ObeliskInc/obelisk-hardware/Generation 2 Mining Hardware/Electrical/Hashing Board/SC1B_MEMO-13.pdf

ORCHID TECHNOLOGIES ENGINEERING & CONSULTING, INC.

147 Main Street, Maynard, MA 01754
Tel: 978‐461‐2000 Fax: 978‐461‐2003 Web Site: www.orchid‐tech.com | Page 1

To: Zach Herbert

Fr: Paul Nickelsberg

Re: SC1B Rev D Release Package

Dt: September 25, 2018

Enclosed, please find the SC1B Revision D Hashing Board Release Package. This release package is suitable for construction of SC1B low volume, prototype circuit board assemblies. While Orchid has made every effort to provide an accurate, re-producible package, design anomalies and changes are inevitable between the construction of prototype assemblies, testing of those prototype assemblies and subsequent volume production. Please plan accordingly.

This package includes:

- SC1B Revision D Build Instructions
- SC1B Revision D Schematic Data Base
- SC1B Revision D Layout Data Base
- SC1B Revision D Bill of Materials

Sincerely,
Paul Nickelsberg
President
Orchid Technologies Engineering and Consulting, Inc.
