ObeliskInc/obelisk-hardware/Generation 2 Mining Hardware/Electrical/Control Board/docs/CC1B_REVA_BLD1_0.pdf

ORCHID TECHNOLOGIES CONFIDENTIAL – All Rights Reserved

FILE=CC1B_REVA_BLD1_0.DOC

# Orchid Technologies CC1B Control board PCB Assembly Build Instructions

Prepared By: Orchid Technologies Engineering and Consulting, Inc. 147 Main Street Maynard, Ma. 01754 978-461-2000

PROPRIETARY DATA NOTICE

This document shall not be duplicated or used for any purpose other than that for which provided. The information disclosed herein was originated by and is the property of Orchid Technologies Engineering & Consulting Inc. and/or its wholly-owned subsidiaries, and except for rights expressly granted by written consent, such information shall not be disclosed or disseminated in whole or in part. Orchid Technologies Engineering & Consulting Inc. and/or its wholly-owned subsidiaries reserve all Patent, Proprietary, Design, Use, Sale, Manufacturing, and Reproduction Rights thereto. Permission is hereby granted to you to copy this document as required for internal use only.

This document is presented to assist you in appraising the potential value of the CC1B CONTROL BOARD Build Instructions based upon the information which you have provided to us concerning your needs. Naturally, your requirements may change as business conditions and your operations change. Only you can determine the feasibility of the proposed CC1B CONTROL BOARD Build Instructions to answer your specific business needs. Consequently, while we believe that our CC1B CONTROL BOARD Build Instructions are sound, it cannot constitute express or implied warranties of merchantability and fitness for a particular purpose.

Revision History:
Revision | Date | Reason
1.0 | August 6, 2018 | Original

CC1B CONTROL Board, Rev A PCB Build Instructions, V1.0

This document contains the assembly-time instructions for the proper build of CC1B CONTROL BOARD Revision A Printed Circuit Boards. These Instructions together with the following documents comprise the CC1B CONTROL BOARD Revision A Circuit Board Fabrication and Assembly data base.

Related Documentation:

1. SC071018 Revision A July 29, 2018 Schematic Data Base
2. CC1B_072918.xls Bill of Materials – Base Bill
3. CC1B CONTROL BOARD PCB, Revision A Data Base Assembly and Fabrication Artwork as released by Orchid Technologies using SC071018 Revision A schematic and the CC1B_072918.xls BOM data base.

The documents listed above are considered finished documents and will not be modified by Orchid Technologies Engineering and Consulting, Inc. until Phase 2 of the project. All modifications to the documents listed above will take the form of notes and appear in this document as revised.

Documentation Errata, Changes, Acceptable Procedures:
All component stuffing and board options reference CC1B_072918.xls. Please use CC1B_072918.xls, as the basic guideline for board stuffing options.

### 0. DO NOT POWER BOARDS

1. Do Not Populate components with values “DNP”.
2. Do Not Populate components with values prefixed “DNP-“.
3. Completed assemblies shall be free of any and all flux residues.

Known BOM Discrepancies and AVL issues:

BOM Updates:
Item No | Description
| None

AVL Issues:
Item No | Description
| None

Programmable Logic Instructions:
This describes the programmable device data files and their uses.

NONE

CC1B CONTROL BOARD Revision A Rework Instructions:
Perform the instructions listed below on all CC1B CONTROL BOARD Revision A Circuit Boards.
Item | Action | Disposition
| None
