ObeliskInc/obelisk-hardware/Generation 2 Mining Hardware/Electrical/Hashing Board/pcb/SC1B_REVD_ASY/SC1B_REVD_AS2.pdf

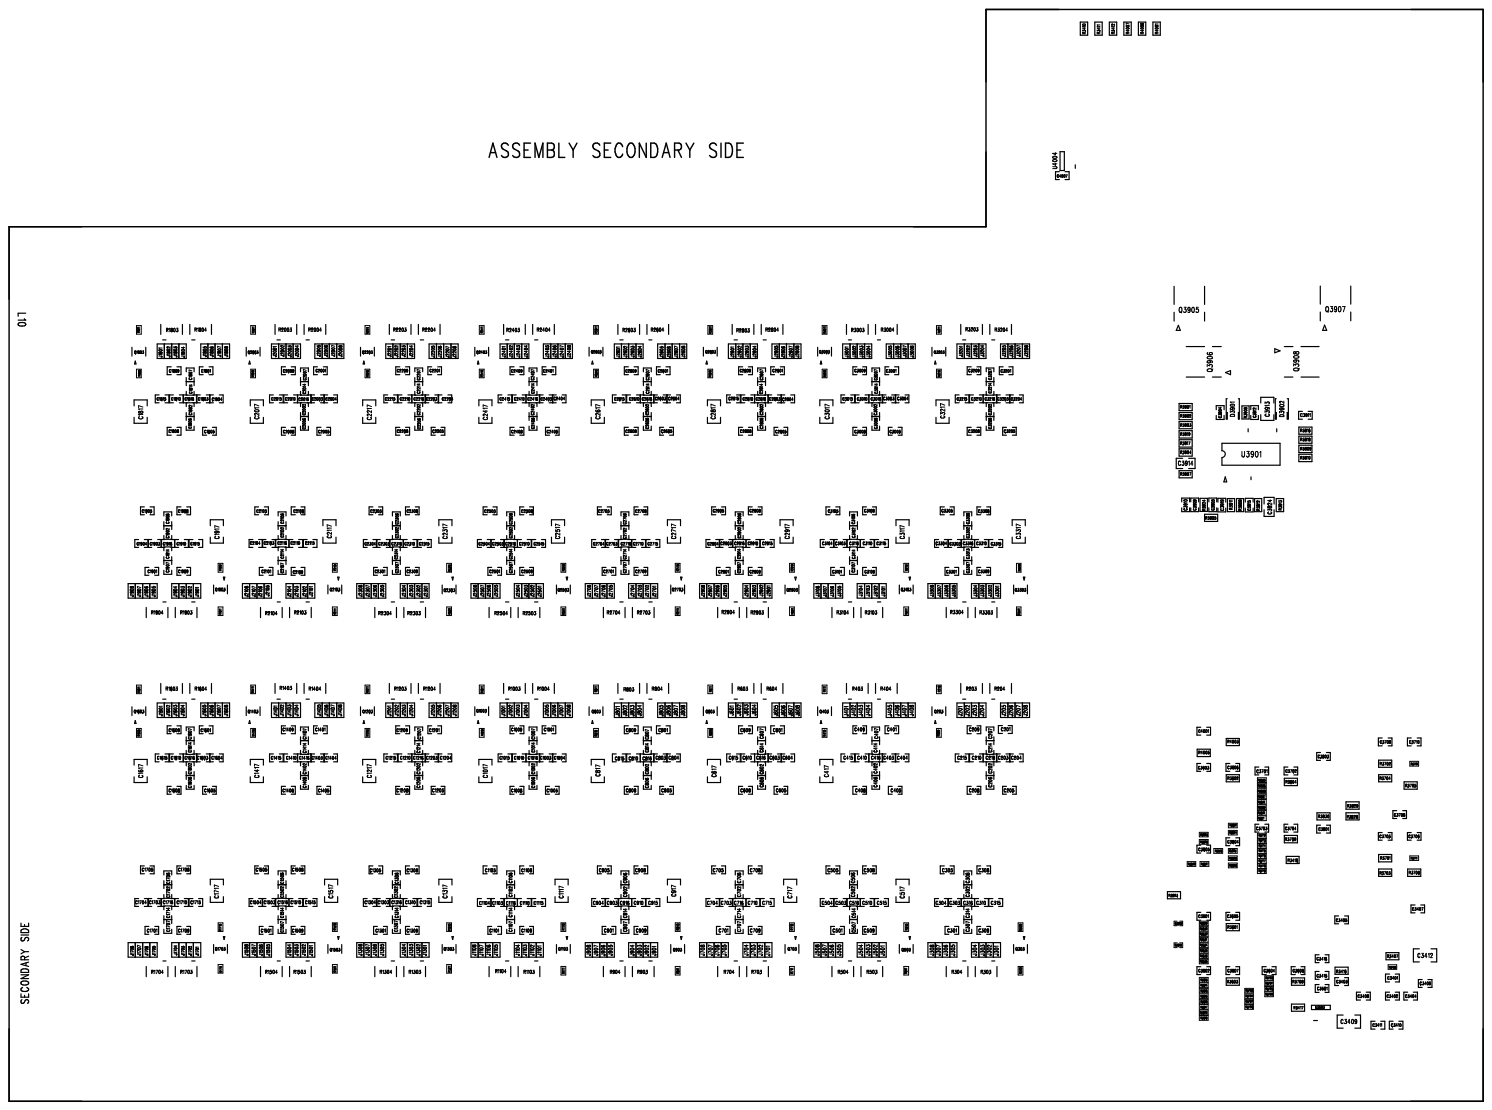
[picture p1: page 1]
