ObeliskInc/obelisk-hardware/Generation 2 Mining Hardware/Electrical/Control Board/docs/CC1B_072918.xls

Item | Quan | Reference | Value | Vendor | Vendor PN | Shape | Notes | Alt Vendor | Alt Vendor PN
1 | 4 | C902,C903,C904,C905 | 15pF/50V | MURATA | GRM0335C1H150J | C0201
2 | 2 | C301,C302 | 18pF/50V | MURATA | GRM0335C1H180J | C0201
3 | 1 | C1616 | 33pF/25V | MURATA | GRM0335C1E330J | C0201
4 | 1 | C1506 | 6800pF/25V | MURATA | GRM155R71E682K | C0402
5 | 1 | C1617 | 0.01uF/6.3V | MURATA | GRM033R70J103K | C0201
6 | 1 | C1601 | 0.01uF/10V | MURATA | GRM033R71A103K | C0201
7 | 1 | C1501 | 0.01uF/16V | MURATA | GRM155R71C103K | C0402
8 | 108 | C601,C602,C603,C604,C605, | 0.1uF/6.3V | MURATA | GRM155R70J104K | CC0402
 |  | C606,C607,C608,C609,C610,
 |  | C611,C612,C613,C614,C615,
 |  | C616,C617,C618,C619,C620,
 |  | C621,C622,C623,C624,C625,
 |  | C626,C627,C628,C629,C630,
 |  | C631,C632,C633,C634,C635,
 |  | C636,C637,C638,C639,C640,
 |  | C641,C642,C643,C644,C645,
 |  | C646,C647,C648,C649,C650,
 |  | C651,C652,C653,C654,C655,
 |  | C656,C657,C658,C659,C701,
 |  | C702,C703,C704,C705,C706,
 |  | C707,C708,C709,C710,C711,
 |  | C712,C713,C714,C715,C716,
 |  | C717,C718,C719,C720,C721,
 |  | C722,C723,C724,C725,C726,
 |  | C727,C728,C729,C730,C802,
 |  | C1001,C1002,C1003,C1201,
 |  | C1202,C1203,C1204,C1205,
 |  | C1206,C1207,C1208,C1209,
 |  | C1210,C1211,C1212,C1301,
 |  | C1302,C1619
9 | 30 | C201,C801,C901,C906,C908, | 0.1uF/16V | MURATA | GRM155R71C104K | CC0402
 |  | C909,C913,C914,C916,
 |  | C1101,C1102,C1103,C1104,
 |  | C1401,C1402,C1403,C1404,
 |  | C1405,C1406,C1407,C1502,
 |  | C1507,C1508,C1509,C1510,
 |  | C1511,C1512,C1602,C1603,
 |  | C1604
10 | 4 | C666,C667,C668,C669 | 1.0uF/6.3V | MURATA | GRM188R70J105K | C0603
11 | 4 | C1621,C1622,C1623,C1624 | 1.0uF/16V | MURATA | GRM21BR71C105K | C0805 | X7R
12 | 3 | C910,C911,C912 | 4.7uF/6.3V | MURATA | GRM188R60J475K | C0603
13 | 13 | C660,C661,C662,C663,C664, | 10uF/6.3V | TDK | CGA4J1X7R0J106K125AC | C0805
 |  | C665,C1004,C1610,C1611,
 |  | C1612,C1613,C1614,C1620
14 | 2 | C1503,C1513 | 10uF/16V | MURATA | GRM31CR71C106K | C1206
15 | 5 | C1504,C1505,C1605,C1606, | 22uF/6.3V | TDK | C2012X6S0J226K | C0805
 |  | C1607
16 | 24 | R301,R306,R307,R308,R309, | 0 OHM | VISHAY | CRCW02010000Z0 | R0201
 |  | R311,R312,R325,R326,R402,
 |  | R403,R1007,R1201,R1202,
 |  | R1203,R1204,R1205,R1206,
 |  | R1207,R1208,R1209,R1210,
 |  | R1211,R1212
17 | 20 | R304,R305,R320,R321,R322, | 33 OHM | VISHAY | CRCW020133R0JN | R0201
 |  | R323,R324,R401,R916,R917,
 |  | R918,R919,R920,R926,R927,
 |  | R928,R929,R930,R1004,
 |  | R1309
18 | 7 | R803,R804,R805,R806,R921, | 330 OHM | VISHAY | CRCW0201330RJN | R0201
 |  | R922,R1406
19 | 12 | R404,R405,R801,R802, | 1K | VISHAY | CRCW02011K00JN | R0201
 |  | R1305,R1308,R1405,R1606,
 |  | R1607,R1609,R1610,R1611
20 | 5 | R318,R319,R702,R1310, | 2.2K | VISHAY | CRCW02012K20JN | R0201
 |  | R1311
21 | 19 | R901,R902,R903,R904,R905, | 4.7K | VISHAY | CRCW02014K70JN | R0201
 |  | R906,R907,R913,R914,R915,
 |  | R923,R924,R933,R1005,
 |  | R1006,R1109,R1110,R1111,
 |  | R1112
22 | 1 | R1504 | 6.8K | VISHAY | CRCW02016K80JN | R0201
23 | 44 | R313,R406,R407,R408,R409, | 10K | VISHAY | CRCW020110K0JN | R0201
 |  | R410,R411,R412,R413,R414,
 |  | R415,R416,R420,R421,R424,
 |  | R425,R426,R925,R1001,
 |  | R1002,R1003,R1008,R1009,
 |  | R1010,R1011,R1012,R1101,
 |  | R1102,R1103,R1104,R1105,
 |  | R1106,R1107,R1108,R1301,
 |  | R1302,R1303,R1304,R1306,
 |  | R1307,R1401,R1402,R1403,
 |  | R1404
24 | 1 | R1502 | 100K | VISHAY | CRCW0201100KJN | R0201
25 | 29 | R201,R704,R705,R706,R707, | 49.9 OHM 1% | VISHAY | CRCW020149R9FK | R0201
 |  | R708,R709,R710,R711,R712,
 |  | R713,R714,R715,R716,R717,
 |  | R718,R719,R720,R721,R722,
 |  | R723,R724,R725,R727,R728,
 |  | R908,R909,R910,R911
26 | 1 | R701 | 100 OHM 1% | VISHAY | CRCW0201100RFK | R0201
27 | 1 | R703 | 240 OHM 1% | VISHAY | CRCW0201240RFK | R0201
28 | 1 | R1501 | 10.0K 1% | VISHAY | CRCW020110K0FK | R0201
29 | 1 | R912 | 12.1K 1% | VISHAY | CRCW020112K1FK | R0201
30 | 1 | R1503 | 26.1K 1% | VISHAY | CRCW020126K1FK | R0201
31 | 1 | R1601 | 150K 1% | VISHAY | CRCW0201150KFK | R0201
32 | 2 | R1602,R1603 | 180K 1% | VISHAY | CRCW0201180KFK | R0201
33 | 1 | R1608 | 270K 1% | VISHAY | CRCW0201270KFK | R0201
34 | 3 | L601,L602,L901 | BLM18 | MURATA | BLM18PG121SN1D | 0603
35 | 1 | L1501 | 10uH | BOURNS | SRU8043-100Y | IND_SRU8043-100Y | NEW
36 | 1 | Y901 | ASFL1-25.000MHz | ABRACON | ASFL1-25.000MHZ-LR-T | CRY\ASFL1
37 | 1 | Y301 | ABM8G-24.000 | ABRACON | ABM8G-24.000MHZ-18-D2Y-T | CRY\ABM8
38 | 1 | U1402 | ASDK-32.768KHZ | ABRACON | ASDK-32.768KHZ | CRY_ASDK
39 | 1 | U1401 | CSEQ | ALTERA | 5M40ZE64C5 | QFP64_7X7MM_TP
40 | 2 | L1601,L1602 | LPS4018-222MRC | COILCRAFT | LPS4018-222MRC | IND_LPS4018
41 | 1 | D801 | LED-553-GG | DIALIGHT | 553-0122F | LED_553-0132F
42 | 1 | U1501 | AP6502SP-13 | DIODES INC | AP6502SP-13 | DIP8_SO-8EP
43 | 1 | D1501 | S1A-13-F | DIODES INC | S1A-13-F | SMA
44 | 1 | J1002 | CONN-DM3CS | HIROSE | DM3CS-SF | HRS-DM3CS-SF
45 | 1 | U1002 | IDT74CBTLV3257QG | IDT | IDT74CBTLV3257QG | DIP16\QSOP
46 | 1 | F1501 | FUSE-5A | LITTELFUSE | 0451005.MRL | FUSE\LF-0451
47 | 1 | U701 | MT41J64M16 | MICRON | MT41J64M16JT-15E:g | BGA96_8X14MM |  | NANYA | NT5CB64M16GP-DH
48 | 1 | U1001 | MT25QL128 | MICRON | MT25QL128ABA3ESF-OSIT | DIP16/SOL |  | MICRON | MT25QL128ABA8ESF-OSIT
49 | 1 | U1601 | LP2998MR | NATIONAL SEMI | LP2998MR/NOPB | DIP8\PSOP
50 | 1 | U1301 | CAT24C256YI-G | ON SEMI | CAT24C256YI-G | DIP8\TSSOP
51 | 2 | Q902,Q901 | MMBT3904LT1 | ON SEMI | MMBT3904LT1G | SOT-23
52 | 2 | Q801,Q802 | MUN5235DW1 | ON SEMI | MUN5235DW1T1G | SOT-363
53 | 2 | U1604,U1605 | NCP114ASN180T1G | ON SEMI | NCP114ASN180T1G | TSOP-5
54 | 1 | U1403 | CAT809TTBI-GT3 | ON SEMI | CAT809TTBI-GT3 | SOT-23
55 | 1 | F1502 | PTC_1A | RAYCHEM | SMD100F | SMD100
56 | 4 | F1503,F1504,F1505,F1506 | PTC_1A5 | RAYCHEM | SMD150F | SMD100
57 | 1 | U901 | LAN8710A-EZC | SMSC | LAN8710A-EZC | QFN32_5X5MM_TP
58 | 5 | J501,J1301,J1302,J1304, | CON2 | SAMTEC | TSW-102-23-T-S | SIP\2P
 |  | J1305
59 | 2 | J1201,J1202 | CON3 | SAMTEC | TSW-103-23-T-S | SIP\3P
60 | 1 | J1001 | HEADER 4X2 | SAMTEC | TSW-104-23-T-D | J\8P
61 | 1 | J1401 | HEADER 5X2 | SAMTEC | TSW-105-23-T-D | J\10P
62 | 1 | J1306 | HEADER 10X2 | SAMTEC | TSW-110-23-T-D | J\20P
63 | 2 | J1207,J1208 | HEADER 10X2S | 3M | D2520-6002 | 3M_D2520-6002
64 | 4 | J1101,J1102,J1103,J1104 | CONN-FAN | TE CONN | 640454-4 | AMP\640454-4
65 | 1 | S801 | SW-RA | TE CONN | 1825027-5 | SW_TE_1825027-X
66 | 1 | J901 | CONN_LAN | UDE | RB1-125BAG1A | UDE_RB1-125BAG1A | RJ45 WITH MAG, NEW
67 | 1 | U201 | AM3352-ZCZ3 | TEXAS INSTRUMENTS | AM3352BZCZ30 | BGA324_.8MM_15X15MM
68 | 9 | U801,U1101,U1102,U1103, | SN74LVC2G14DB | TEXAS INSTRUMENTS | SN74LVC2G14DBVRE4 | SOT-23-6
 |  | U1104,U1201,U1202,U1203,
 |  | U1204
69 | 1 | U1603 | TPS22967DSGT | TEXAS INSTRUMENTS | TPS22967DSGI | DSG8_2X2MM_TP
70 | 1 | U1602 | TPS62410DRCT | TEXAS INSTRUMENTS | TPS62410DRCT | DRC10_3X3MM_TP
71 | 1 | D1401 | TLMG1100 | VISHAY | TLMG1100-GS08 | LED\0603
72 | 1 | D805 | VBUS054B-HSF | VISHAY | VBUS054B-HSF | ARRAY_VBUS054B-HSF
73 | 27 | R303,R310,R417,R418,R419, | DNP | DO NOT POPULATE | DO NOT POPULATE | 0402
 |  | R422,R423,R1013,R1113,
 |  | R1114,R1115,R1116,R1213,
 |  | R1214,R1215,R1216,R1217,
 |  | R1218,R1219,R1220,R1221,
 |  | R1222,R1223,R1224,R1407,
 |  | R1408,R1409
74 | 2 | H1302,H1303 | HOLE_M3X6 | DO NOT POPULATE | DO NOT POPULATE | HOLE_M3X6
75 | 2 | H1301,H1304 | SLOT_M3X3MM | DO NOT POPULATE | DO NOT POPULATE | SLOT_M3X3MM
76 | 17 | T201,T301,T501,T502,T503, | TP | OTEC TEST POINT | DO NOT POPULATE | TPTOP
 |  | T504,T505,T506,T507,T508,
 |  | T509,T601,T602,T1401,
 |  | T1402,T1403,T1404
77 | 1 | D802 | DNP_LED-553-GG | DO NOT POPULATE | DO NOT POPULATE | LED_553-0132F
78 | 3 | D1402,D1403,D1404 | DNP_TLMG1100 | DO NOT POPULATE | DO NOT POPULATE | LED\0603
79 | 4 | J1203,J1204,J1205,J1206 | DNP_CON3 | DO NOT POPULATE | DO NOT POPULATE | SIP\3P
80 | 4 | J1209,J1210,J1211,J1212 | DNP_HEADER 10X2S | DO NOT POPULATE | DO NOT POPULATE | 3M_D2520-6002
81 | 8 | U1205,U1206,U1207,U1208, | DNP_SN74LVC2G14DB | DO NOT POPULATE | DO NOT POPULATE | SOT-23-6
 |  | U1209,U1210,U1211,U1212
