ObeliskInc/obelisk-hardware/Generation 2 Mining Hardware/Electrical/Hashing Board/docs/SC1B_091918.xls

Item | Quan | Reference | Value | Vendor | Vendor PN | Shape | Notes
1 | 3 | C3410,C3411,C3915 | 22pF/50V | MURATA | GRM1555C1H220J | C0402
2 | 1 | C3909 | 220pF/50V | TDK | C1005C0G1H221J050BA | C0402
3 | 1 | C3905 | 820pF/50V | TDK | C1005C0G1H821J050BA | C0402
4 | 4 | C3609,C3610,C3617,C3618 | 2200pF/16V | MURATA | GRM033R71C222K | C0201
5 | 5 | C3401,C3413,C3414,C3415, | 0.01uF/16V | MURATA | GRM155R71C103K | C0402
 |  | C3416
6 | 409 | C201,C202,C203,C204,C205, | 0.1uF/6.3V | MURATA | GRM155R710J104K | C0402
 |  | C206,C207,C208,C209,C210,
 |  | C214,C215,C301,C302,C303,
 |  | C304,C305,C306,C307,C308,
 |  | C309,C310,C314,C315,C401,
 |  | C402,C403,C404,C405,C406,
 |  | C407,C408,C409,C410,C414,
 |  | C415,C501,C502,C503,C504,
 |  | C505,C506,C507,C508,C509,
 |  | C510,C514,C515,C601,C602,
 |  | C603,C604,C605,C606,C607,
 |  | C608,C609,C610,C614,C615,
 |  | C701,C702,C703,C704,C705,
 |  | C706,C707,C708,C709,C710,
 |  | C714,C715,C801,C802,C803,
 |  | C804,C805,C806,C807,C808,
 |  | C809,C810,C814,C815,C901,
 |  | C902,C903,C904,C905,C906,
 |  | C907,C908,C909,C910,C914,
 |  | C915,C1001,C1002,C1003,
 |  | C1004,C1005,C1006,C1007,
 |  | C1008,C1009,C1010,C1014,
 |  | C1015,C1101,C1102,C1103,
 |  | C1104,C1105,C1106,C1107,
 |  | C1108,C1109,C1110,C1114,
 |  | C1115,C1201,C1202,C1203,
 |  | C1204,C1205,C1206,C1207,
 |  | C1208,C1209,C1210,C1214,
 |  | C1215,C1301,C1302,C1303,
 |  | C1304,C1305,C1306,C1307,
 |  | C1308,C1309,C1310,C1314,
 |  | C1315,C1401,C1402,C1403,
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
 |  | R1509,R1609,R1709,R1809,
 |  | R1909,R2009,R2109,R2209,
 |  | R2309,R2409,R2509,R2609,
 |  | R2709,R2809,R2909,R3009,
 |  | R3109,R3209,R3309
32 | 1 | R3911 | 3.90K 1% | VISHAY | CRCW04023K90FK | R0402
33 | 2 | R3904,R3912 | 11.0K 1% | VISHAY | CRCW040211K0FK | R0402
34 | 4 | R3907,R3913,R3916,R3917 | 20.0K 1% | VISHAY | CRCW040220K0FK | R0402
35 | 1 | R3922 | 30.0K 1% | VISHAY | CRCW040230K0FK | R0402
36 | 1 | R3905 | 43.2K 1% | VISHAY | CRCW040243K2FK | R0402
37 | 2 | R3919,R3918 | 49.9K 1% | VISHAY | CRCW040249K9FK | R0402
38 | 1 | R3908 | 60.4K 1% | VISHAY | CRCW040260K4FK | R0402
39 | 1 | R3903 | 100K 1% | VISHAY | CRCW0402100KFK | R0402
40 | 2 | RT3901,RT3902 | 100KT | MURATA | NCU18WF104F60RB | R0603 | THERMISTOR
41 | 2 | R3414,R3415 | R4A-33 OHM | VISHAY | CRA06S083033RJ | ARRAY_CRA06S0831
42 | 64 | R203,R204,R303,R304,R403, | R4A-100 OHM | VISHAY | CRA06S083101RJ | ARRAY_CRA06S0831
 |  | R404,R503,R504,R603,R604,
 |  | R703,R704,R803,R804,R903,
 |  | R904,R1003,R1004,R1103,
 |  | R1104,R1203,R1204,R1303,
 |  | R1304,R1403,R1404,R1503,
 |  | R1504,R1603,R1604,R1703,
 |  | R1704,R1803,R1804,R1903,
 |  | R1904,R2003,R2004,R2103,
 |  | R2104,R2203,R2204,R2303,
 |  | R2304,R2403,R2404,R2503,
 |  | R2504,R2603,R2604,R2703,
 |  | R2704,R2803,R2804,R2903,
 |  | R2904,R3003,R3004,R3103,
 |  | R3104,R3203,R3204,R3303,
 |  | R3304
43 | 32 | R205,R308,R405,R505,R605, | R4A-1M | VISHAY | CRA06S0831M00J | ARRAY_CRA06S0831
 |  | R705,R805,R905,R1005,
 |  | R1105,R1205,R1305,R1405,
 |  | R1505,R1605,R1705,R1805,
 |  | R1905,R2005,R2105,R2205,
 |  | R2305,R2405,R2505,R2605,
 |  | R2705,R2805,R2905,R3005,
 |  | R3105,R3205,R3305
44 | 1 | Y3401 | 8.00MHZ | CARDINAL COMP | CX532Z-A2B3C5-70-8.0D18 | CRY_CX532
45 | 2 | L3901,L3902 | 1.2uH | COILCRAFT | XAL1060-122MEB | IND_XAL1060-401/1350
46 | 2 | U3501,U3502 | TMP37GRTZ | ANALOG DEVICES | TMP37GRTZ-REEL7 | SOT-23-5
47 | 1 | U3902 | AD5111BCPZ80 | ANALOG DEVICES | AD5111BCPZ80 | LFCSP8_UD_2X2MM
48 | 32 | U201,U301,U401,U501,U601, | BLAKE2B | CSS | BLAKE2B | BGA144_.8MM_10X10MM
 |  | U701,U801,U901,U1001,
 |  | U1101,U1201,U1301,U1401,
 |  | U1501,U1601,U1701,U1801,
 |  | U1901,U2001,U2101,U2201,
 |  | U2301,U2401,U2501,U2601,
 |  | U2701,U2801,U2901,U3001,
 |  | U3101,U3201,U3301
49 | 2 | D3901,D3902 | DFLS1100-7 | DIODES INC | DFLS1100-7 | POWERDI_123
50 | 6 | Q3901,Q3902,Q3903,Q3904, | BSC018NE2LS | INFINEON | BSC018NE2LSIATMA1 | POWERPAK-SO8
 |  | Q3905,Q3907
51 | 1 | U3901 | LTC3855IFE#PBF | LINEAR TECH | LTC3855IFE#PBF | DIP38_SSOP_TP
52 | 1 | F4001 | FUSE-5A | LITTELFUSE | 0451005.MRL | FUSE\LF-0451
53 | 3 | J3901,J3902,J3903 | MINIFIT_JR_6P | MOLEX | 0039301061 | MOLEX\39-30-0060
54 | 1 | L3401 | BEAD1 | MURATA | BLM21PG300SN1D | 0805
55 | 34 | D201,D302,D401,D501,D601, | IP4220CZ6 | NEXPERIA | IP4220CZ6 | TSOP-6
 |  | D701,D801,D901,D1001,
 |  | D1101,D1201,D1301,D1401,
 |  | D1501,D1601,D1701,D1801,
 |  | D1901,D2001,D2101,D2201,
 |  | D2301,D2401,D2501,D2601,
 |  | D2701,D2801,D2901,D3001,
 |  | D3101,D3201,D3301,D3404,
 |  | D4006
56 | 42 | Q203,Q303,Q403,Q503,Q603, | MUN5235DW1 | ON SEMI | MUN5235DW1T1G | SOT-363
 |  | Q703,Q803,Q903,Q1003,
 |  | Q1103,Q1203,Q1303,Q1403,
 |  | Q1503,Q1603,Q1703,Q1803,
 |  | Q1903,Q2003,Q2103,Q2203,
 |  | Q2303,Q2403,Q2503,Q2603,
 |  | Q2703,Q2803,Q2903,Q3003,
 |  | Q3103,Q3203,Q3303,Q3501,
 |  | Q3502,Q3503,Q3504,Q3505,
 |  | Q3506,Q3507,Q3508,Q3801,
 |  | Q3802
57 | 64 | Q201,Q202,Q301,Q302,Q401, | MUN5335DW1 | ON SEMI | MUN5335DW1T1G | SOT-363
 |  | Q402,Q501,Q502,Q601,Q602,
 |  | Q701,Q702,Q801,Q802,Q901,
 |  | Q902,Q1001,Q1002,Q1101,
 |  | Q1102,Q1201,Q1202,Q1301,
 |  | Q1302,Q1401,Q1402,Q1501,
 |  | Q1502,Q1601,Q1602,Q1701,
 |  | Q1702,Q1801,Q1802,Q1901,
 |  | Q1902,Q2001,Q2002,Q2101,
 |  | Q2102,Q2201,Q2202,Q2301,
 |  | Q2302,Q2401,Q2402,Q2501,
 |  | Q2502,Q2601,Q2602,Q2701,
 |  | Q2702,Q2801,Q2802,Q2901,
 |  | Q2902,Q3001,Q3002,Q3101,
 |  | Q3102,Q3201,Q3202,Q3301,
 |  | Q3302
58 | 1 | D4007 | MMBD4148 | ON SEMI | MMBD4148SE | SOT-23
59 | 4 | J4001,J4002,J4003,J4004 | CON2 | SAMTEC | TSW-102-23-T-S | SIP\2P
60 | 2 | J3401,J3501 | HEADER 5X2 | SAMTEC | TSW-105-23-T-D | J\10P
61 | 1 | J4005 | HEADER 10X2 | SAMTEC | TSW-110-23-T-D | J\20P
62 | 1 | U3401 | STM32F101V8 | ST MICRO | STM32F101V8T6TR | LQFP100_14X14MM
63 | 32 | D202,D301,D402,D502,D602, | BAT30F4 | ST MICRO | BAT30F4 | DIODE_BAT30F4
 |  | D702,D802,D902,D1002,
 |  | D1102,D1202,D1302,D1402,
 |  | D1502,D1602,D1702,D1802,
 |  | D1902,D2002,D2102,D2202,
 |  | D2302,D2402,D2502,D2602,
 |  | D2702,D2802,D2902,D3002,
 |  | D3102,D3202,D3302
64 | 2 | U3702,U3701 | SN74AVC4T245DR | TI | SN74AVC4T245DR | DIP16_SO
65 | 2 | U3703,U4004 | SN74LVC2G14DB | TI | SN74LVC2G14DBVRE4 | SOT-23-6
66 | 2 | U3801,U3802 | CD4097BPWR | TI | CD4097BPWR | DIP24\TSSOP
67 | 2 | U3803,U4001 | TLV272CDR | TI | TLV272CDR | DIP8\SO
68 | 6 | U3601,U3602,U3603,U3604, | SN74AVC8T245PW | TI | SN74AVC8T245PW | DIP24\TSSOP
 |  | U3704,U3705
69 | 1 | U4002 | TPS70912DRVR | TI | TPS70912DRVR | DIP6_WSON_TP
70 | 1 | U4003 | TPS70933DRVR | TI | TPS70933DRVR | DIP6_WSON_TP
71 | 1 | U3503 | SN74LVC1G3157DBV | TI | SN74LVC13157DBVR | SOT-23-6
72 | 6 | D3401,D3402,D3403,D4003, | TLMG1100 | VISHAY | TLMG1100-GS08 | LED\0603
 |  | D4004,D4005
73 | 176 | J201,J202,J203,J204,J205, | BJC | OTEC JUMPER | DO NOT POPULATE | OTEC_BJC | BOARD SHAPE - CLOSED
 |  | J206,J207,J208,J301,J302,
 |  | J303,J304,J305,J307,J308,
 |  | J402,J403,J404,J405,J406,
 |  | J407,J408,J502,J503,J504,
 |  | J505,J507,J508,J601,J603,
 |  | J604,J605,J606,J607,J608,
 |  | J701,J703,J704,J705,J707,
 |  | J708,J803,J804,J805,J806,
 |  | J807,J808,J903,J904,J905,
 |  | J907,J908,J1001,J1002,
 |  | J1004,J1005,J1006,J1007,
 |  | J1008,J1101,J1102,J1104,
 |  | J1105,J1107,J1108,J1202,
 |  | J1204,J1205,J1206,J1207,
 |  | J1208,J1302,J1304,J1305,
 |  | J1307,J1308,J1401,J1404,
 |  | J1405,J1406,J1407,J1408,
 |  | J1501,J1504,J1505,J1507,
 |  | J1508,J1604,J1605,J1606,
 |  | J1607,J1608,J1704,J1705,
 |  | J1707,J1708,J1801,J1802,
 |  | J1803,J1805,J1806,J1807,
 |  | J1808,J1901,J1902,J1903,
 |  | J1905,J1907,J1908,J2002,
 |  | J2003,J2005,J2006,J2007,
 |  | J2008,J2102,J2103,J2105,
 |  | J2107,J2108,J2201,J2203,
 |  | J2205,J2206,J2207,J2208,
 |  | J2301,J2303,J2305,J2307,
 |  | J2308,J2403,J2405,J2406,
 |  | J2407,J2408,J2503,J2505,
 |  | J2507,J2508,J2601,J2602,
 |  | J2605,J2606,J2607,J2608,
 |  | J2701,J2702,J2705,J2707,
 |  | J2708,J2802,J2805,J2806,
 |  | J2807,J2808,J2902,J2905,
 |  | J2907,J2908,J3001,J3005,
 |  | J3006,J3007,J3008,J3101,
 |  | J3105,J3107,J3108,J3205,
 |  | J3206,J3207,J3208,J3305,
 |  | J3307,J3308
74 | 80 | J306,J401,J501,J506,J602, | BJO | OTEC JUMPER | DO NOT POPULATE | OTEC_BJO | BOARD SHAPE - OPEN
 |  | J702,J706,J801,J802,J901,
 |  | J902,J906,J1003,J1103,
 |  | J1106,J1201,J1203,J1301,
 |  | J1303,J1306,J1402,J1403,
 |  | J1502,J1503,J1506,J1601,
 |  | J1602,J1603,J1701,J1702,
 |  | J1703,J1706,J1804,J1904,
 |  | J1906,J2001,J2004,J2101,
 |  | J2104,J2106,J2202,J2204,
 |  | J2302,J2304,J2306,J2401,
 |  | J2402,J2404,J2501,J2502,
 |  | J2504,J2506,J2603,J2604,
 |  | J2703,J2704,J2706,J2801,
 |  | J2803,J2804,J2901,J2903,
 |  | J2904,J2906,J3002,J3003,
 |  | J3004,J3102,J3103,J3104,
 |  | J3106,J3201,J3202,J3203,
 |  | J3204,J3301,J3302,J3303,
 |  | J3304,J3306
75 | 67 | T201,T202,T301,T302,T401, | TP | OTEC TEST POINT | DO NOT POPULATE | TPTOP
 |  | T402,T501,T502,T601,T602,
 |  | T701,T702,T801,T802,T901,
 |  | T902,T1001,T1002,T1101,
 |  | T1102,T1201,T1202,T1301,
 |  | T1302,T1401,T1402,T1501,
 |  | T1502,T1601,T1602,T1701,
 |  | T1702,T1801,T1802,T1901,
 |  | T1902,T2001,T2002,T2101,
 |  | T2102,T2201,T2202,T2301,
 |  | T2302,T2401,T2402,T2501,
 |  | T2502,T2601,T2602,T2701,
 |  | T2702,T2801,T2802,T2901,
 |  | T2902,T3001,T3002,T3101,
 |  | T3102,T3201,T3202,T3301,
 |  | T3302,T3403,T3404,T3405
76 | 8 | H4001,H4002,H4003,H4004, | HOLE125-250 | OTEC MOUNTING HOLE | DO NOT POPULATE | HOLE125-250
 |  | H4005,H4006,H4007,H4008
77 | 24 | R3606,R3607,R3608,R3609, | DNP-0201 | -- | DO NOT POPULATE | R0201
 |  | R3611,R3612,R3614,R3615,
 |  | R3616,R3617,R3619,R3620,
 |  | R3713,R3714,R3715,R3717,
 |  | R3718,R3719,R3721,R3722,
 |  | R3723,R3724,R3726,R3727
78 | 5 | R3413,R3901,R3902,R3909, | DNP | -- | DO NOT POPULATE | R0402
 |  | R3910
79 | 1 | C3919 | DNP-C0402 | -- | DO NOT POPULATE | C0402
80 | 1 | R4009 | DNP-2010 | -- | DO NOT POPULATE | 2010
81 | 2 | Q3908,Q3906 | DNP-MOSFETN | -- | DO NOT POPULATE | POWERPAK-SO8
