ObeliskInc/obelisk-hardware/Generation 1 Mining Hardware/Mechanical/TE-1719_742929-01_SC1-Upper-Guide.DXF

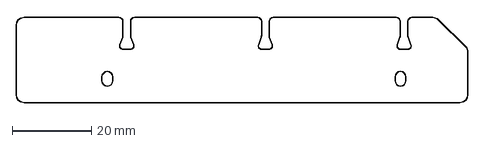
[picture p16: CAD file, 2019-08-30]
Generation 1 Mining Hardware/Mechanical/TE-1719_742929-01_SC1-Upper-Guide.DXF
114.0 x 21.5 mm
