ObeliskInc/obelisk-hardware/Generation 2 Mining Hardware/Heatsink/Heatsink.SLDPRT

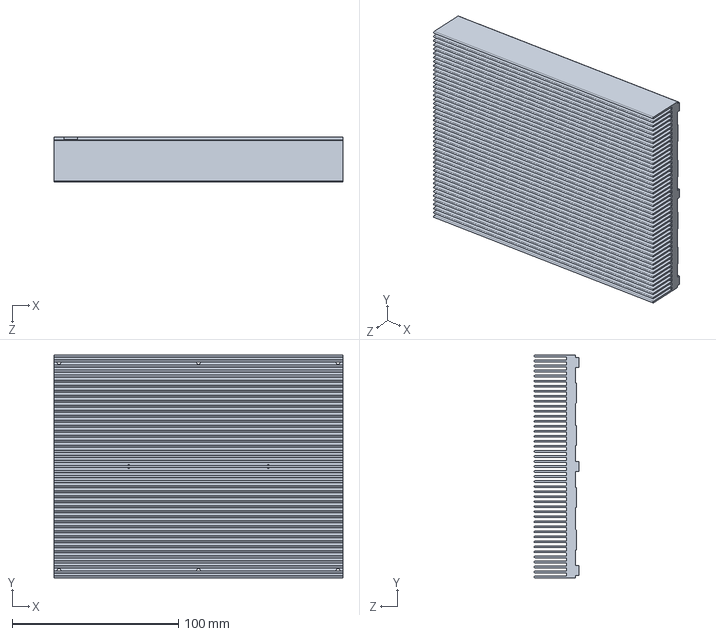
[picture p17: CAD file, 2019-09-12]
Generation 2 Mining Hardware/Heatsink/Heatsink.SLDPRT
174.0 x 134.1 x 27.0 mm
