ObeliskInc/obelisk-hardware/Generation 2 Mining Hardware/Mechanical – Immersion/OB_1735102-D_1U-Rack-Sled-Assem_2018-01-07/FOAM_062_NEOPRENE-ADHESIVE.SLDPRT

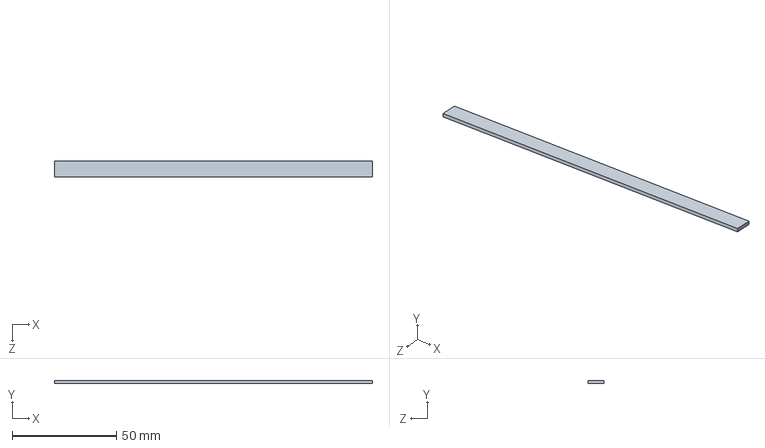
[picture p18: CAD file, 2019-08-30]
Generation 2 Mining Hardware/Mechanical – Immersion/OB_1735102-D_1U-Rack-Sled-Assem_2018-01-07/FOAM_062_NEOPRENE-ADHESIVE.SLDPRT
152.4 x 1.57 x 7.62 mm
