ObeliskInc/obelisk-hardware/Generation 2 Mining Hardware/Mechanical – Immersion/OB_1735102-D_1U-Rack-Sled-Assem_2018-01-07/ATS-2476-C1-R0.SLDPRT

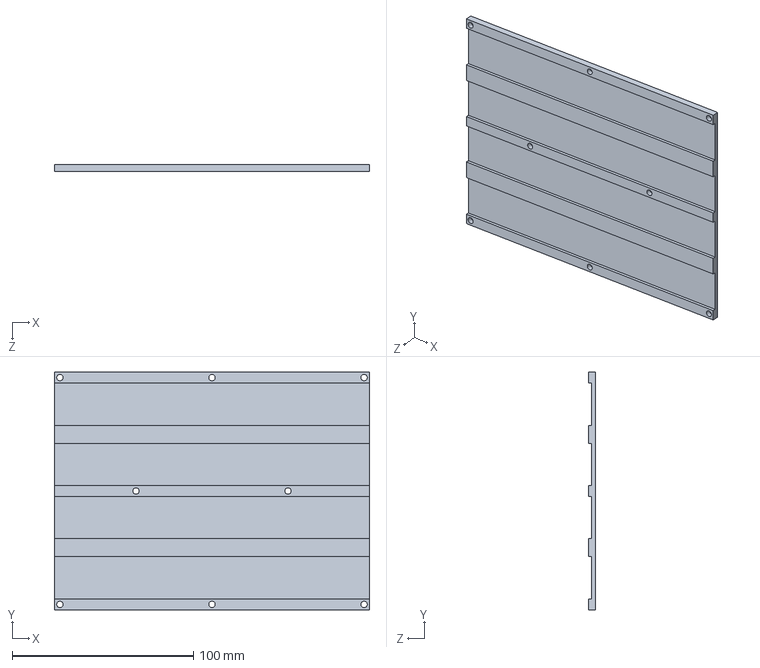
[picture p19: CAD file, 2019-08-30]
Generation 2 Mining Hardware/Mechanical – Immersion/OB_1735102-D_1U-Rack-Sled-Assem_2018-01-07/ATS-2476-C1-R0.SLDPRT
174.0 x 131.3 x 4.00 mm
