ObeliskInc/obelisk-hardware/Generation 2 Mining Hardware/Mechanical – Slim/OB_1735100-F_W2-Assem_2018-10-01/Standoff_4-40x312_JHP-BSO644010D.SLDPRT

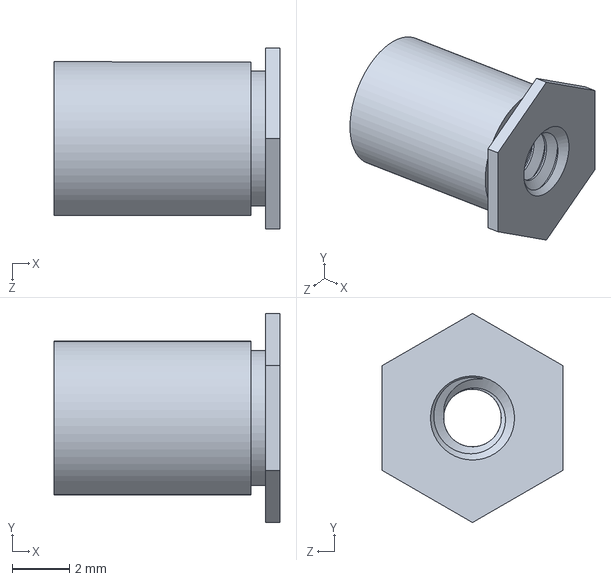
[picture p20: CAD file, 2019-08-30]
Generation 2 Mining Hardware/Mechanical – Slim/OB_1735100-F_W2-Assem_2018-10-01/Standoff_4-40x312_JHP-BSO644010D.SLDPRT
7.92 x 7.33 x 6.35 mm
