ObeliskInc/obelisk-hardware/Generation 1 Mining Hardware/Mechanical/TE-1719_742921-02_SC1-Assem_PRELIM_051818/TE-1719_742924-02_SC1-Cover.SLDPRT

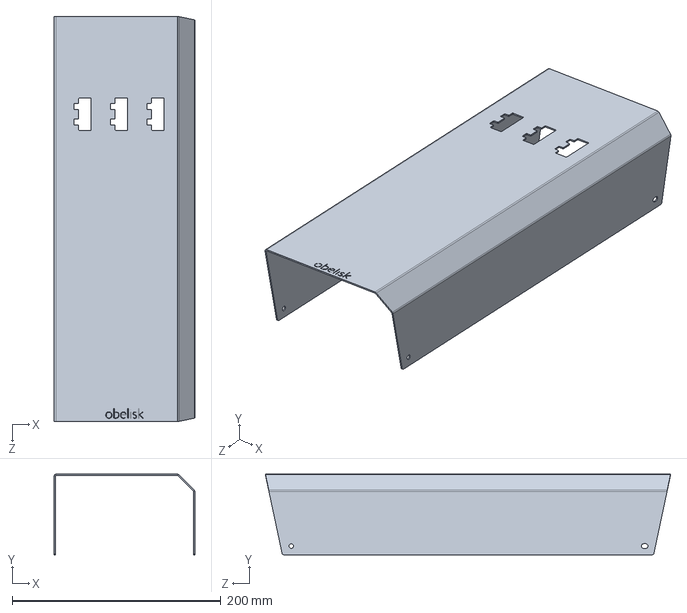
[picture p21: CAD file, 2019-08-30]
Generation 1 Mining Hardware/Mechanical/TE-1719_742921-02_SC1-Assem_PRELIM_051818/TE-1719_742924-02_SC1-Cover.SLDPRT
135.0 x 77.5 x 388.5 mm
