ObeliskInc/obelisk-hardware/Generation 2 Mining Hardware/Mechanical – Immersion/OB_1735102-D_1U-Rack-Sled-Assem_2018-01-07/BACK.SLDPRT

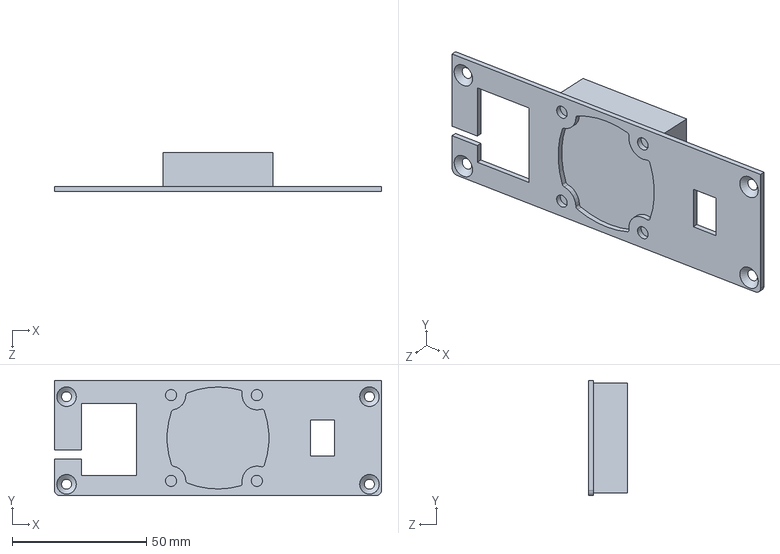
[picture p22: CAD file, 2019-08-30]
Generation 2 Mining Hardware/Mechanical – Immersion/OB_1735102-D_1U-Rack-Sled-Assem_2018-01-07/BACK.SLDPRT
122.0 x 43.0 x 14.5 mm
