ObeliskInc/obelisk-hardware/Generation 2 Mining Hardware/Mechanical – Slim/OB_1735100-F_W2-Assem_2018-10-01/CARD-GUIDE_Bivar-DC-800-102.SLDPRT

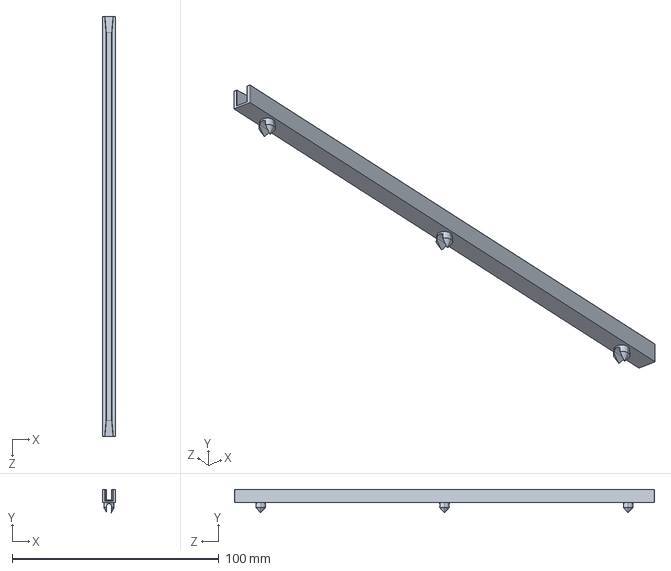
[picture p23: CAD file, 2019-08-30]
Generation 2 Mining Hardware/Mechanical – Slim/OB_1735100-F_W2-Assem_2018-10-01/CARD-GUIDE_Bivar-DC-800-102.SLDPRT
6.35 x 11.2 x 203.2 mm
