ObeliskInc/obelisk-hardware/Generation 1 Mining Hardware/Mechanical/TE-1719_742921-02_SC1-Assem_PRELIM_051818/M-RJE73-188-00XX0-REVG1.SLDPRT

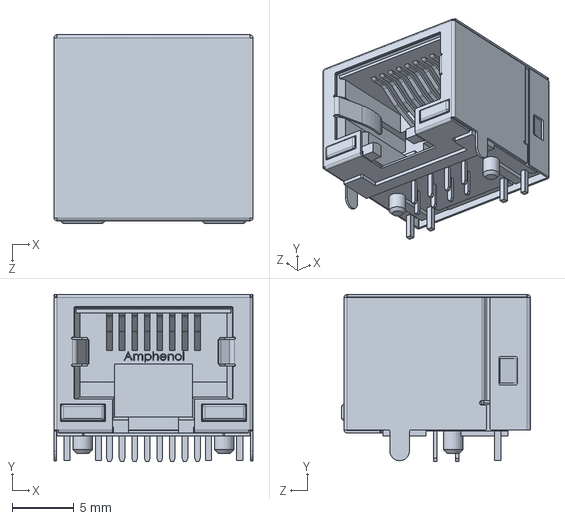
[picture p24: CAD file, 2019-08-30]
Generation 1 Mining Hardware/Mechanical/TE-1719_742921-02_SC1-Assem_PRELIM_051818/M-RJE73-188-00XX0-REVG1.SLDPRT
16.1 x 13.6 x 15.3 mm
