ObeliskInc/obelisk-hardware/Generation 1 Mining Hardware/Mechanical/TE-1719_742921-02_SC1-Assem_PRELIM_051818/LED_Dual-3mm_Dialight.SLDPRT

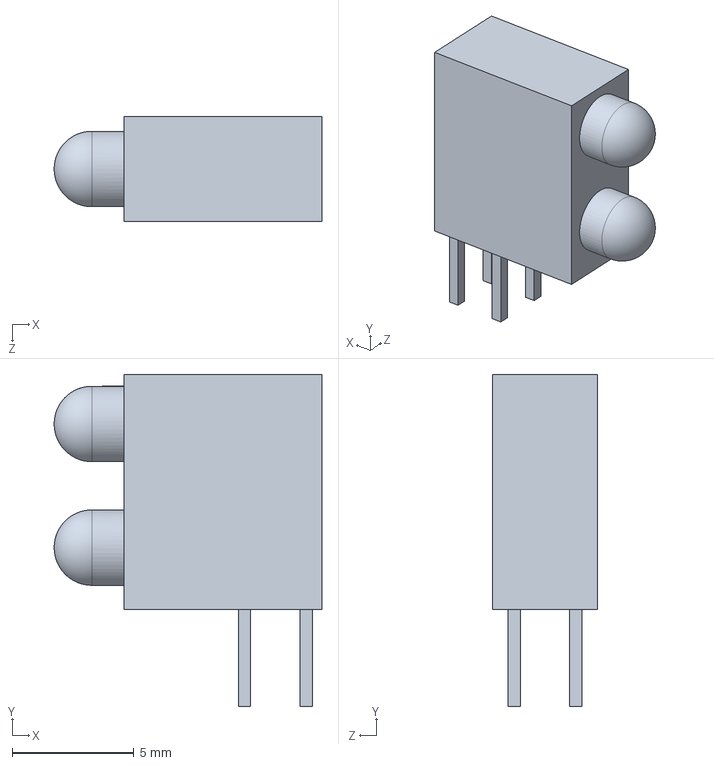
[picture p25: CAD file, 2019-08-30]
Generation 1 Mining Hardware/Mechanical/TE-1719_742921-02_SC1-Assem_PRELIM_051818/LED_Dual-3mm_Dialight.SLDPRT
11.0 x 13.6 x 4.32 mm
