ObeliskInc/obelisk-hardware/Generation 2 Mining Hardware/Mechanical – Immersion/OB_1735102-D_1U-Rack-Sled-Assem_2018-01-07/MP1000-1121 ON OFF KEY.SLDPRT

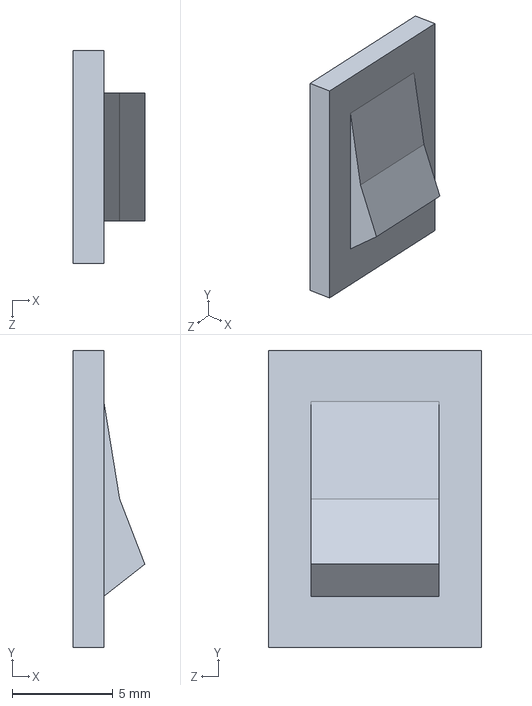
[picture p26: CAD file, 2019-08-30]
Generation 2 Mining Hardware/Mechanical – Immersion/OB_1735102-D_1U-Rack-Sled-Assem_2018-01-07/MP1000-1121 ON OFF KEY.SLDPRT
3.56 x 14.7 x 10.5 mm
