ObeliskInc/obelisk-hardware/Generation 1 Mining Hardware/Mechanical/TE-1719_742921-02_SC1-Assem_PRELIM_051818/TE-1719_742933-00_SC1-AIRFLOW-GUIDE.SLDPRT

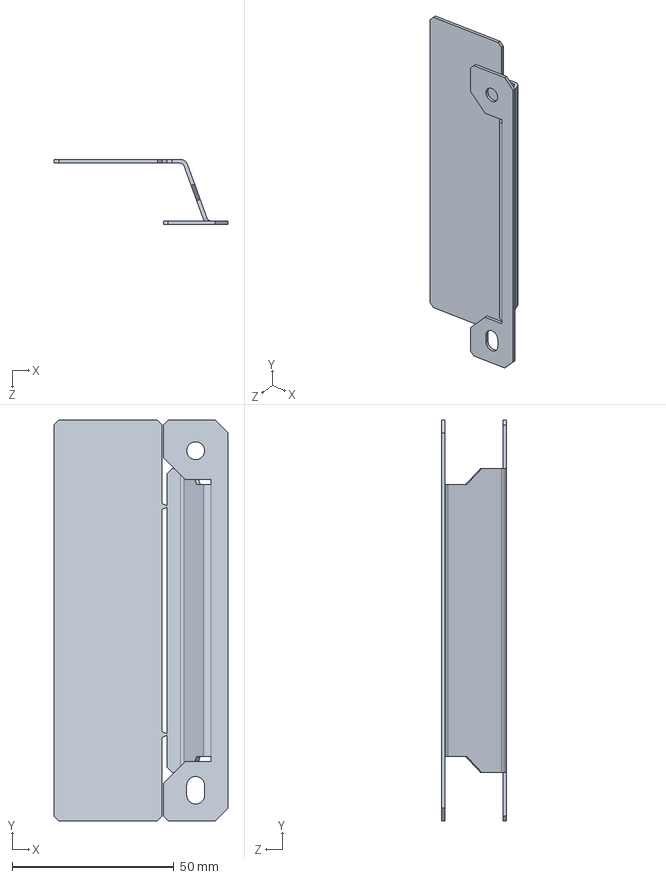
[picture p27: CAD file, 2019-08-30]
Generation 1 Mining Hardware/Mechanical/TE-1719_742921-02_SC1-Assem_PRELIM_051818/TE-1719_742933-00_SC1-AIRFLOW-GUIDE.SLDPRT
53.8 x 124.0 x 20.2 mm
