ObeliskInc/obelisk-hardware/Generation 2 Mining Hardware/Mechanical – Slim/OB_1735100-F_W2-Assem_2018-10-01/CARD-GUIDE_Bivar-DC-450-102.SLDPRT

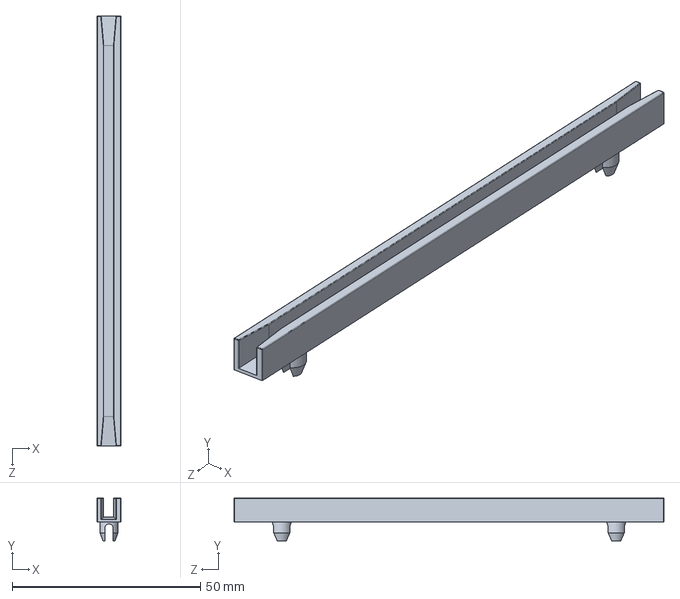
[picture p28: CAD file, 2019-08-30]
Generation 2 Mining Hardware/Mechanical – Slim/OB_1735100-F_W2-Assem_2018-10-01/CARD-GUIDE_Bivar-DC-450-102.SLDPRT
6.35 x 11.4 x 114.3 mm
