ObeliskInc/obelisk-hardware/Generation 2 Mining Hardware/Mechanical – Immersion/OB_1735102-D_1U-Rack-Sled-Assem_2018-01-07/OB_1735315-B_1U-Outer-Bracket.SLDPRT

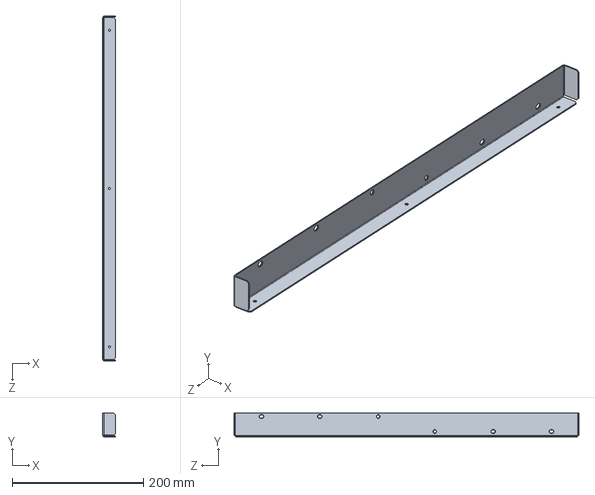
[picture p29: CAD file, 2019-08-30]
Generation 2 Mining Hardware/Mechanical – Immersion/OB_1735102-D_1U-Rack-Sled-Assem_2018-01-07/OB_1735315-B_1U-Outer-Bracket.SLDPRT
19.1 x 36.1 x 525.8 mm
