ObeliskInc/obelisk-hardware/Generation 1 Mining Hardware/Mechanical/TE-1719_742921-02_SC1-Assem_PRELIM_051818/EVQPF008K.SLDPRT

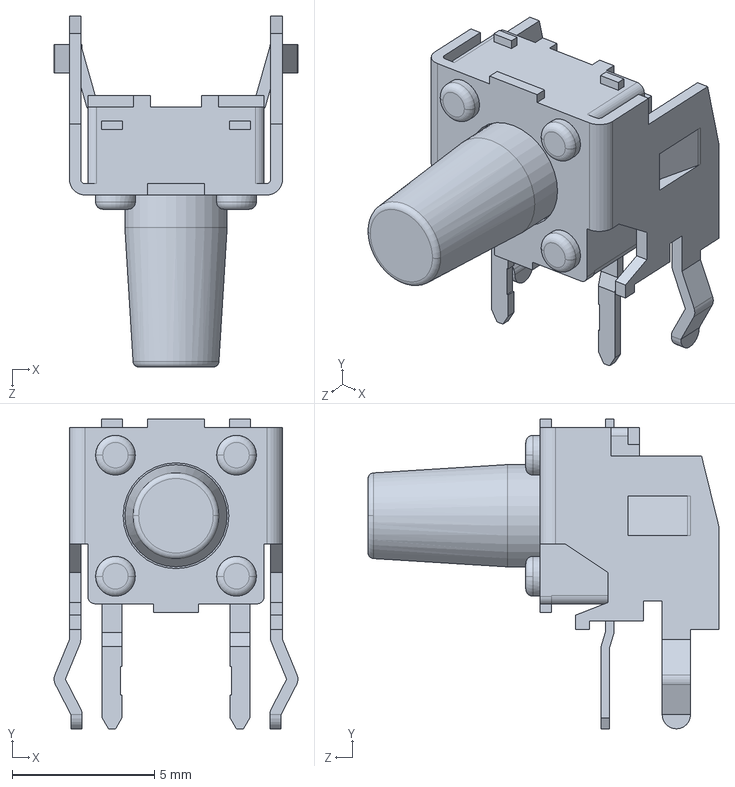
[picture p30: CAD file, 2019-08-30]
Generation 1 Mining Hardware/Mechanical/TE-1719_742921-02_SC1-Assem_PRELIM_051818/EVQPF008K.SLDPRT
8.58 x 10.9 x 12.4 mm
