ObeliskInc/obelisk-hardware/Generation 2 Mining Hardware/Mechanical – Slim/OB_1735100-F_W2-Assem_2018-10-01/OB_1735307-A_Grill-Foam-Strip-Upper.SLDPRT

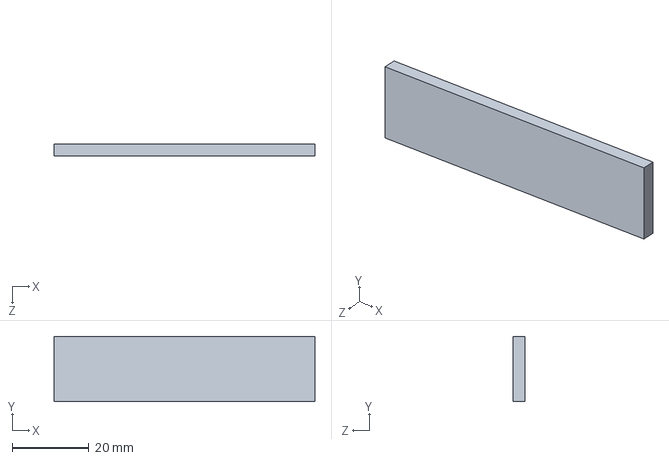
[picture p32: CAD file, 2019-08-30]
Generation 2 Mining Hardware/Mechanical – Slim/OB_1735100-F_W2-Assem_2018-10-01/OB_1735307-A_Grill-Foam-Strip-Upper.SLDPRT
68.0 x 17.0 x 3.05 mm
