ObeliskInc/obelisk-hardware/Generation 1 Mining Hardware/Mechanical/TE-1719_742921-02_SC1-Assem_PRELIM_051818/FAN_Jaro_JCD1203812LBBA0D(4600).SLDPRT

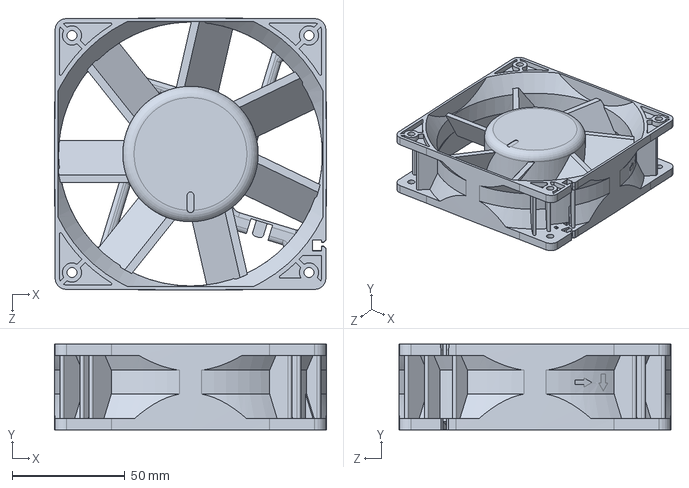
[picture p33: CAD file, 2019-08-30]
Generation 1 Mining Hardware/Mechanical/TE-1719_742921-02_SC1-Assem_PRELIM_051818/FAN_Jaro_JCD1203812LBBA0D(4600).SLDPRT
120.5 x 38.0 x 120.5 mm
