ObeliskInc/obelisk-hardware/Generation 2 Mining Hardware/Mechanical – Slim/OB_1735100-F_W2-Assem_2018-10-01/OB_1735305-A_PCB-Foam-Strip.SLDPRT

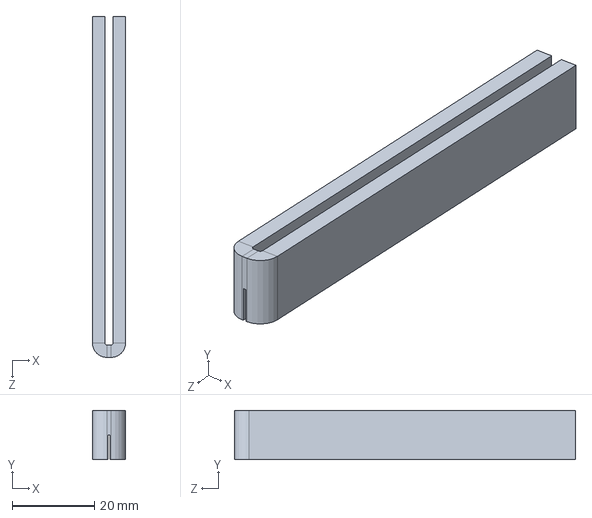
[picture p35: CAD file, 2019-08-30]
Generation 2 Mining Hardware/Mechanical – Slim/OB_1735100-F_W2-Assem_2018-10-01/OB_1735305-A_PCB-Foam-Strip.SLDPRT
8.10 x 12.0 x 83.0 mm
