ObeliskInc/obelisk-hardware/Generation 2 Mining Hardware/Mechanical – Slim/OB_1735100-F_W2-Assem_2018-10-01/Fan_60x60x38_Generic.SLDPRT

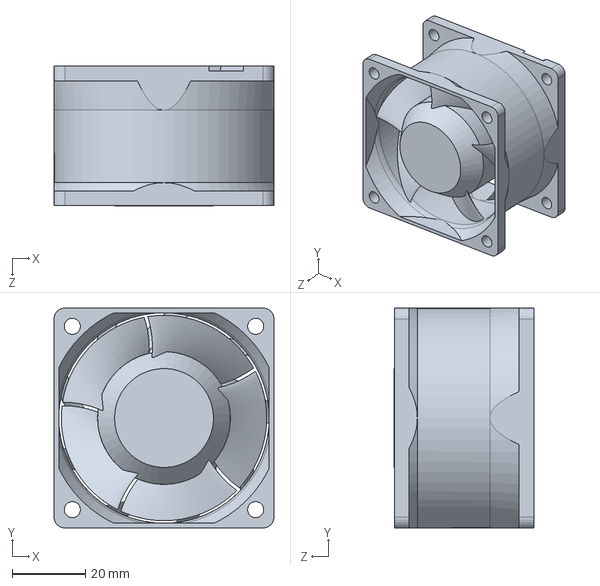
[picture p38: CAD file, 2019-08-30]
Generation 2 Mining Hardware/Mechanical – Slim/OB_1735100-F_W2-Assem_2018-10-01/Fan_60x60x38_Generic.SLDPRT
60.0 x 60.0 x 38.1 mm
