ObeliskInc/obelisk-hardware/Generation 1 Mining Hardware/Mechanical/TE-1719_742921-02_SC1-Assem_PRELIM_051818/RIVET_3-32_97447A110.SLDPRT

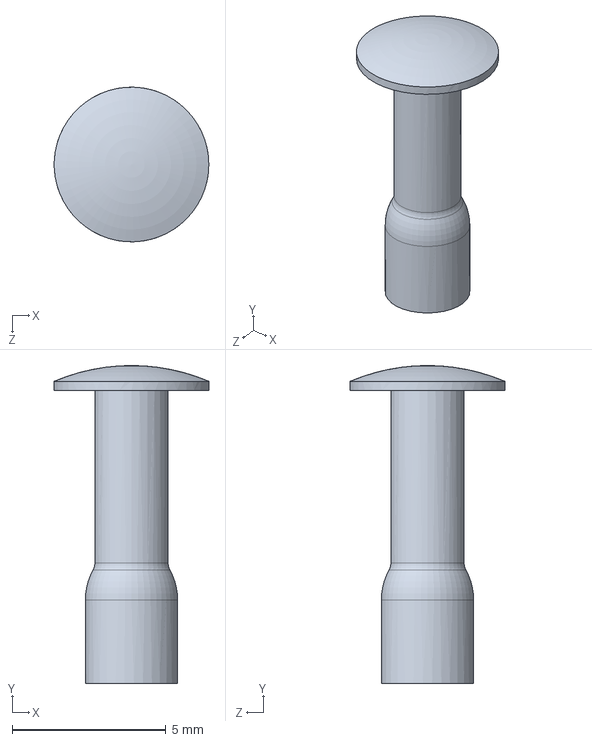
[picture p39: CAD file, 2019-08-30]
Generation 1 Mining Hardware/Mechanical/TE-1719_742921-02_SC1-Assem_PRELIM_051818/RIVET_3-32_97447A110.SLDPRT
5.03 x 10.3 x 5.03 mm
