ObeliskInc/obelisk-hardware/Generation 2 Mining Hardware/Mechanical – Immersion/OB_1735102-D_1U-Rack-Sled-Assem_2018-01-07/OB_1735317-A_1U-Foam-Support.SLDPRT

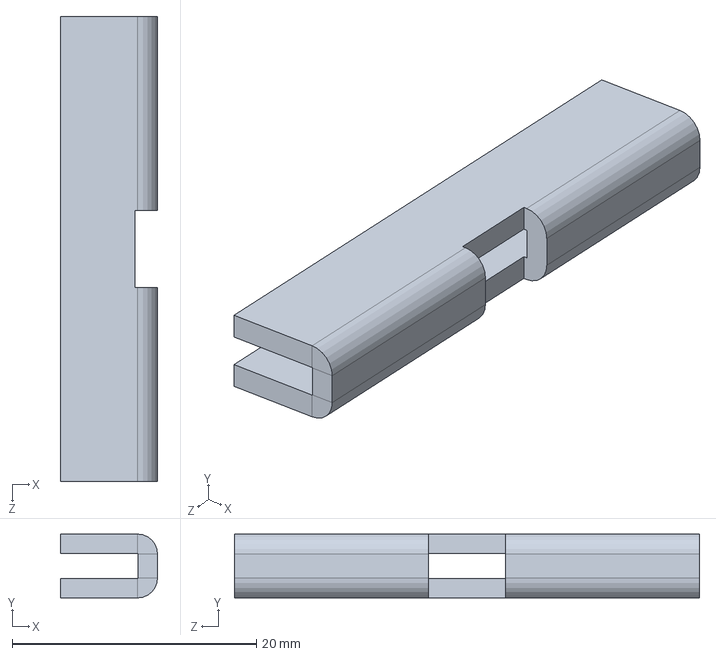
[picture p40: CAD file, 2019-08-30]
Generation 2 Mining Hardware/Mechanical – Immersion/OB_1735102-D_1U-Rack-Sled-Assem_2018-01-07/OB_1735317-A_1U-Foam-Support.SLDPRT
7.95 x 5.23 x 38.1 mm
