ObeliskInc/obelisk-hardware/Generation 2 Mining Hardware/Mechanical – Slim/OB_1735100-F_W2-Assem_2018-10-01/RIVET_1-8_JAY-CEE_PR42FFP.SLDPRT

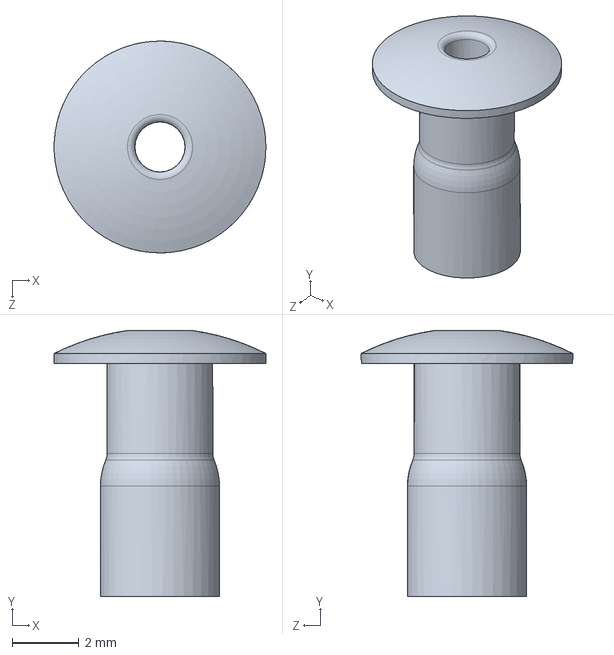
[picture p41: CAD file, 2019-08-30]
Generation 2 Mining Hardware/Mechanical – Slim/OB_1735100-F_W2-Assem_2018-10-01/RIVET_1-8_JAY-CEE_PR42FFP.SLDPRT
6.35 x 7.97 x 6.35 mm
