ObeliskInc/obelisk-hardware/Generation 2 Mining Hardware/Mechanical – Immersion/OB_1735102-D_1U-Rack-Sled-Assem_2018-01-07/MP1000-1121 BACK PLATE.SLDPRT

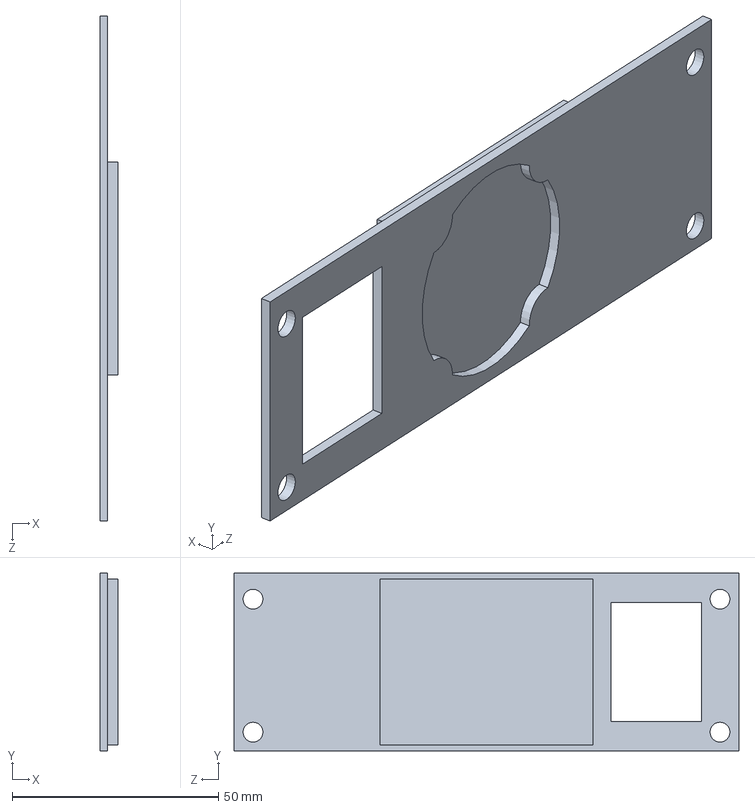
[picture p42: CAD file, 2019-08-30]
Generation 2 Mining Hardware/Mechanical – Immersion/OB_1735102-D_1U-Rack-Sled-Assem_2018-01-07/MP1000-1121 BACK PLATE.SLDPRT
4.45 x 43.2 x 122.4 mm
