ObeliskInc/obelisk-hardware/Generation 2 Mining Hardware/Mechanical – Slim/OB_1735100-F_W2-Assem_2018-10-01/OB_1735306-A_Foam-Block-Air-Guide.SLDPRT

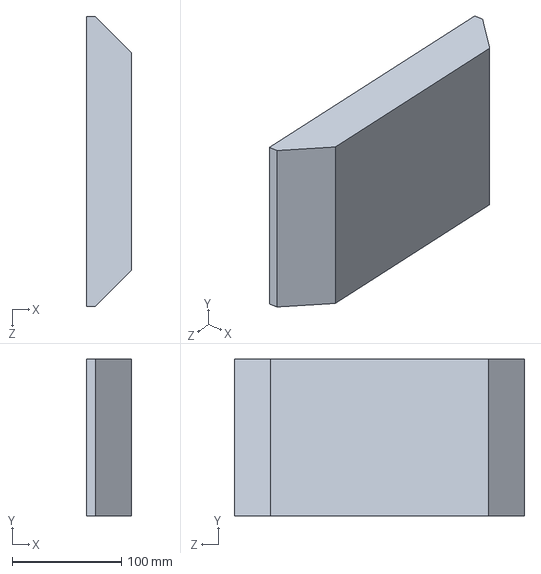
[picture p43: CAD file, 2019-08-30]
Generation 2 Mining Hardware/Mechanical – Slim/OB_1735100-F_W2-Assem_2018-10-01/OB_1735306-A_Foam-Block-Air-Guide.SLDPRT
41.0 x 144.0 x 266.0 mm
