ObeliskInc/obelisk-hardware/Generation 1 Mining Hardware/Mechanical/TE-1719_742921-02_SC1-Assem_PRELIM_051818/TE-1719_742929-01_SC1-Upper-Guide.SLDPRT

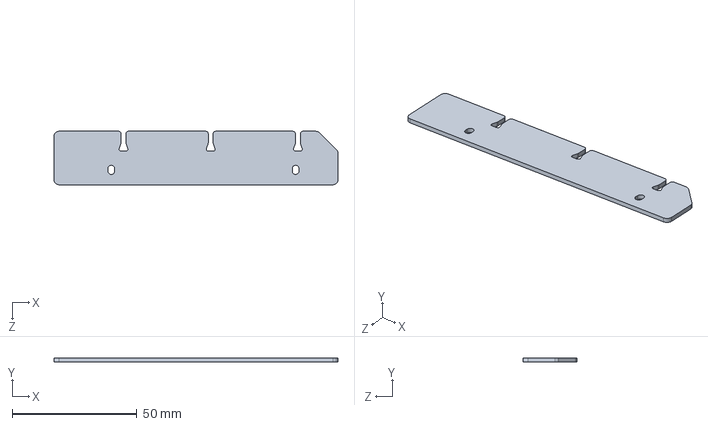
[picture p44: CAD file, 2019-08-30]
Generation 1 Mining Hardware/Mechanical/TE-1719_742921-02_SC1-Assem_PRELIM_051818/TE-1719_742929-01_SC1-Upper-Guide.SLDPRT
114.0 x 1.59 x 21.5 mm
