ObeliskInc/obelisk-hardware/Generation 1 Mining Hardware/Mechanical/TE-1719_742921-02_SC1-Assem_PRELIM_051818/STICKER_FRONT.SLDPRT

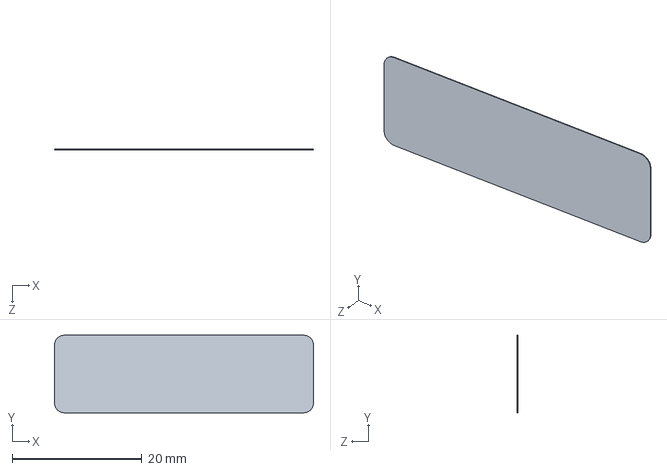
[picture p45: CAD file, 2019-08-30]
Generation 1 Mining Hardware/Mechanical/TE-1719_742921-02_SC1-Assem_PRELIM_051818/STICKER_FRONT.SLDPRT
40.0 x 12.0 x 0.1 mm
