ObeliskInc/obelisk-hardware/Generation 2 Mining Hardware/Mechanical – Slim/OB_1735100-F_W2-Assem_2018-10-01/OB_1735308-A_Grill-Foam-Strip-Lower.SLDPRT

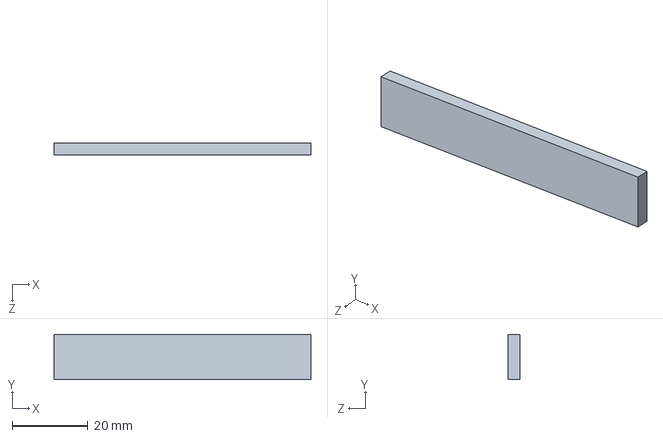
[picture p46: CAD file, 2019-08-30]
Generation 2 Mining Hardware/Mechanical – Slim/OB_1735100-F_W2-Assem_2018-10-01/OB_1735308-A_Grill-Foam-Strip-Lower.SLDPRT
68.0 x 12.0 x 3.05 mm
