ObeliskInc/obelisk-hardware/Generation 1 Mining Hardware/Mechanical/TE-1719_742921-02_SC1-Assem_PRELIM_051818/PEM-Standoff_BSO-440-18ZI.SLDPRT

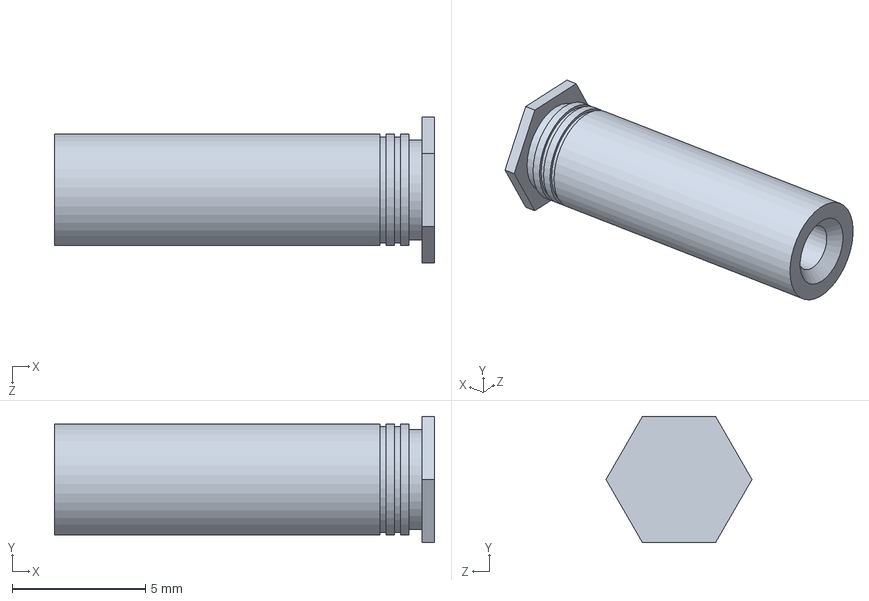
[picture p47: CAD file, 2019-08-30]
Generation 1 Mining Hardware/Mechanical/TE-1719_742921-02_SC1-Assem_PRELIM_051818/PEM-Standoff_BSO-440-18ZI.SLDPRT
14.3 x 4.75 x 5.48 mm
