ObeliskInc/obelisk-hardware/Generation 2 Mining Hardware/Mechanical – Immersion/OB_1735102-D_1U-Rack-Sled-Assem_2018-01-07/OB_1735316-C_1U-Corner-Panel.SLDPRT

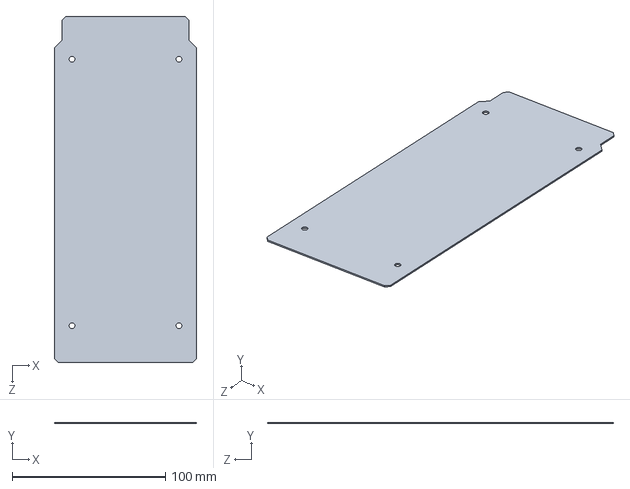
[picture p48: CAD file, 2019-08-30]
Generation 2 Mining Hardware/Mechanical – Immersion/OB_1735102-D_1U-Rack-Sled-Assem_2018-01-07/OB_1735316-C_1U-Corner-Panel.SLDPRT
92.7 x 0.914 x 226.1 mm
