ObeliskInc/obelisk-hardware/Generation 2 Mining Hardware/Mechanical – Immersion/OB_1735102-D_1U-Rack-Sled-Assem_2018-01-07/Copy of 3M_89120_0101^SC1B_RevB- HashBoard_withHS_Heal-Import.SLDPRT

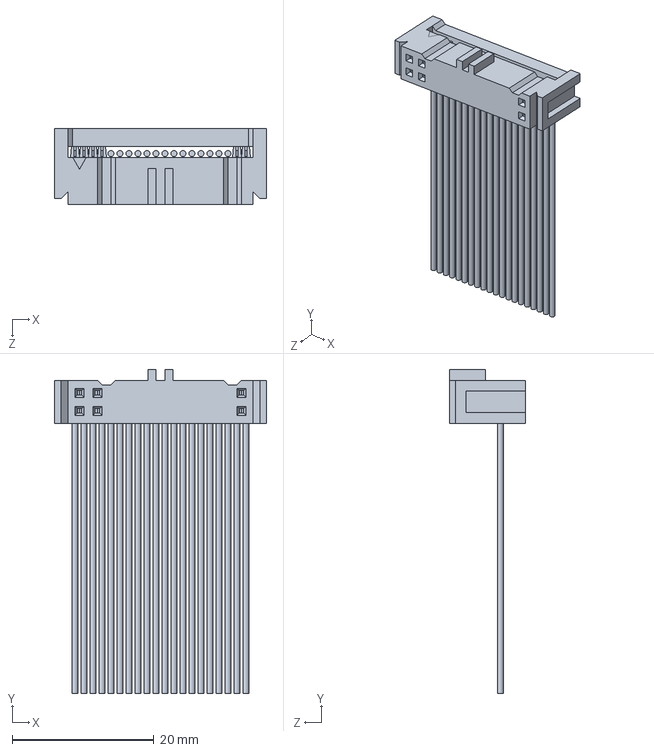
[picture p49: CAD file, 2019-08-30]
Generation 2 Mining Hardware/Mechanical – Immersion/OB_1735102-D_1U-Rack-Sled-Assem_2018-01-07/Copy of 3M_89120_0101^SC1B_RevB- HashBoard_withHS_Heal-Import.SLDPRT
30.0 x 45.7 x 10.7 mm
