ObeliskInc/obelisk-hardware/Generation 2 Mining Hardware/Mechanical – Immersion/OB_1735102-D_1U-Rack-Sled-Assem_2018-01-07/HANDLE_Hammond-1427B2BK-1.SLDPRT

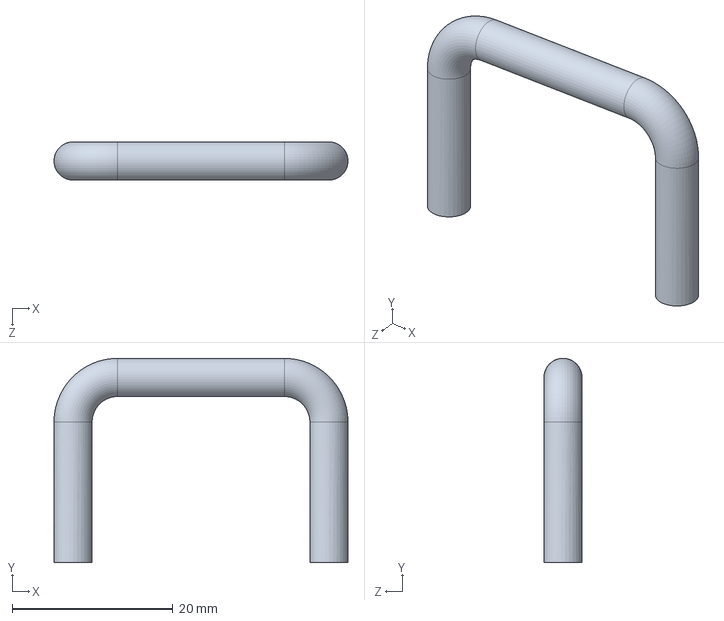
[picture p51: CAD file, 2019-08-30]
Generation 2 Mining Hardware/Mechanical – Immersion/OB_1735102-D_1U-Rack-Sled-Assem_2018-01-07/HANDLE_Hammond-1427B2BK-1.SLDPRT
36.5 x 25.4 x 4.75 mm
