ObeliskInc/obelisk-hardware/Generation 2 Mining Hardware/Mechanical – Immersion/OB_1735102-D_1U-Rack-Sled-Assem_2018-01-07/MP1000-1121 PCB SPACER.SLDPRT

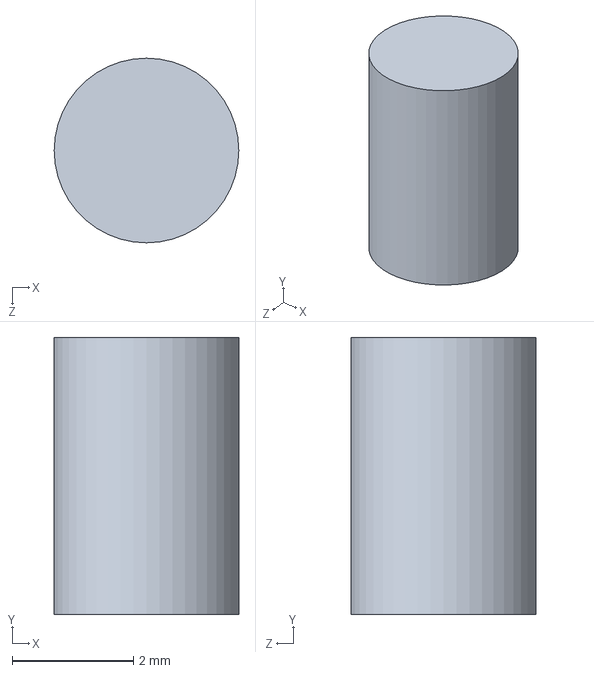
[picture p52: CAD file, 2019-08-30]
Generation 2 Mining Hardware/Mechanical – Immersion/OB_1735102-D_1U-Rack-Sled-Assem_2018-01-07/MP1000-1121 PCB SPACER.SLDPRT
3.05 x 4.57 x 3.05 mm
