ObeliskInc/obelisk-hardware/Generation 2 Mining Hardware/Mechanical – Immersion/OB_1735102-D_1U-Rack-Sled-Assem_2018-01-07/MP1000-1121 FAN CAP.SLDPRT

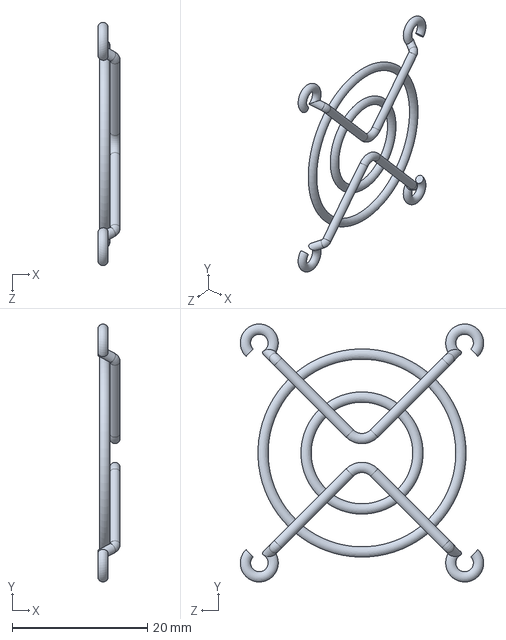
[picture p53: CAD file, 2019-08-30]
Generation 2 Mining Hardware/Mechanical – Immersion/OB_1735102-D_1U-Rack-Sled-Assem_2018-01-07/MP1000-1121 FAN CAP.SLDPRT
3.30 x 38.1 x 35.9 mm
