ObeliskInc/obelisk-hardware/Generation 2 Mining Hardware/Mechanical – Immersion/OB_1735102-D_1U-Rack-Sled-Assem_2018-01-07/APS-Power-Supply_01.SLDPRT

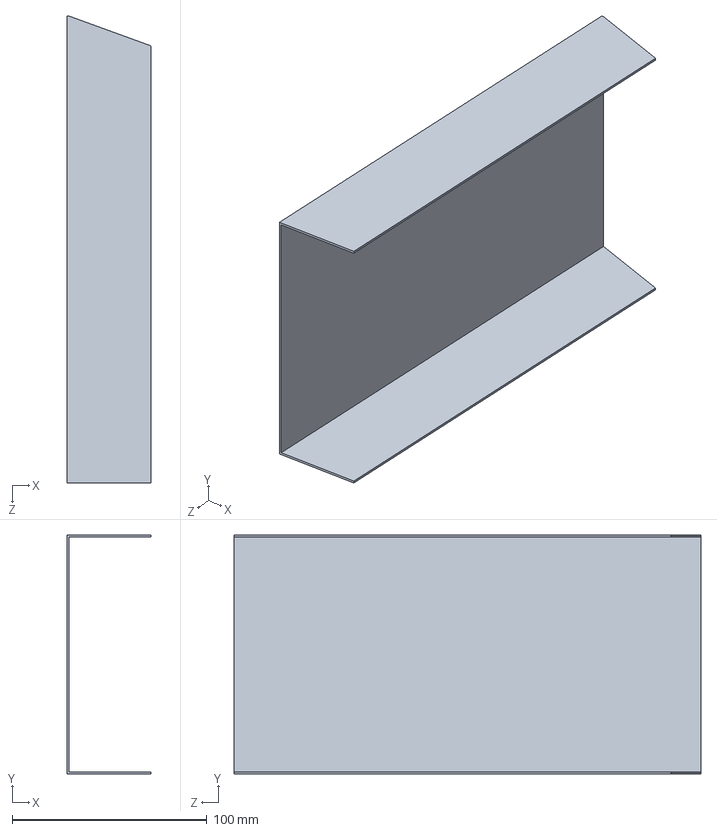
[picture p55: CAD file, 2019-08-30]
Generation 2 Mining Hardware/Mechanical – Immersion/OB_1735102-D_1U-Rack-Sled-Assem_2018-01-07/APS-Power-Supply_01.SLDPRT
43.2 x 122.4 x 239.6 mm
