ObeliskInc/obelisk-hardware/Generation 2 Mining Hardware/Mechanical – Immersion/OB_1735102-D_1U-Rack-Sled-Assem_2018-01-07/OB_1735312-E_1U-Front-Panel.SLDPRT

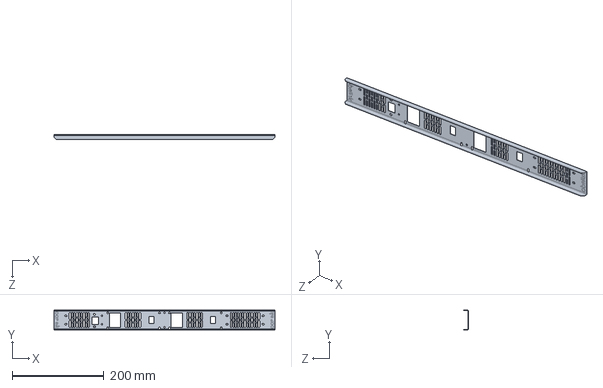
[picture p57: CAD file, 2019-08-30]
Generation 2 Mining Hardware/Mechanical – Immersion/OB_1735102-D_1U-Rack-Sled-Assem_2018-01-07/OB_1735312-E_1U-Front-Panel.SLDPRT
482.6 x 43.0 x 10.2 mm
