ObeliskInc/obelisk-hardware/Generation 2 Mining Hardware/Mechanical – Immersion/OB_1735102-D_1U-Rack-Sled-Assem_2018-01-07/OB_1735313-B_1U-Top-Cover.SLDPRT

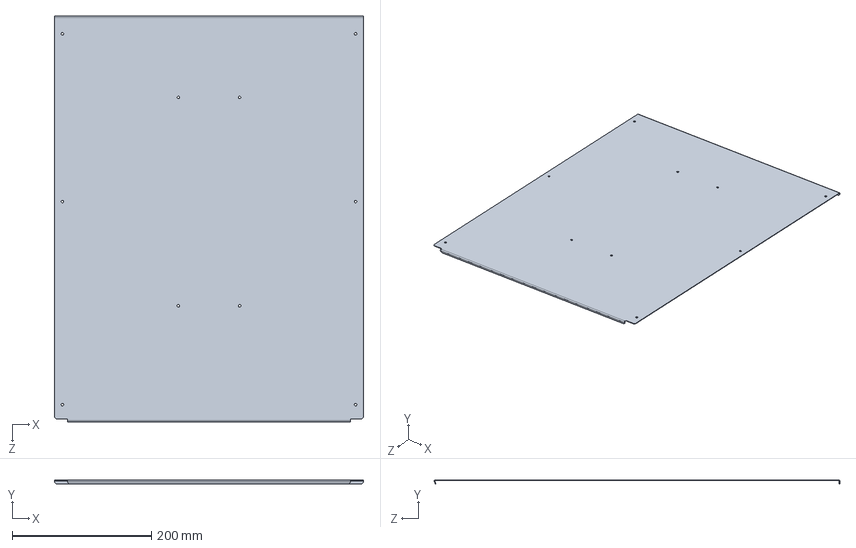
[picture p58: CAD file, 2019-08-30]
Generation 2 Mining Hardware/Mechanical – Immersion/OB_1735102-D_1U-Rack-Sled-Assem_2018-01-07/OB_1735313-B_1U-Top-Cover.SLDPRT
444.5 x 6.35 x 583.5 mm
