ObeliskInc/obelisk-hardware/Generation 2 Mining Hardware/Mechanical – Immersion/OB_1735102-D_1U-Rack-Sled-Assem_2018-01-07/MP1000-1121 PCB.SLDPRT

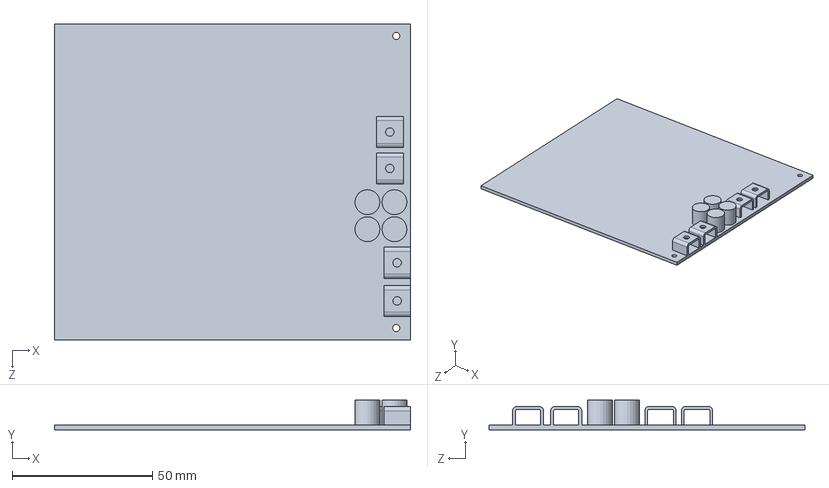
[picture p59: CAD file, 2019-08-30]
Generation 2 Mining Hardware/Mechanical – Immersion/OB_1735102-D_1U-Rack-Sled-Assem_2018-01-07/MP1000-1121 PCB.SLDPRT
127.0 x 10.7 x 112.9 mm
