ObeliskInc/obelisk-hardware/Generation 2 Mining Hardware/Mechanical – Immersion/OB_1735102-D_1U-Rack-Sled-Assem_2018-01-07/OB_1735313-C_1U-Top-Cover.SLDPRT

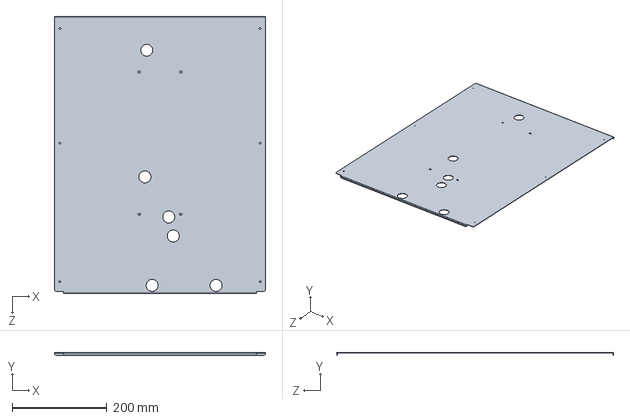
[picture p60: CAD file, 2019-08-30]
Generation 2 Mining Hardware/Mechanical – Immersion/OB_1735102-D_1U-Rack-Sled-Assem_2018-01-07/OB_1735313-C_1U-Top-Cover.SLDPRT
444.5 x 6.35 x 583.5 mm
