ObeliskInc/obelisk-hardware/Generation 2 Mining Hardware/Mechanical – Immersion/OB_1735102-D_1U-Rack-Sled-Assem_2018-01-07/ETHERNET_RJ45-Panel-Mount-Extension-Cable.SLDPRT

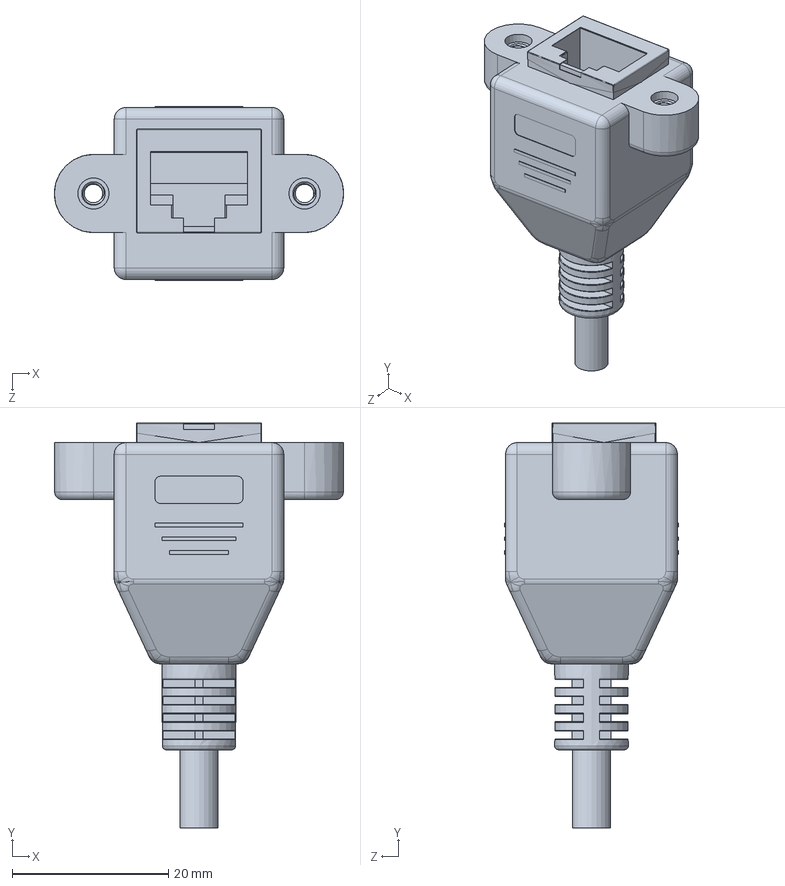
[picture p61: CAD file, 2019-08-30]
Generation 2 Mining Hardware/Mechanical – Immersion/OB_1735102-D_1U-Rack-Sled-Assem_2018-01-07/ETHERNET_RJ45-Panel-Mount-Extension-Cable.SLDPRT
37.0 x 51.8 x 22.2 mm
