ObeliskInc/obelisk-hardware/Generation 2 Mining Hardware/Mechanical – Immersion/OB_1735102-D_1U-Rack-Sled-Assem_2018-01-07/PEM-STANDOFF_BSO-440-10ZI.SLDPRT

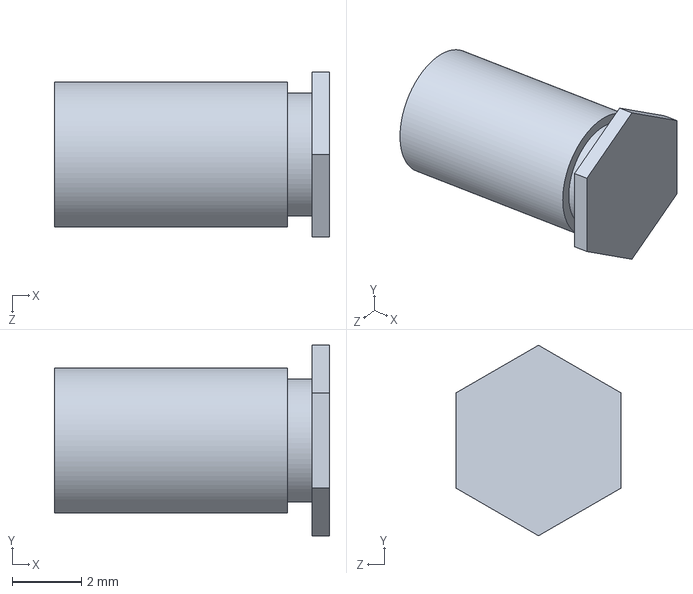
[picture p63: CAD file, 2019-08-30]
Generation 2 Mining Hardware/Mechanical – Immersion/OB_1735102-D_1U-Rack-Sled-Assem_2018-01-07/PEM-STANDOFF_BSO-440-10ZI.SLDPRT
7.94 x 5.50 x 4.76 mm
