ObeliskInc/obelisk-hardware/Generation 2 Mining Hardware/Mechanical – Immersion/OB_1735313-C_1U-Top-Cover.PDF

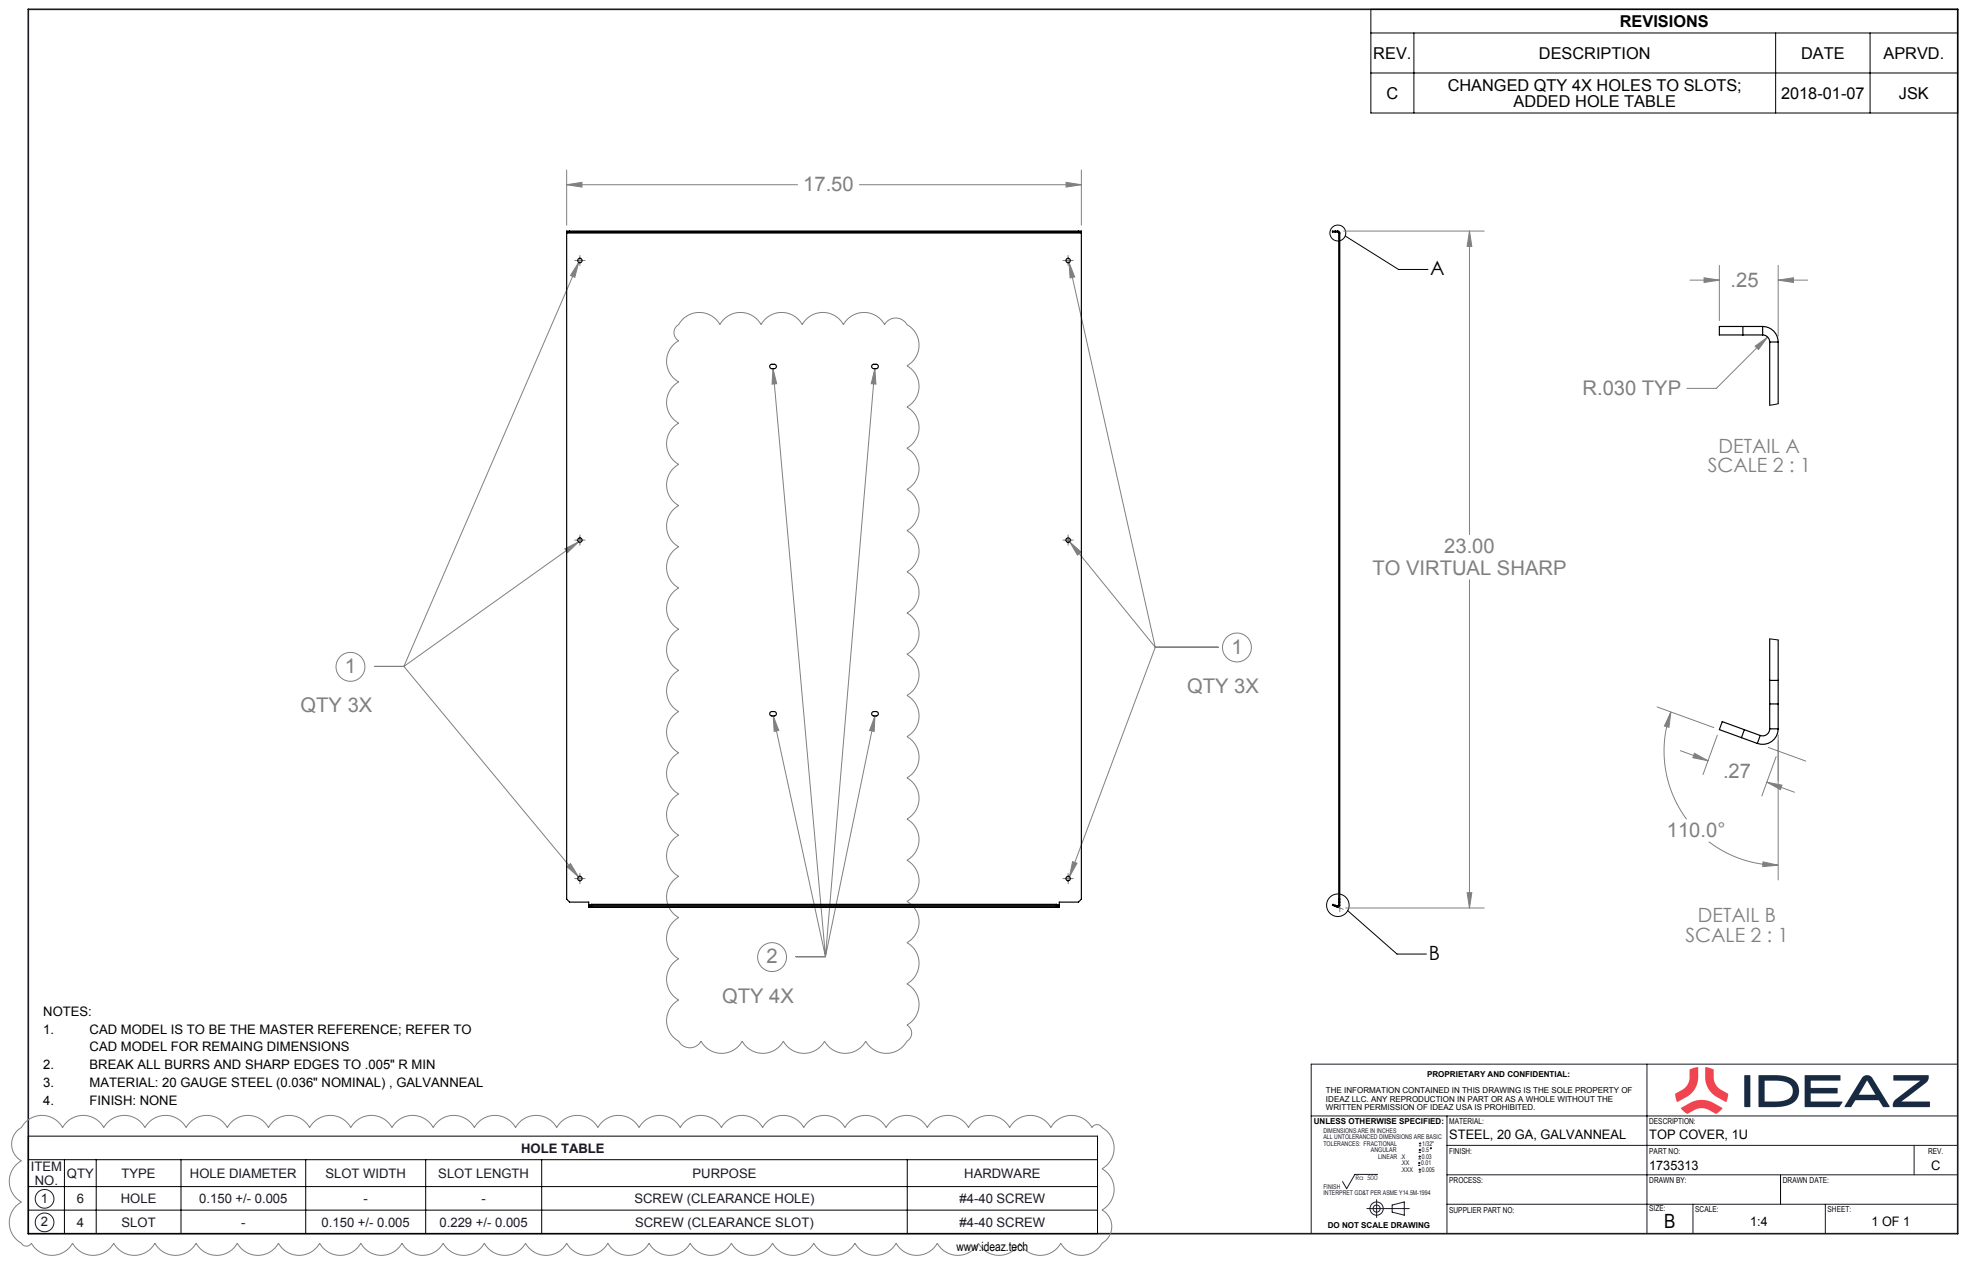
[picture p73: page 1]
QTY 3X; QTY 4X; DETAIL B SCALE 2 : 1; R.030 TYP; DETAIL A SCALE 2 : 1; HOLE TABLE

REVISIONS

REV. | DESCRIPTION | DATE | APRVD.
C | CHANGED QTY 4X HOLES TO SLOTS; ADDED HOLE TABLE | 2018-01-07 | JSK

TO VIRTUAL SHARP

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

FINISH: | PART NO: REV. 1735313 C

ITEM NO. | QTY | TYPE | HOLE DIAMETER | SLOT WIDTH | SLOT LENGTH | PURPOSE | HARDWARE
1 | 6 | HOLE | 0.150 +/- 0.005 | - | - | SCREW (CLEARANCE HOLE) | #4-40 SCREW
SUPPLIER PART NO: | SIZE: B | SCALE: 1:4 | SHEET: 1 OF 1
2 | 4 | SLOT | - | 0.150 +/- 0.005 | 0.229 +/- 0.005 | SCREW (CLEARANCE SLOT) | #4-40 SCREW

PROCESS: | DRAWN BY: | DRAWN DATE:

www.ideaz.tech
