ObeliskInc/obelisk-hardware/Generation 2 Mining Hardware/Mechanical – Immersion/OB_1735314-C_1U-Inner-Bracket.PDF

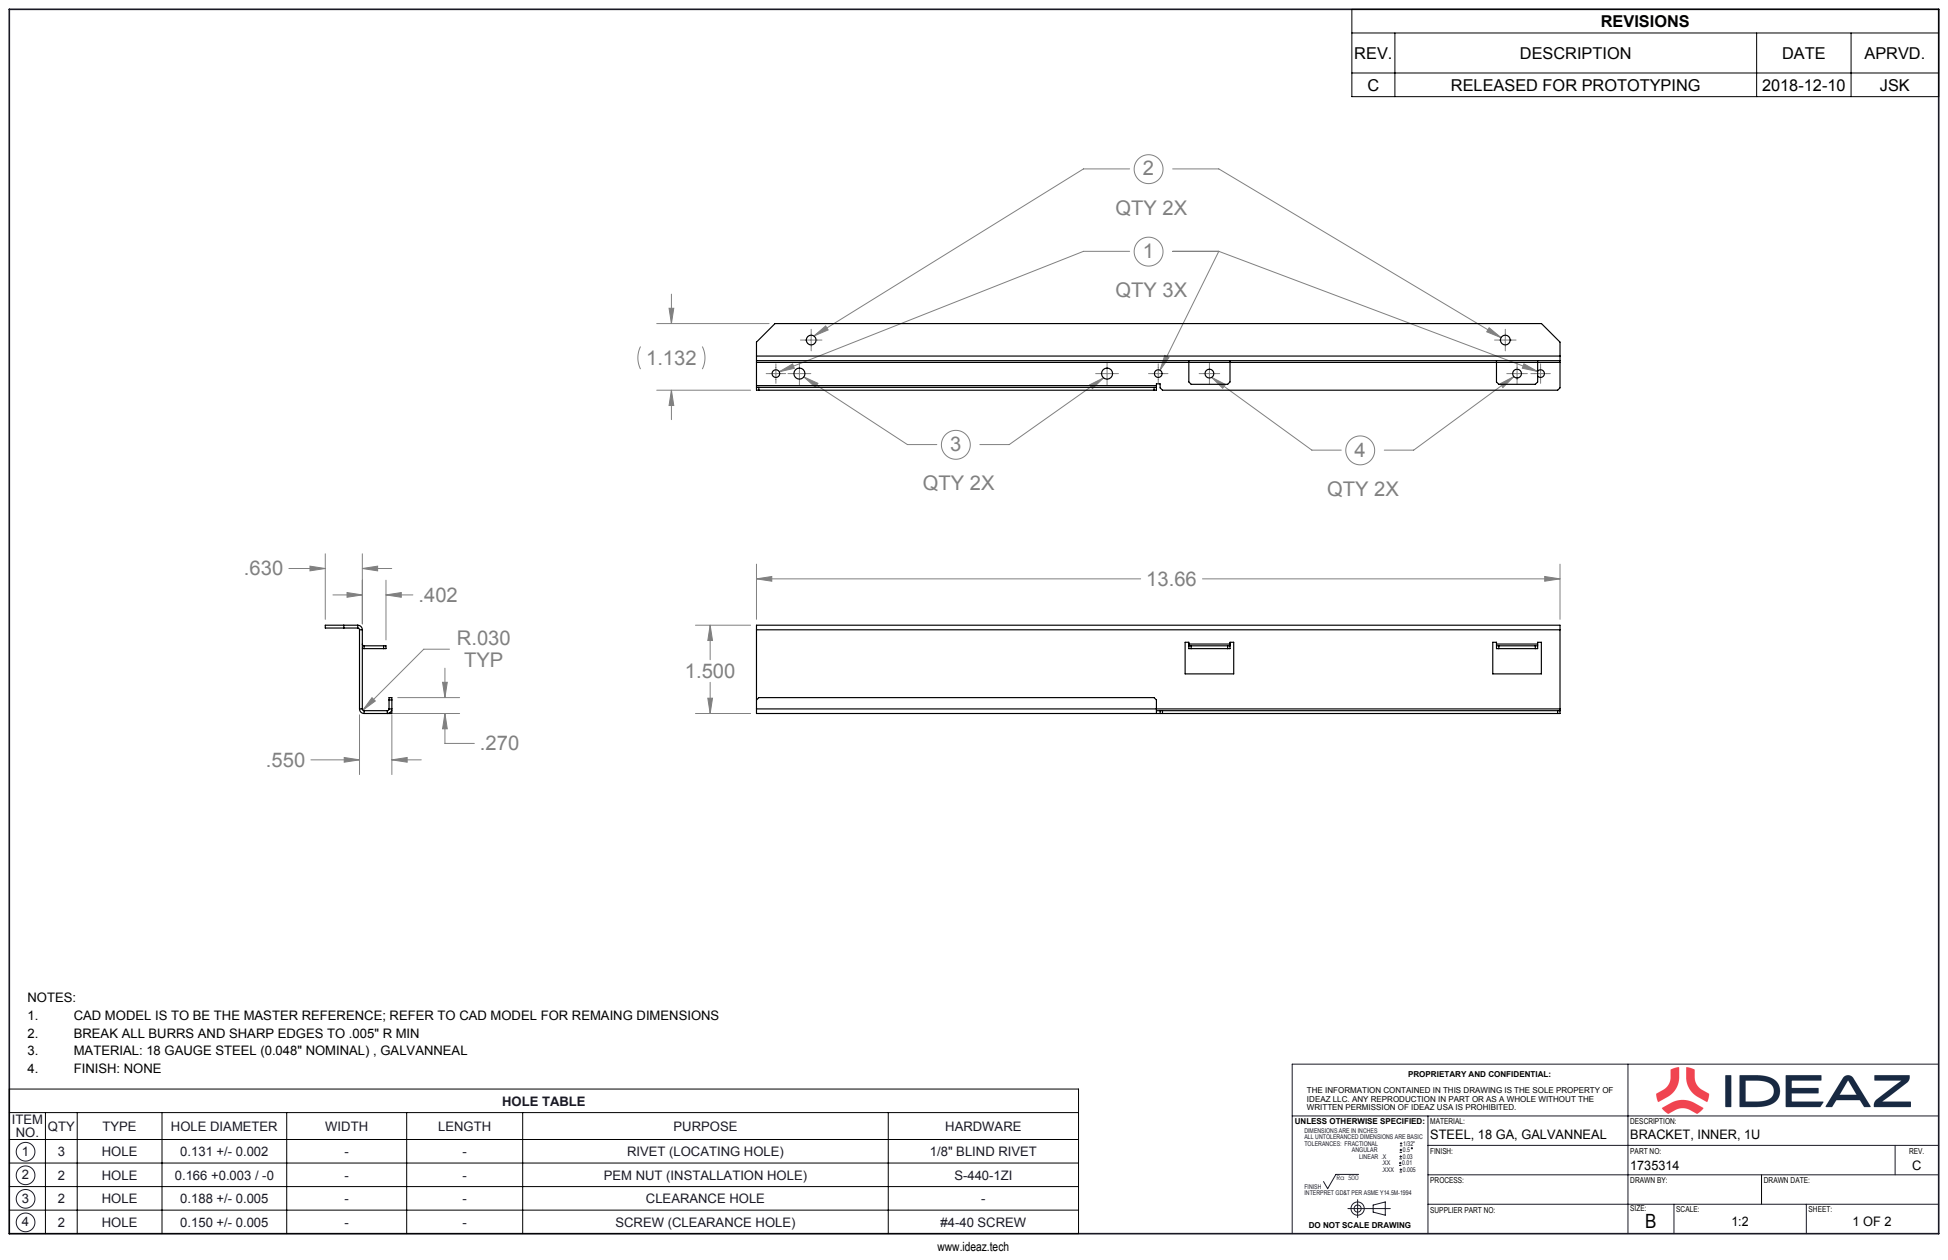
[picture p74: page 1]
TOLERANCES: FRACTIONAL; LINEAR .X; .XXX 0.005; QTY 3X; QTY 2X; HOLE TABLE; QTY; TYPE; HOLE DIAMETER; WIDTH; LENGTH; PURPOSE; HARDWARE; BRACKET, INNER, 1U

REVISIONS

REV. | DESCRIPTION | DATE | APRVD.
C | RELEASED FOR PROTOTYPING | 2018-12-10 | JSK

NOTES:
1. CAD MODEL IS TO BE THE MASTER REFERENCE; REFER TO CAD MODEL FOR REMAING DIMENSIONS
2. BREAK ALL BURRS AND SHARP EDGES TO .005" R MIN
3. MATERIAL: 18 GAUGE STEEL (0.048" NOMINAL) , GALVANNEAL
4. FINISH: NONE

PROPRIETARY AND CONFIDENTIAL:

THE INFORMATION CONTAINED IN THIS DRAWING IS THE SOLE PROPERTY OF
IDEAZ LLC. ANY REPRODUCTION IN PART OR AS A WHOLE WITHOUT THE
WRITTEN PERMISSION OF IDEAZ USA IS PROHIBITED.
UNLESS OTHERWISE SPECIFIED:
DIMENSIONS ARE IN INCHES
ALL UNTOLERANCED DIMENSIONS ARE BASIC

MATERIAL:
STEEL, 18 GA, GALVANNEAL

1 | 3 | HOLE | 0.131 +/- 0.002 | - | - | RIVET (LOCATING HOLE) | 1/8" BLIND RIVET
2 | 2 | HOLE | 0.166 +0.003 / -0 | - | - | PEM NUT (INSTALLATION HOLE) | S-440-1ZI
3 | 2 | HOLE | 0.188 +/- 0.005 | - | - | CLEARANCE HOLE | -
4 | 2 | HOLE | 0.150 +/- 0.005 | - | - | SCREW (CLEARANCE HOLE) | #4-40 SCREW

FINISH: | PART NO: REV. 1735314 C

FINISH
INTERPRET GD&T PER ASME Y14.5M-1994

PROCESS: | DRAWN BY: | DRAWN DATE:
SUPPLIER PART NO: | SIZE: B | SCALE: 1:2 | SHEET: 1 OF 2

DO NOT SCALE DRAWING

www.ideaz.tech

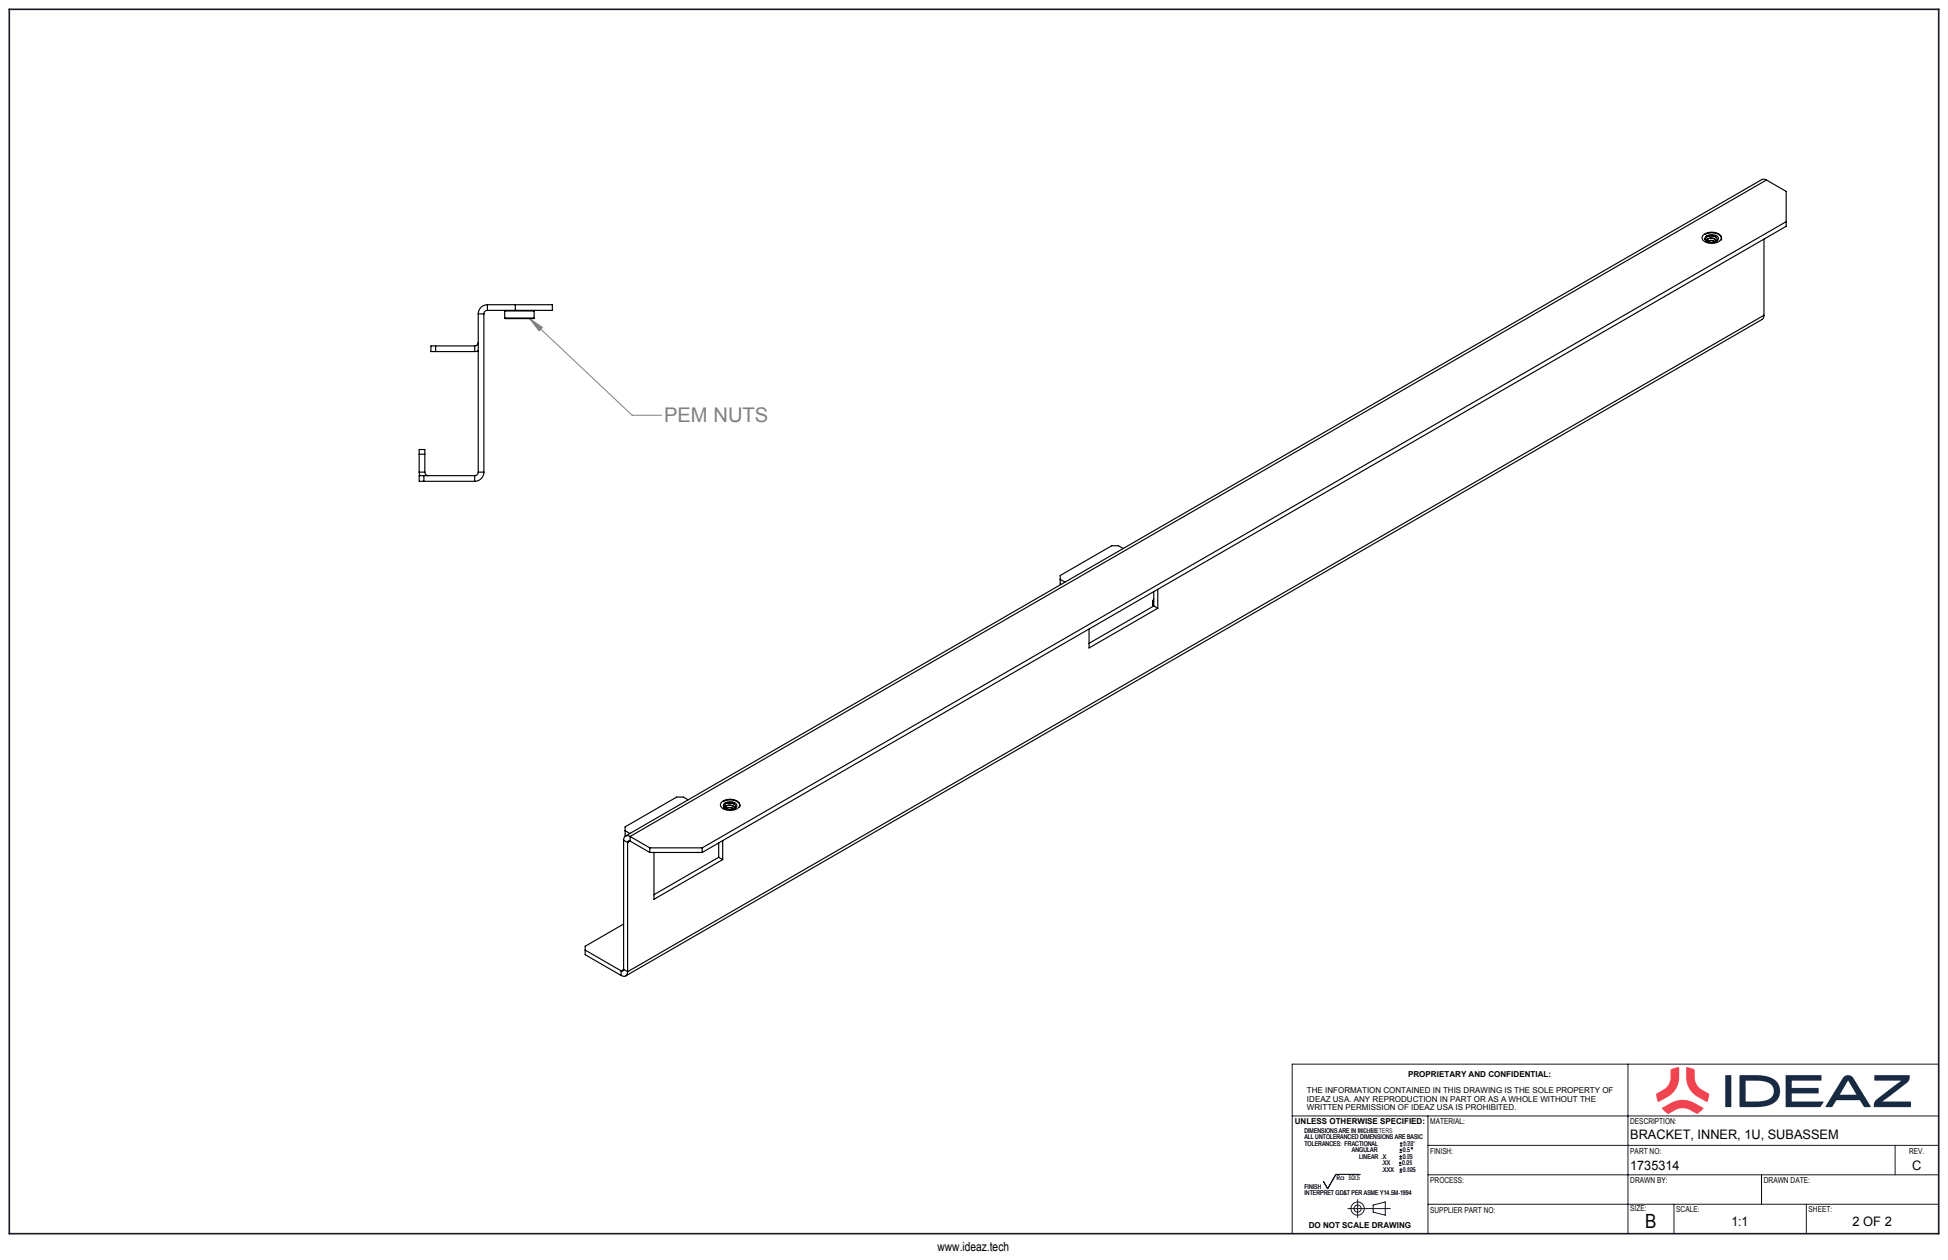
[picture p75: page 2]
PEM NUTS

PROPRIETARY AND CONFIDENTIAL: THE INFORMATION CONTAINED IN THIS DRAWING IS THE SOLE PROPERTY OF IDEAZ USA. ANY REPRODUCTION IN PART OR AS A WHOLE WITHOUT THE WRITTEN PERMISSION OF IDEAZ USA IS PROHIBITED.

UNLESS OTHERWISE SPECIFIED: DIMENSIONS ARE IN INCHES DIMENSIONS ARE IN MILLIMETERS ALL UNTOLERANCED DIMENSIONS ARE BASIC ALL UNTOLERANCED DIMENSIONS ARE BASIC TOLERANCES: FRACTIONAL TOLERANCES: FRACTIONAL 1/32" 0.75 ANGULAR ANGULAR 0.5 0.5 LINEAR .X LINEAR .X 0.03 0.75 .XX .XX 0.01 0.25 .XXX 0.005 .XXX 0.125 Ra 500 Ra 12.5 FINISH FINISH INTERPRET GD&T PER ASME Y14.5M-1994 INTERPRET GD&T PER ASME Y14.5M-1994 DO NOT SCALE DRAWING | MATERIAL: | DESCRIPTION: BRACKET, INNER, 1U, SUBASSEM

FINISH: | PART NO: REV. 1735314 C

PROCESS: | DRAWN BY: | DRAWN DATE:
SUPPLIER PART NO: | SIZE: B | SCALE: 1:1 | SHEET: 2 OF 2

www.ideaz.tech
