ObeliskInc/obelisk-hardware/Generation 2 Mining Hardware/Mechanical – Slim/OB_1735300-D_W2-Front-Grill.PDF

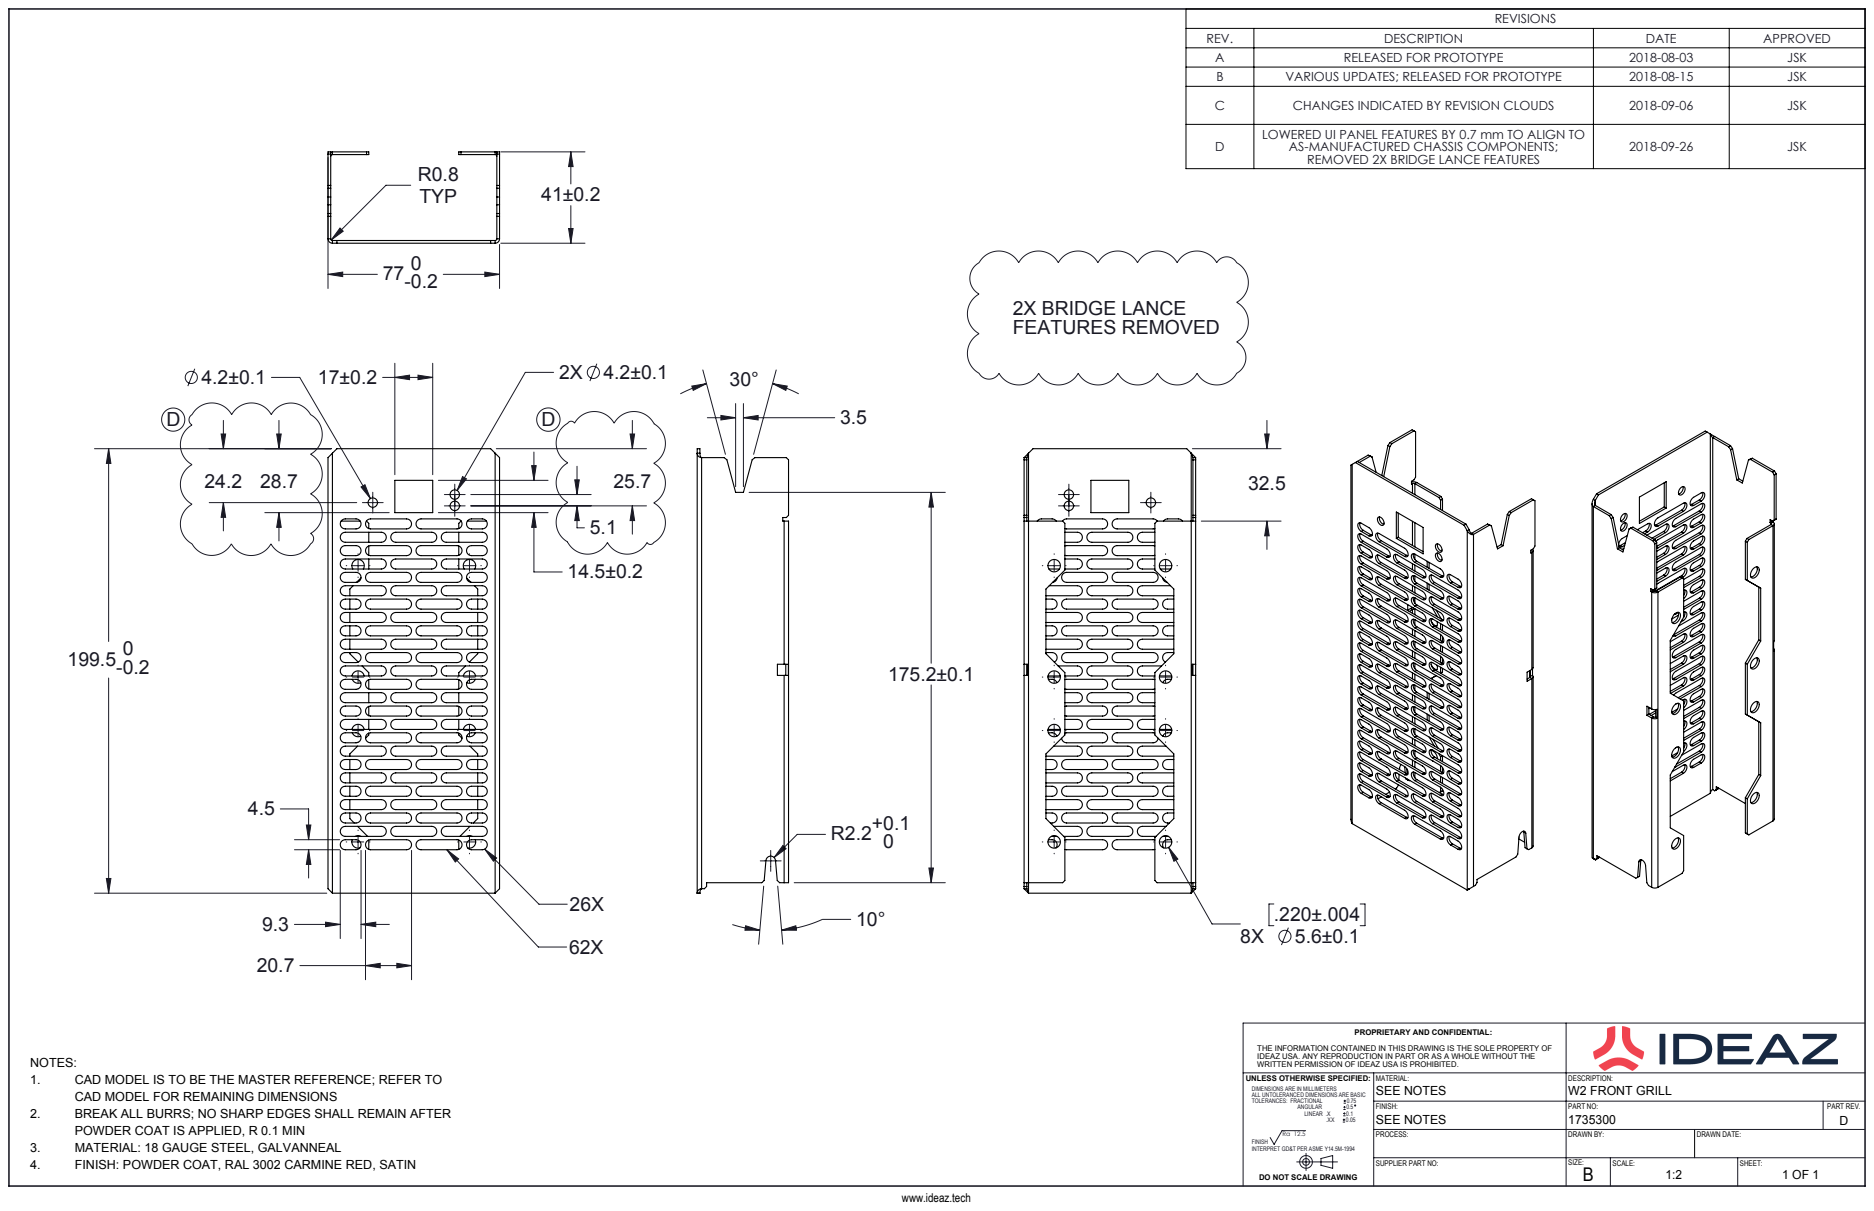
[picture p76: page 1]
2X BRIDGE LANCE FEATURES REMOVED

REVISIONS

REV. | DESCRIPTION | DATE | APPROVED
A | RELEASED FOR PROTOTYPE | 2018-08-03 | JSK
B | VARIOUS UPDATES; RELEASED FOR PROTOTYPE | 2018-08-15 | JSK
C | CHANGES INDICATED BY REVISION CLOUDS | 2018-09-06 | JSK
D | LOWERED UI PANEL FEATURES BY 0.7 mm TO ALIGN TO AS-MANUFACTURED CHASSIS COMPONENTS; REMOVED 2X BRIDGE LANCE FEATURES | 2018-09-26 | JSK

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

NOTES:
1. CAD MODEL IS TO BE THE MASTER REFERENCE; REFER TO
CAD MODEL FOR REMAINING DIMENSIONS
2. BREAK ALL BURRS; NO SHARP EDGES SHALL REMAIN AFTER
POWDER COAT IS APPLIED, R 0.1 MIN
3. MATERIAL: 18 GAUGE STEEL, GALVANNEAL
4. FINISH: POWDER COAT, RAL 3002 CARMINE RED, SATIN

UNLESS OTHERWISE SPECIFIED: DIMENSIONS ARE IN MILLIMETERS ALL UNTOLERANCED DIMENSIONS ARE BASIC TOLERANCES: FRACTIONAL 0.75 ANGULAR 0.5 LINEAR .X 0.1 .XX 0.05 Ra 12.5 FINISH INTERPRET GD&T PER ASME Y14.5M-1994 DO NOT SCALE DRAWING | MATERIAL: SEE NOTES | DESCRIPTION: W2 FRONT GRILL

FINISH: SEE NOTES | PART NO: PART REV. 1735300 D

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

www.ideaz.tech
