ObeliskInc/obelisk-hardware/Generation 2 Mining Hardware/Mechanical – Slim/OB_1735302-D_W2-Cover.PDF

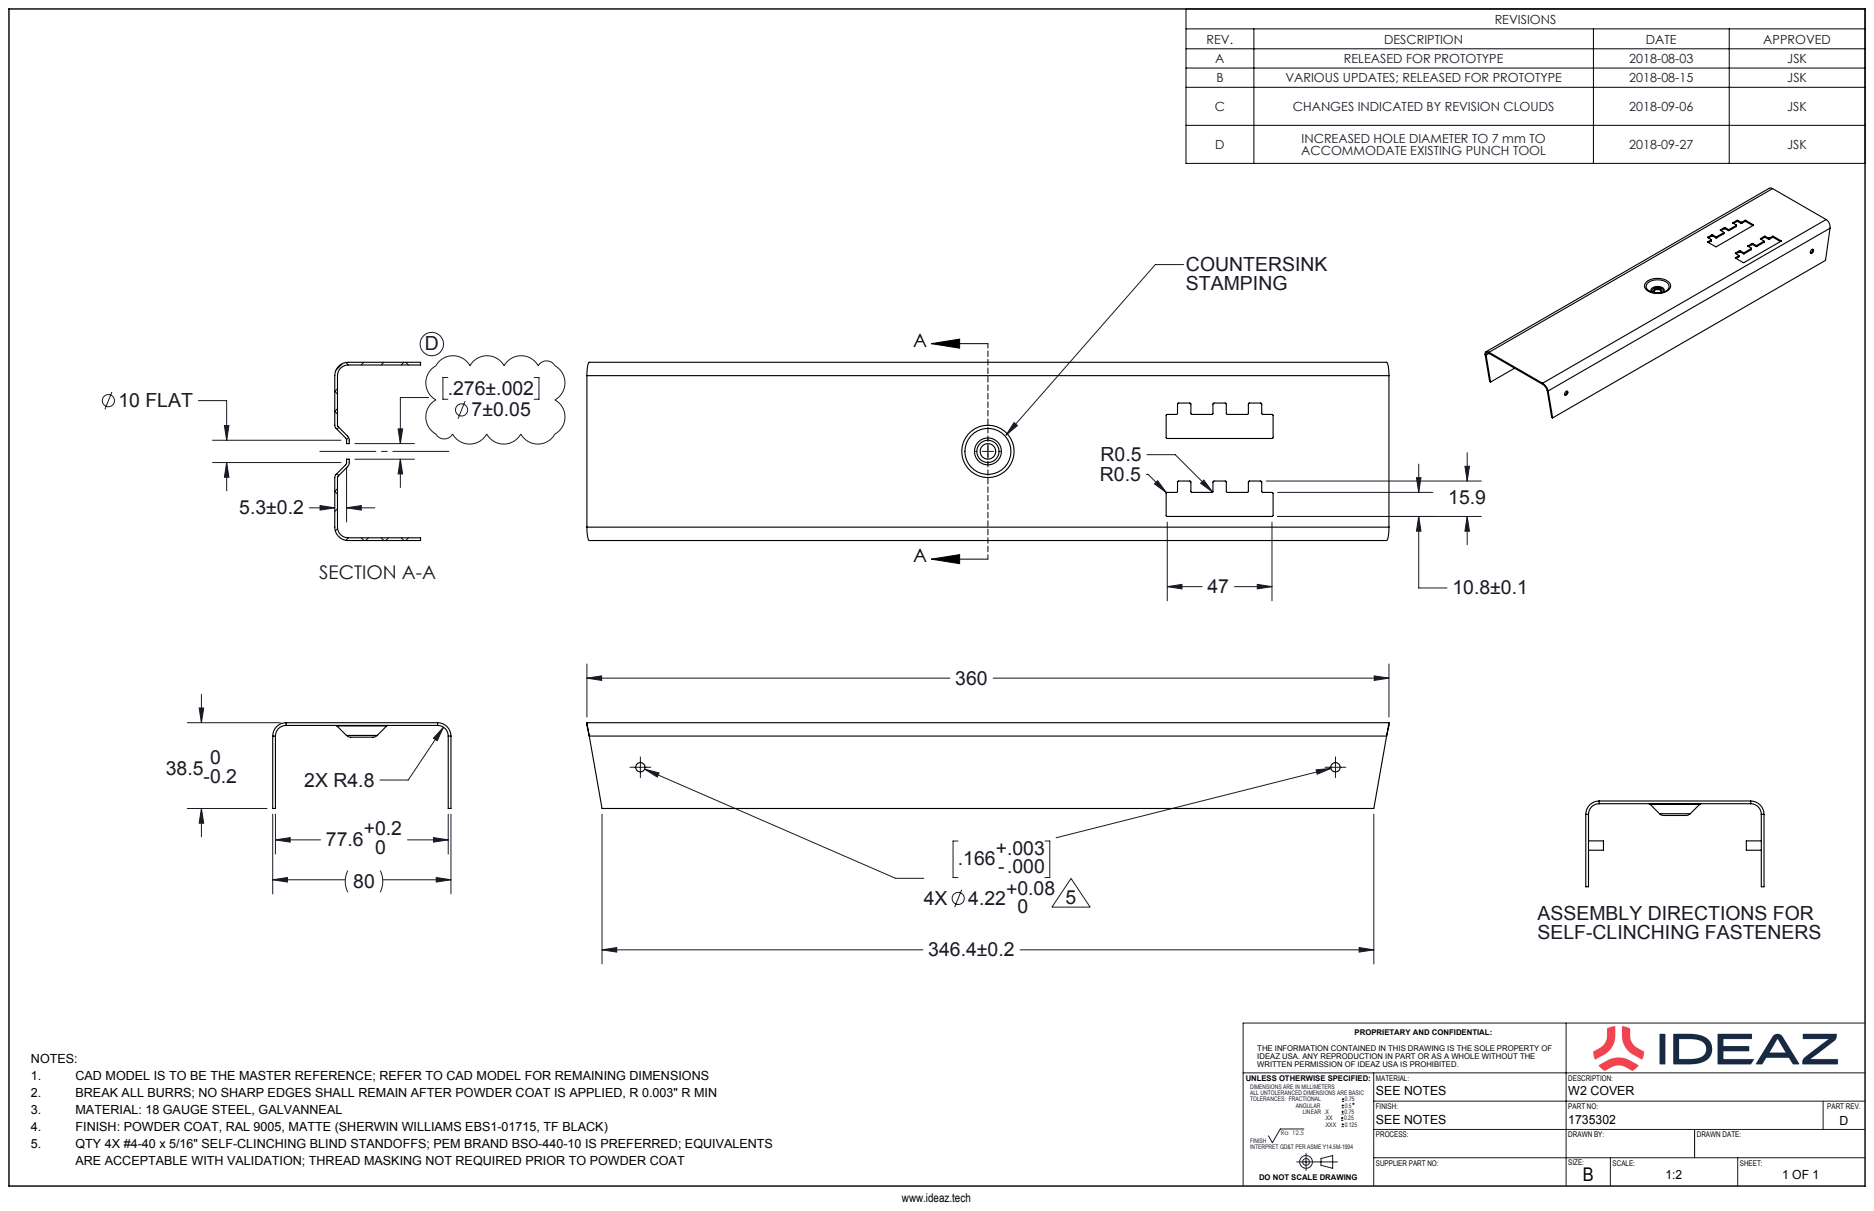
[picture p77: page 1]
10 FLAT; SECTION A-A

REVISIONS

REV. | DESCRIPTION | DATE | APPROVED
A | RELEASED FOR PROTOTYPE | 2018-08-03 | JSK
B | VARIOUS UPDATES; RELEASED FOR PROTOTYPE | 2018-08-15 | JSK
C | CHANGES INDICATED BY REVISION CLOUDS | 2018-09-06 | JSK
D | INCREASED HOLE DIAMETER TO 7 mm TO ACCOMMODATE EXISTING PUNCH TOOL | 2018-09-27 | JSK

ASSEMBLY DIRECTIONS FOR
SELF-CLINCHING FASTENERS

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

NOTES:
1. CAD MODEL IS TO BE THE MASTER REFERENCE; REFER TO CAD MODEL FOR REMAINING DIMENSIONS
2. BREAK ALL BURRS; NO SHARP EDGES SHALL REMAIN AFTER POWDER COAT IS APPLIED, R 0.003" R MIN
3. MATERIAL: 18 GAUGE STEEL, GALVANNEAL
4. FINISH: POWDER COAT, RAL 9005, MATTE (SHERWIN WILLIAMS EBS1-01715, TF BLACK)
5. QTY 4X #4-40 x 5/16" SELF-CLINCHING BLIND STANDOFFS; PEM BRAND BSO-440-10 IS PREFERRED; EQUIVALENTS
ARE ACCEPTABLE WITH VALIDATION; THREAD MASKING NOT REQUIRED PRIOR TO POWDER COAT

UNLESS OTHERWISE SPECIFIED: DIMENSIONS ARE IN MILLIMETERS ALL UNTOLERANCED DIMENSIONS ARE BASIC TOLERANCES: FRACTIONAL 0.75 ANGULAR 0.5 LINEAR .X 0.75 .XX 0.25 .XXX 0.125 Ra 12.5 FINISH INTERPRET GD&T PER ASME Y14.5M-1994 DO NOT SCALE DRAWING | MATERIAL: SEE NOTES | DESCRIPTION: W2 COVER

FINISH: SEE NOTES | PART NO: PART REV. 1735302 D

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

www.ideaz.tech
