ObeliskInc/obelisk-hardware/Generation 2 Mining Hardware/Mechanical – Slim/OB_1735303-E_W2-Chassis-Right.PDF

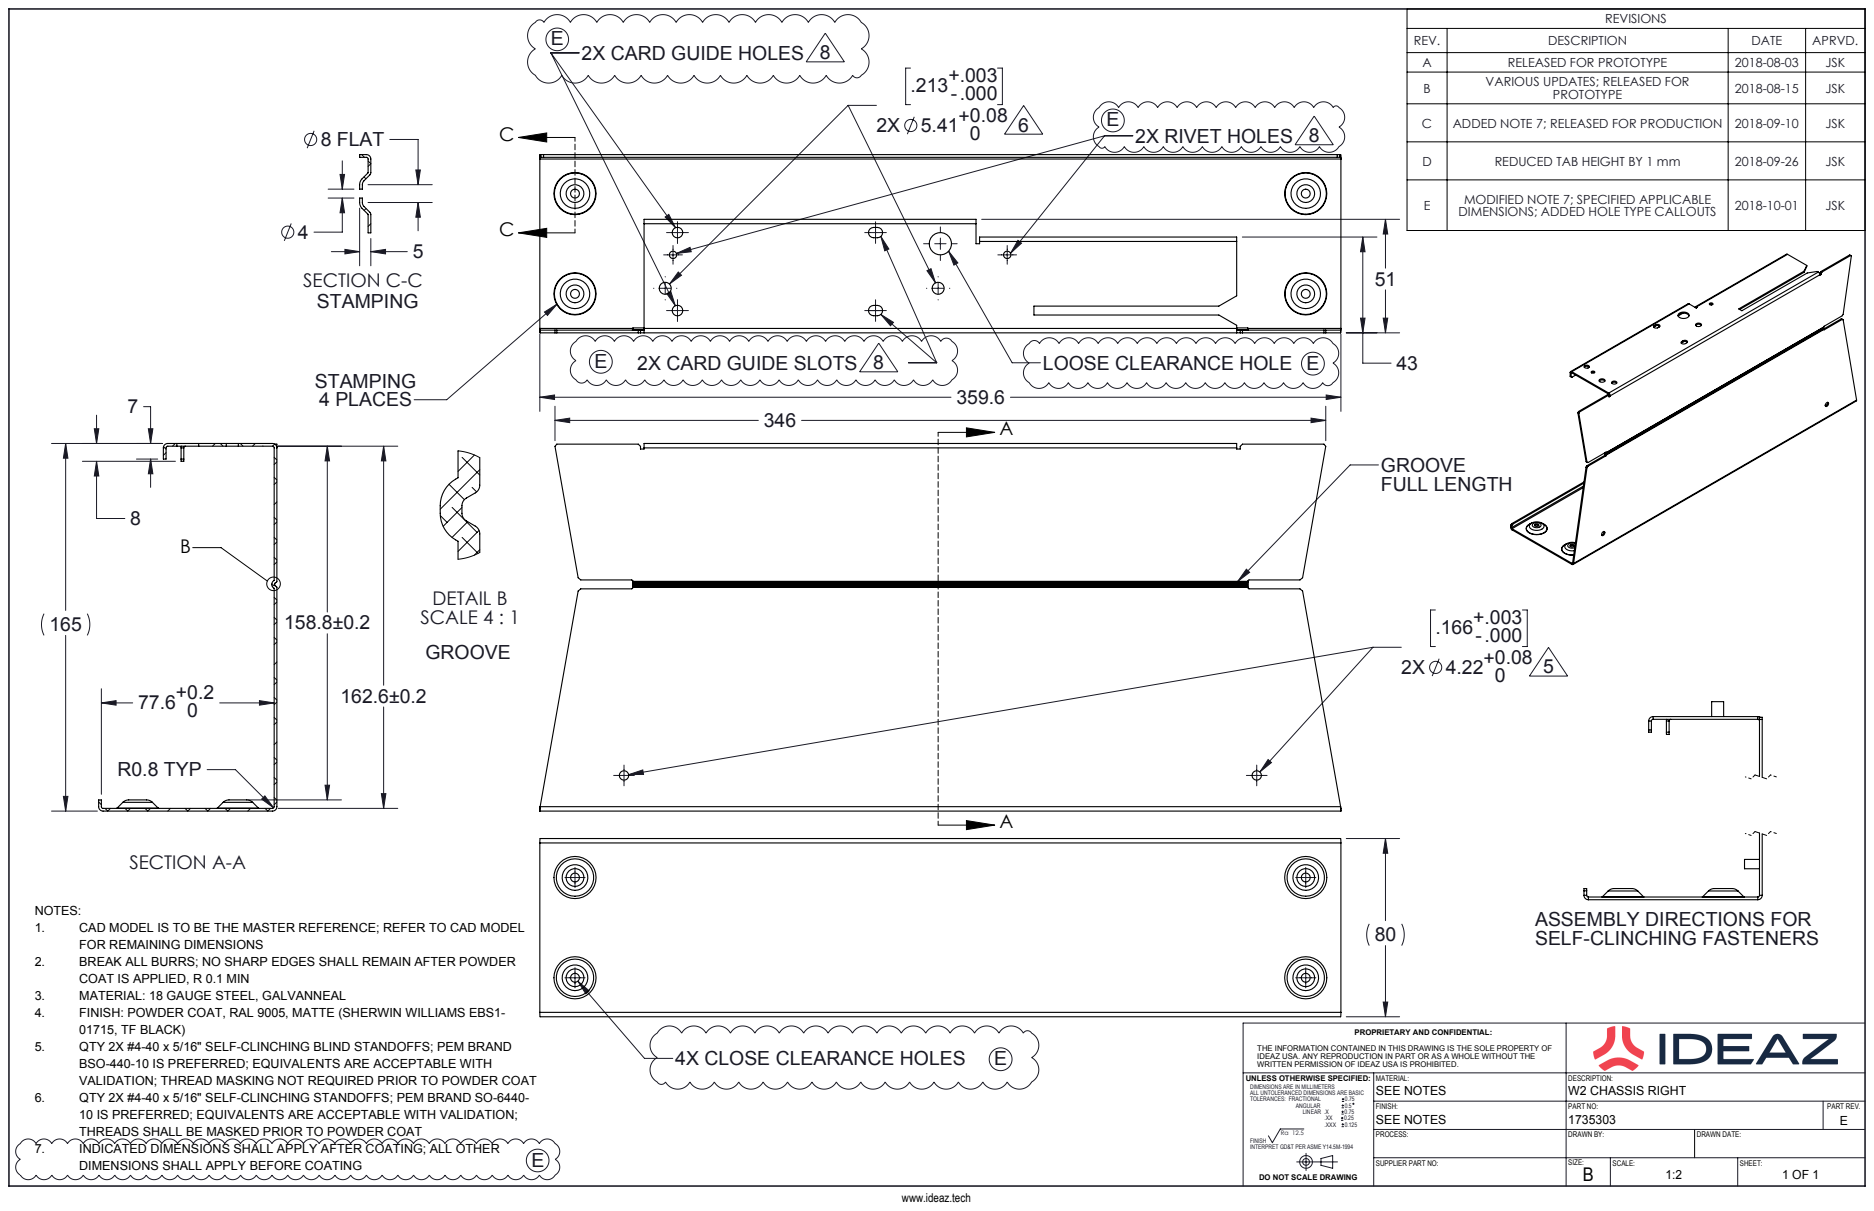
[picture p78: page 1]
FULL LENGTH; 4 PLACES; 2X RIVET HOLES 8; LOOSE CLEARANCE HOLE E; R0.8 TYP; SECTION A-A; DETAIL B SCALE 4 : 1; 8 FLAT; SECTION C-C; DIMENSIONS SHALL APPLY BEFORE COATING

REVISIONS

2X CARD GUIDE HOLES 8

REV. | DESCRIPTION | DATE | APRVD.
A | RELEASED FOR PROTOTYPE | 2018-08-03 | JSK
B | VARIOUS UPDATES; RELEASED FOR PROTOTYPE | 2018-08-15 | JSK

C | ADDED NOTE 7; RELEASED FOR PRODUCTION | 2018-09-10 | JSK

D | REDUCED TAB HEIGHT BY 1 mm | 2018-09-26 | JSK

E | MODIFIED NOTE 7; SPECIFIED APPLICABLE DIMENSIONS; ADDED HOLE TYPE CALLOUTS | 2018-10-01 | JSK

2X CARD GUIDE SLOTS 8

NOTES:
1. CAD MODEL IS TO BE THE MASTER REFERENCE; REFER TO CAD MODEL
FOR REMAINING DIMENSIONS
2. BREAK ALL BURRS; NO SHARP EDGES SHALL REMAIN AFTER POWDER
COAT IS APPLIED, R 0.1 MIN
3. MATERIAL: 18 GAUGE STEEL, GALVANNEAL
4. FINISH: POWDER COAT, RAL 9005, MATTE (SHERWIN WILLIAMS EBS1-
01715, TF BLACK)
5. QTY 2X #4-40 x 5/16" SELF-CLINCHING BLIND STANDOFFS; PEM BRAND
BSO-440-10 IS PREFERRED; EQUIVALENTS ARE ACCEPTABLE WITH
VALIDATION; THREAD MASKING NOT REQUIRED PRIOR TO POWDER COAT
6. QTY 2X #4-40 x 5/16" SELF-CLINCHING STANDOFFS; PEM BRAND SO-6440-
10 IS PREFERRED; EQUIVALENTS ARE ACCEPTABLE WITH VALIDATION;
THREADS SHALL BE MASKED PRIOR TO POWDER COAT
7. INDICATED DIMENSIONS SHALL APPLY AFTER COATING; ALL OTHER

ASSEMBLY DIRECTIONS FOR
SELF-CLINCHING FASTENERS

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

4X CLOSE CLEARANCE HOLES E

UNLESS OTHERWISE SPECIFIED: DIMENSIONS ARE IN MILLIMETERS ALL UNTOLERANCED DIMENSIONS ARE BASIC TOLERANCES: FRACTIONAL 0.75 ANGULAR 0.5 LINEAR .X 0.75 .XX 0.25 .XXX 0.125 Ra 12.5 FINISH INTERPRET GD&T PER ASME Y14.5M-1994 DO NOT SCALE DRAWING | MATERIAL: SEE NOTES | DESCRIPTION: W2 CHASSIS RIGHT

FINISH: SEE NOTES | PART NO: PART REV. 1735303 E

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

www.ideaz.tech
