ObeliskInc/obelisk-hardware/Generation 2 Mining Hardware/Mechanical – Slim/OB_1735304-E_W2-Chassis-Left.PDF

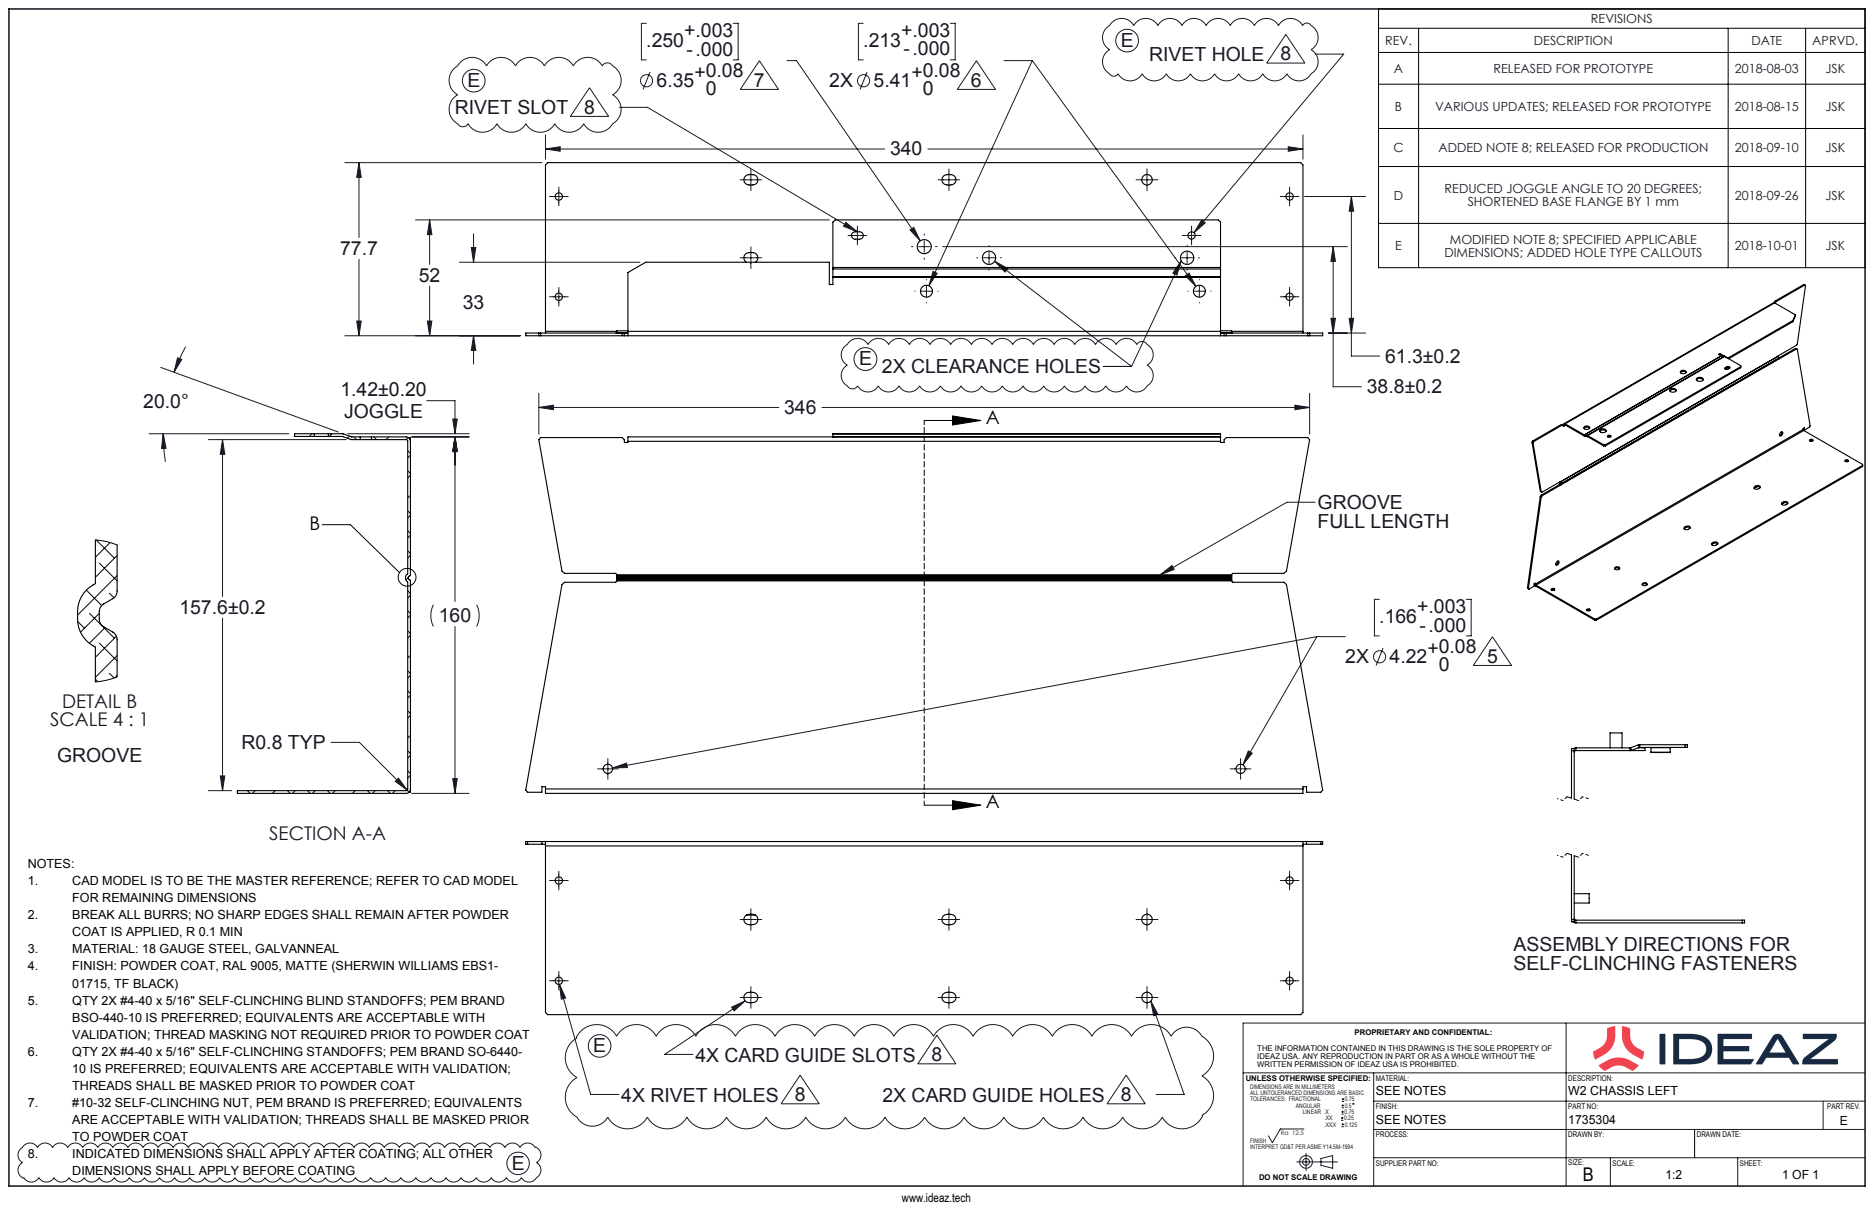
[picture p79: page 1]
FULL LENGTH; R0.8 TYP; SECTION A-A; DETAIL B SCALE 4 : 1; RIVET SLOT 8; RIVET HOLE 8; 2X CLEARANCE HOLES; 4X RIVET HOLES 8; DIMENSIONS SHALL APPLY BEFORE COATING

REVISIONS

REV. | DESCRIPTION | DATE | APRVD.
A | RELEASED FOR PROTOTYPE | 2018-08-03 | JSK

B | VARIOUS UPDATES; RELEASED FOR PROTOTYPE | 2018-08-15 | JSK

C | ADDED NOTE 8; RELEASED FOR PRODUCTION | 2018-09-10 | JSK

D | REDUCED JOGGLE ANGLE TO 20 DEGREES; SHORTENED BASE FLANGE BY 1 mm | 2018-09-26 | JSK

E | MODIFIED NOTE 8; SPECIFIED APPLICABLE DIMENSIONS; ADDED HOLE TYPE CALLOUTS | 2018-10-01 | JSK

NOTES:
1. CAD MODEL IS TO BE THE MASTER REFERENCE; REFER TO CAD MODEL
FOR REMAINING DIMENSIONS
2. BREAK ALL BURRS; NO SHARP EDGES SHALL REMAIN AFTER POWDER
COAT IS APPLIED, R 0.1 MIN
3. MATERIAL: 18 GAUGE STEEL, GALVANNEAL
4. FINISH: POWDER COAT, RAL 9005, MATTE (SHERWIN WILLIAMS EBS1-
01715, TF BLACK)
5. QTY 2X #4-40 x 5/16" SELF-CLINCHING BLIND STANDOFFS; PEM BRAND
BSO-440-10 IS PREFERRED; EQUIVALENTS ARE ACCEPTABLE WITH
VALIDATION; THREAD MASKING NOT REQUIRED PRIOR TO POWDER COAT
6. QTY 2X #4-40 x 5/16" SELF-CLINCHING STANDOFFS; PEM BRAND SO-6440-
10 IS PREFERRED; EQUIVALENTS ARE ACCEPTABLE WITH VALIDATION;
THREADS SHALL BE MASKED PRIOR TO POWDER COAT
7. #10-32 SELF-CLINCHING NUT, PEM BRAND IS PREFERRED; EQUIVALENTS
ARE ACCEPTABLE WITH VALIDATION; THREADS SHALL BE MASKED PRIOR
TO POWDER COAT
8. INDICATED DIMENSIONS SHALL APPLY AFTER COATING; ALL OTHER

ASSEMBLY DIRECTIONS FOR
SELF-CLINCHING FASTENERS

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

4X CARD GUIDE SLOTS 8

UNLESS OTHERWISE SPECIFIED: DIMENSIONS ARE IN MILLIMETERS ALL UNTOLERANCED DIMENSIONS ARE BASIC TOLERANCES: FRACTIONAL 0.75 ANGULAR 0.5 LINEAR .X 0.75 .XX 0.25 .XXX 0.125 Ra 12.5 FINISH INTERPRET GD&T PER ASME Y14.5M-1994 DO NOT SCALE DRAWING | MATERIAL: SEE NOTES | DESCRIPTION: W2 CHASSIS LEFT

2X CARD GUIDE HOLES 8

FINISH: SEE NOTES | PART NO: PART REV. 1735304 E

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

www.ideaz.tech
