ObeliskInc/obelisk-hardware/Generation 2 Mining Hardware/Mechanical – Slim/OB_1735305-A_PCB-Foam-Strip.PDF

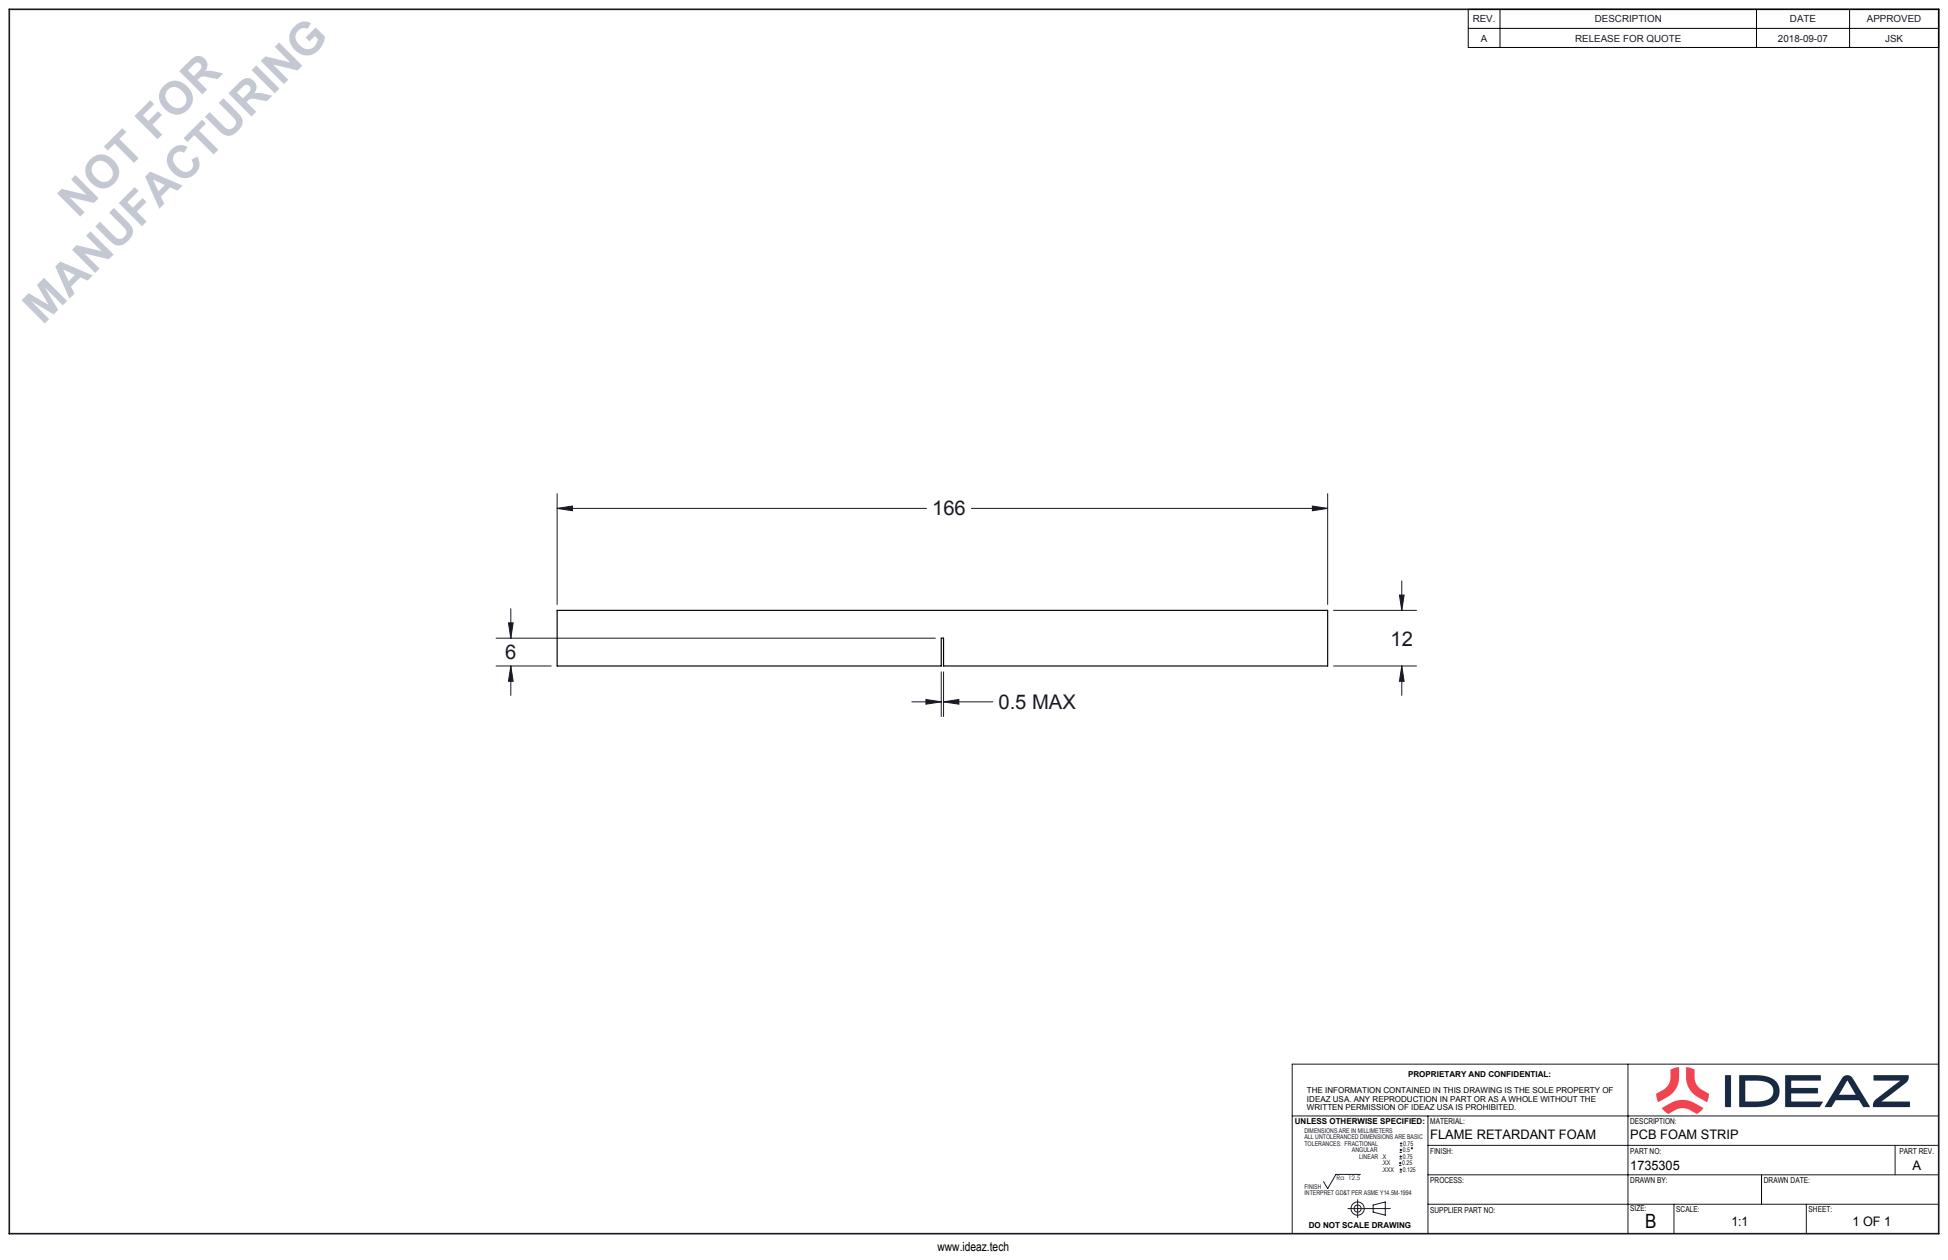
[picture p80: page 1]
0.5 MAX; NOT FOR

REV. | DESCRIPTION | DATE | APPROVED
A | RELEASE FOR QUOTE | 2018-09-07 | JSK

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

UNLESS OTHERWISE SPECIFIED: DIMENSIONS ARE IN MILLIMETERS ALL UNTOLERANCED DIMENSIONS ARE BASIC TOLERANCES: FRACTIONAL 0.75 ANGULAR 0.5 LINEAR .X 0.75 .XX 0.25 .XXX 0.125 Ra 12.5 FINISH INTERPRET GD&T PER ASME Y14.5M-1994 DO NOT SCALE DRAWING | MATERIAL: FLAME RETARDANT FOAM | DESCRIPTION: PCB FOAM STRIP

FINISH: | PART NO: PART REV. 1735305 A

PROCESS: | DRAWN BY: | DRAWN DATE:
SUPPLIER PART NO: | SIZE: B | SCALE: 1:1 | SHEET: 1 OF 1

www.ideaz.tech
