ObeliskInc/obelisk-hardware/Generation 1 Mining Hardware/Electrical/Control Board/SOMController742904RAsch.pdf

07 JUN 2018 | 0 | INITIAL- OBELISK HASHING CONTROLLER 742904 (FROM PROTOTYPE 742902)
14 JUN 2018 | A | PRODUCTION RELEASE- OBELISK SOM HASHING CONTROLLER 742904 REV A

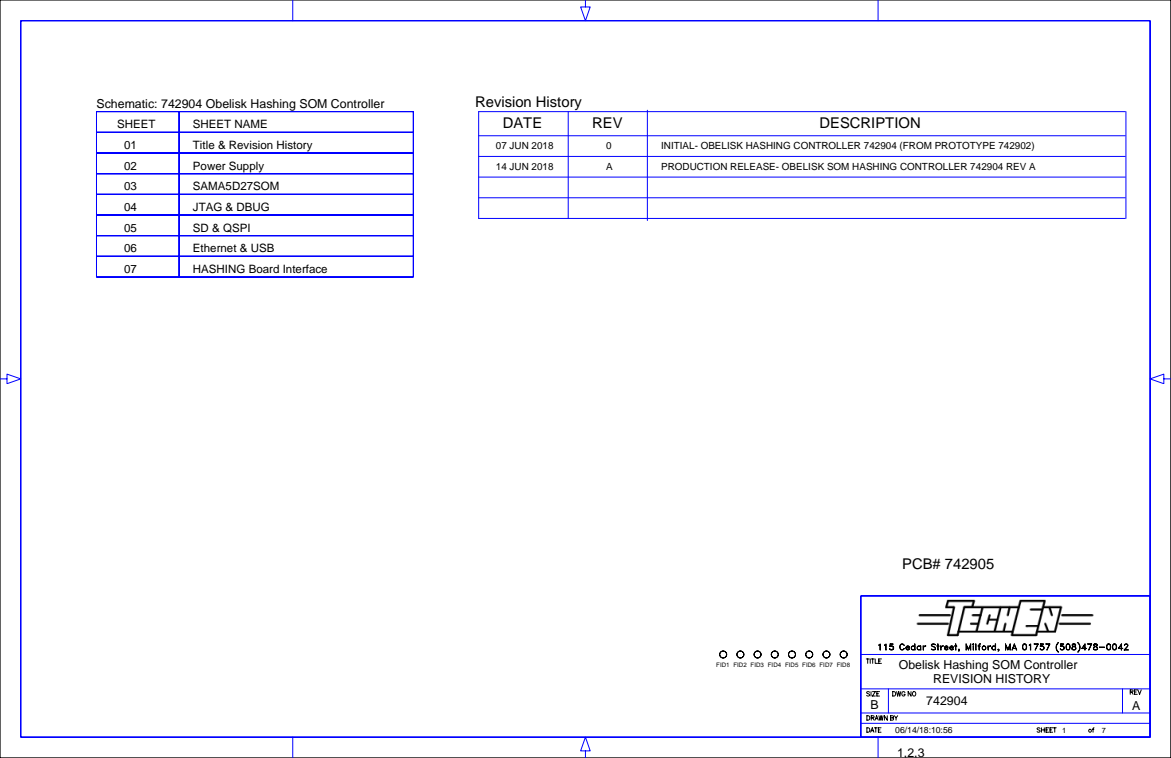
[picture p81: page 1]
Revision History; REV; DESCRIPTION; DATE; SHEET; SHEET NAME; FID1 FID2 FID3 FID4 FID5 FID6 FID7 FID8; PCB# 742905

Schematic: 742904 Obelisk Hashing SOM Controller

01 | Title & Revision History
02 | Power Supply
03 | SAMA5D27SOM
04 | JTAG & DBUG
05 | SD & QSPI
06 | Ethernet & USB
07 | HASHING Board Interface

Obelisk Hashing SOM Controller
REVISION HISTORY

# POWER SUPPLY

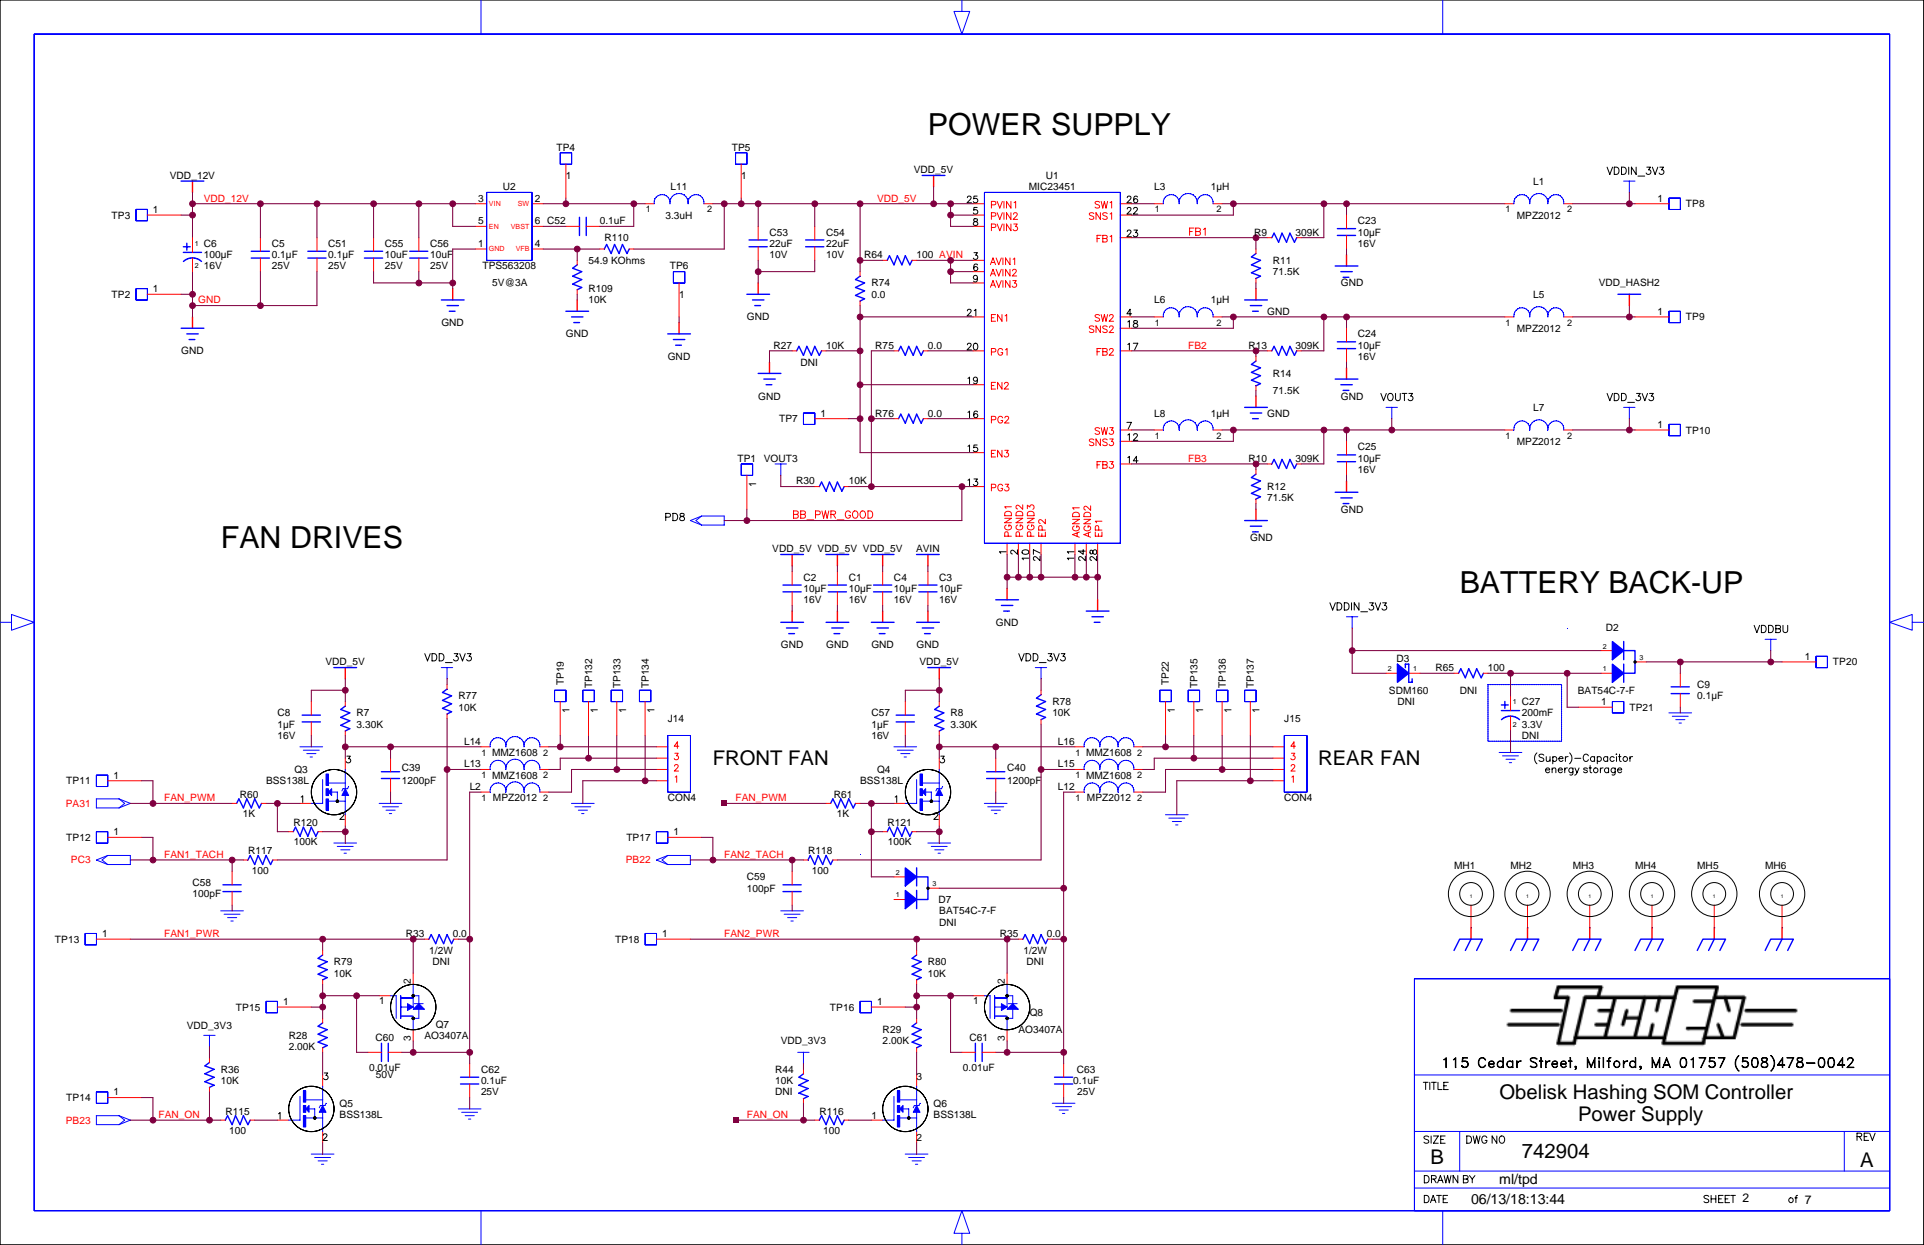
[picture p82: page 2]

Obelisk Hashing SOM Controller

# SOM CONTROLLER

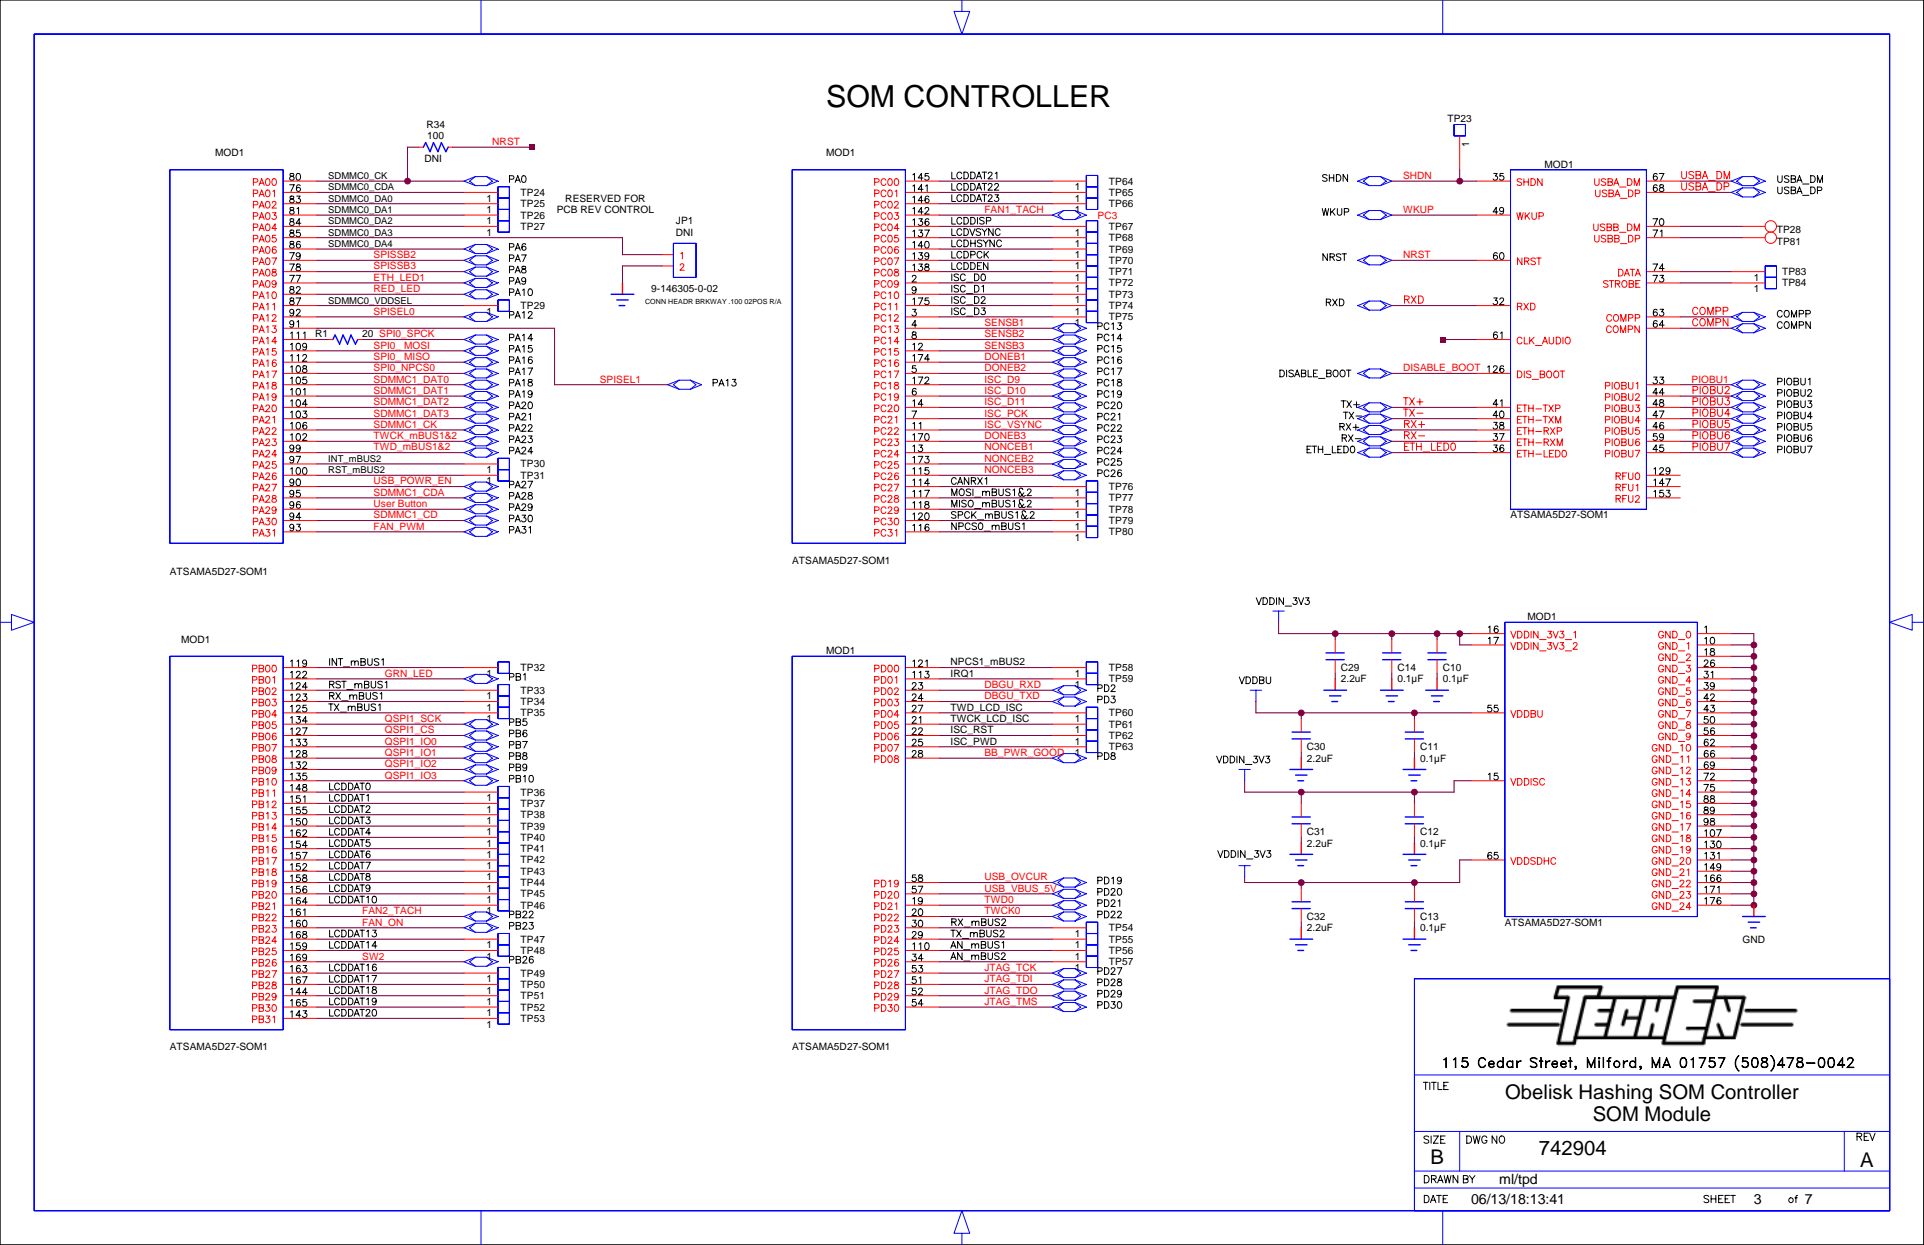
[picture p83: page 3]

Obelisk Hashing SOM Controller

JTAG | DEBUG PORT

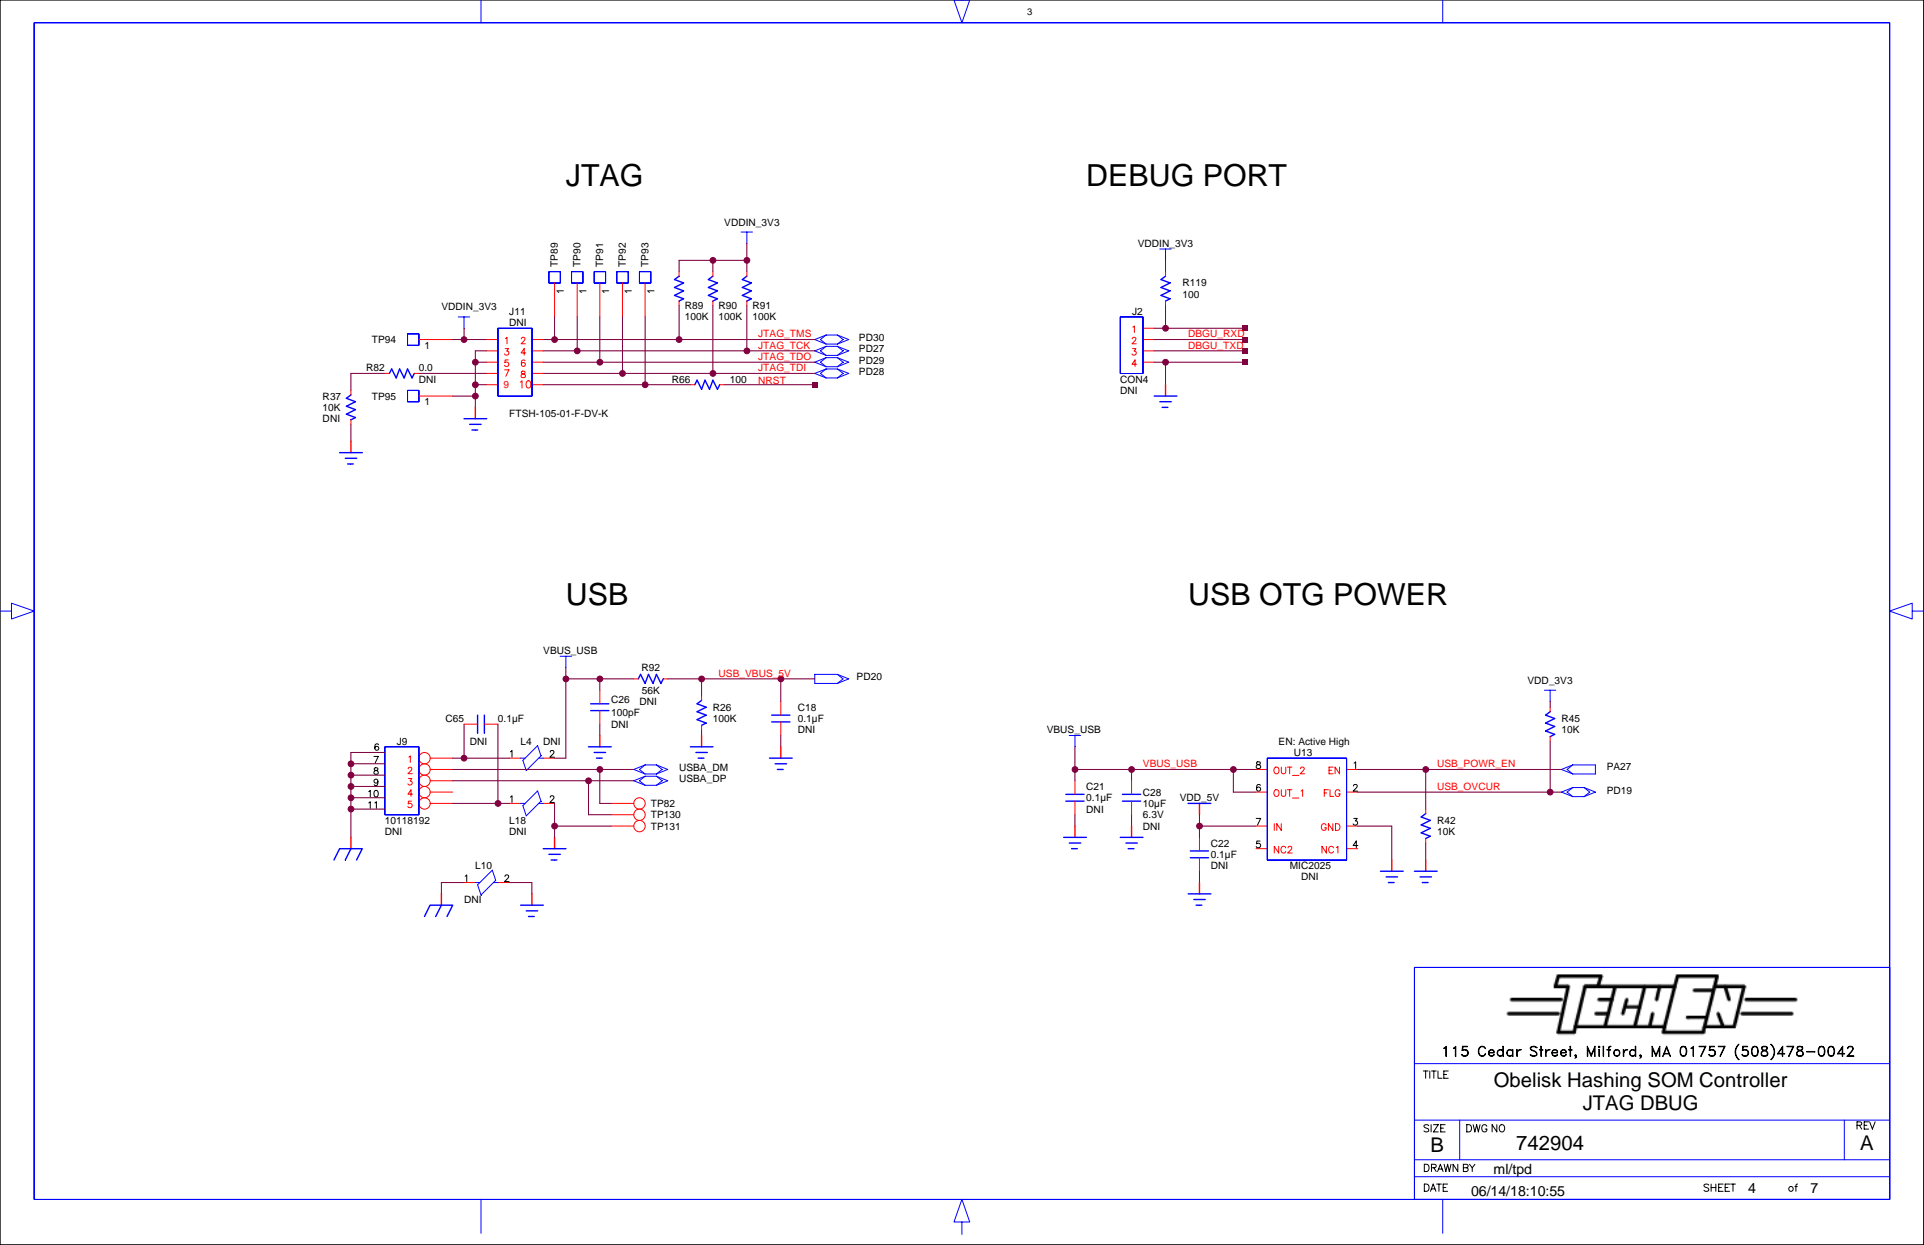
[picture p84: page 4]

Obelisk Hashing SOM Controller

# QSPI Flash

# SDMMC1 µSD Card interface

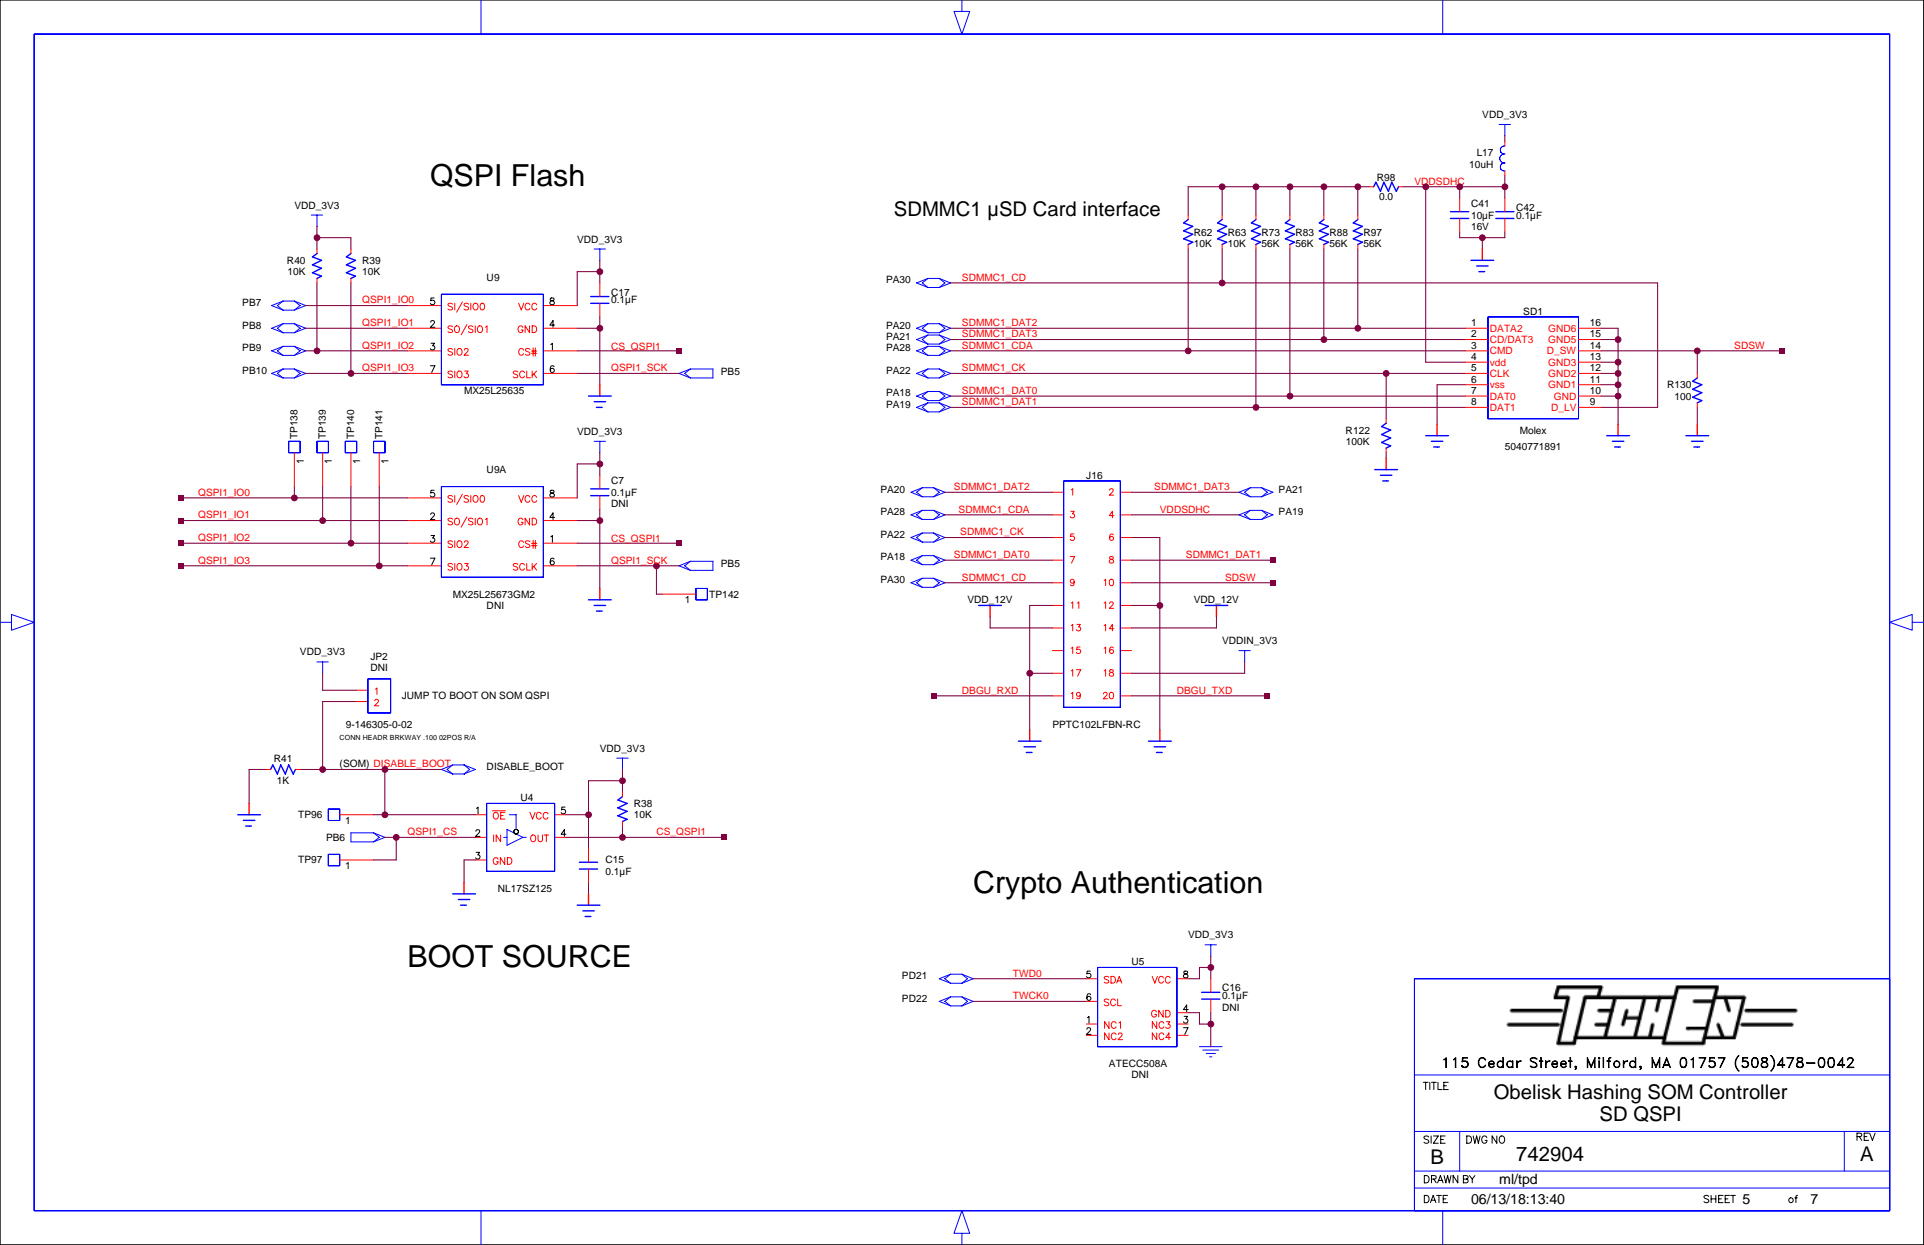
[picture p85: page 5]

JUMP TO BOOT ON SOM QSPI

Obelisk Hashing SOM Controller

## User Button

## NRST

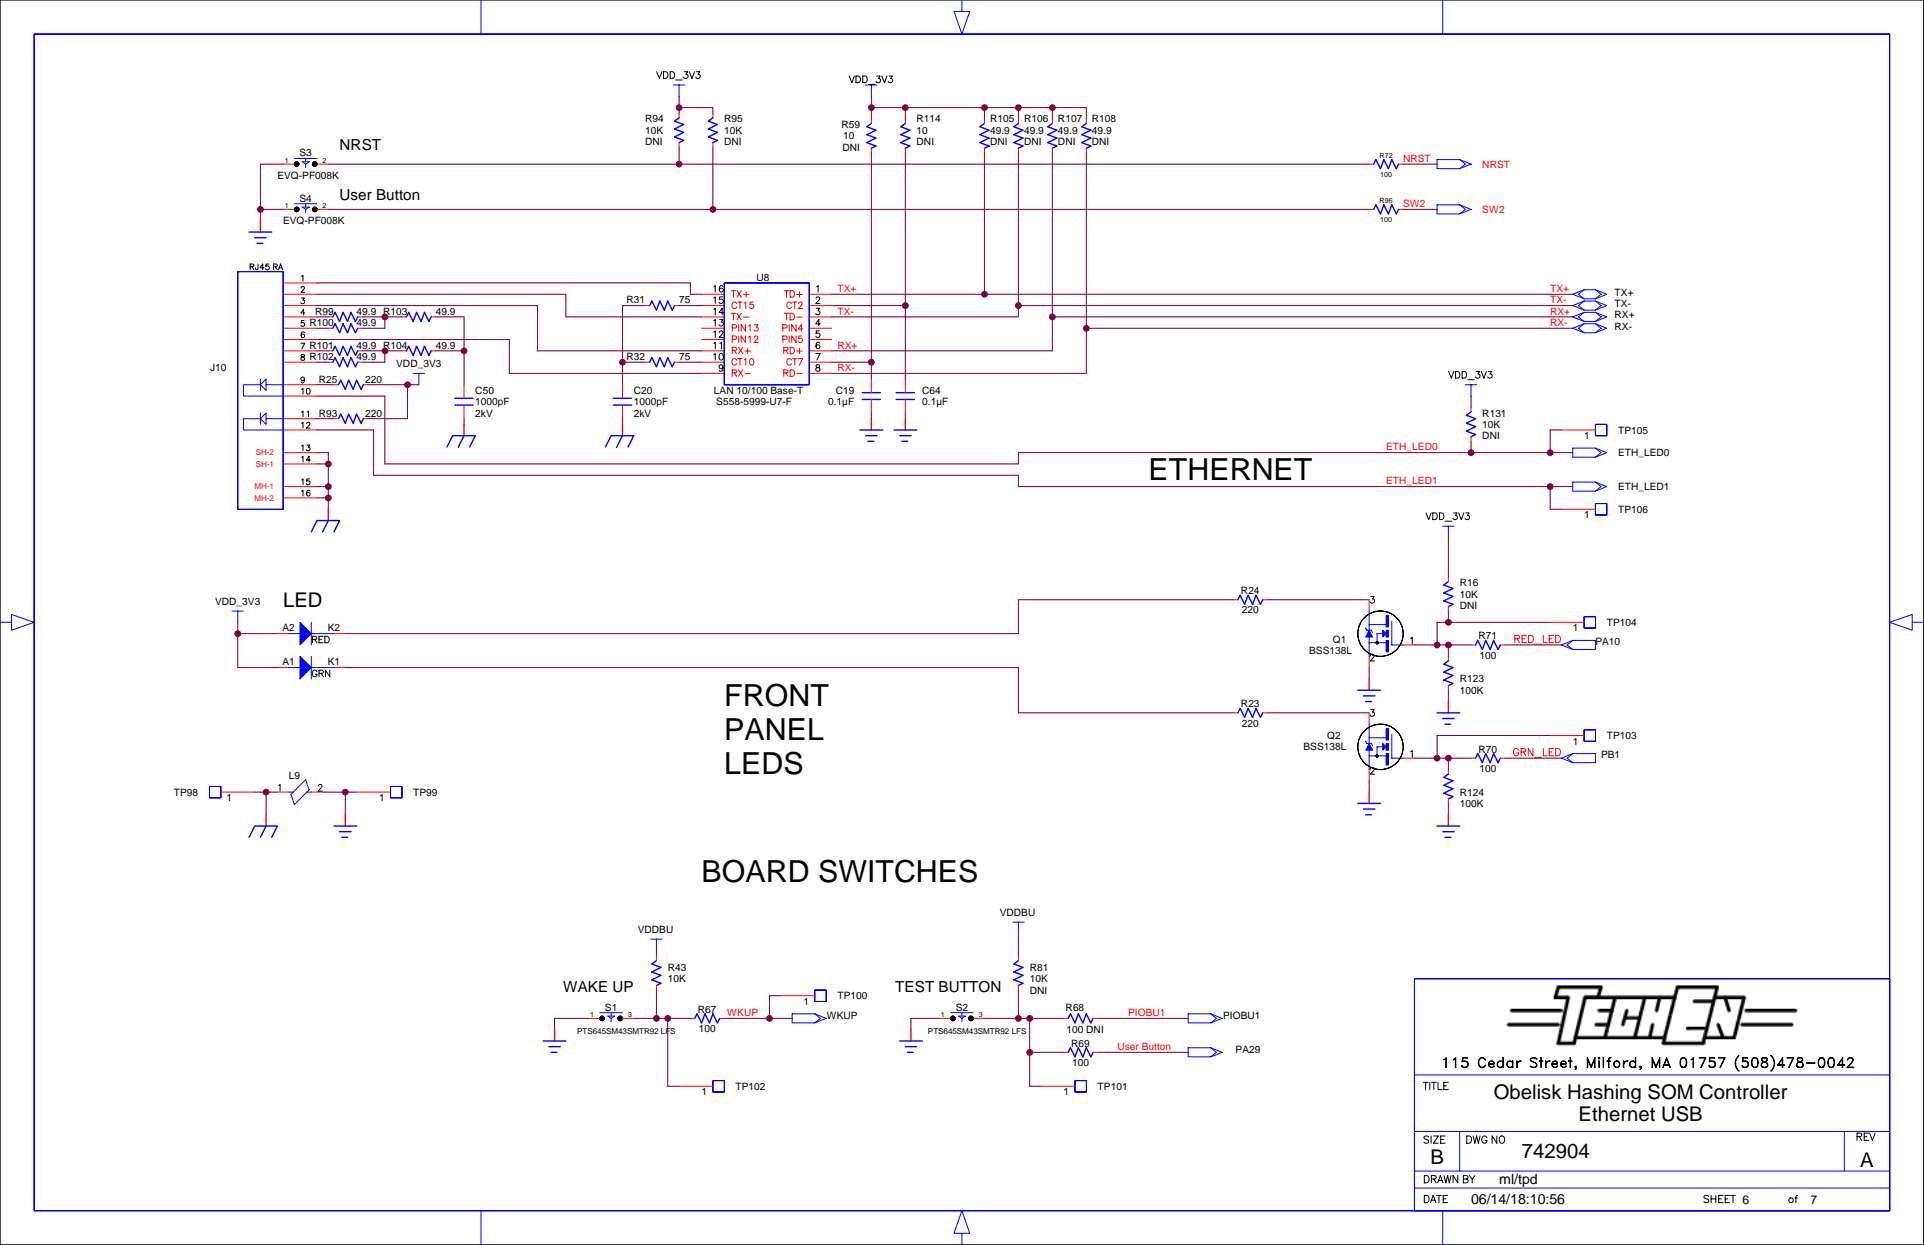
[picture p86: page 6]

10 DNI | 49.9 DNI | 49.9 DNI | 49.9 DNI | DNI

Obelisk Hashing SOM Controller

# SLOT 1

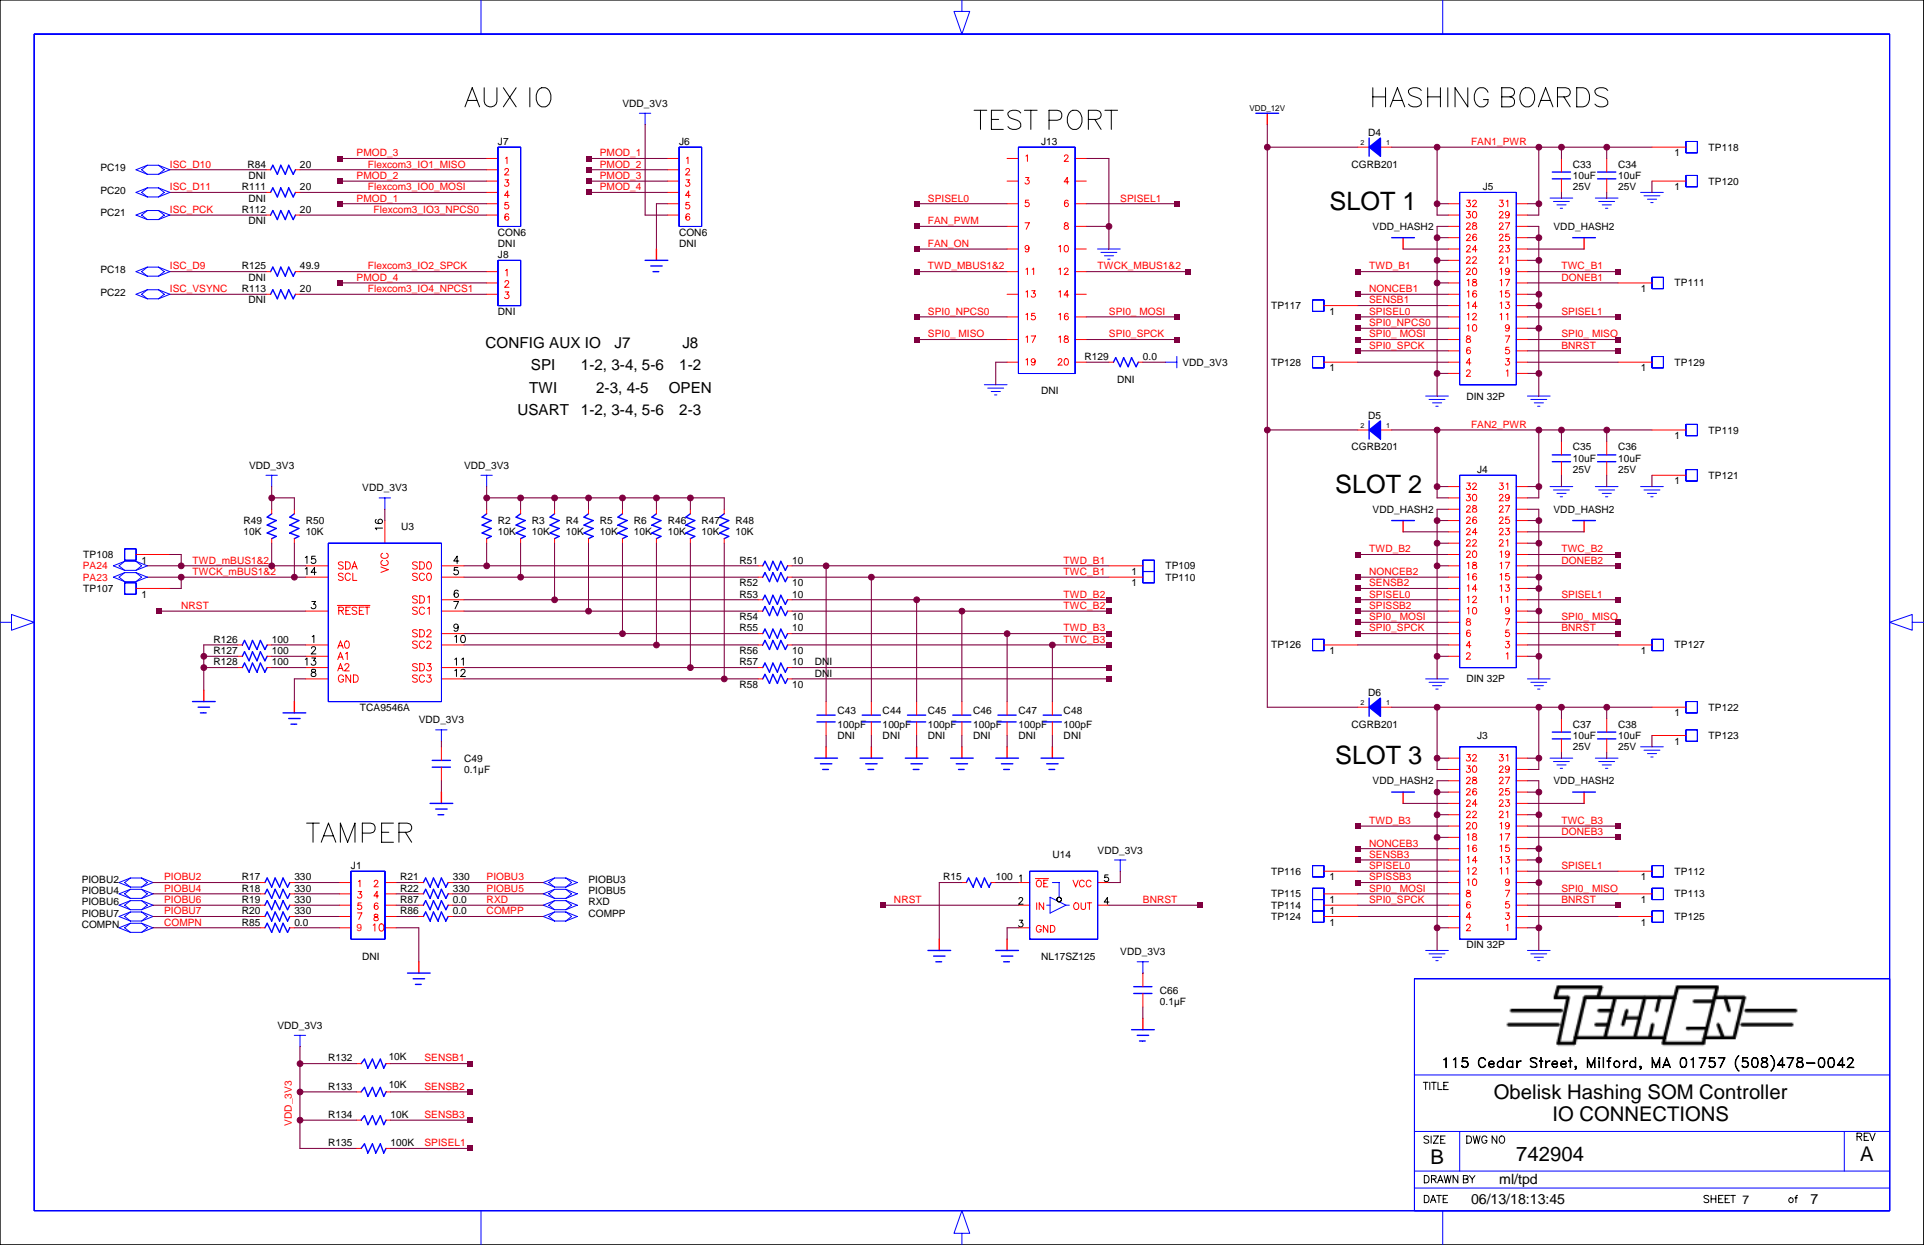
[picture p87: page 7]

VDD_12V

1 SPI0_SPCK

Obelisk Hashing SOM Controller
IO CONNECTIONS
