ObeliskInc/obelisk-hardware/Generation 1 Mining Hardware/Electrical/Hashing Board/SIAHashBd742901R2sch_06-19-18b.pdf

# 25 AMP ASIC POWER SUPPLY

# INPUT

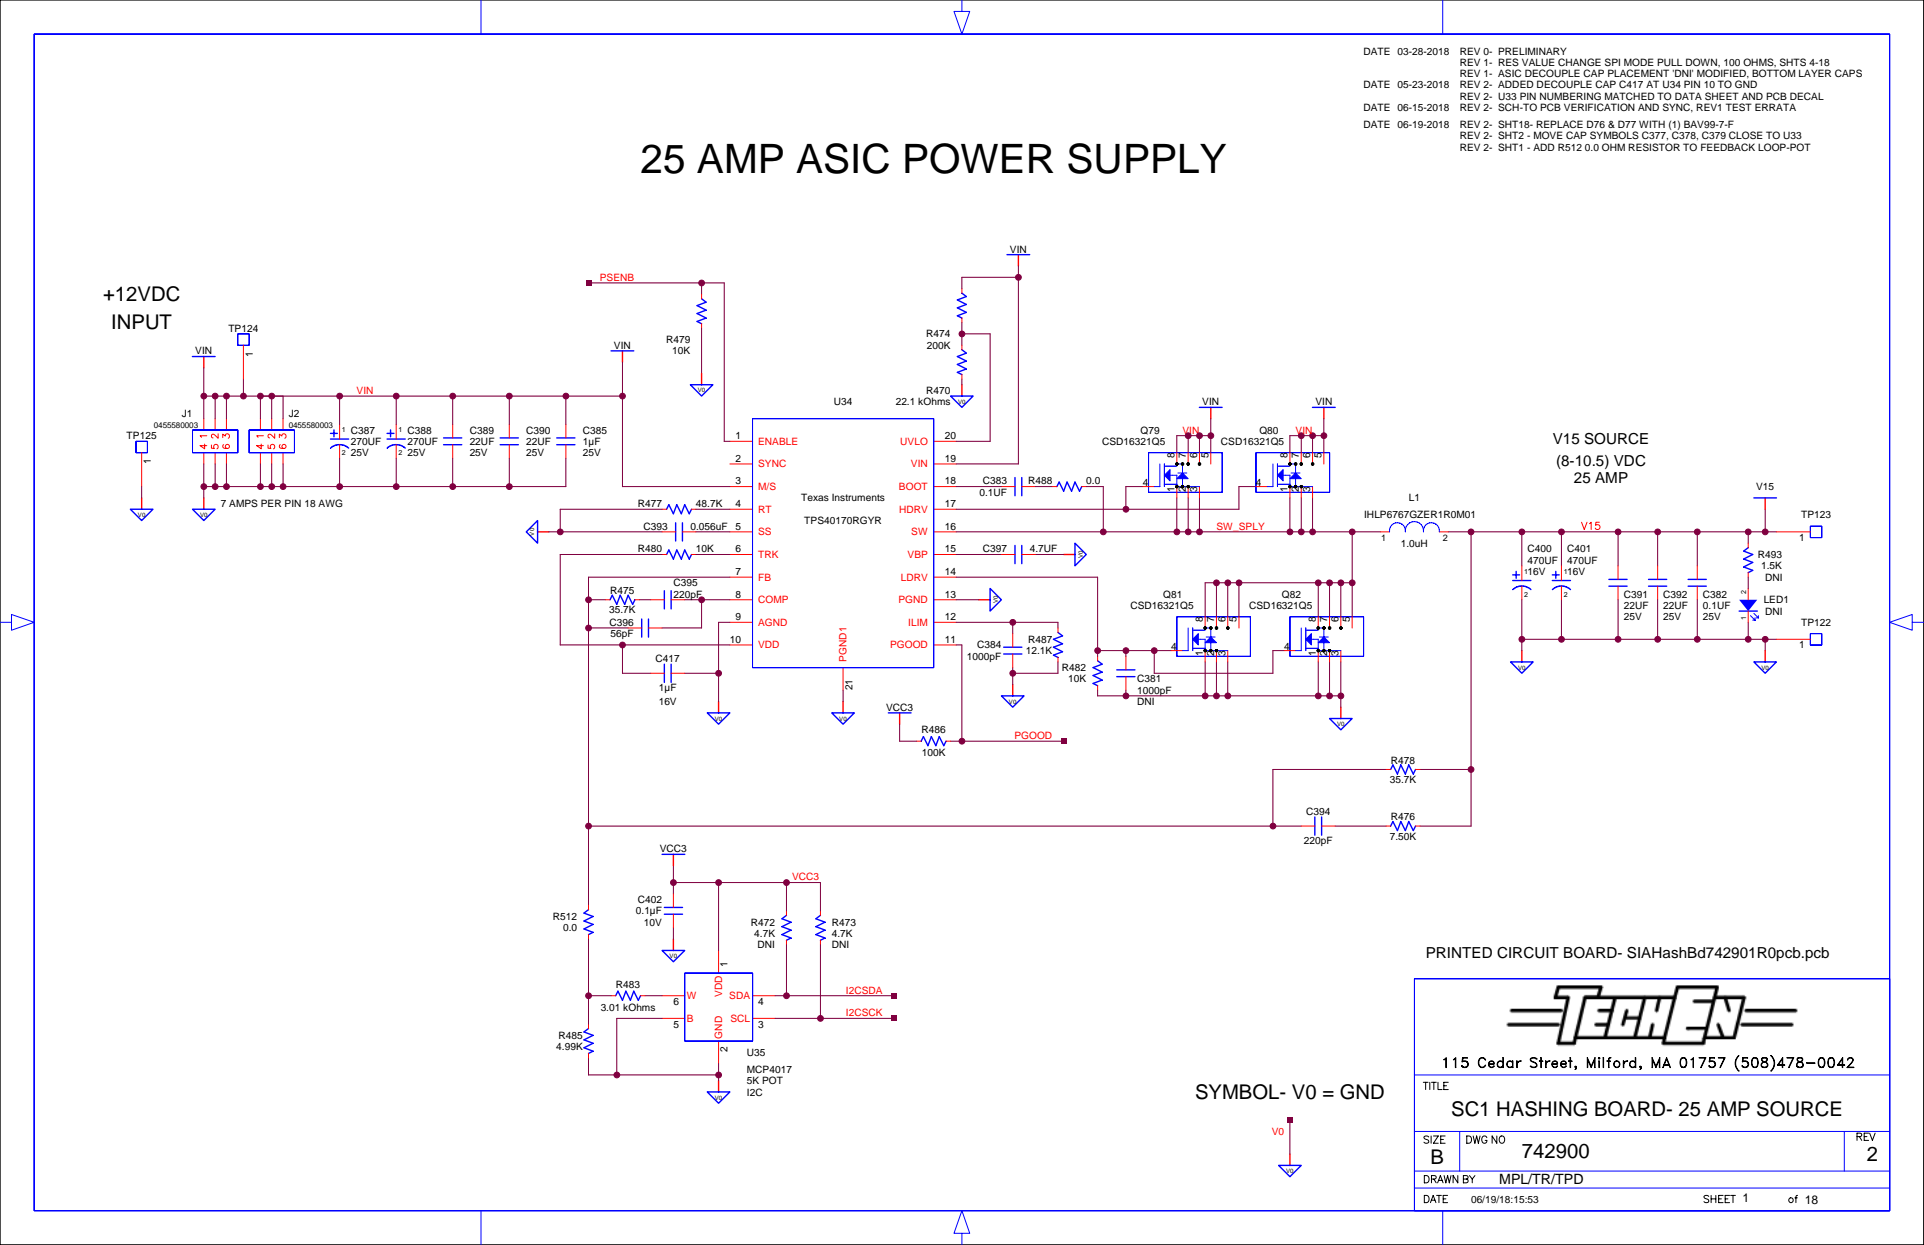
[picture p88: page 1]

REV 0- PRELIMINARY
REV 1- RES VALUE CHANGE SPI MODE PULL DOWN, 100 OHMS, SHTS 4-18
REV 1- ASIC DECOUPLE CAP PLACEMENT 'DNI' MODIFIED, BOTTOM LAYER CAPS
REV 2- ADDED DECOUPLE CAP C417 AT U34 PIN 10 TO GND
REV 2- U33 PIN NUMBERING MATCHED TO DATA SHEET AND PCB DECAL
REV 2- SCH-TO PCB VERIFICATION AND SYNC, REV1 TEST ERRATA

DATE 06-15-2018
DATE 06-19-2018 REV 2- SHT18- REPLACE D76 & D77 WITH (1) BAV99-7-F

REV 2- SHT2 - MOVE CAP SYMBOLS C377, C378, C379 CLOSE TO U33
REV 2- SHT1 - ADD R512 0.0 OHM RESISTOR TO FEEDBACK LOOP-POT

7 AMPS PER PIN 18 AWG

PRINTED CIRCUIT BOARD- SIAHashBd742901R0pcb.pcb

SC1 HASHING BOARD- 25 AMP SOURCE

# BUFFERING AND LEVEL TRANSLATION

### VCC3 FROM CONTROLLER

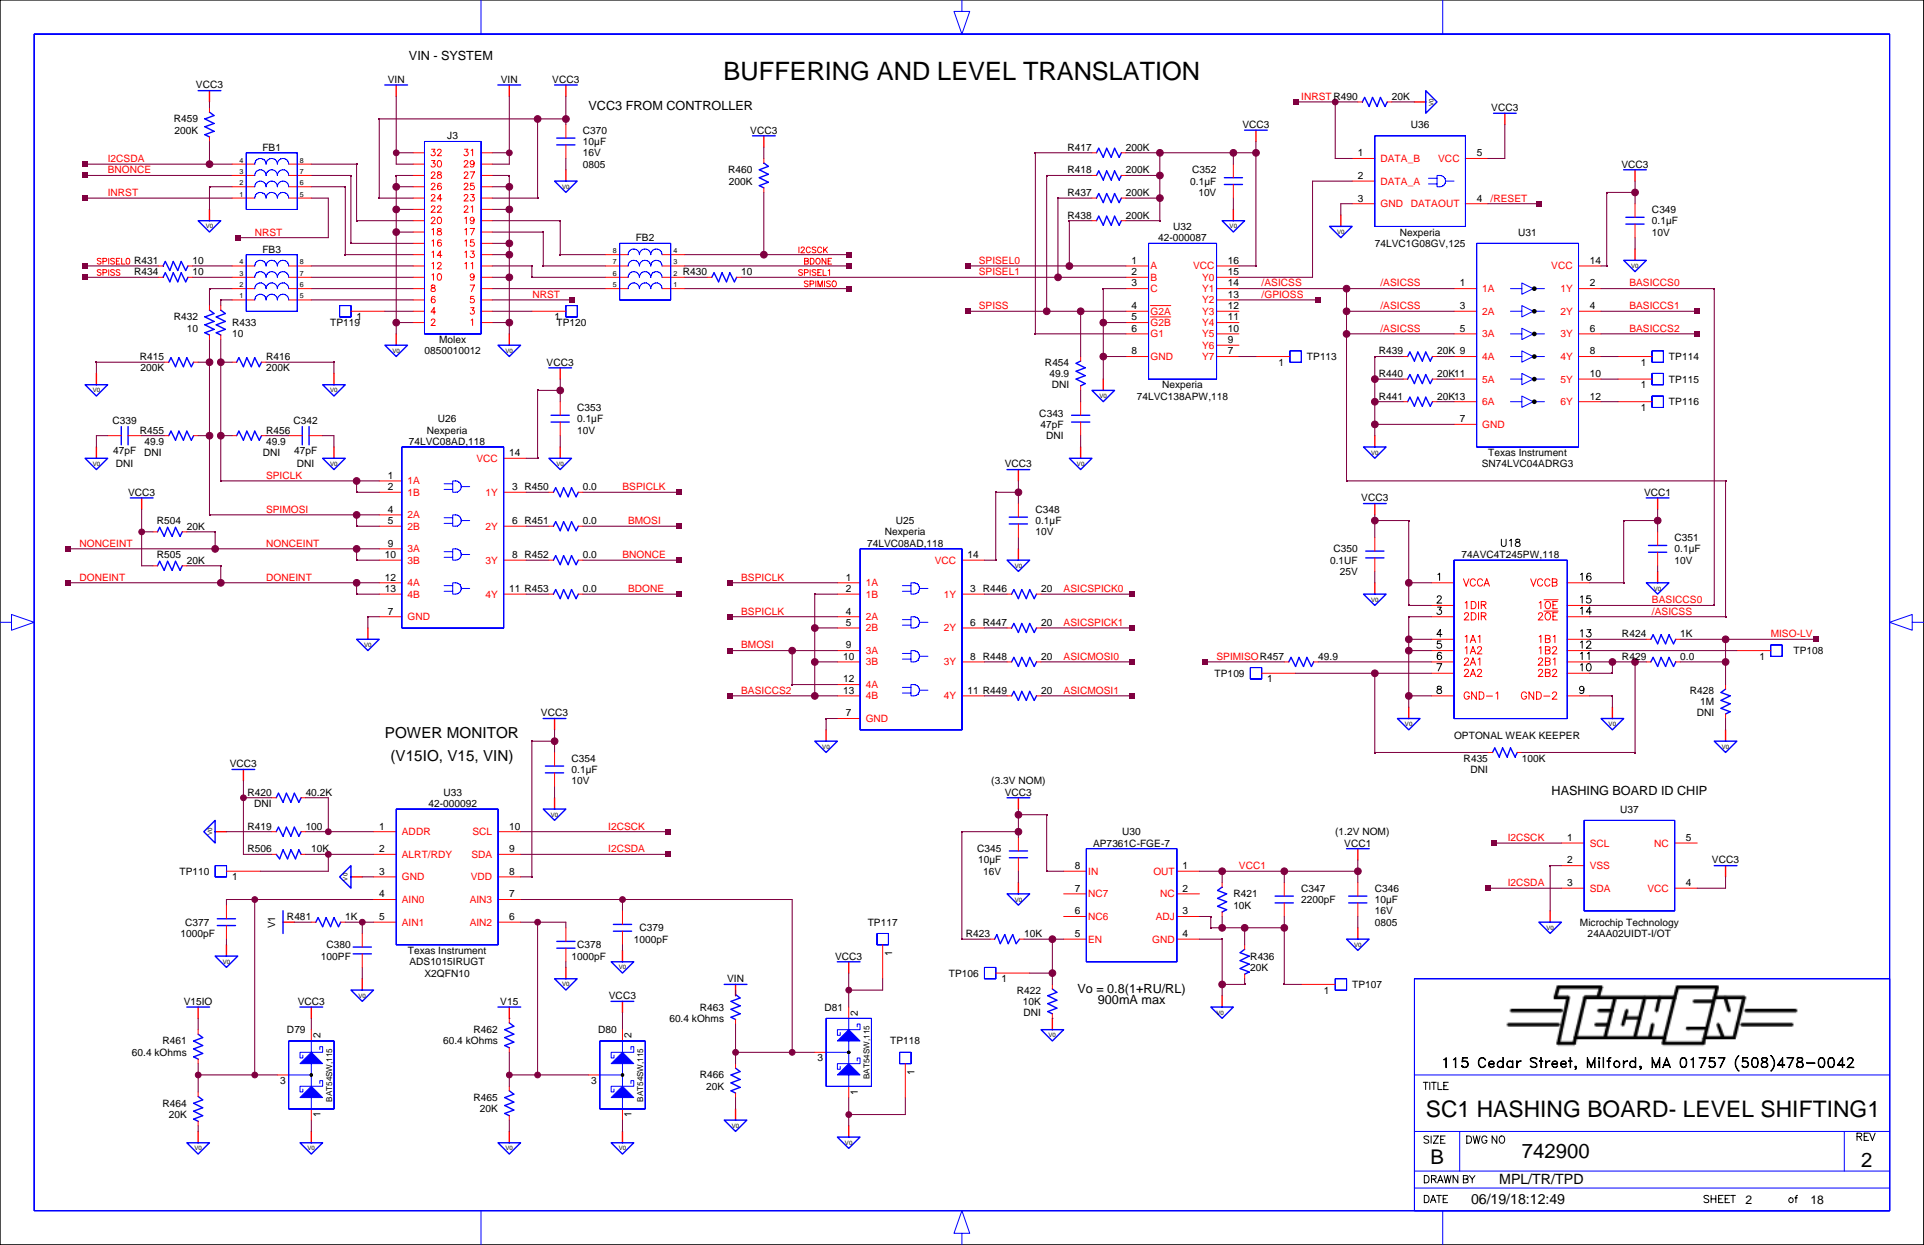
[picture p89: page 2]

HASHING BOARD ID CHIP

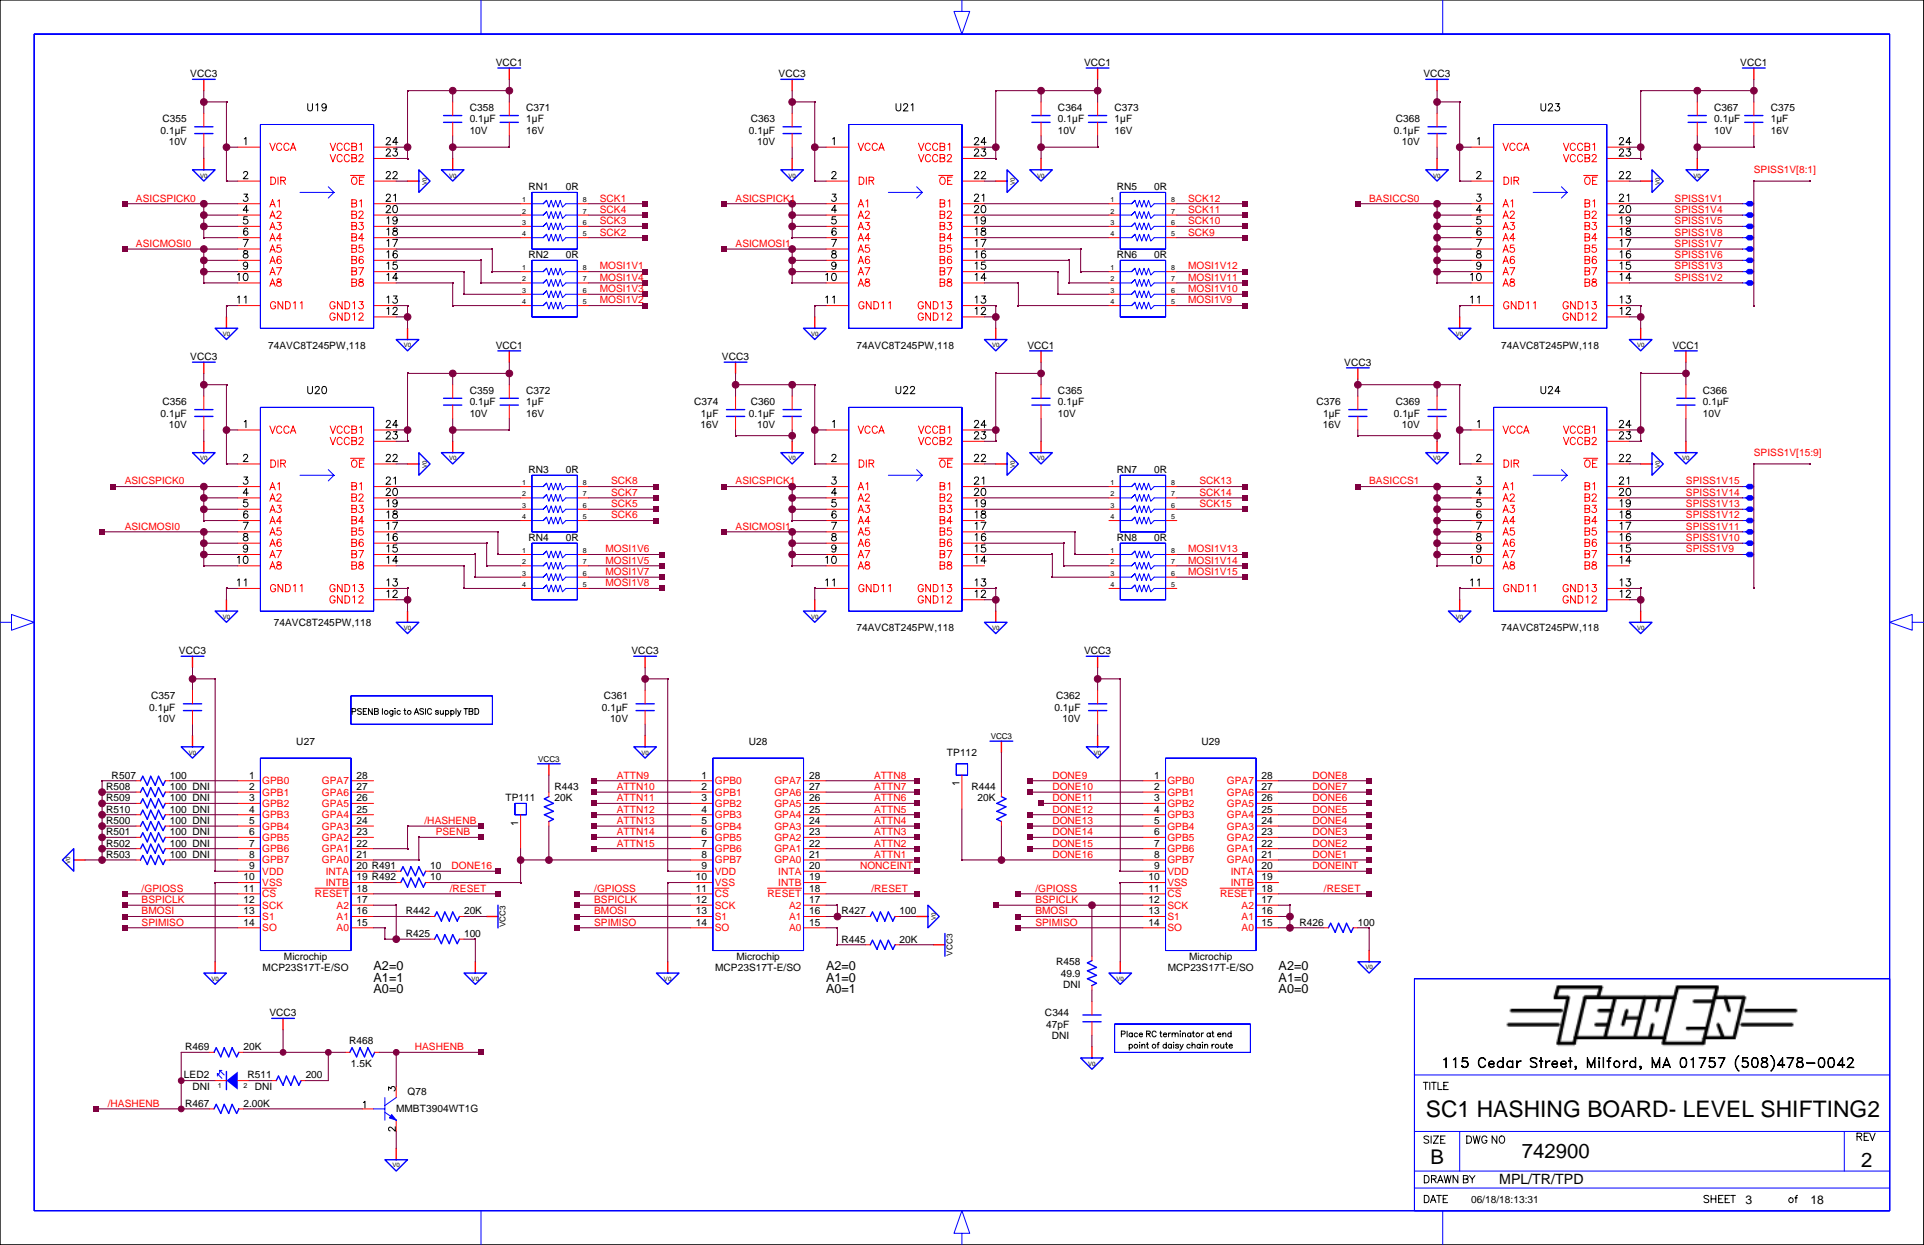
[picture p90: page 3]

# ASIC 1

U1

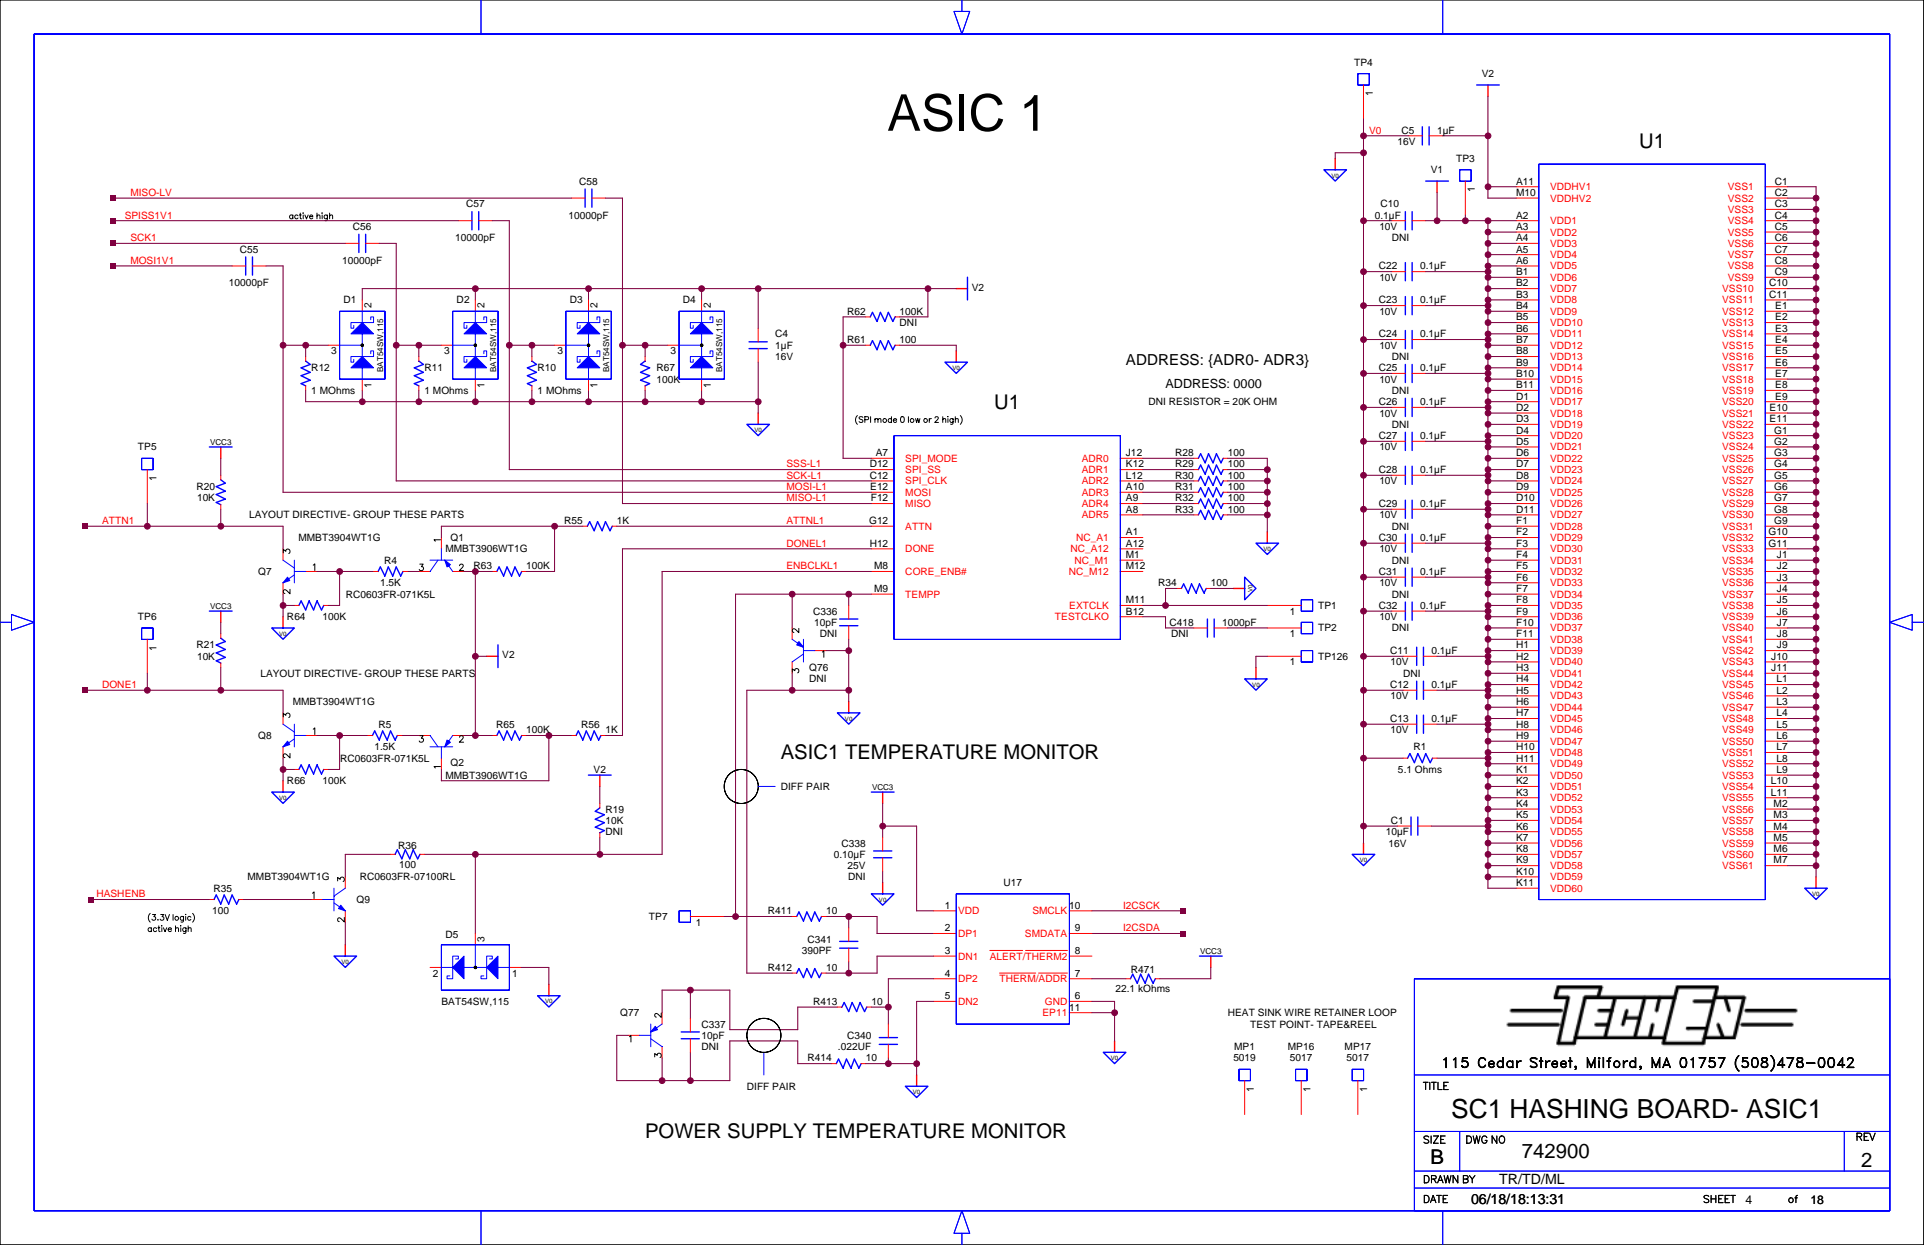
[picture p91: page 4]

A3 | C5
A4 | C6
A5 | C7
A6 | C8

B5 | E2
B6 | E3

B8 | E5
B9 | E6

B11 | E8
D1 | E9

D3 | E11
D4 | G1

D6 | G3
D7 | G4

LAYOUT DIRECTIVE- GROUP THESE PARTS

F7 | J4
F8 | J5

F10 | J7
F11 | J8
H1 | J9

H3 | J11
H4 | L1

H6 | L3
H7 | L4

H9 | L6
H10 | L7

K1 | L9
K2 | L10
K3 | L11
K4 | M2
K5 | M3

K7 | M5
K8 | M6
K9 | M7

HEAT SINK WIRE RETAINER LOOP
TEST POINT- TAPE&REEL

POWER SUPPLY TEMPERATURE MONITOR

# ASIC 2

U2

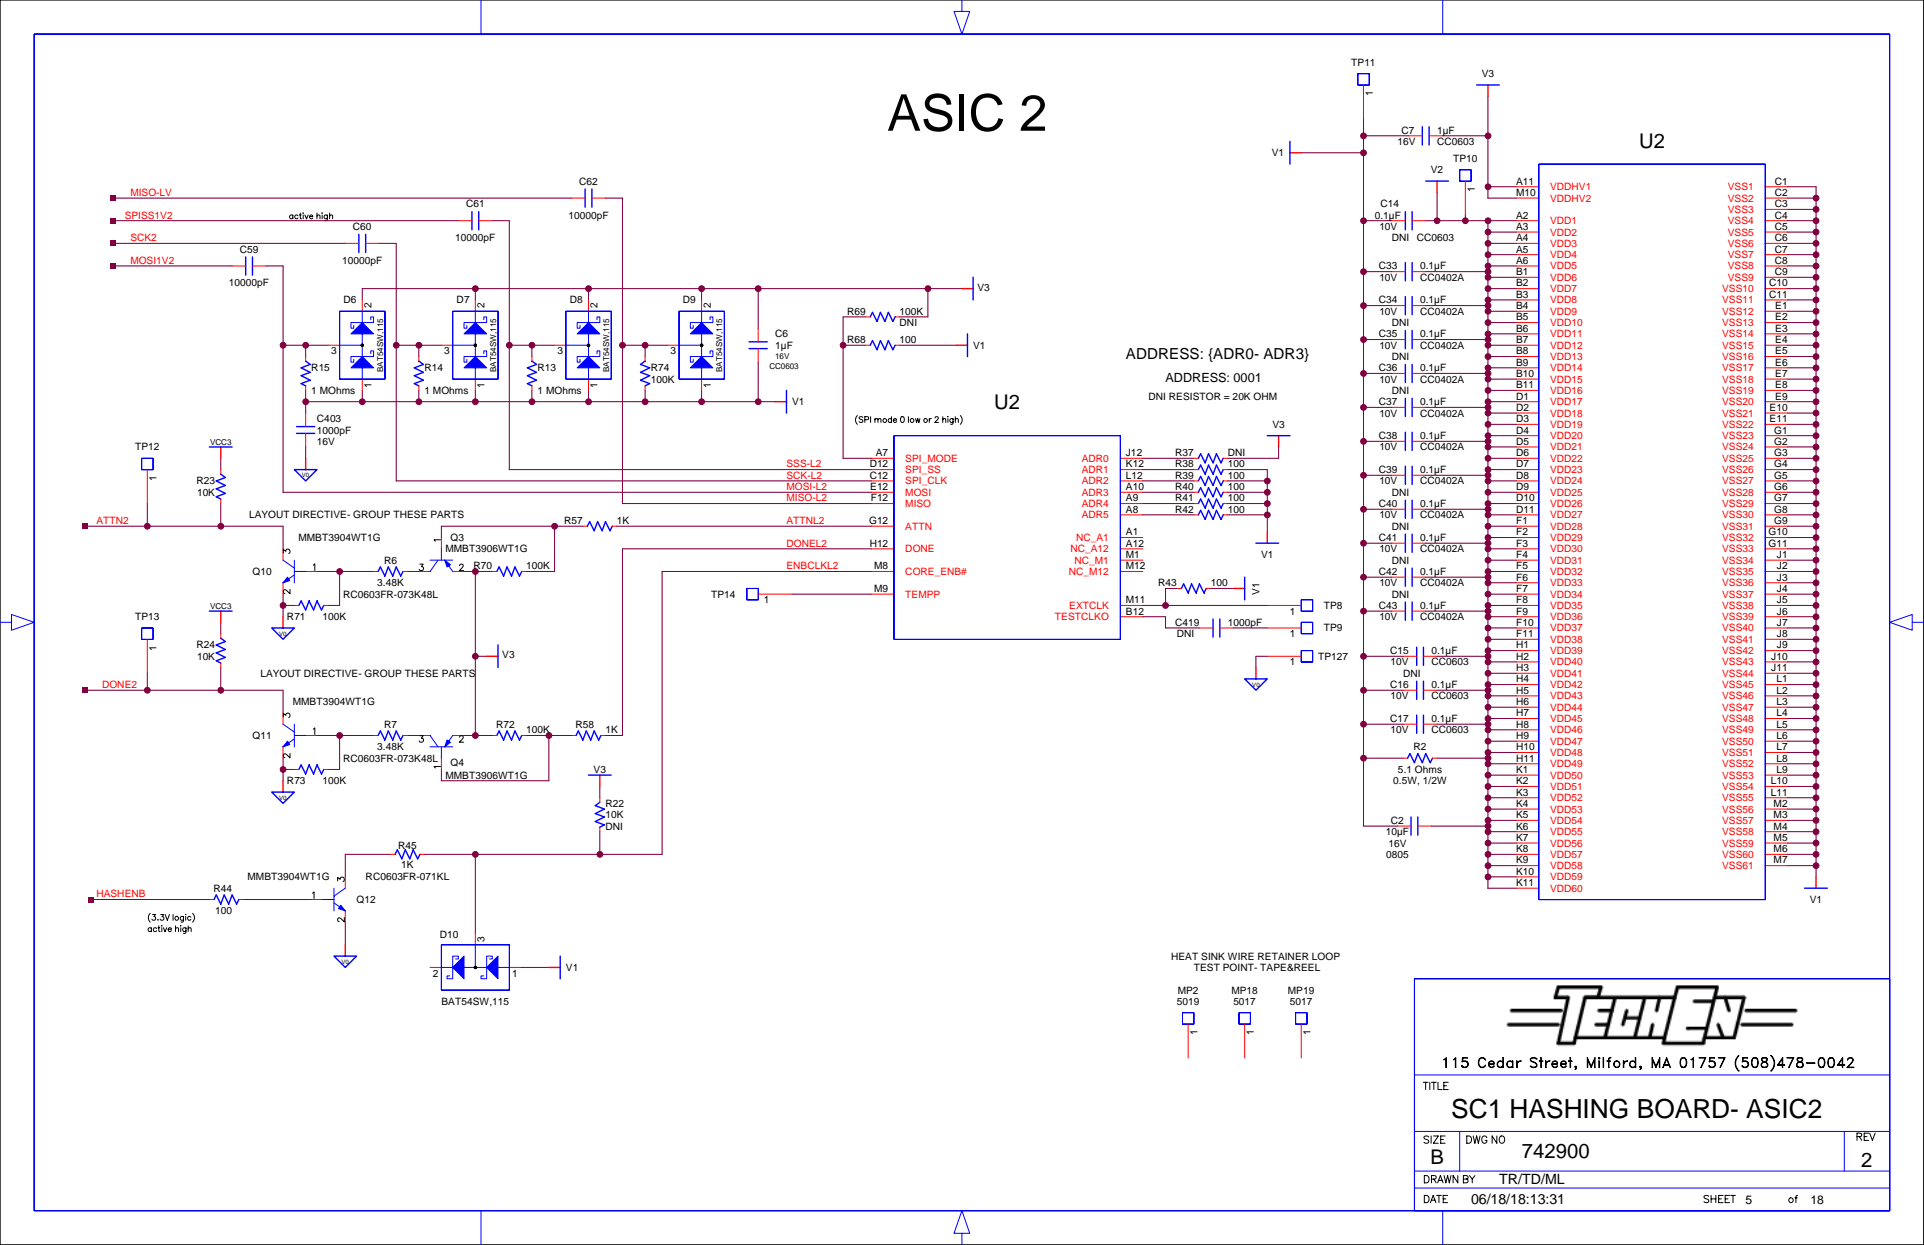
[picture p92: page 5]

A3 | C5
A4 | C6
A5 | C7
A6 | C8

B5 | E2
B6 | E3

B8 | E5
B9 | E6

B11 | E8
D1 | E9

D3 | E11
D4 | G1

LAYOUT DIRECTIVE- GROUP THESE PARTS

F7 | J4
F8 | J5

F10 | J7
F11 | J8
H1 | J9

H3 | J11
H4 | L1

H6 | L3
H7 | L4

H9 | L6
H10 | L7

K1 | L9
K2 | L10
K3 | L11
K4 | M2
K5 | M3

K7 | M5
K8 | M6
K9 | M7

HEAT SINK WIRE RETAINER LOOP
TEST POINT- TAPE&REEL

# ASIC 3

U3

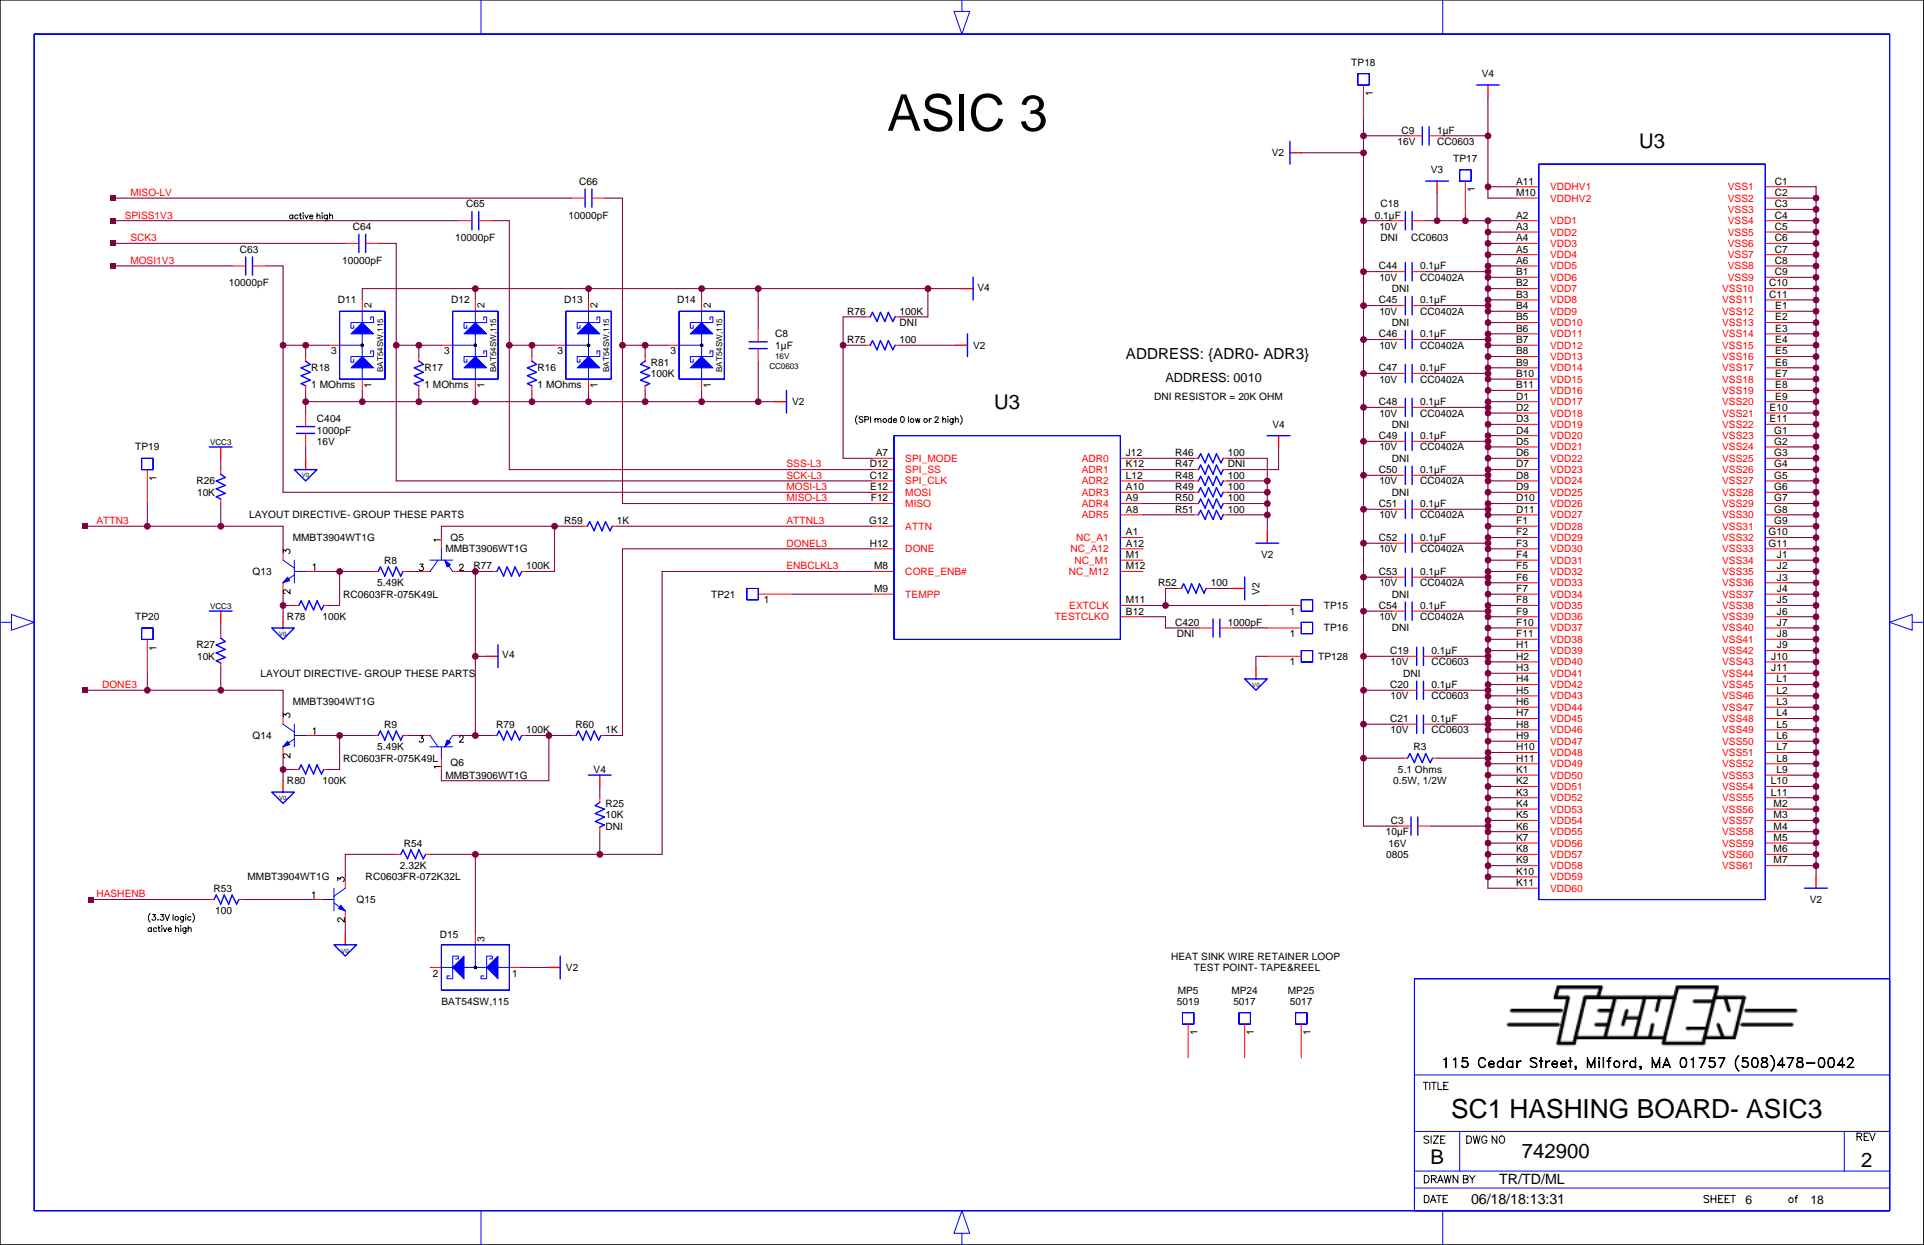
[picture p93: page 6]

A3 | C5
A4 | C6
A5 | C7
A6 | C8

B8 | E5
B9 | E6

B11 | E8
D1 | E9

D3 | E11
D4 | G1

LAYOUT DIRECTIVE- GROUP THESE PARTS

F7 | J4
F8 | J5

F10 | J7
F11 | J8
H1 | J9

H3 | J11
H4 | L1

H6 | L3
H7 | L4

H9 | L6
H10 | L7

K1 | L9
K2 | L10
K3 | L11
K4 | M2
K5 | M3

K7 | M5
K8 | M6
K9 | M7

HEAT SINK WIRE RETAINER LOOP
TEST POINT- TAPE&REEL

# ASIC 4

U4

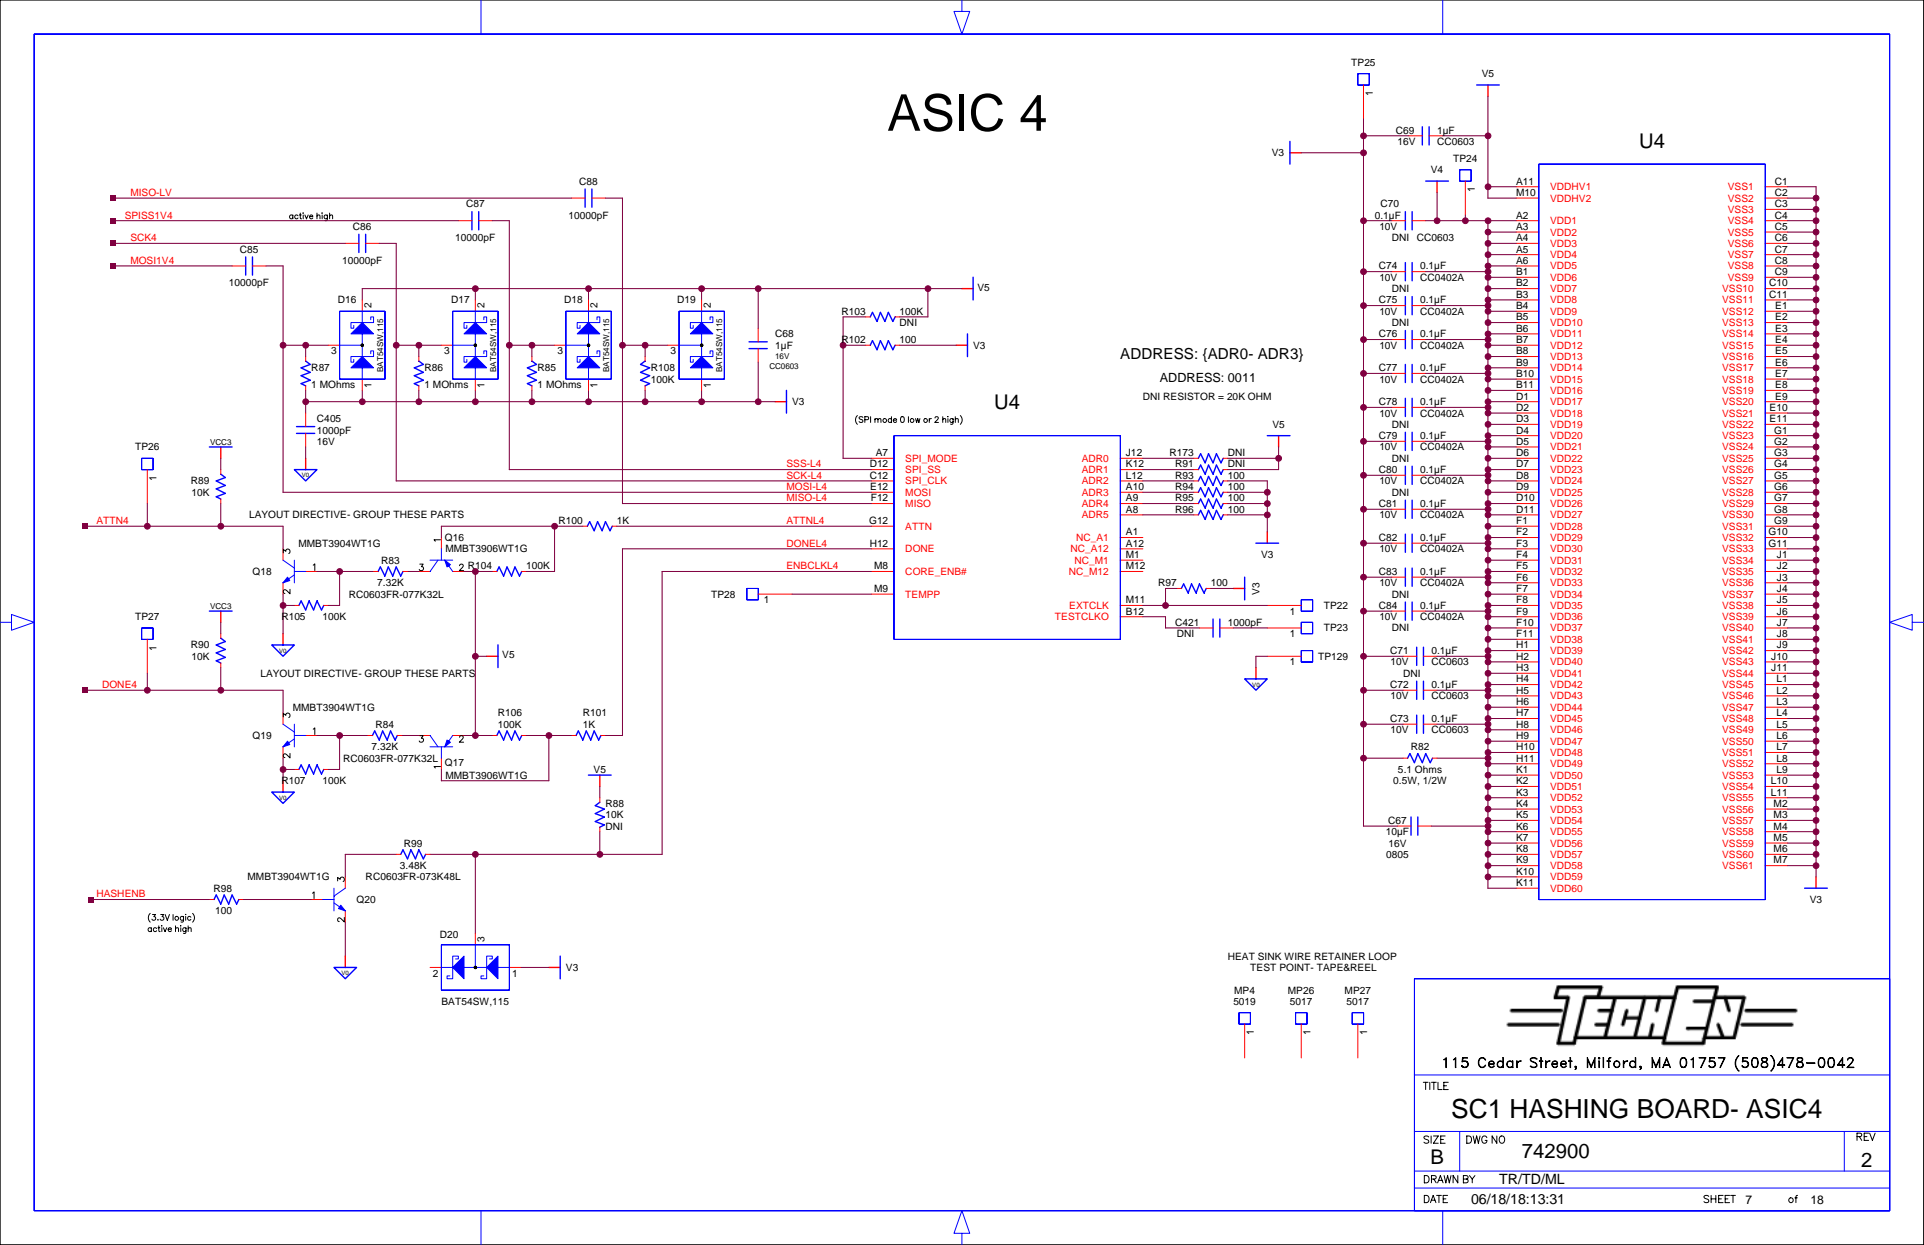
[picture p94: page 7]

A3 | C5
A4 | C6
A5 | C7
A6 | C8

B8 | E5
B9 | E6

B11 | E8
D1 | E9

D3 | E11
D4 | G1

LAYOUT DIRECTIVE- GROUP THESE PARTS

F1 | G9
F2 | G10

F7 | J4
F8 | J5

F10 | J7
F11 | J8
H1 | J9

H3 | J11
H4 | L1

H6 | L3
H7 | L4

H9 | L6
H10 | L7

K1 | L9
K2 | L10
K3 | L11
K4 | M2
K5 | M3

K7 | M5
K8 | M6
K9 | M7

HEAT SINK WIRE RETAINER LOOP
TEST POINT- TAPE&REEL

# ASIC 5

U5

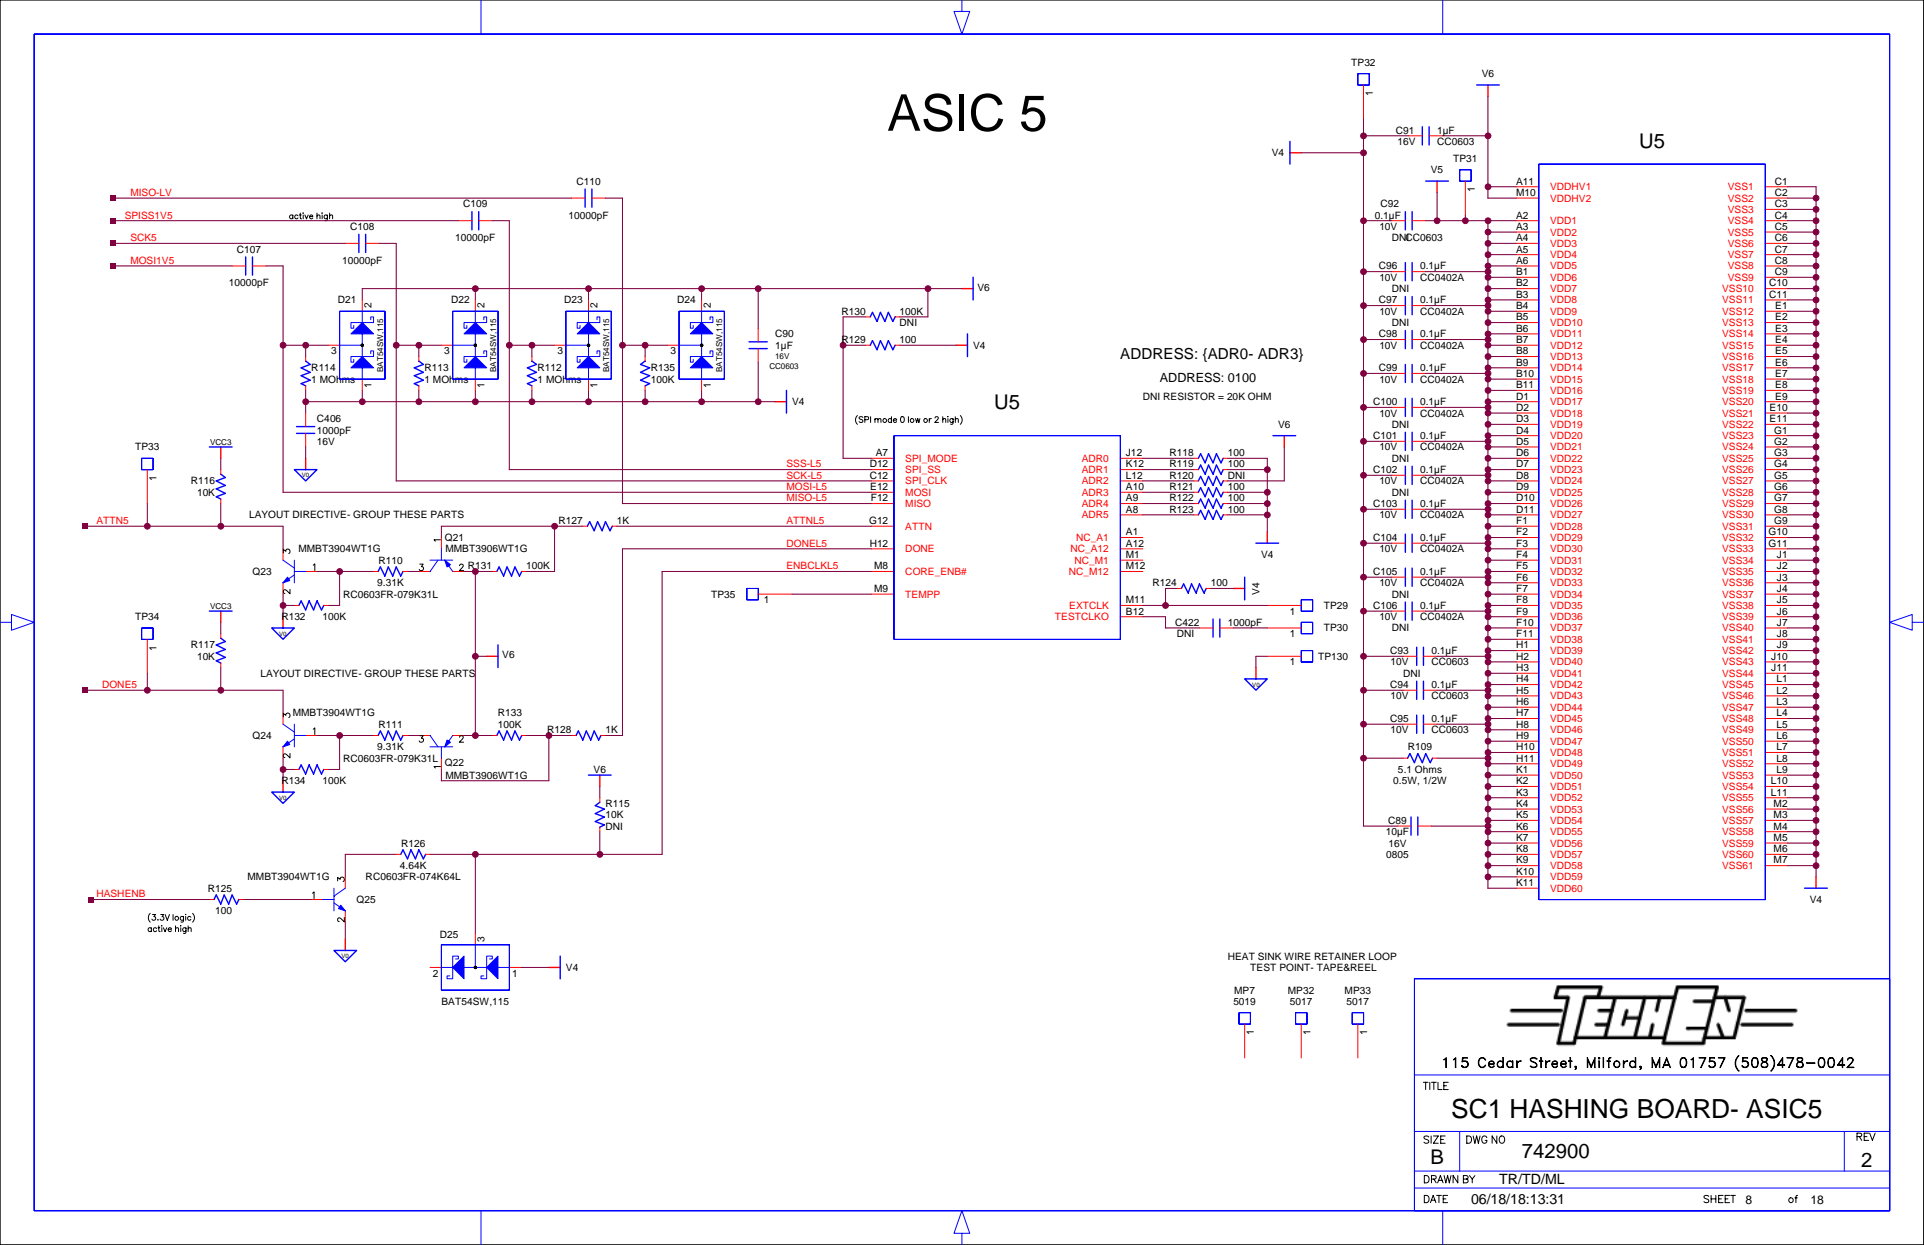
[picture p95: page 8]

A3 | C5
A4 | C6
A5 | C7
A6 | C8

B8 | E5
B9 | E6

B11 | E8
D1 | E9

D3 | E11
D4 | G1

LAYOUT DIRECTIVE- GROUP THESE PARTS

F1 | G9
F2 | G10

F7 | J4
F8 | J5

F10 | J7
F11 | J8
H1 | J9

H3 | J11
H4 | L1

H6 | L3
H7 | L4

H9 | L6
H10 | L7

K1 | L9
K2 | L10
K3 | L11
K4 | M2
K5 | M3

K7 | M5
K8 | M6
K9 | M7

HEAT SINK WIRE RETAINER LOOP
TEST POINT- TAPE&REEL

# ASIC 6

U6

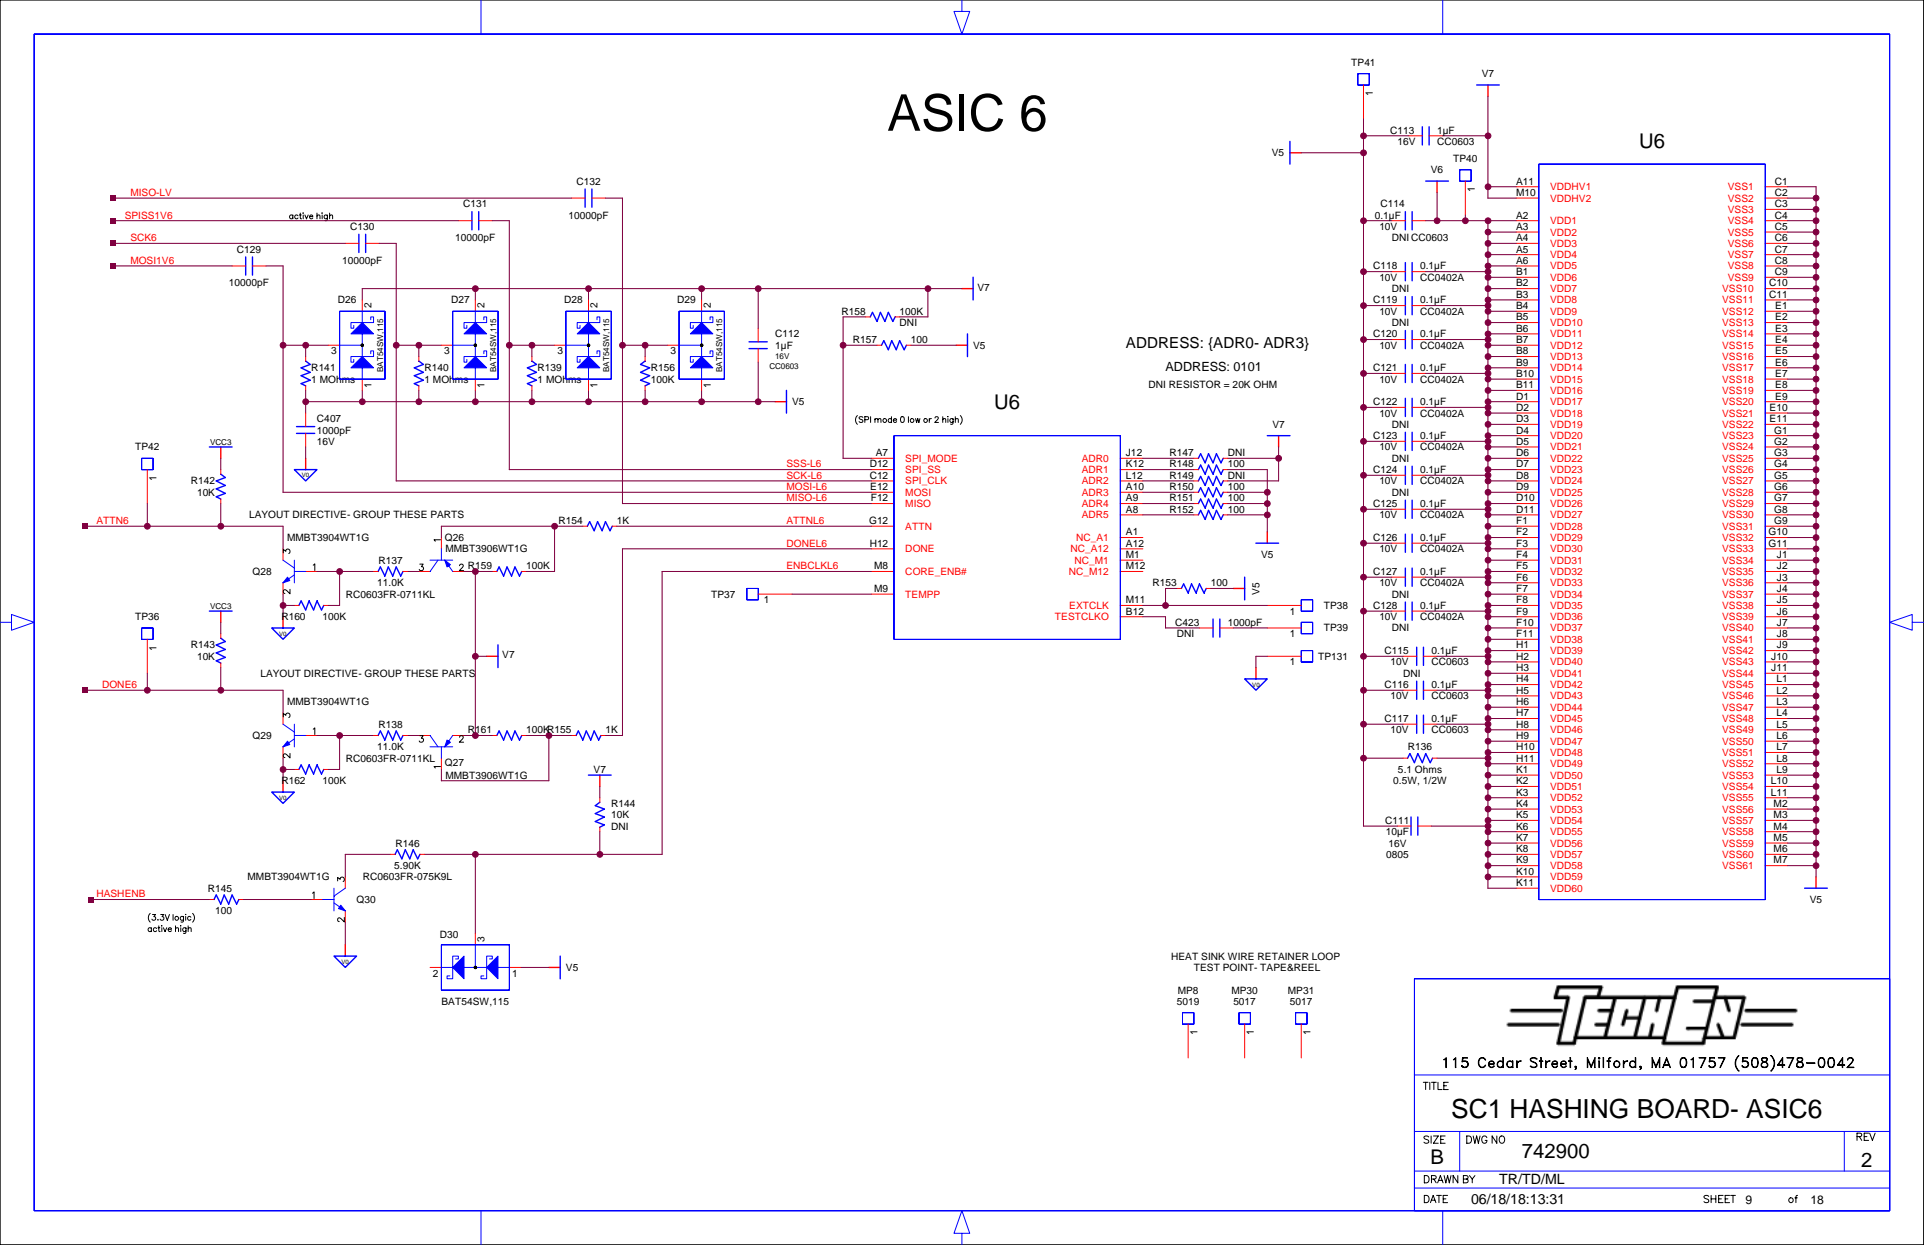
[picture p96: page 9]

A3 | C5
A4 | C6
A5 | C7
A6 | C8

B8 | E5
B9 | E6

B11 | E8
D1 | E9

D3 | E11
D4 | G1

LAYOUT DIRECTIVE- GROUP THESE PARTS

F7 | J4
F8 | J5

F10 | J7
F11 | J8
H1 | J9

H3 | J11
H4 | L1

H6 | L3
H7 | L4

H9 | L6
H10 | L7

K1 | L9
K2 | L10
K3 | L11
K4 | M2
K5 | M3

K7 | M5
K8 | M6
K9 | M7

HEAT SINK WIRE RETAINER LOOP
TEST POINT- TAPE&REEL

# ASIC 7

U7

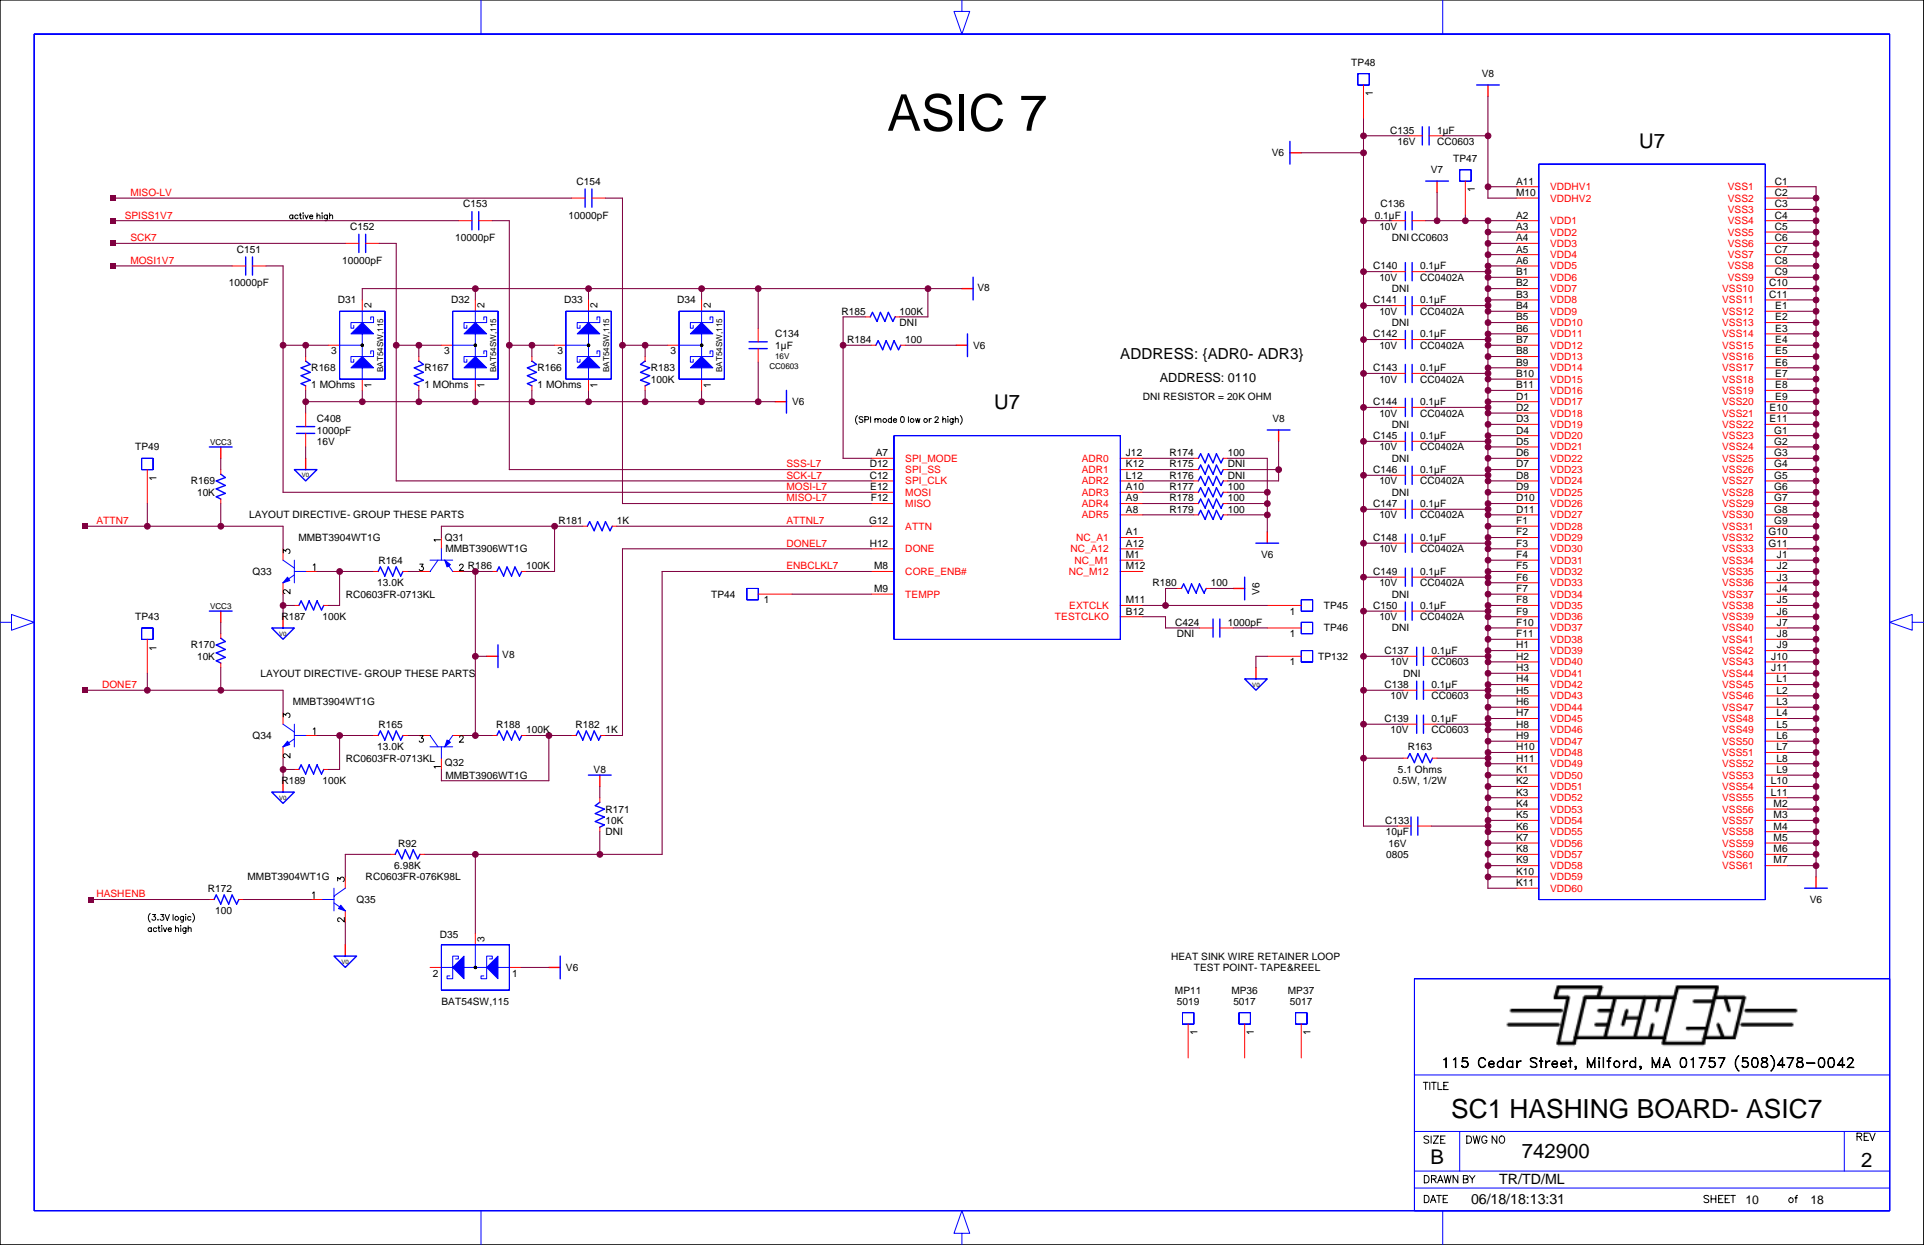
[picture p97: page 10]

A3 | C5
A4 | C6
A5 | C7
A6 | C8

B8 | E5
B9 | E6

B11 | E8
D1 | E9

D3 | E11
D4 | G1

LAYOUT DIRECTIVE- GROUP THESE PARTS

F7 | J4
F8 | J5

F10 | J7
F11 | J8
H1 | J9

H3 | J11
H4 | L1

H6 | L3
H7 | L4

H9 | L6
H10 | L7

K1 | L9
K2 | L10
K3 | L11
K4 | M2
K5 | M3

K7 | M5
K8 | M6
K9 | M7

HEAT SINK WIRE RETAINER LOOP
TEST POINT- TAPE&REEL

# ASIC 8

U8

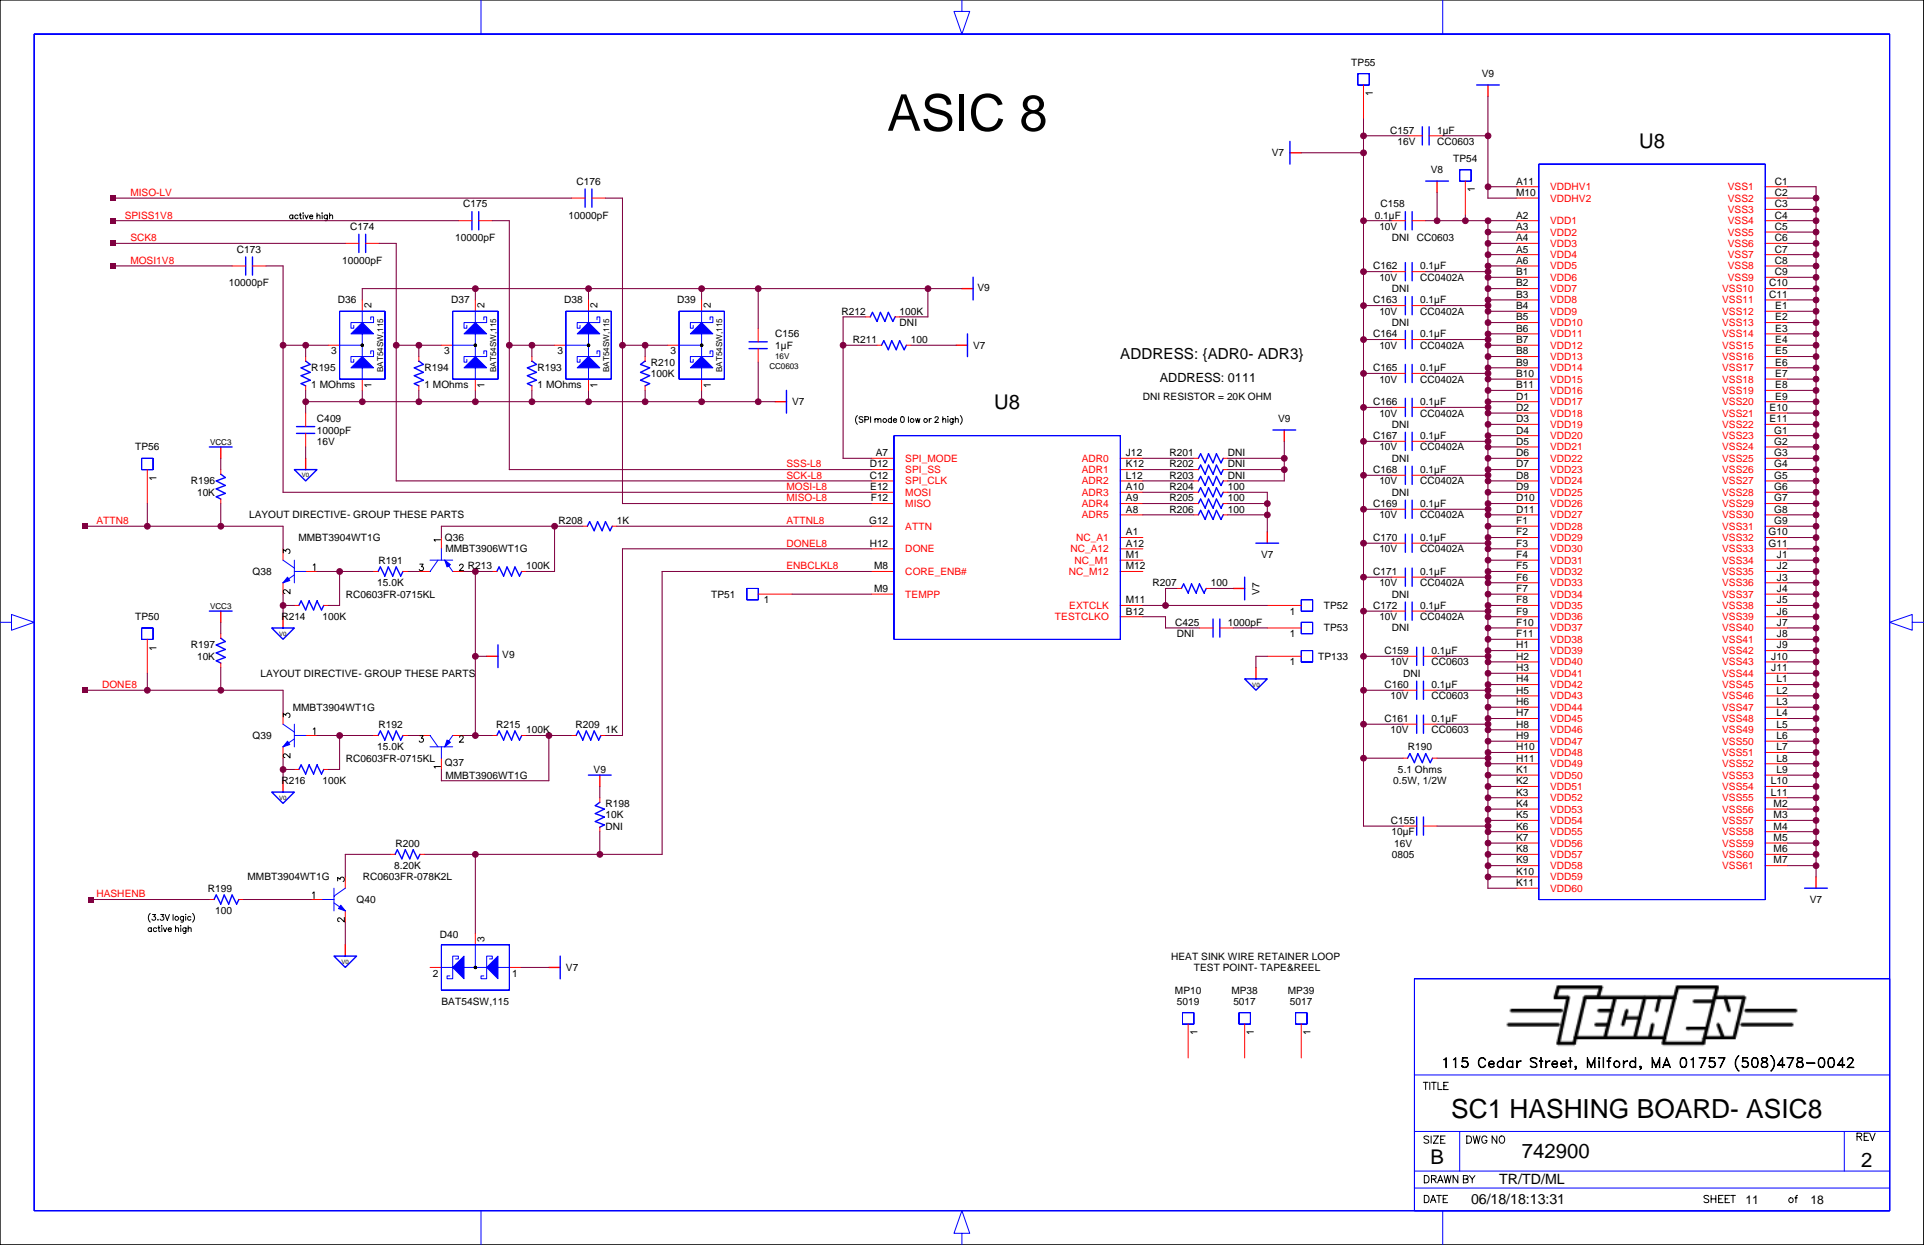
[picture p98: page 11]

A3 | C5
A4 | C6
A5 | C7
A6 | C8

B8 | E5
B9 | E6

B11 | E8
D1 | E9

D3 | E11
D4 | G1

LAYOUT DIRECTIVE- GROUP THESE PARTS

F7 | J4
F8 | J5

F10 | J7
F11 | J8
H1 | J9

H3 | J11
H4 | L1

H6 | L3
H7 | L4

H9 | L6
H10 | L7

K1 | L9
K2 | L10
K3 | L11
K4 | M2
K5 | M3

K7 | M5
K8 | M6
K9 | M7

HEAT SINK WIRE RETAINER LOOP
TEST POINT- TAPE&REEL

# ASIC 9

U9

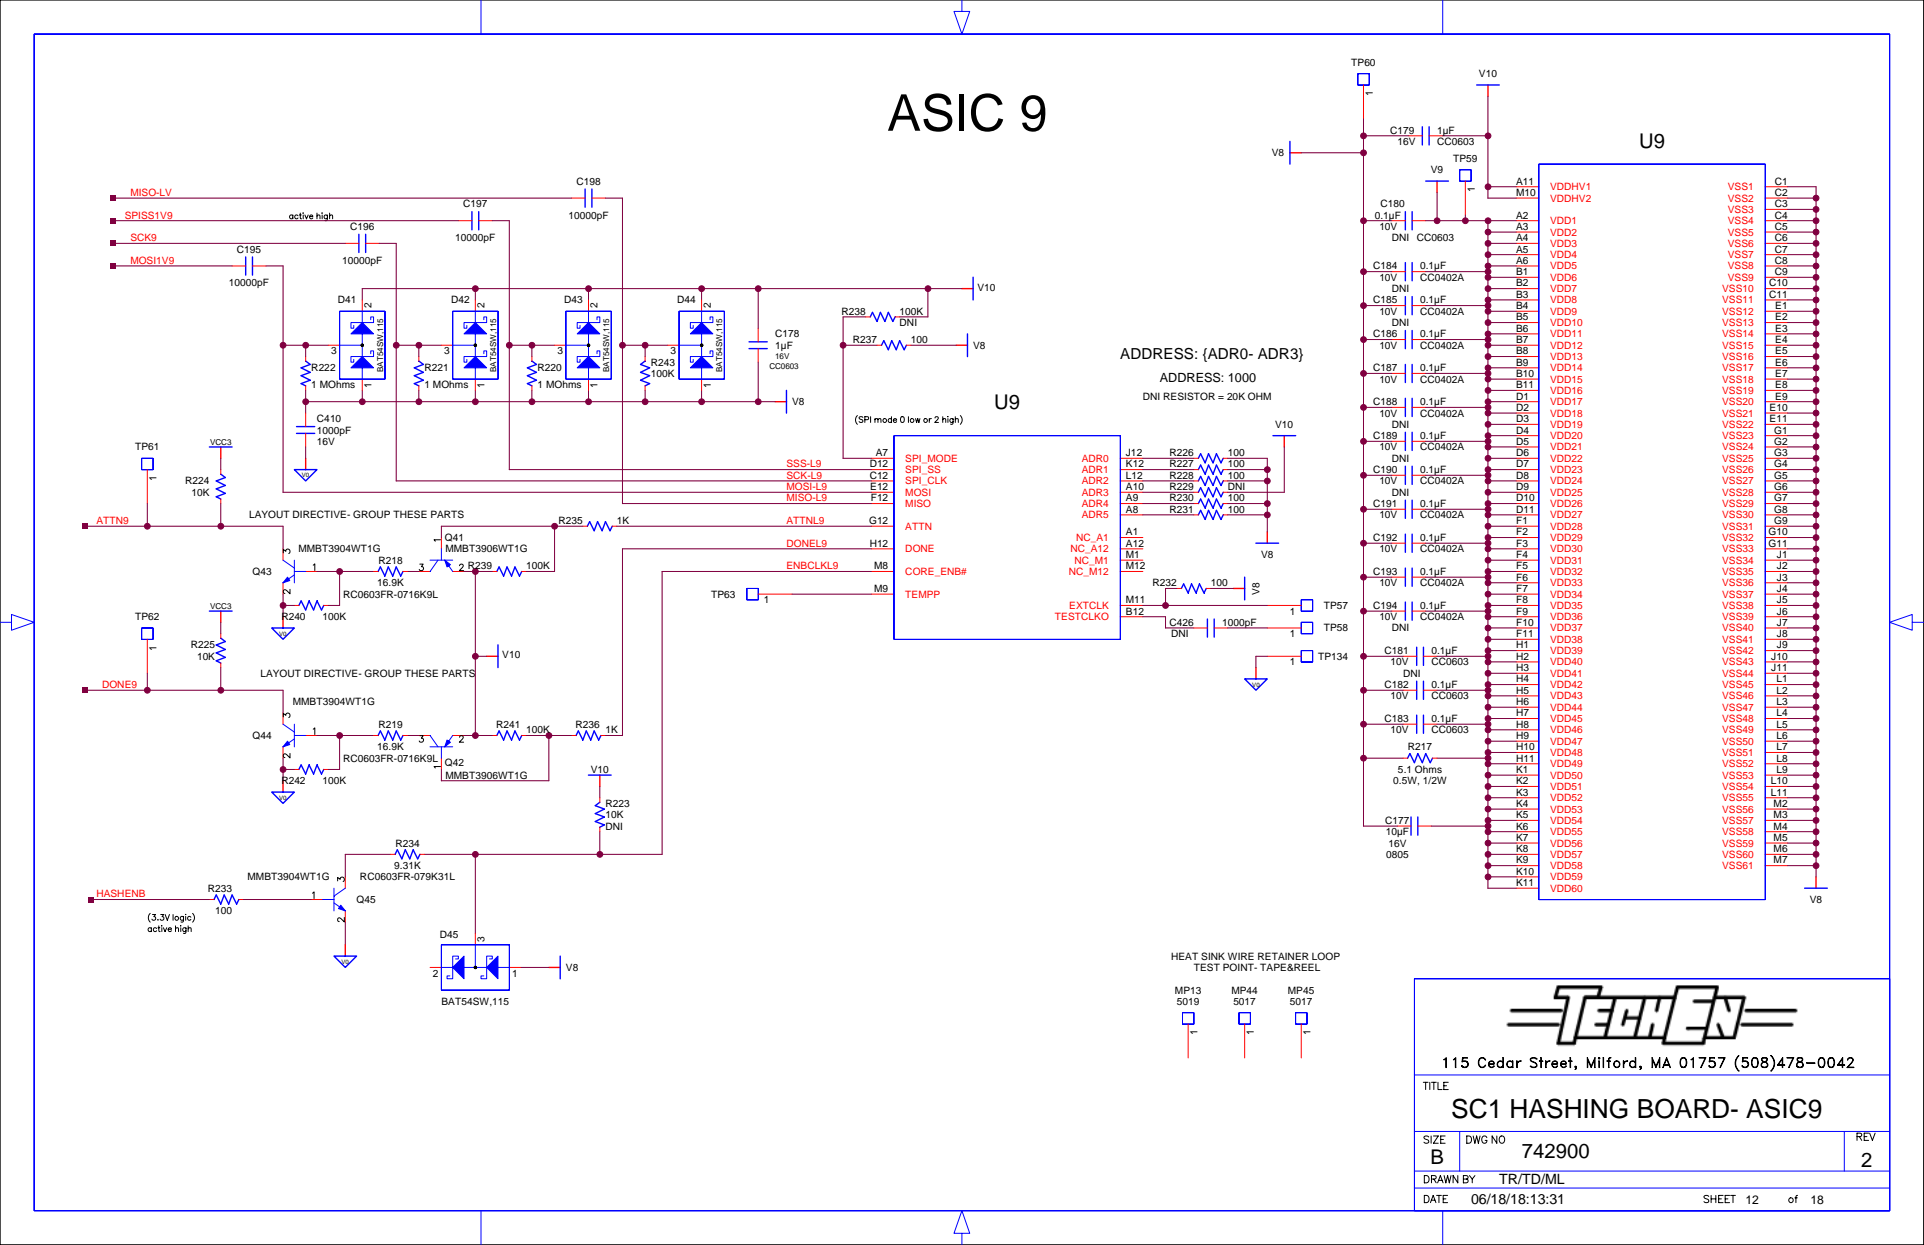
[picture p99: page 12]

A3 | C5
A4 | C6
A5 | C7
A6 | C8

B8 | E5
B9 | E6

B11 | E8
D1 | E9

D3 | E11
D4 | G1

LAYOUT DIRECTIVE- GROUP THESE PARTS

F7 | J4
F8 | J5

F10 | J7
F11 | J8
H1 | J9

H3 | J11
H4 | L1

H6 | L3
H7 | L4

H9 | L6
H10 | L7

K1 | L9
K2 | L10
K3 | L11
K4 | M2
K5 | M3

K7 | M5
K8 | M6
K9 | M7

HEAT SINK WIRE RETAINER LOOP
TEST POINT- TAPE&REEL

# ASIC 10

U10

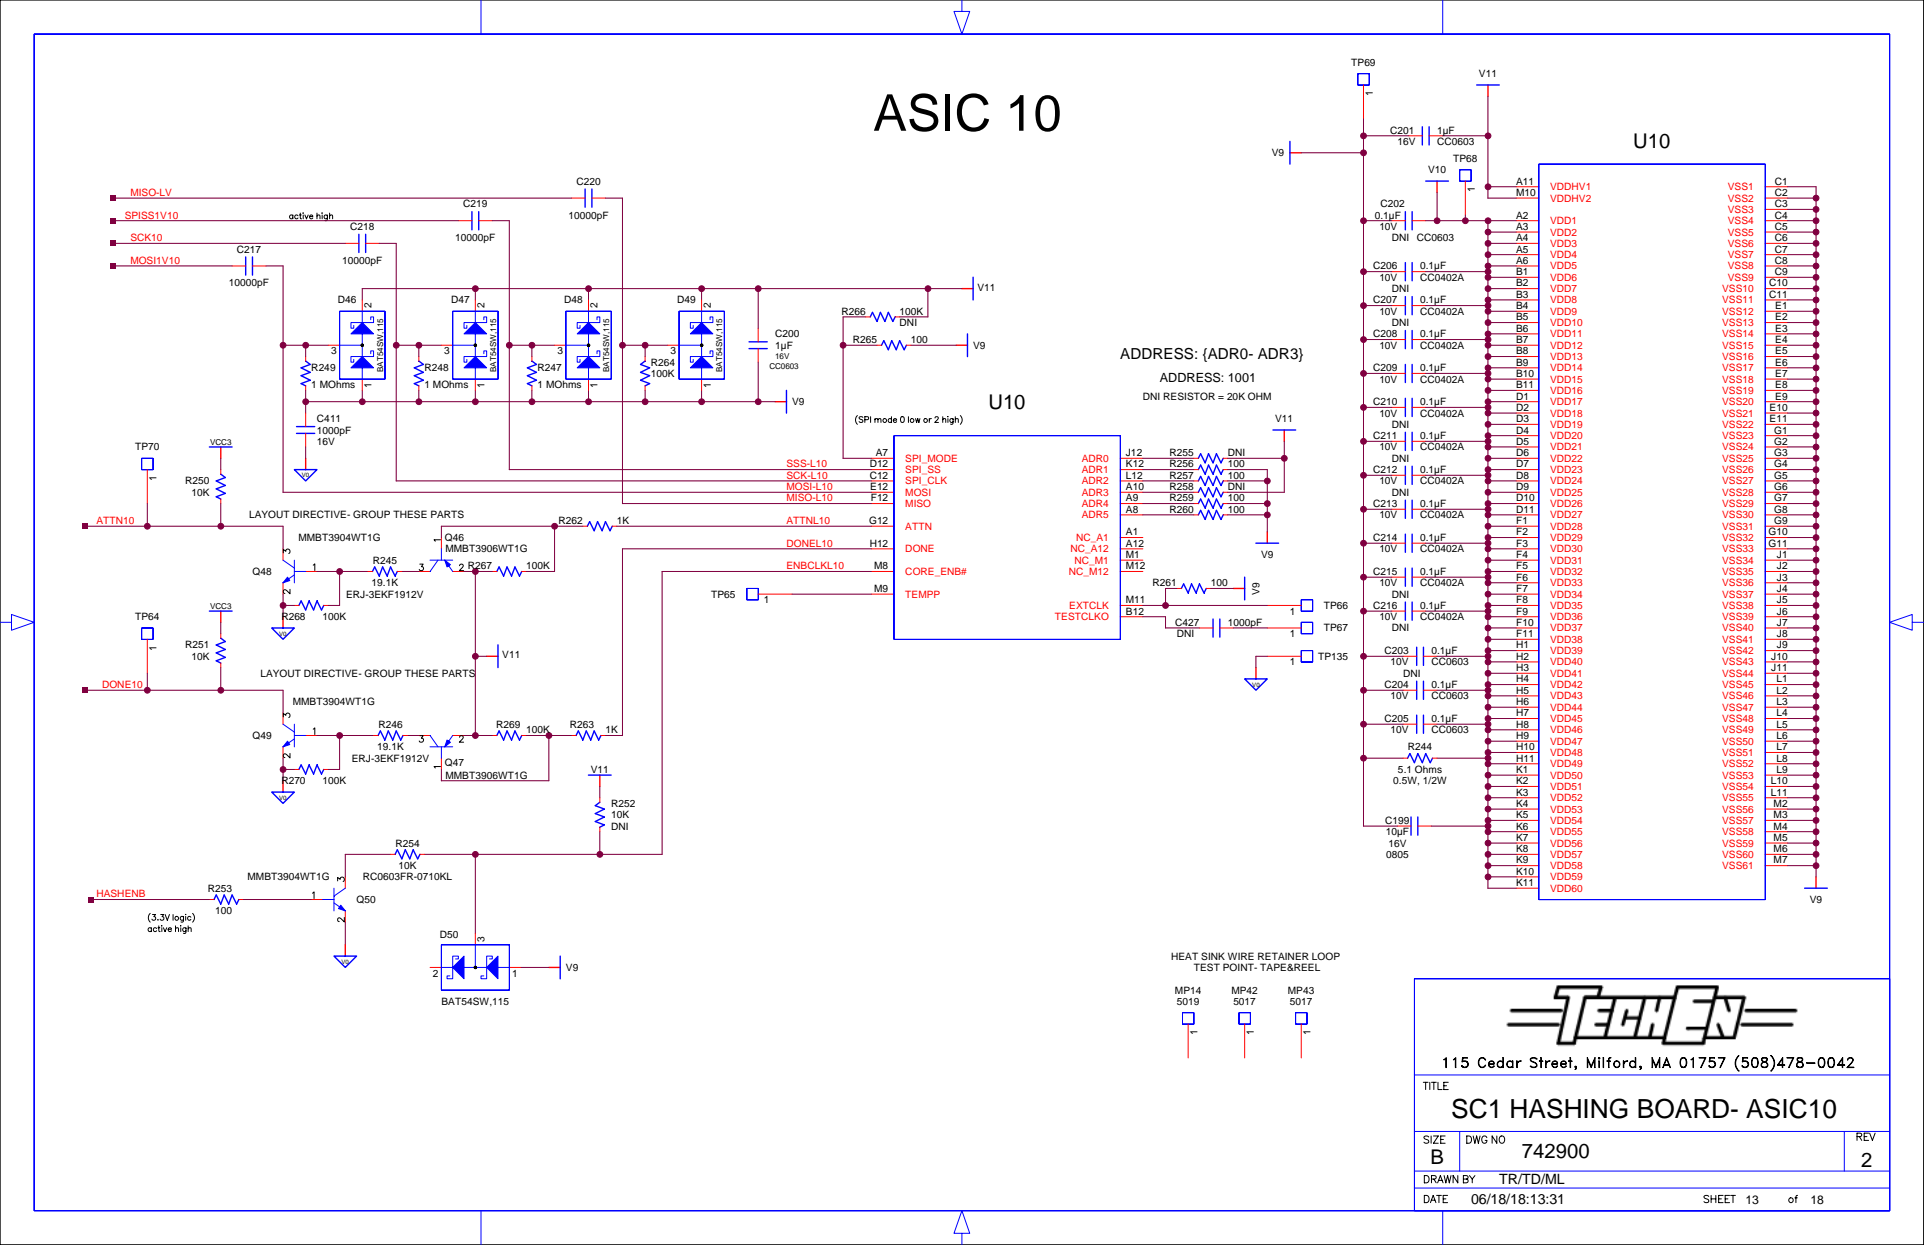
[picture p100: page 13]

A3 | C5
A4 | C6
A5 | C7
A6 | C8

B8 | E5
B9 | E6

B11 | E8
D1 | E9

D3 | E11
D4 | G1

LAYOUT DIRECTIVE- GROUP THESE PARTS

F7 | J4
F8 | J5

F10 | J7
F11 | J8
H1 | J9

H3 | J11
H4 | L1

H6 | L3
H7 | L4

H9 | L6
H10 | L7

K1 | L9
K2 | L10
K3 | L11
K4 | M2
K5 | M3

K7 | M5
K8 | M6
K9 | M7

HEAT SINK WIRE RETAINER LOOP
TEST POINT- TAPE&REEL

# ASIC 11

U11

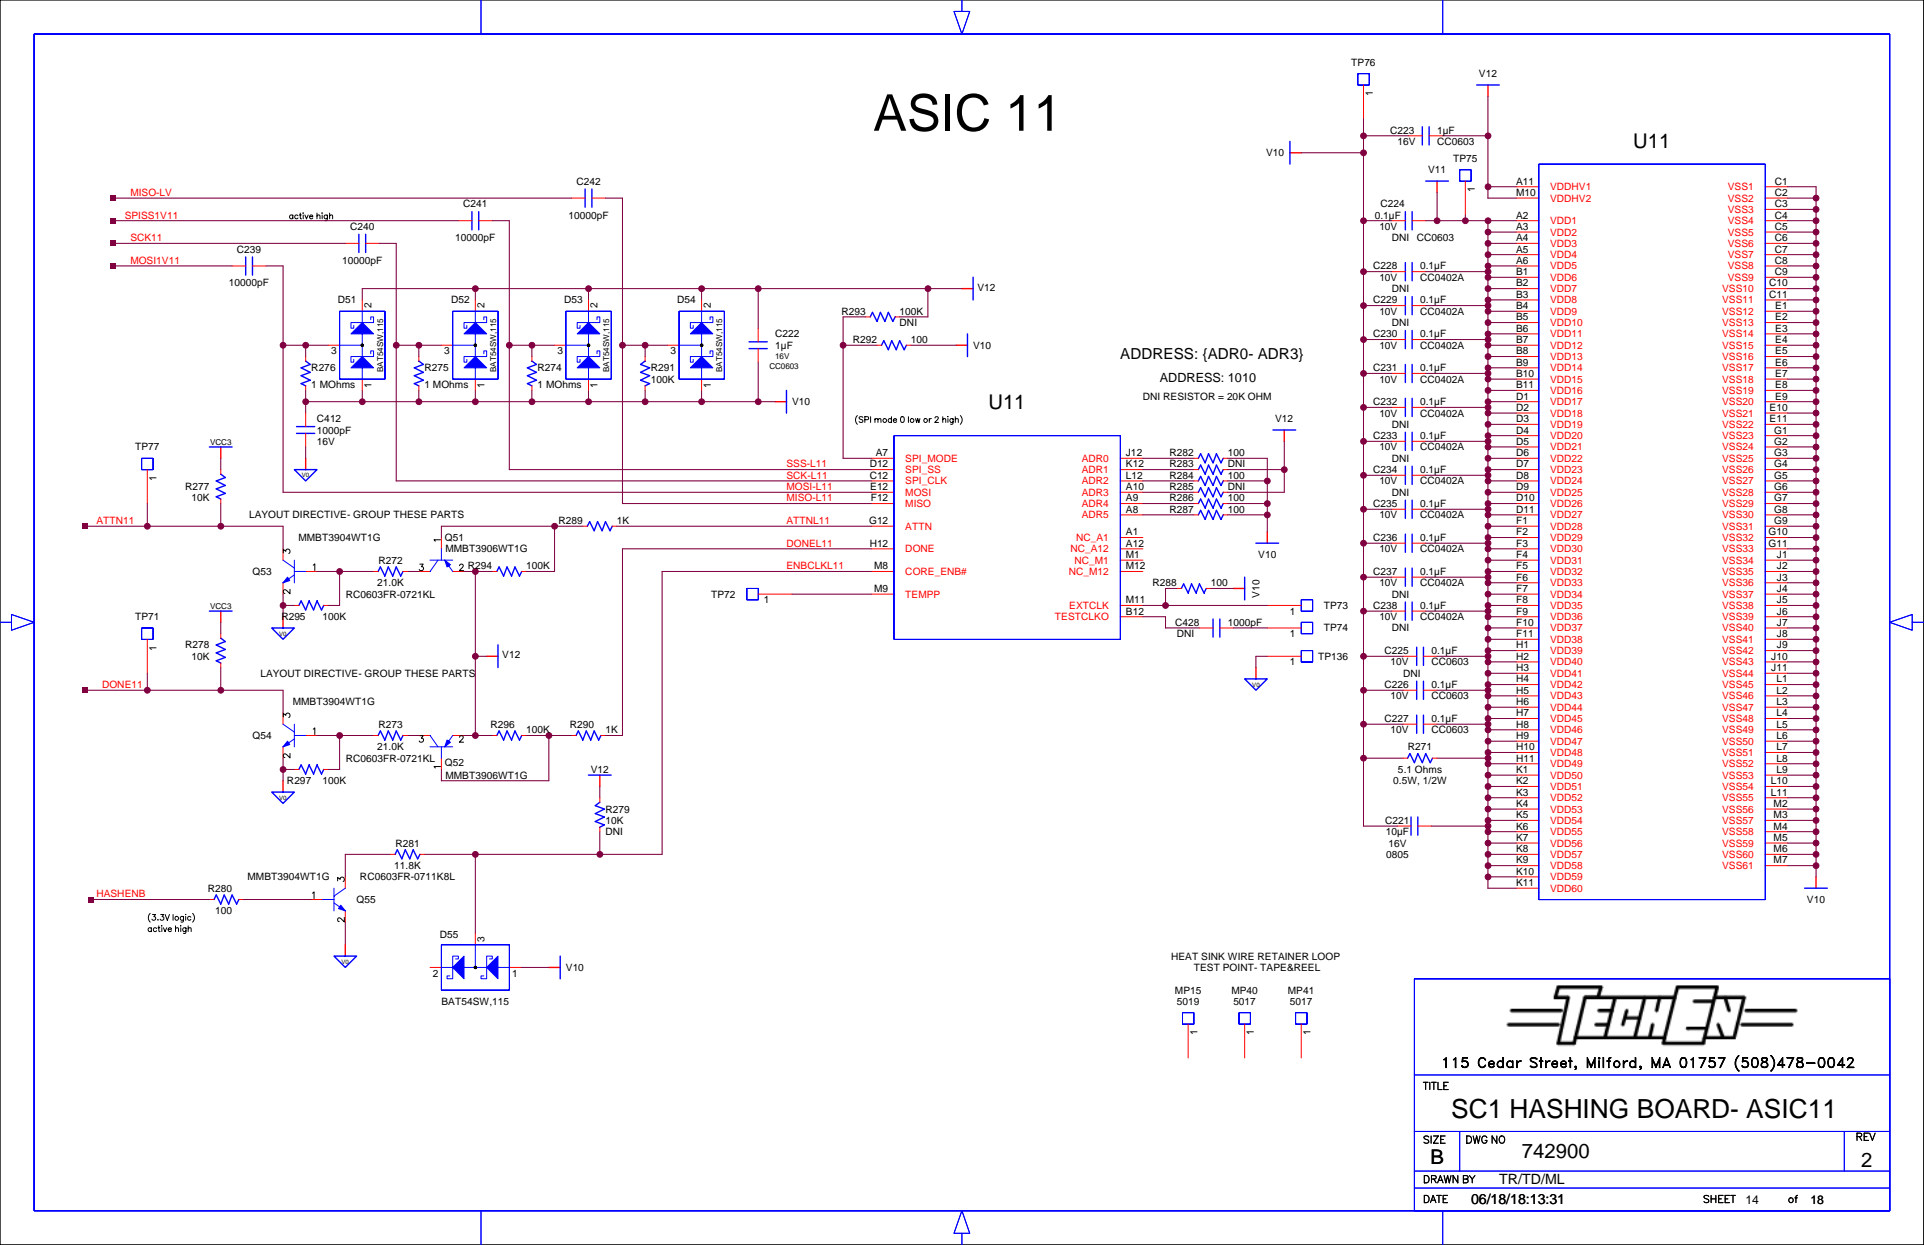
[picture p101: page 14]

A3 | C5
A4 | C6
A5 | C7
A6 | C8

B8 | E5
B9 | E6

B11 | E8
D1 | E9

D3 | E11
D4 | G1

LAYOUT DIRECTIVE- GROUP THESE PARTS

F7 | J4
F8 | J5

F10 | J7
F11 | J8
H1 | J9

H3 | J11
H4 | L1

H6 | L3
H7 | L4

H9 | L6
H10 | L7

K1 | L9
K2 | L10
K3 | L11
K4 | M2
K5 | M3

K7 | M5
K8 | M6
K9 | M7

HEAT SINK WIRE RETAINER LOOP
TEST POINT- TAPE&REEL

# ASIC 12

U12

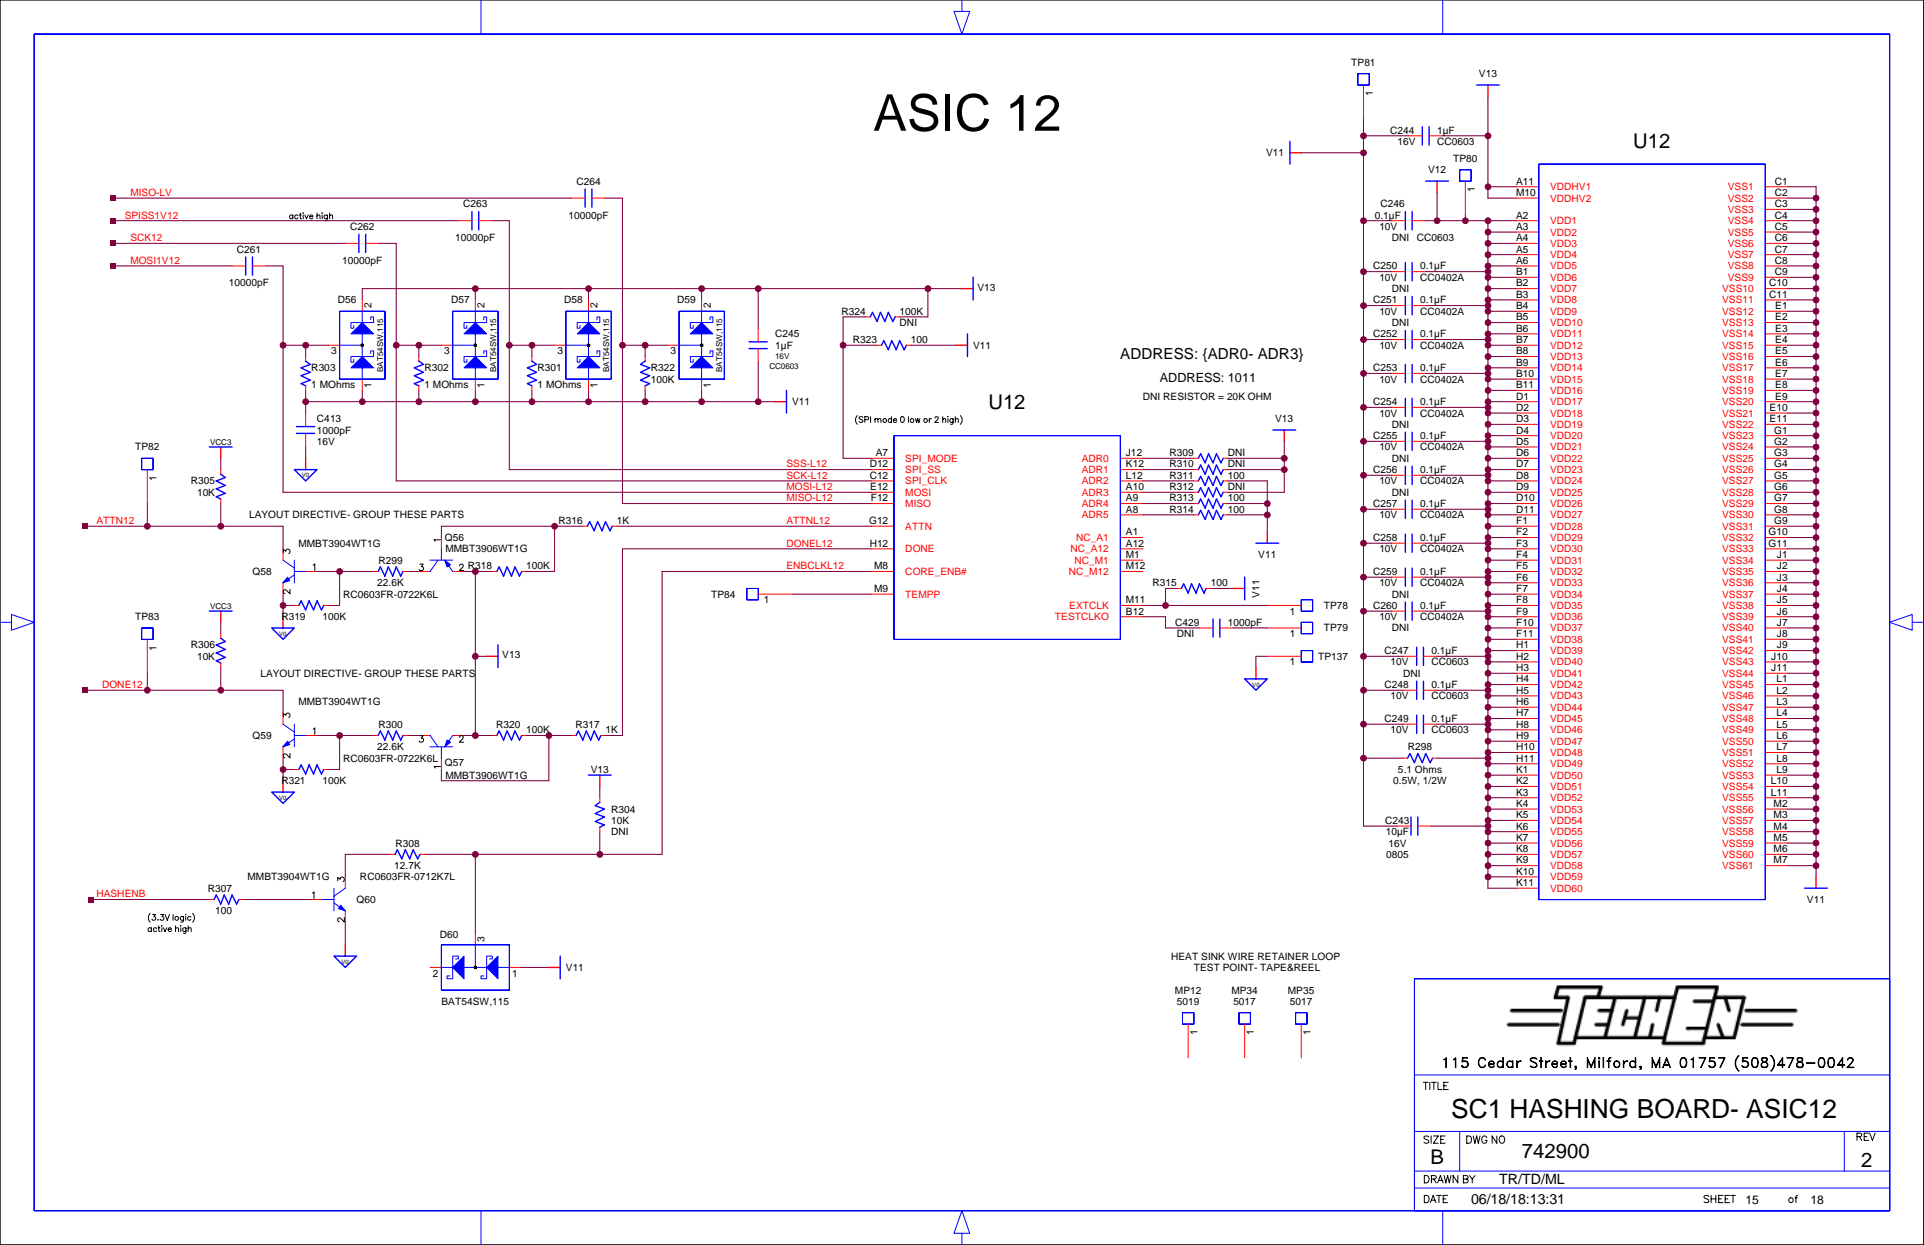
[picture p102: page 15]

A3 | C5
A4 | C6
A5 | C7
A6 | C8

B8 | E5
B9 | E6

B11 | E8
D1 | E9

D3 | E11
D4 | G1

LAYOUT DIRECTIVE- GROUP THESE PARTS

F7 | J4
F8 | J5

F10 | J7
F11 | J8
H1 | J9

H3 | J11
H4 | L1

H6 | L3
H7 | L4

H9 | L6
H10 | L7

K1 | L9
K2 | L10
K3 | L11
K4 | M2
K5 | M3

K7 | M5
K8 | M6
K9 | M7

HEAT SINK WIRE RETAINER LOOP
TEST POINT- TAPE&REEL

# ASIC 13

U13

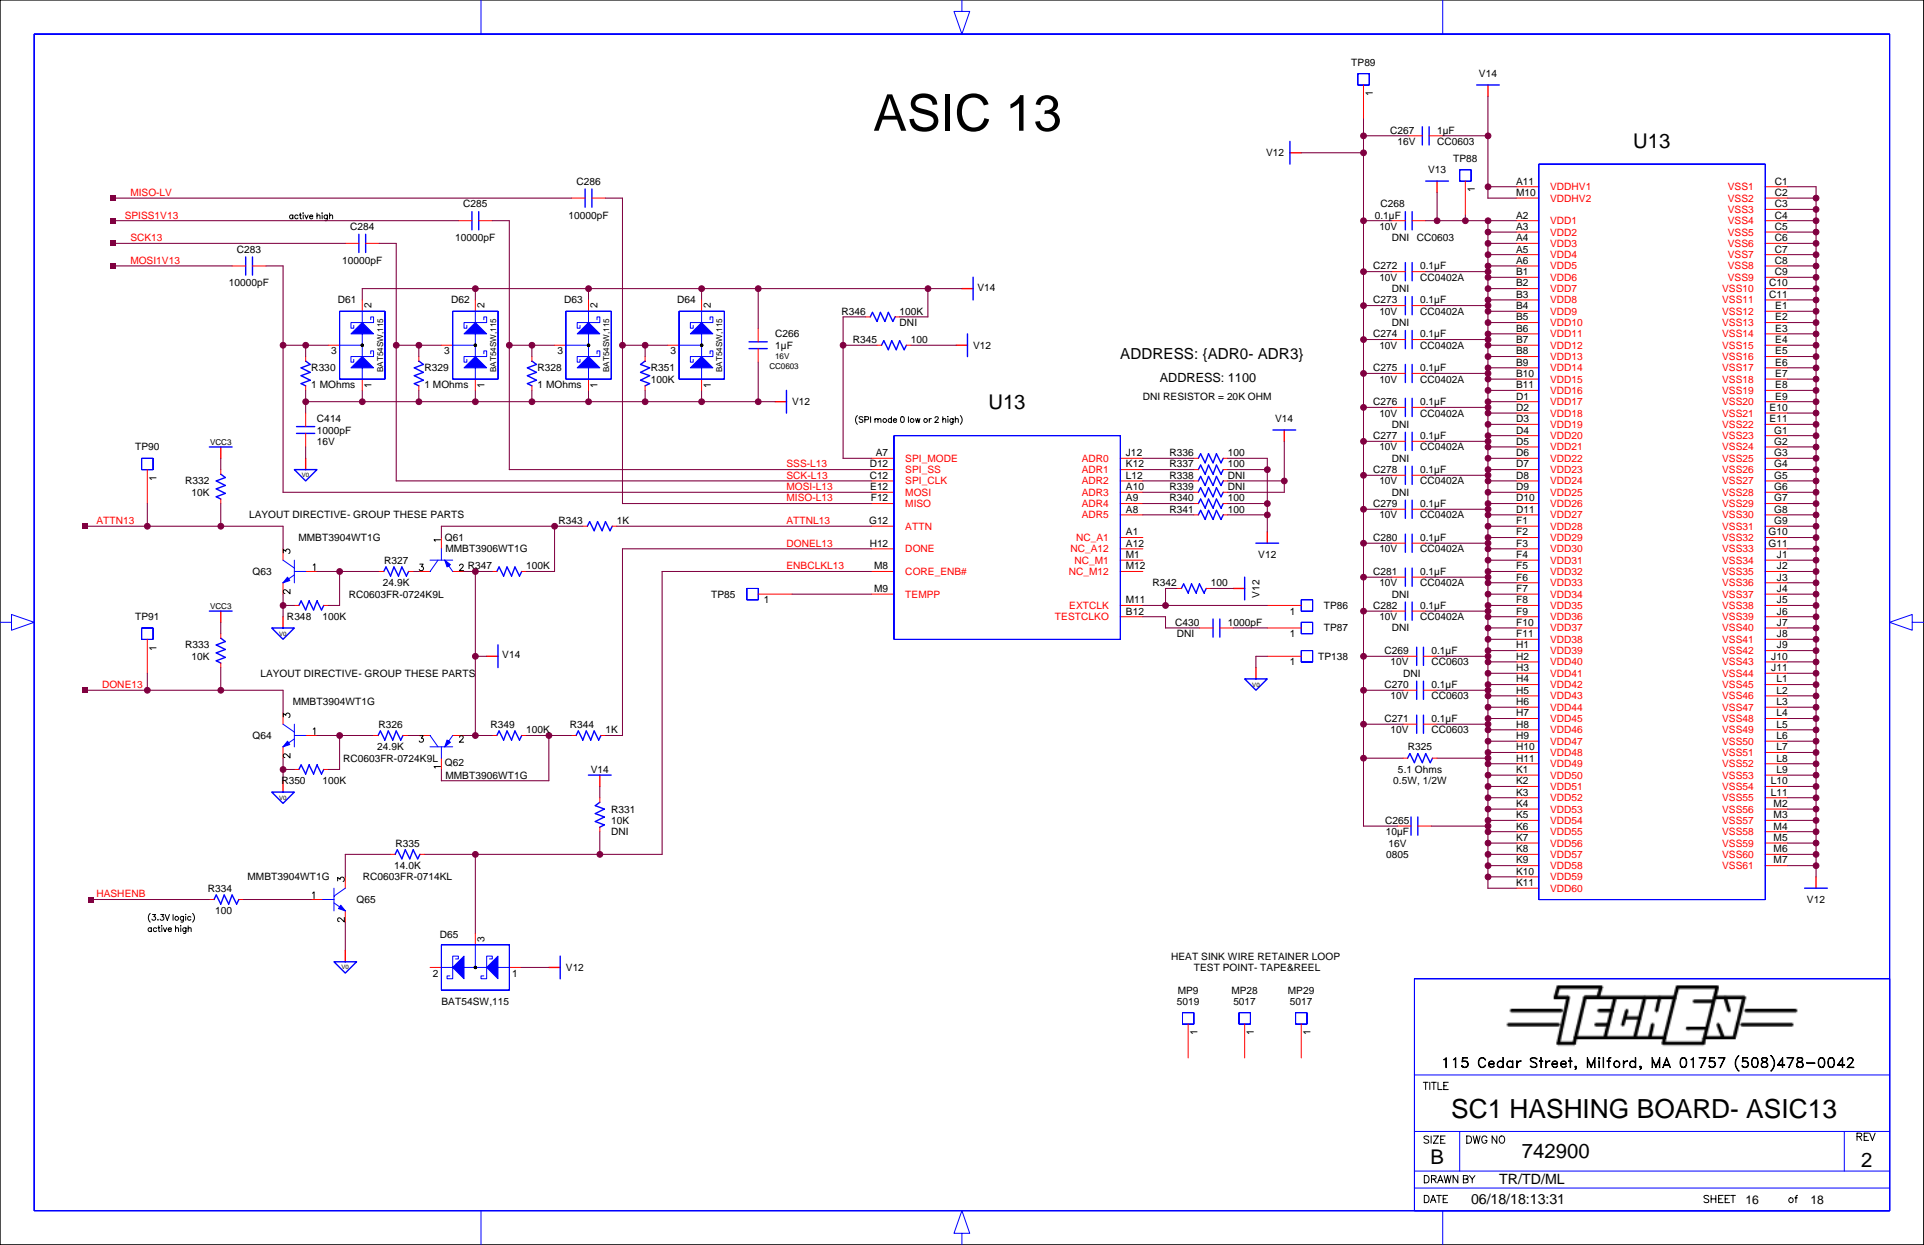
[picture p103: page 16]

A3 | C5
A4 | C6
A5 | C7
A6 | C8

B8 | E5
B9 | E6

B11 | E8
D1 | E9

D3 | E11
D4 | G1

LAYOUT DIRECTIVE- GROUP THESE PARTS

F7 | J4
F8 | J5

F10 | J7
F11 | J8
H1 | J9

H3 | J11
H4 | L1

H6 | L3
H7 | L4

H9 | L6
H10 | L7

K1 | L9
K2 | L10
K3 | L11
K4 | M2
K5 | M3

K7 | M5
K8 | M6
K9 | M7

HEAT SINK WIRE RETAINER LOOP
TEST POINT- TAPE&REEL

# ASIC 14

U14

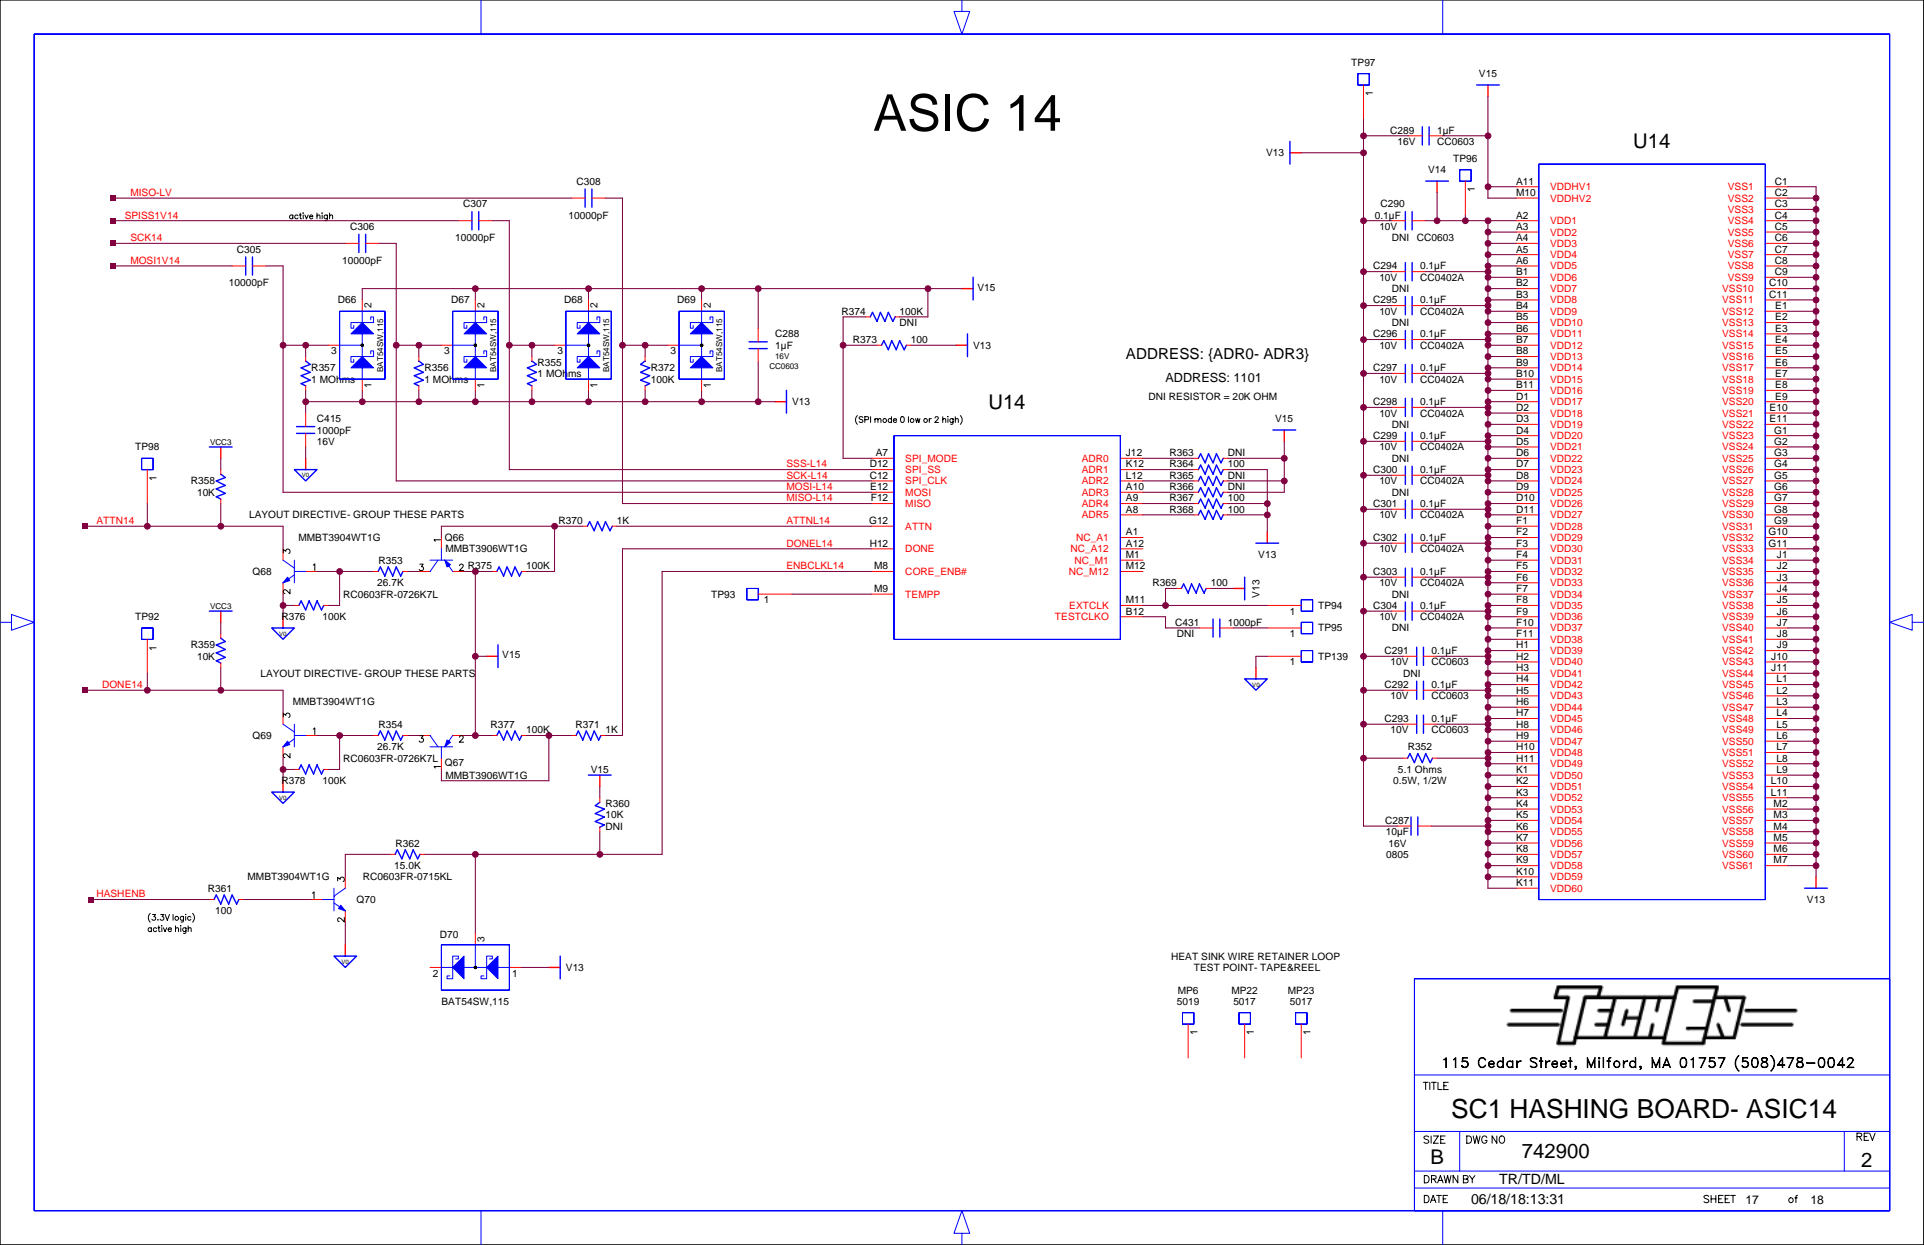
[picture p104: page 17]

A3 | C5
A4 | C6
A5 | C7
A6 | C8

B8 | E5
B9 | E6

B11 | E8
D1 | E9

D3 | E11
D4 | G1

LAYOUT DIRECTIVE- GROUP THESE PARTS

F7 | J4
F8 | J5

F10 | J7
F11 | J8
H1 | J9

H3 | J11
H4 | L1

H6 | L3
H7 | L4

H9 | L6
H10 | L7

K1 | L9
K2 | L10
K3 | L11
K4 | M2
K5 | M3

K7 | M5
K8 | M6
K9 | M7

HEAT SINK WIRE RETAINER LOOP
TEST POINT- TAPE&REEL

# ASIC 15

U15

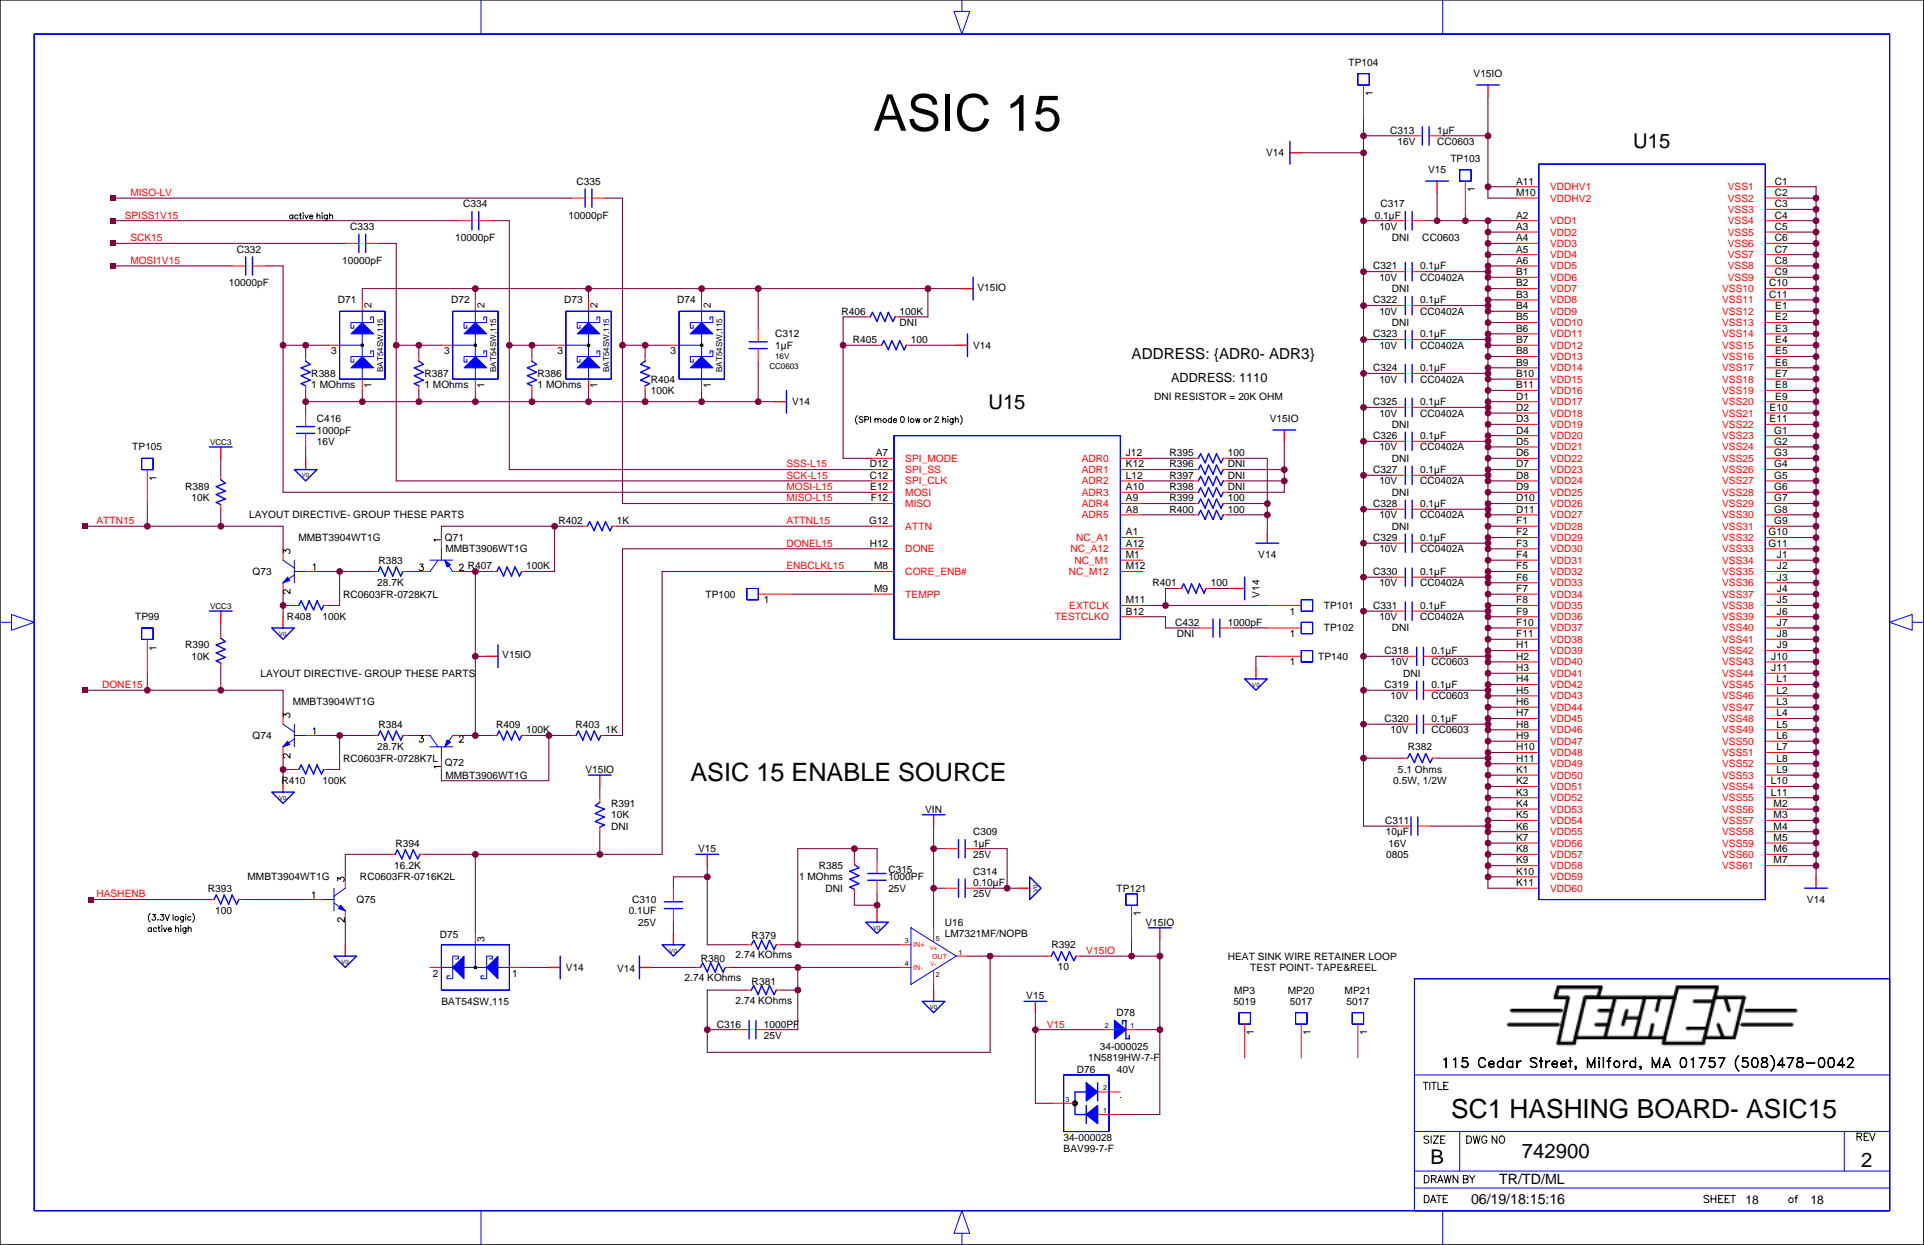
[picture p105: page 18]

A3 | C5
A4 | C6
A5 | C7
A6 | C8

B8 | E5
B9 | E6

B11 | E8
D1 | E9

D3 | E11
D4 | G1

LAYOUT DIRECTIVE- GROUP THESE PARTS

F1 | G9
F2 | G10

F7 | J4
F8 | J5

F10 | J7
F11 | J8
H1 | J9

H3 | J11
H4 | L1

H6 | L3
H7 | L4

H9 | L6
H10 | L7

K1 | L9
K2 | L10
K3 | L11
K4 | M2
K5 | M3

K7 | M5
K8 | M6
K9 | M7

HEAT SINK WIRE RETAINER LOOP
TEST POINT- TAPE&REEL
