ObeliskInc/obelisk-hardware/Generation 2 Mining Hardware/Electrical/Control Board/docs/cc1b_072918.pdf

## Orchid Technologies Engineering & Consulting, Inc. - Confidential

# ORCHID TECHNOLOGIES

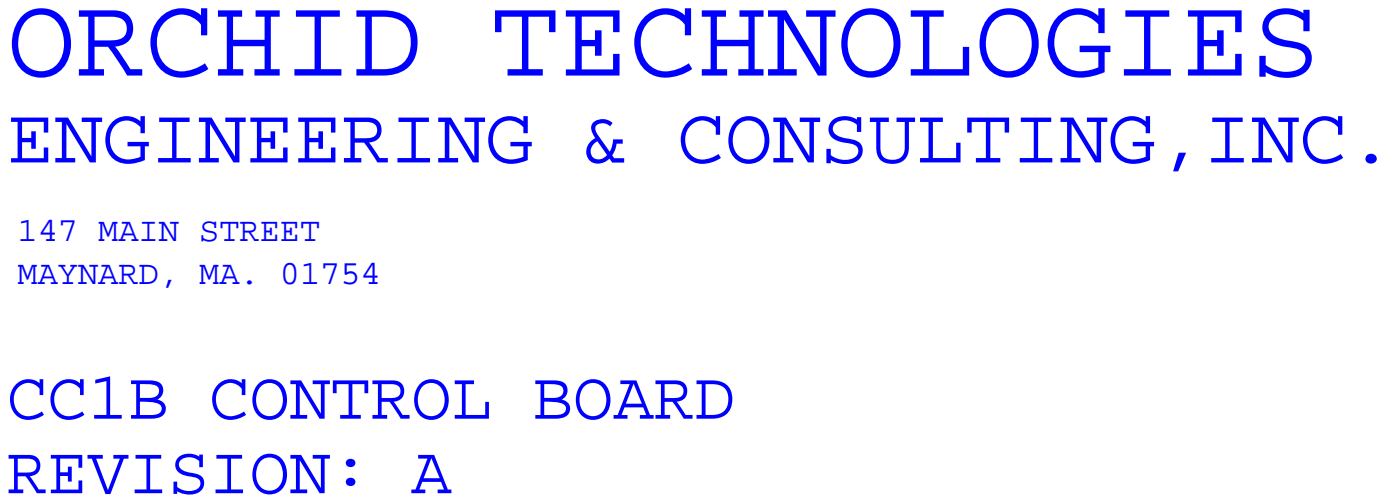
[picture p106: page 1]
REVISION: A; CC1B CONTROL BOARD; 147 MAIN STREET MAYNARD, MA. 01754; JULY 29, 2018; Size; Document Number; Rev; Date:; Sheet

ENGINEERING & CONSULTING,INC.

Orchid Technologies Engineering and Consulting, Inc.
Title
CC1B CONTROL BOARD

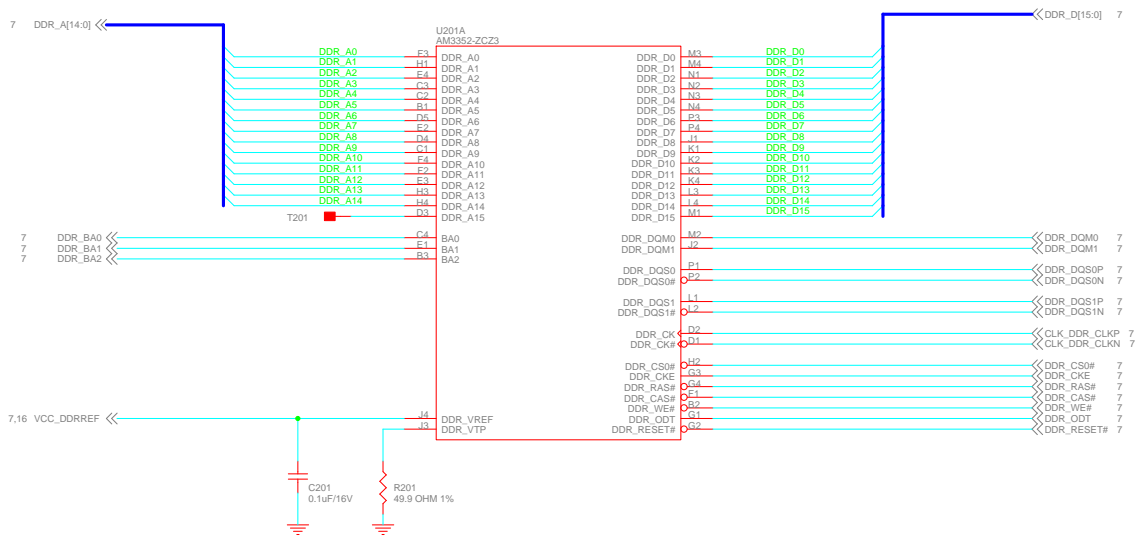
[picture p107: page 2]

Orchid Technologies Engineering and Consulting, Inc.

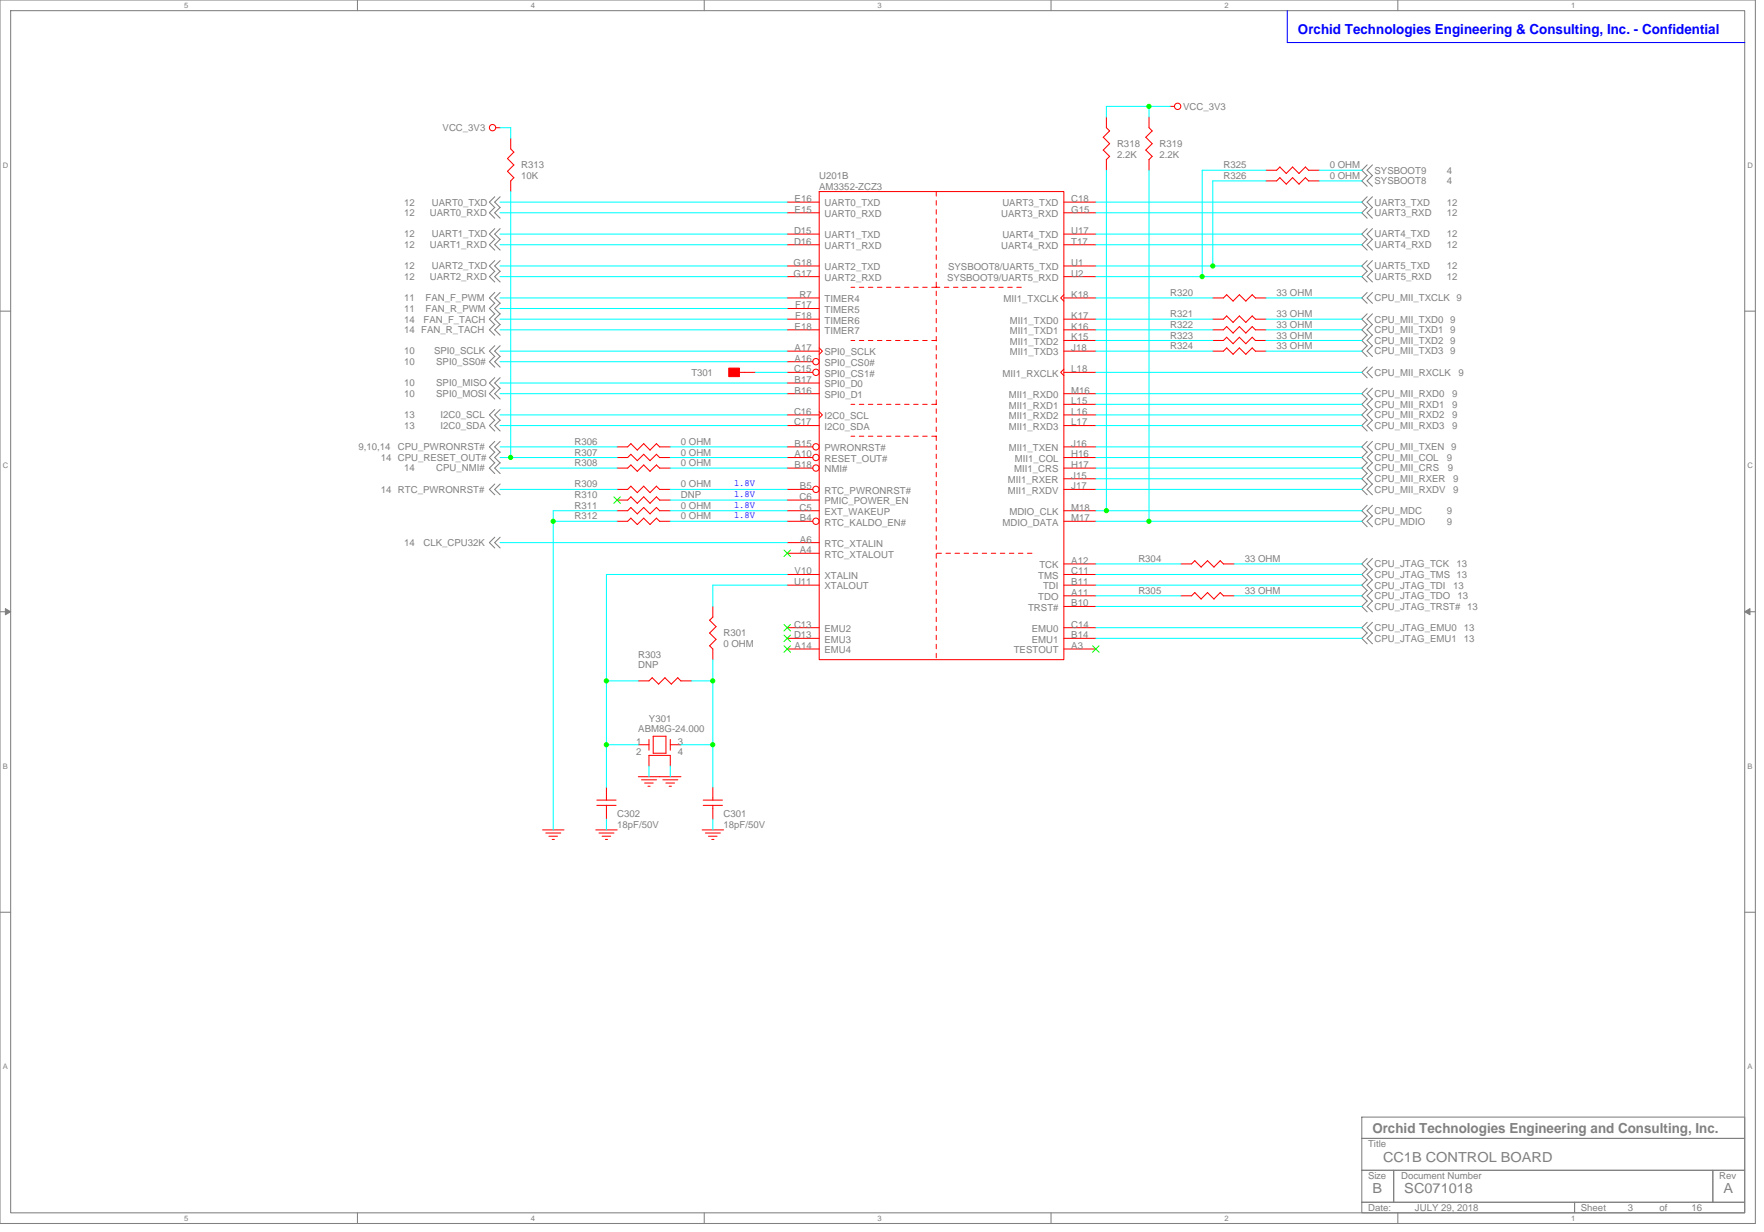
[picture p108: page 3]

Orchid Technologies Engineering and Consulting, Inc.

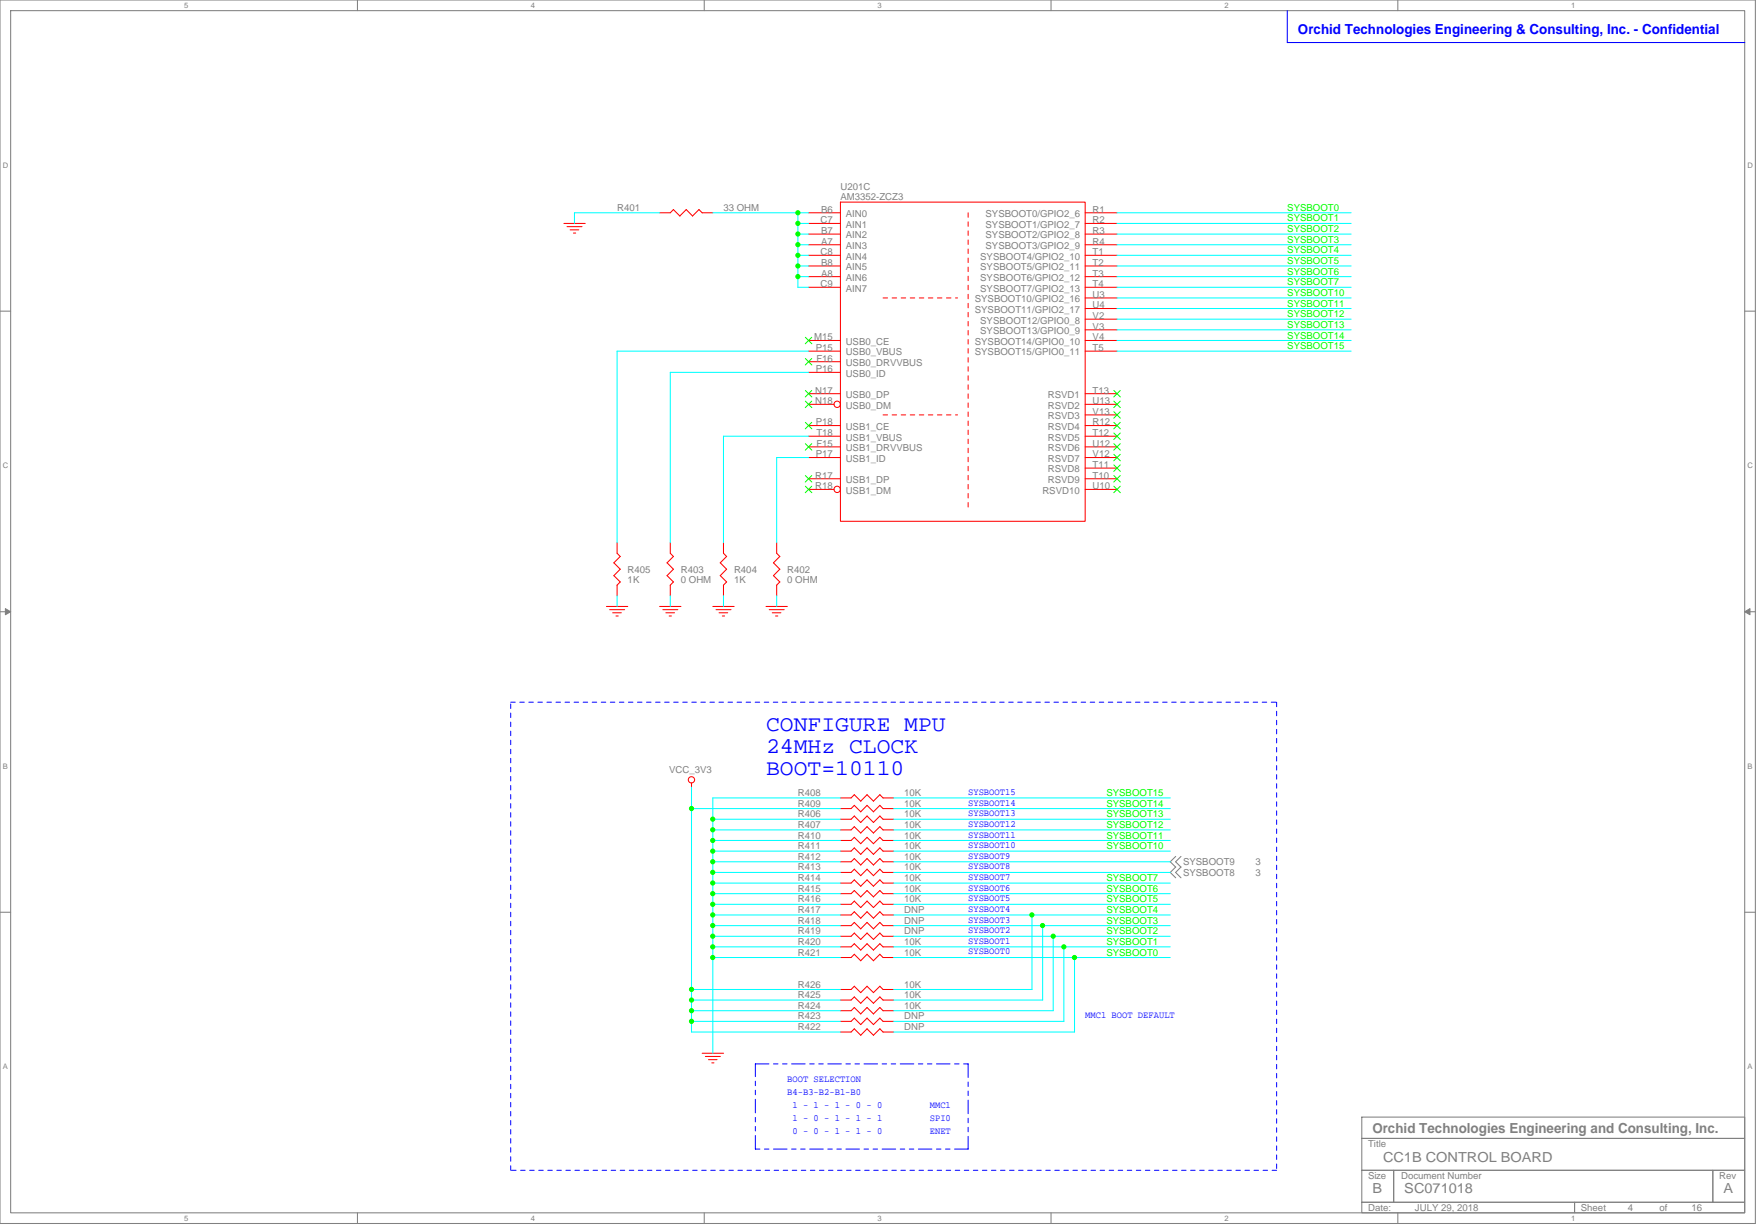
[picture p109: page 4]

Orchid Technologies Engineering and Consulting, Inc.

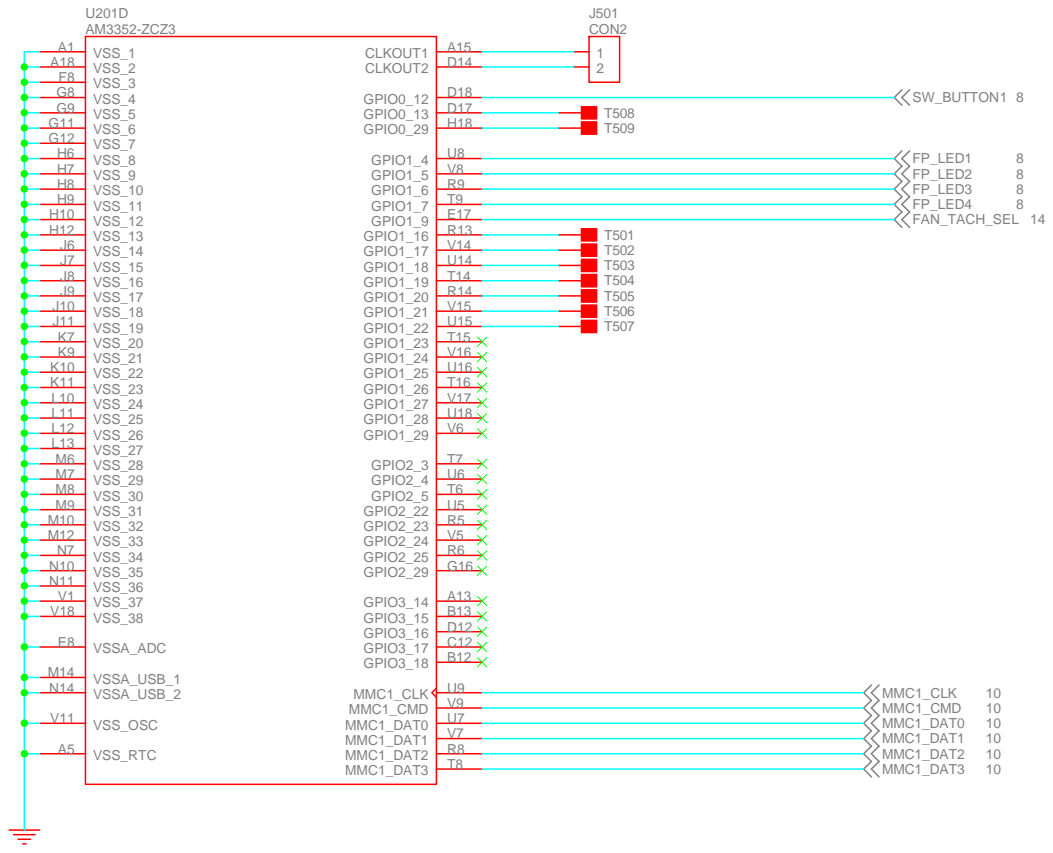
[picture p110: page 5]

Orchid Technologies Engineering and Consulting, Inc.

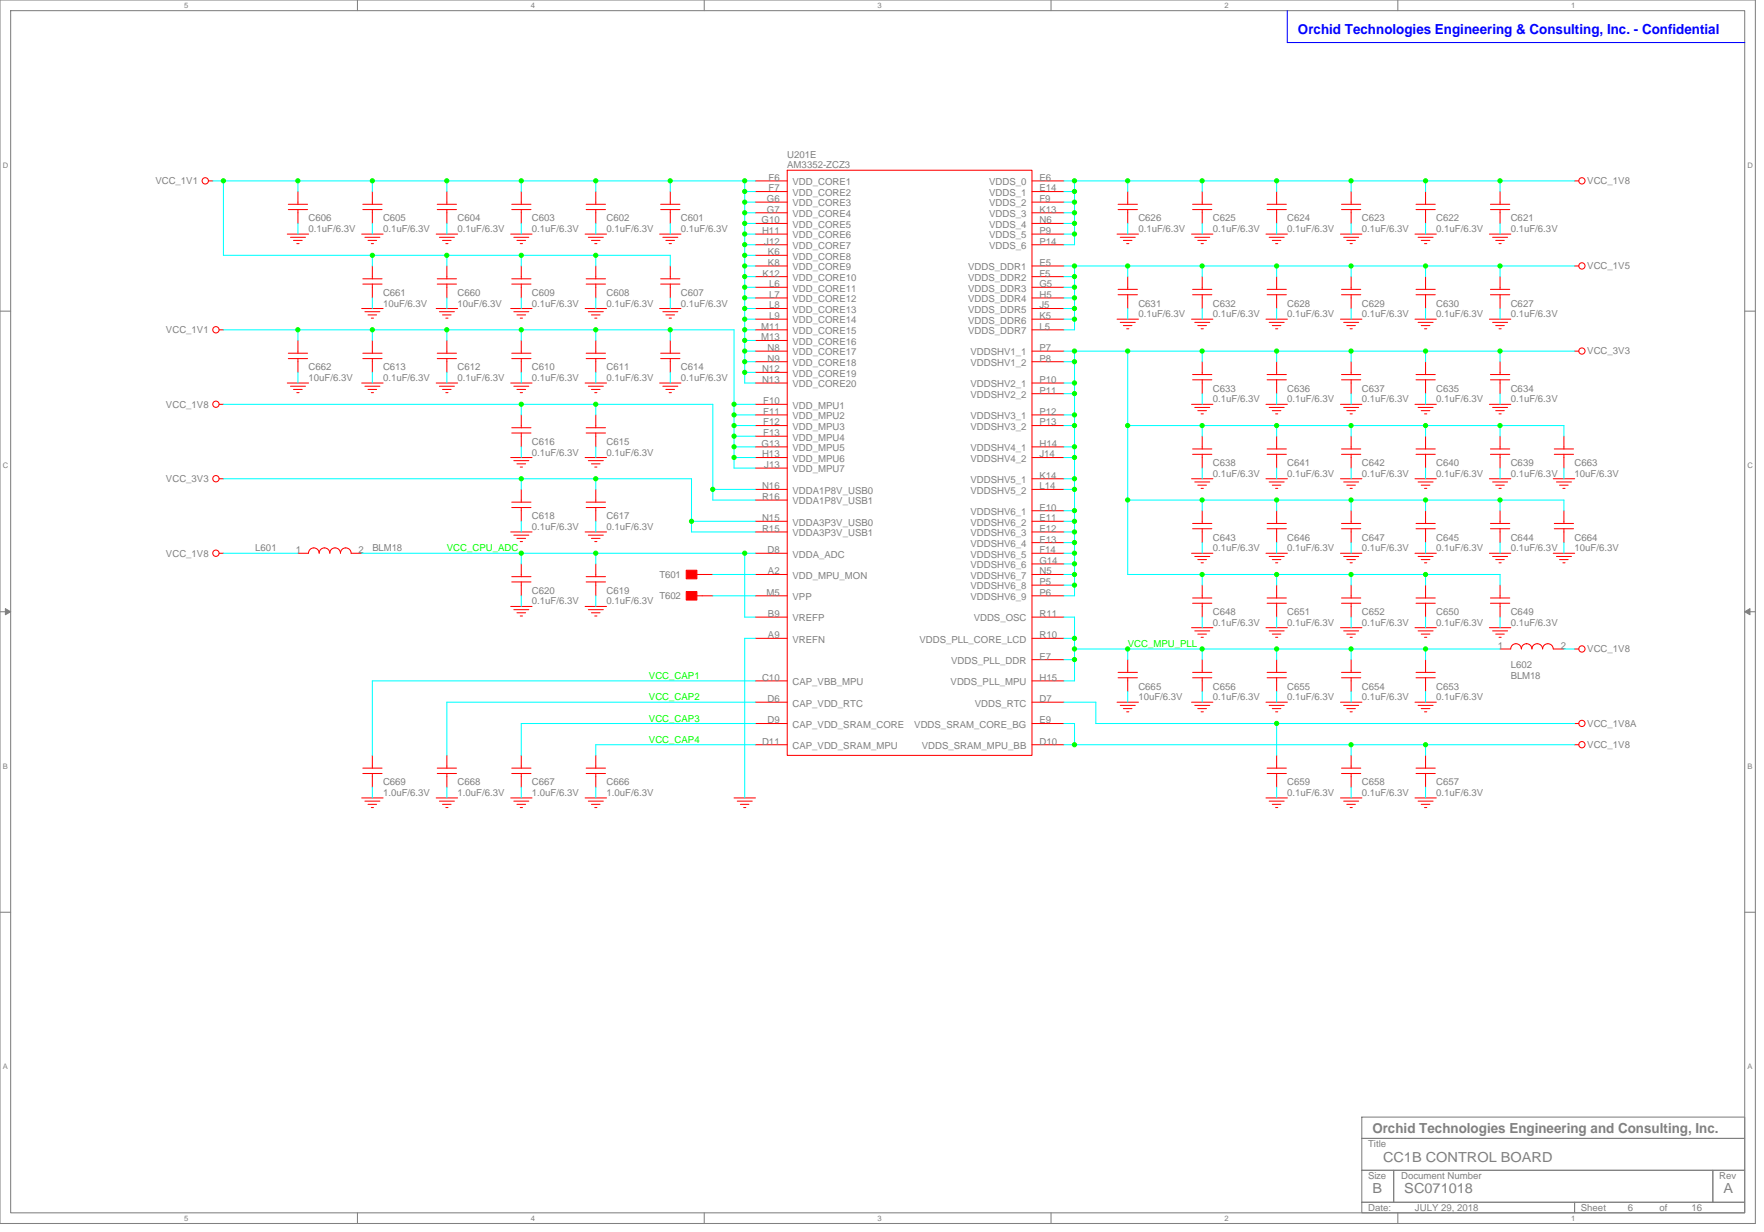
[picture p111: page 6]

Orchid Technologies Engineering and Consulting, Inc.

# MEMORY SIZE = 128M BYTE

# DDR3

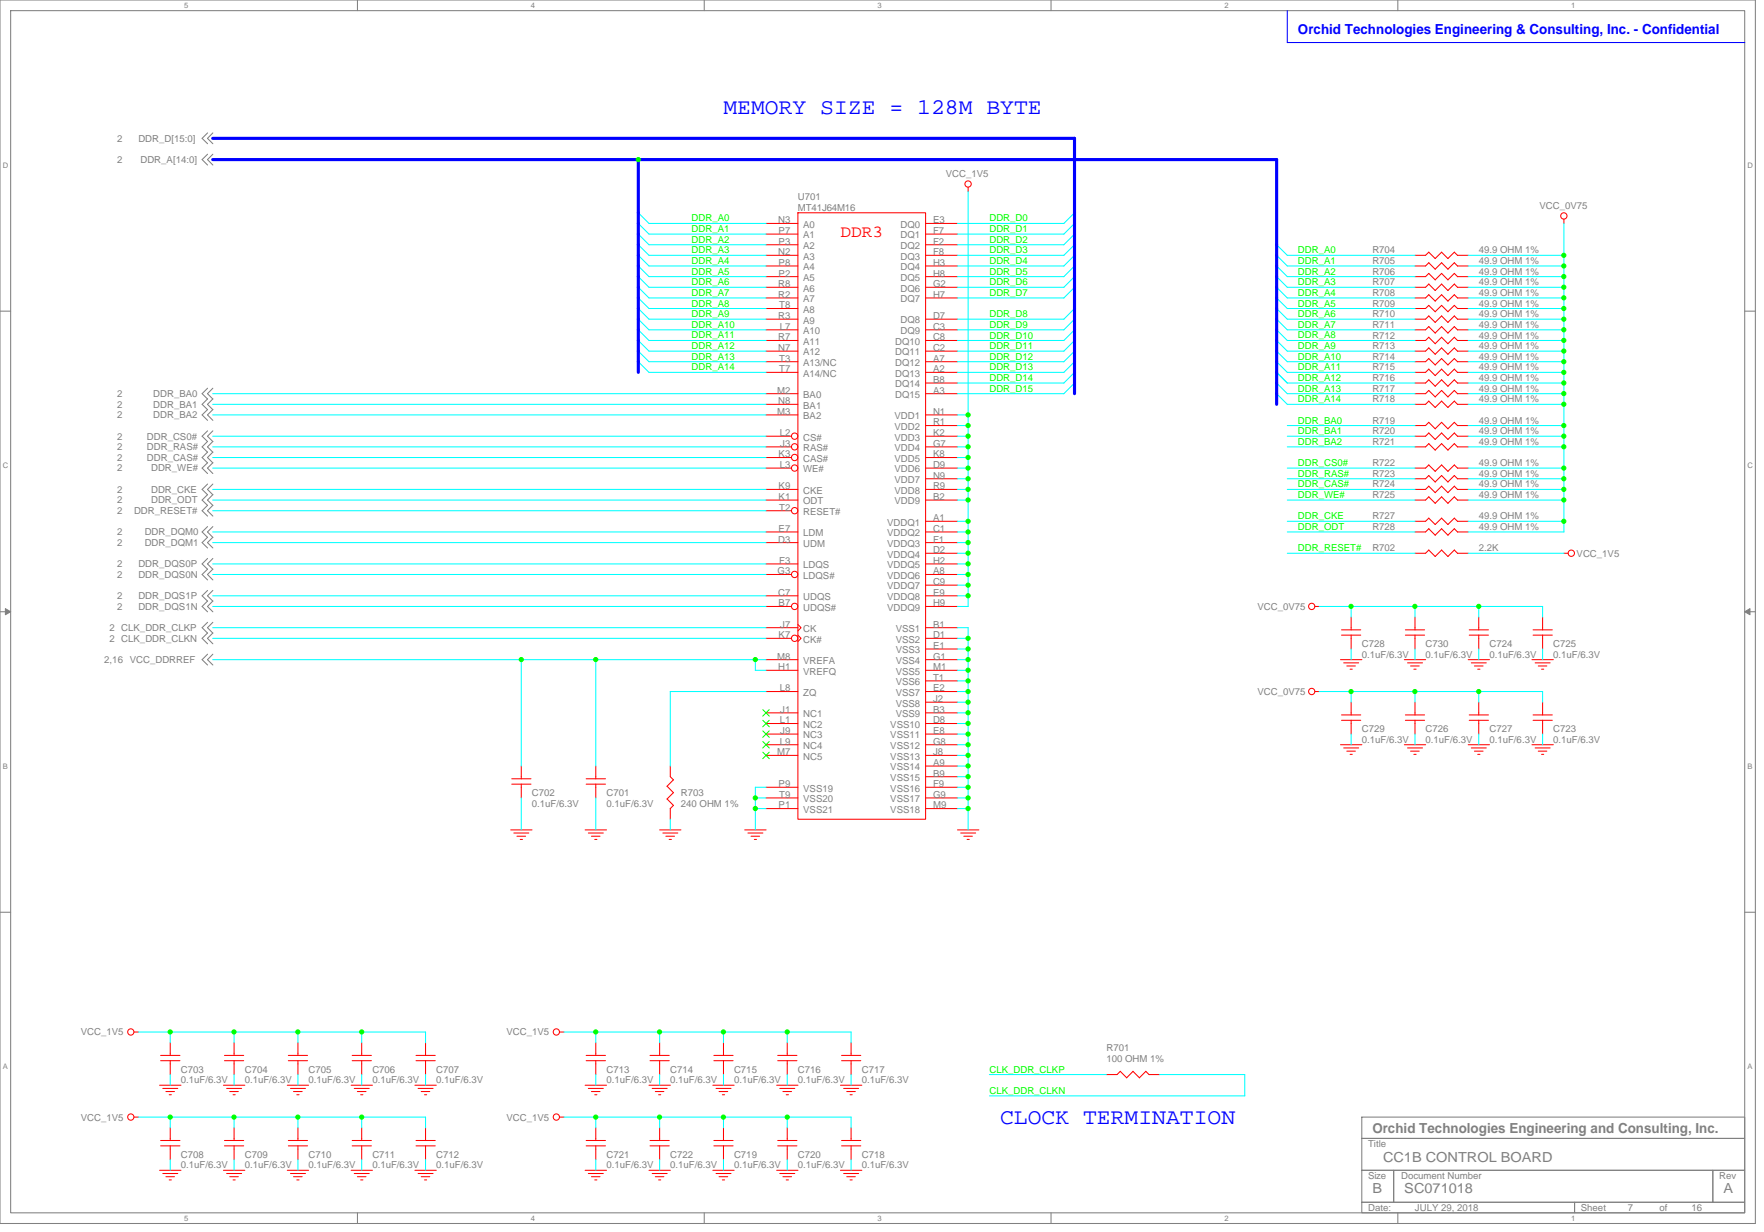
[picture p112: page 7]

Orchid Technologies Engineering and Consulting, Inc.

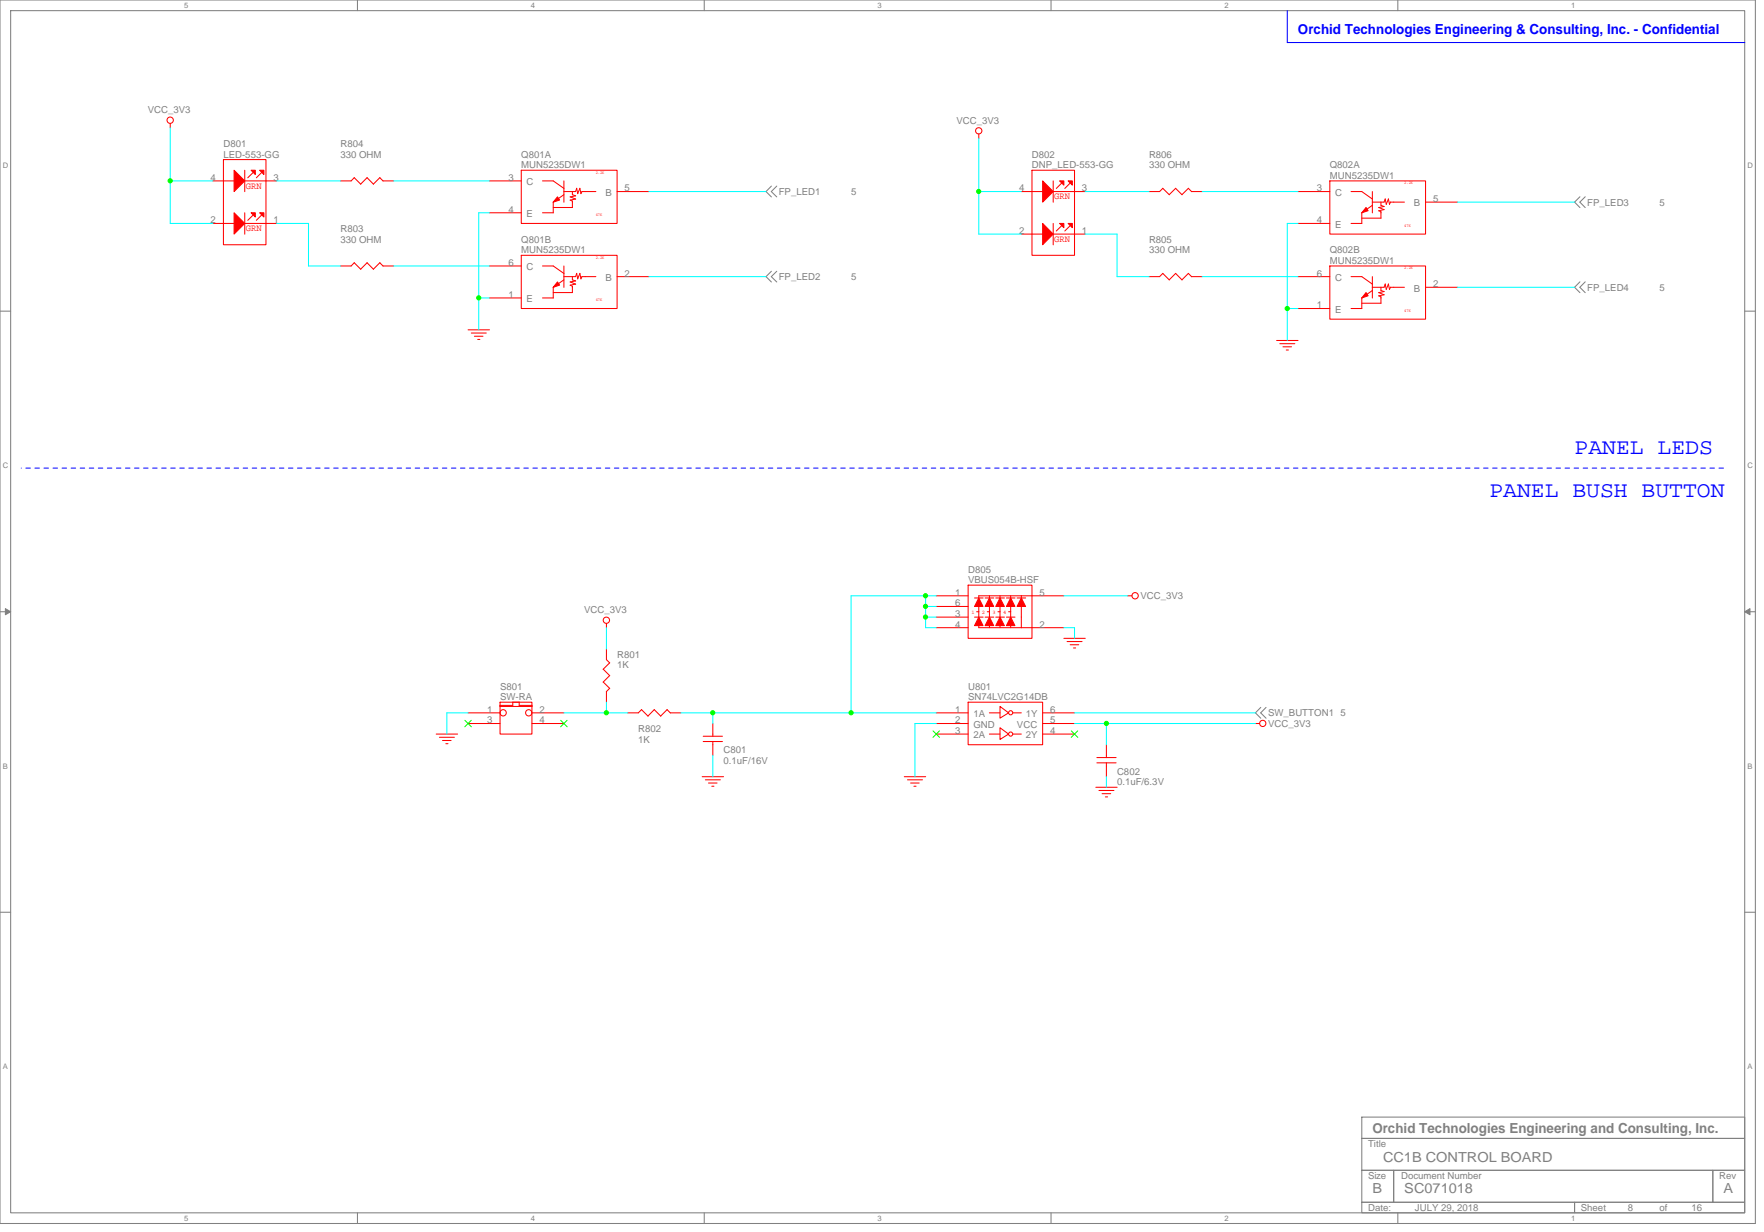
[picture p113: page 8]

Orchid Technologies Engineering and Consulting, Inc.

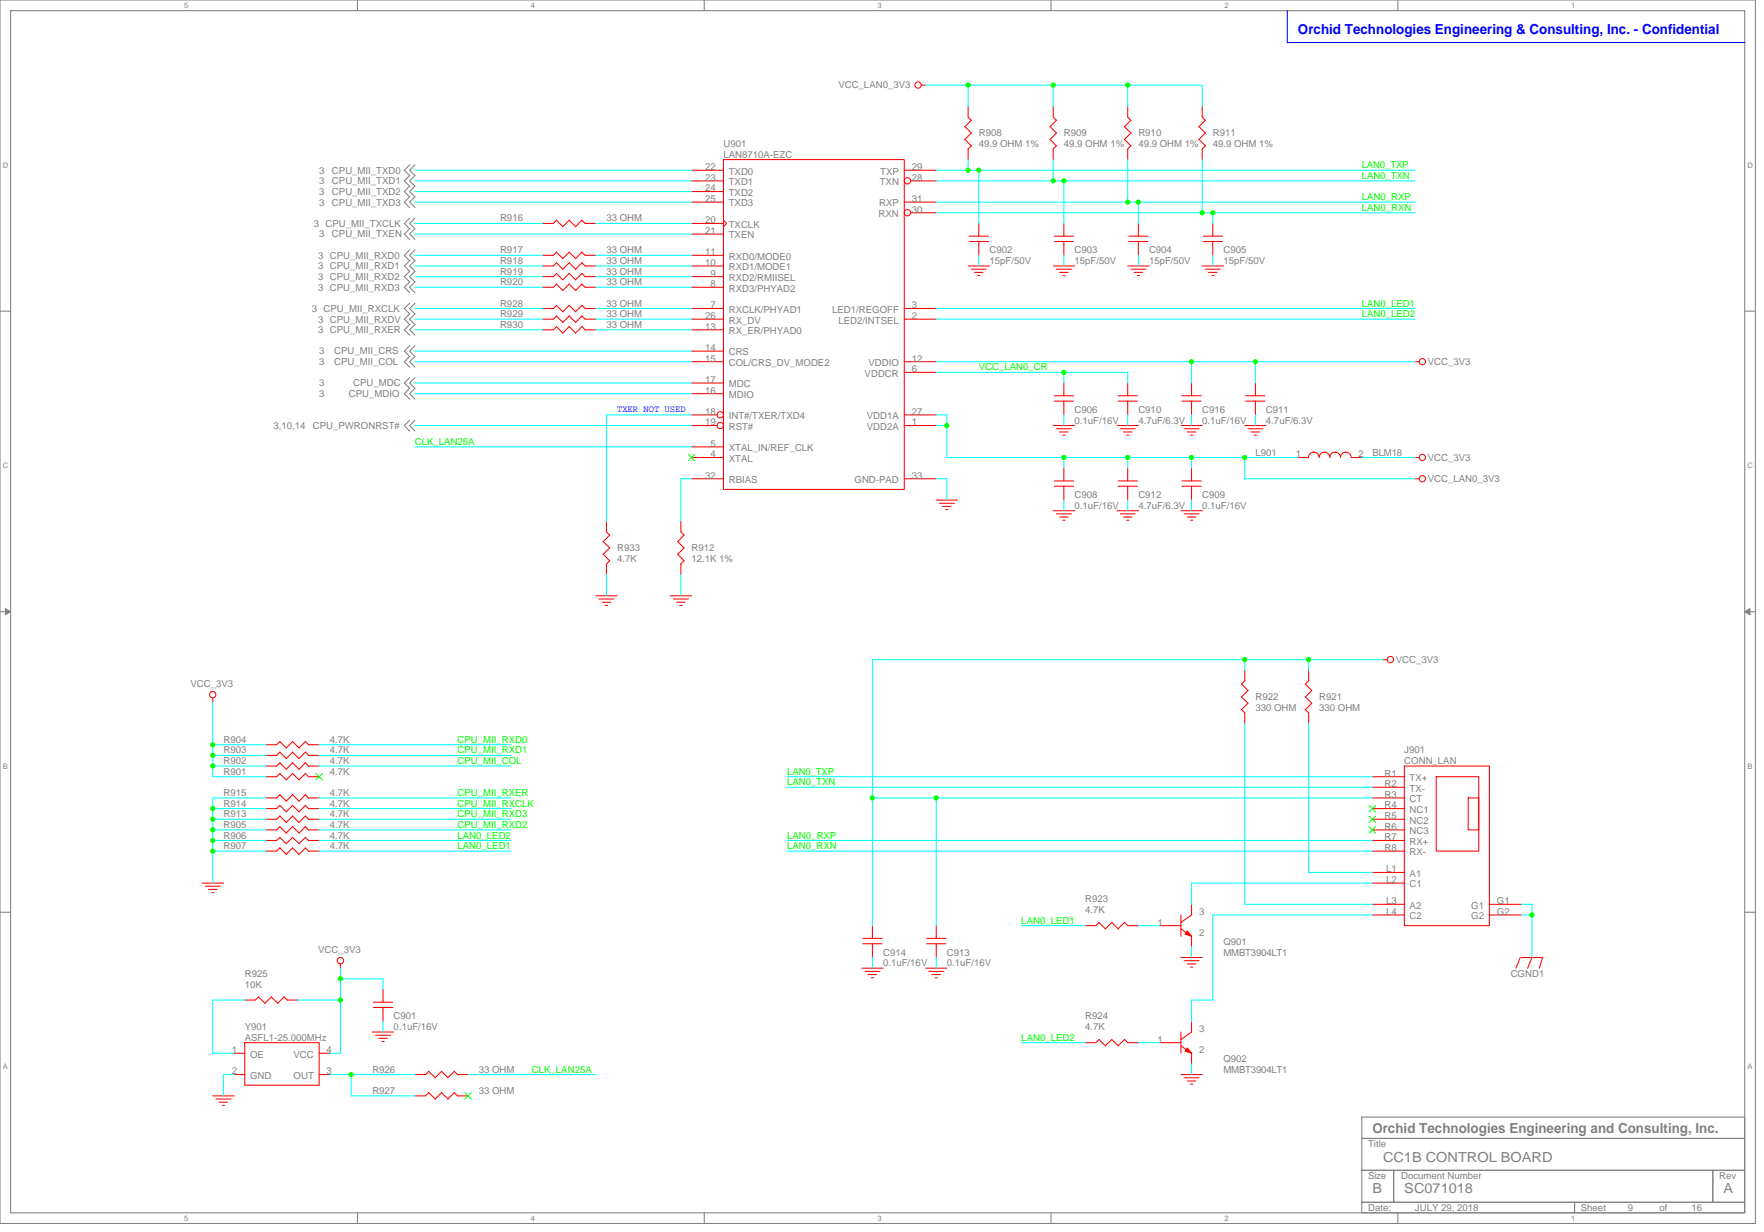
[picture p114: page 9]

Orchid Technologies Engineering and Consulting, Inc.

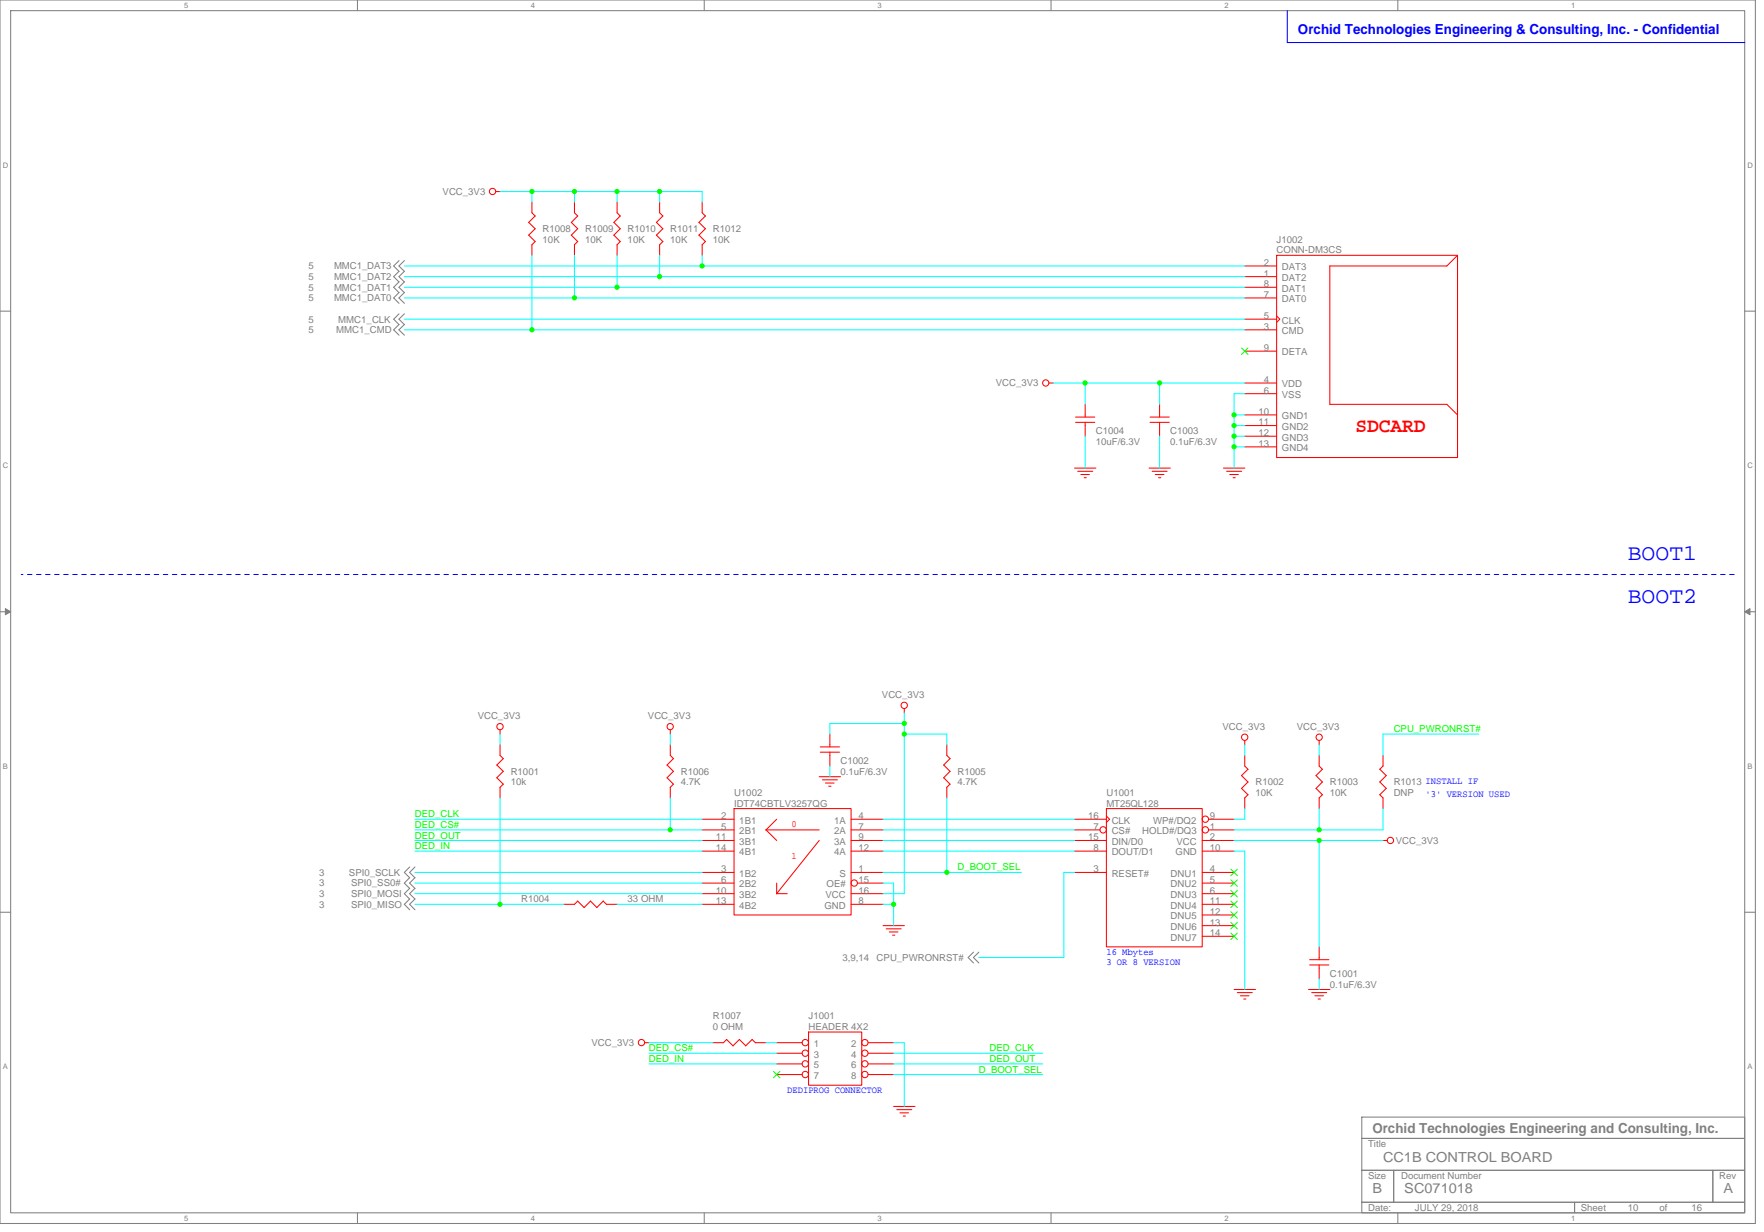
[picture p115: page 10]

Orchid Technologies Engineering and Consulting, Inc.

# FAN / TACH 1

# FRONT FAN

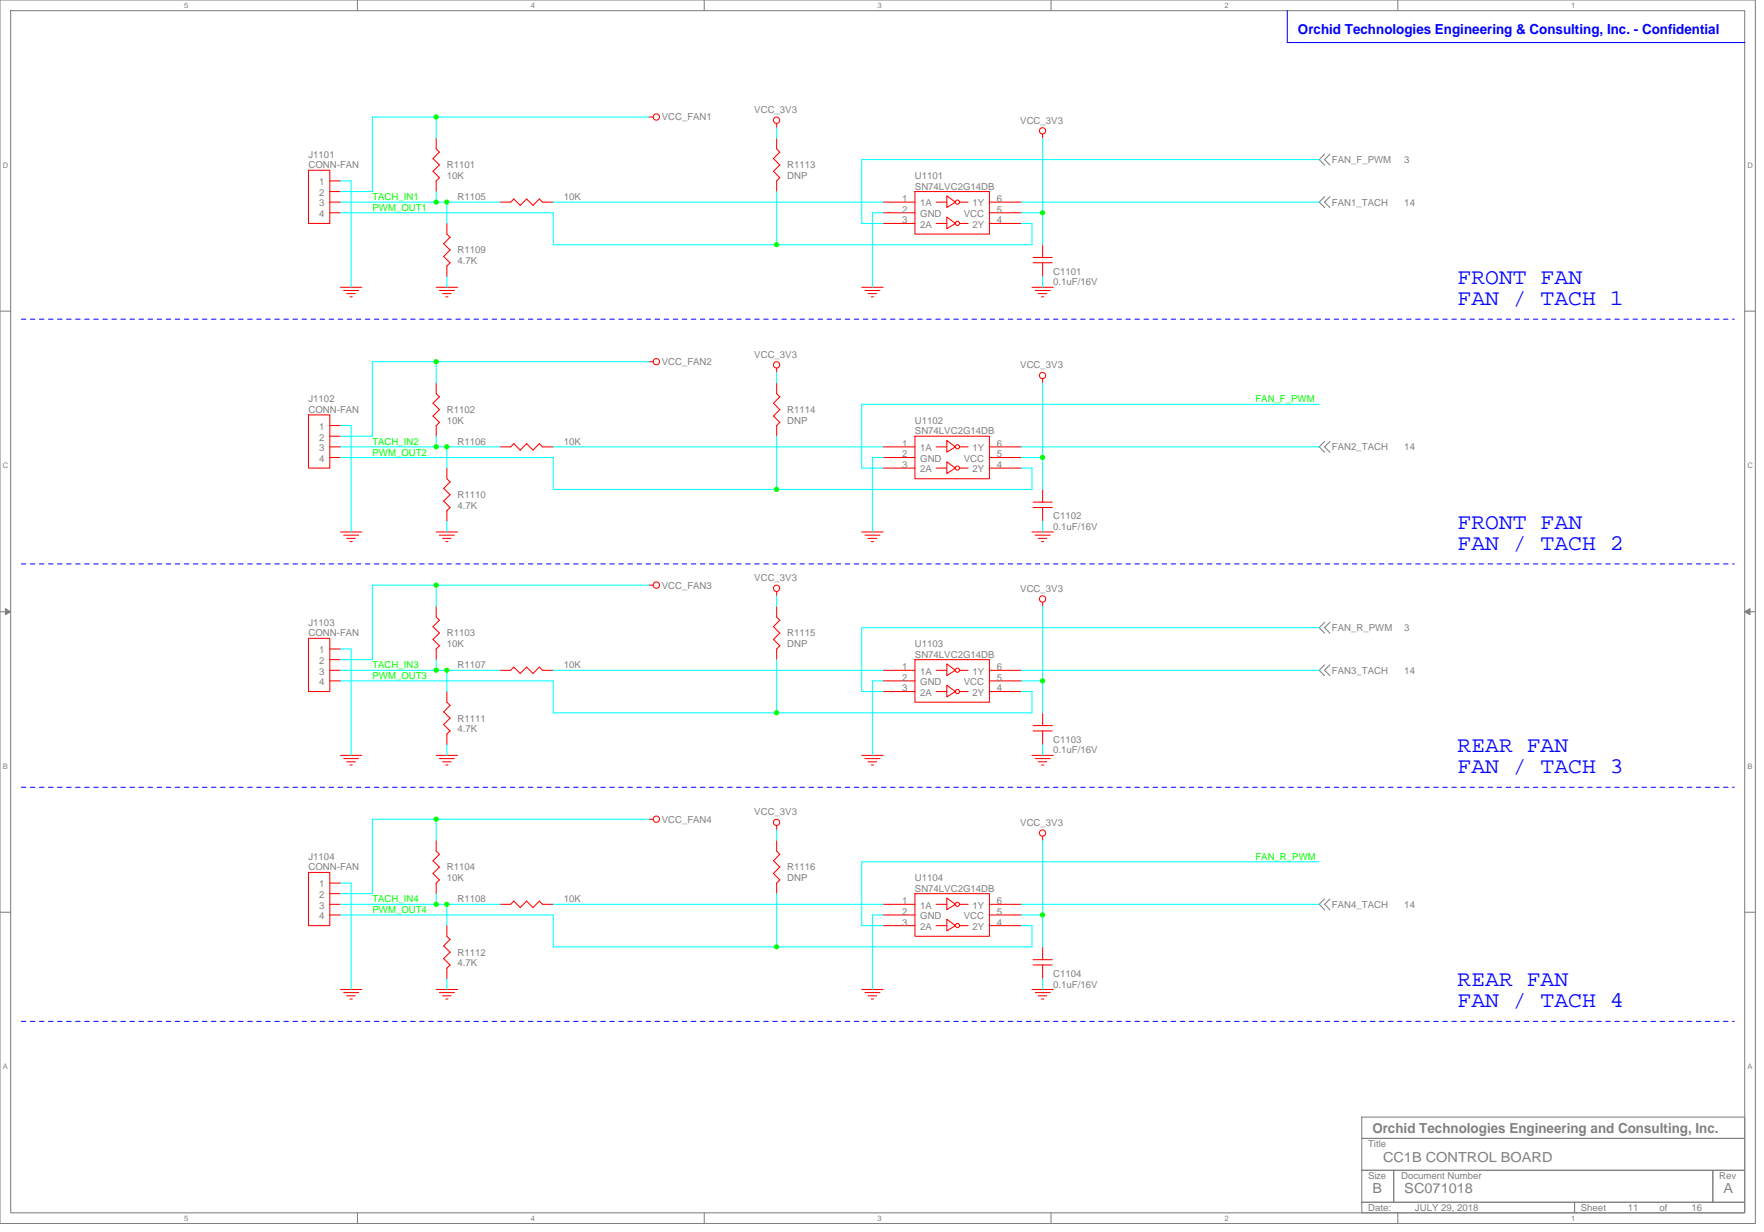
[picture p116: page 11]

Orchid Technologies Engineering and Consulting, Inc.

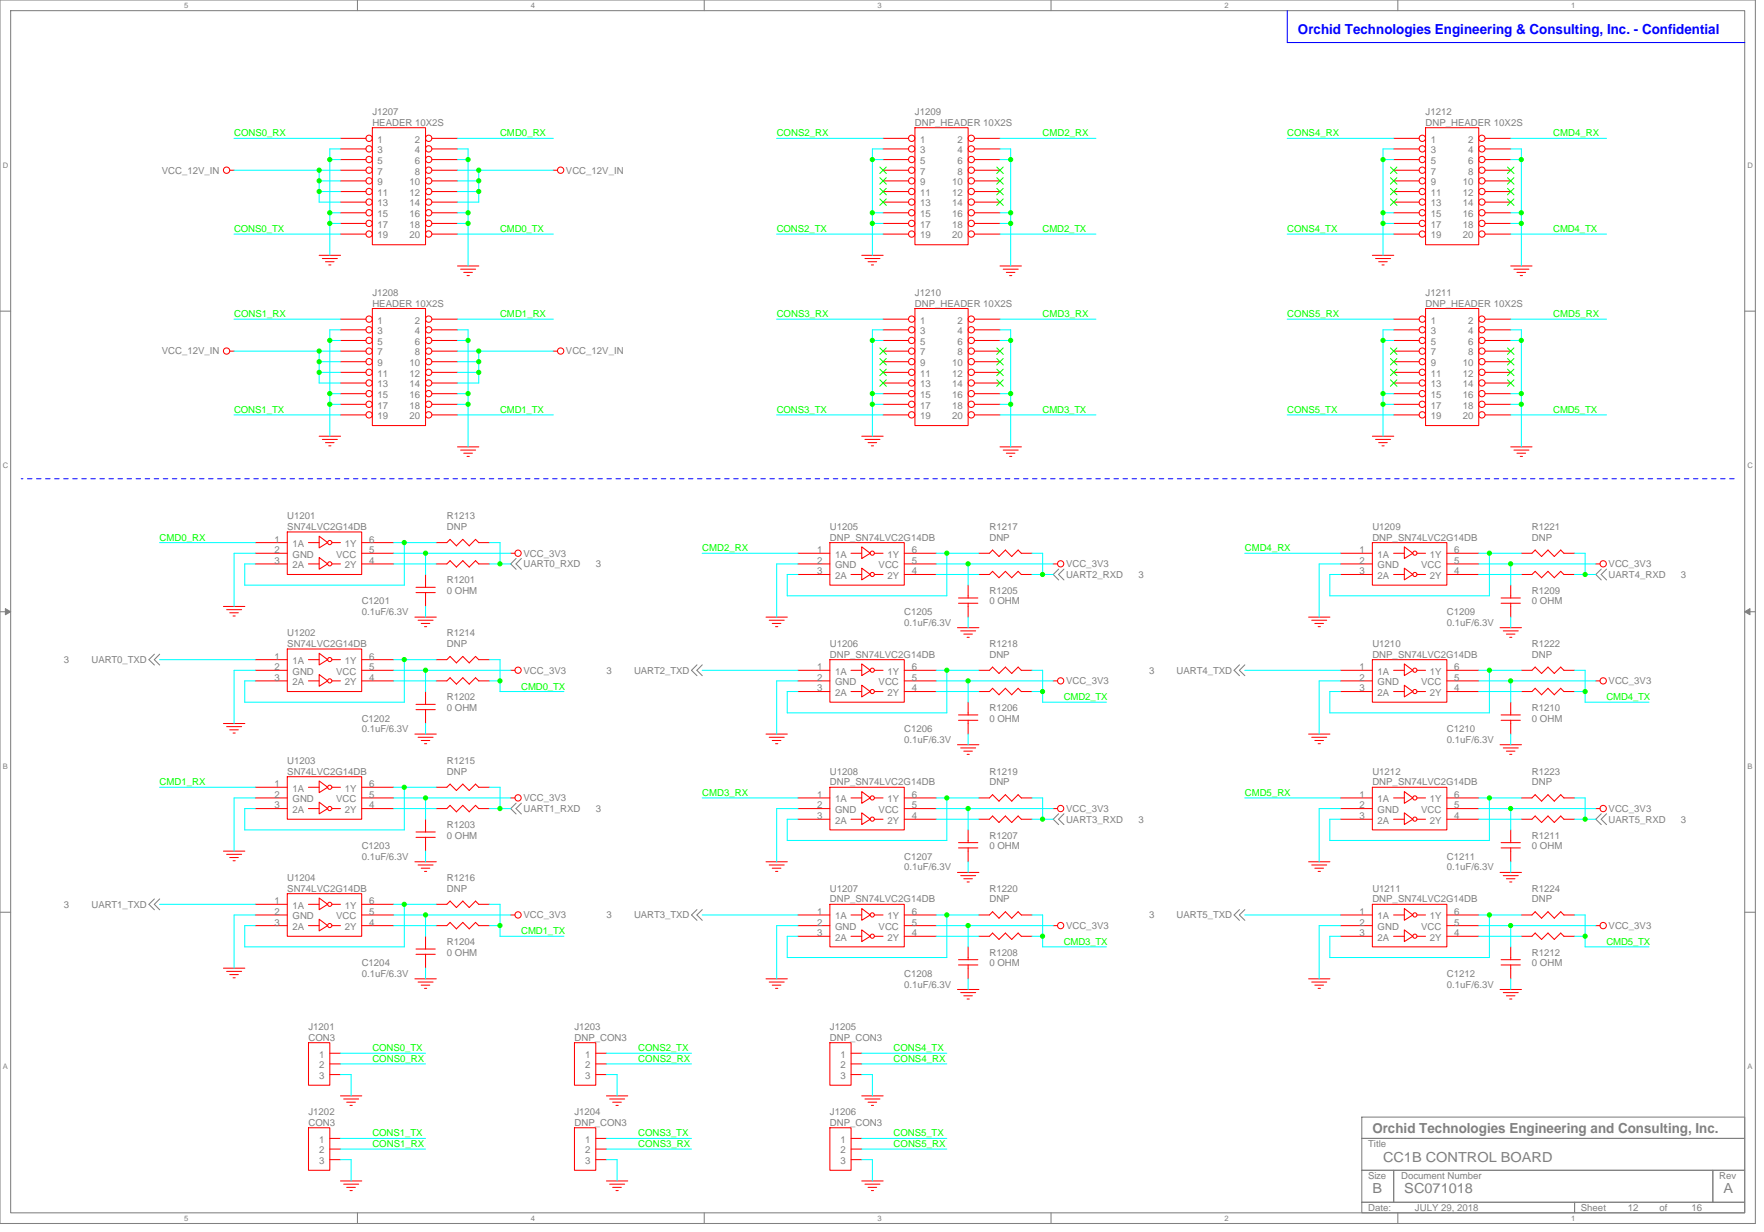
[picture p117: page 12]

Orchid Technologies Engineering and Consulting, Inc.

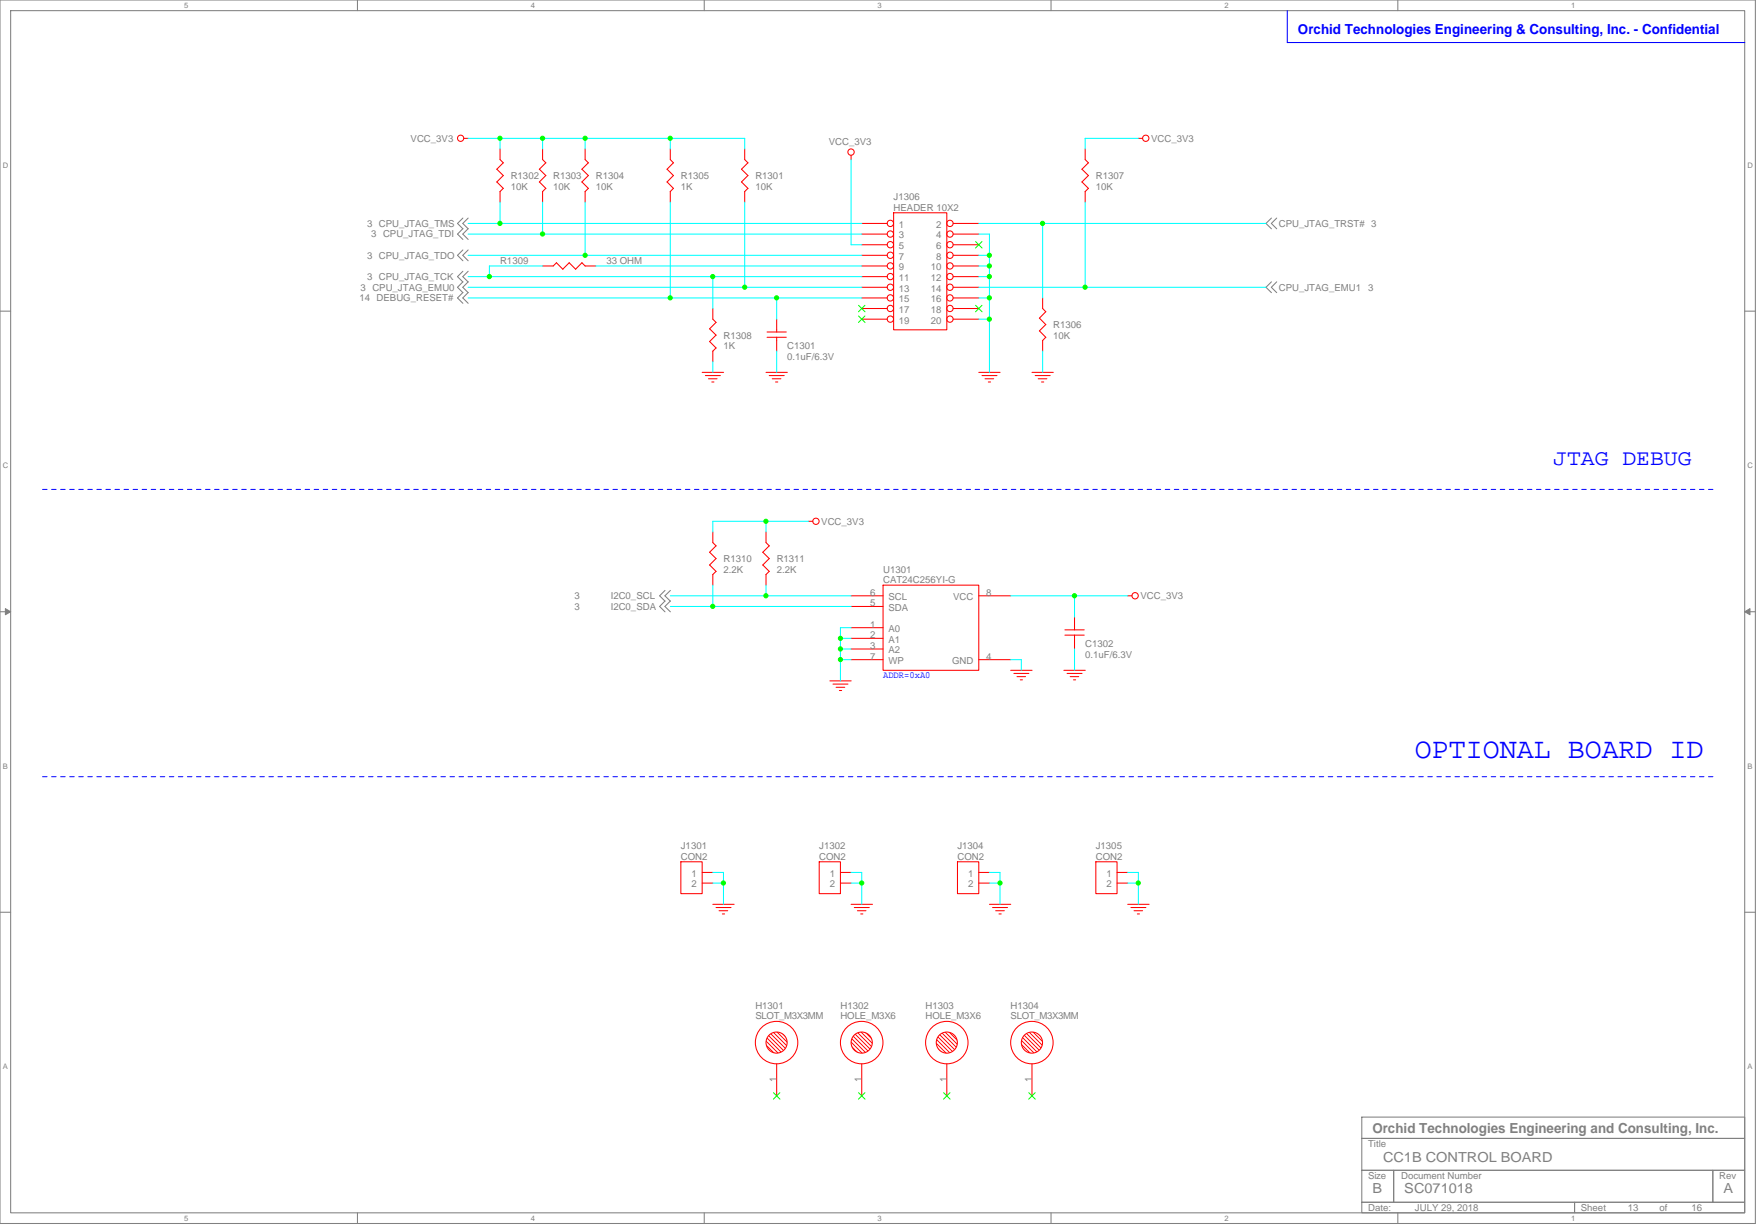
[picture p118: page 13]

Orchid Technologies Engineering and Consulting, Inc.

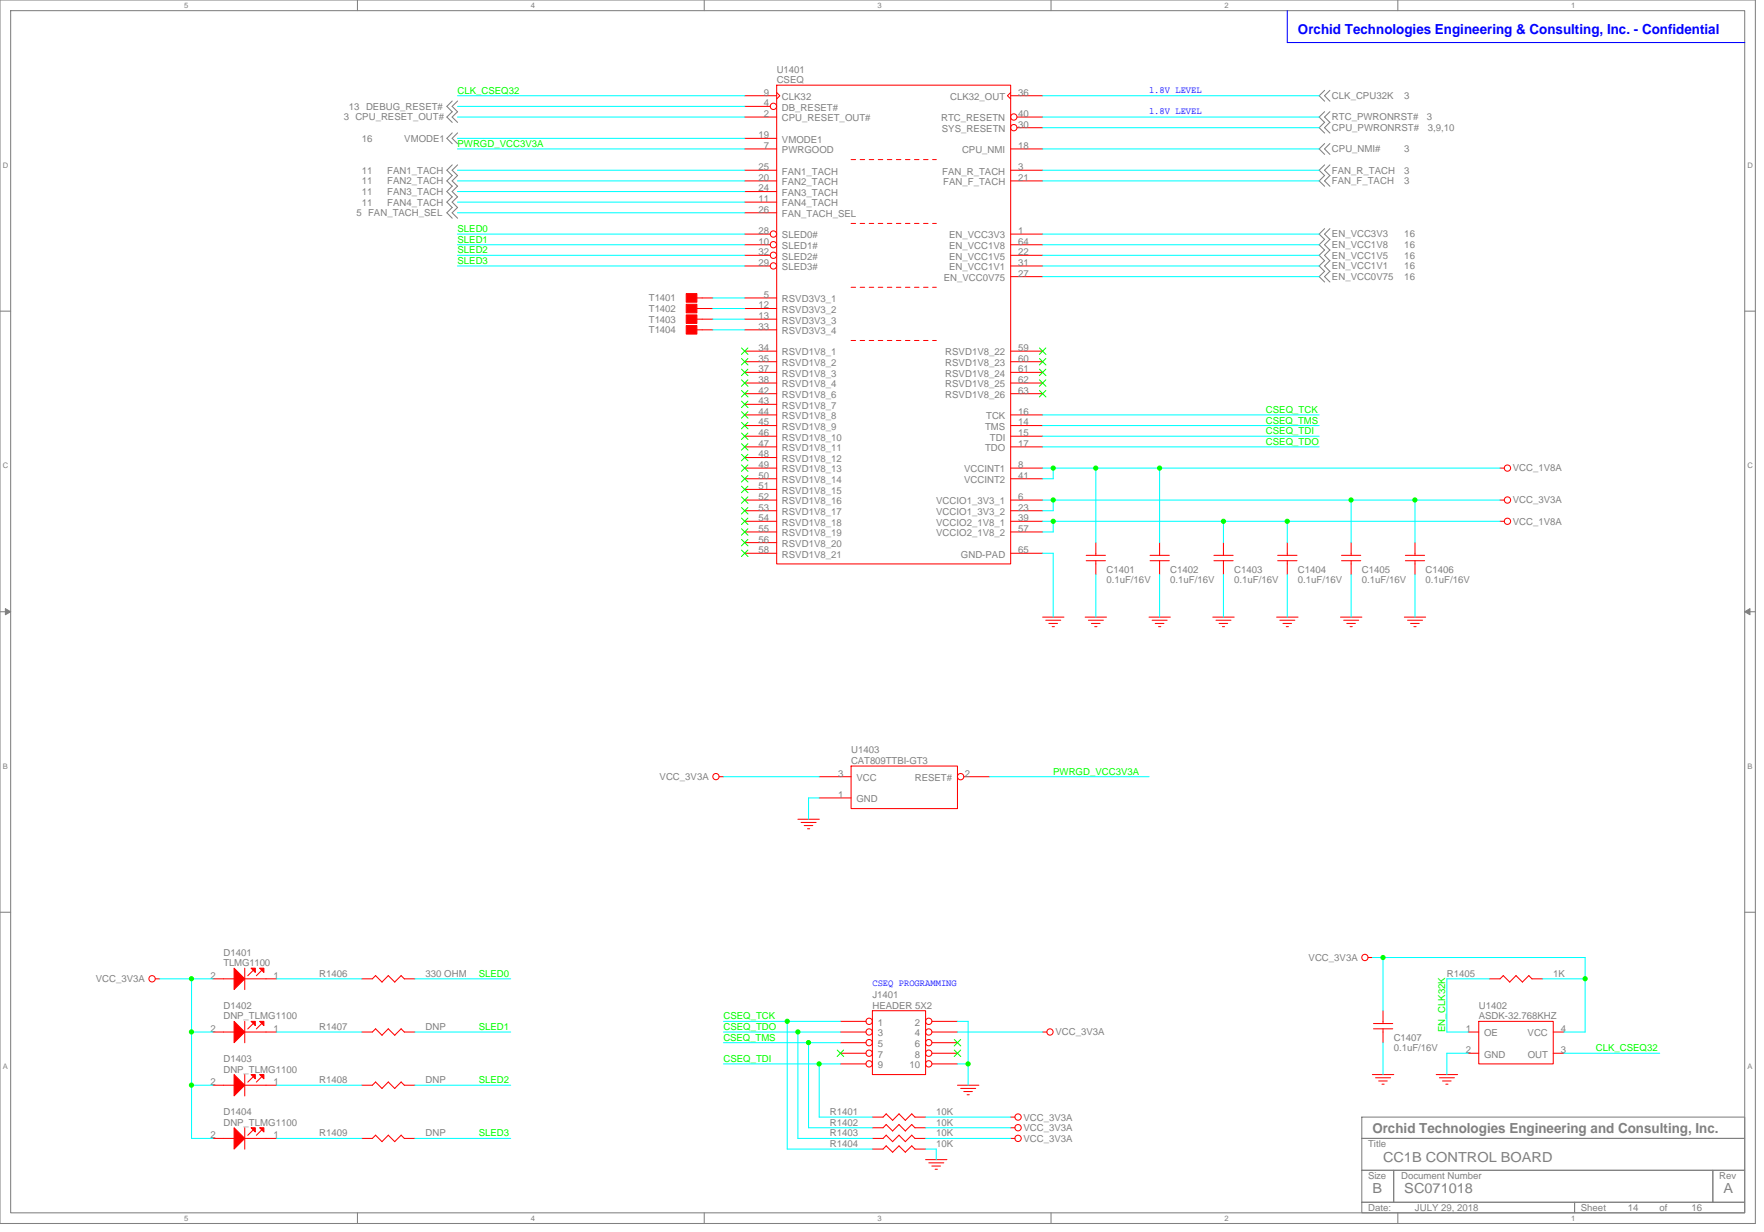
[picture p119: page 14]

Orchid Technologies Engineering and Consulting, Inc.

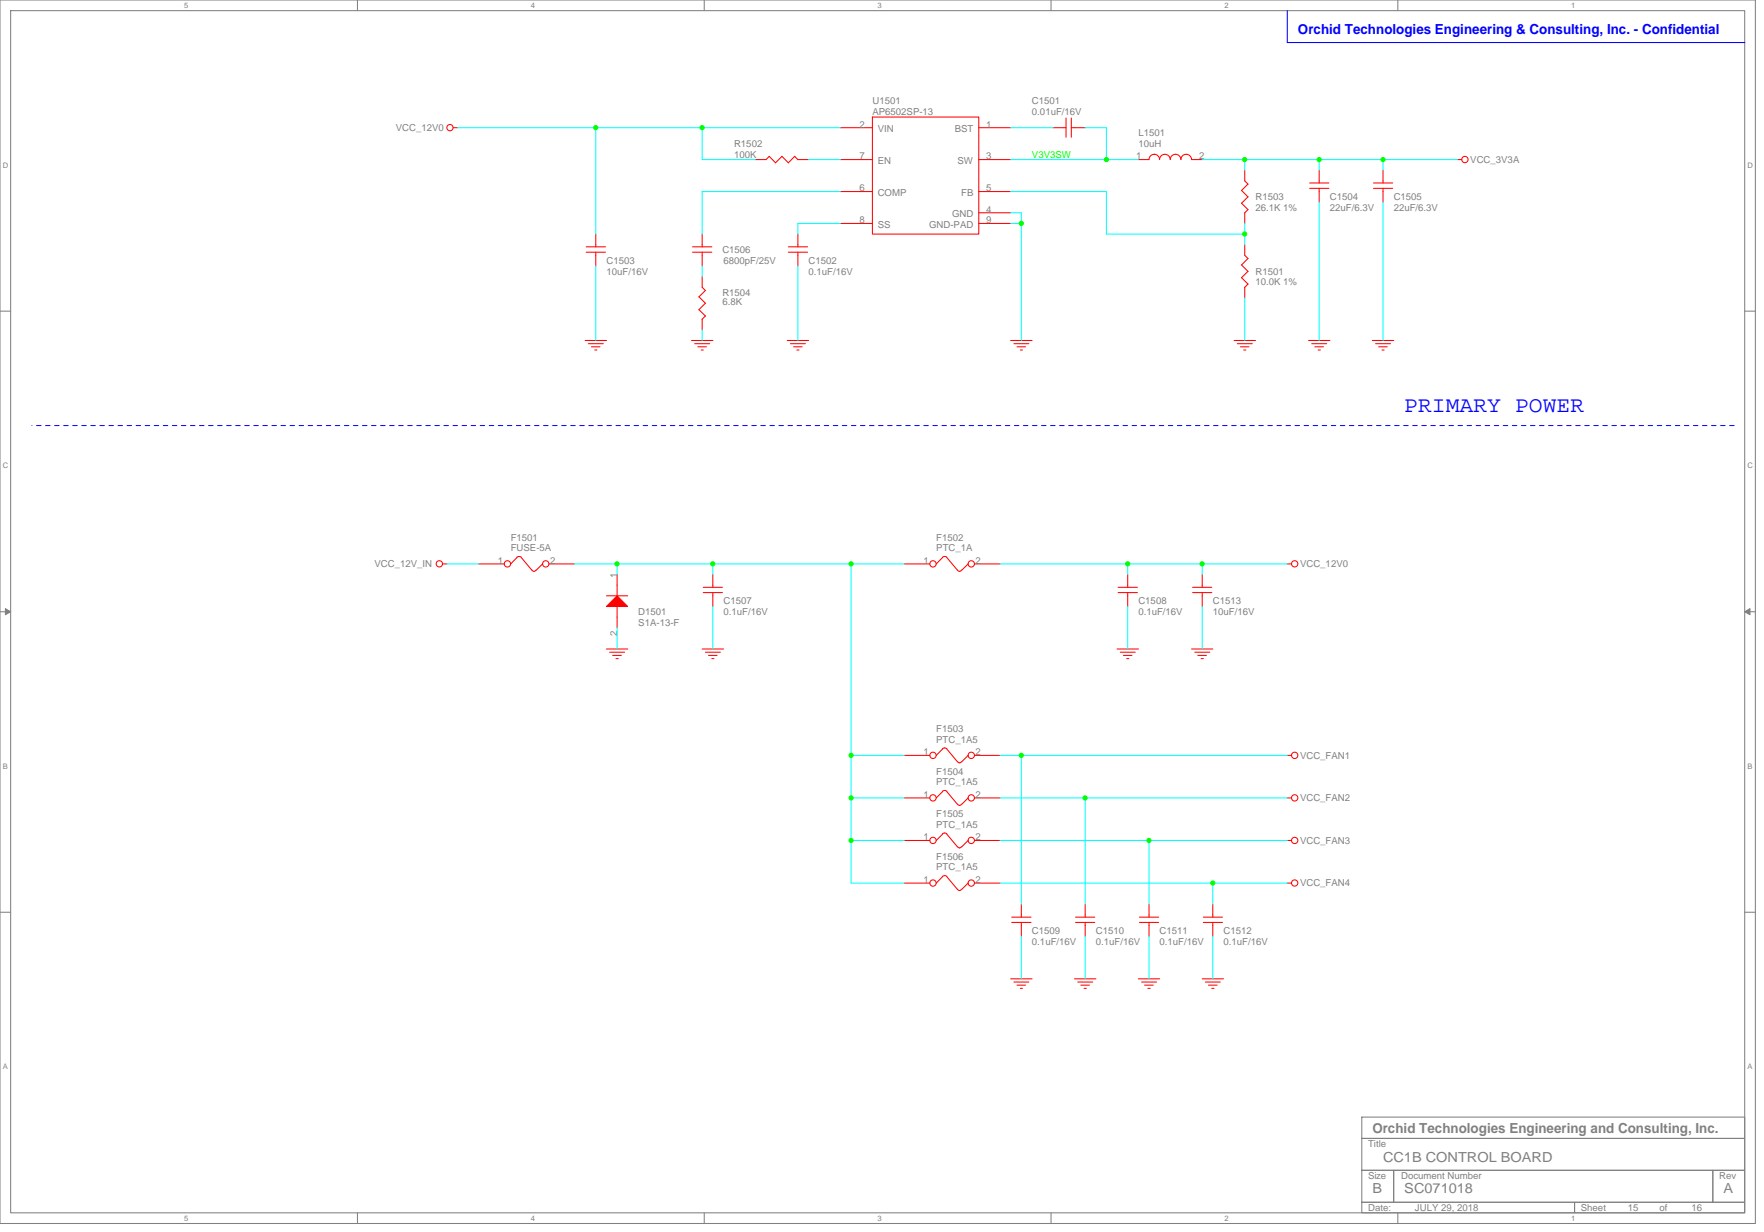
[picture p120: page 15]

Orchid Technologies Engineering and Consulting, Inc.

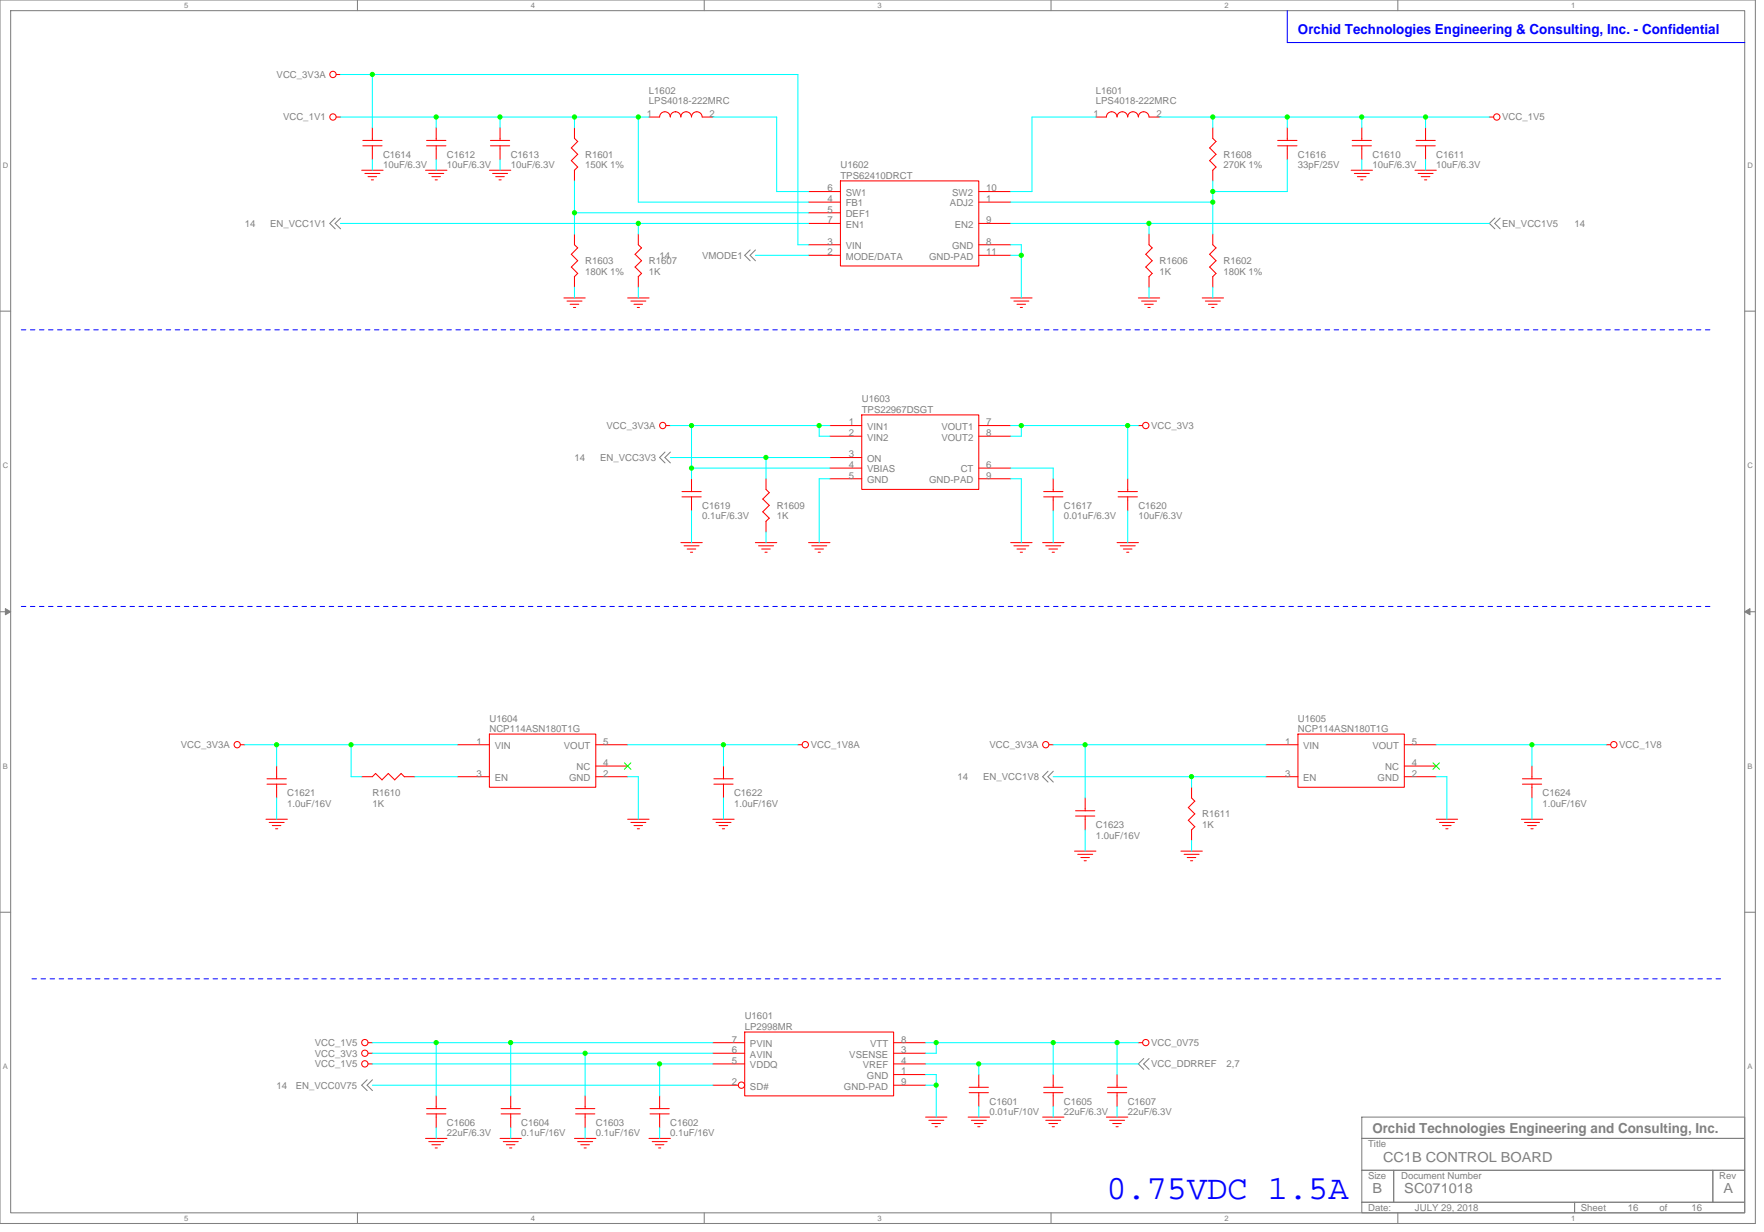
[picture p121: page 16]

Orchid Technologies Engineering and Consulting, Inc.
