ObeliskInc/obelisk-hardware/Generation 1 Mining Hardware/Electrical/Control Board/SOMController742905RApcb.pdf

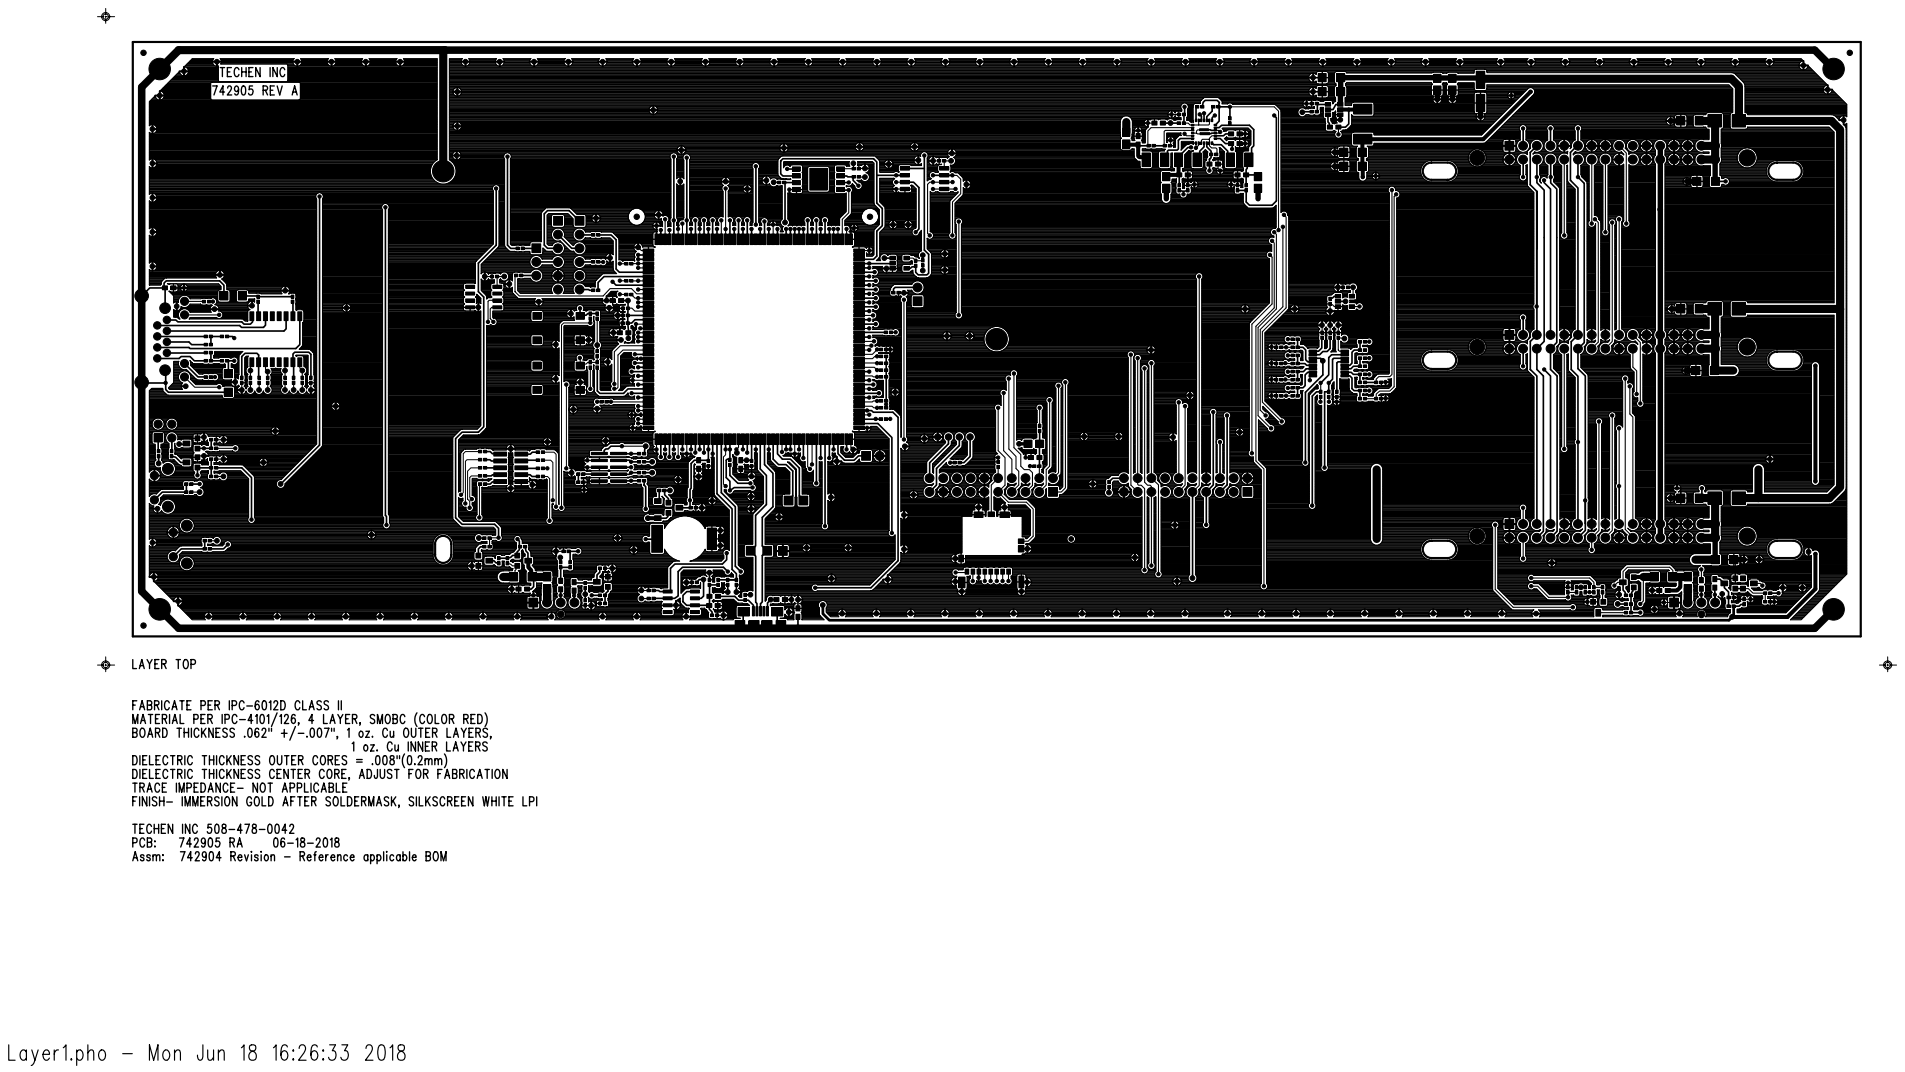
[picture p123: page 1]

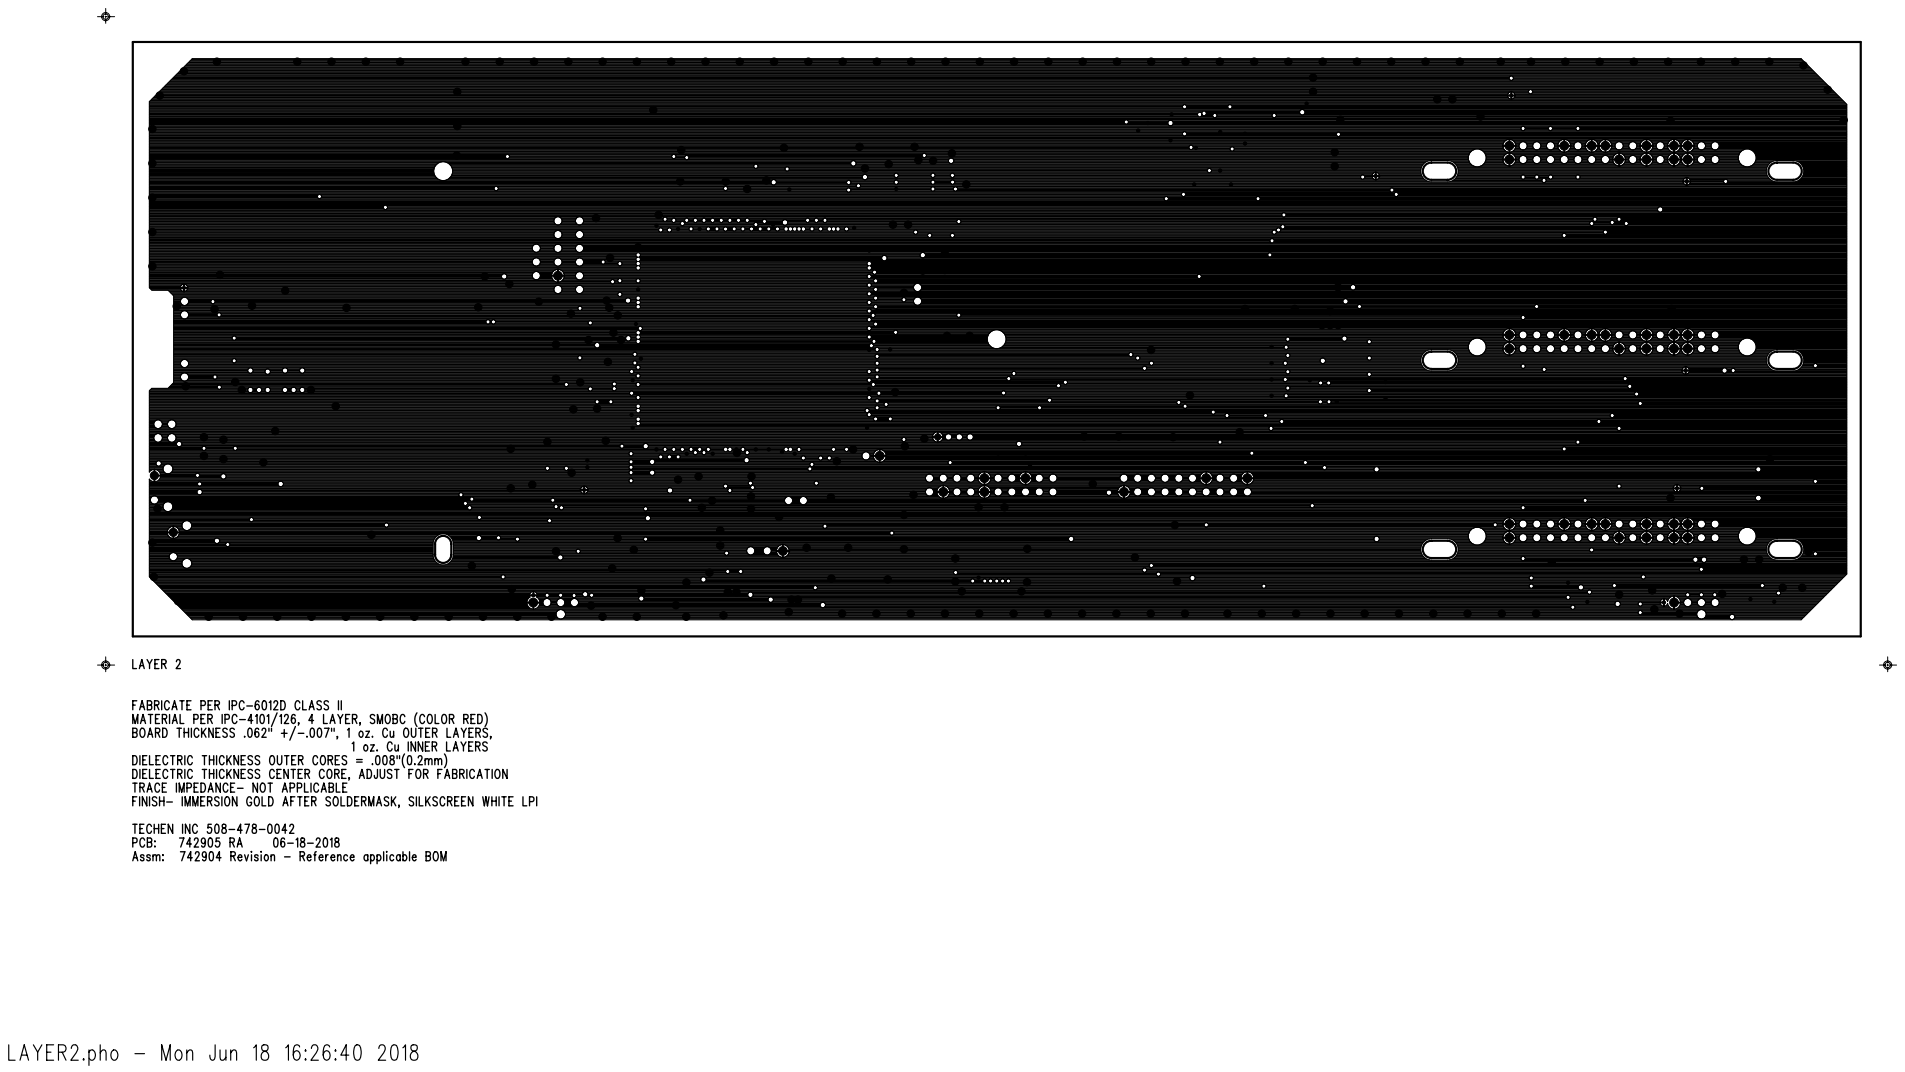
[picture p124: page 2]

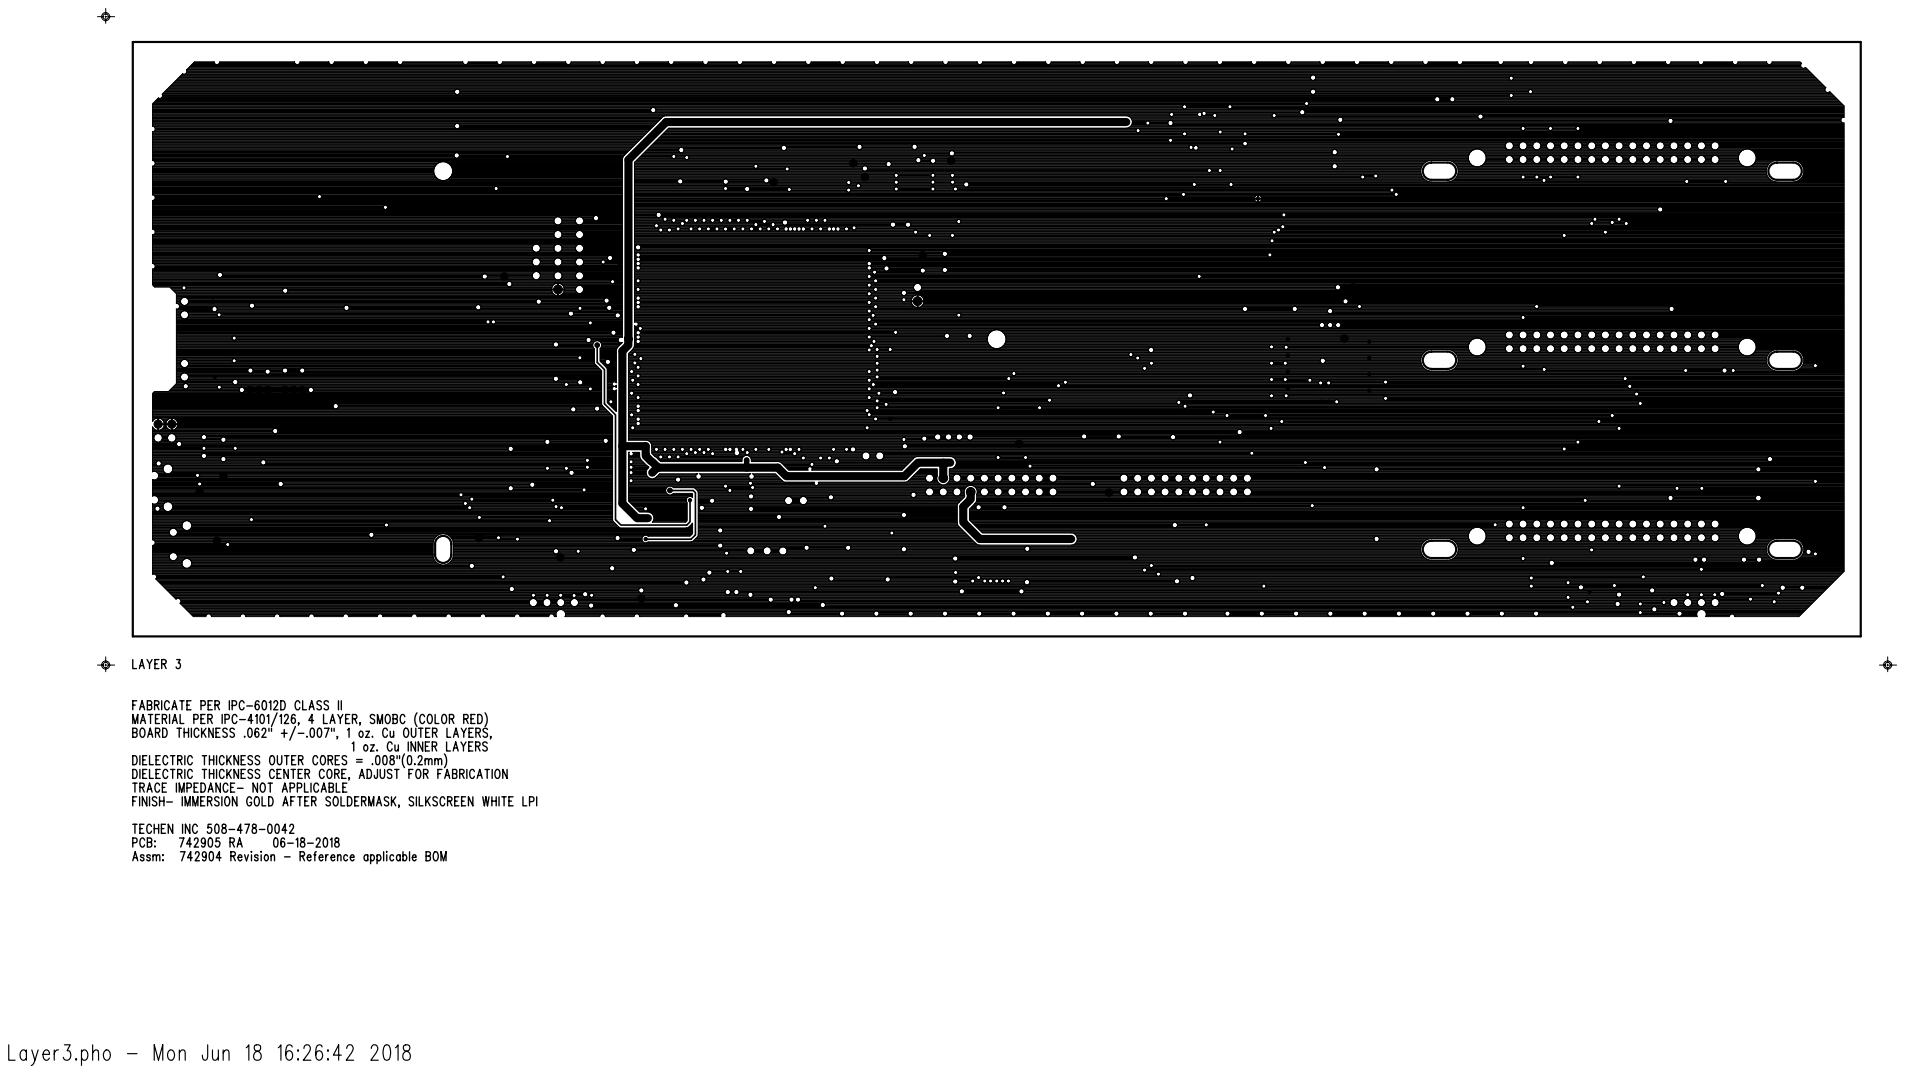
[picture p125: page 3]

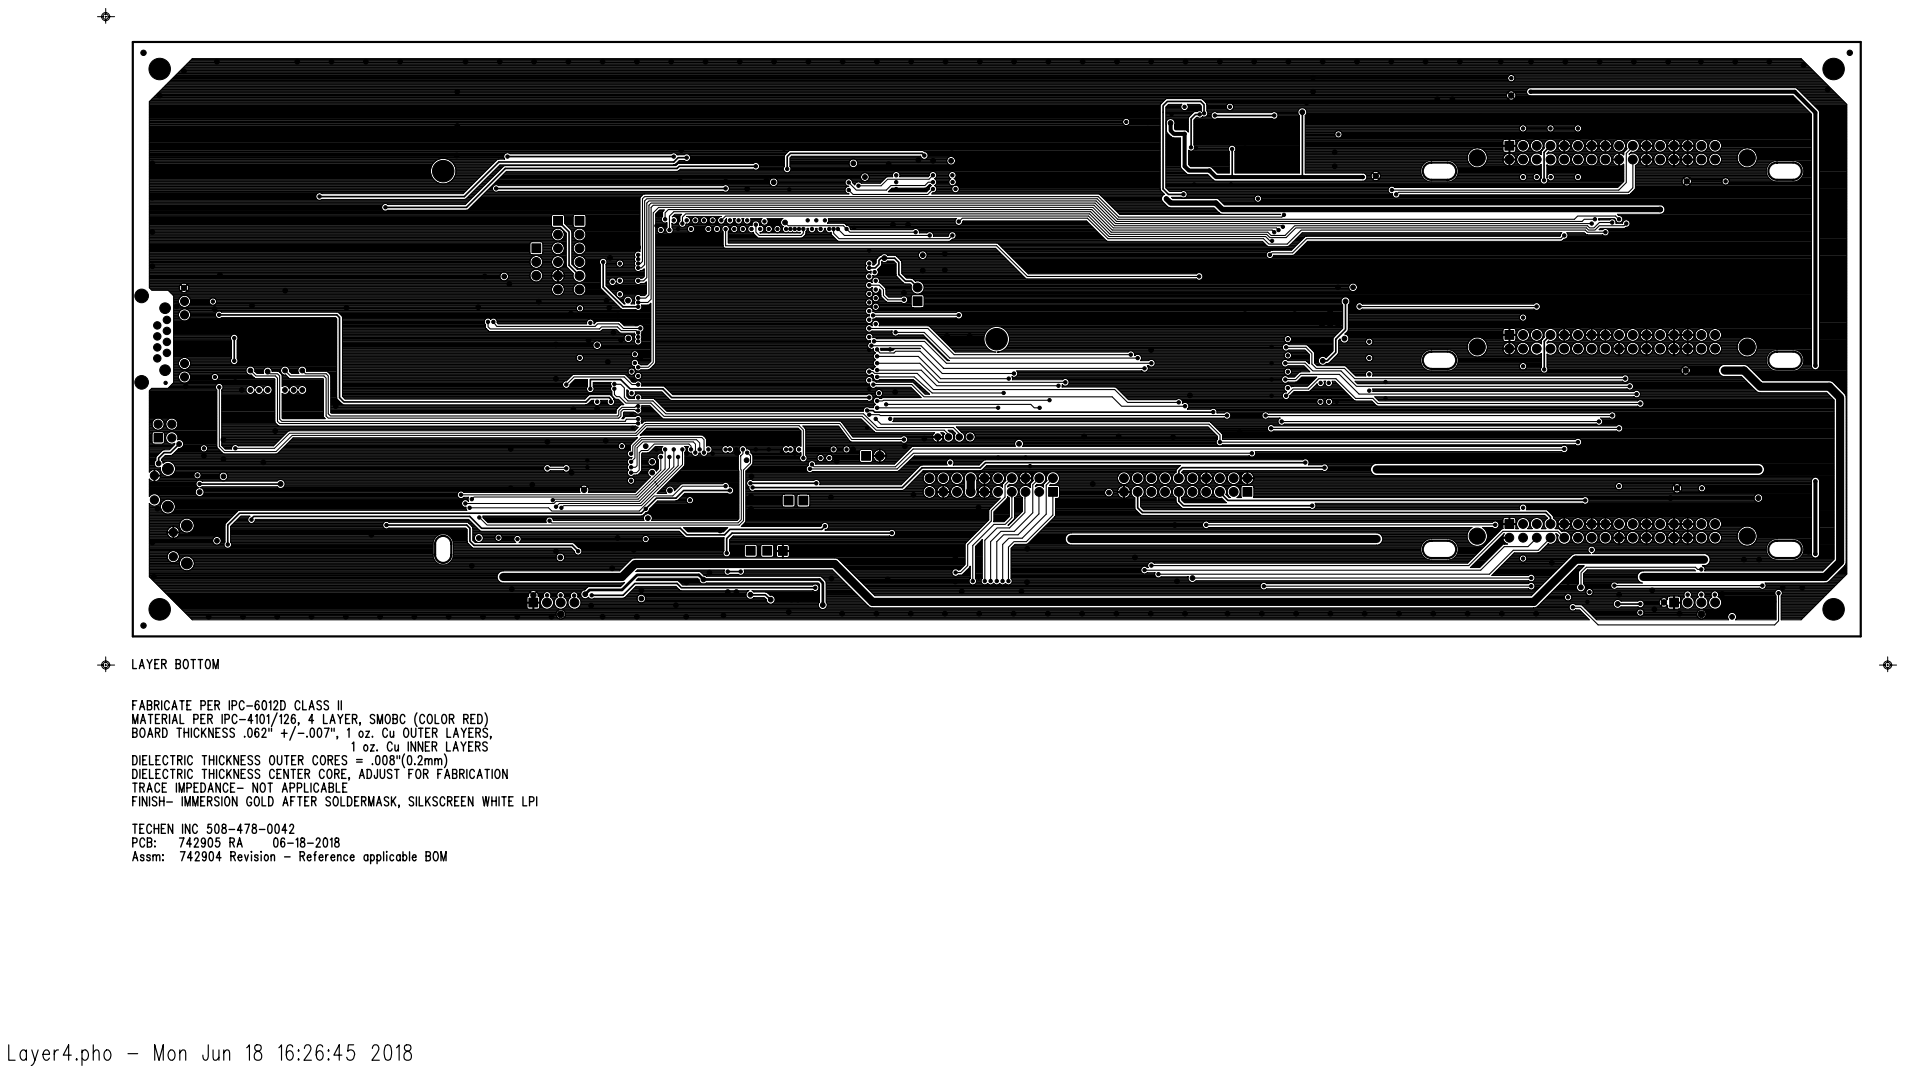
[picture p126: page 4]

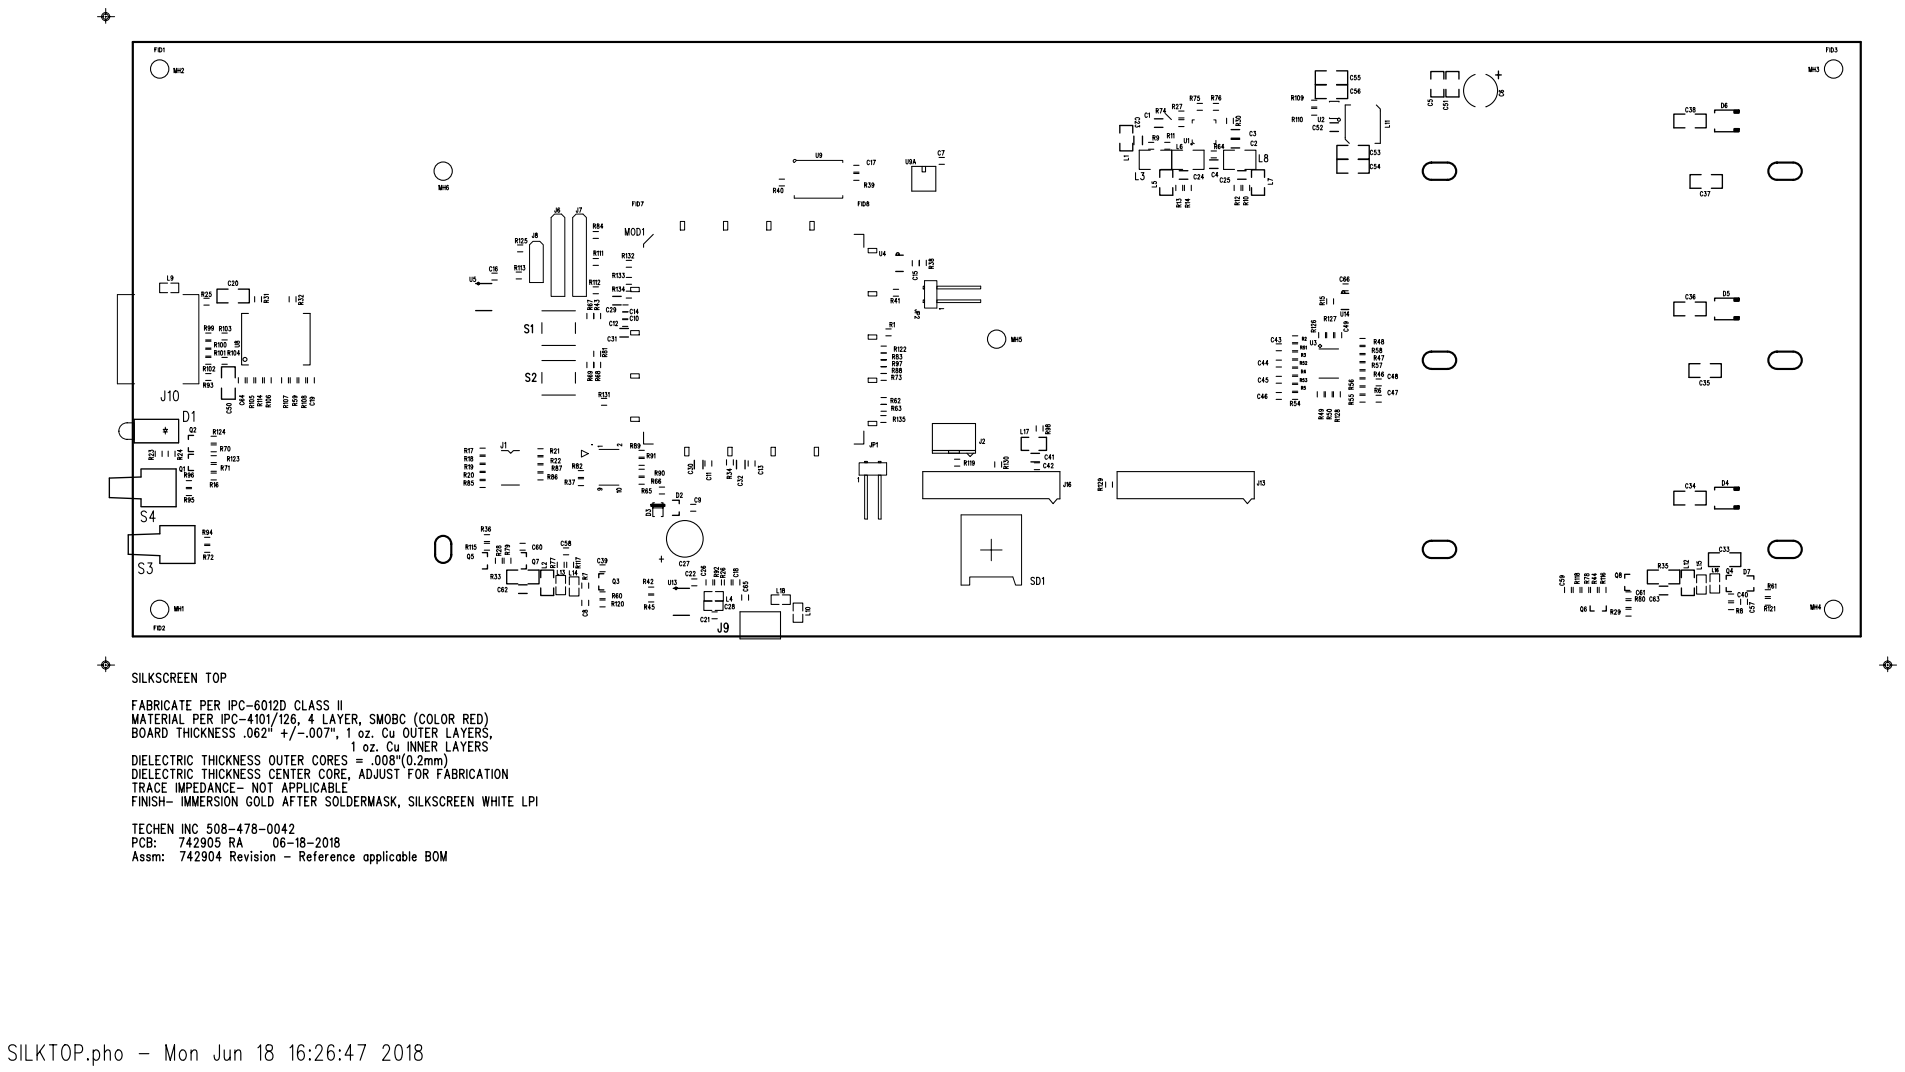
[picture p127: page 5]

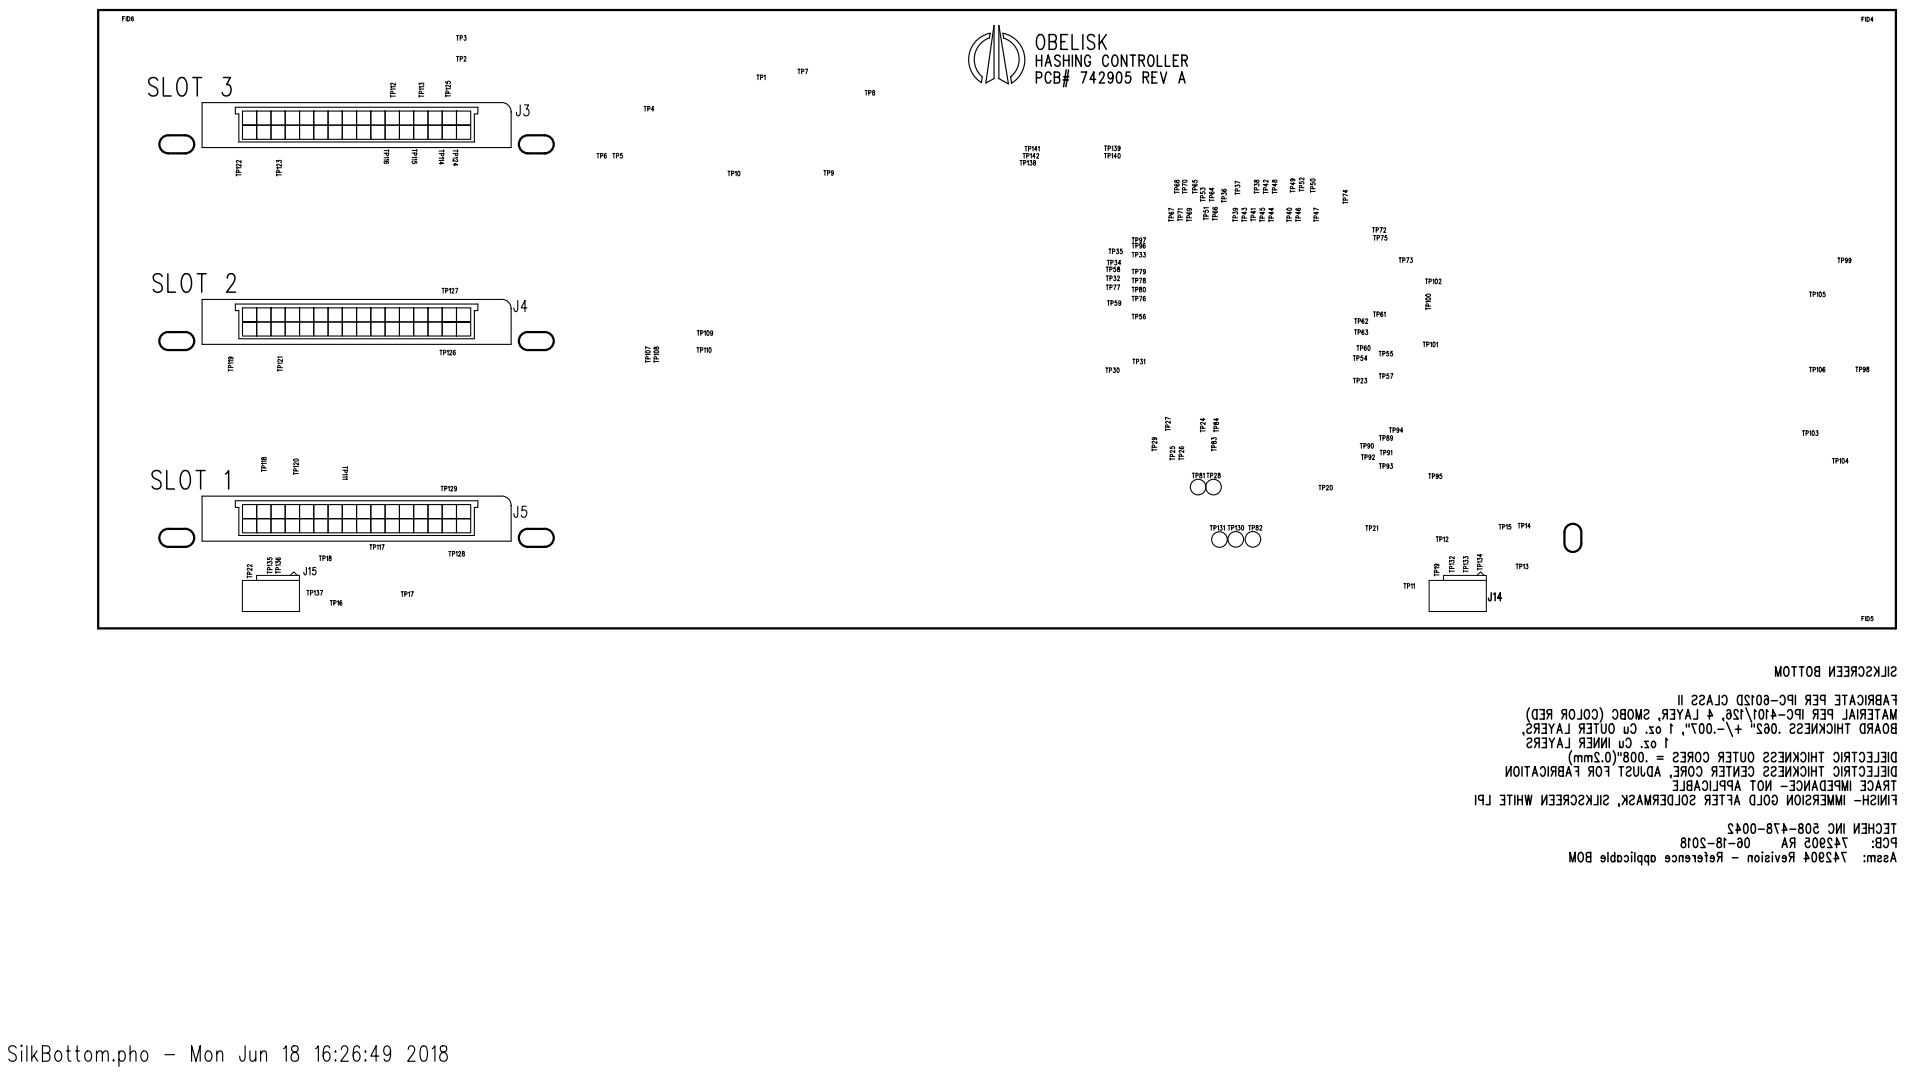
[picture p128: page 6]

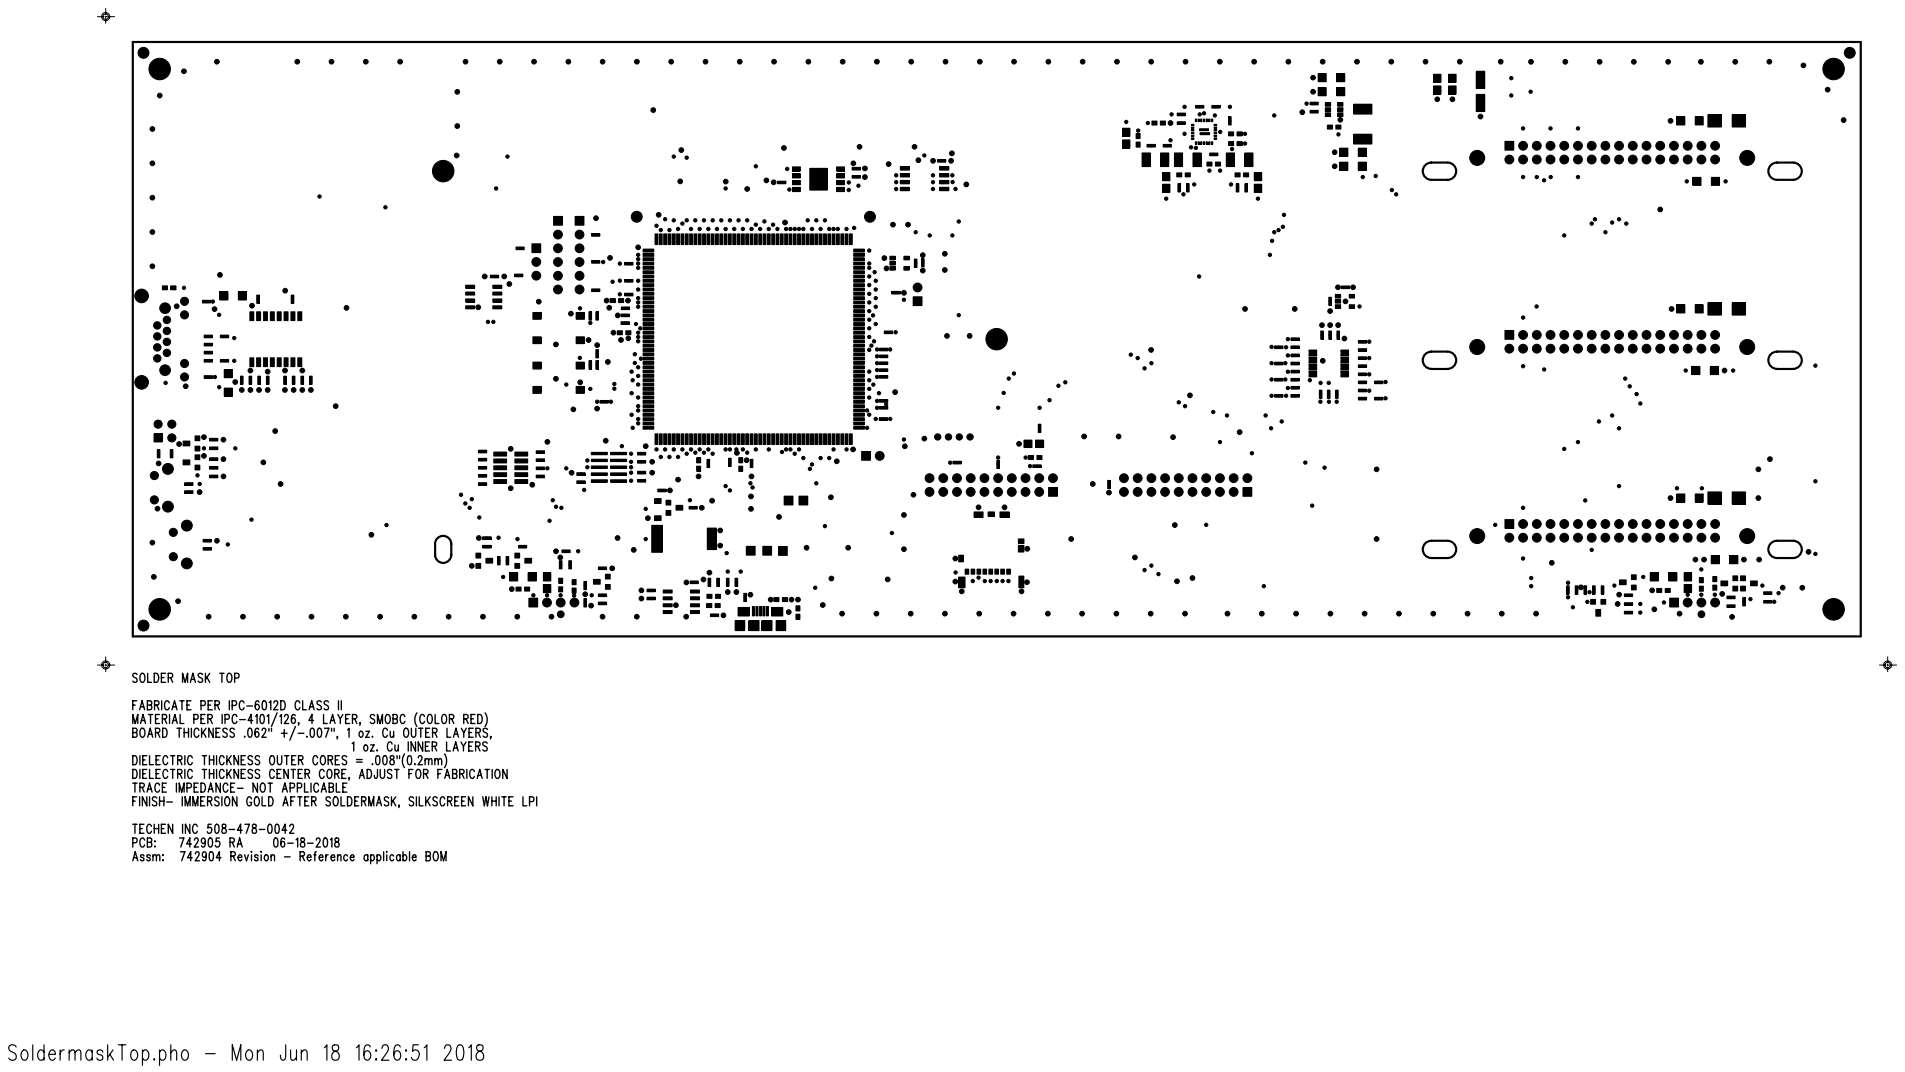
[picture p129: page 7]

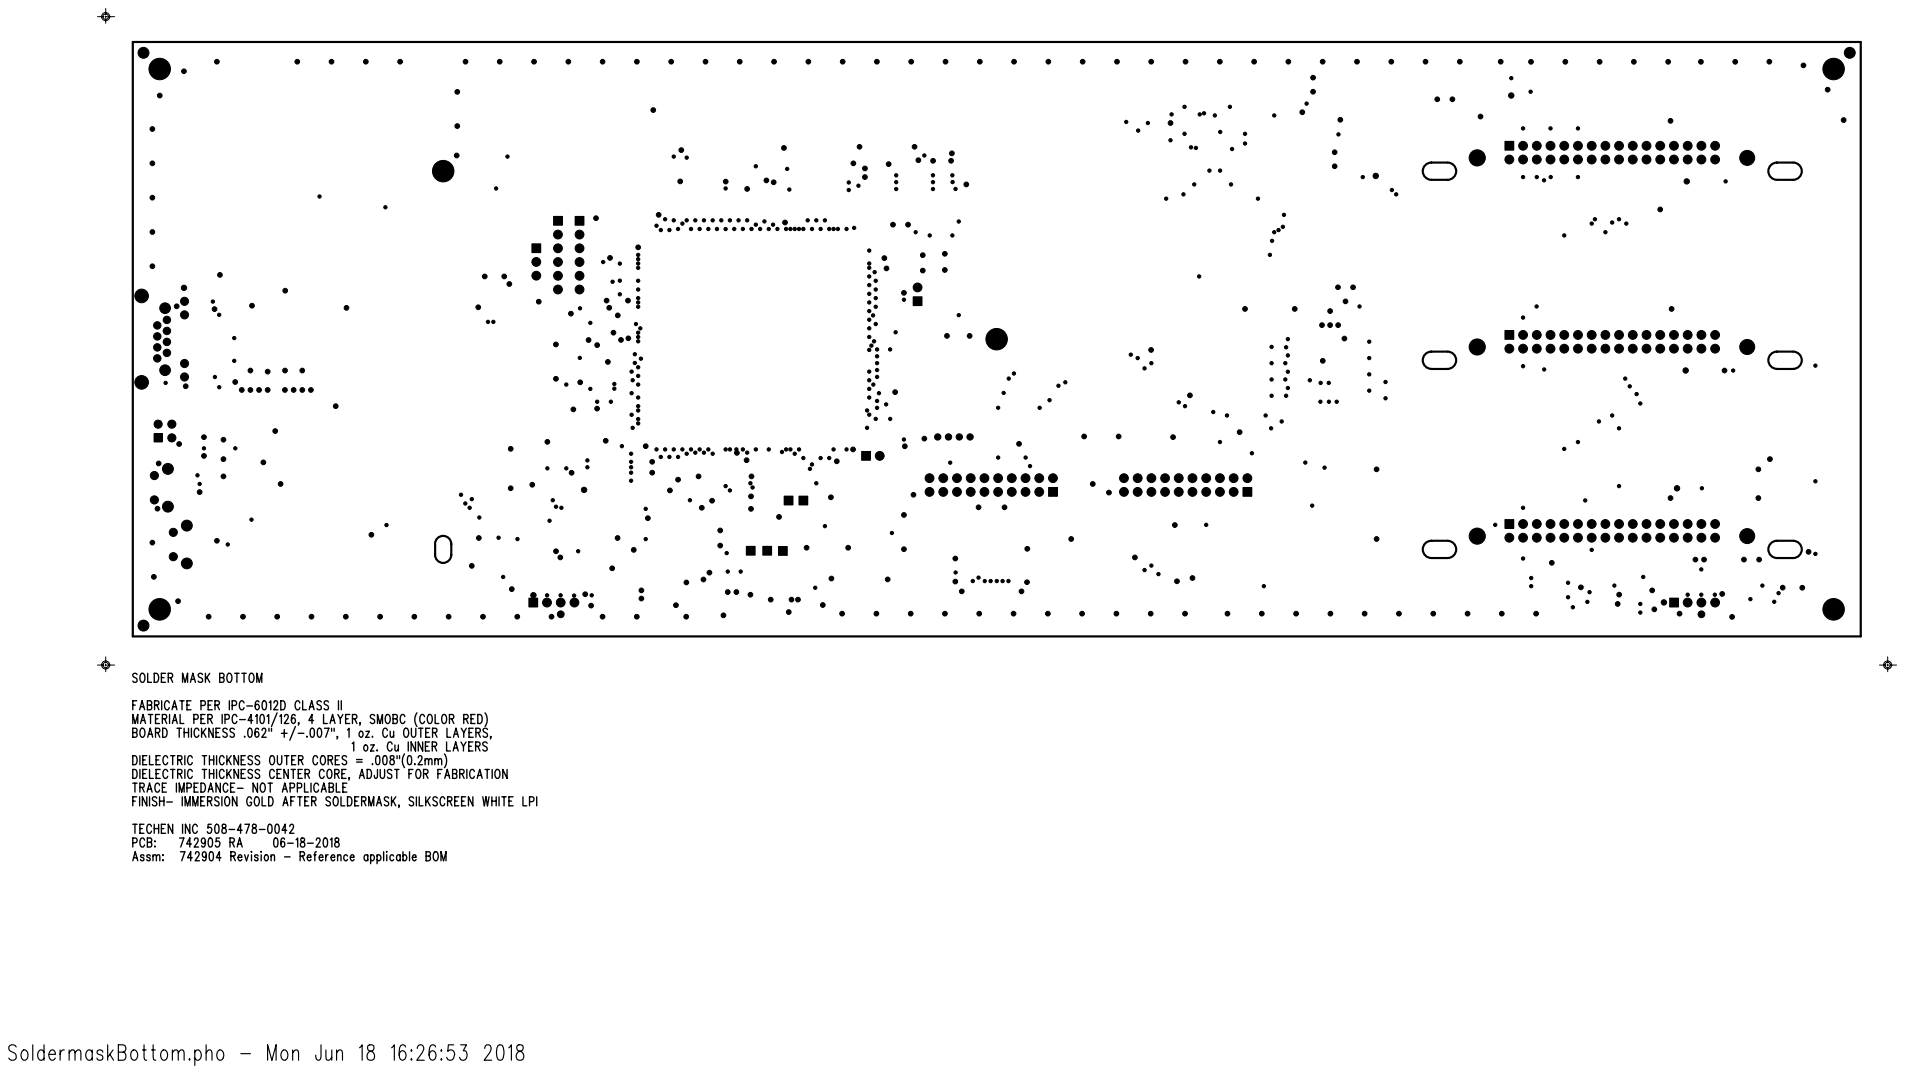
[picture p130: page 8]

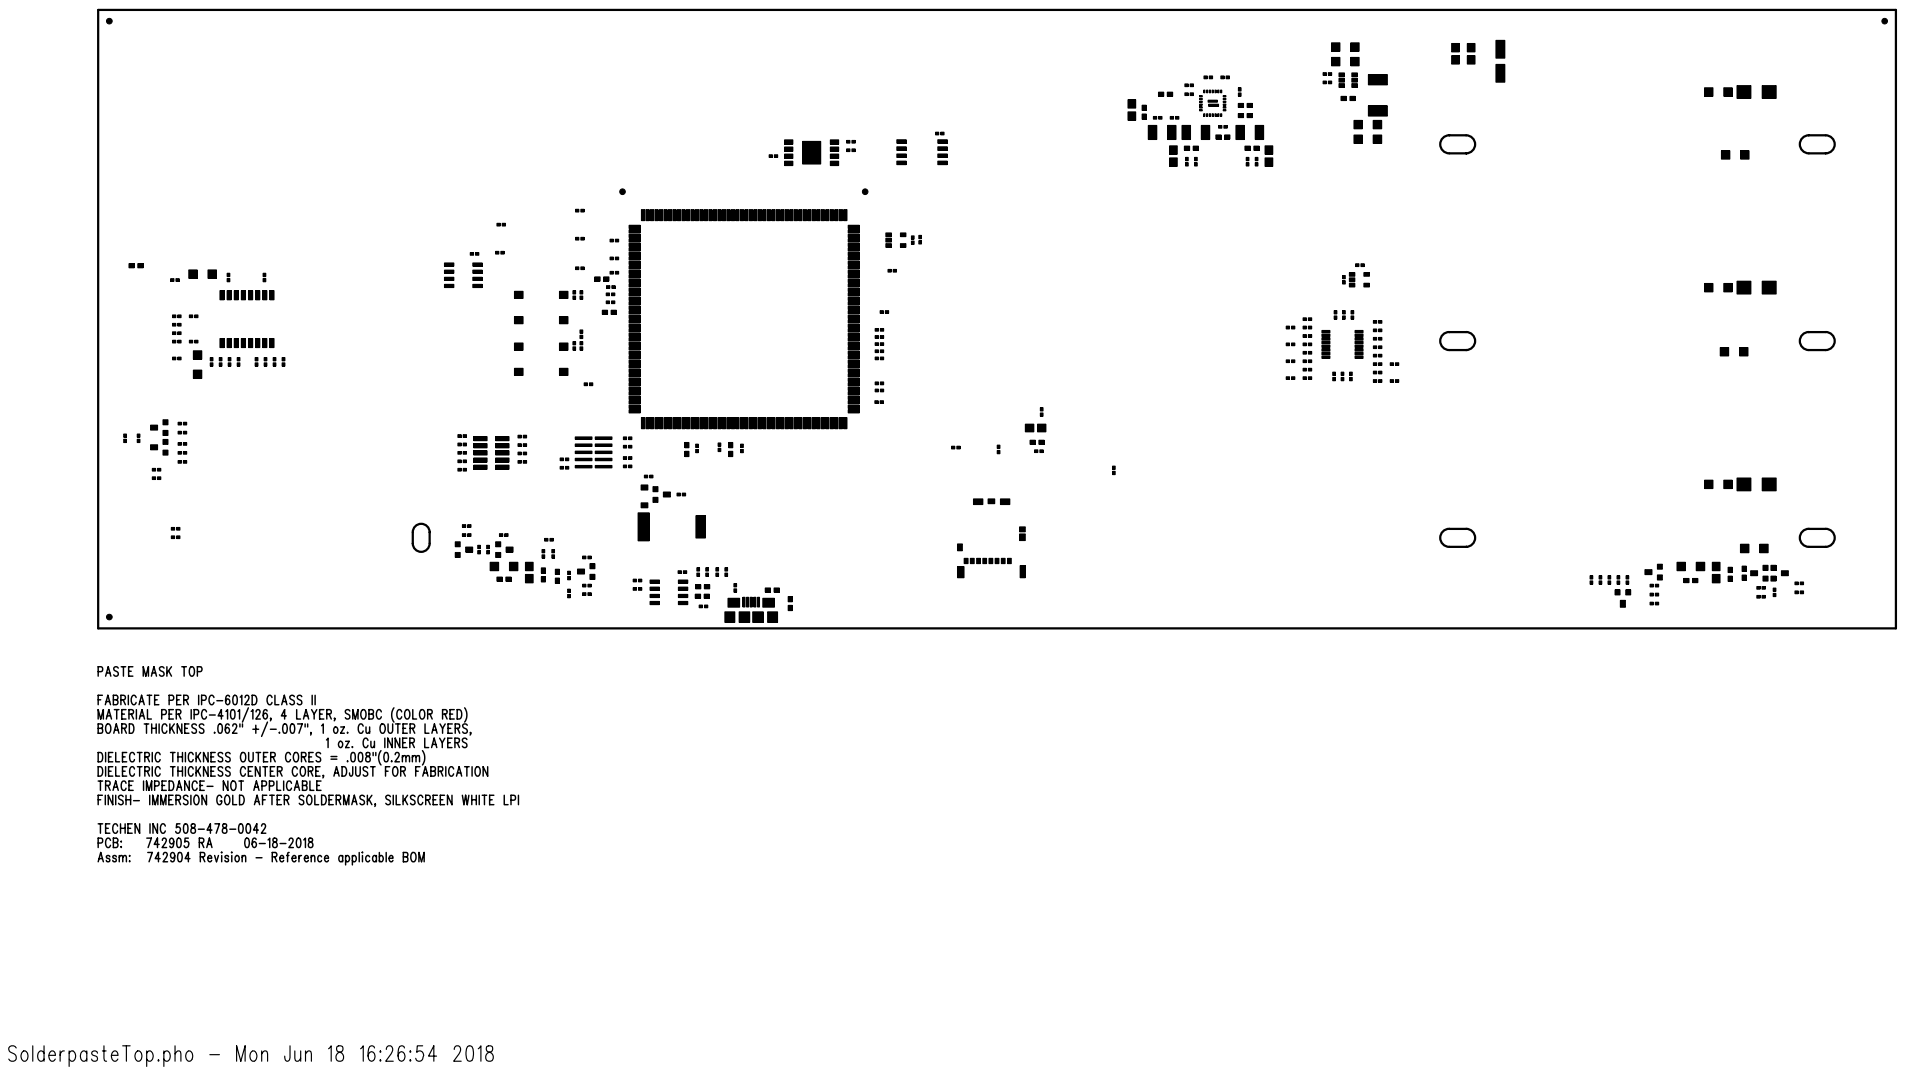
[picture p131: page 9]

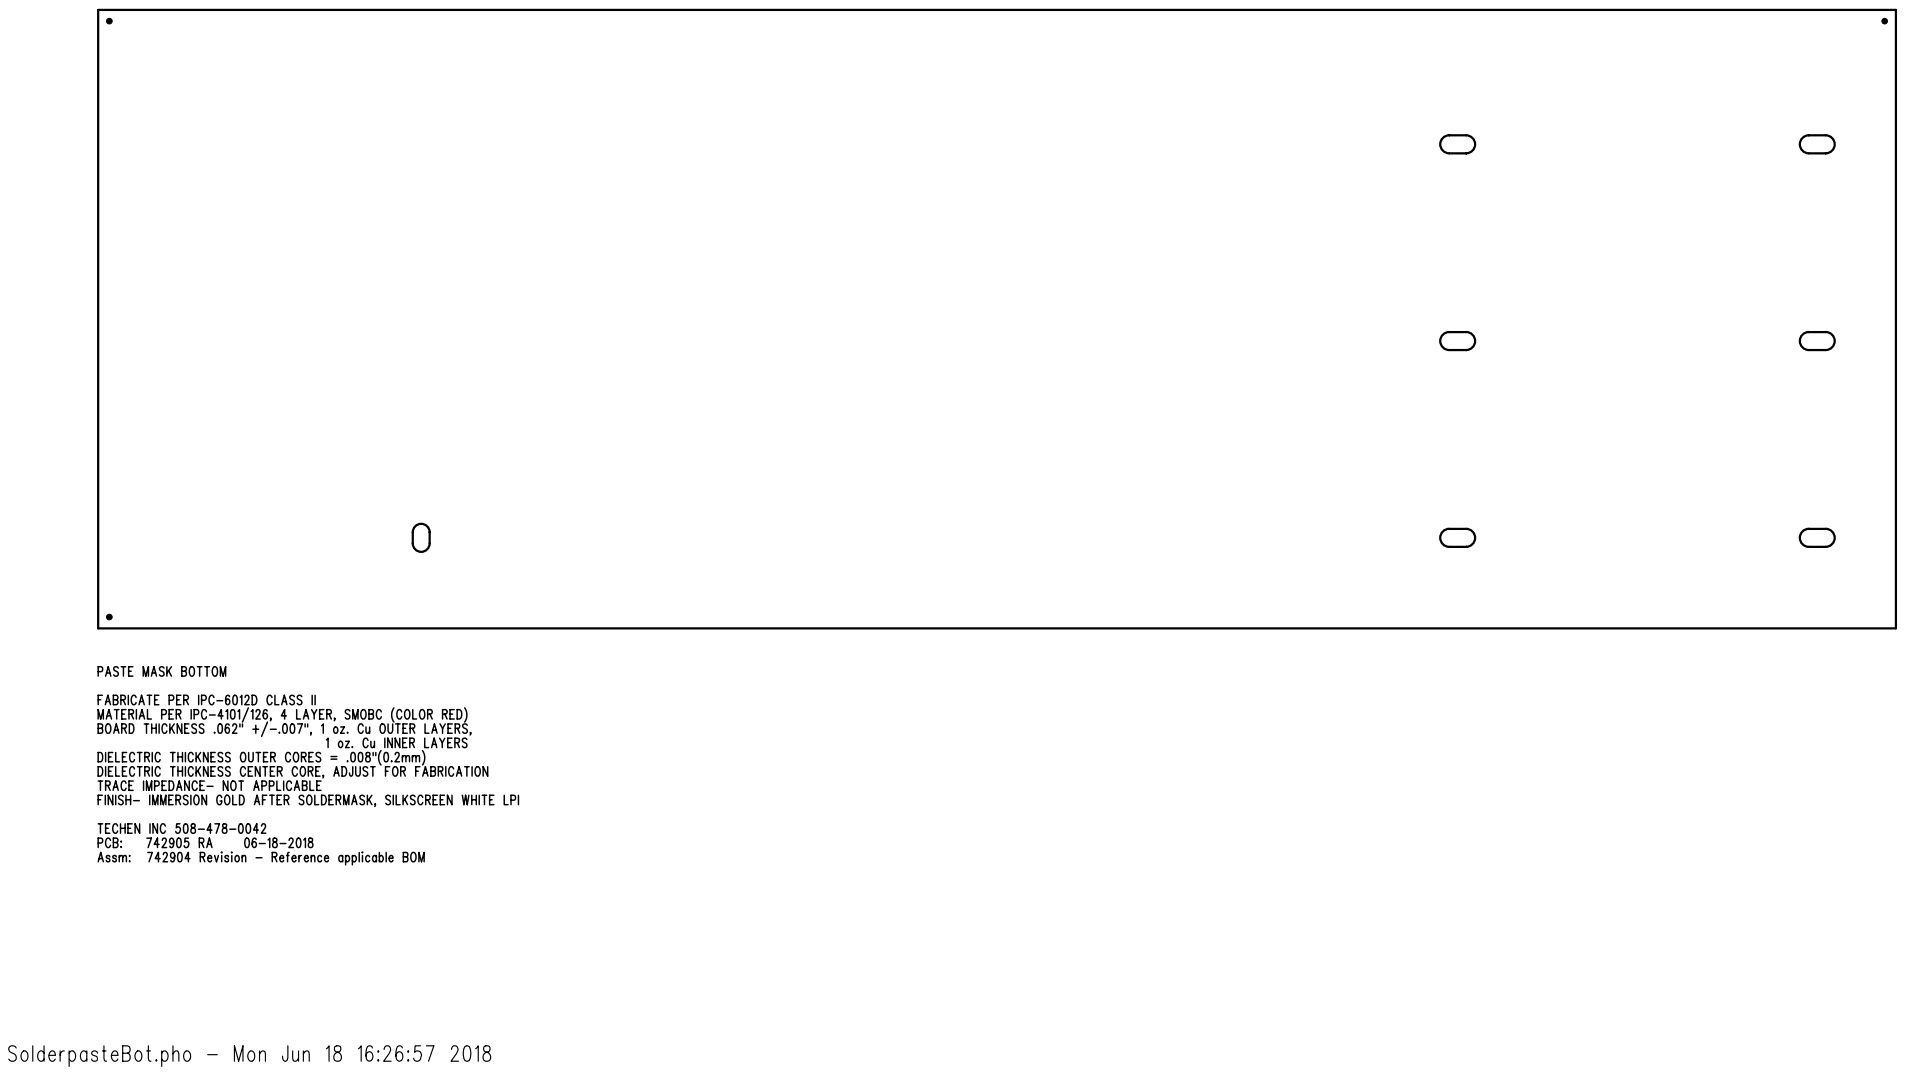
[picture p132: page 10]

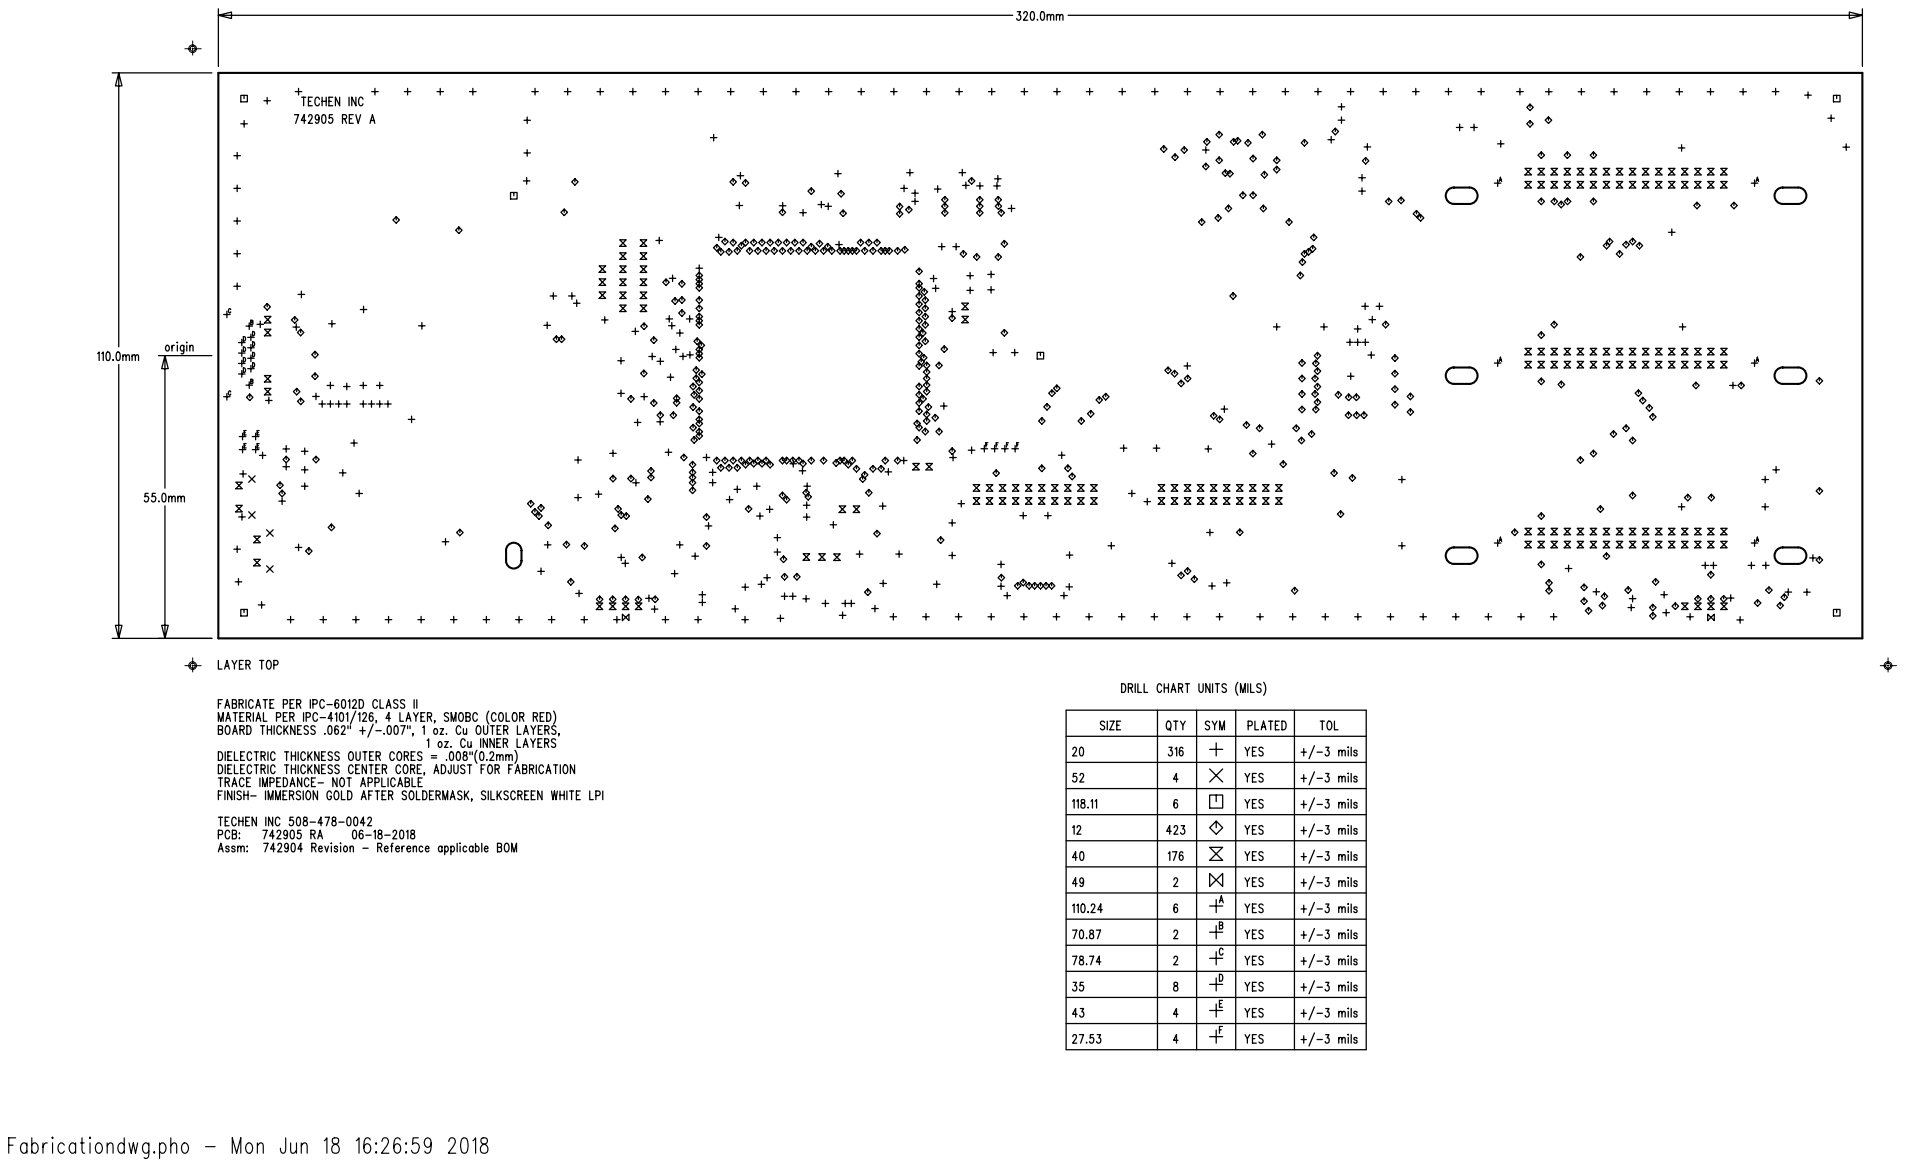
[picture p133: page 11]

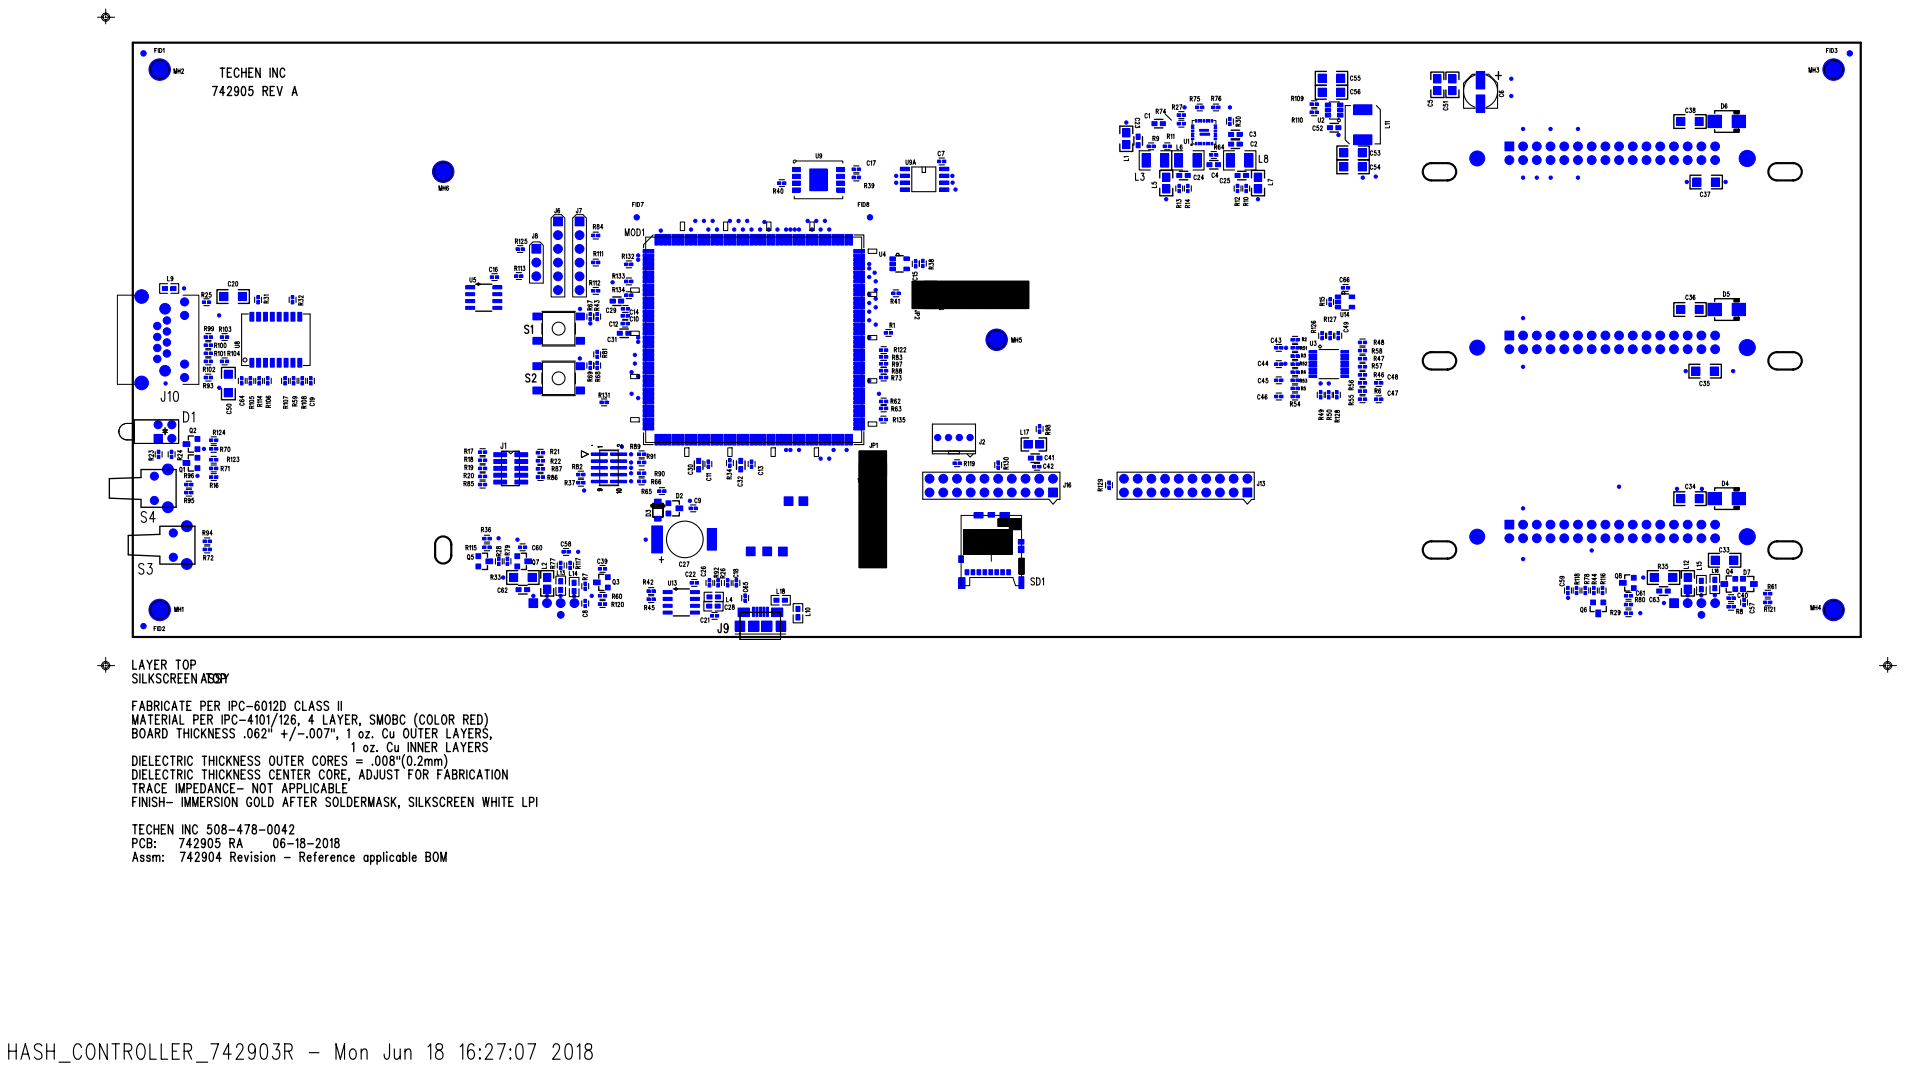
[picture p134: page 12]

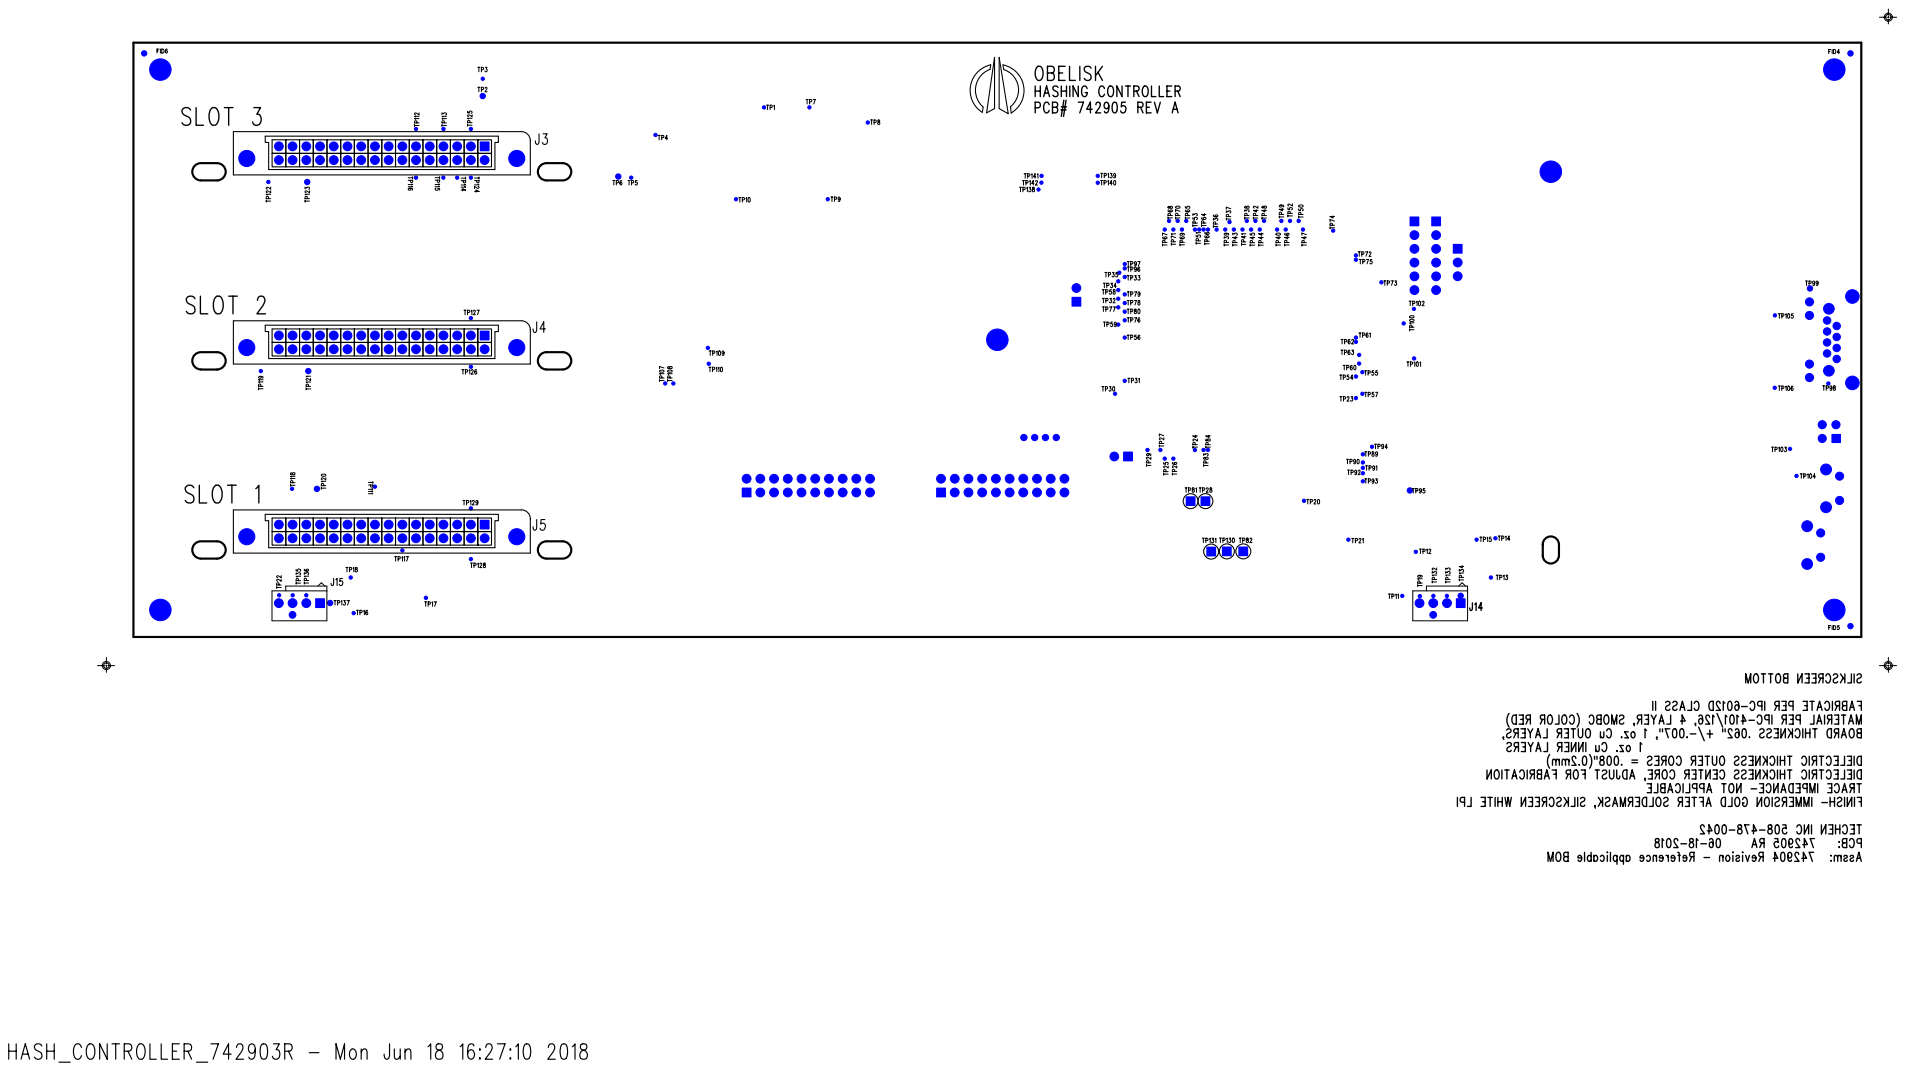
[picture p135: page 13]
