ObeliskInc/obelisk-hardware/Generation 1 Mining Hardware/Electrical/Hashing Board/SIAHashingBd742901R2pcb.pdf

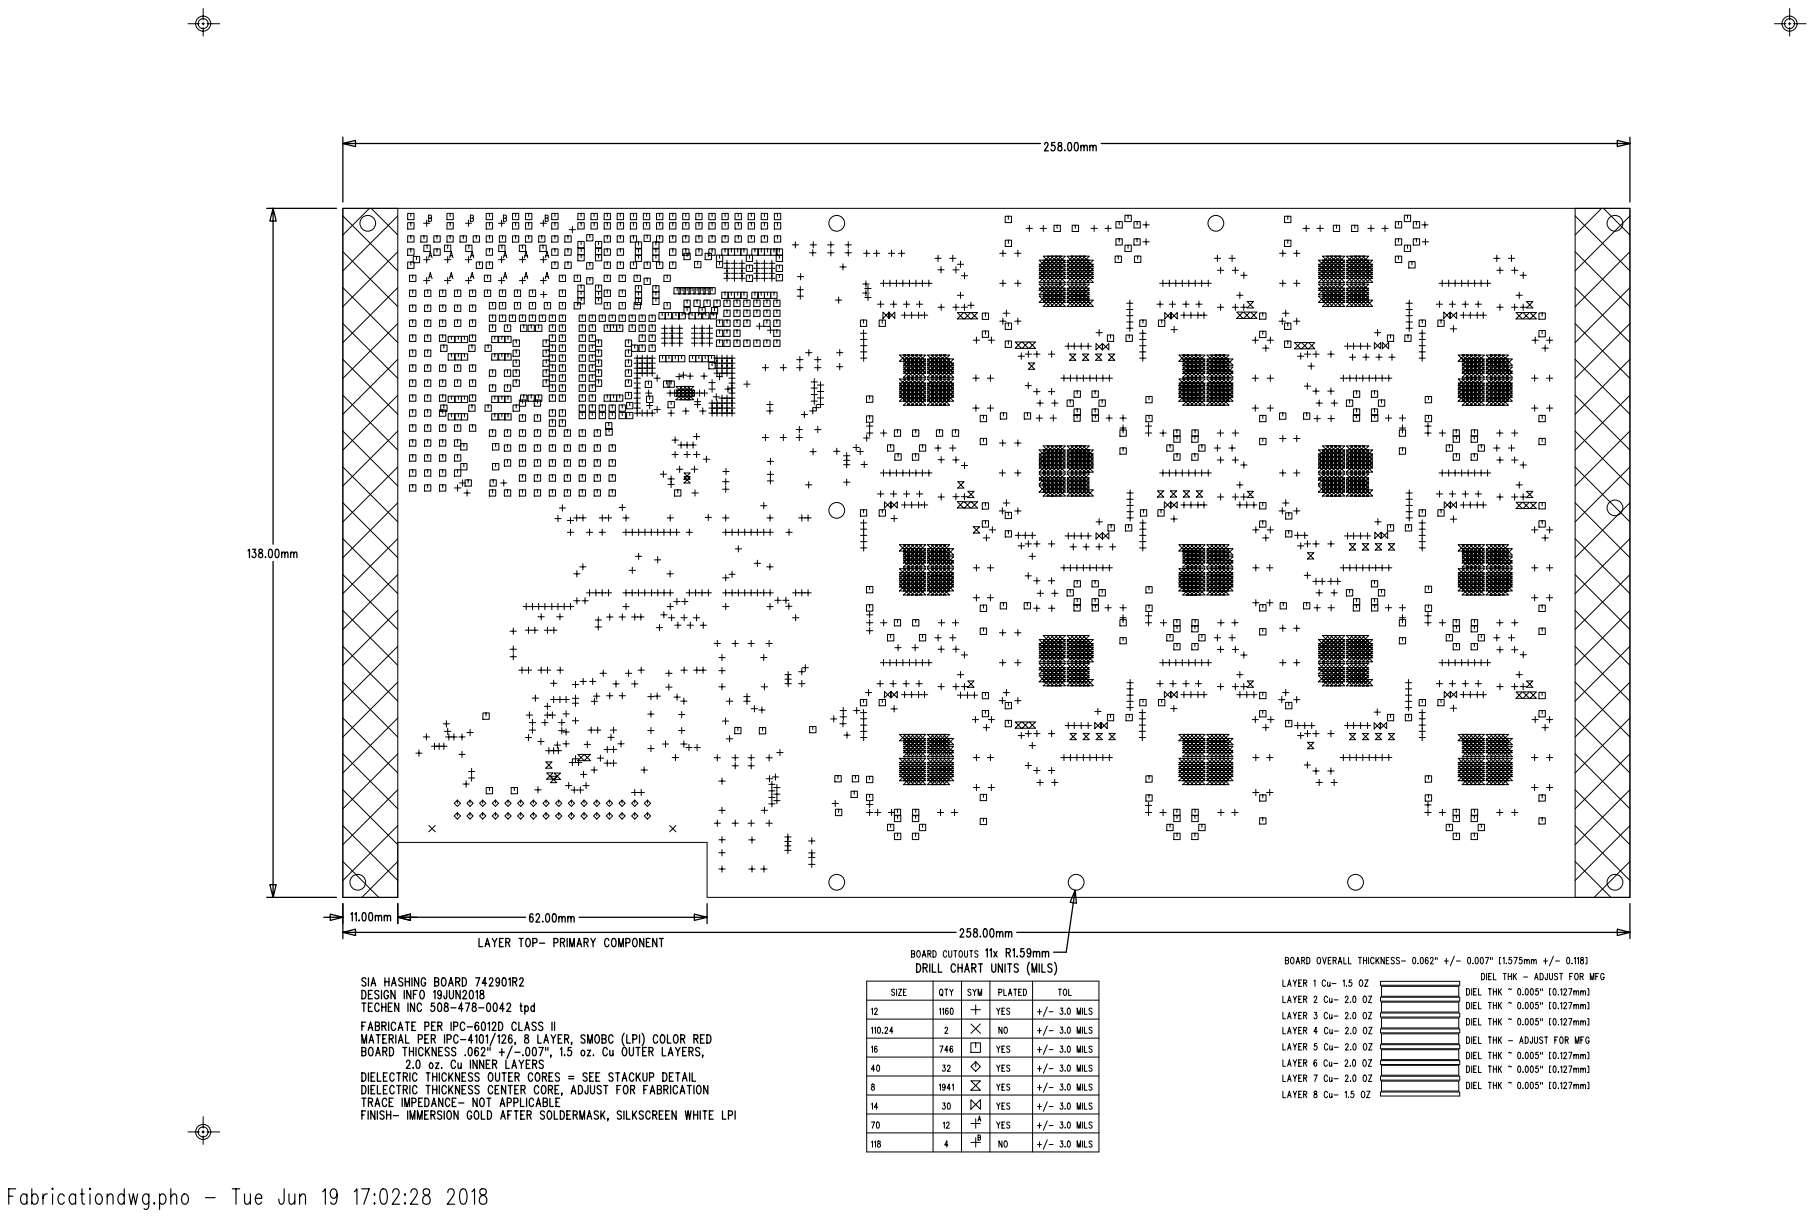
[picture p136: page 1]

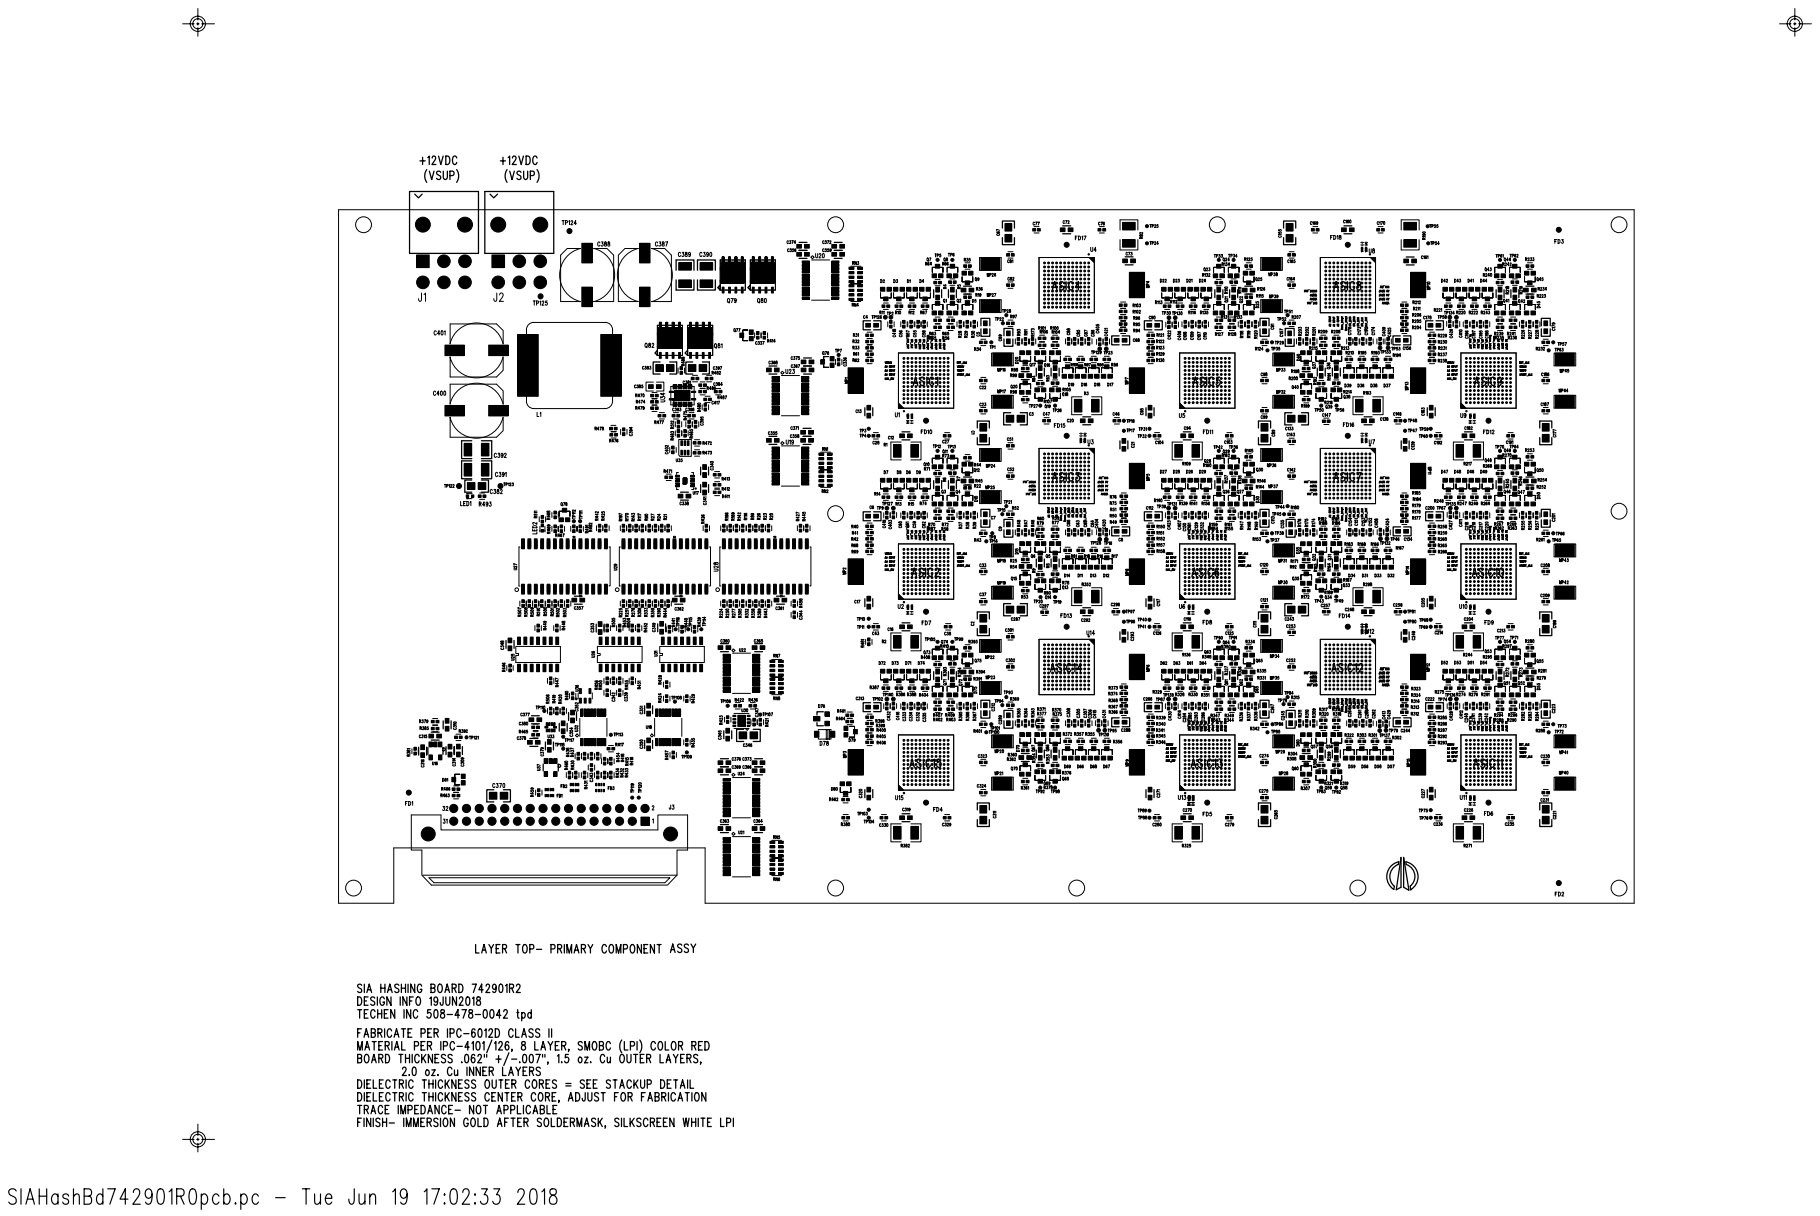
[picture p137: page 2]

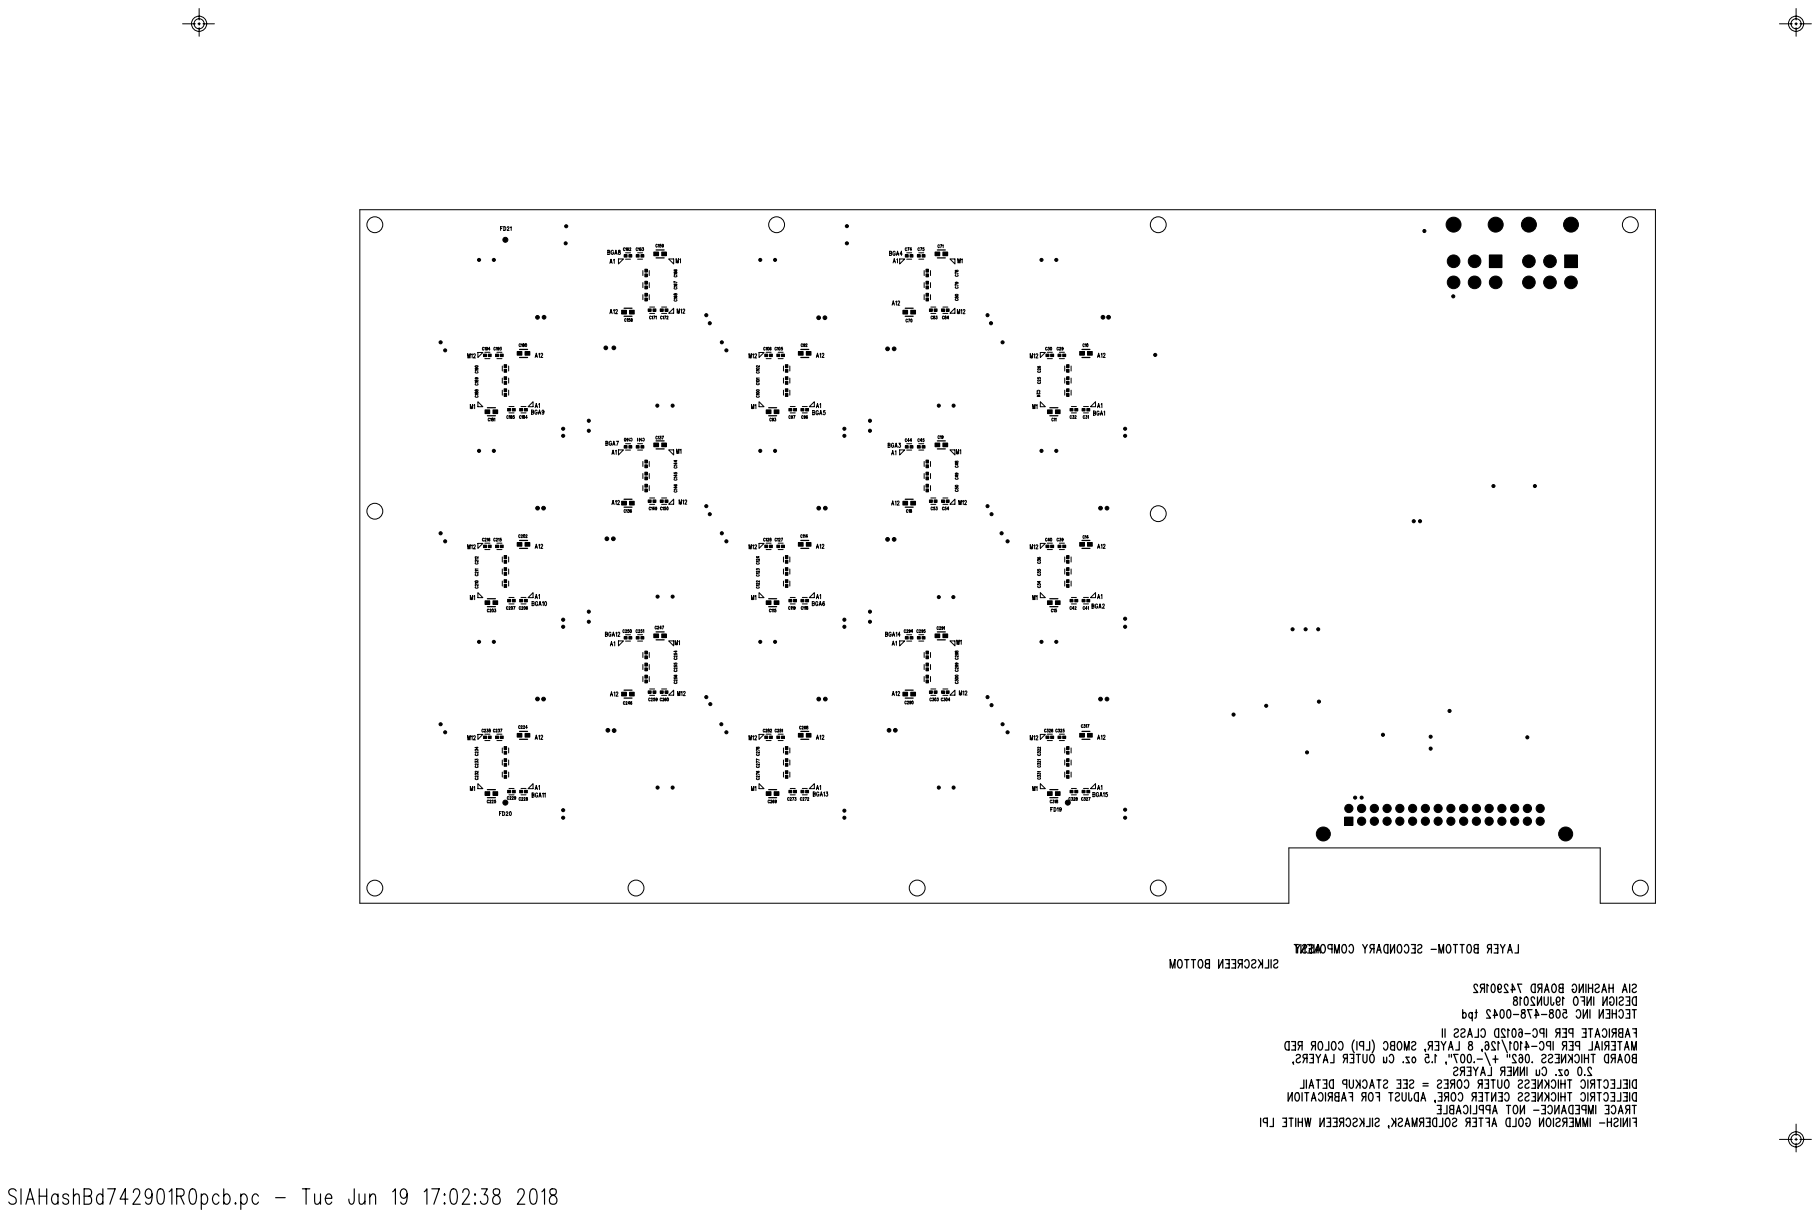
[picture p138: page 3]

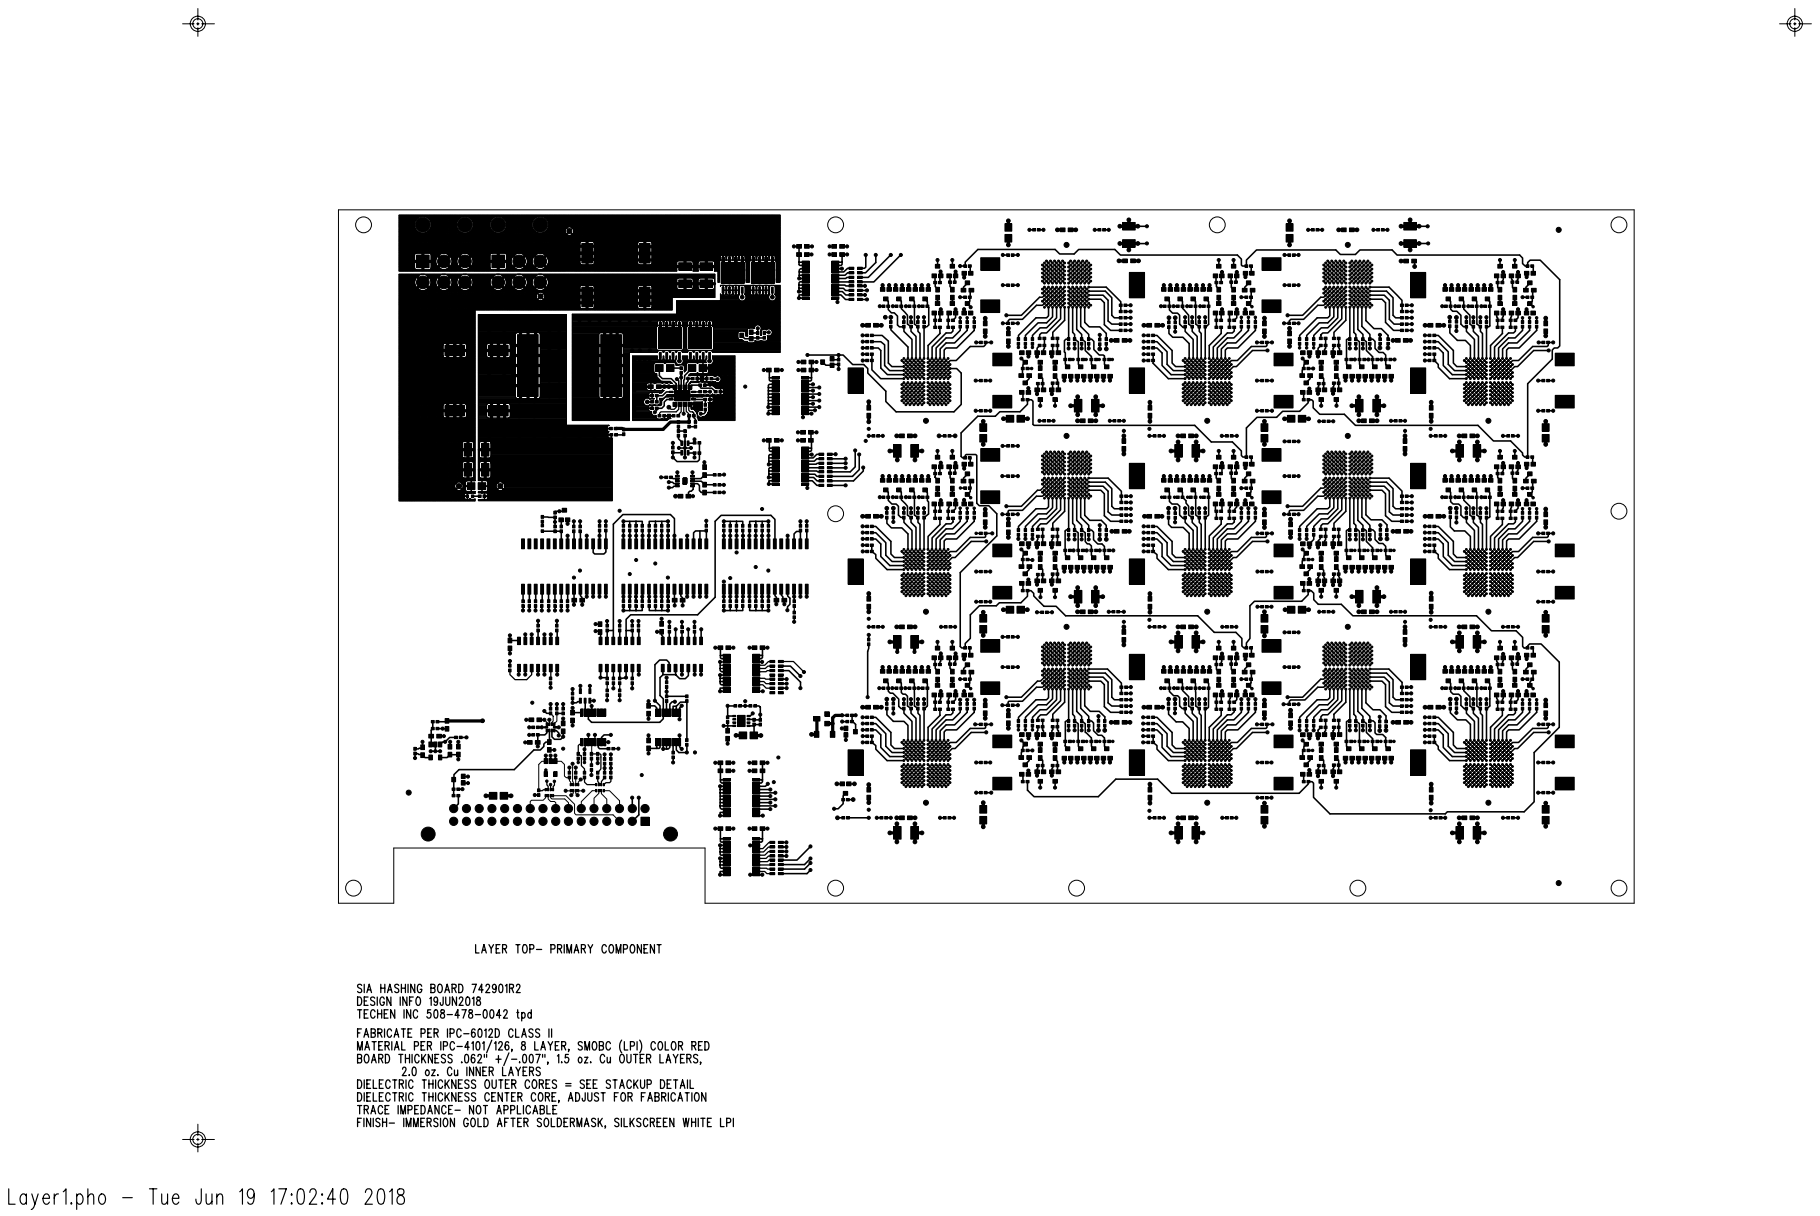
[picture p139: page 4]

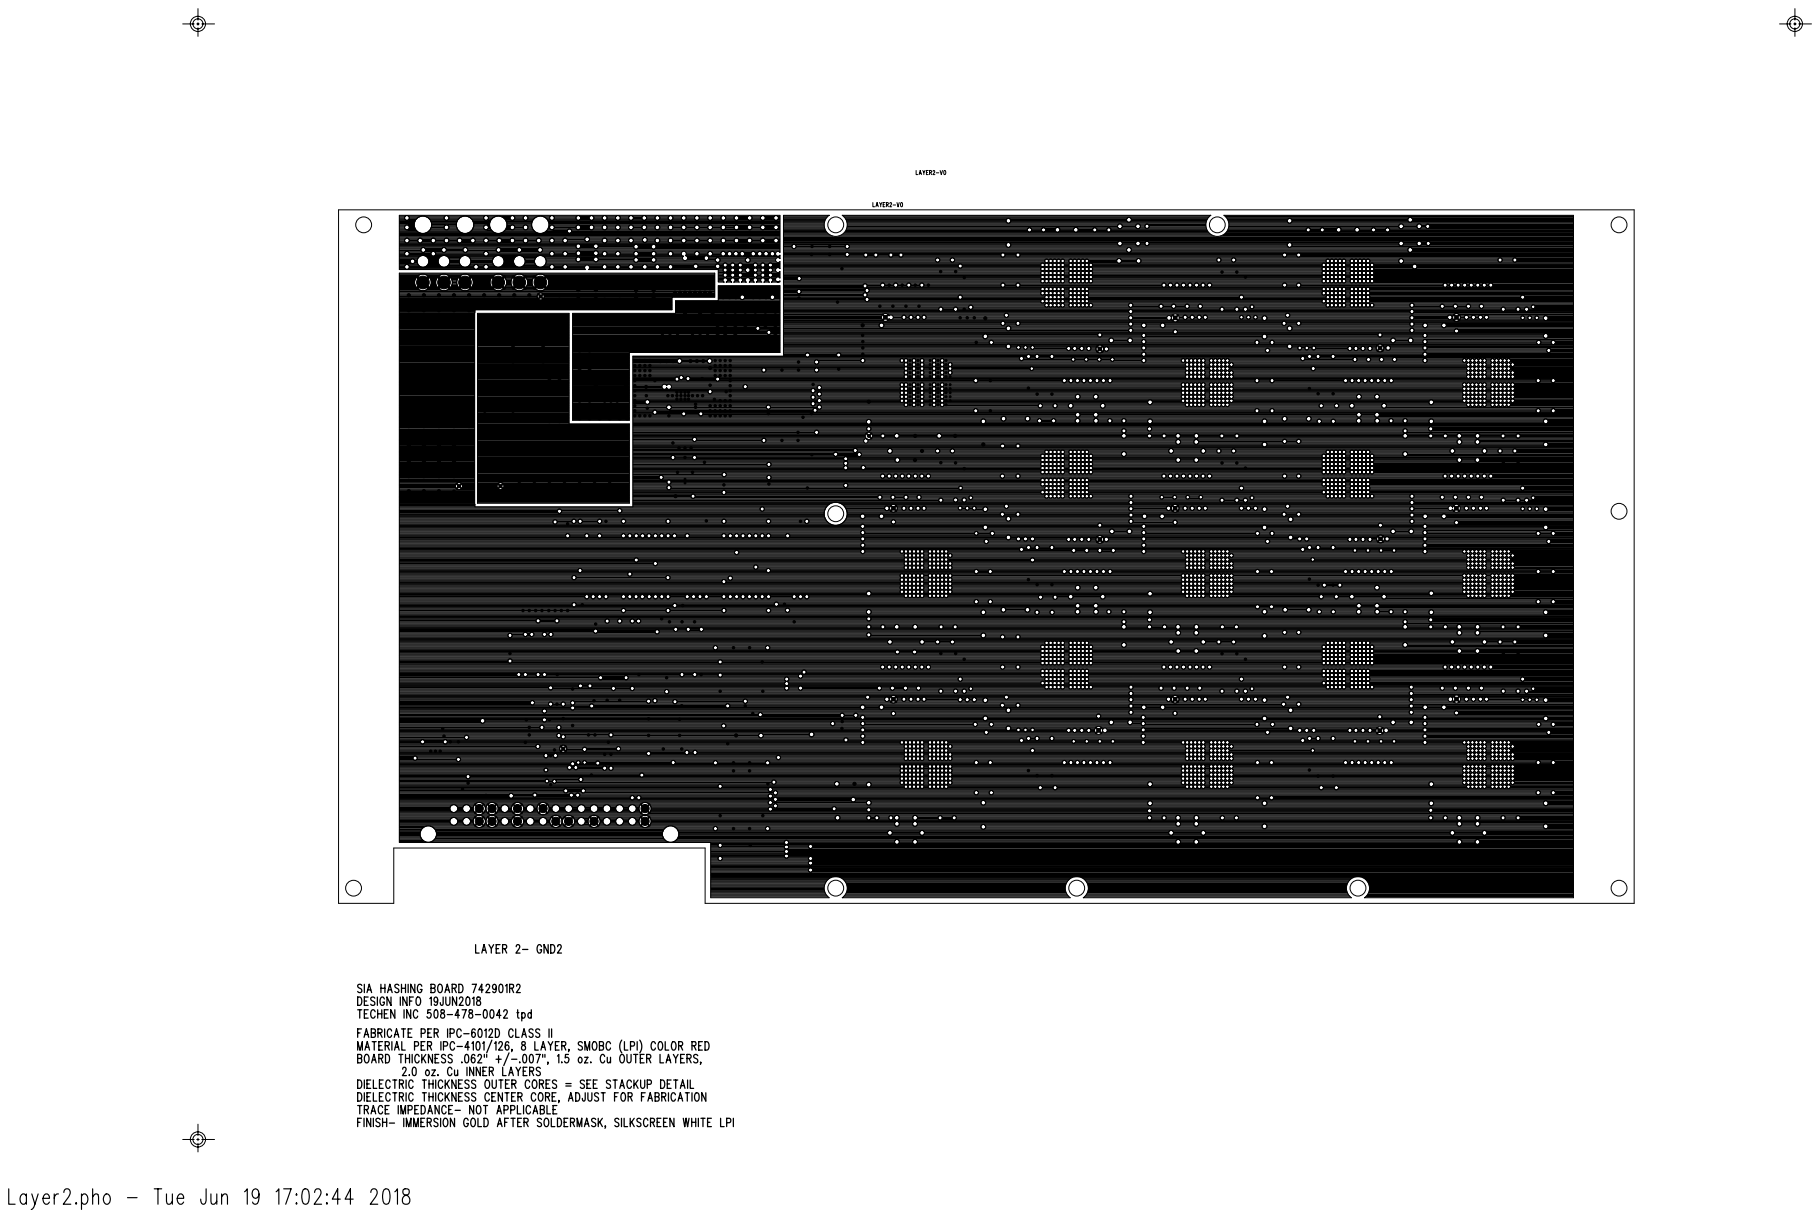
[picture p140: page 5]

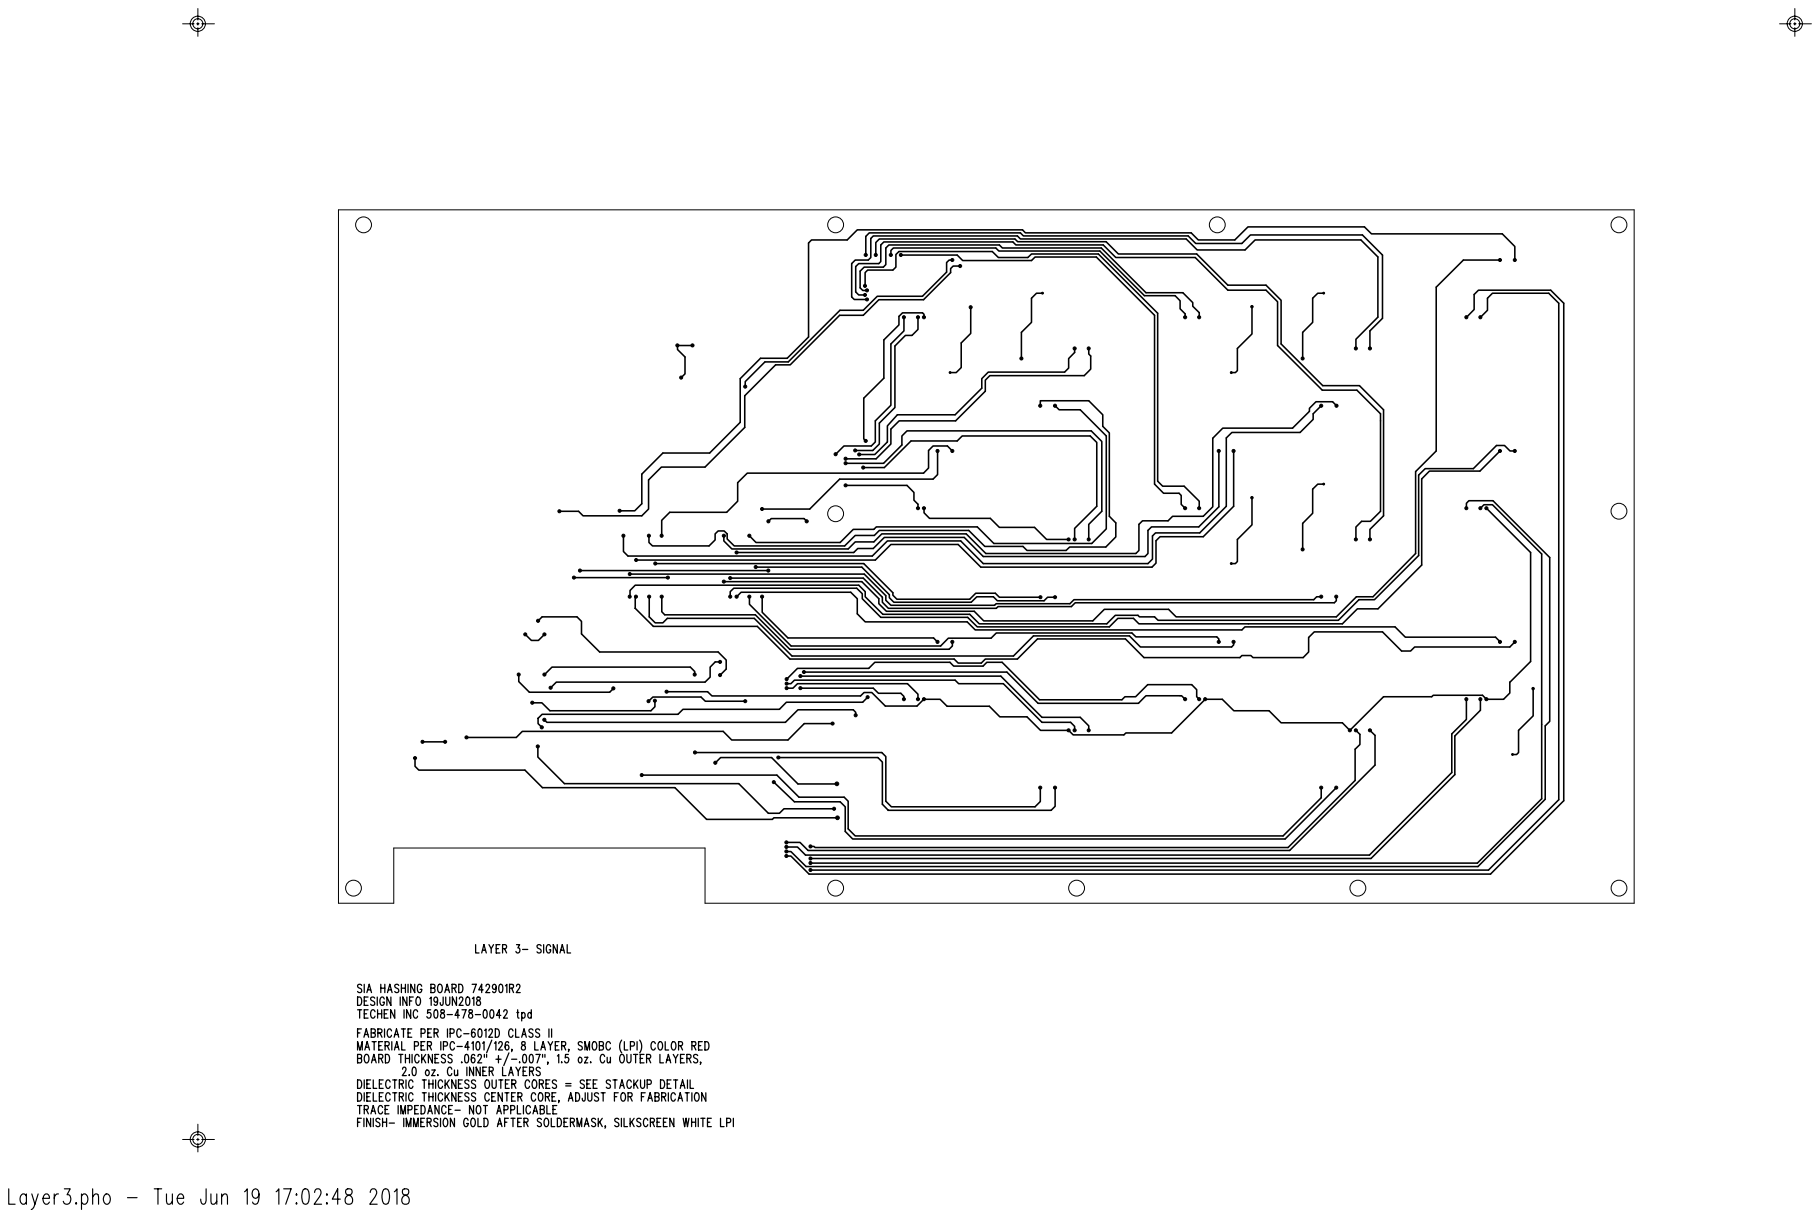
[picture p141: page 6]

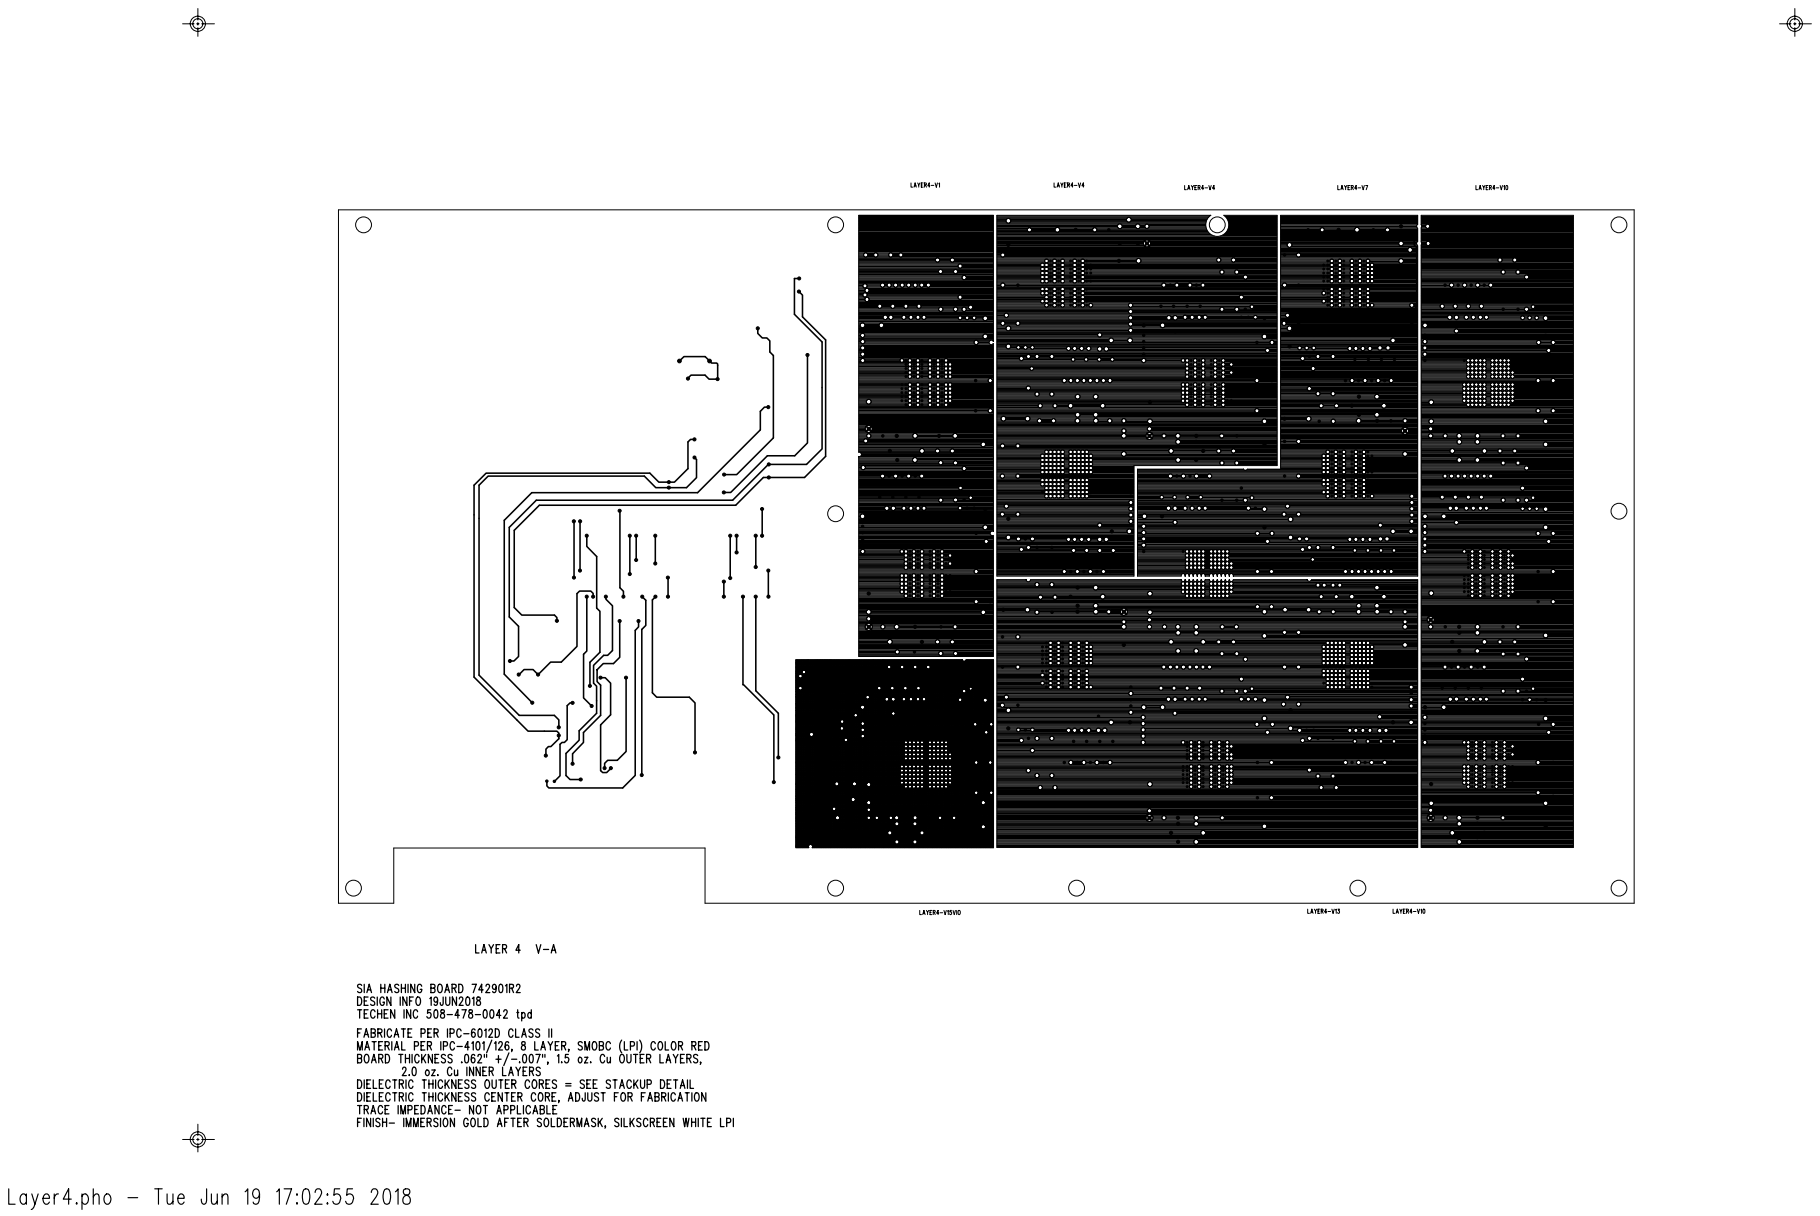
[picture p142: page 7]

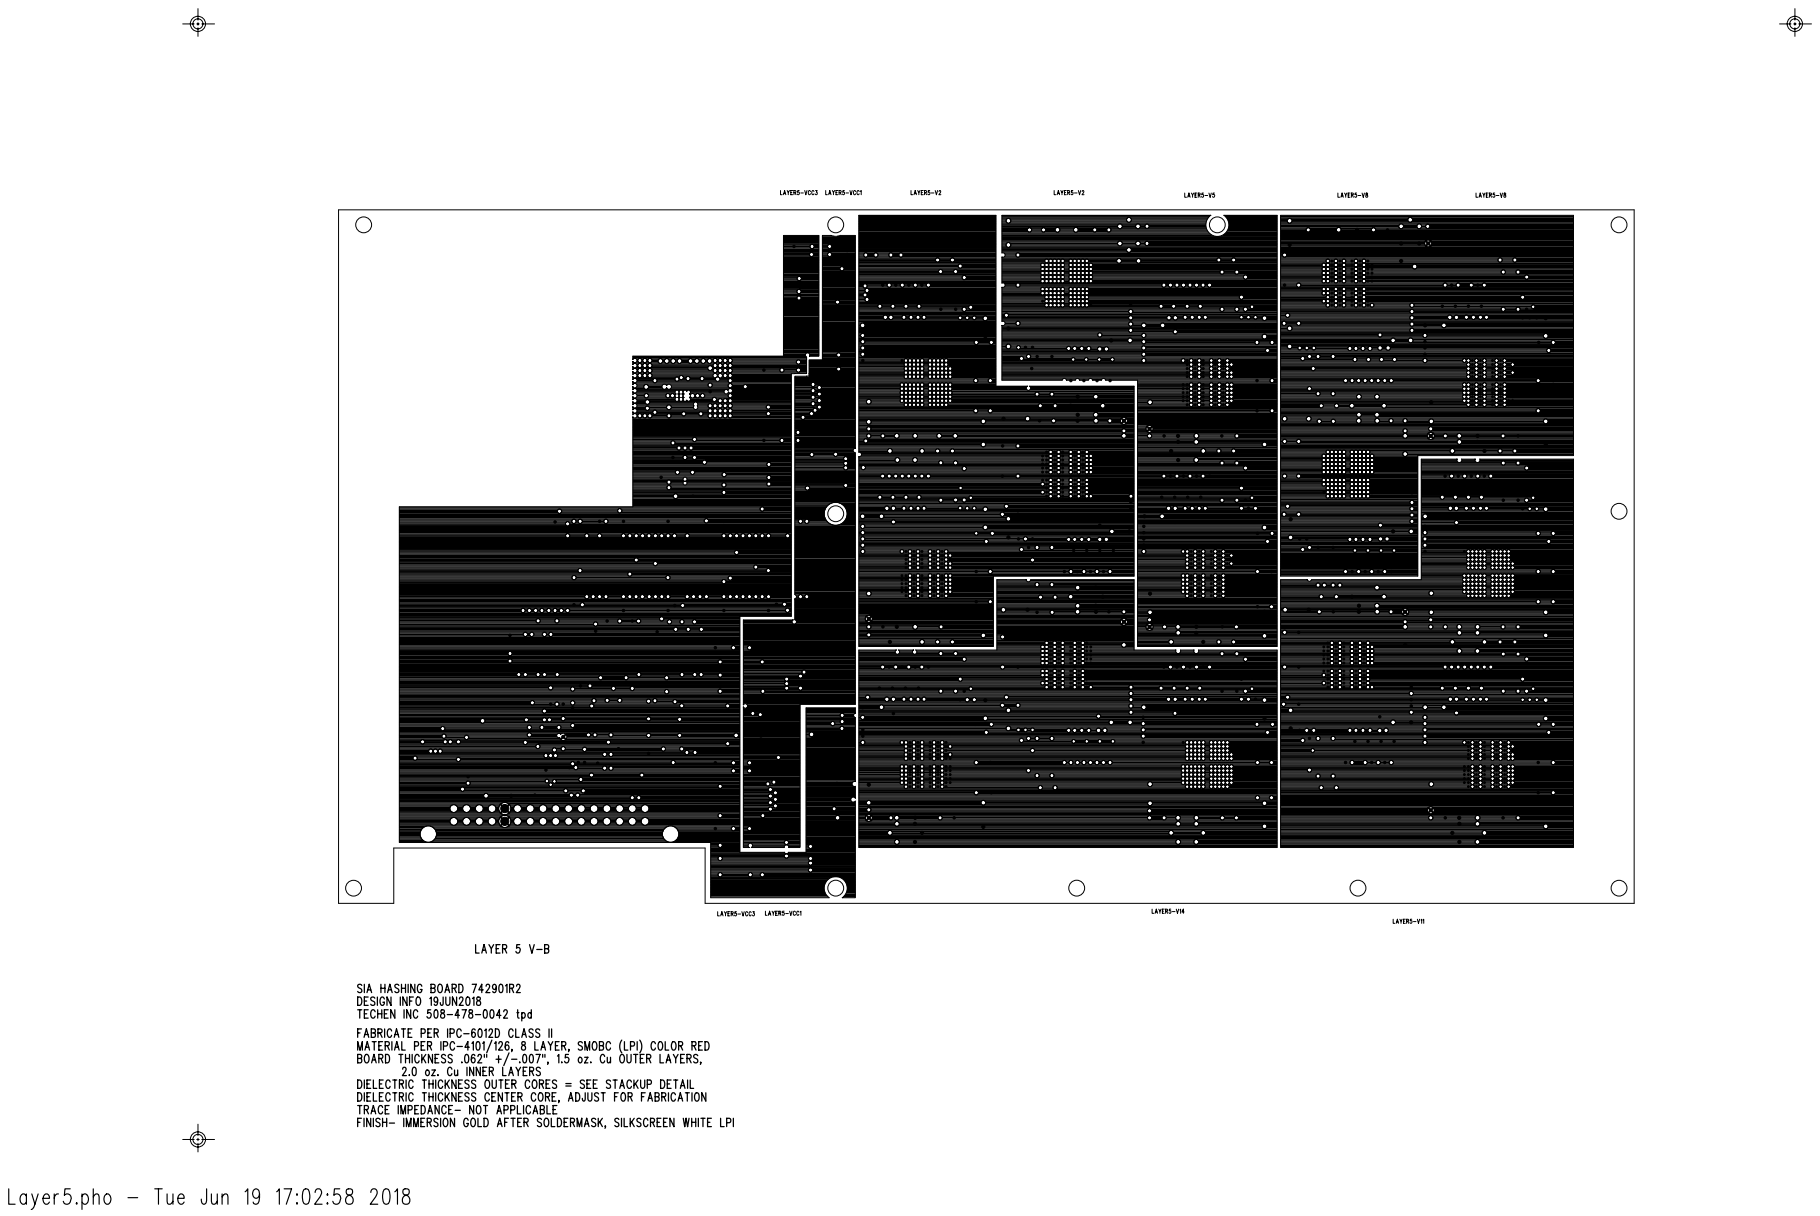
[picture p143: page 8]

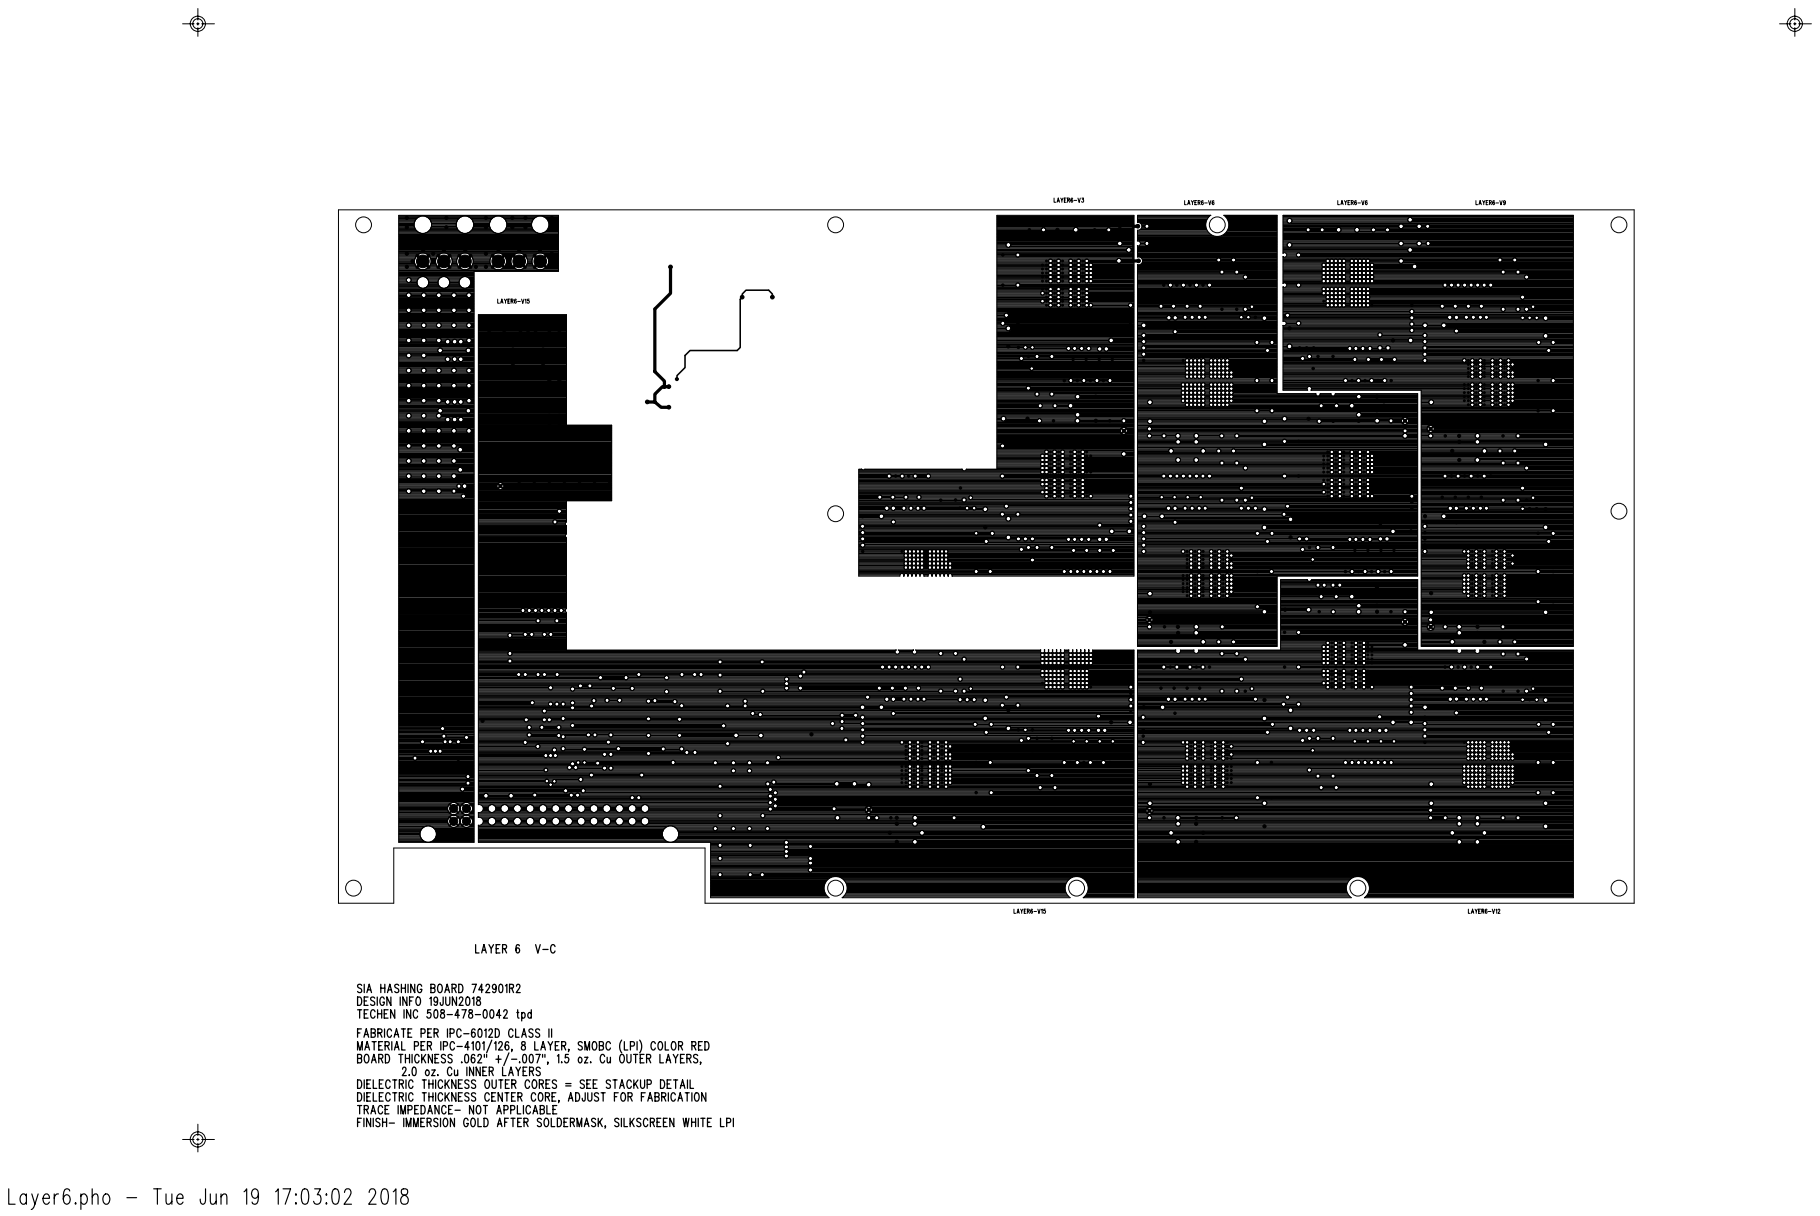
[picture p144: page 9]

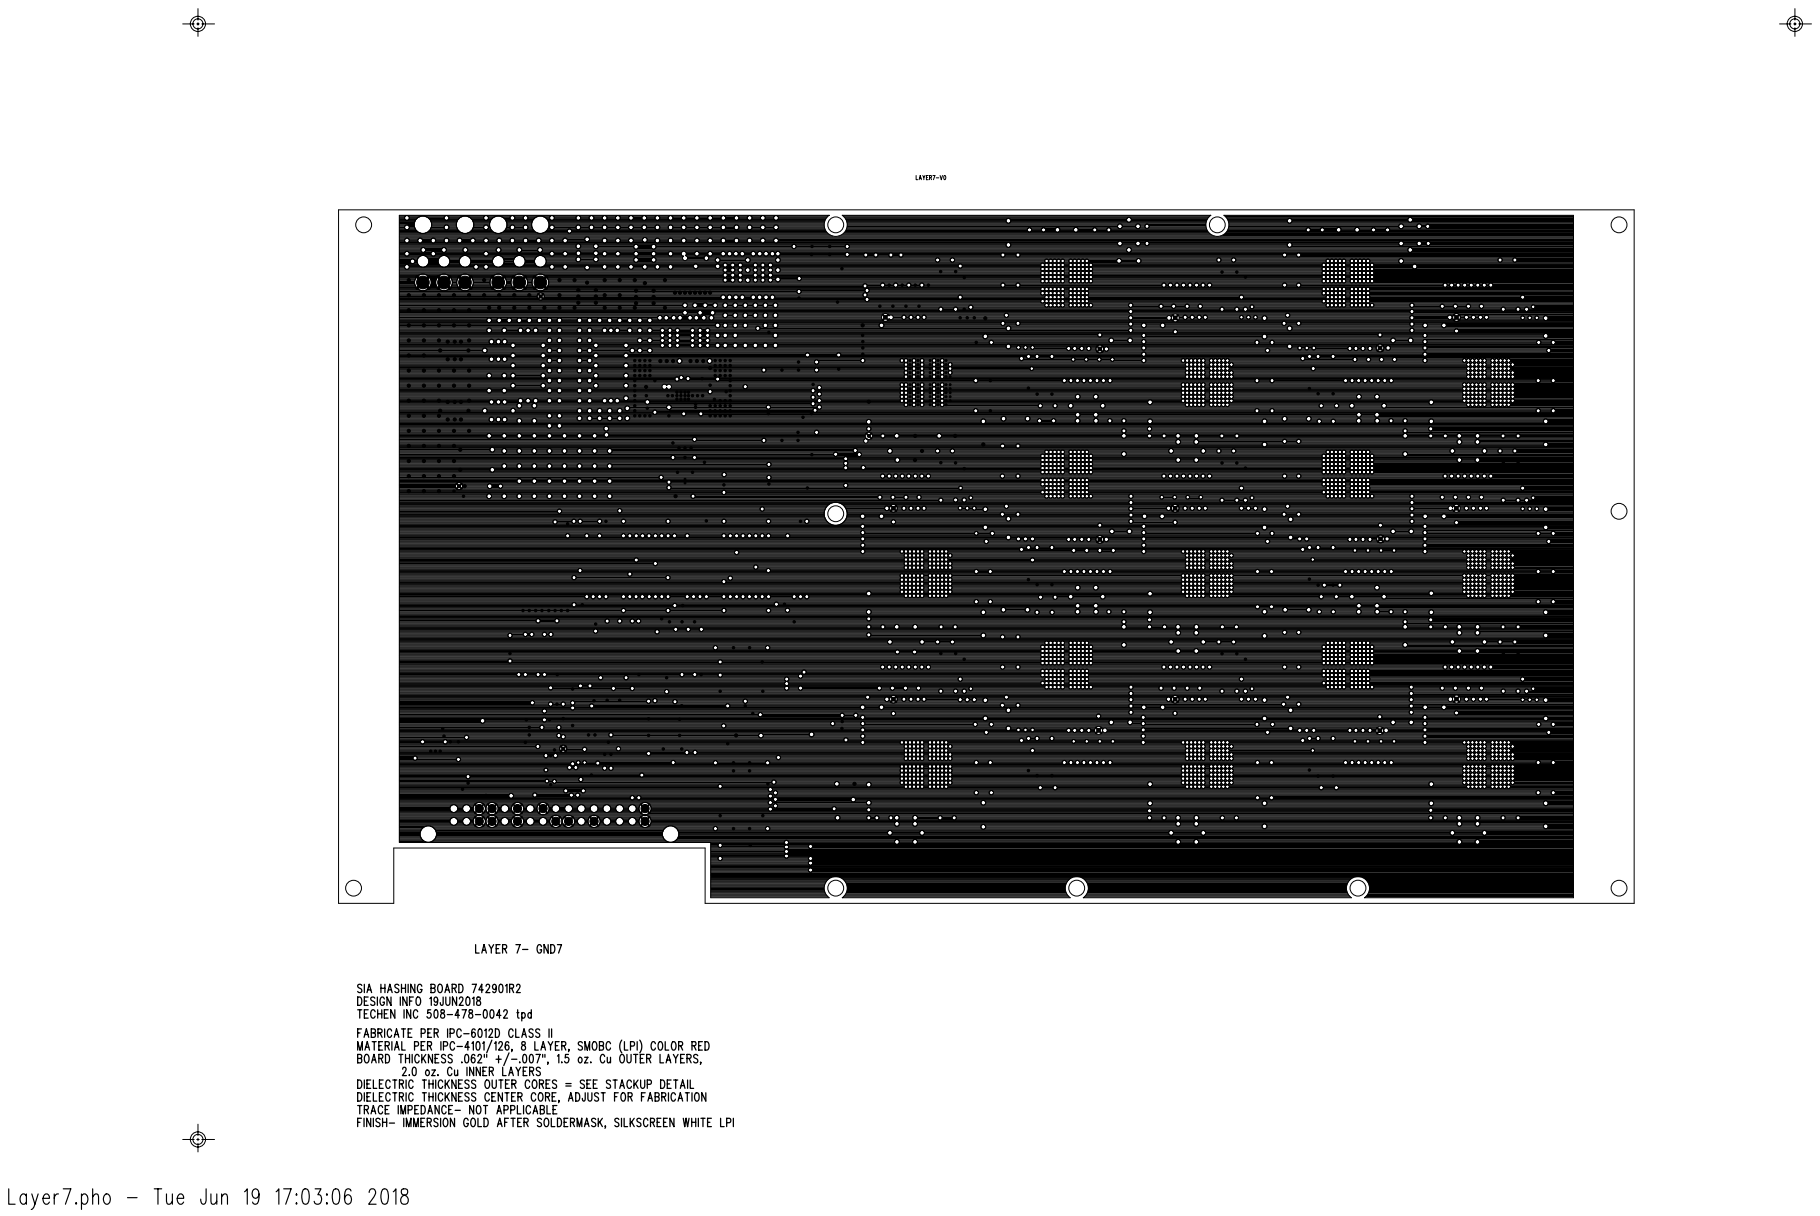
[picture p145: page 10]

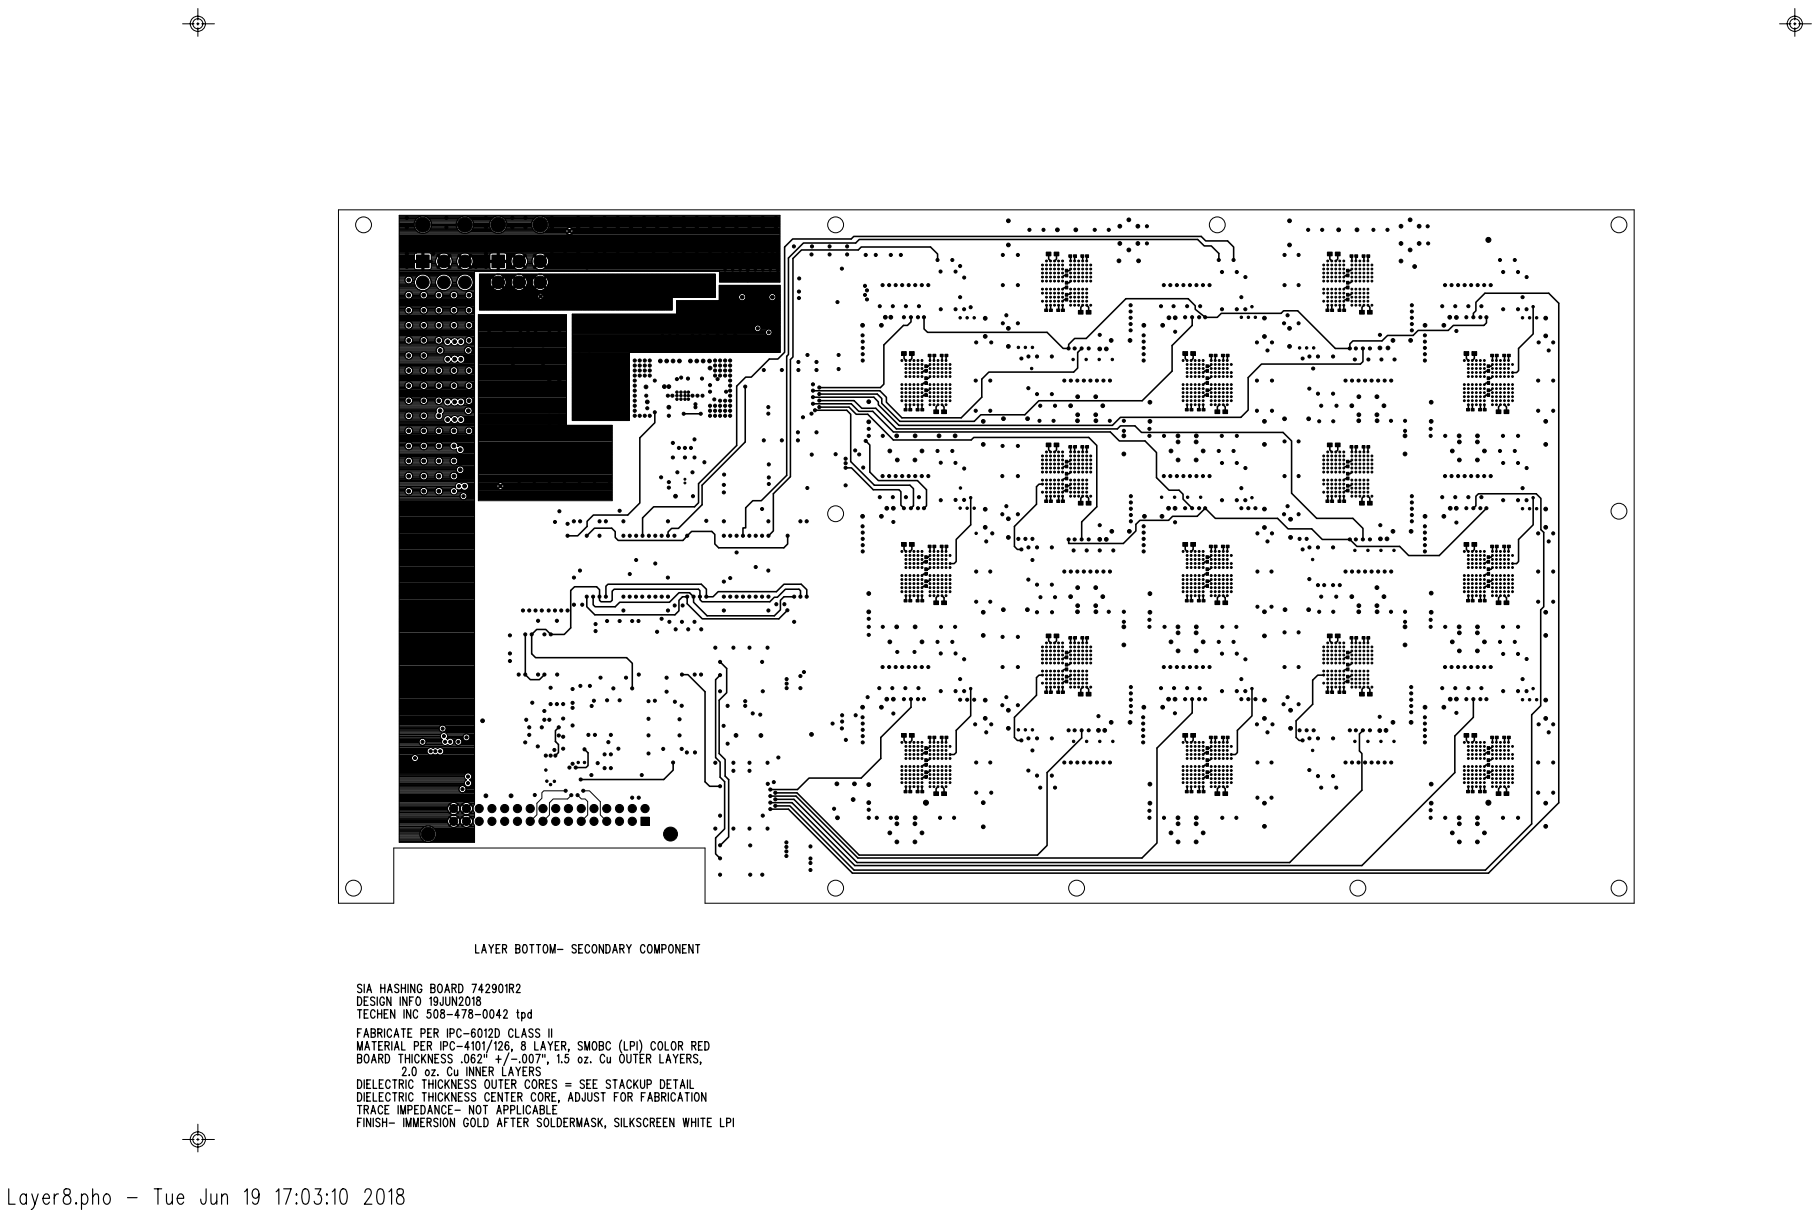
[picture p146: page 11]

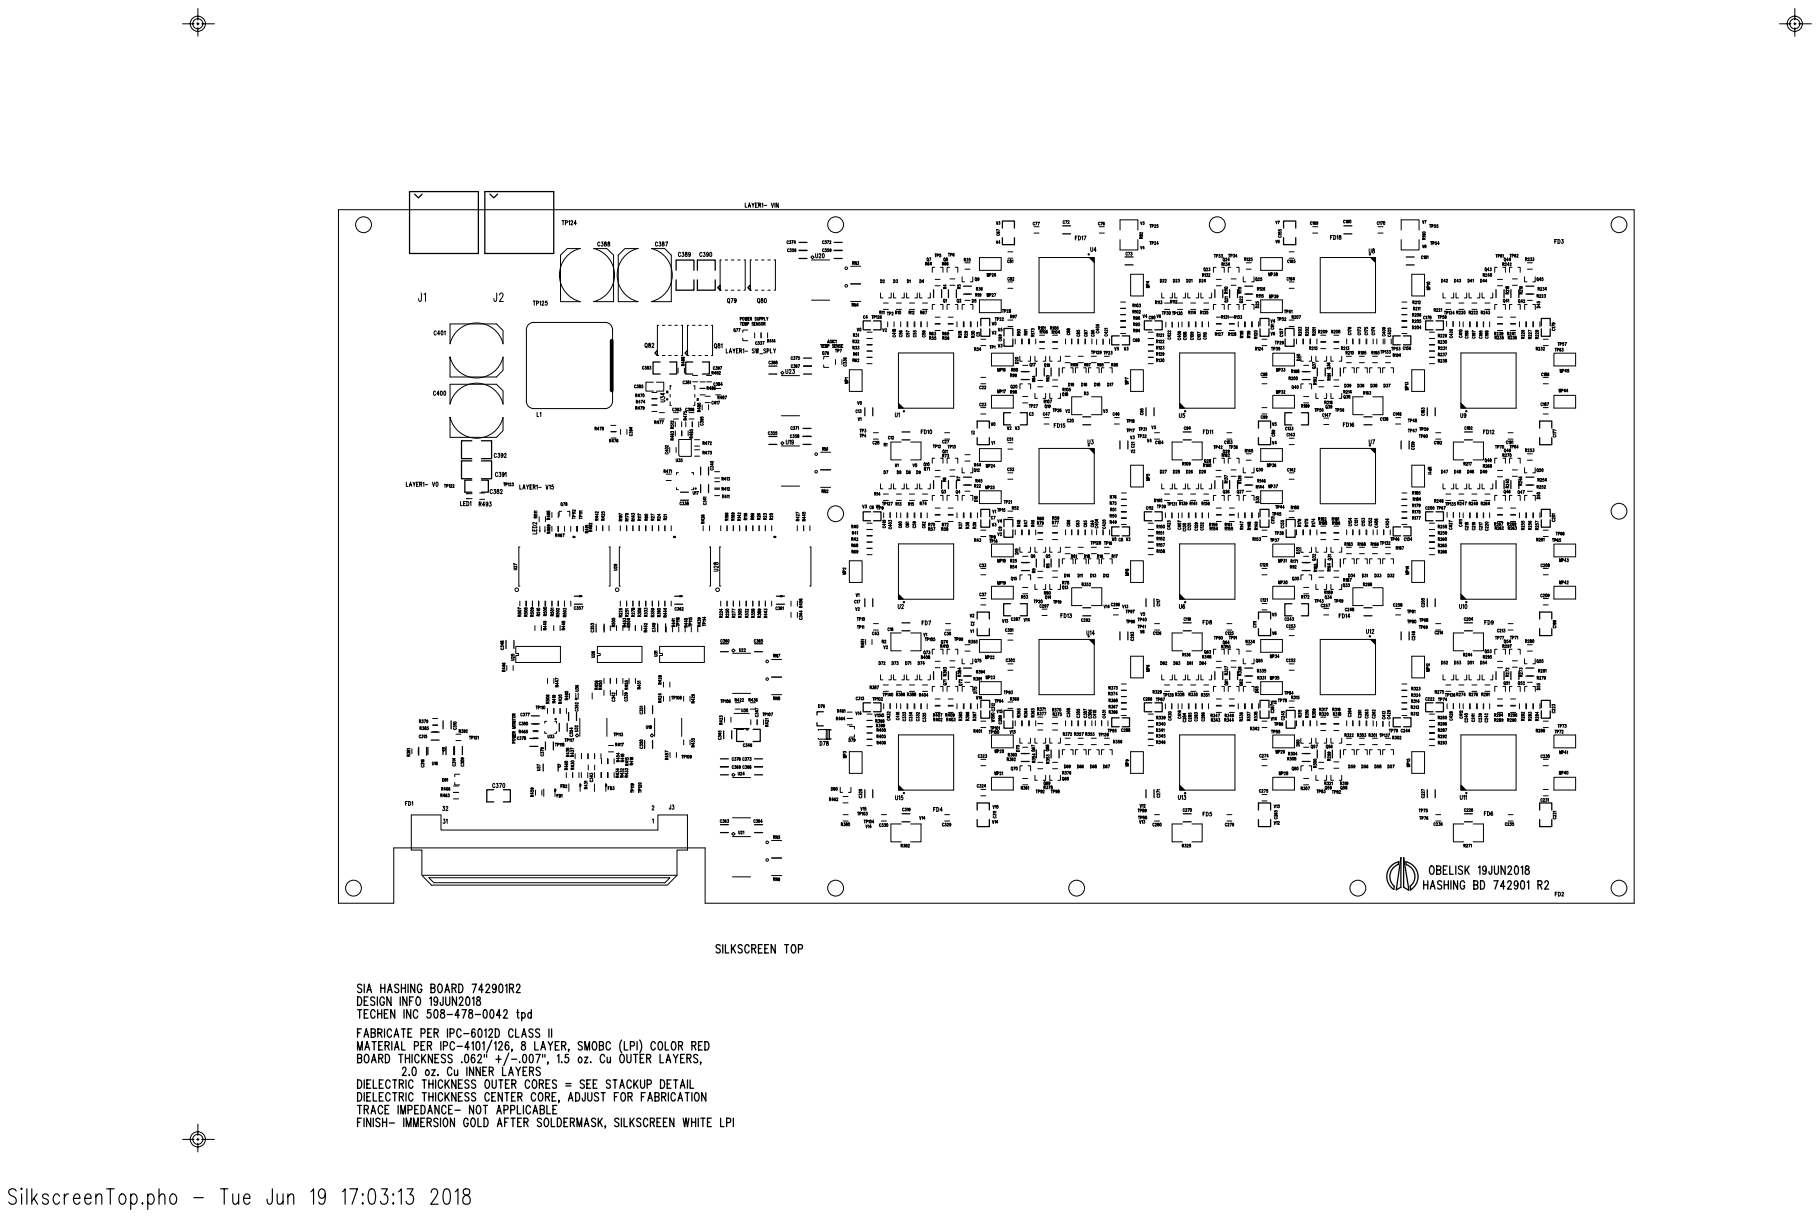
[picture p147: page 12]

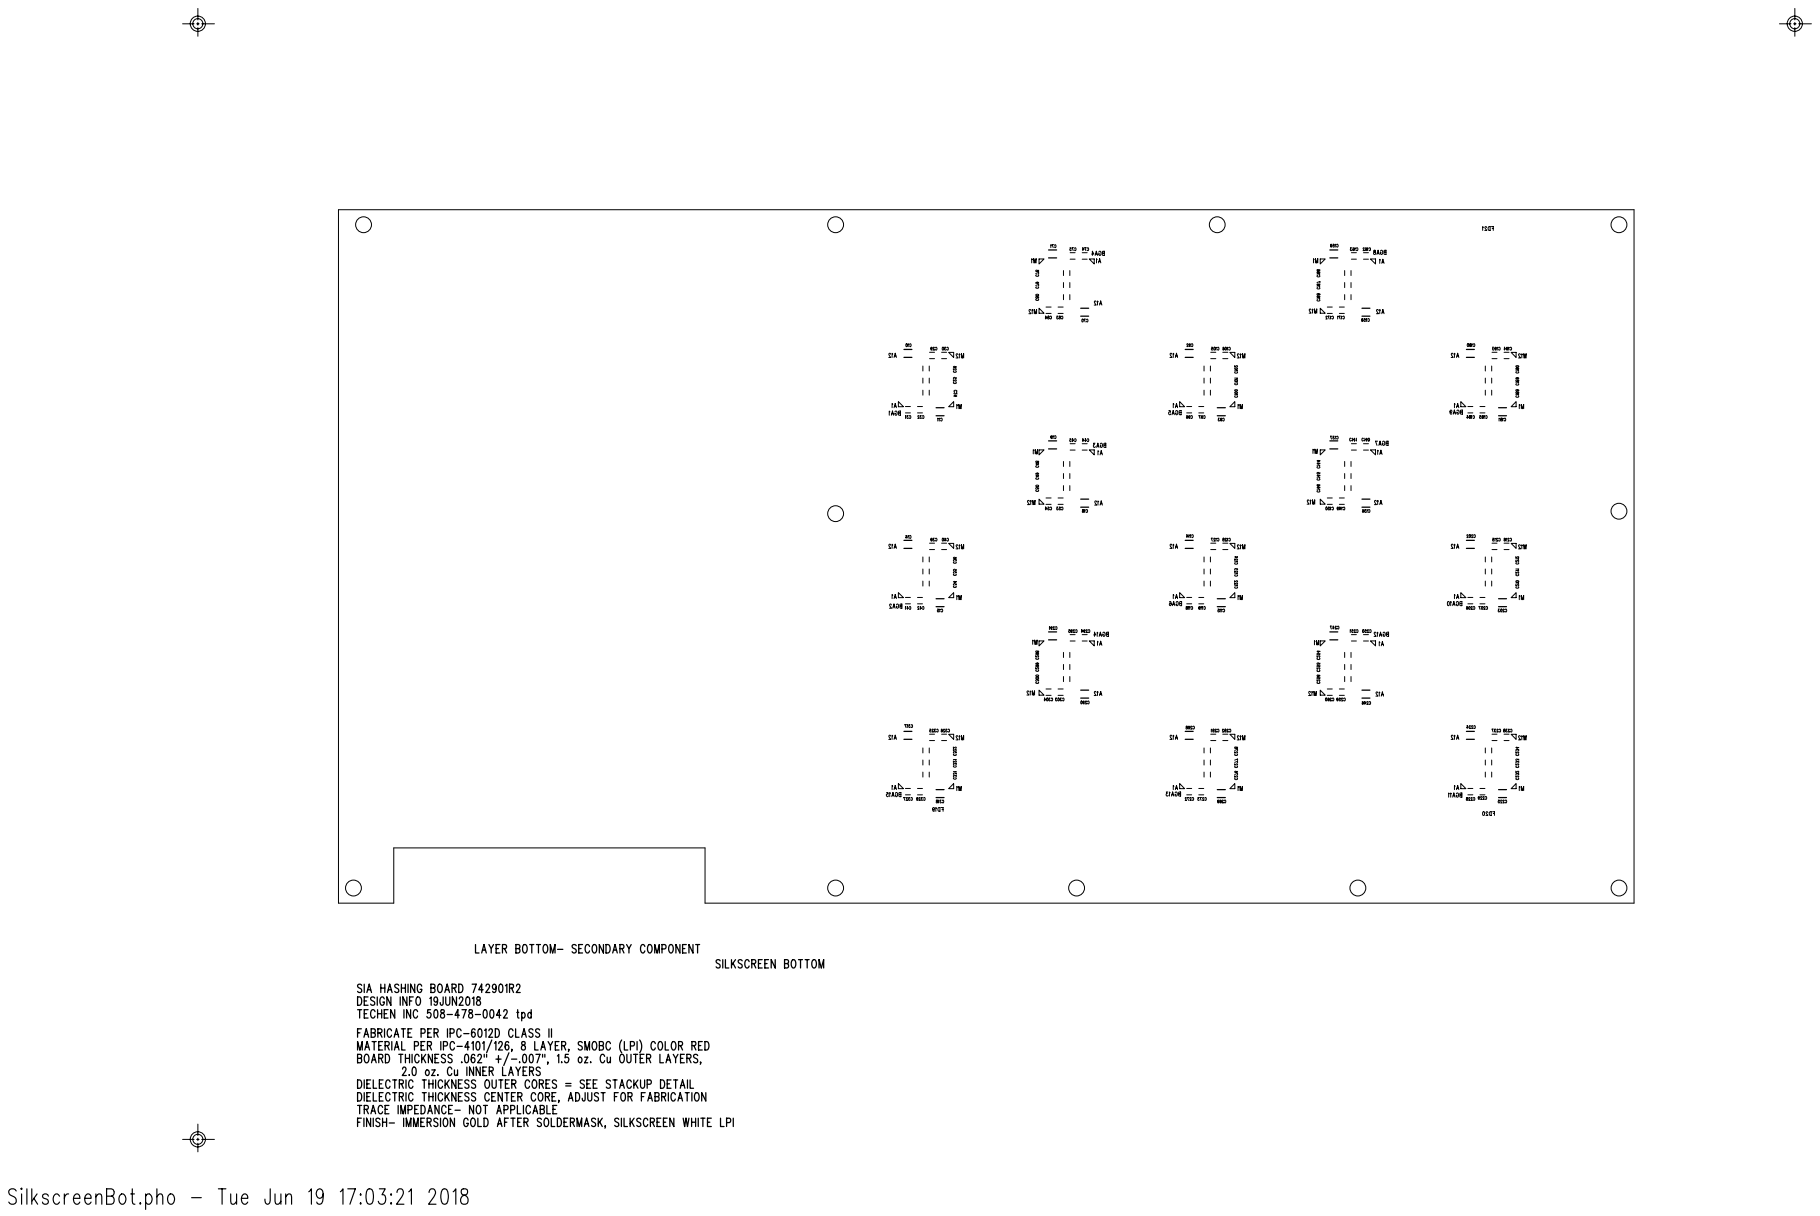
[picture p148: page 13]

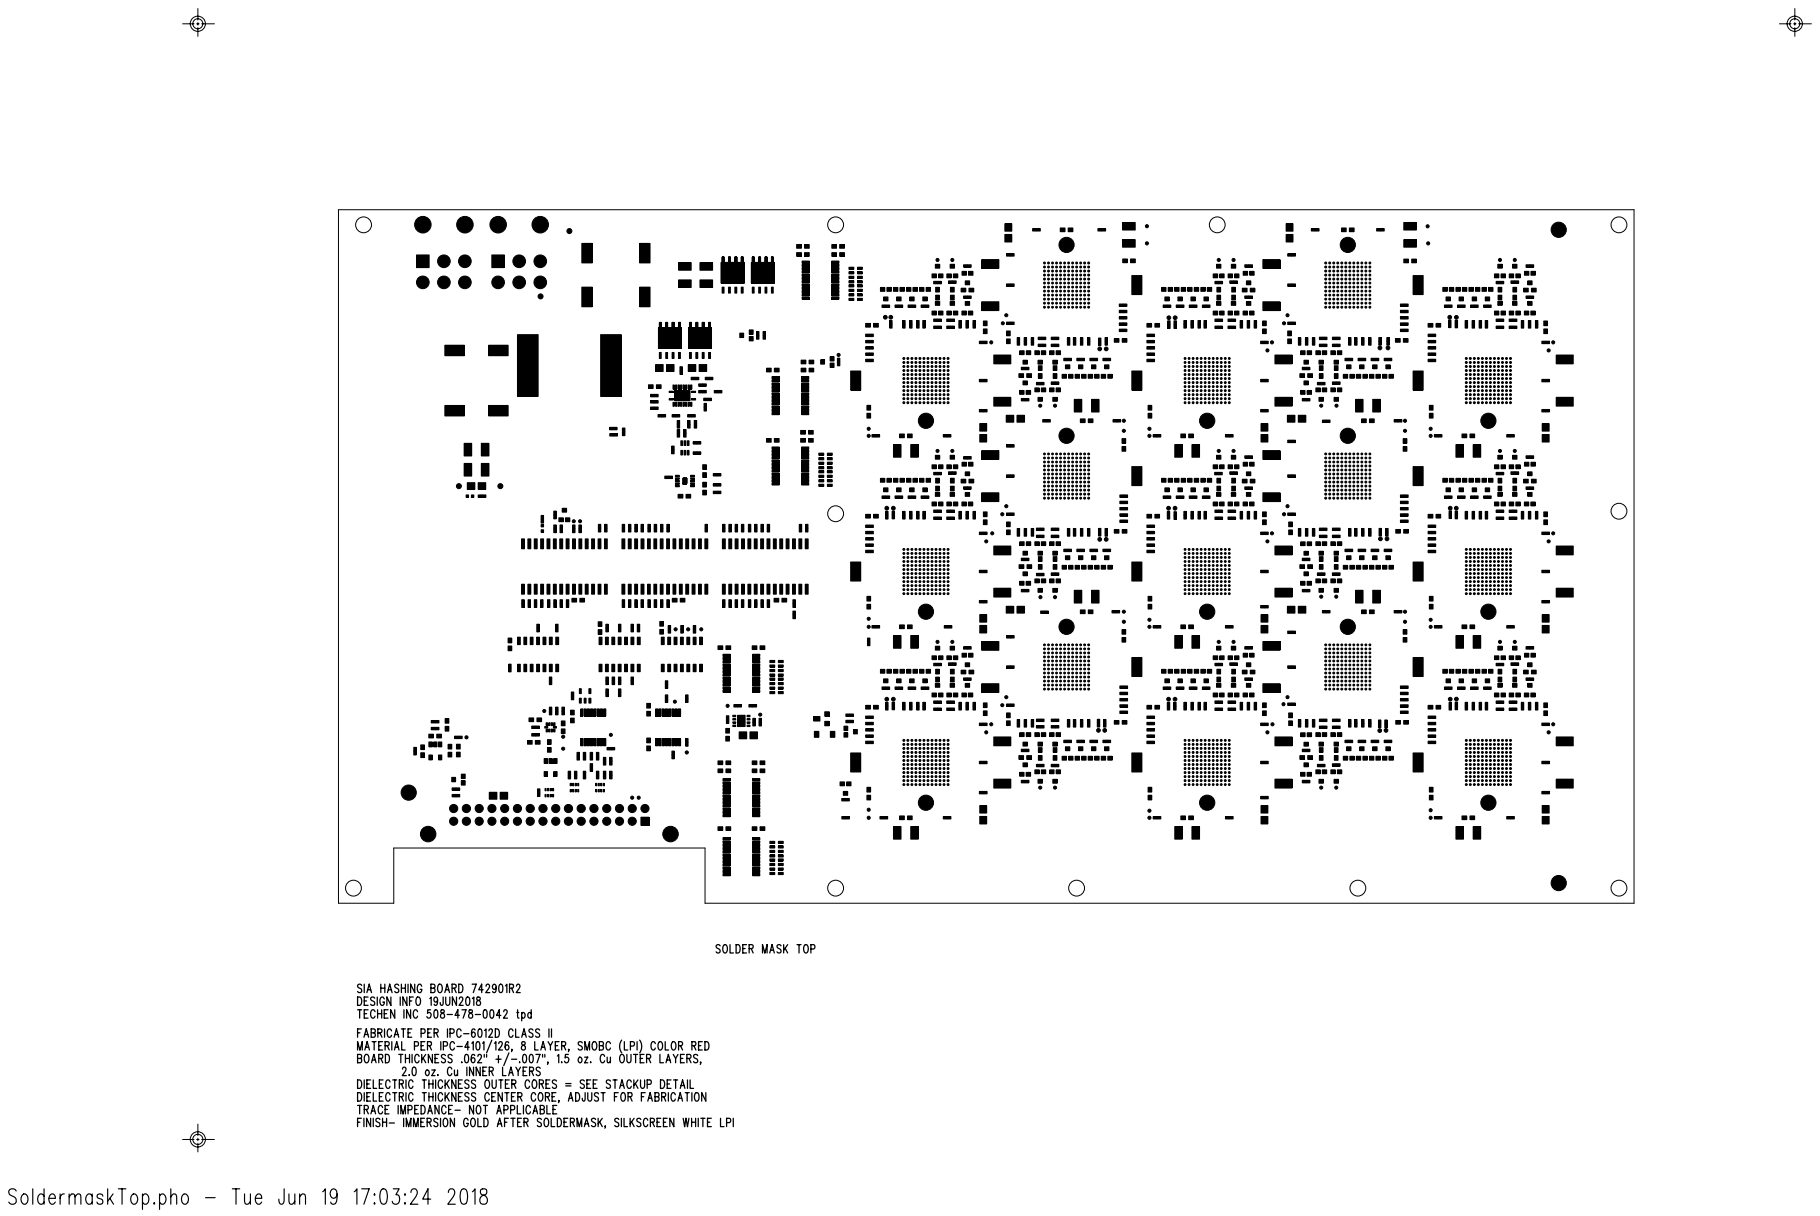
[picture p149: page 14]

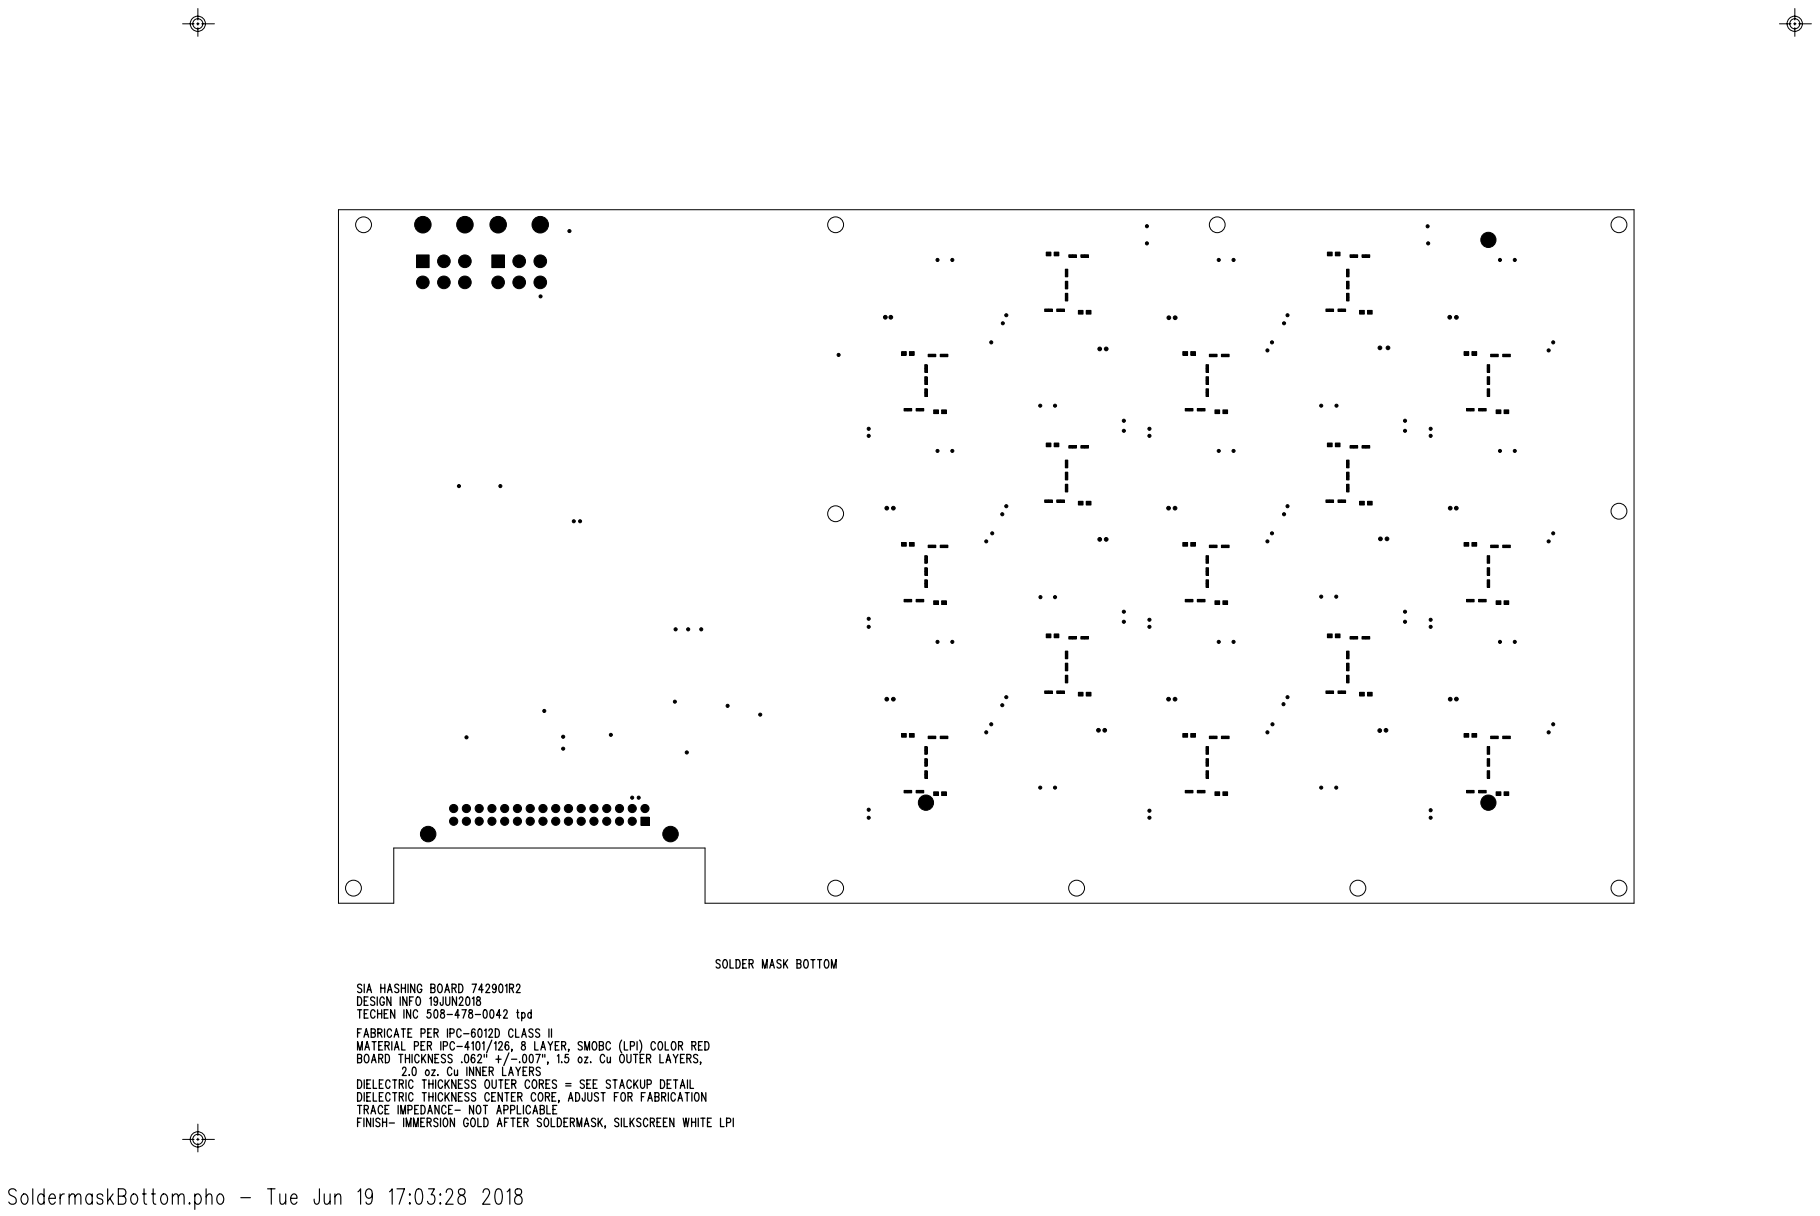
[picture p150: page 15]

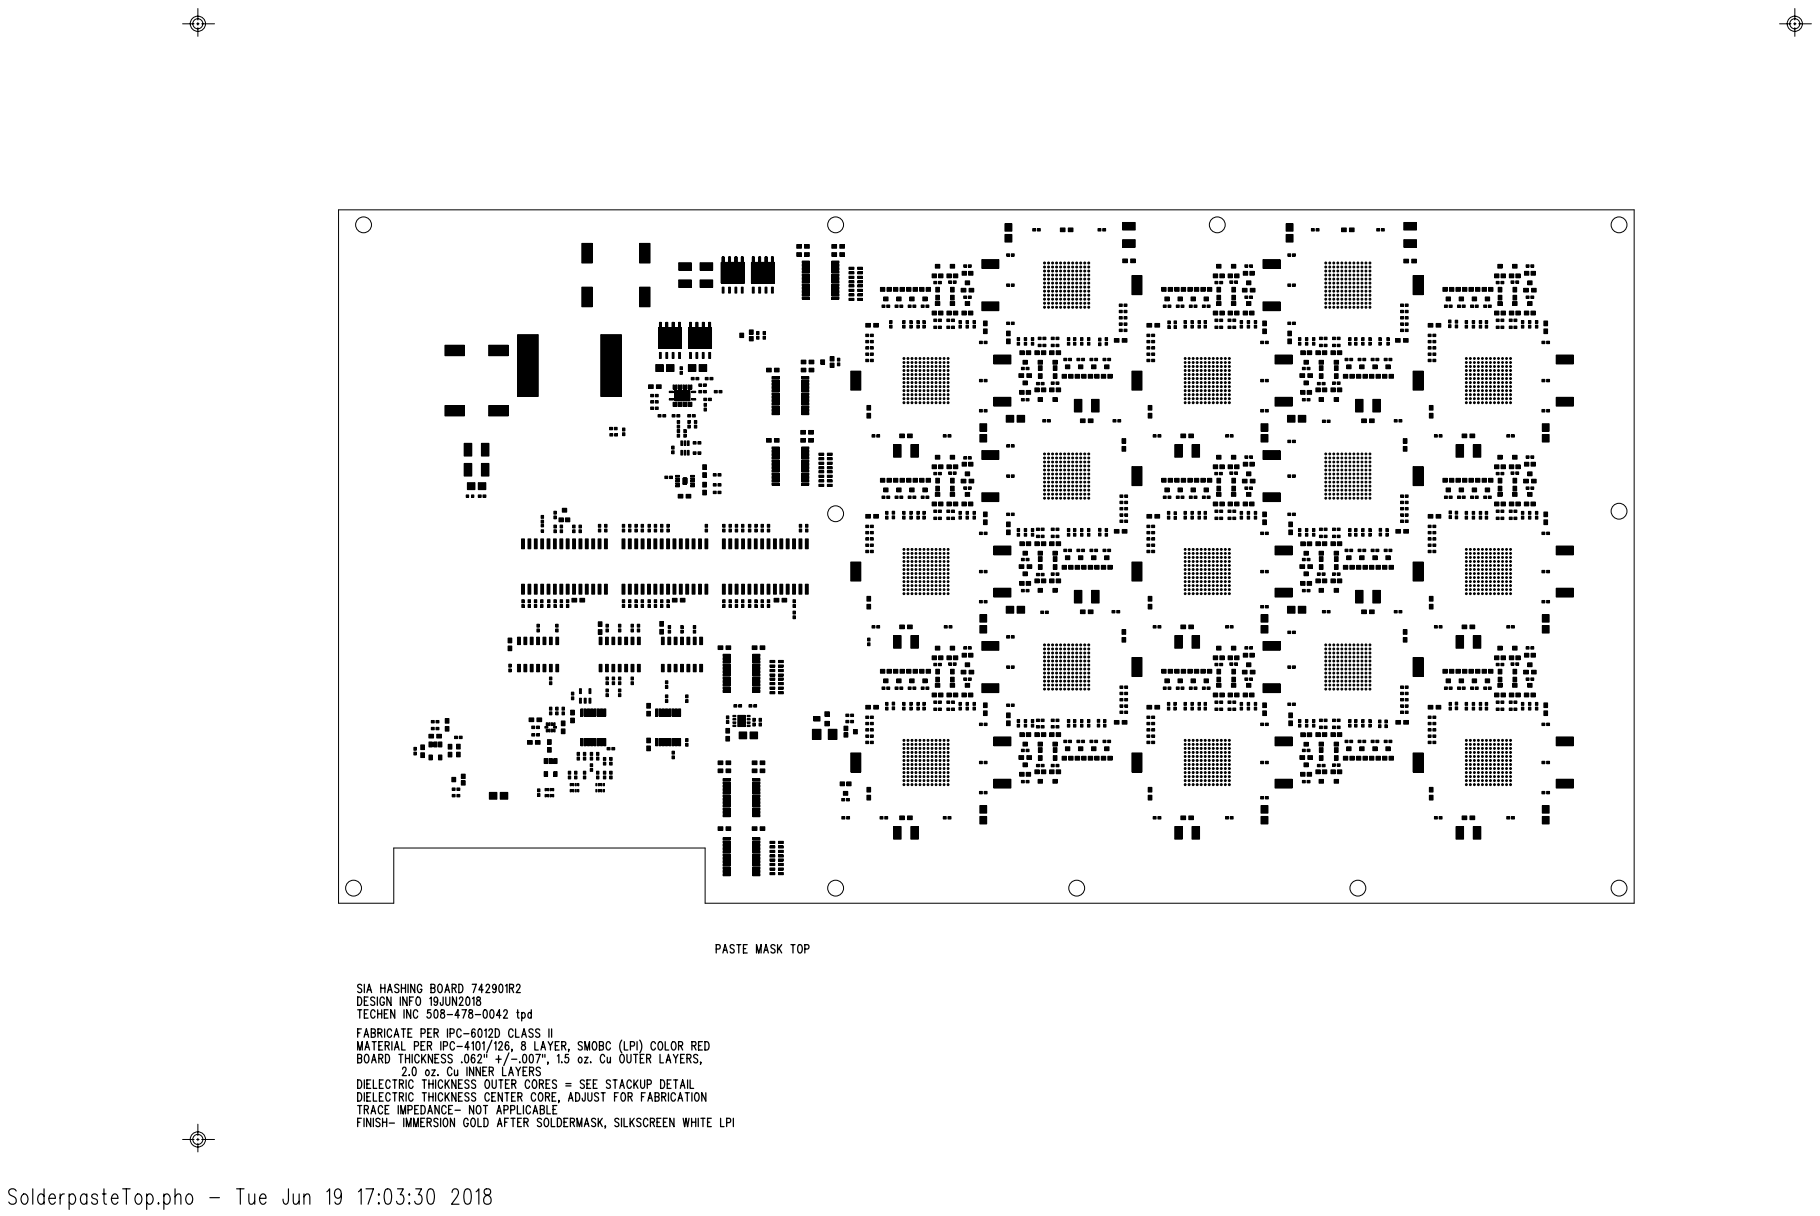
[picture p151: page 16]

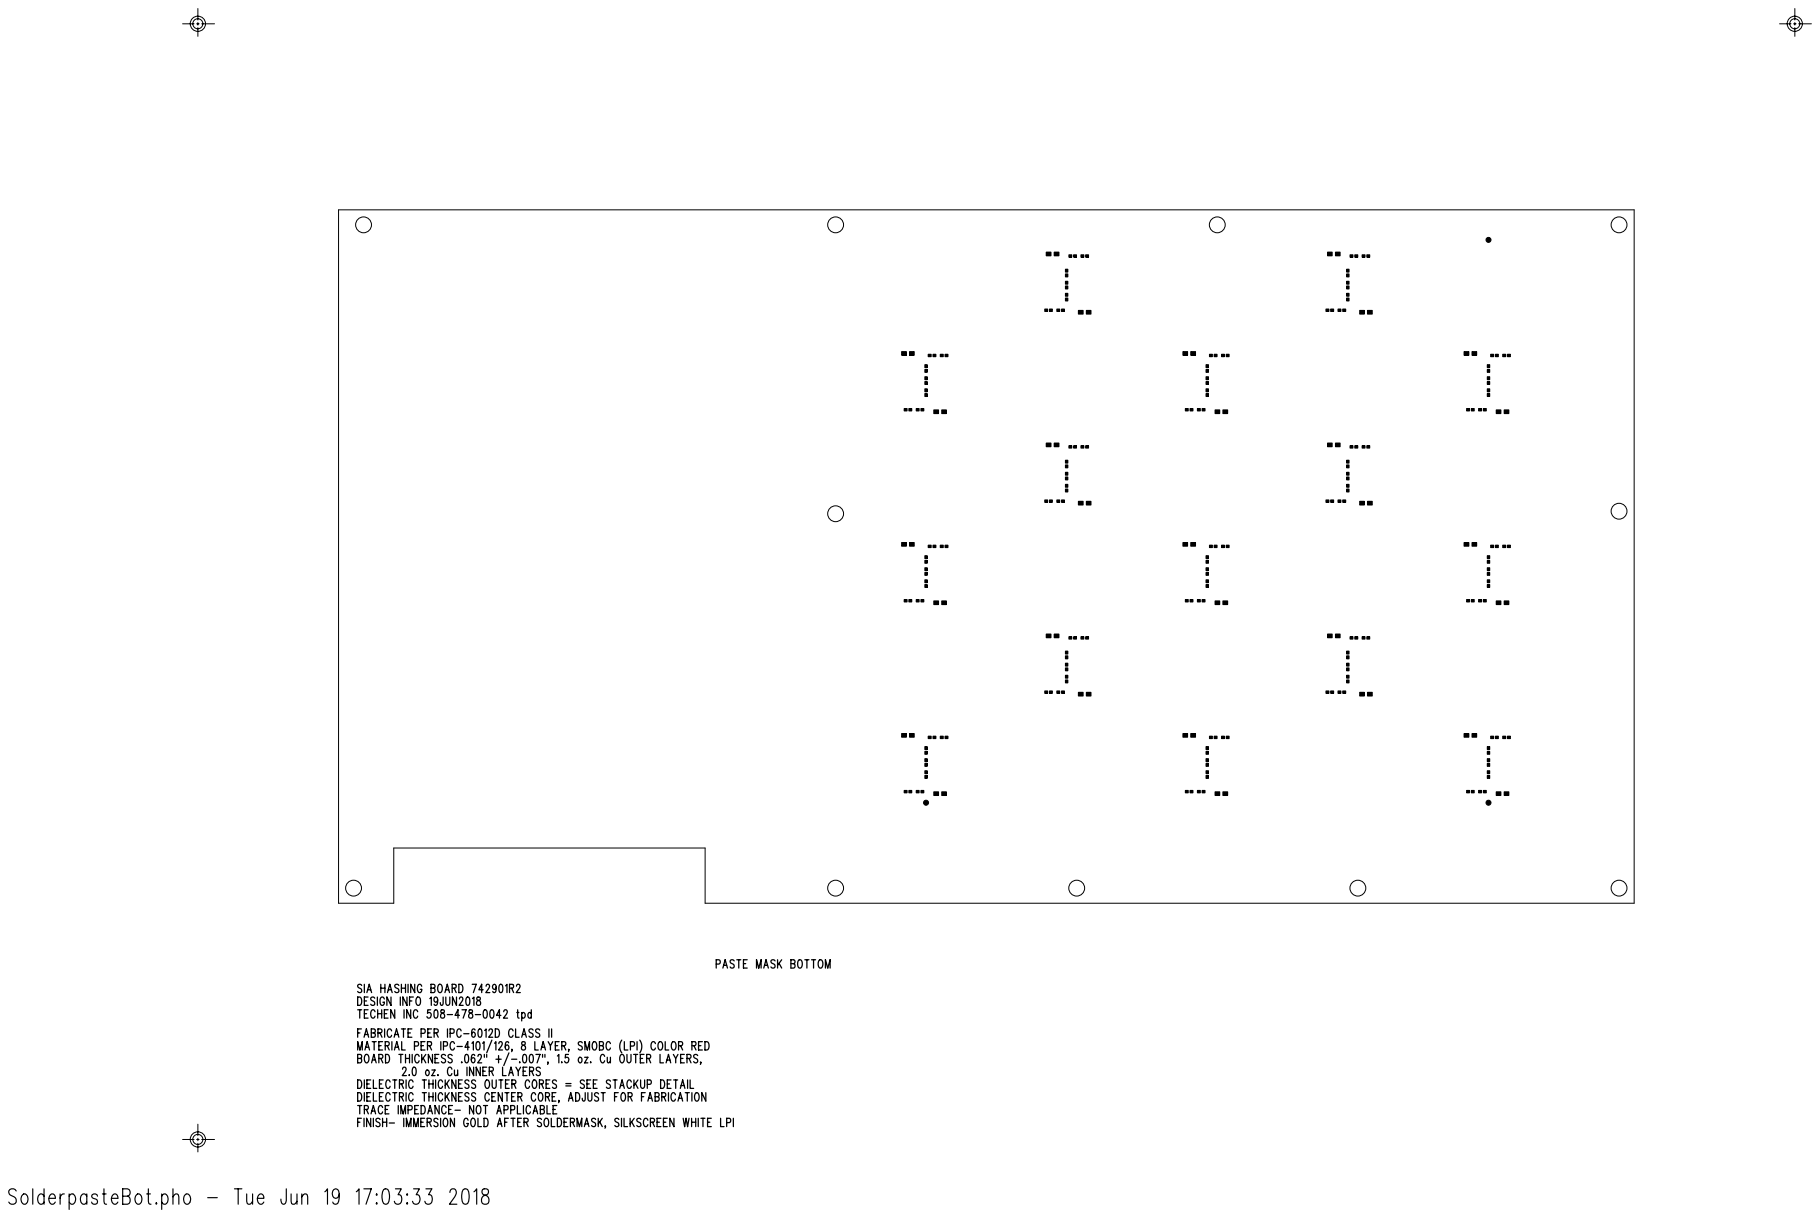
[picture p152: page 17]
