ObeliskInc/obelisk-hardware/Generation 2 Mining Hardware/Electrical/Hashing Board/docs/sc1b_091918.pdf

## Orchid Technologies Engineering & Consulting, Inc. - Confidential

# ORCHID TECHNOLOGIES

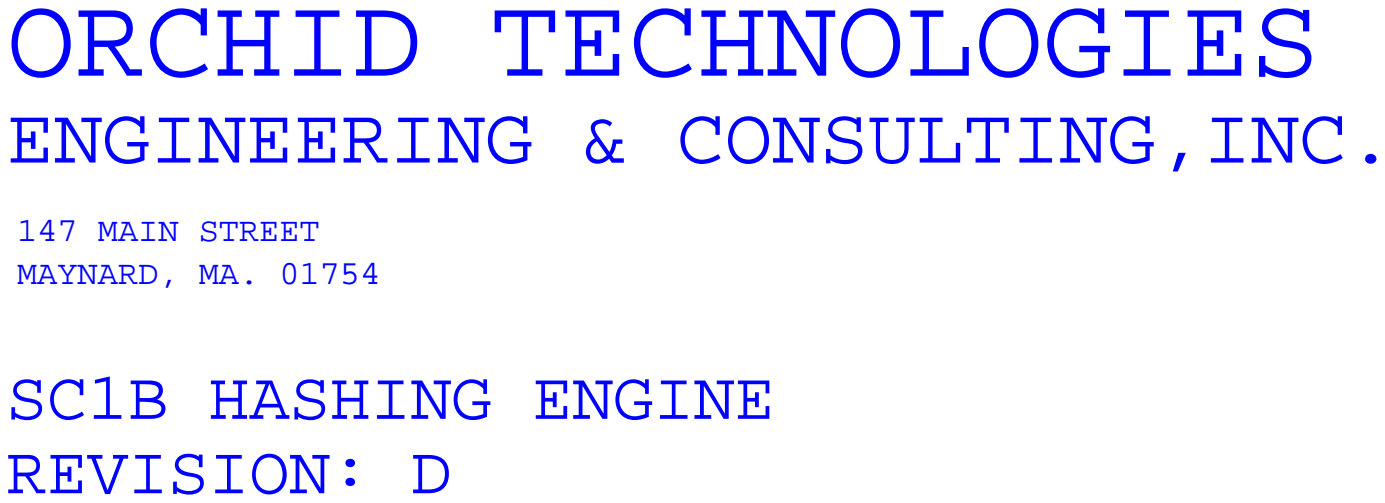
[picture p153: page 1]
REVISION: D; SC1B HASHING ENGINE; 147 MAIN STREET MAYNARD, MA. 01754; SEPTEMBER 19, 2018; Size; Document Number; Rev; Date:; Sheet

ENGINEERING & CONSULTING,INC.

Orchid Technologies Engineering and Consulting, Inc.
Title
SC1B HASHING ENGINE

# ASIC 0A : ADDRESS 00H

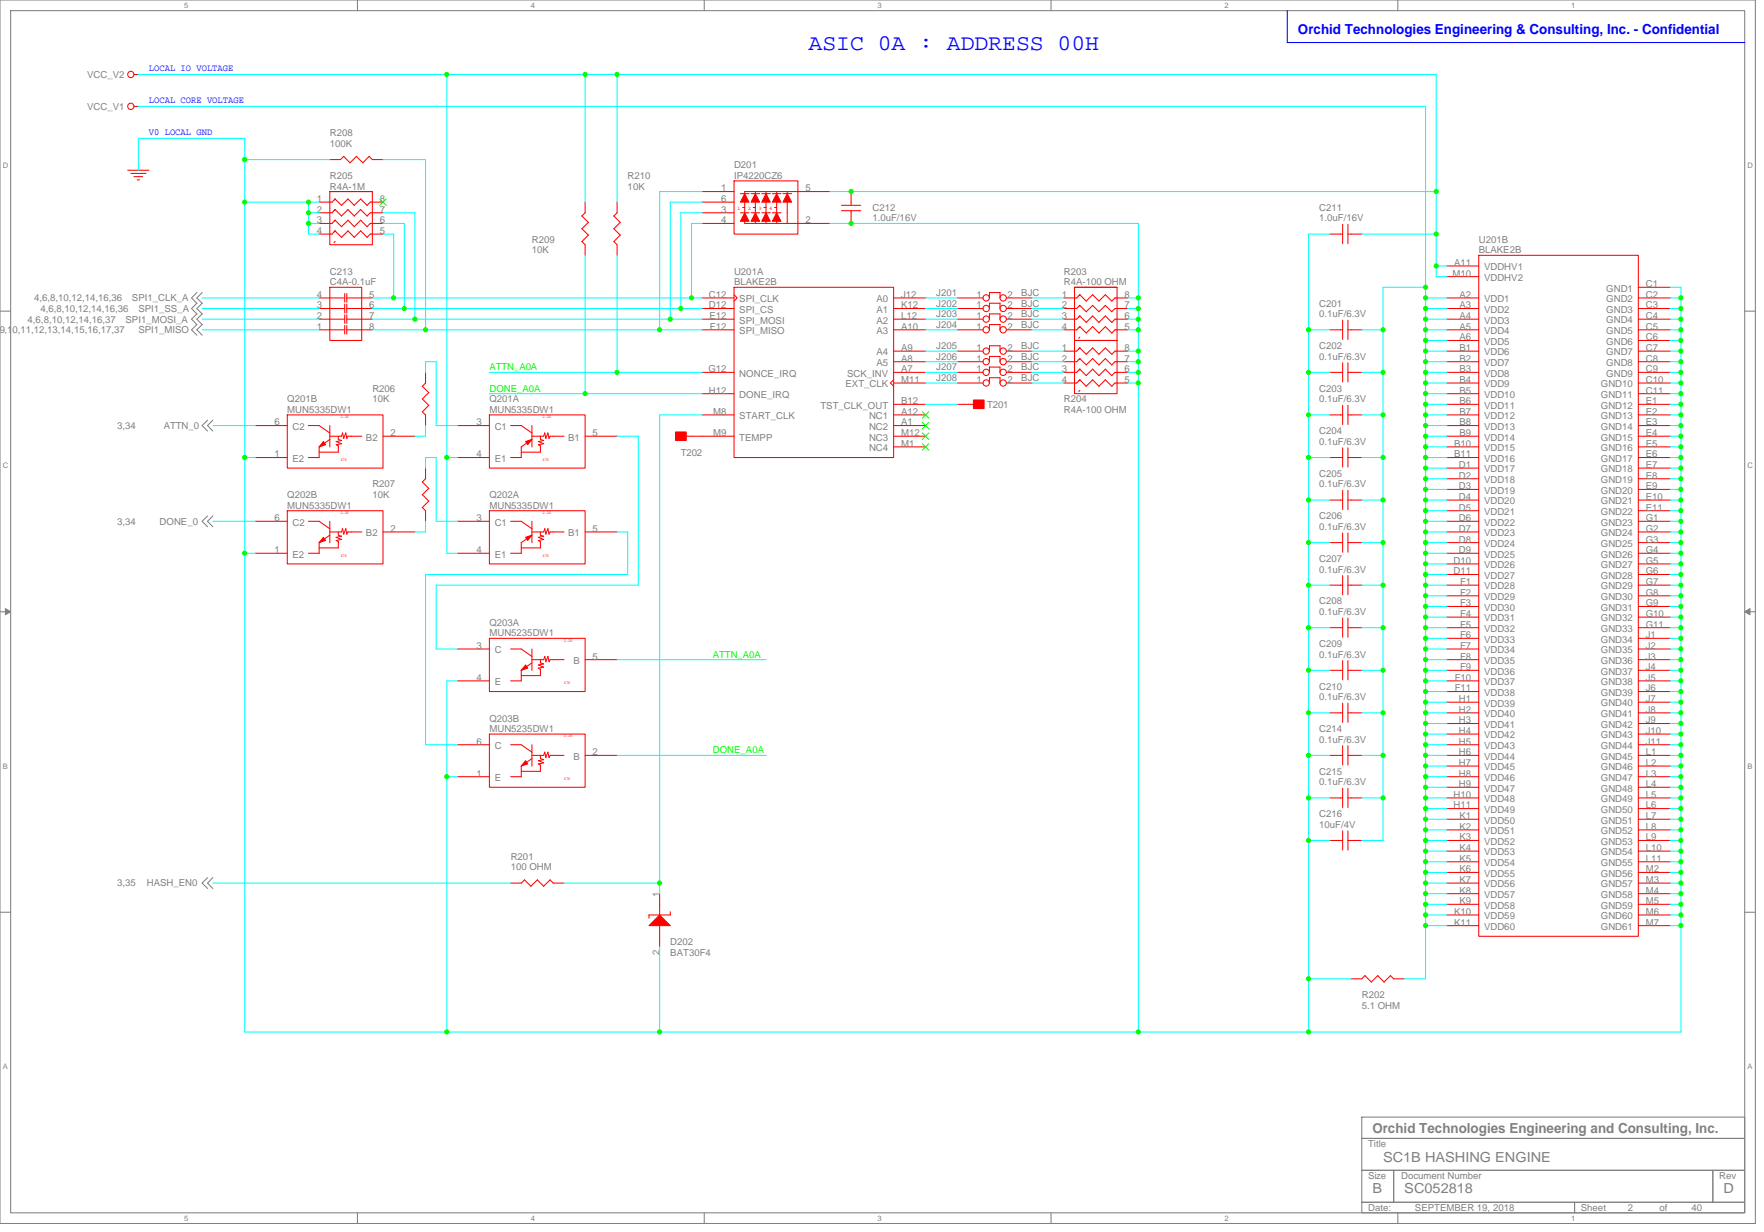
[picture p154: page 2]

Orchid Technologies Engineering and Consulting, Inc.

# ASIC 0B : ADDRESS 20H

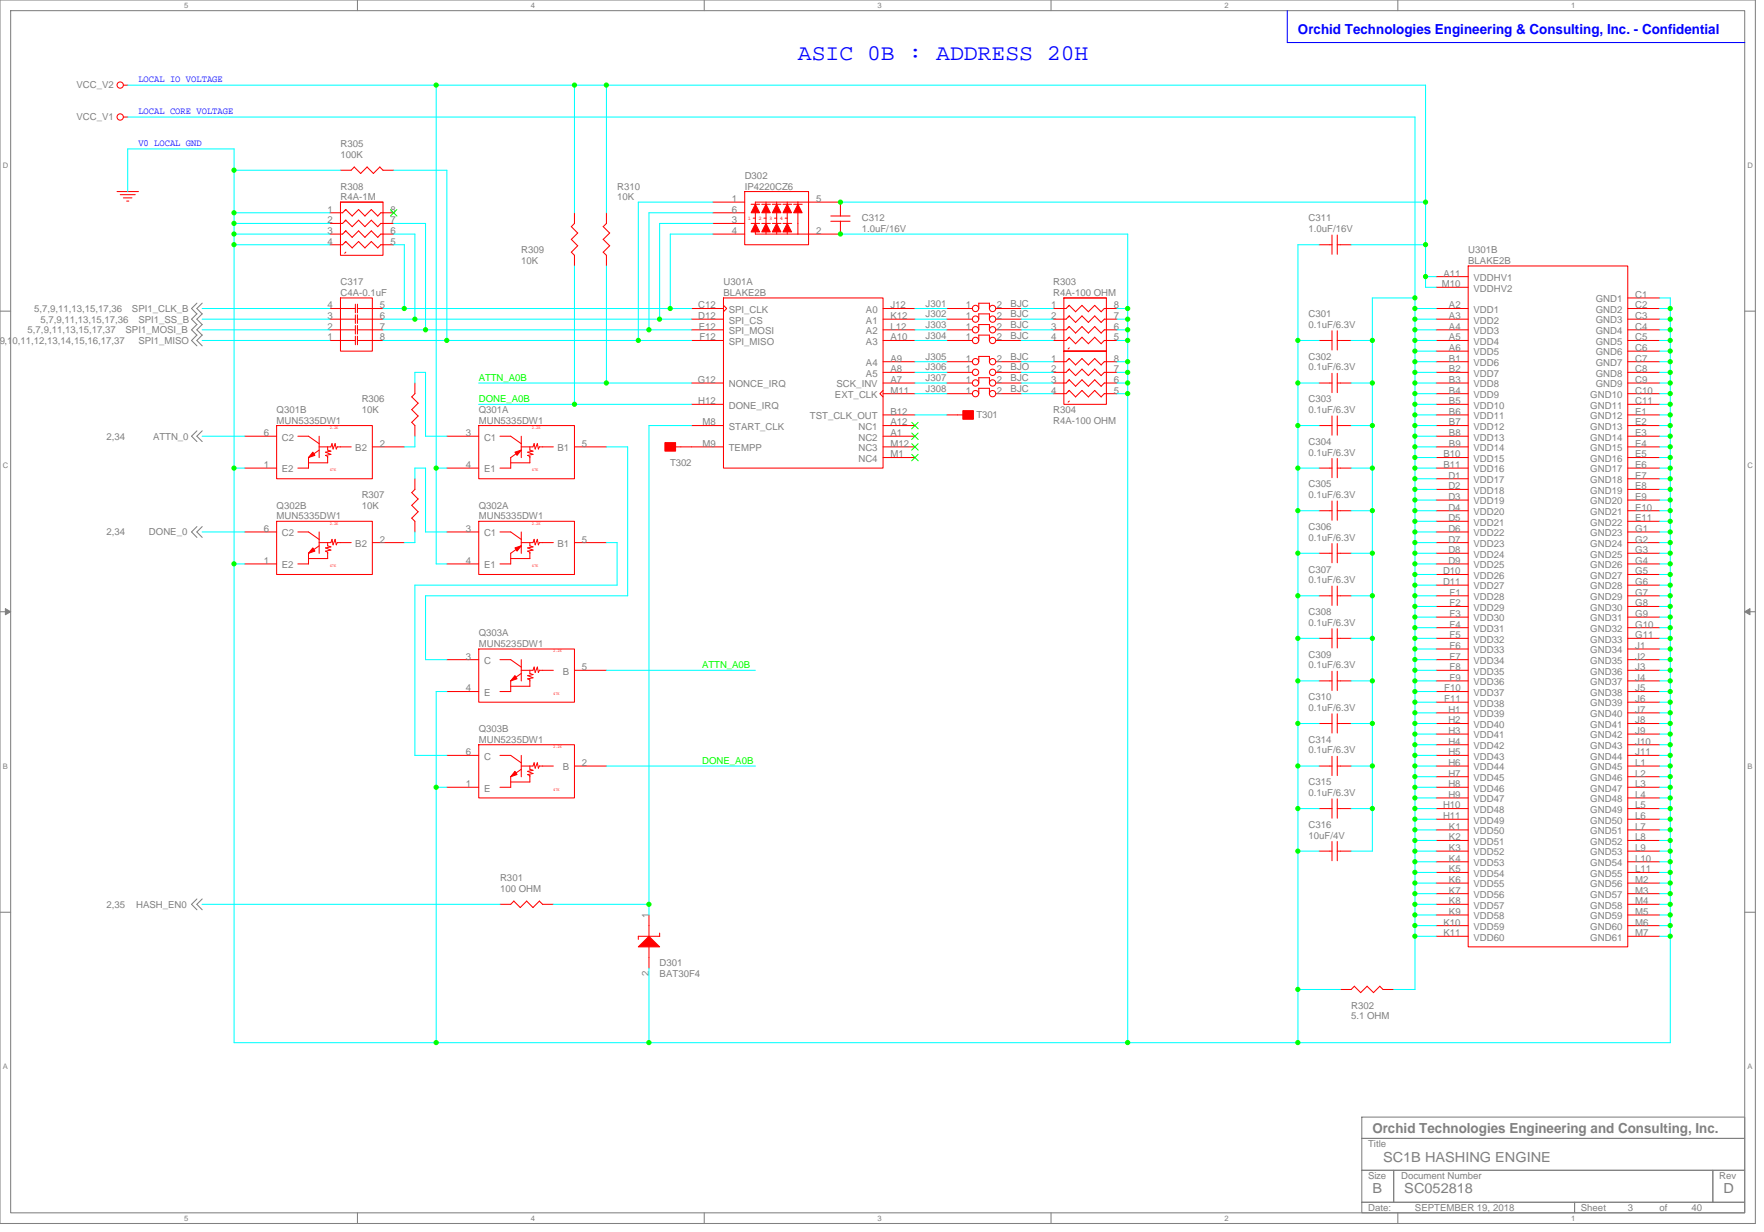
[picture p155: page 3]

Orchid Technologies Engineering and Consulting, Inc.

# ASIC 1A : ADDRESS 01H

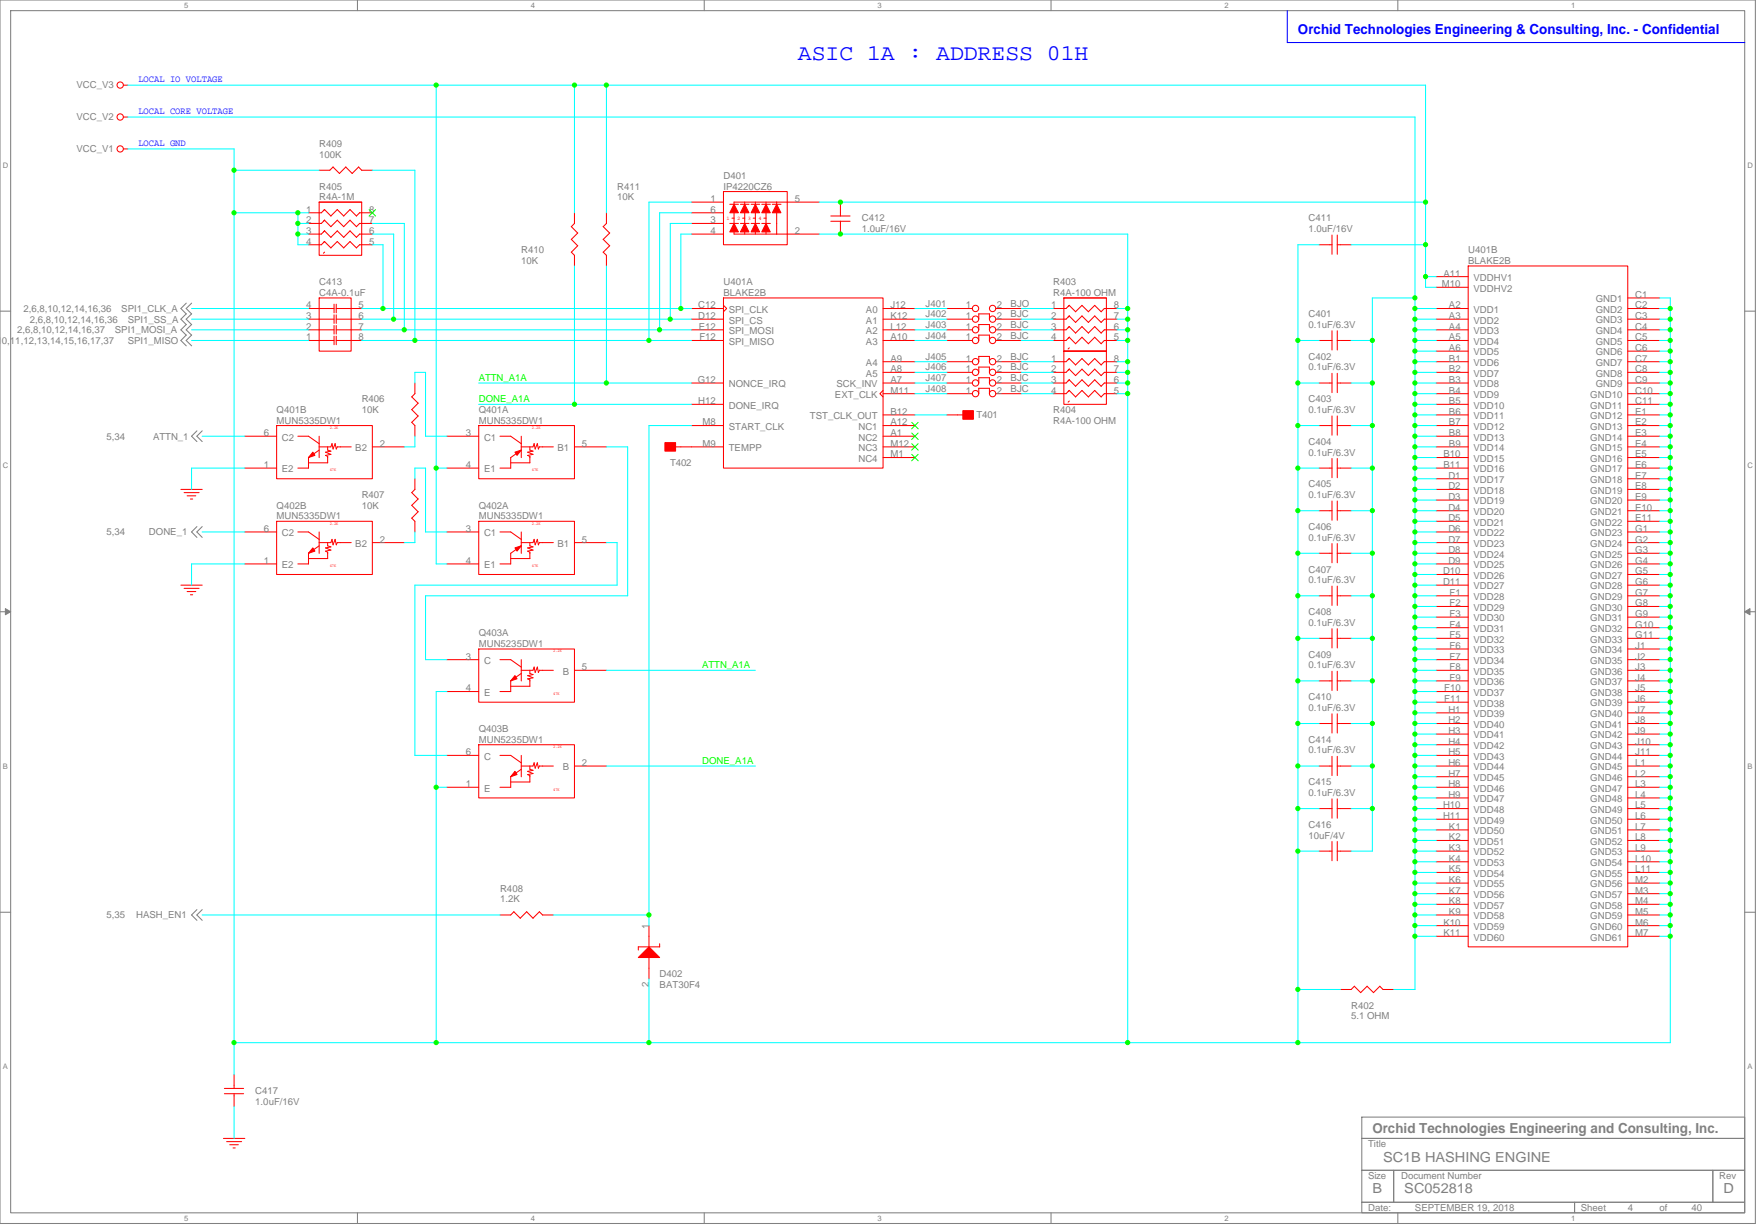
[picture p156: page 4]

Orchid Technologies Engineering and Consulting, Inc.

# ASIC 1B : ADDRESS 21H

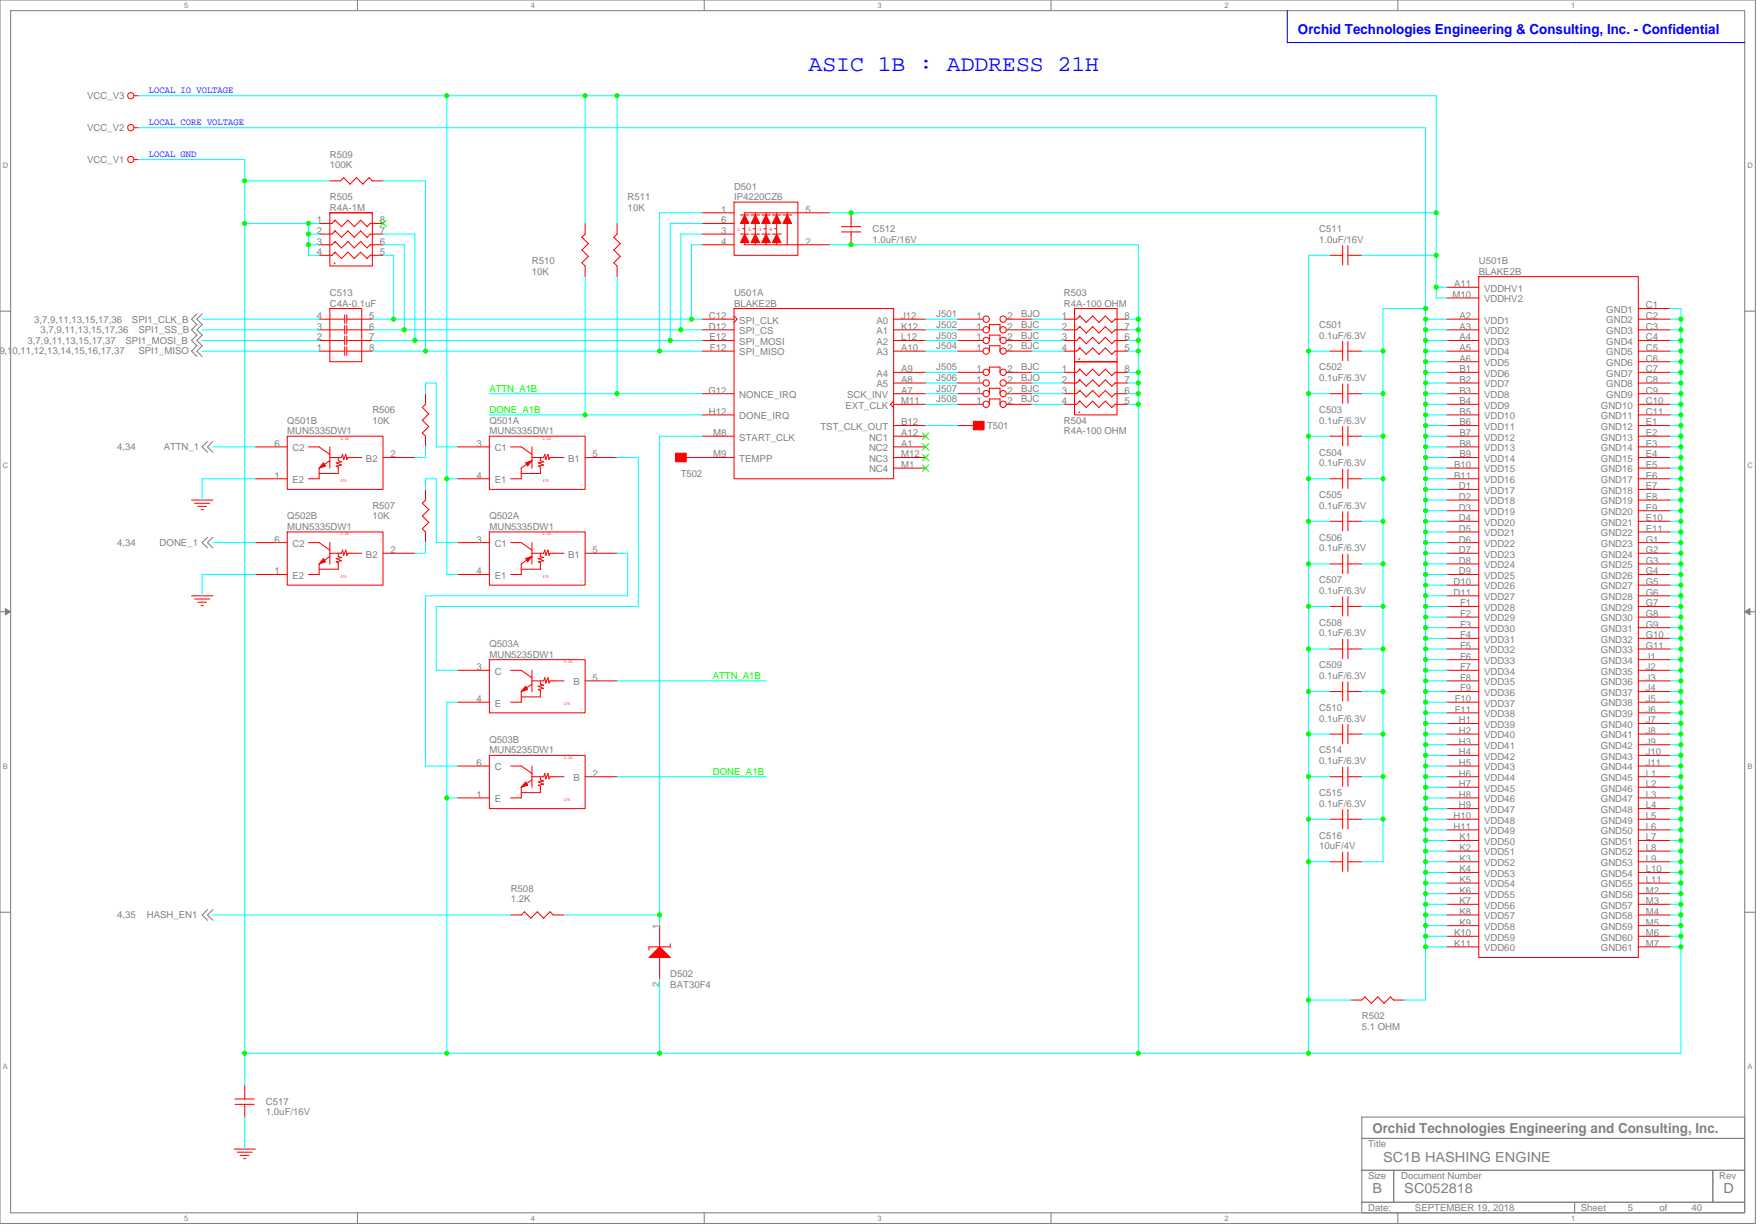
[picture p157: page 5]

Orchid Technologies Engineering and Consulting, Inc.

# ASIC 2A : ADDRESS 02H

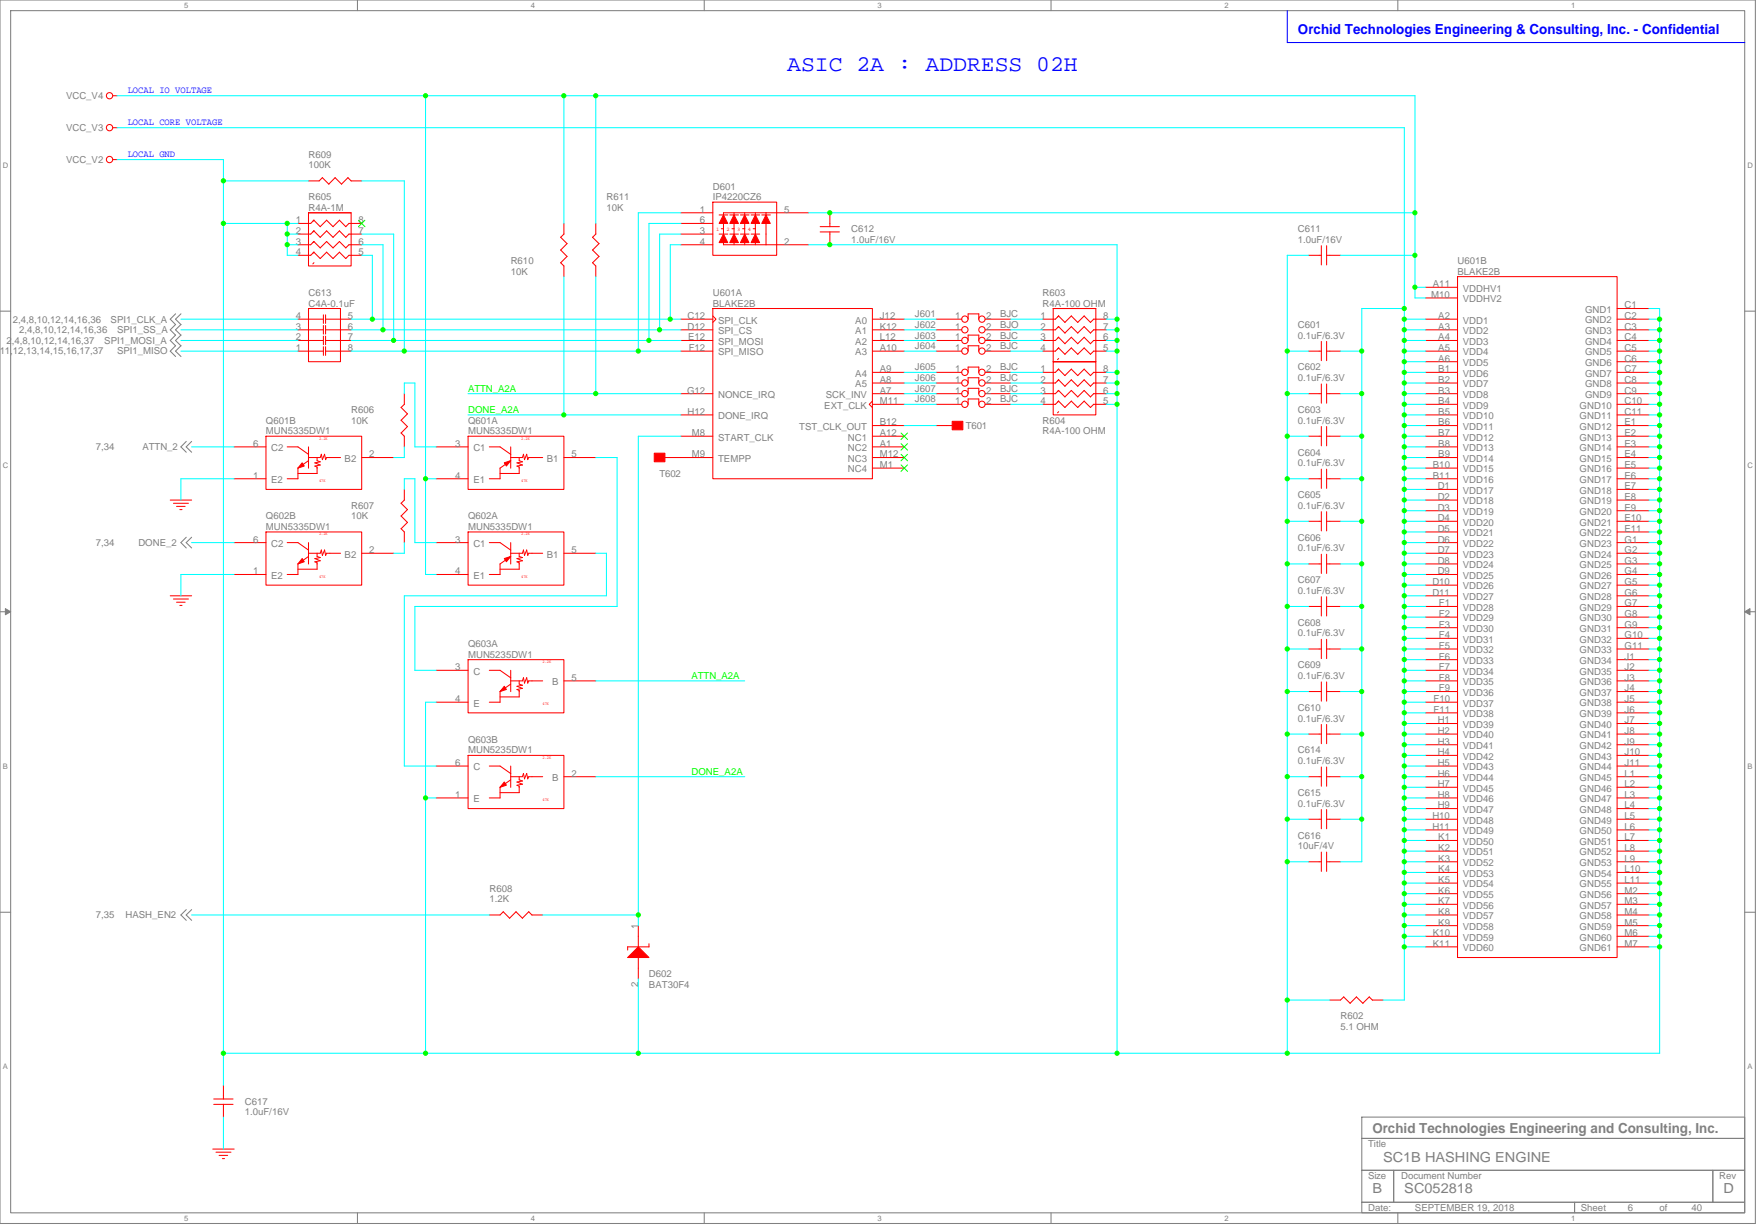
[picture p158: page 6]

Orchid Technologies Engineering and Consulting, Inc.

# ASIC 2B : ADDRESS 22H

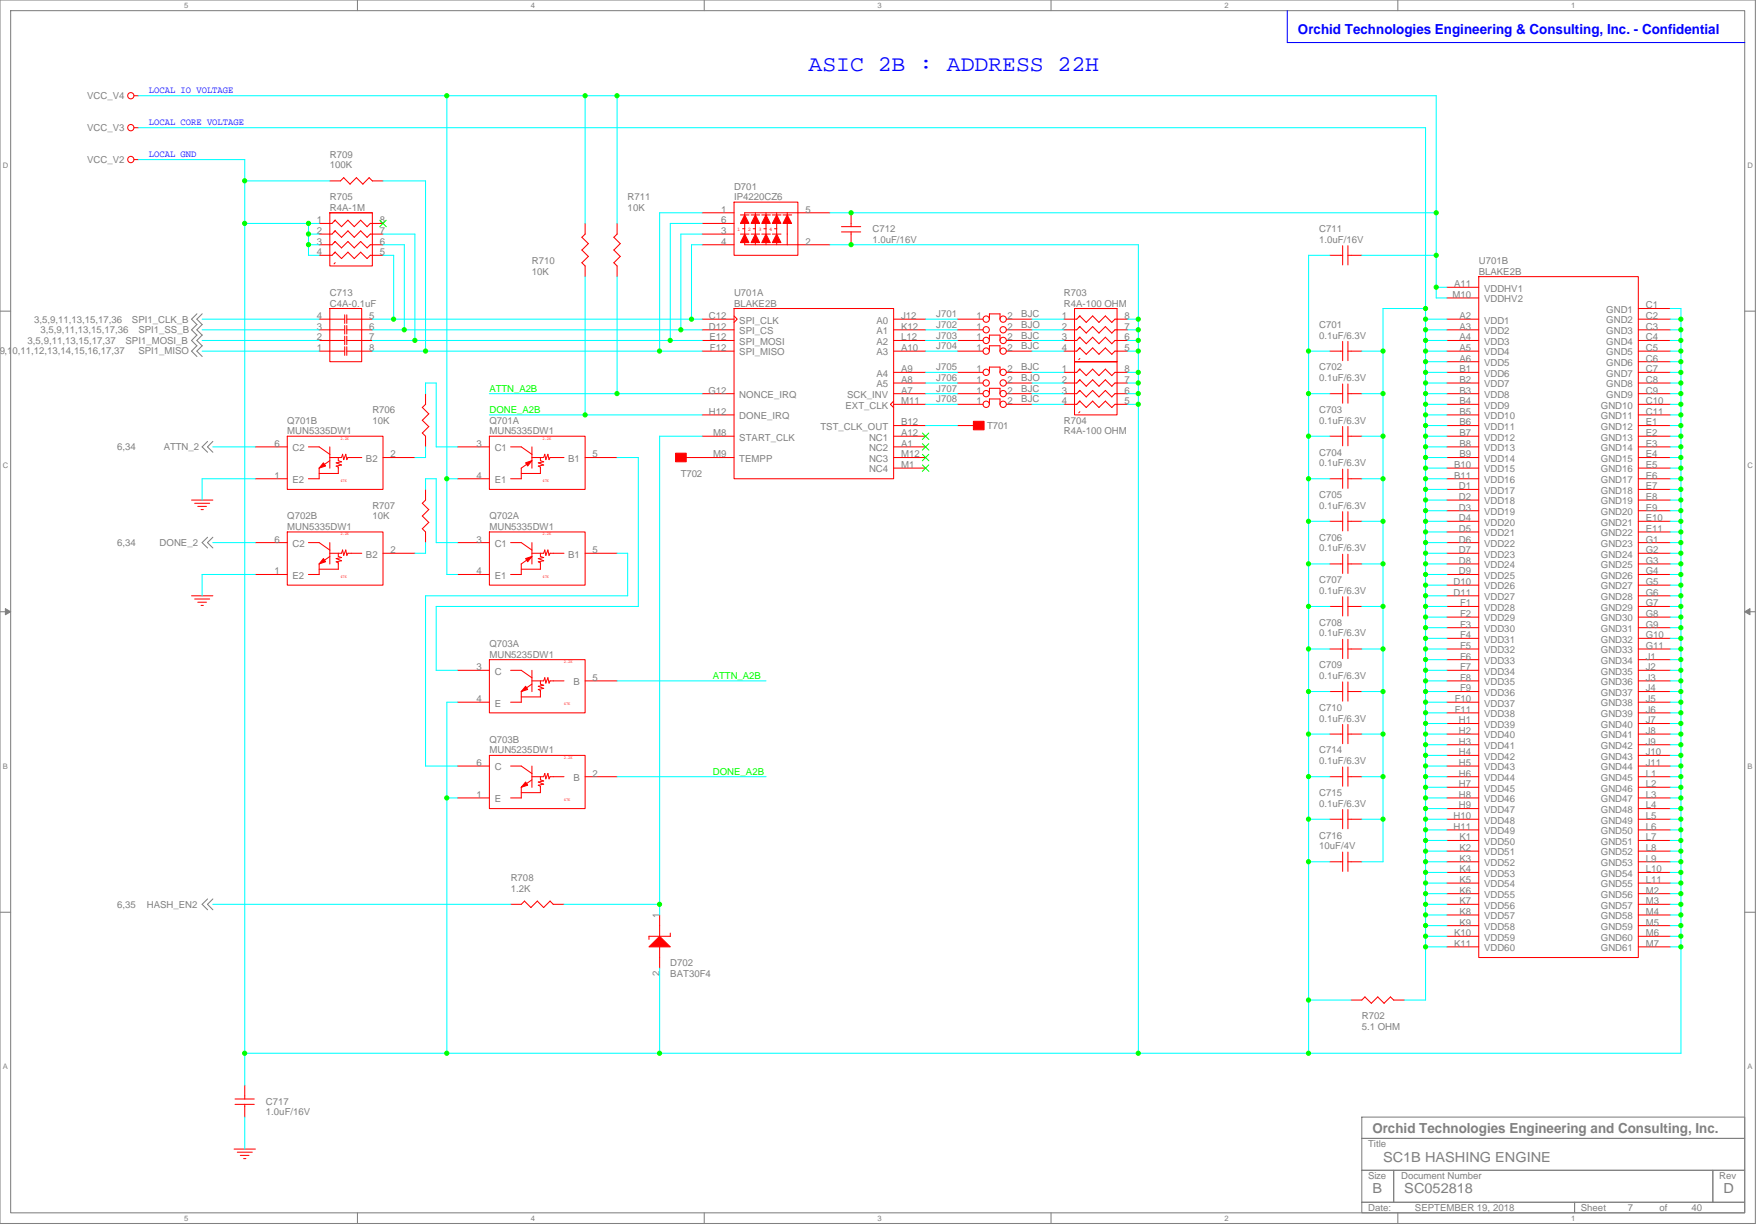
[picture p159: page 7]

Orchid Technologies Engineering and Consulting, Inc.

# ASIC 3A : ADDRESS 03H

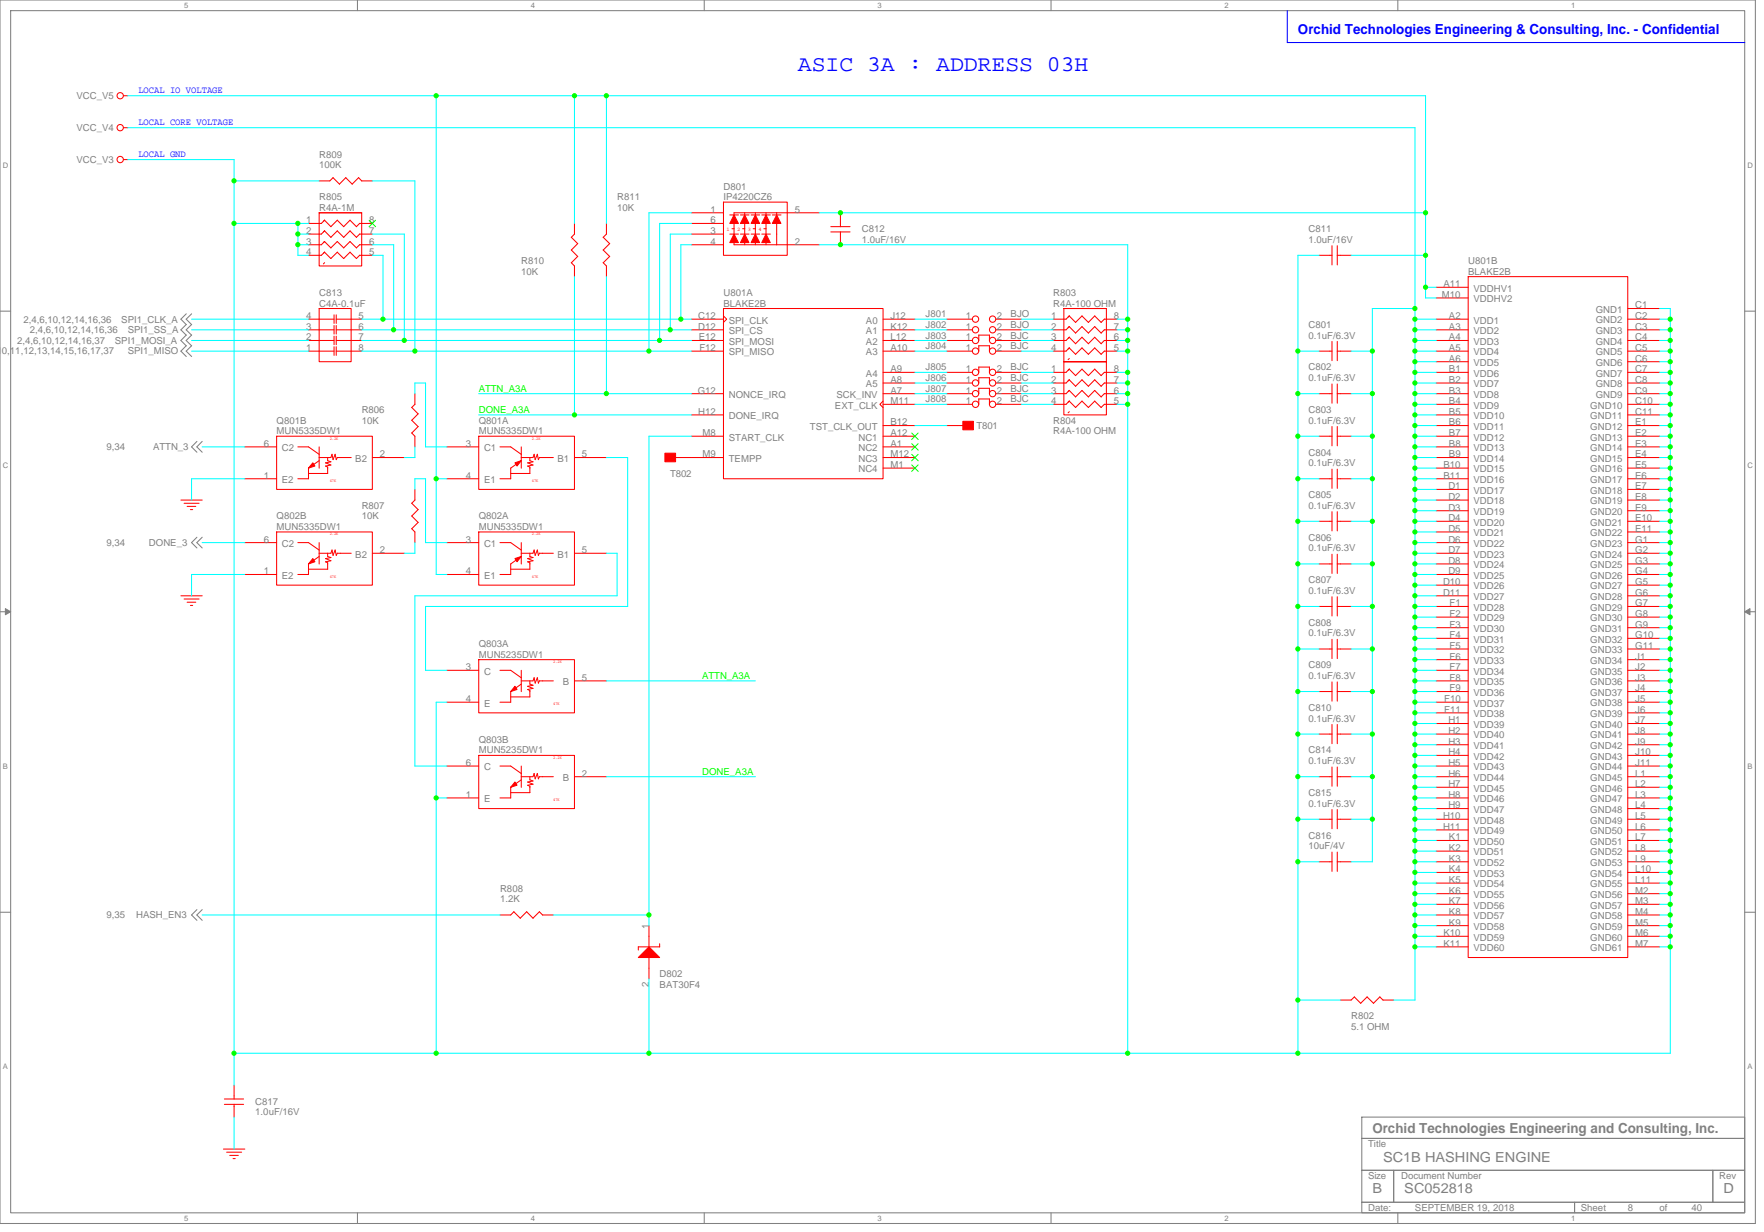
[picture p160: page 8]

Orchid Technologies Engineering and Consulting, Inc.

# ASIC 3B : ADDRESS 23H

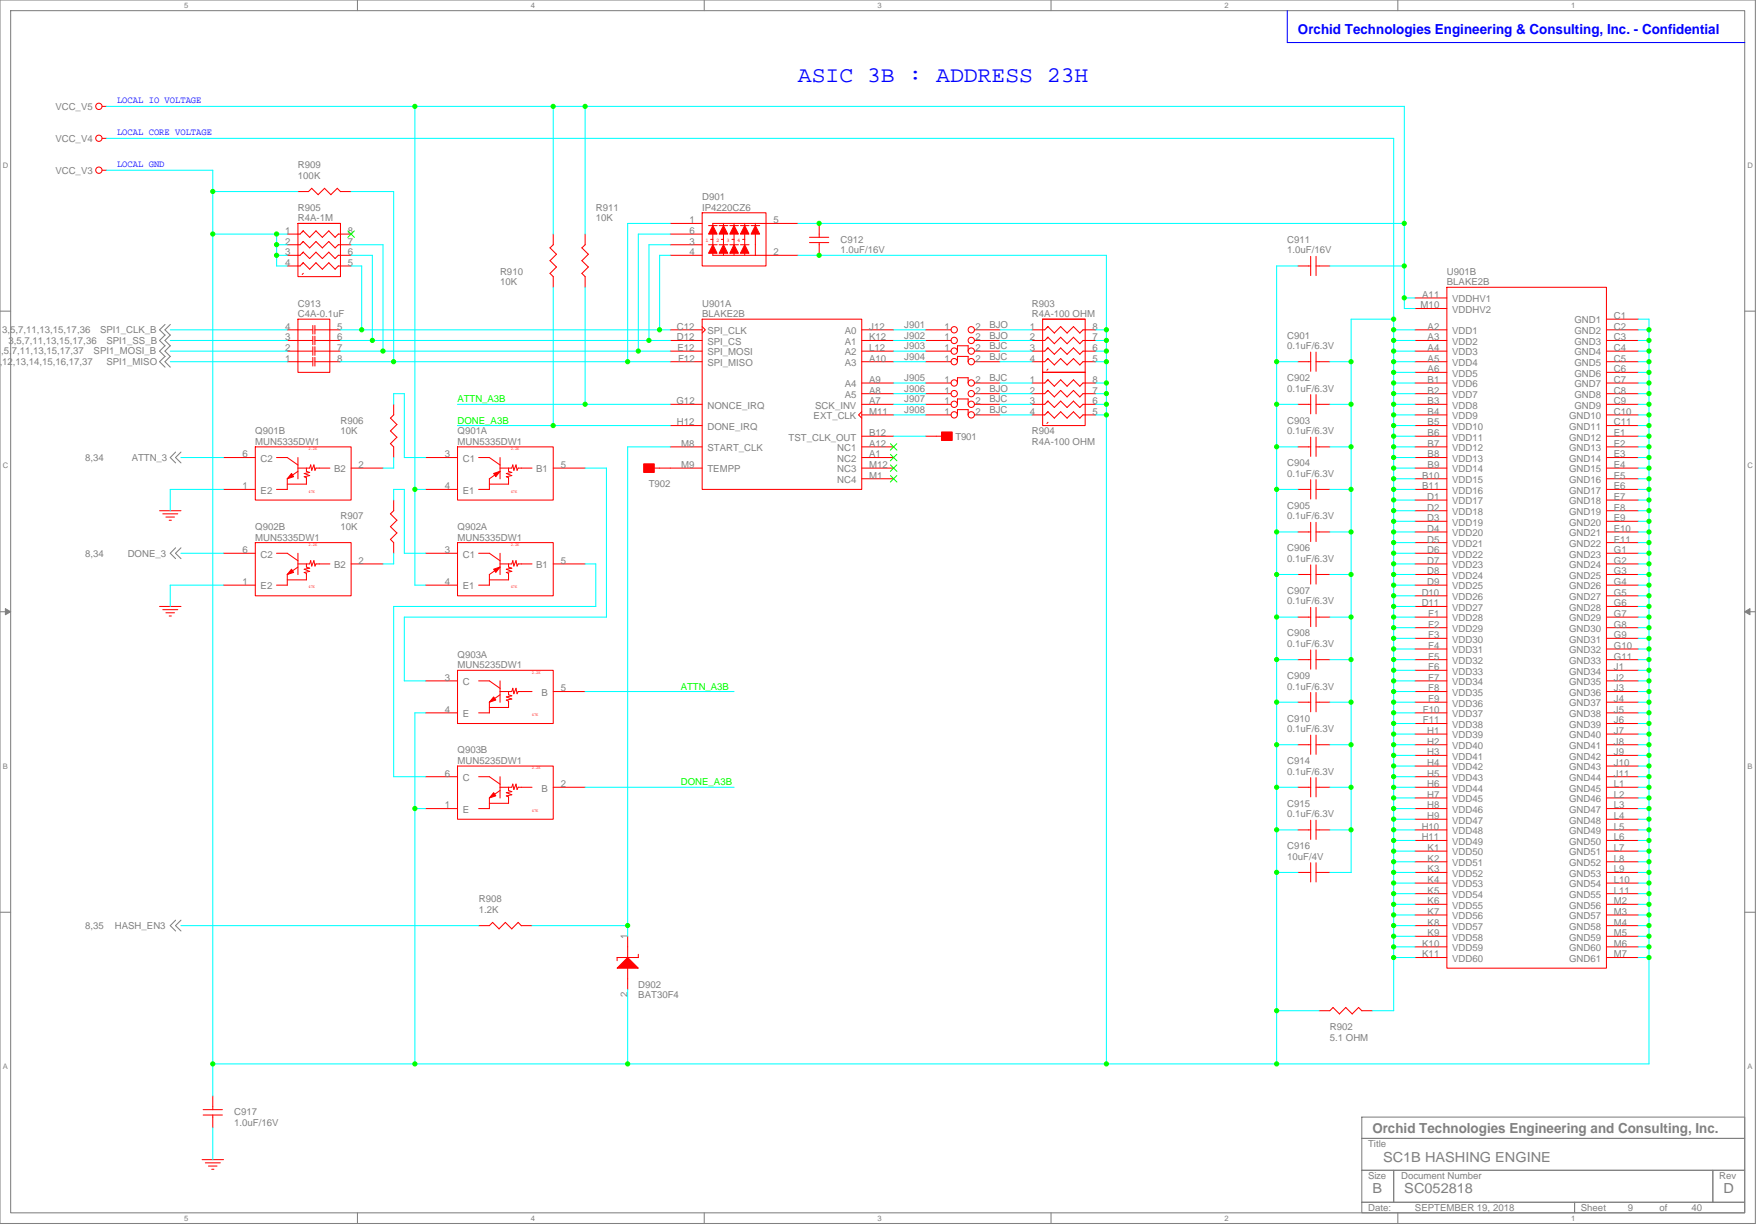
[picture p161: page 9]

3 | 6 | | | D12
2 | 7 | | E12
1 | 8 | F12

Orchid Technologies Engineering and Consulting, Inc.

# ASIC 4A : ADDRESS 04H

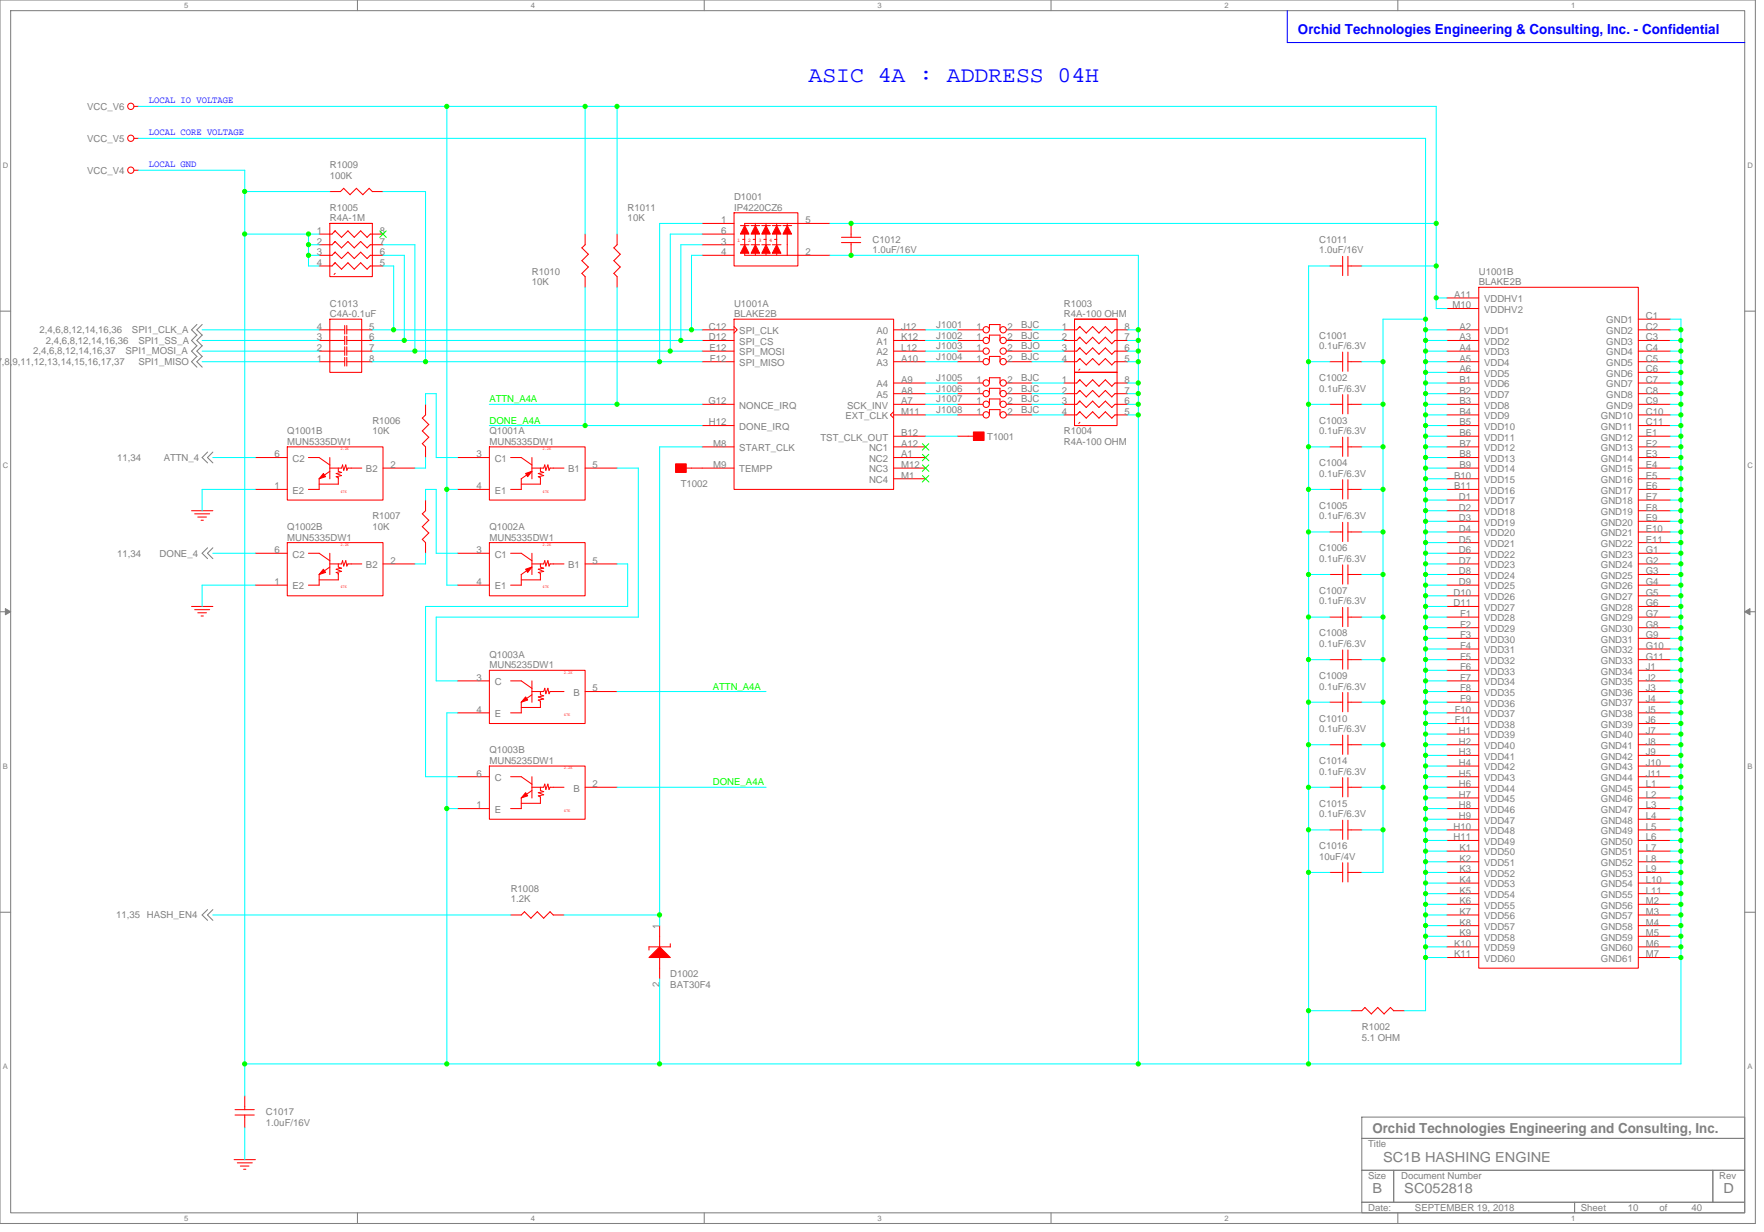
[picture p162: page 10]

Orchid Technologies Engineering and Consulting, Inc.

# ASIC 4B : ADDRESS 24H

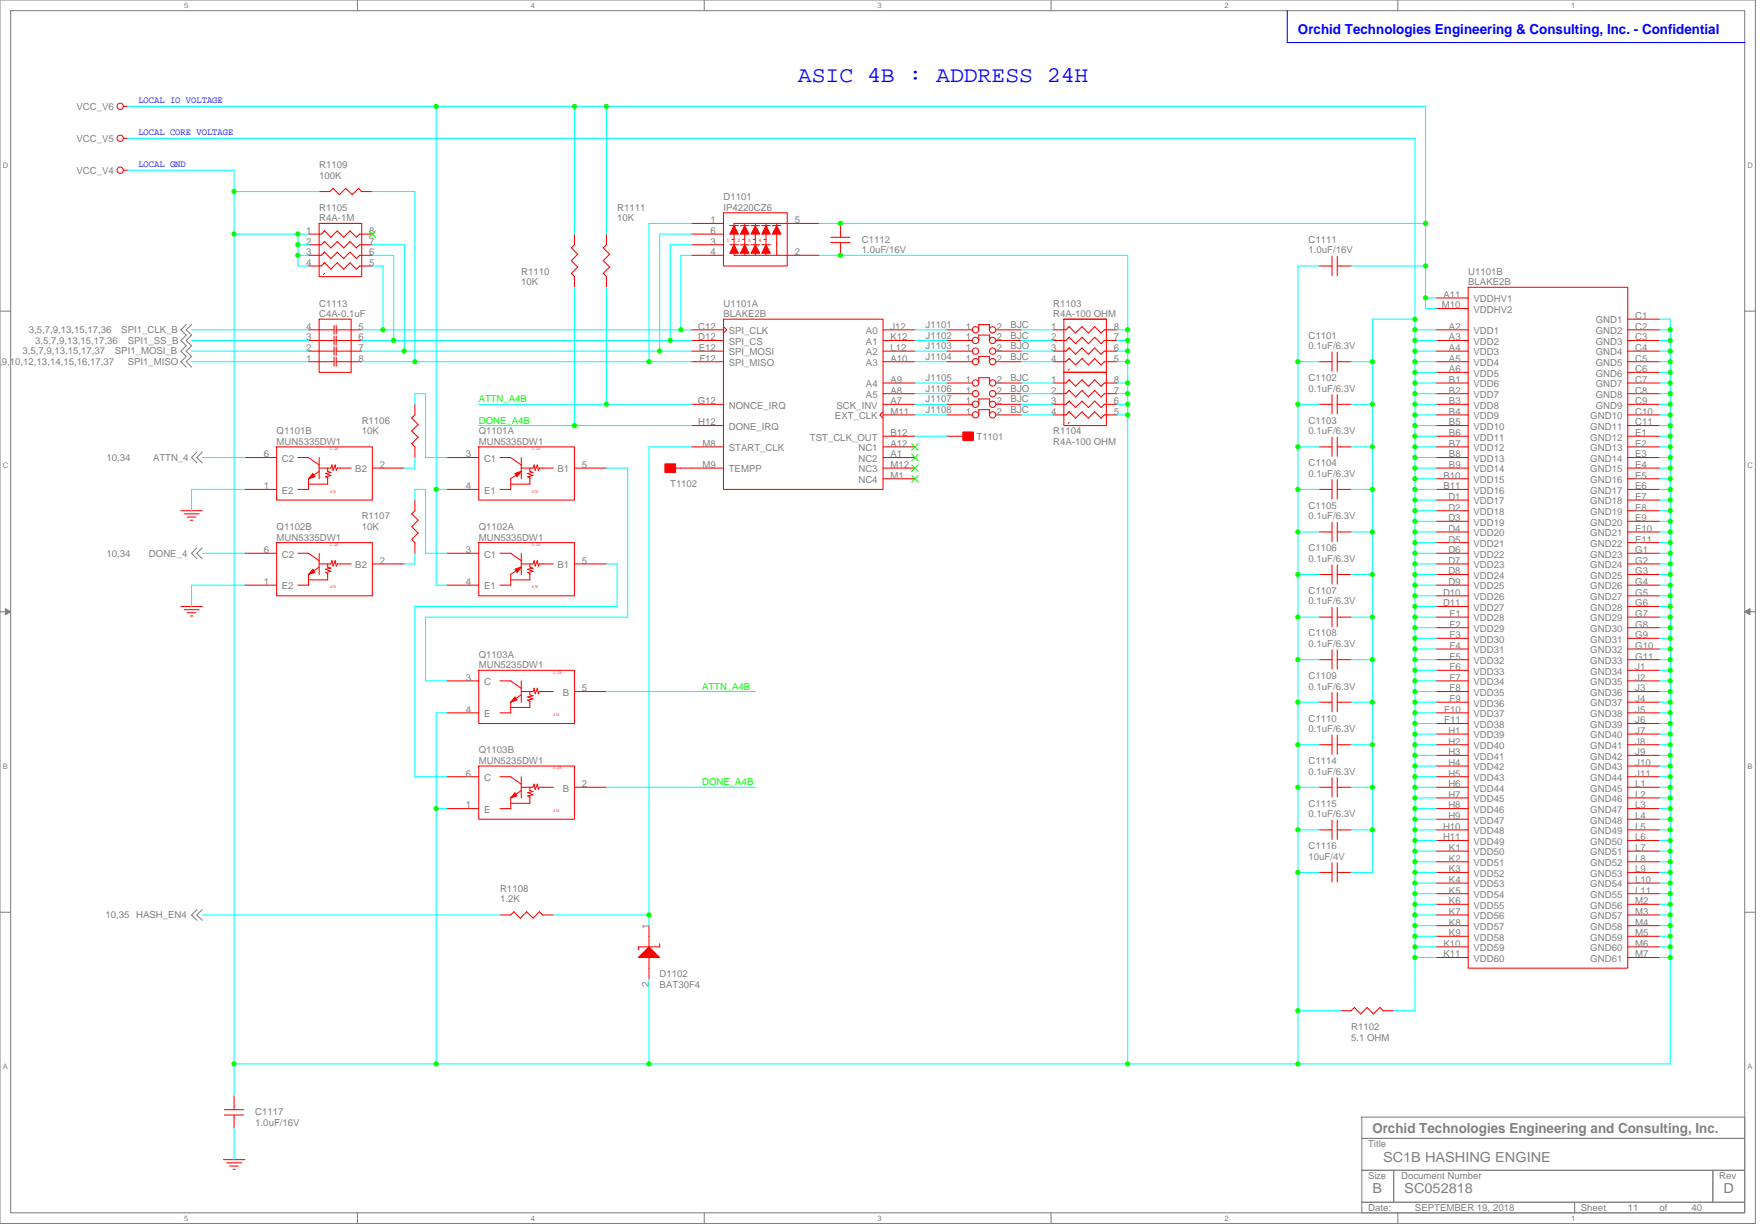
[picture p163: page 11]

Orchid Technologies Engineering and Consulting, Inc.

# ASIC 5A : ADDRESS 05H

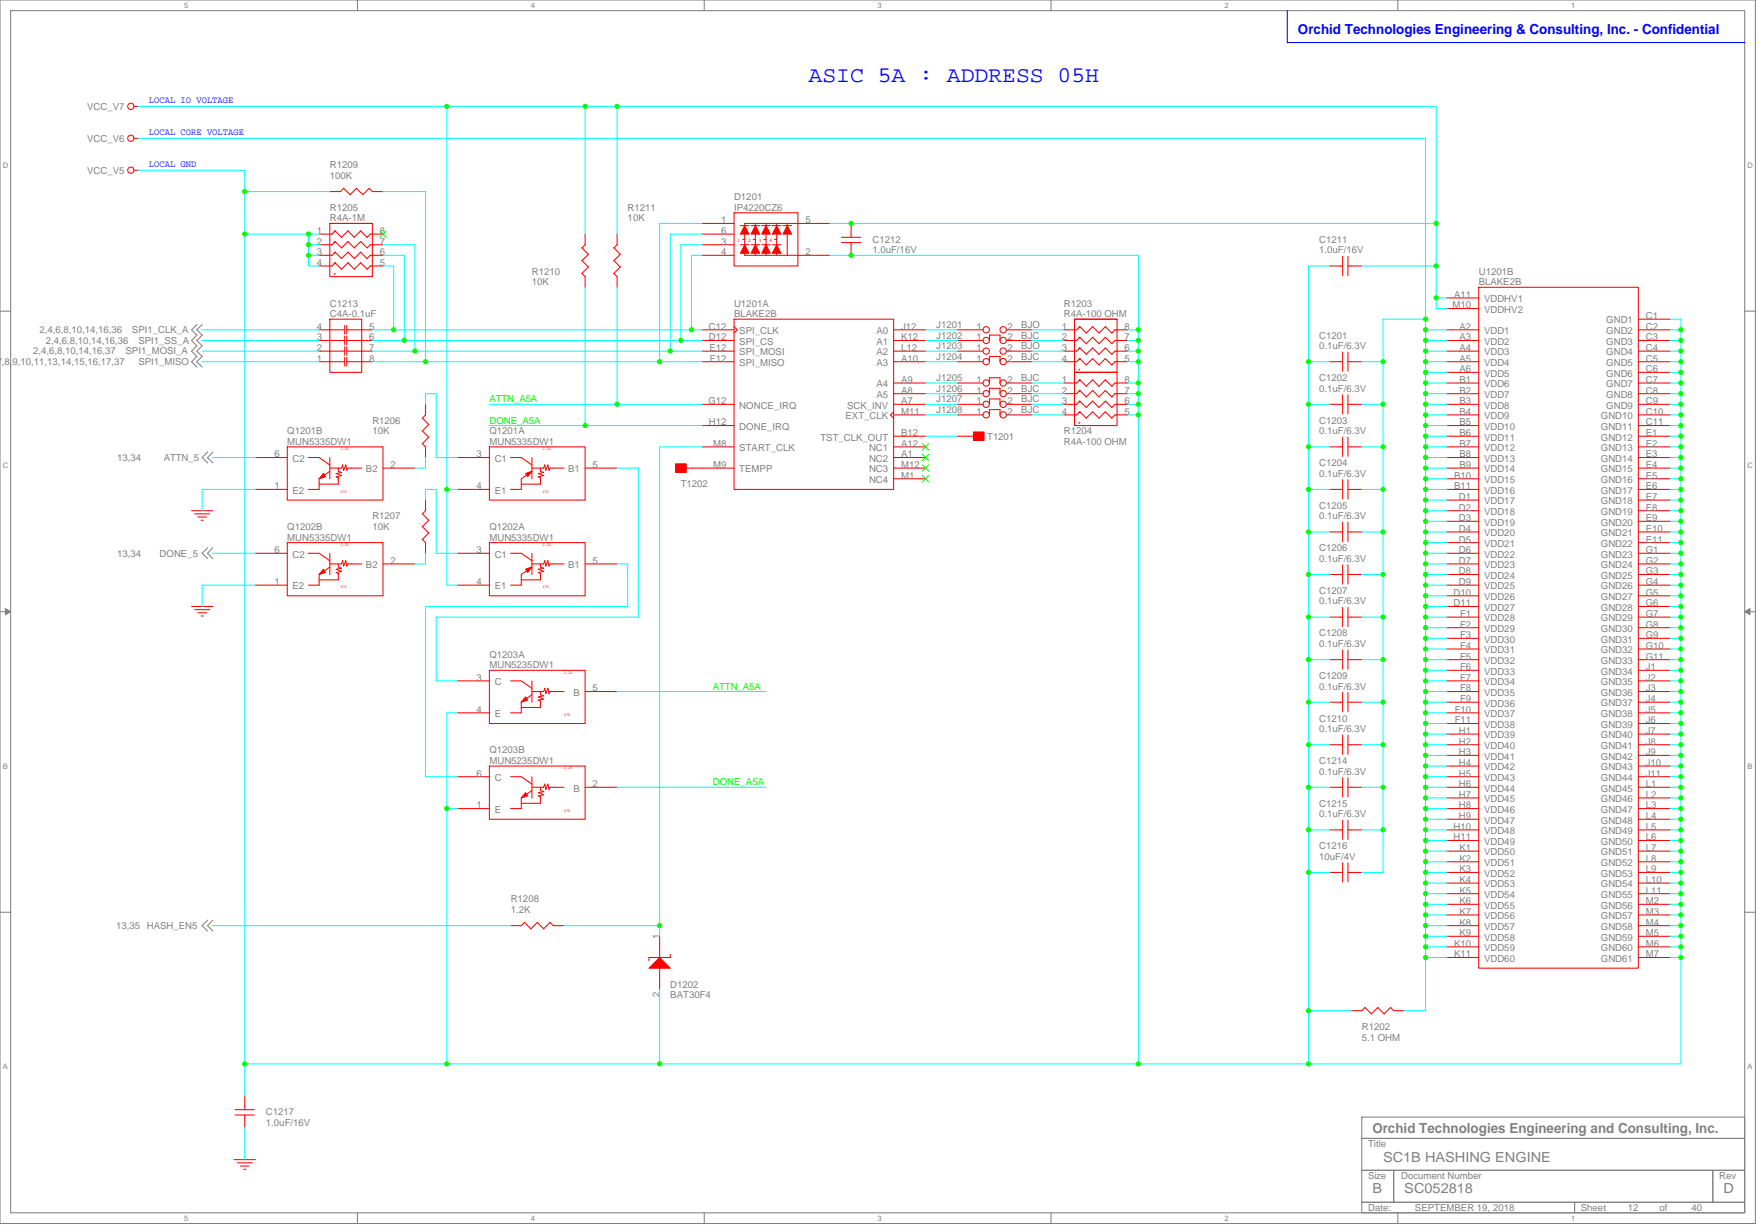
[picture p164: page 12]

Orchid Technologies Engineering and Consulting, Inc.

# ASIC 5B : ADDRESS 25H

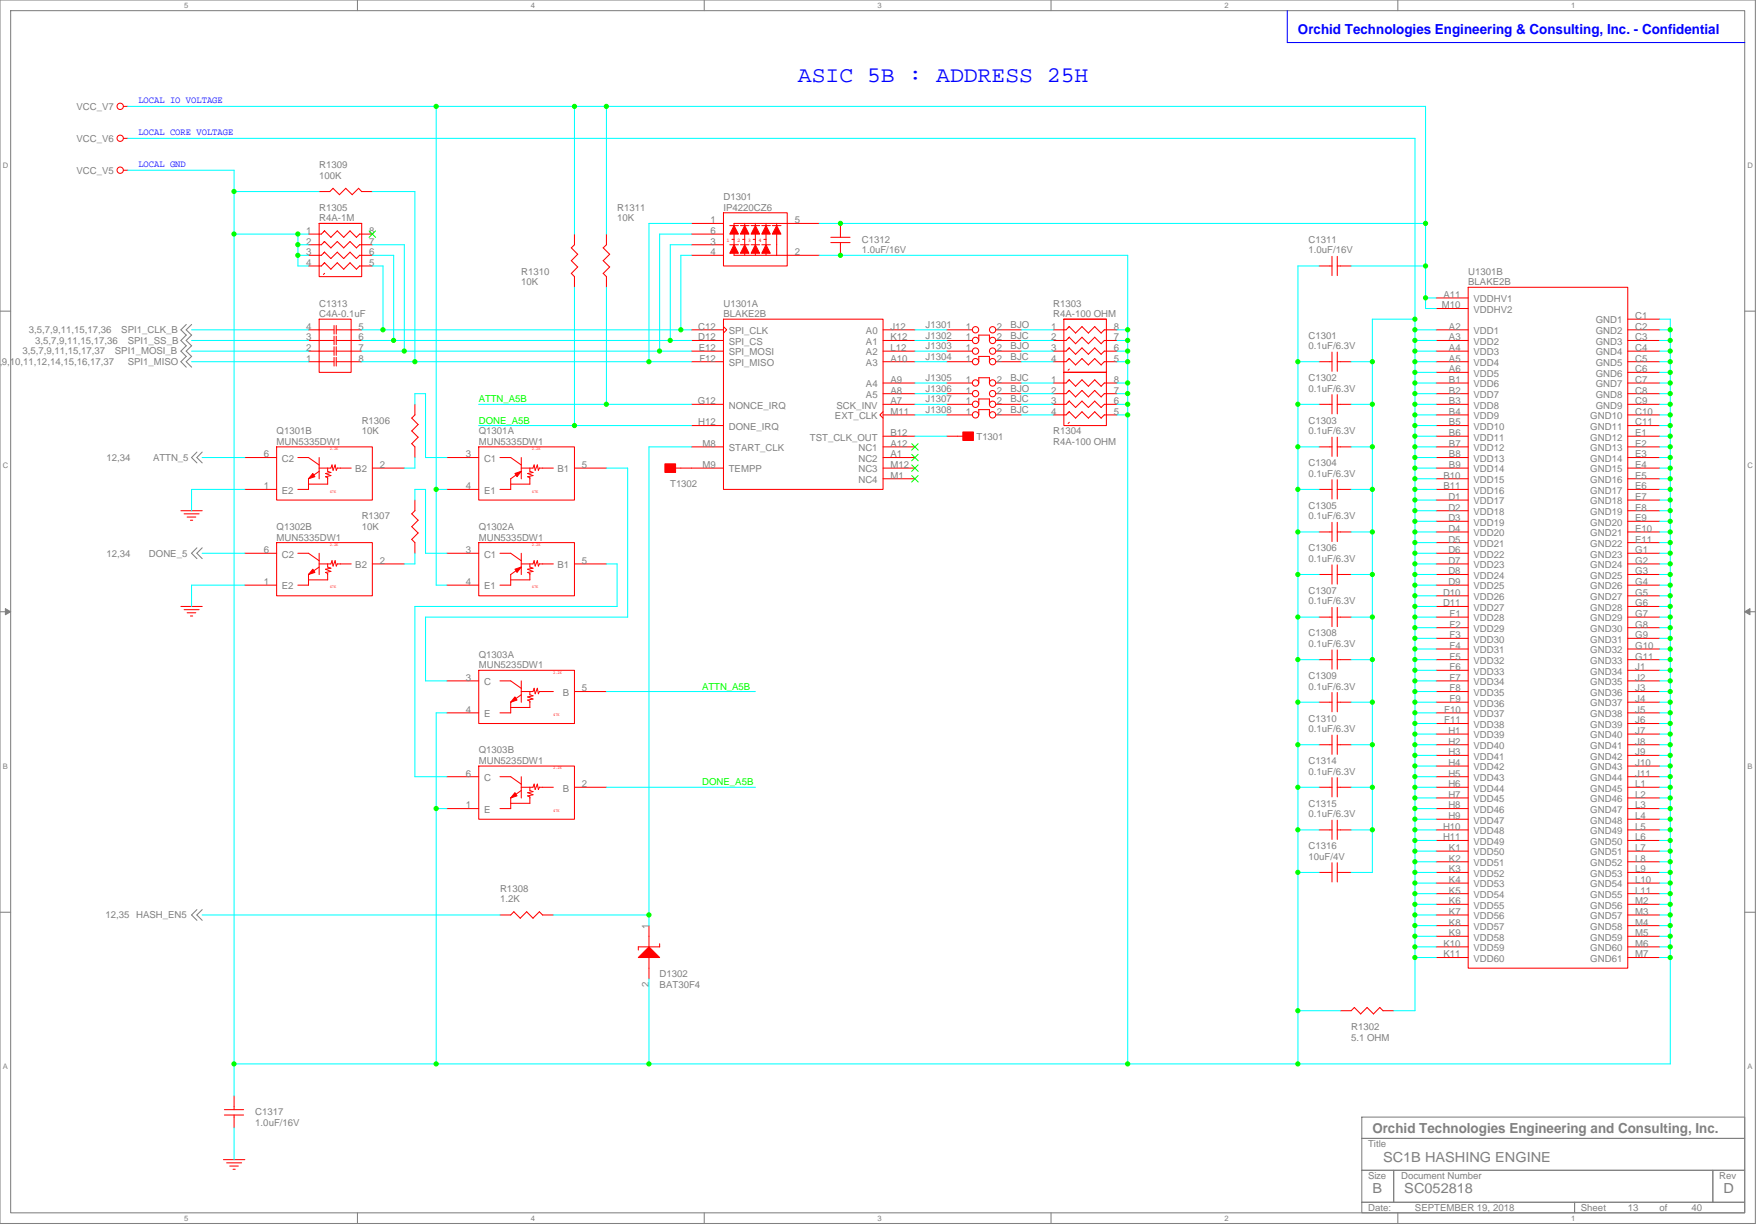
[picture p165: page 13]

Orchid Technologies Engineering and Consulting, Inc.

# ASIC 6A : ADDRESS 06H

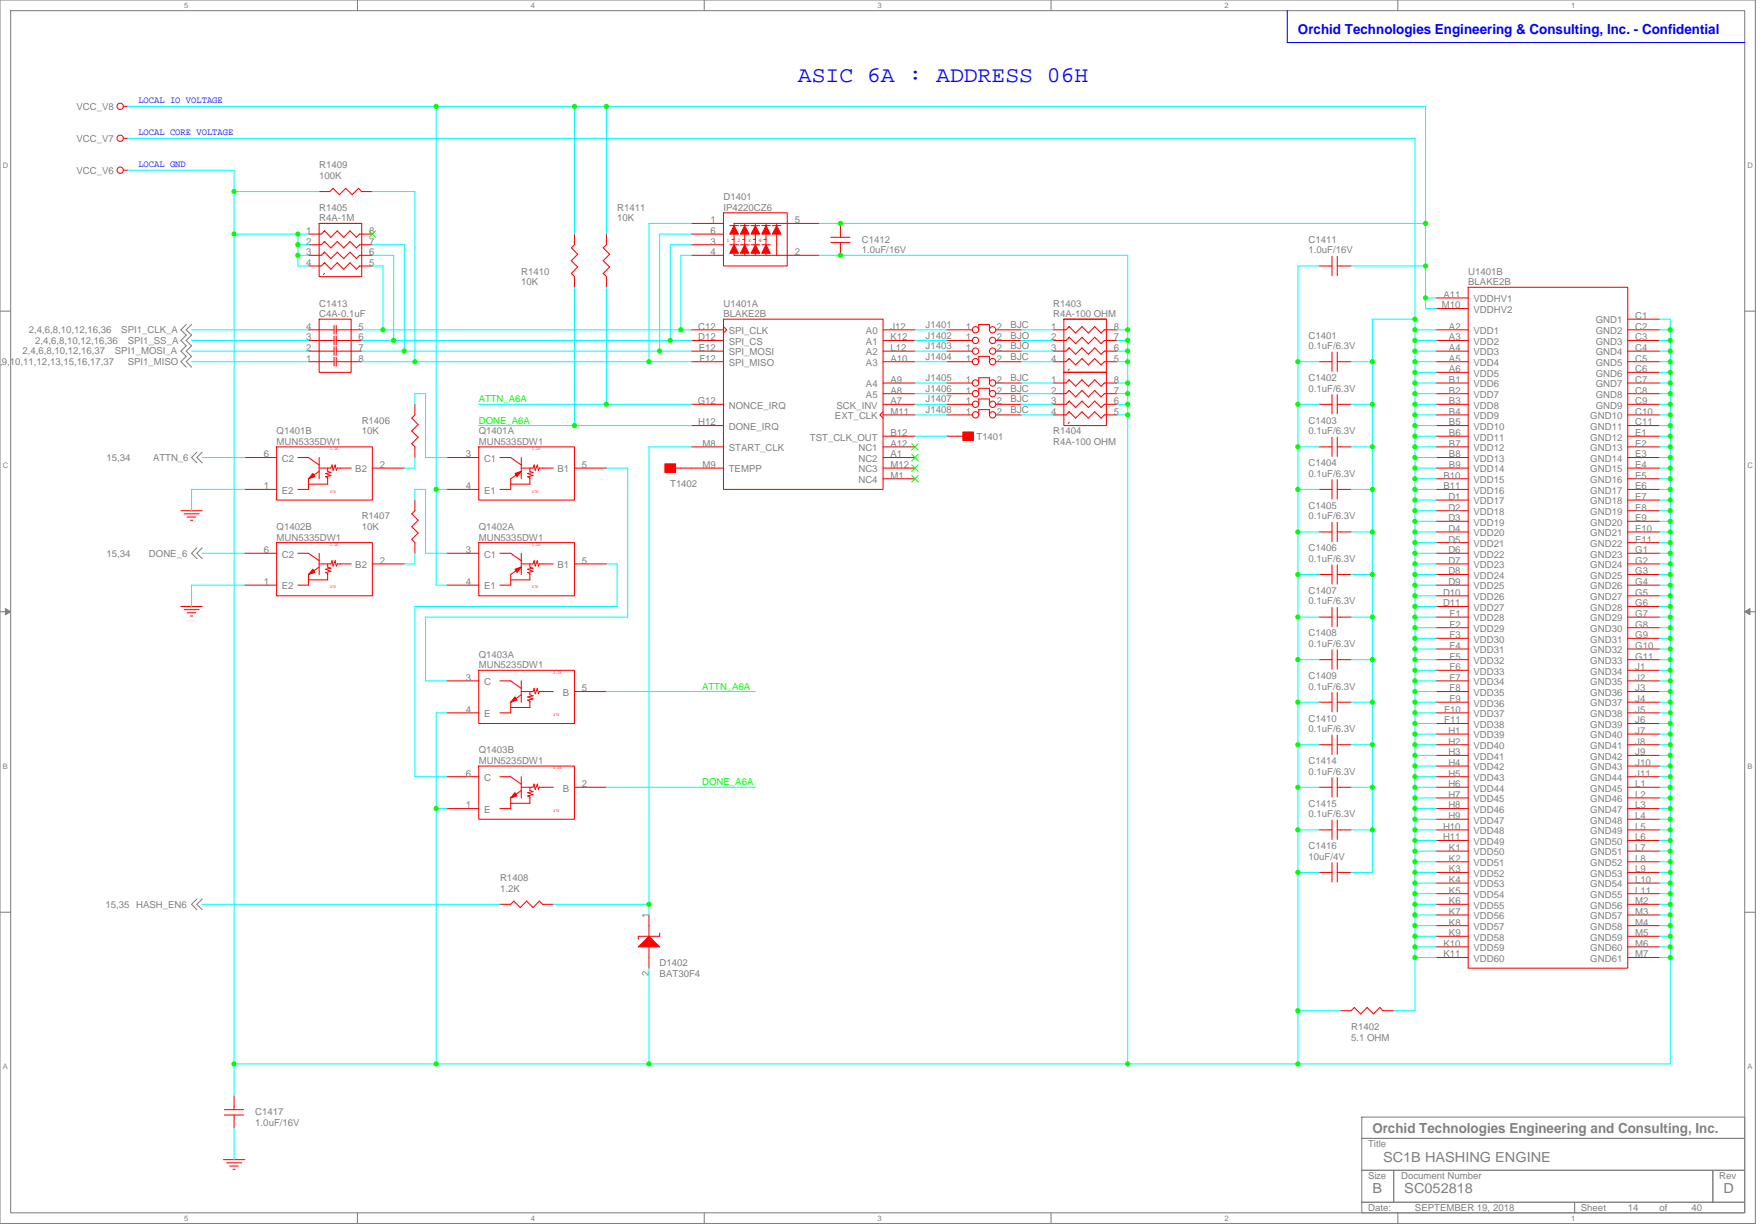
[picture p166: page 14]

Orchid Technologies Engineering and Consulting, Inc.

# ASIC 6B : ADDRESS 26H

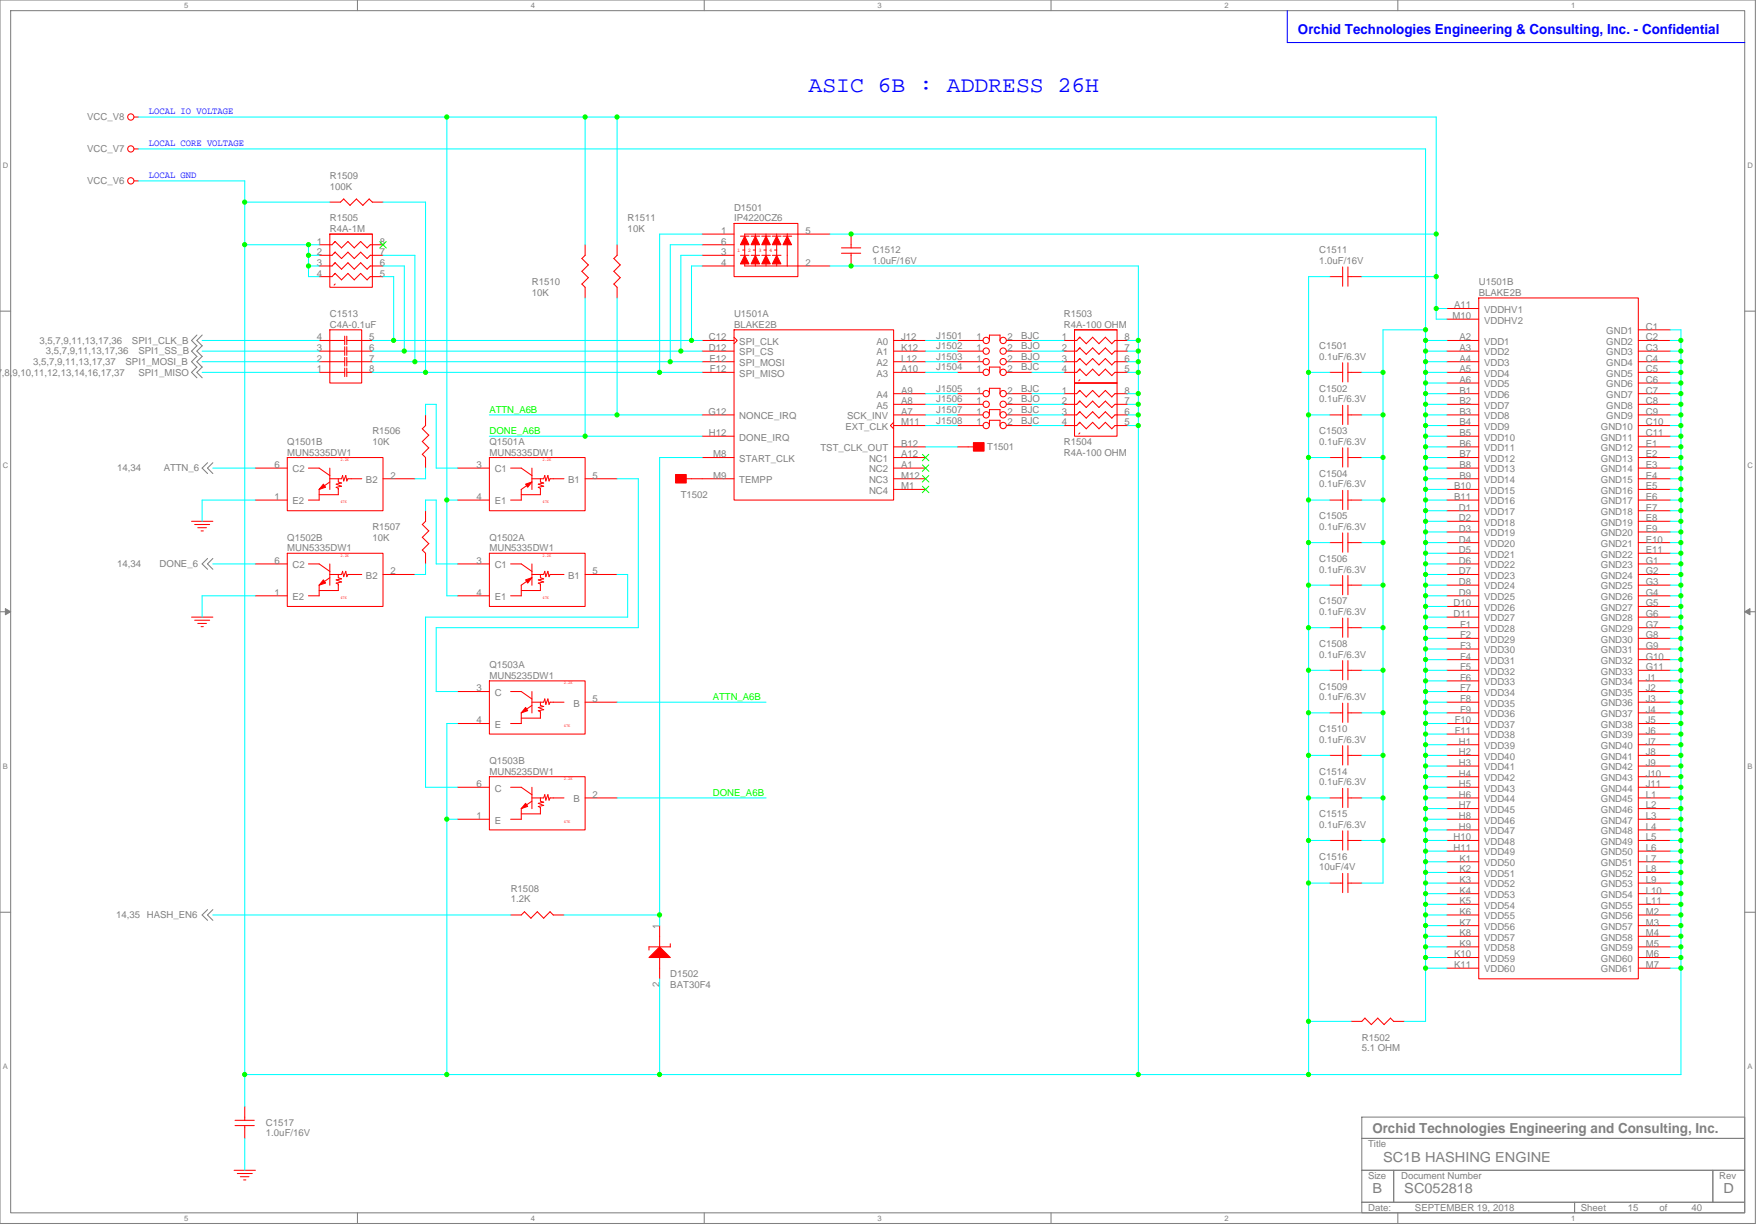
[picture p167: page 15]

Orchid Technologies Engineering and Consulting, Inc.

# ASIC 7A : ADDRESS 07H

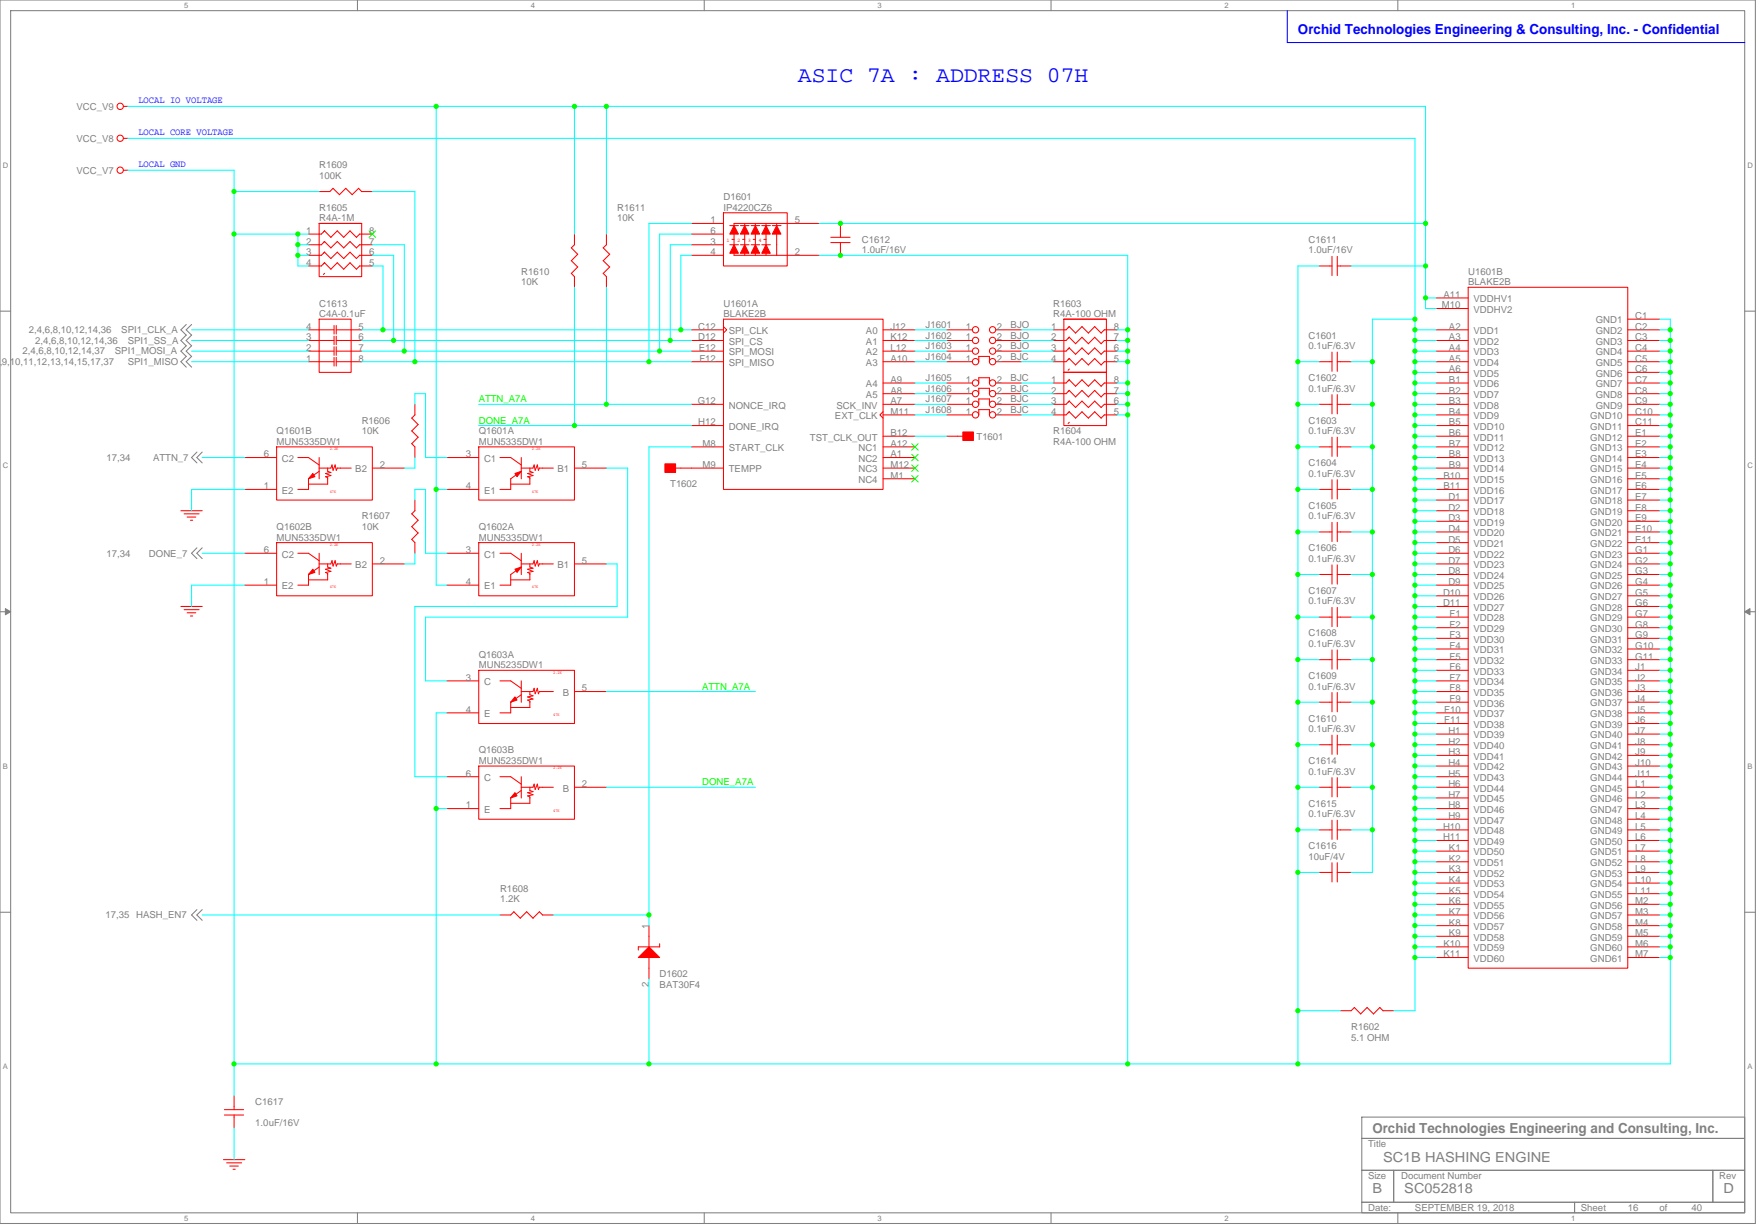
[picture p168: page 16]

Orchid Technologies Engineering and Consulting, Inc.

# ASIC 7B: ADDRESS 27H

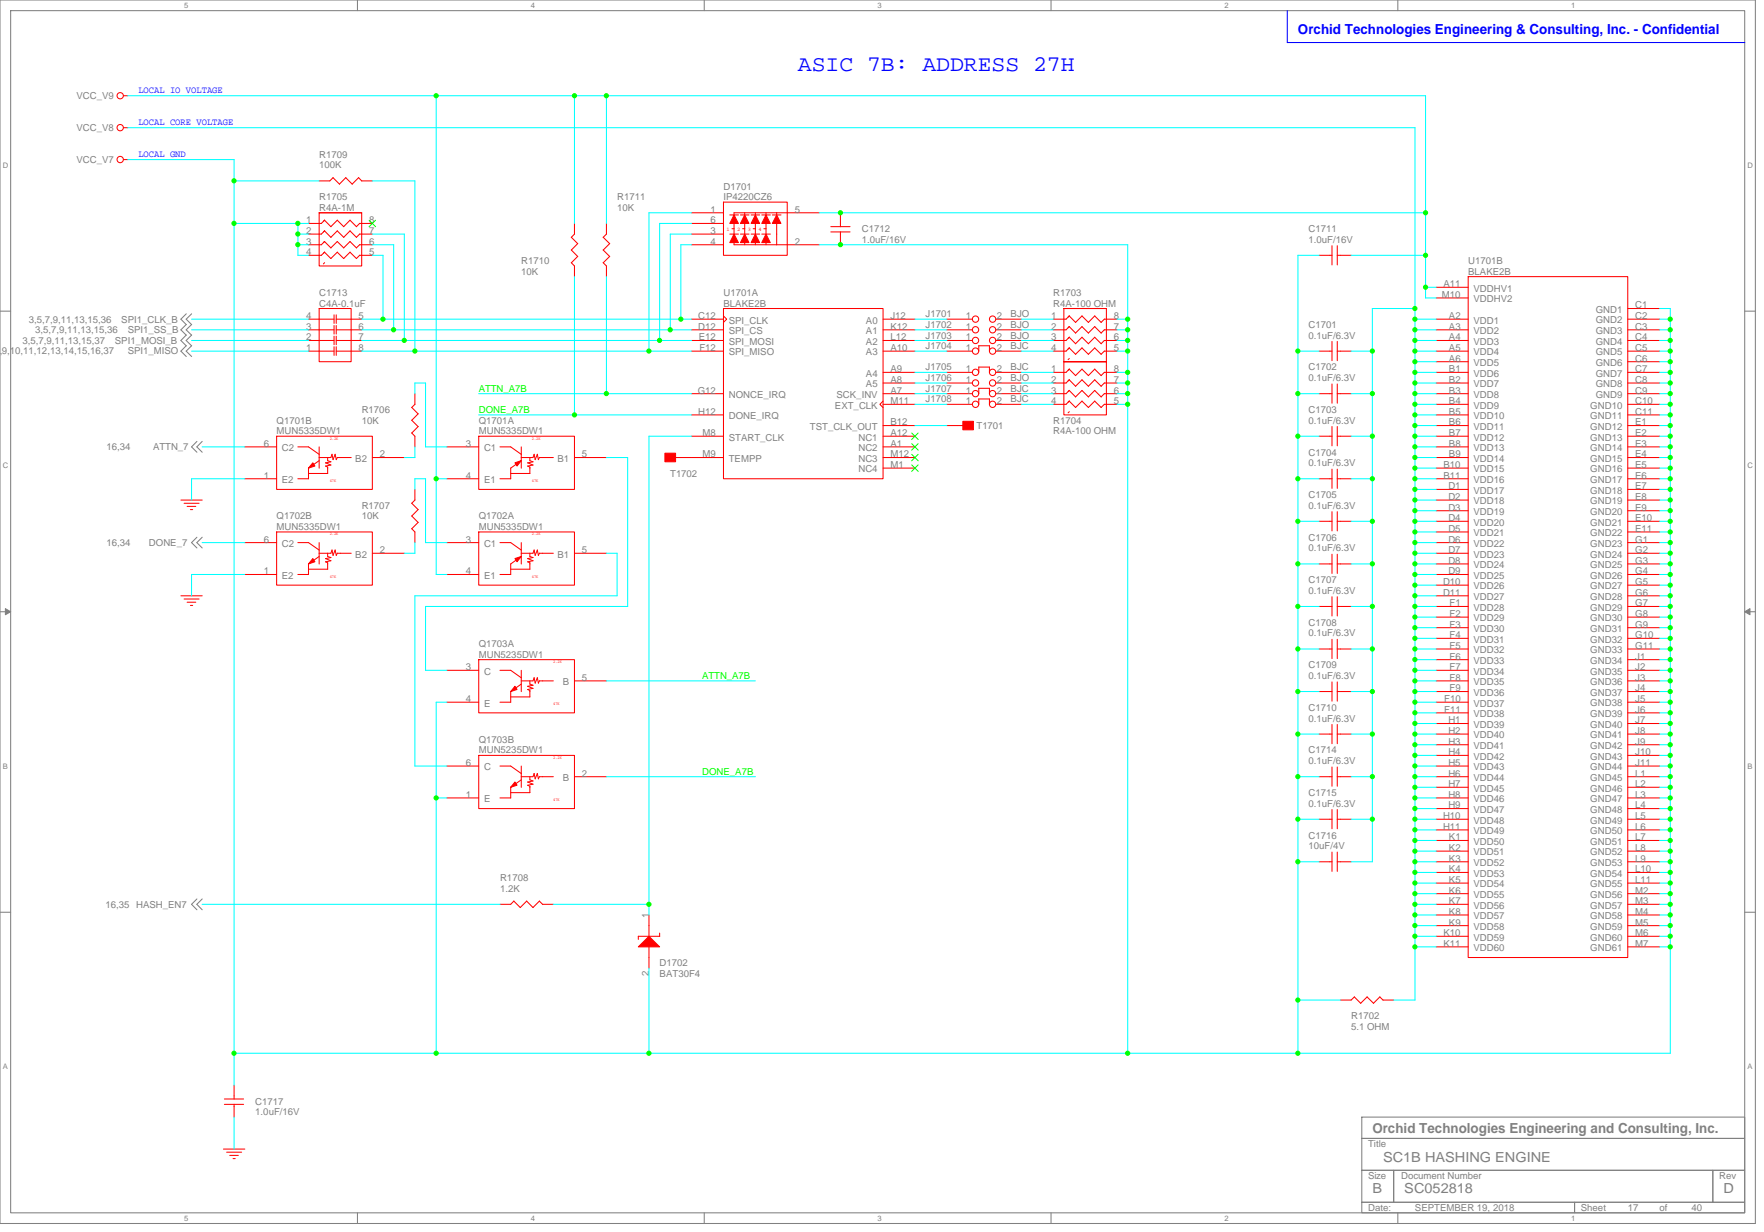
[picture p169: page 17]

Orchid Technologies Engineering and Consulting, Inc.

# ASIC 8A : ADDRESS 08H

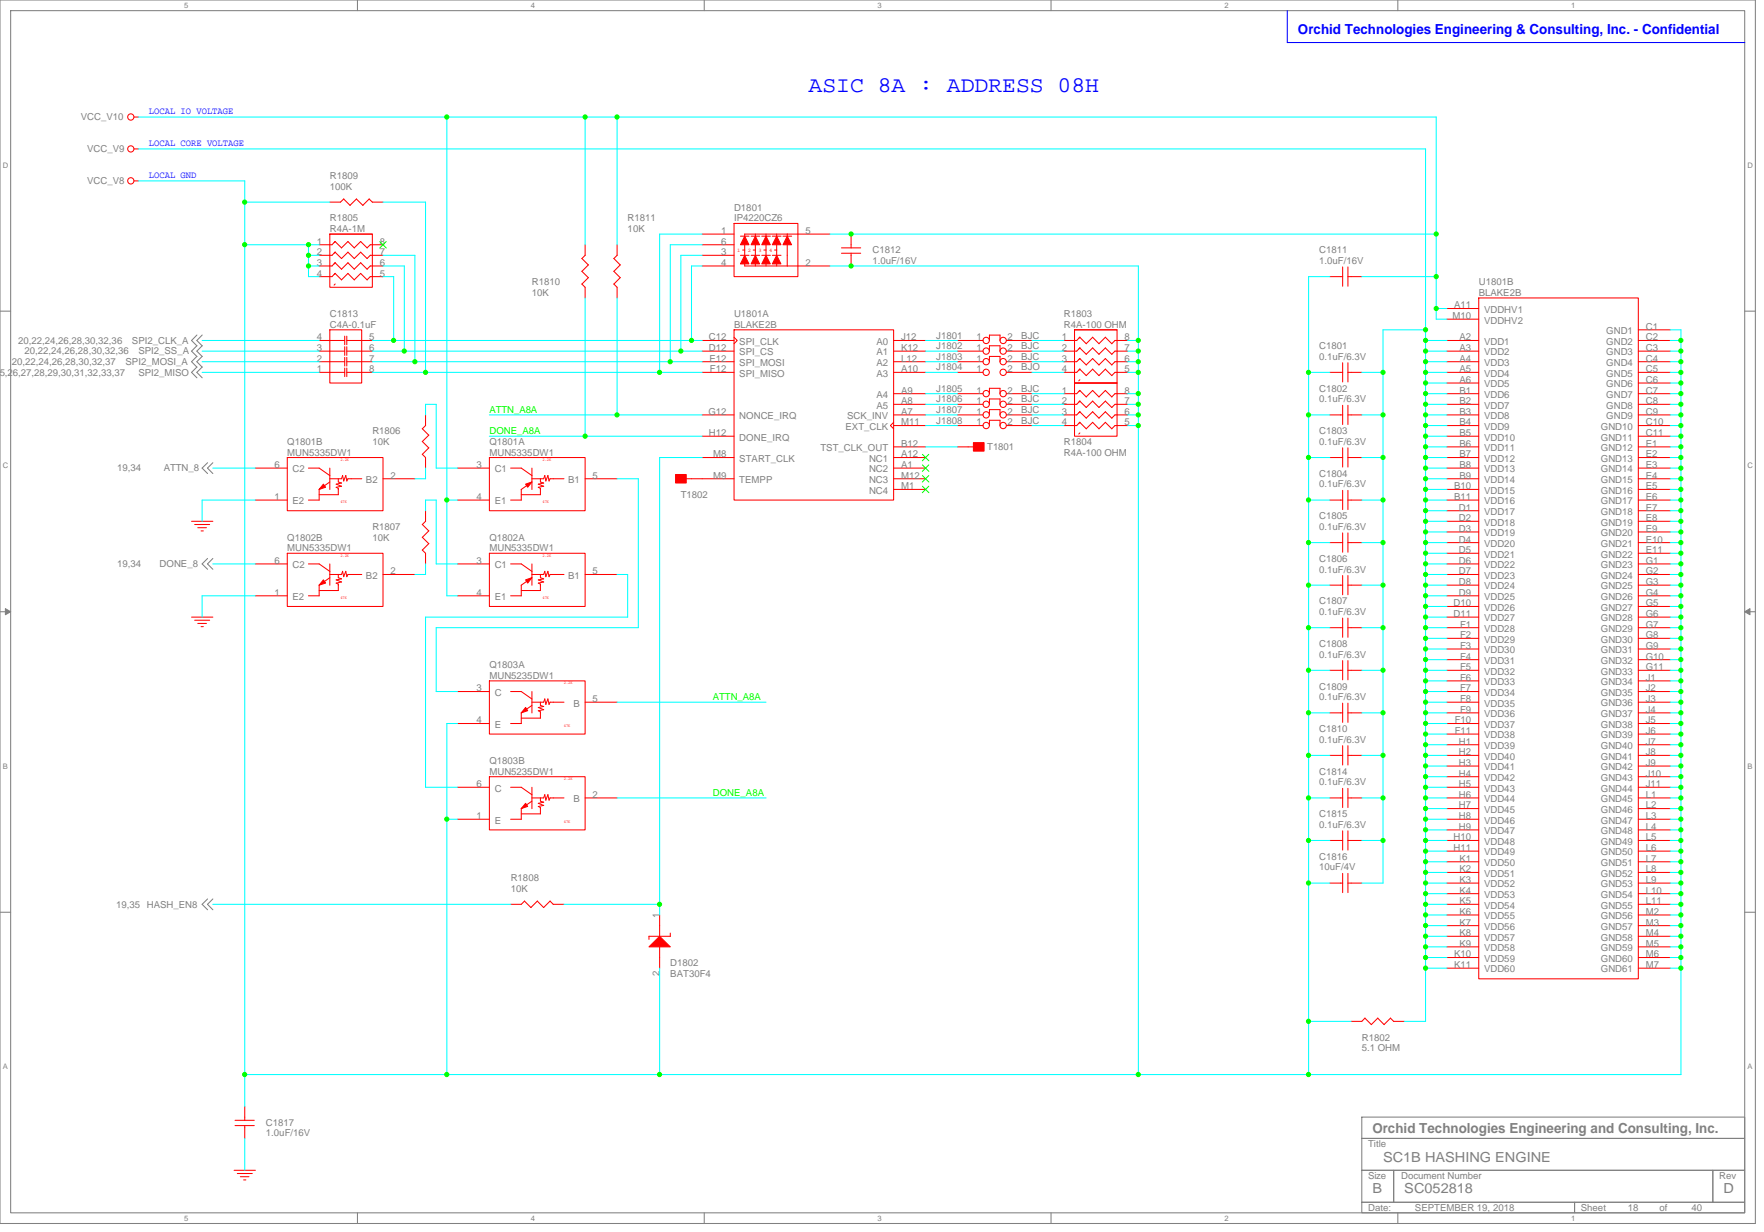
[picture p170: page 18]

Orchid Technologies Engineering and Consulting, Inc.

# ASIC 8B : ADDRESS 28H

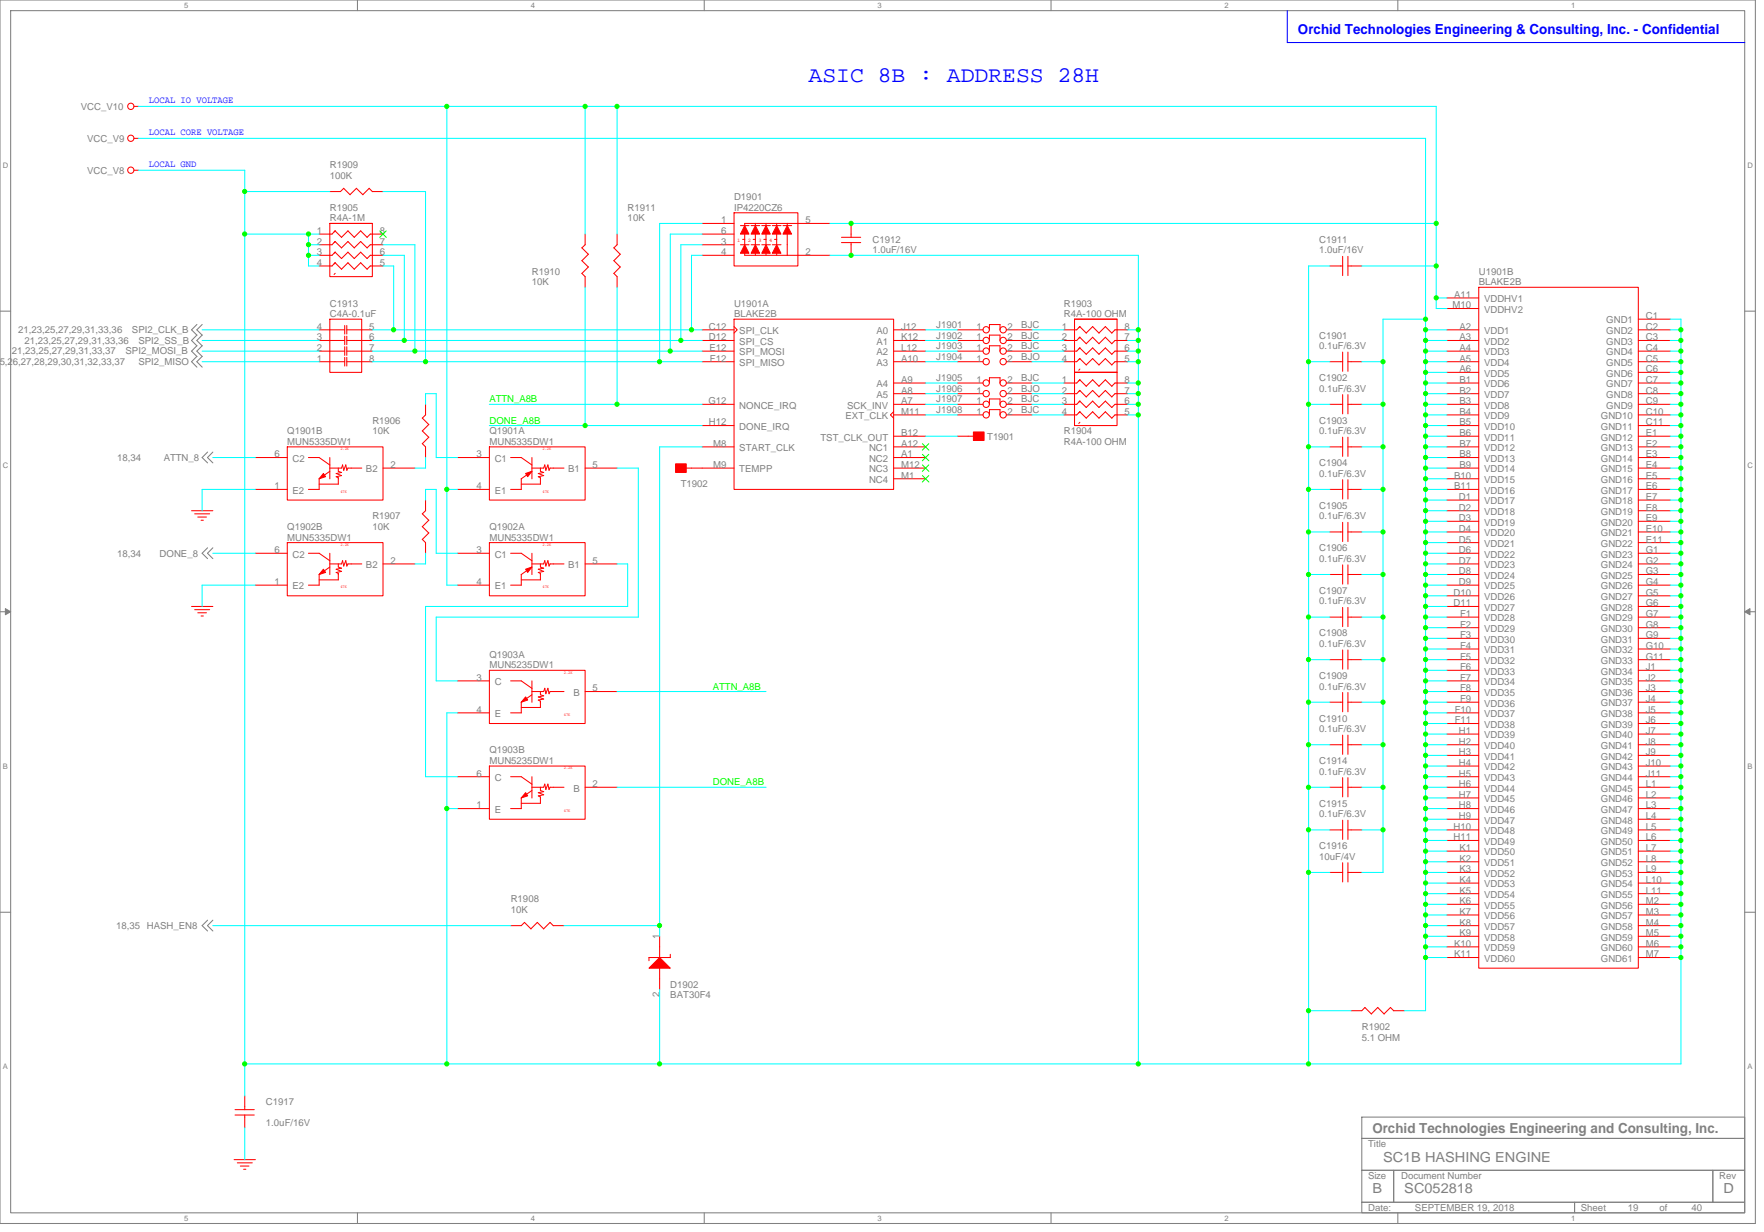
[picture p171: page 19]

Orchid Technologies Engineering and Consulting, Inc.

# ASIC 9A : ADDRESS 09H

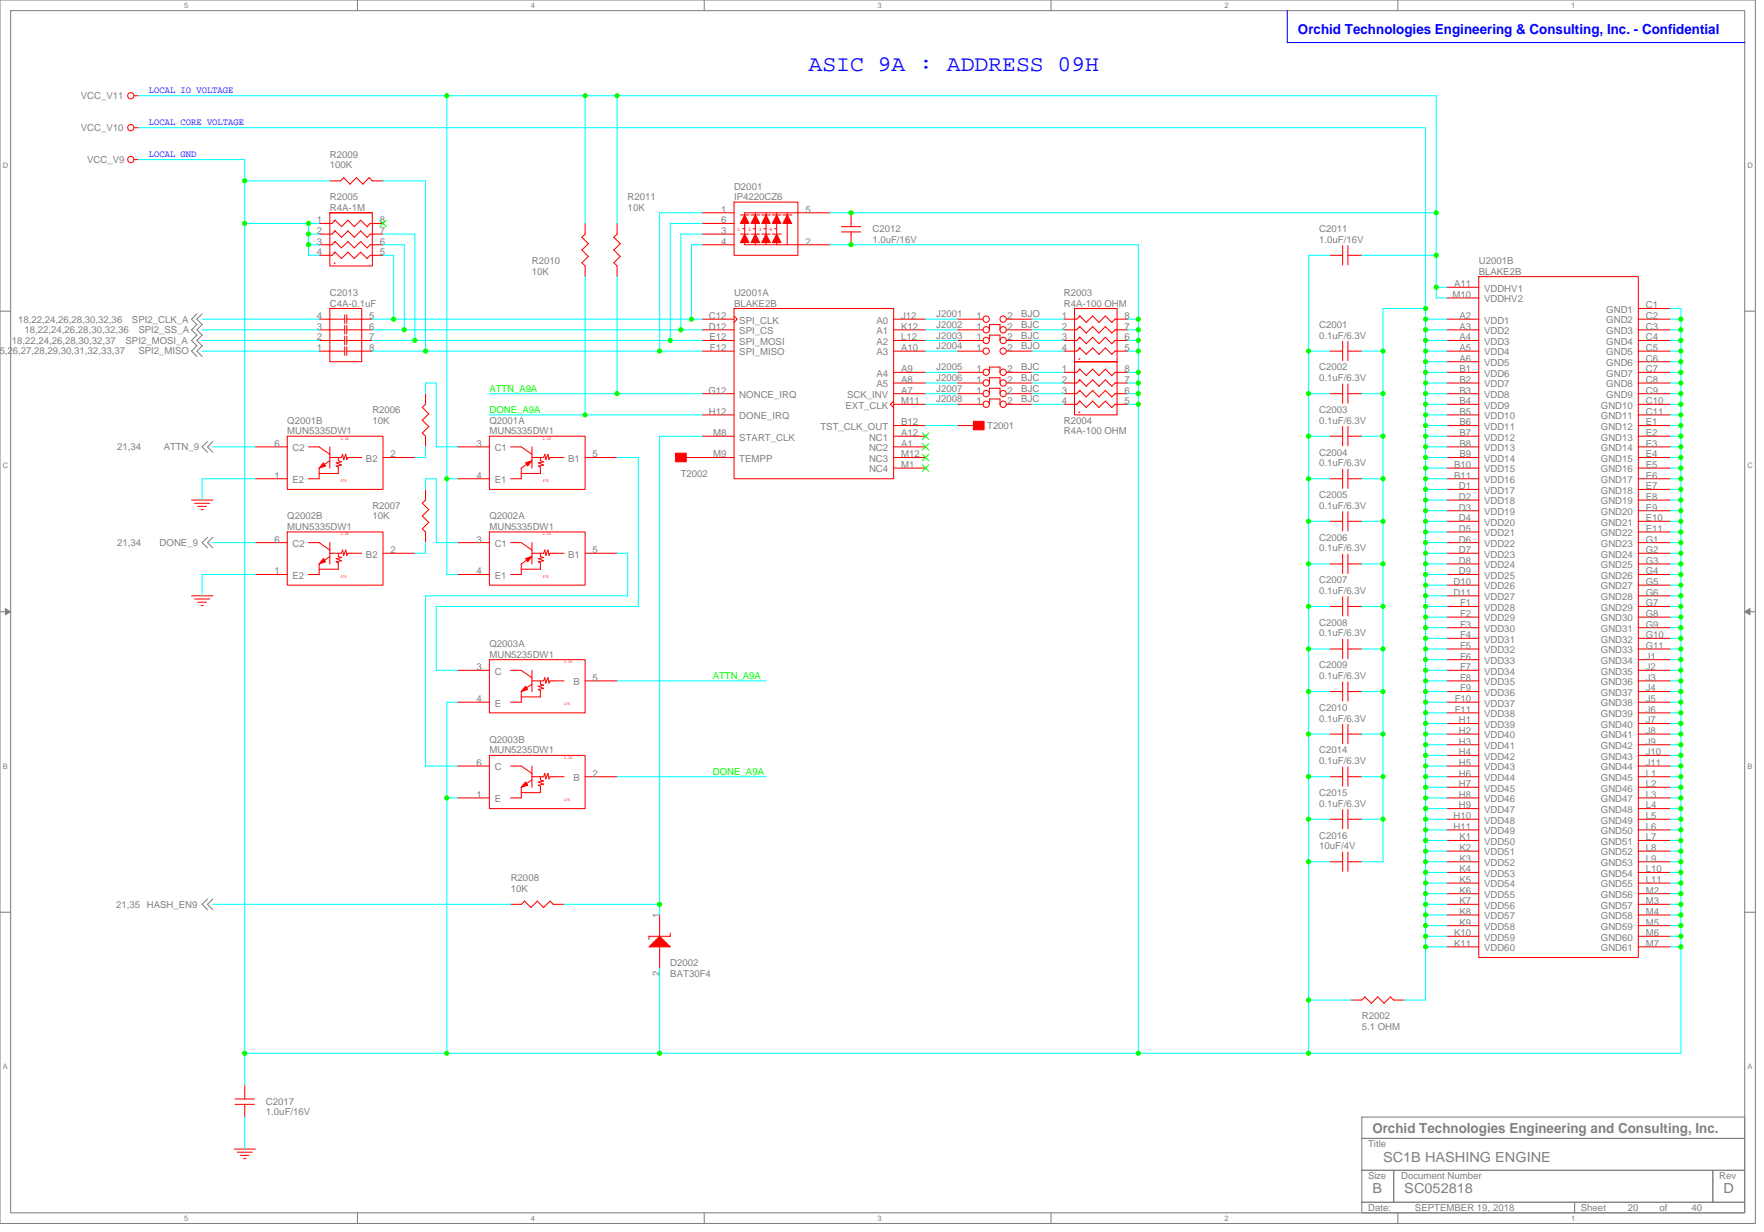
[picture p172: page 20]

Orchid Technologies Engineering and Consulting, Inc.

# ASIC 9B : ADDRESS 29H

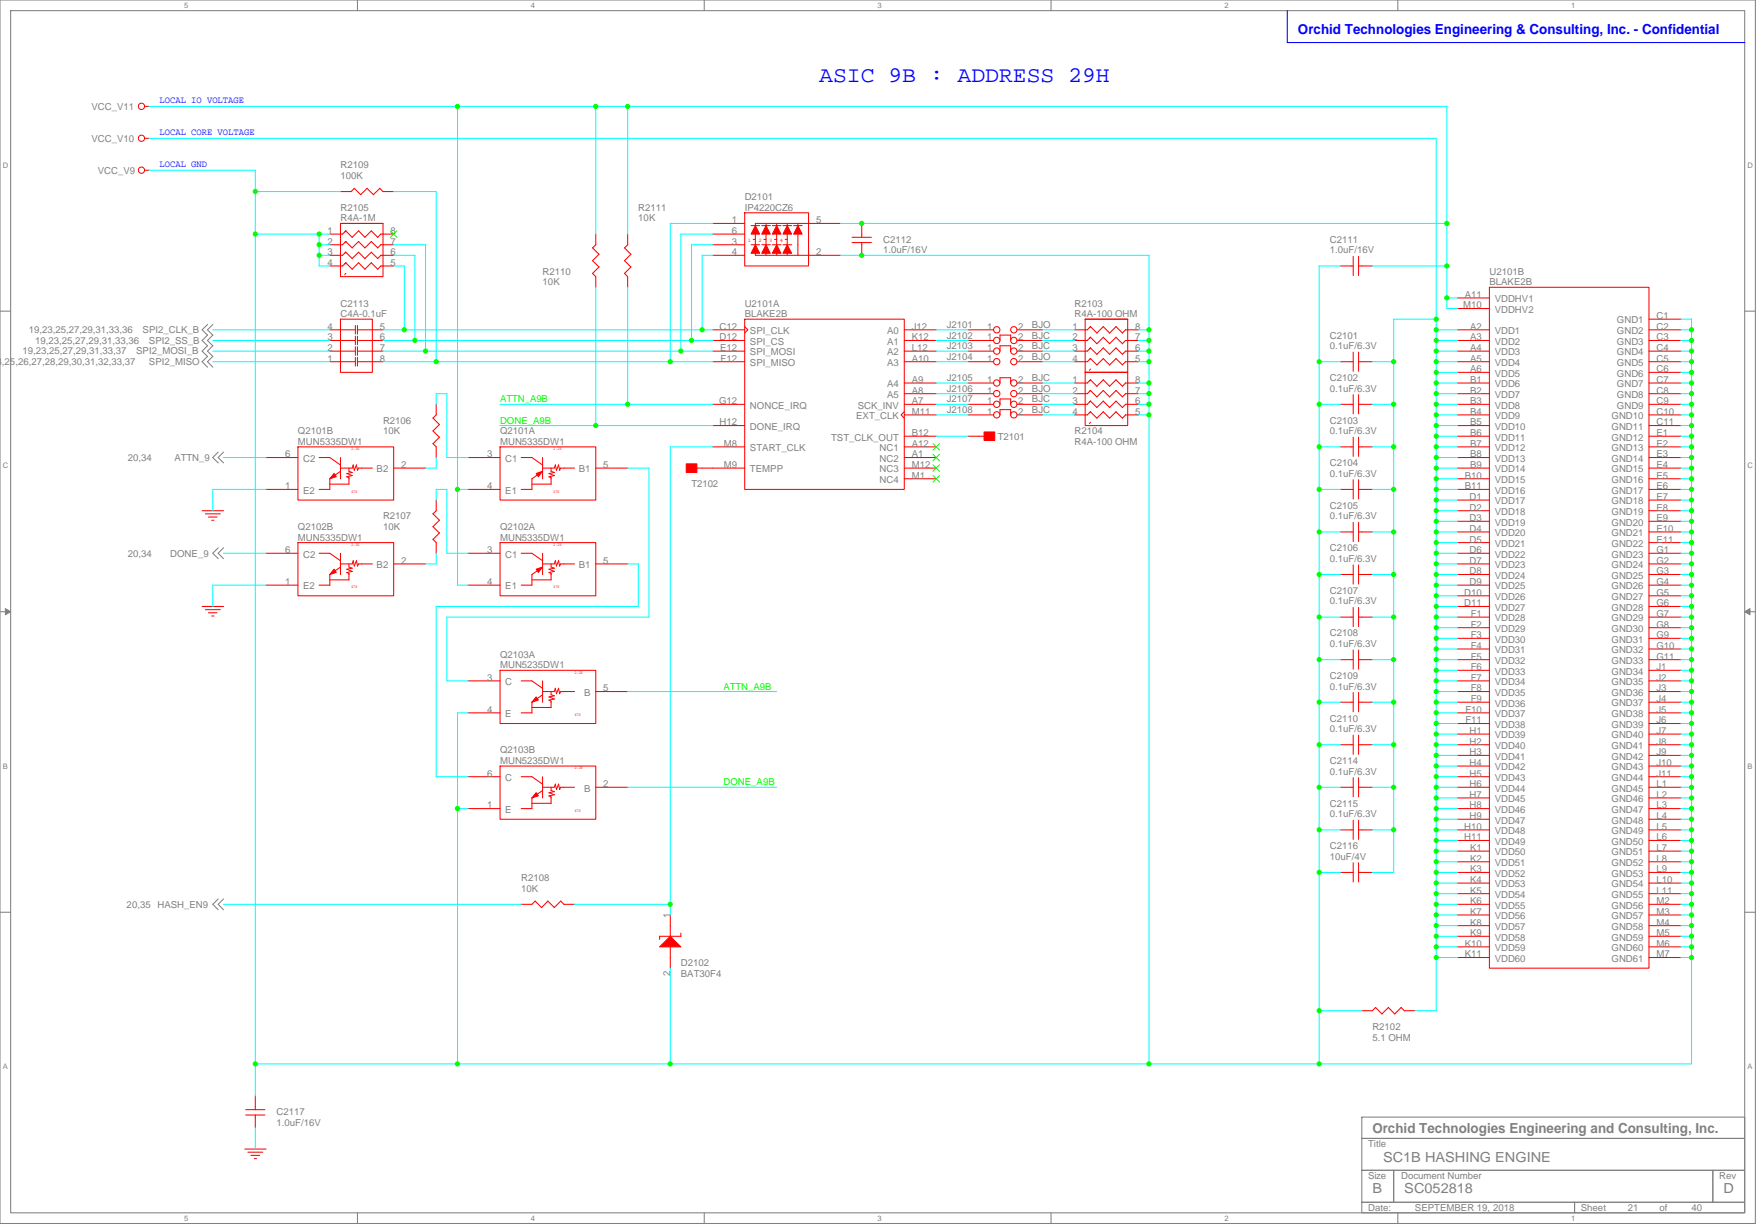
[picture p173: page 21]

Orchid Technologies Engineering and Consulting, Inc.

# ASIC 10A : ADDRESS 0AH

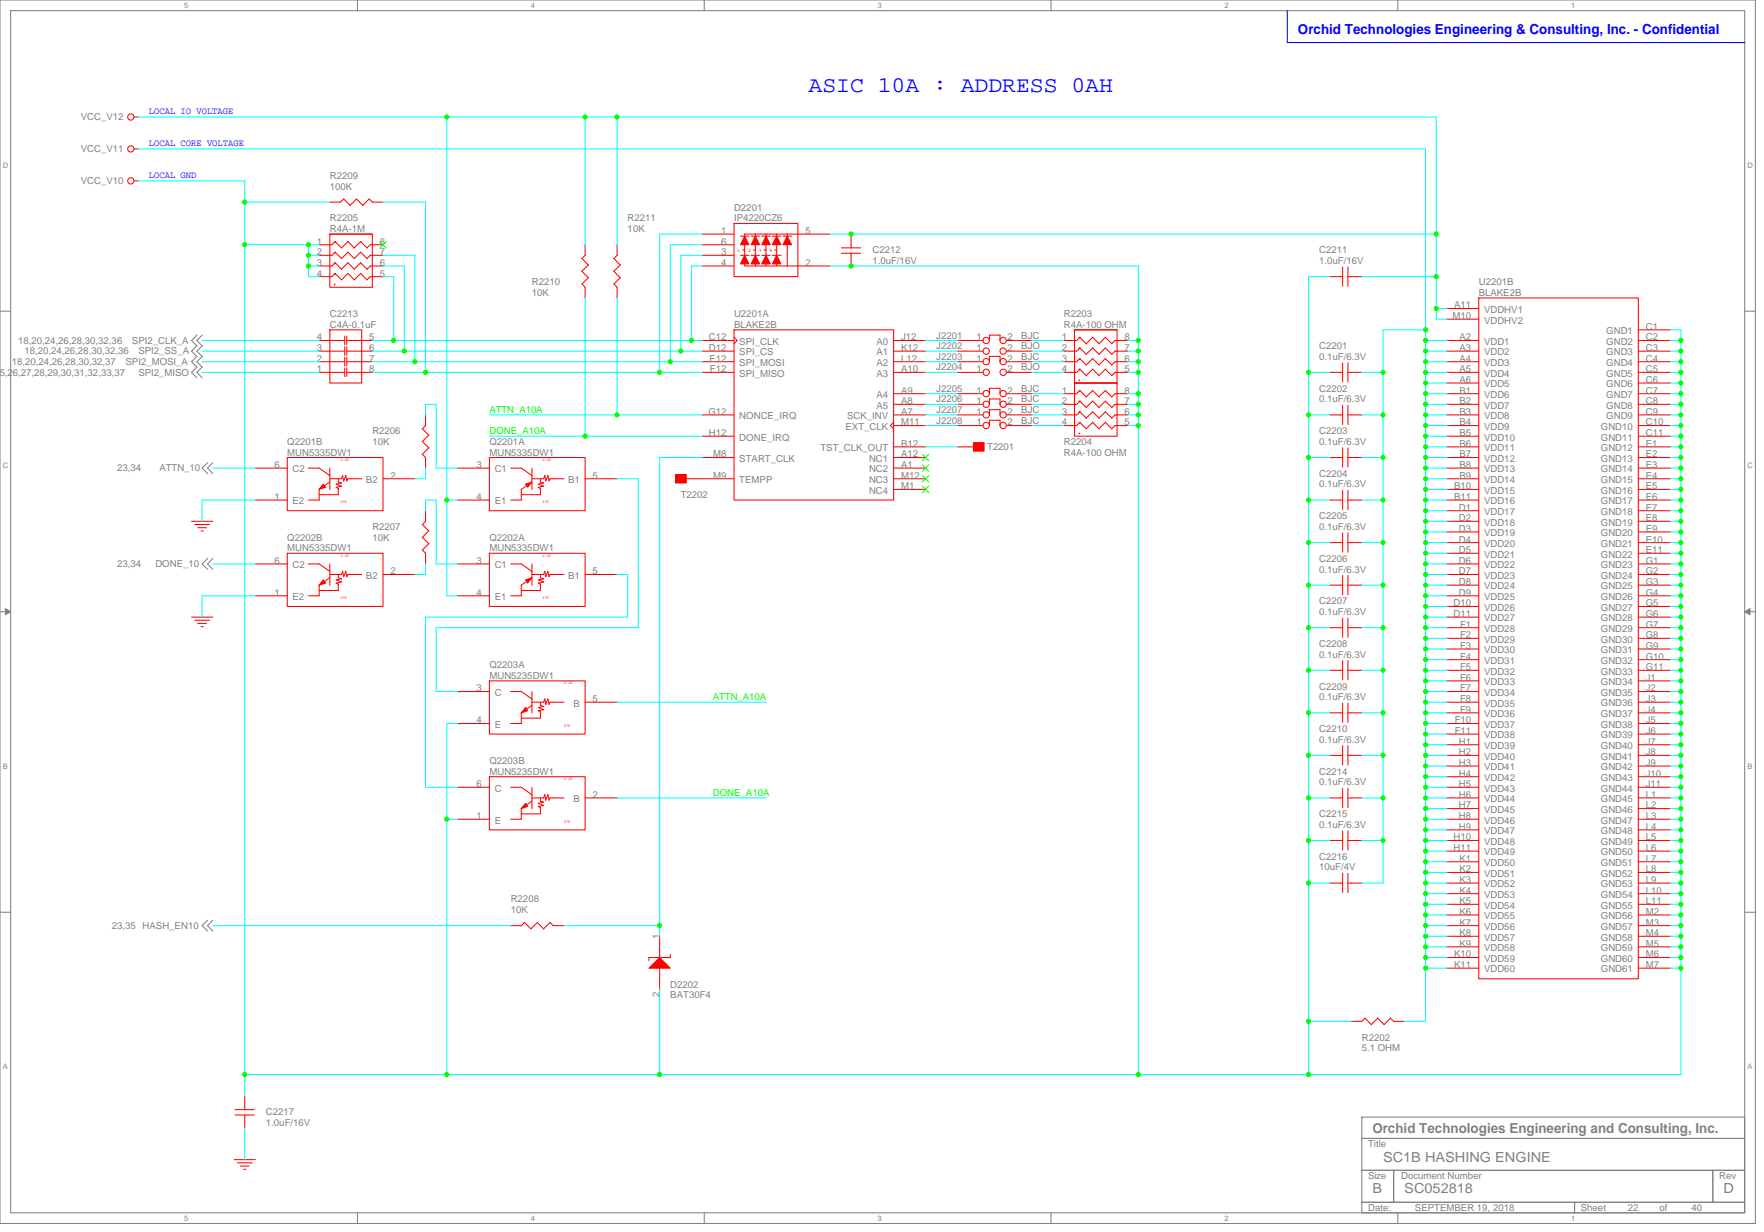
[picture p174: page 22]

Orchid Technologies Engineering and Consulting, Inc.

# ASIC 10B : ADDRESS 2AH

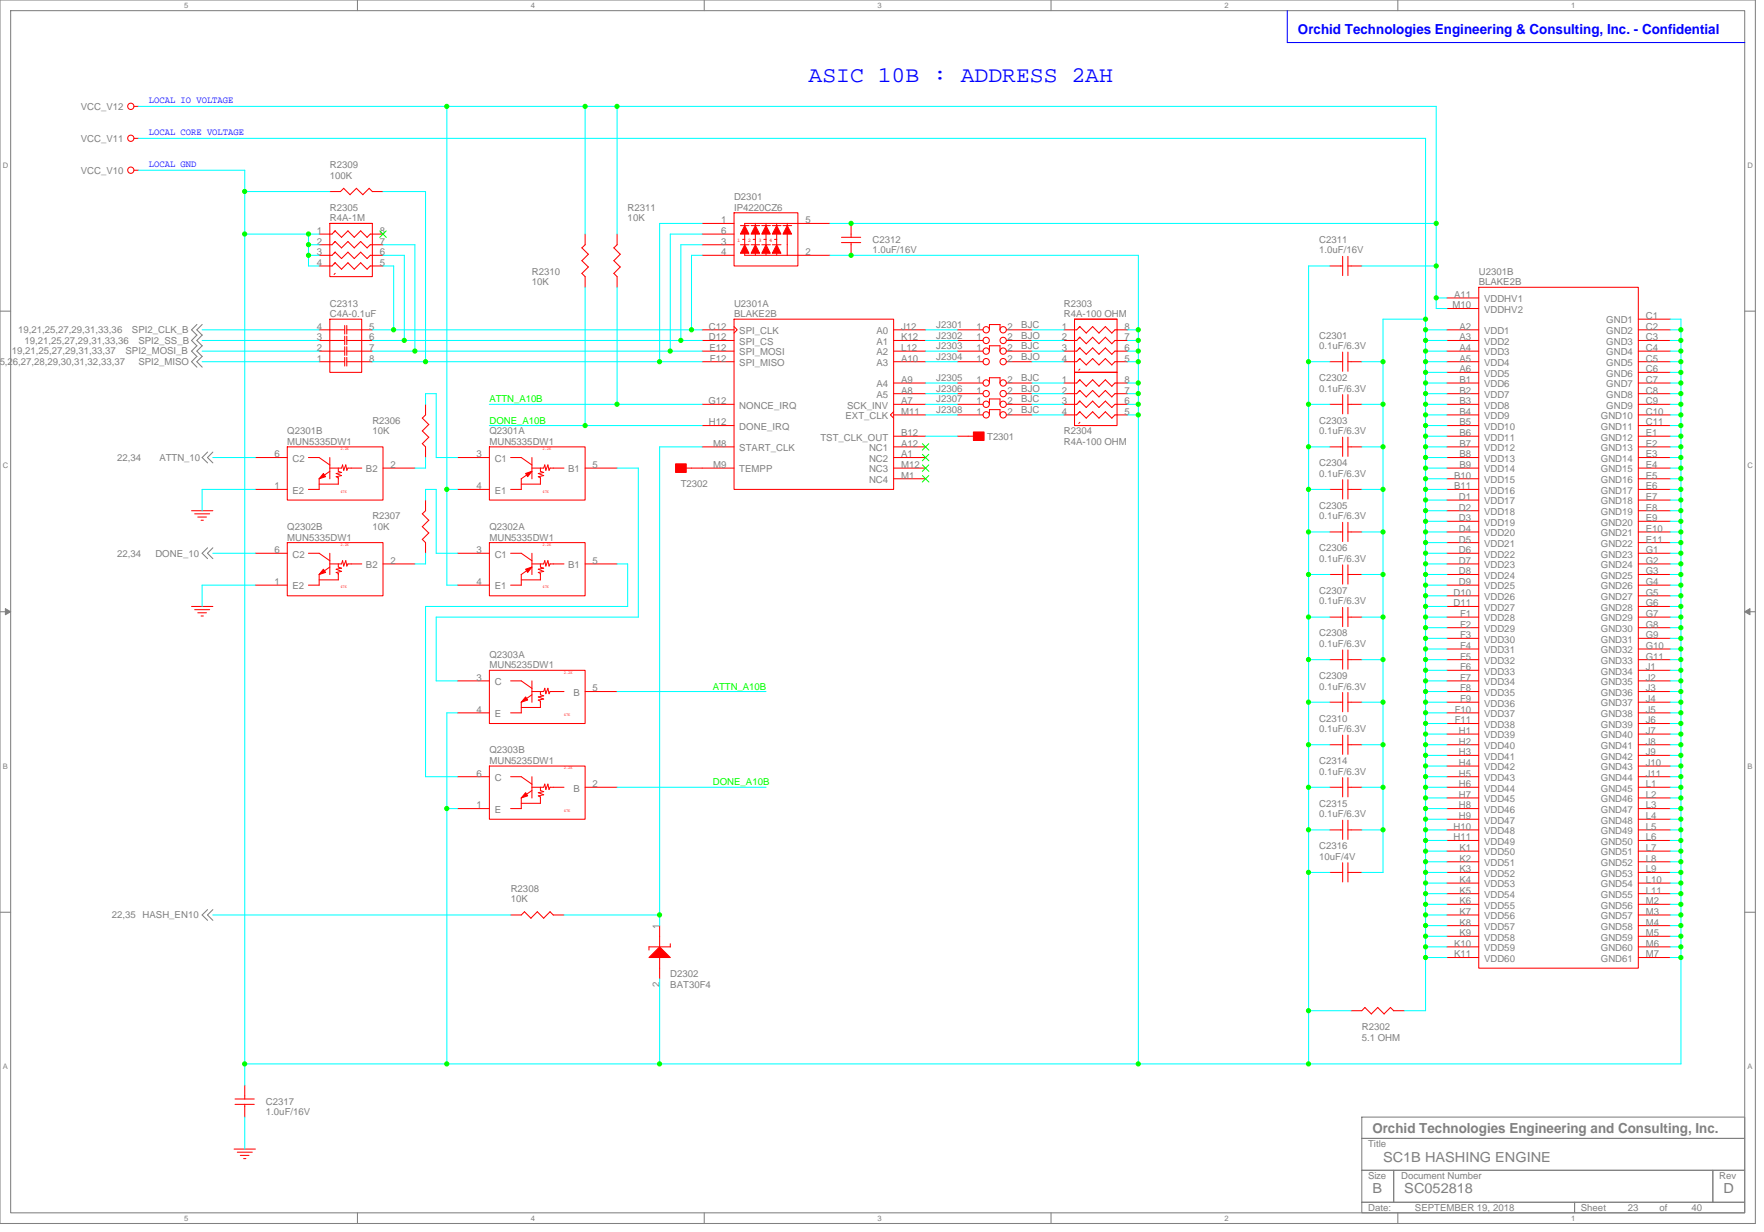
[picture p175: page 23]

Orchid Technologies Engineering and Consulting, Inc.

# ASIC 11A : ADDRESS 0BH

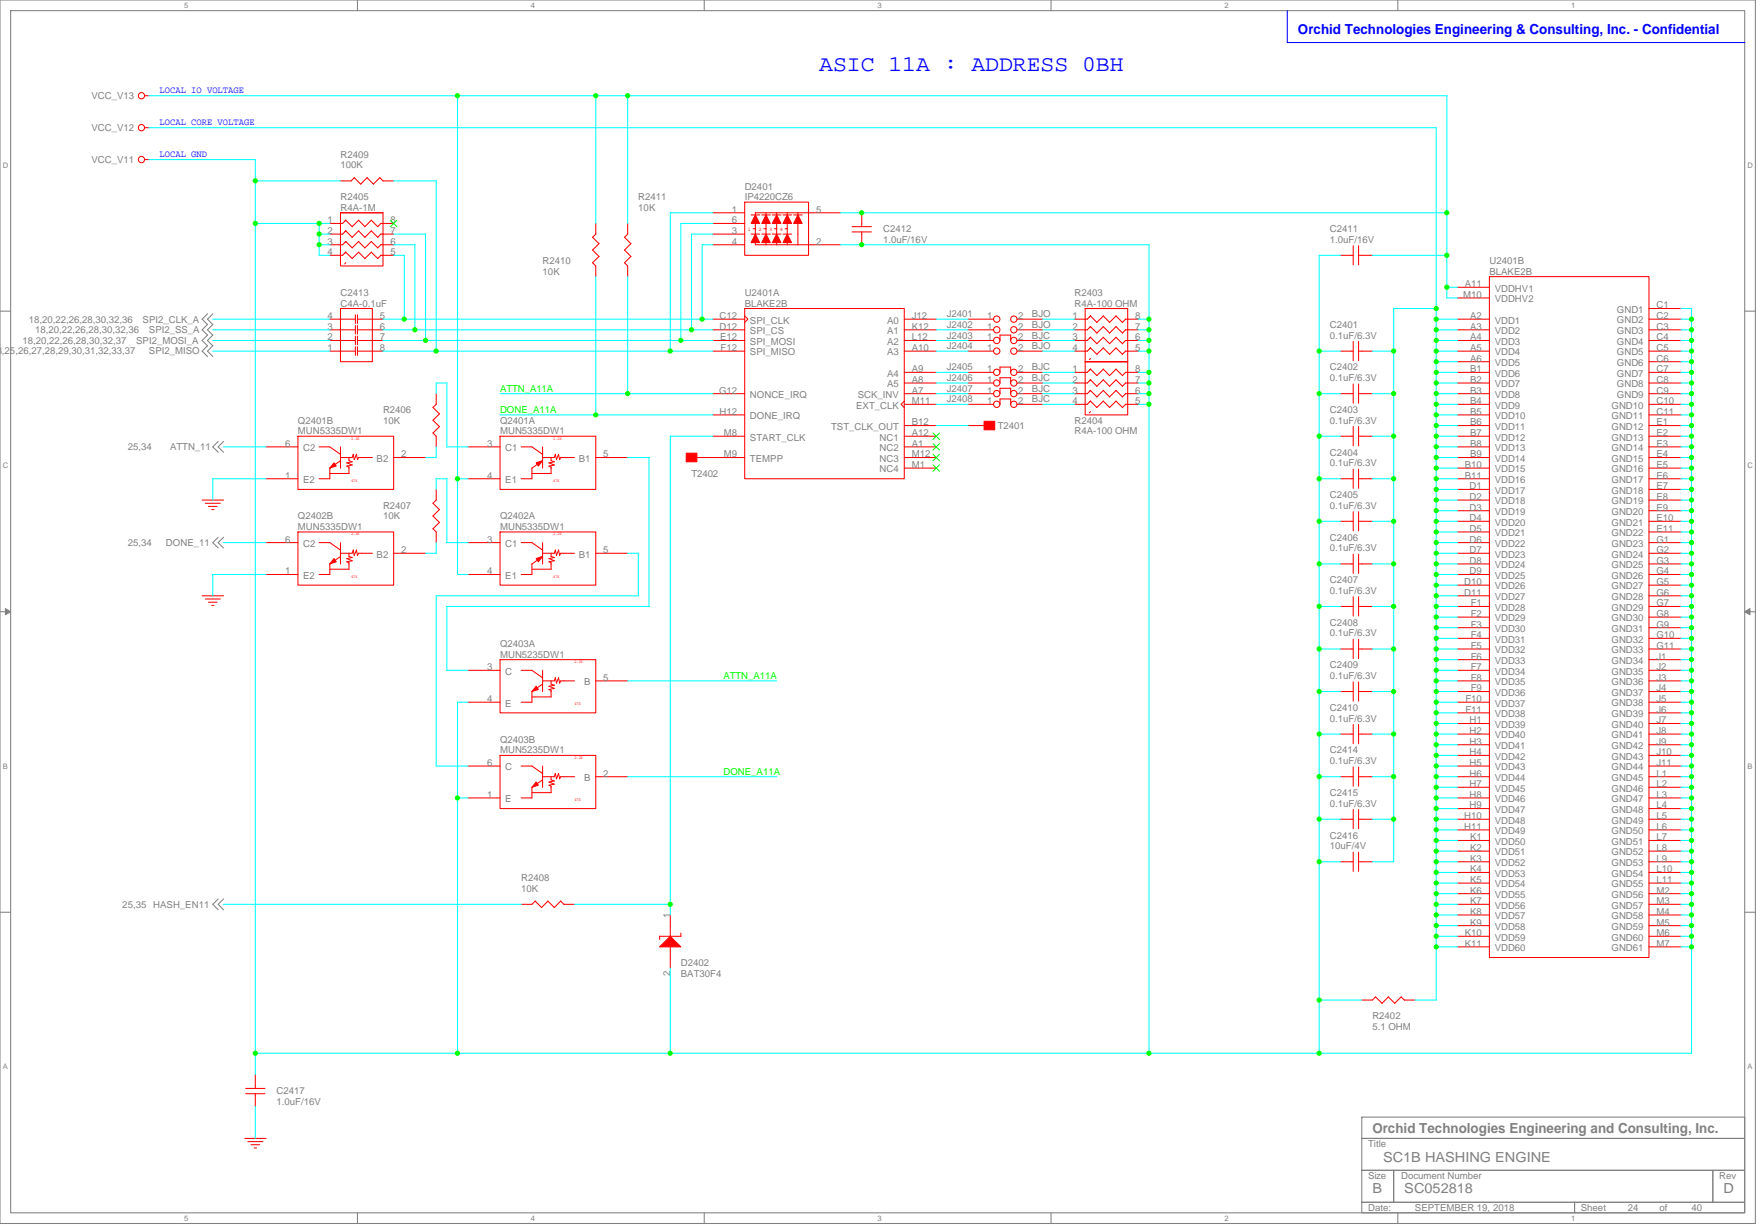
[picture p176: page 24]

Orchid Technologies Engineering and Consulting, Inc.

# ASIC 11B : ADDRESS 2BH

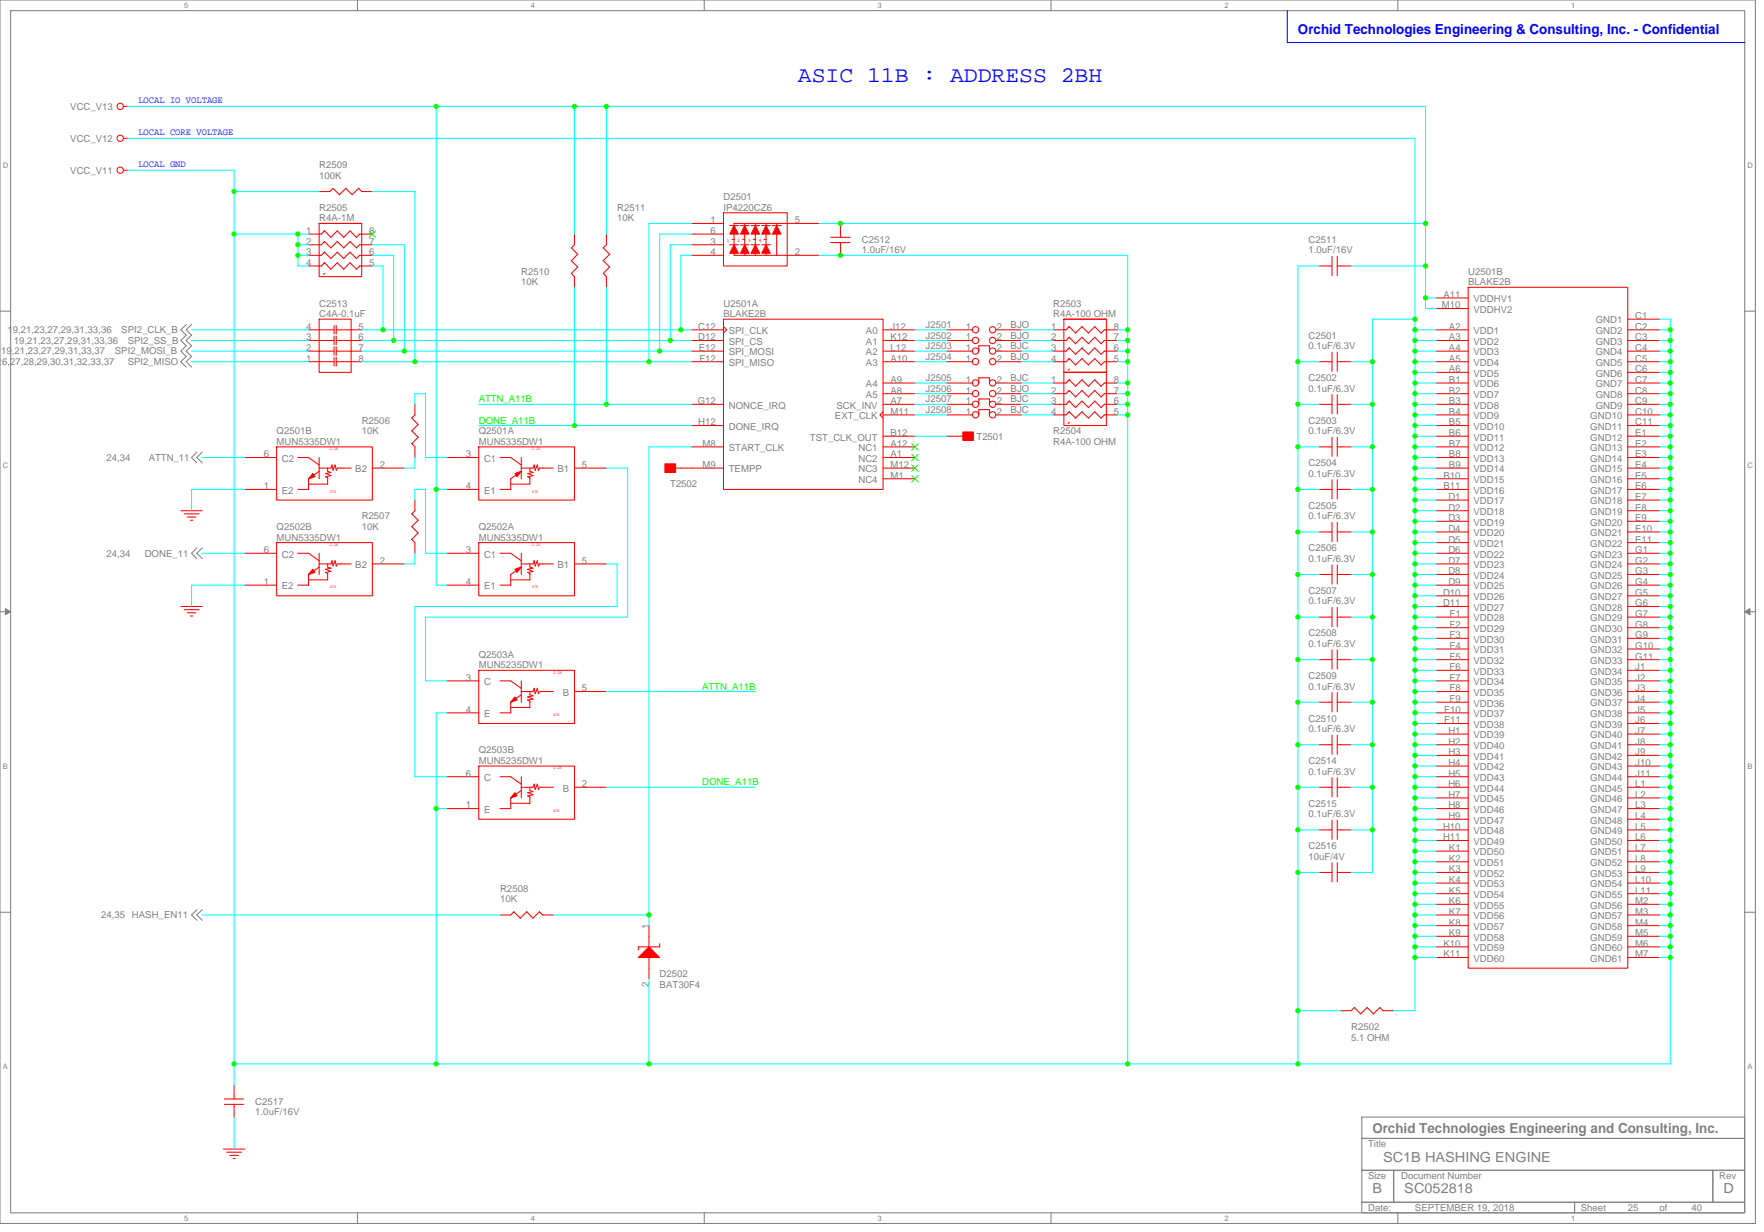
[picture p177: page 25]

Orchid Technologies Engineering and Consulting, Inc.

# ASIC 12A : ADDRESS 0CH

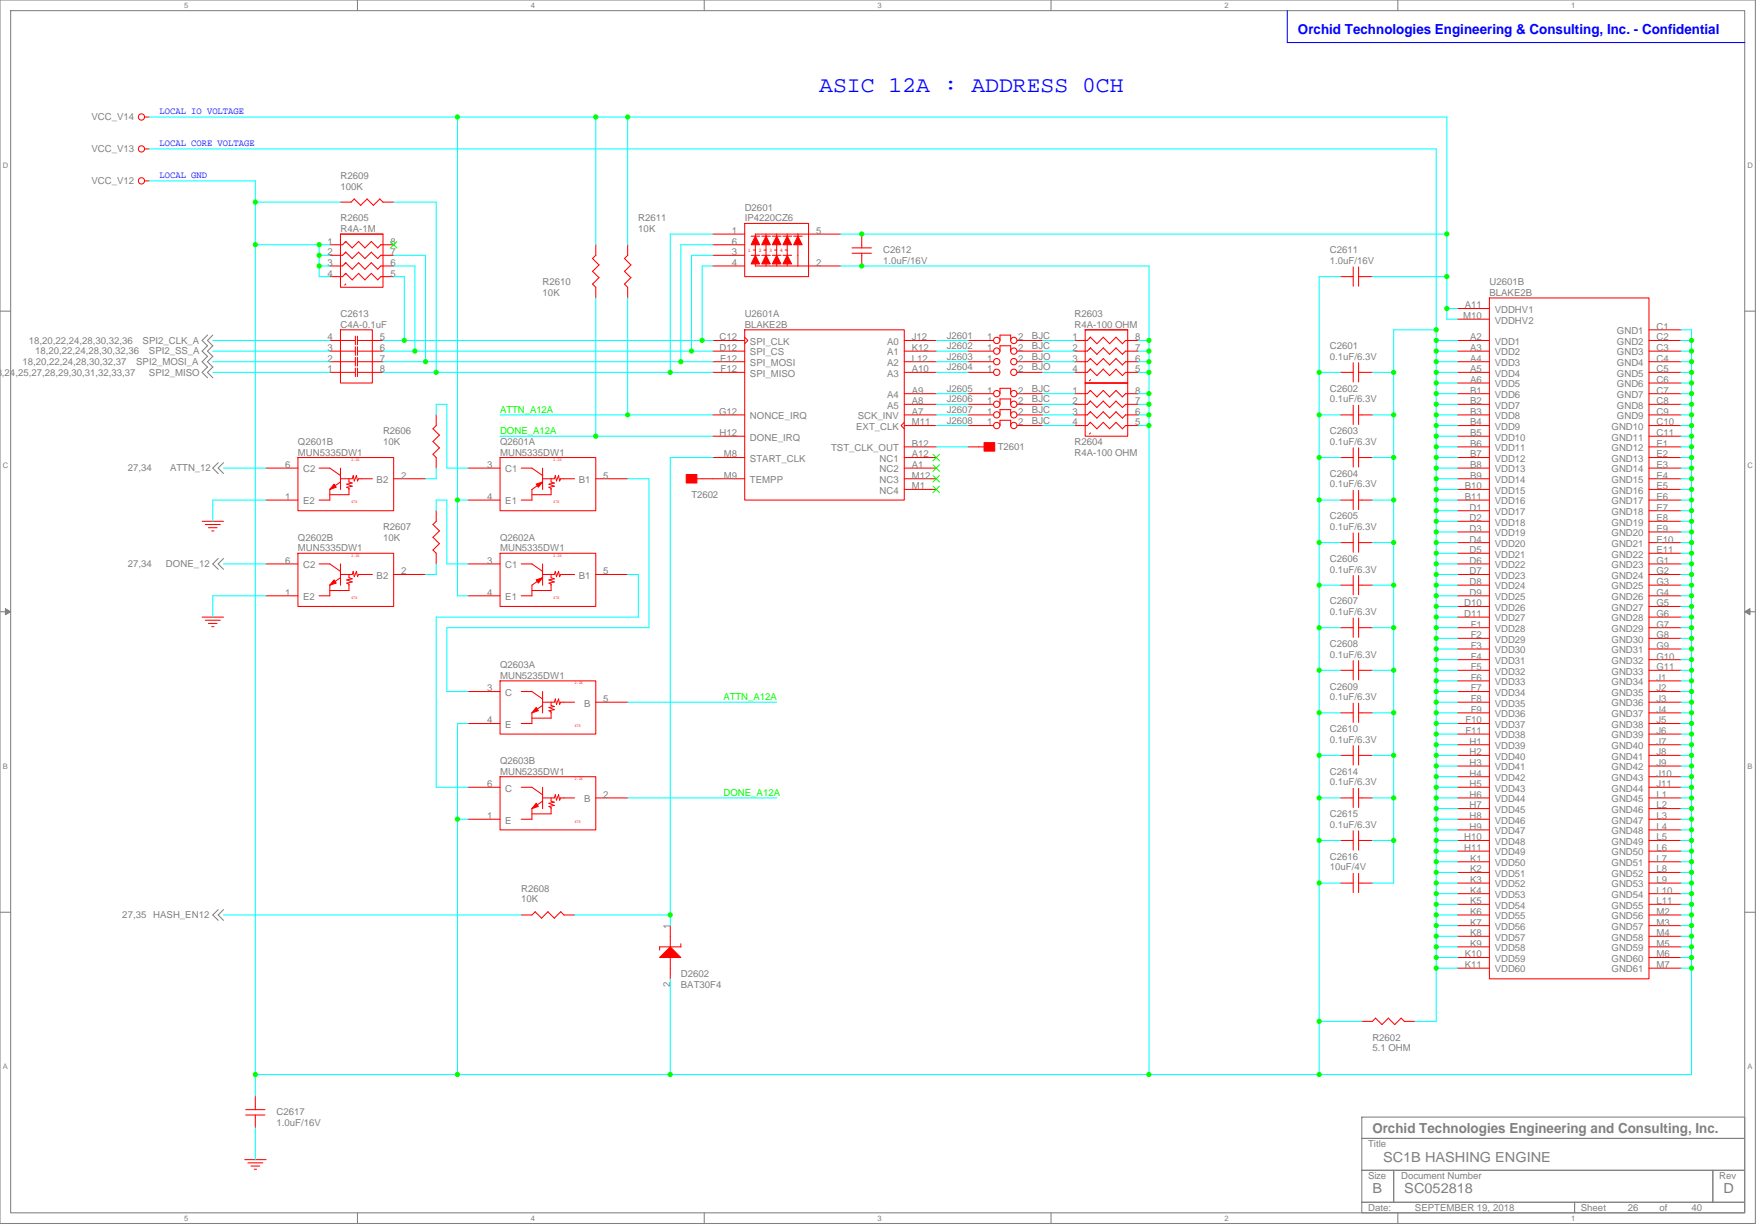
[picture p178: page 26]

Orchid Technologies Engineering and Consulting, Inc.

# ASIC 12B : ADDRESS 2CH

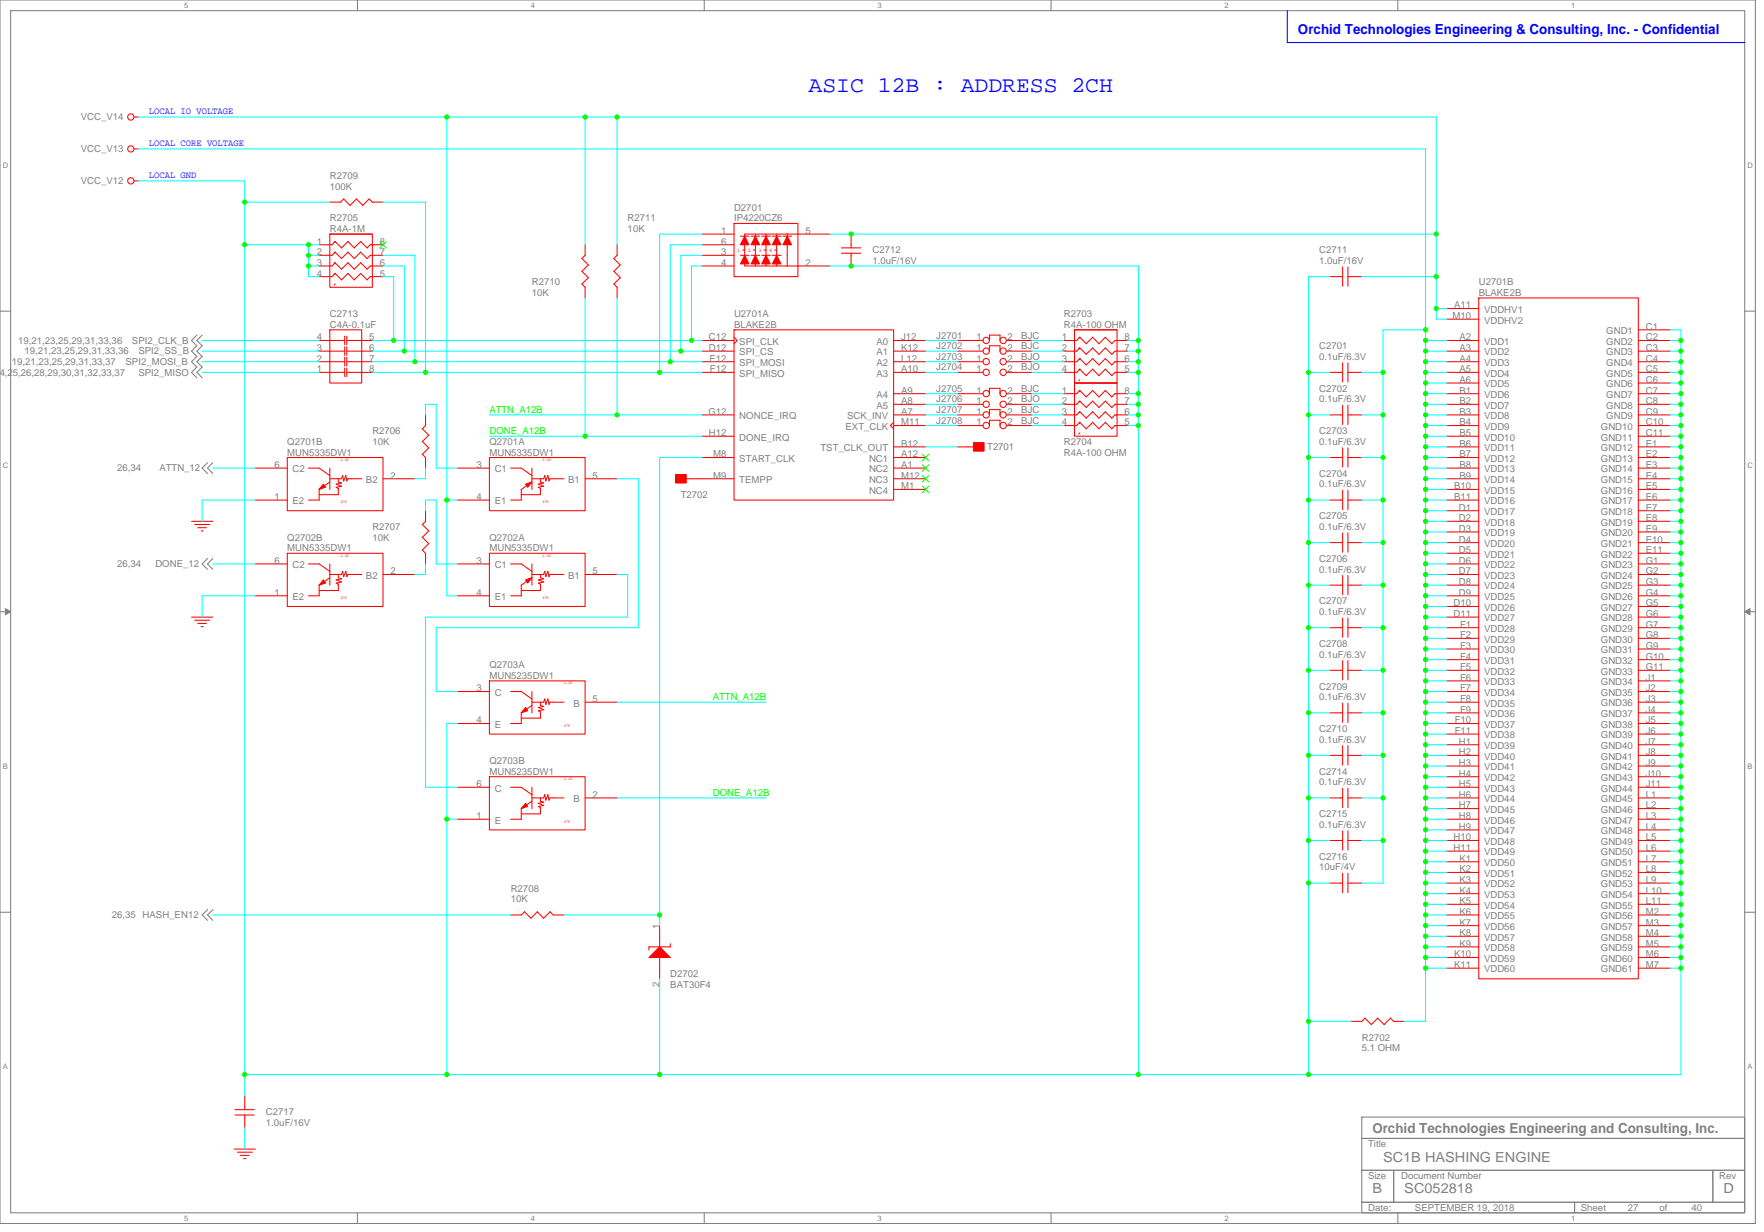
[picture p179: page 27]

Orchid Technologies Engineering and Consulting, Inc.

# ASIC 13A : ADDRESS 0DH

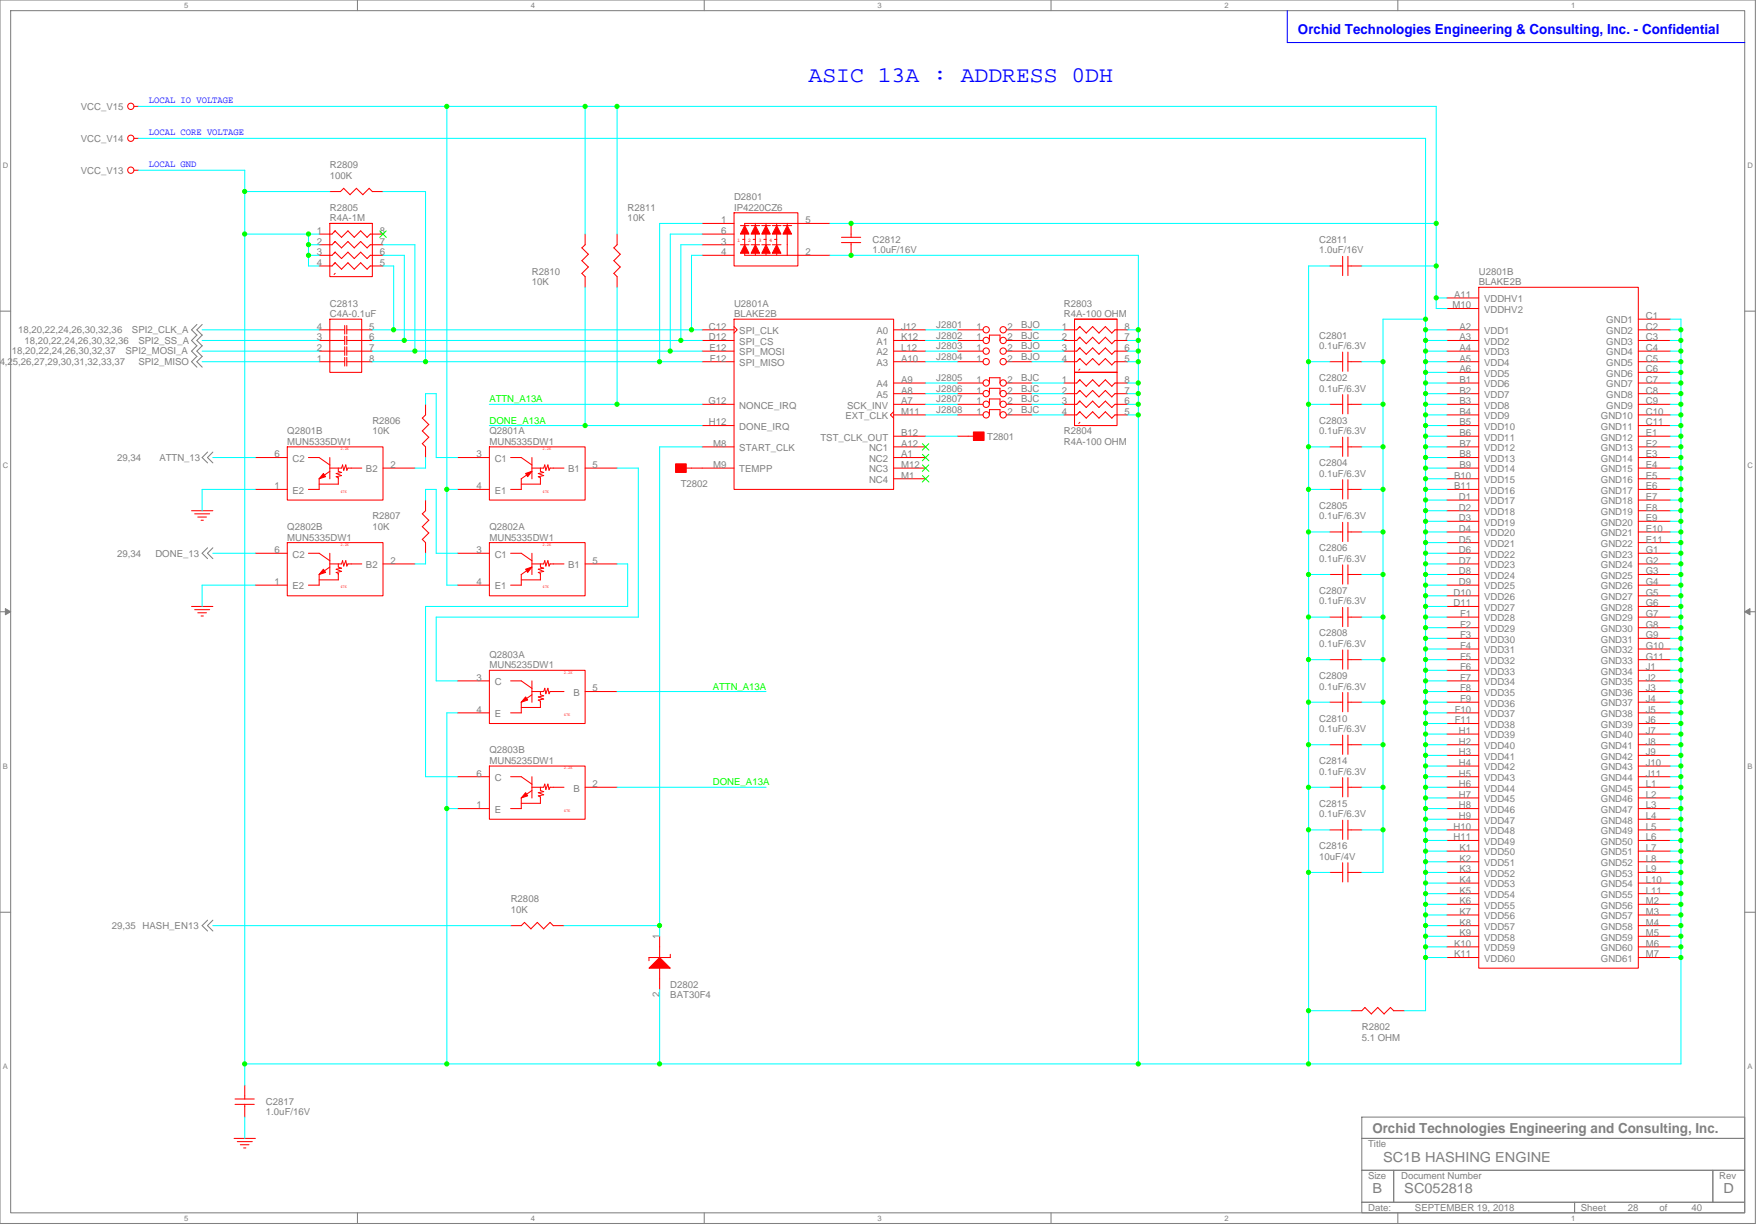
[picture p180: page 28]

Orchid Technologies Engineering and Consulting, Inc.

# ASIC 13B : ADDRESS 2DH

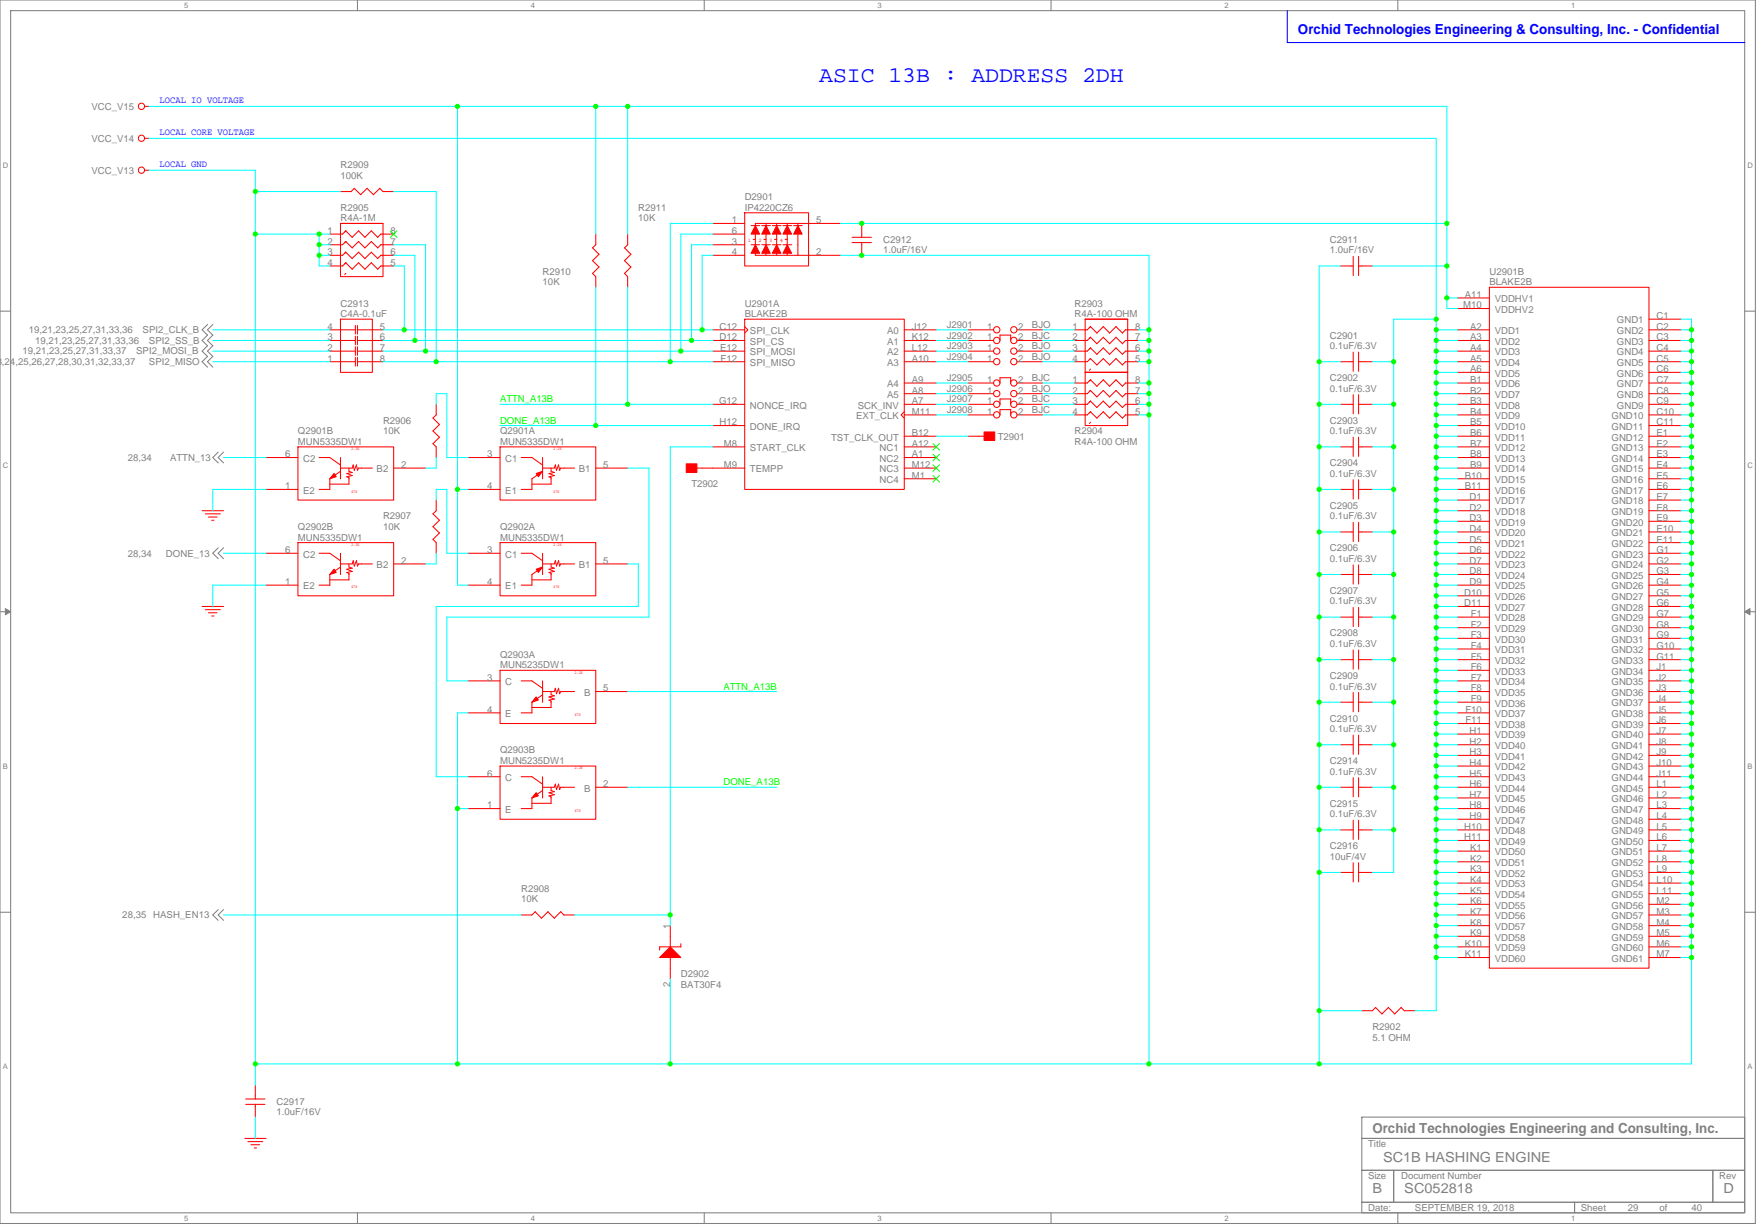
[picture p181: page 29]

Orchid Technologies Engineering and Consulting, Inc.

# ASIC 14A : ADDRESS 0EH

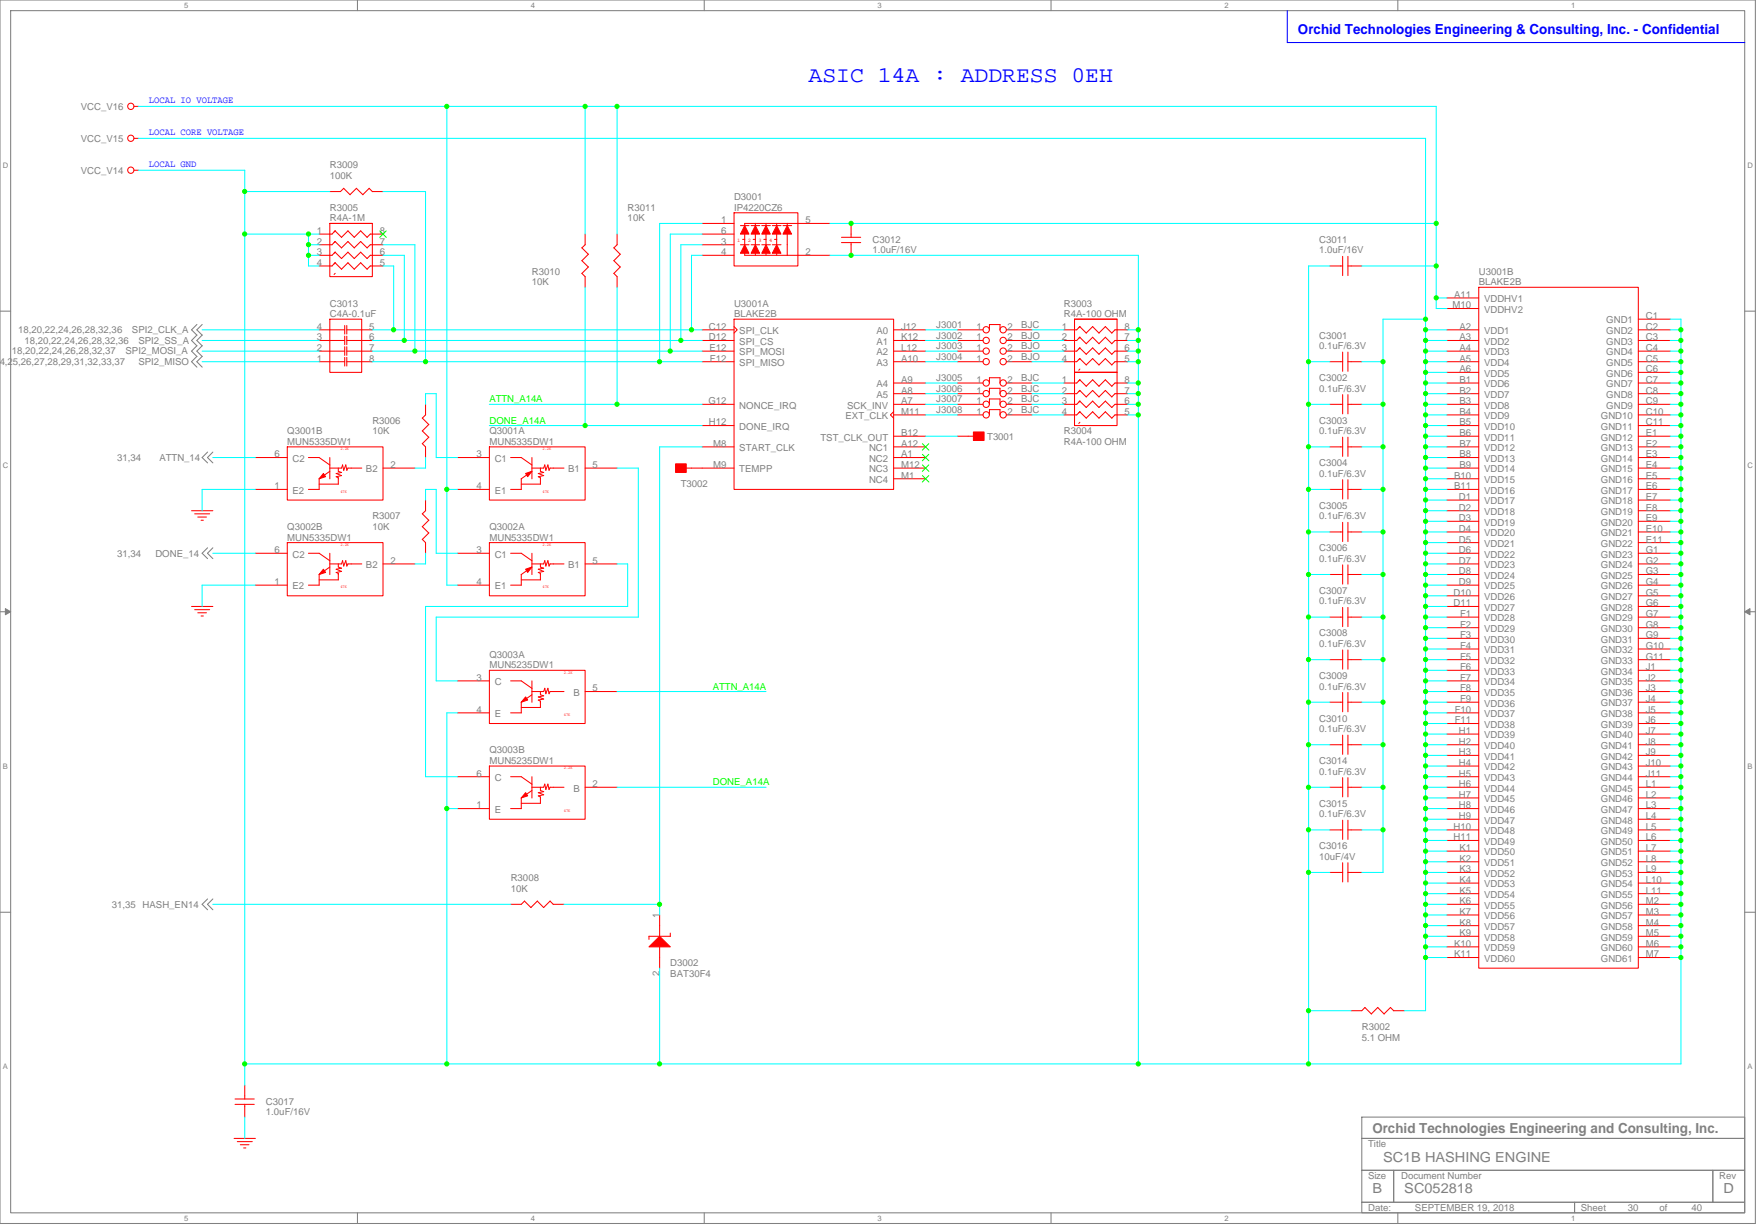
[picture p182: page 30]

Orchid Technologies Engineering and Consulting, Inc.

# ASIC 14B : ADDRESS 2EH

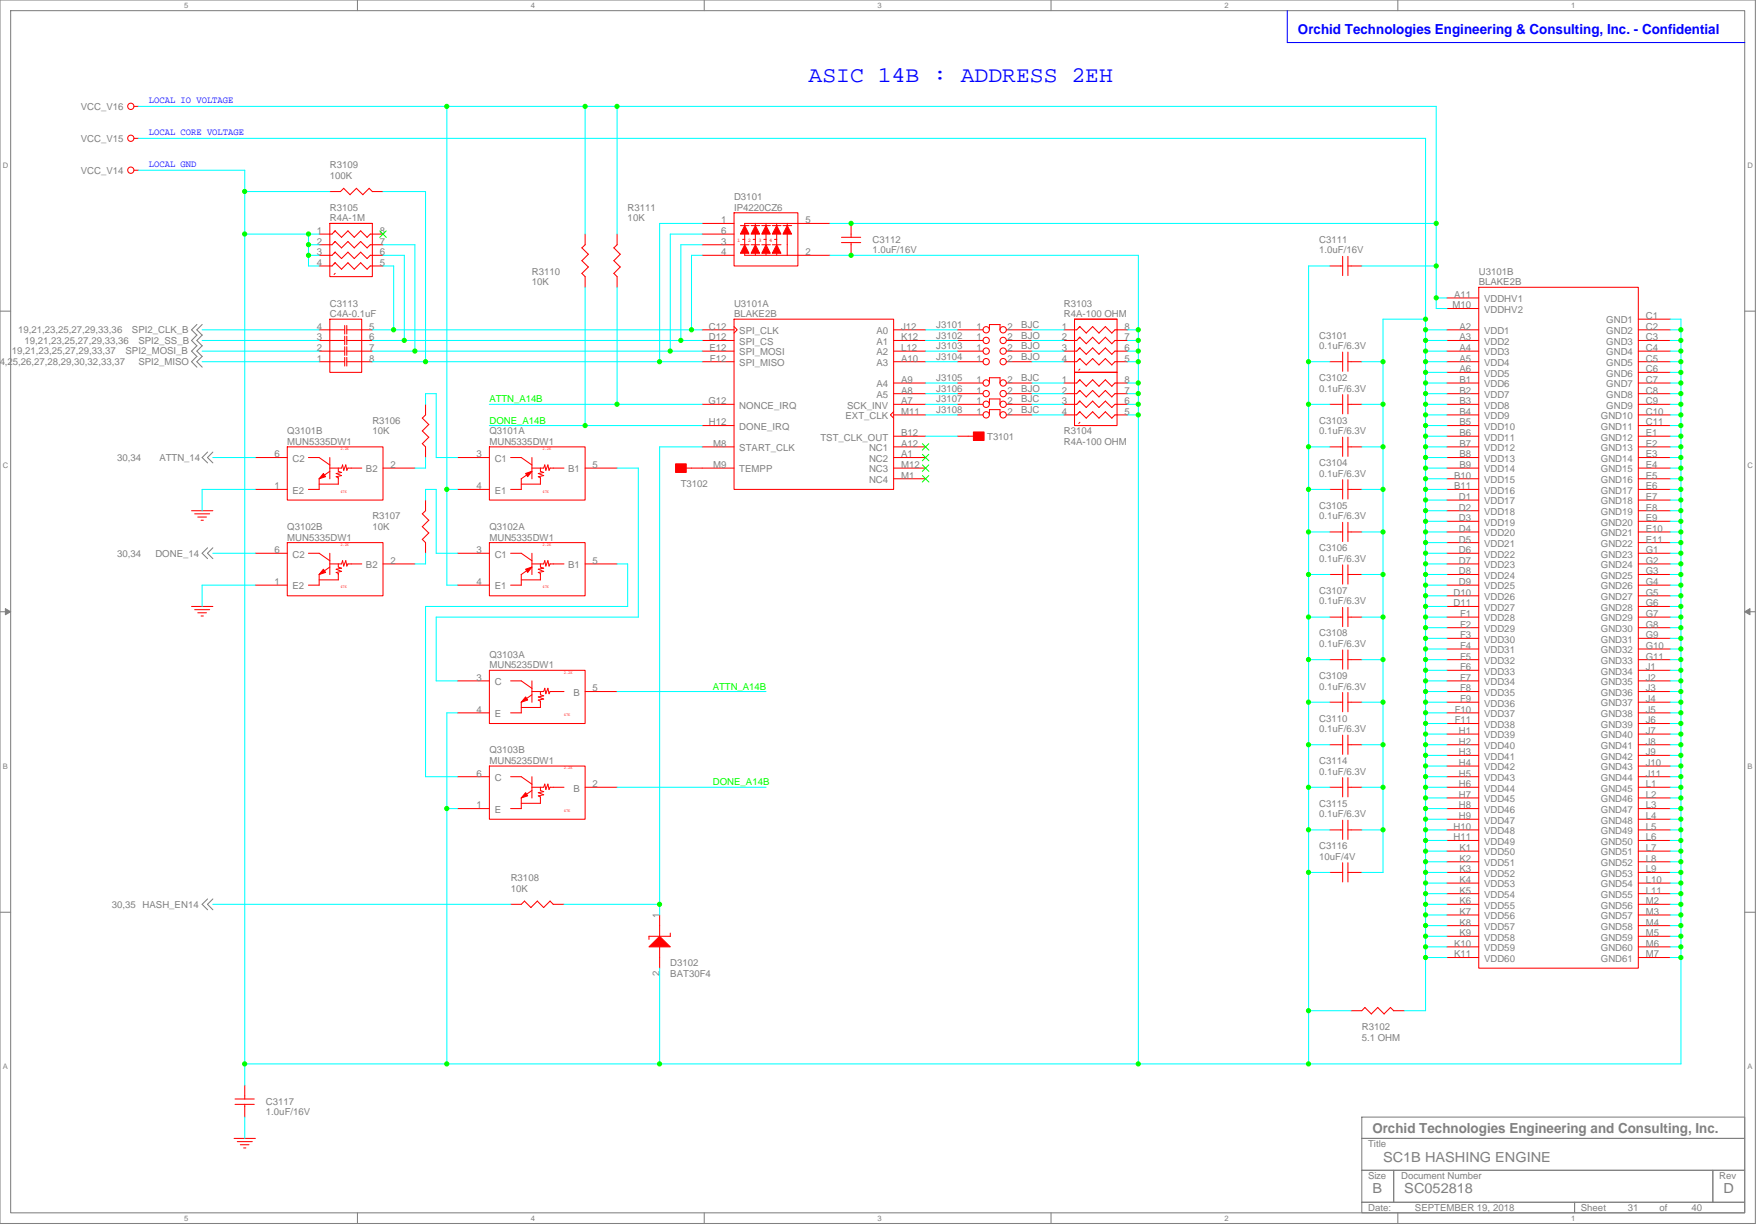
[picture p183: page 31]

Orchid Technologies Engineering and Consulting, Inc.

# ASIC 15A : ADDRESS 0FH

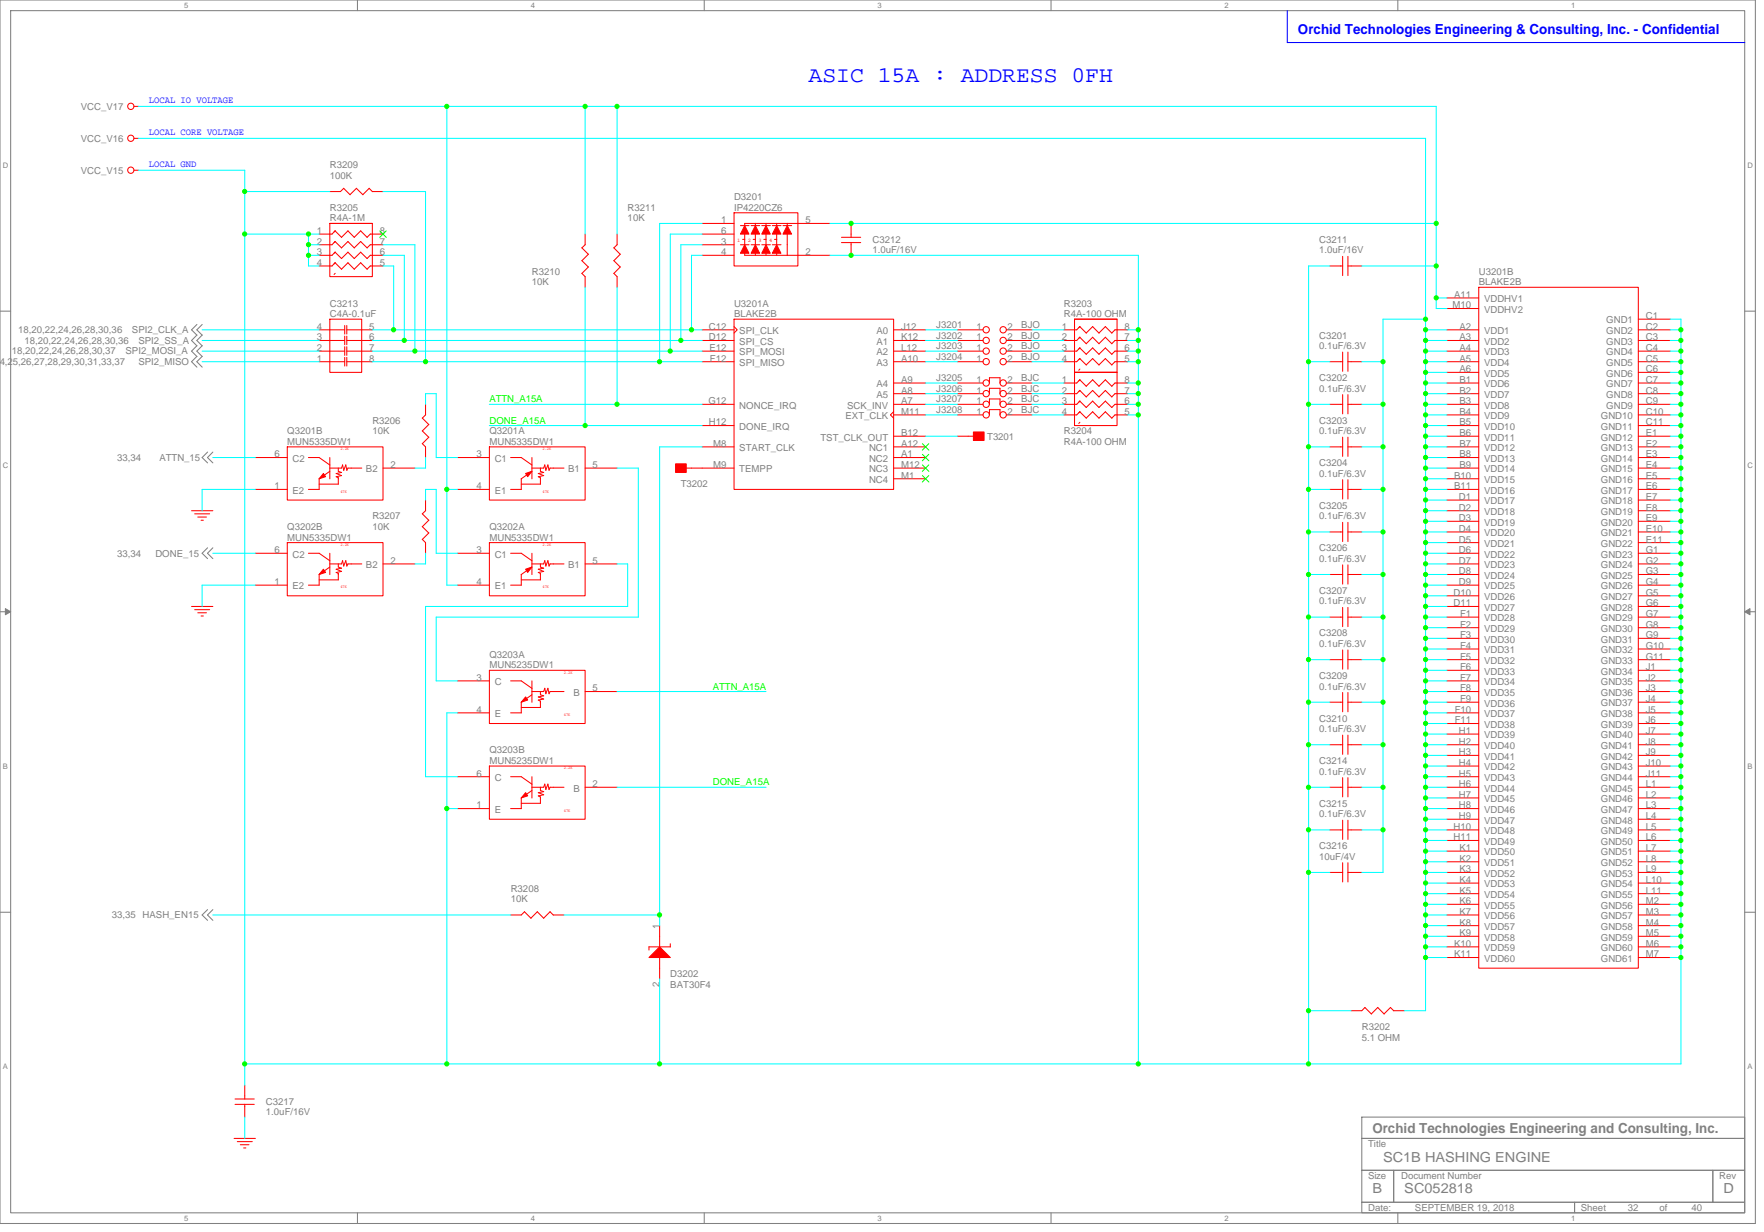
[picture p184: page 32]

Orchid Technologies Engineering and Consulting, Inc.

# ASIC 15B : ADDRESS 2FH

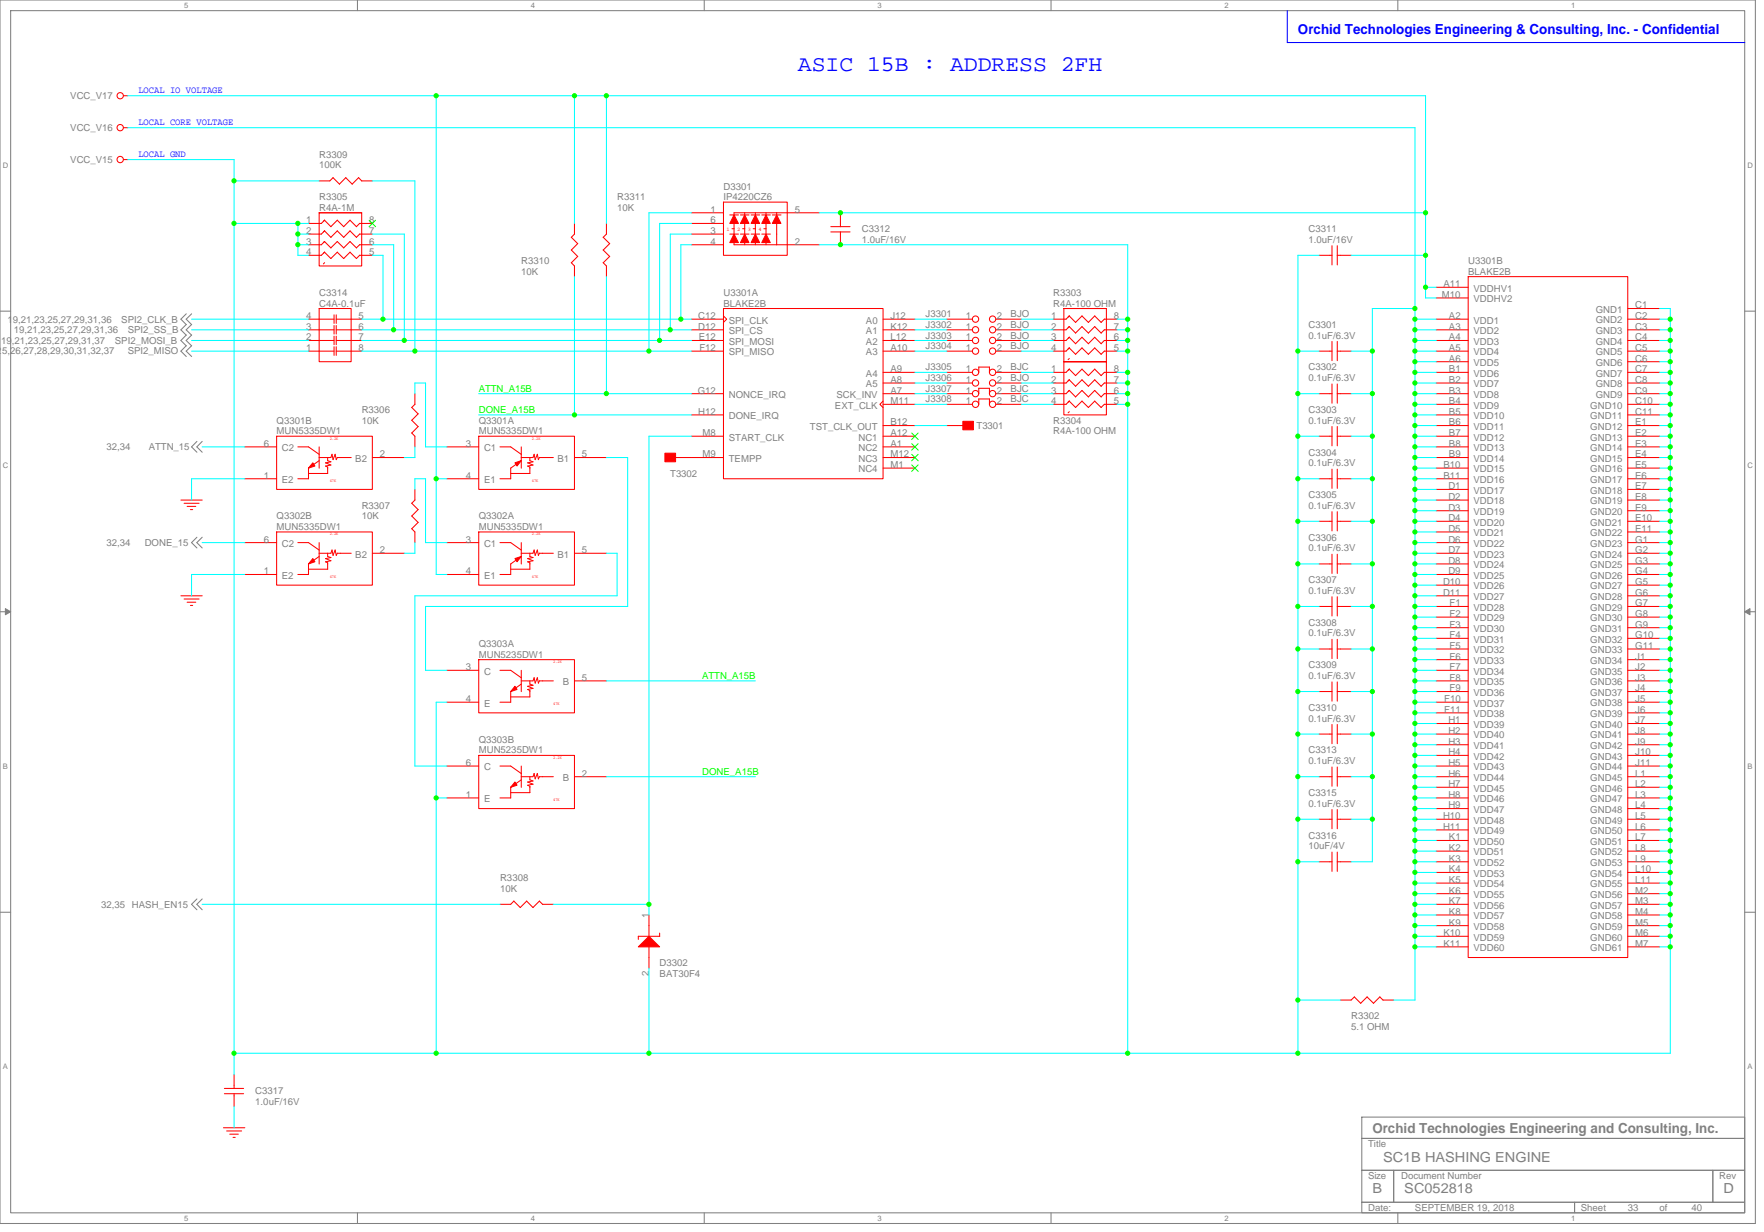
[picture p185: page 33]

Orchid Technologies Engineering and Consulting, Inc.

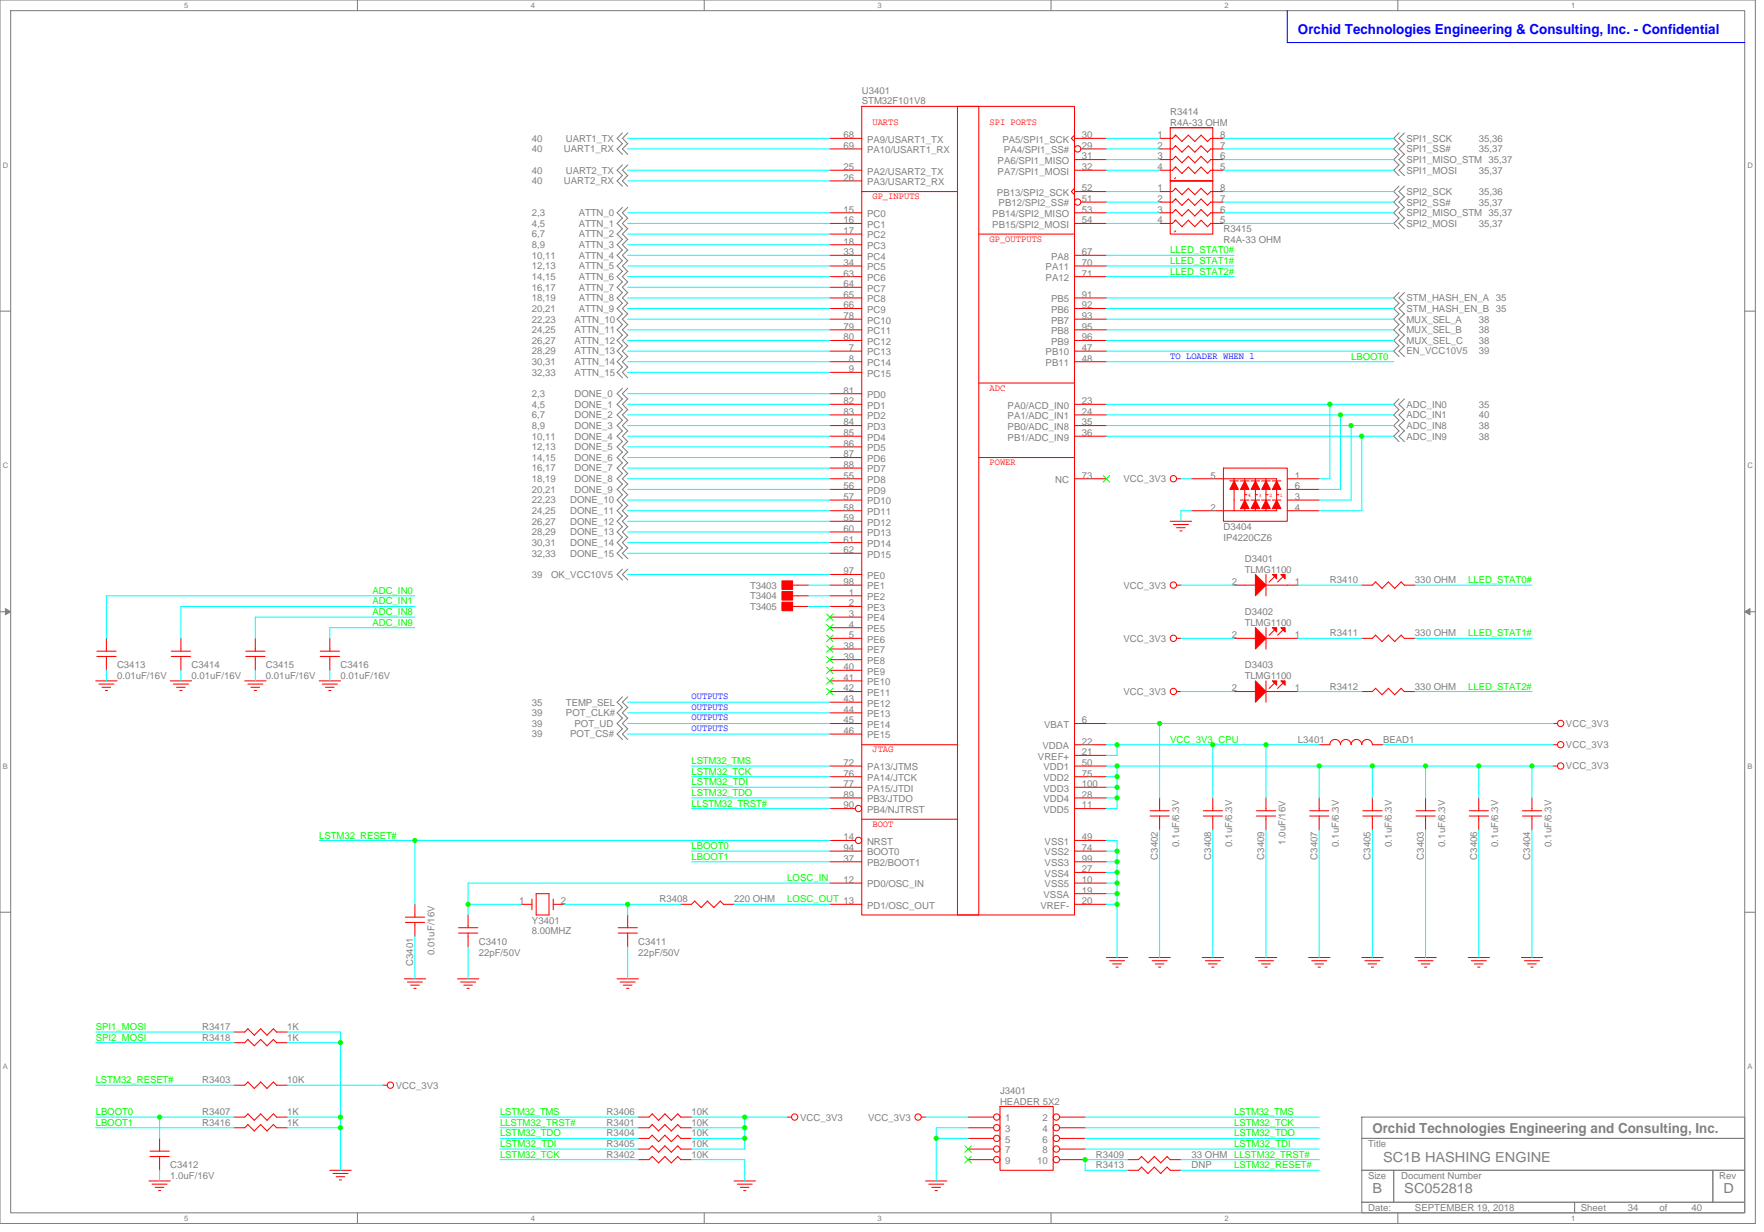
[picture p186: page 34]

Orchid Technologies Engineering and Consulting, Inc.

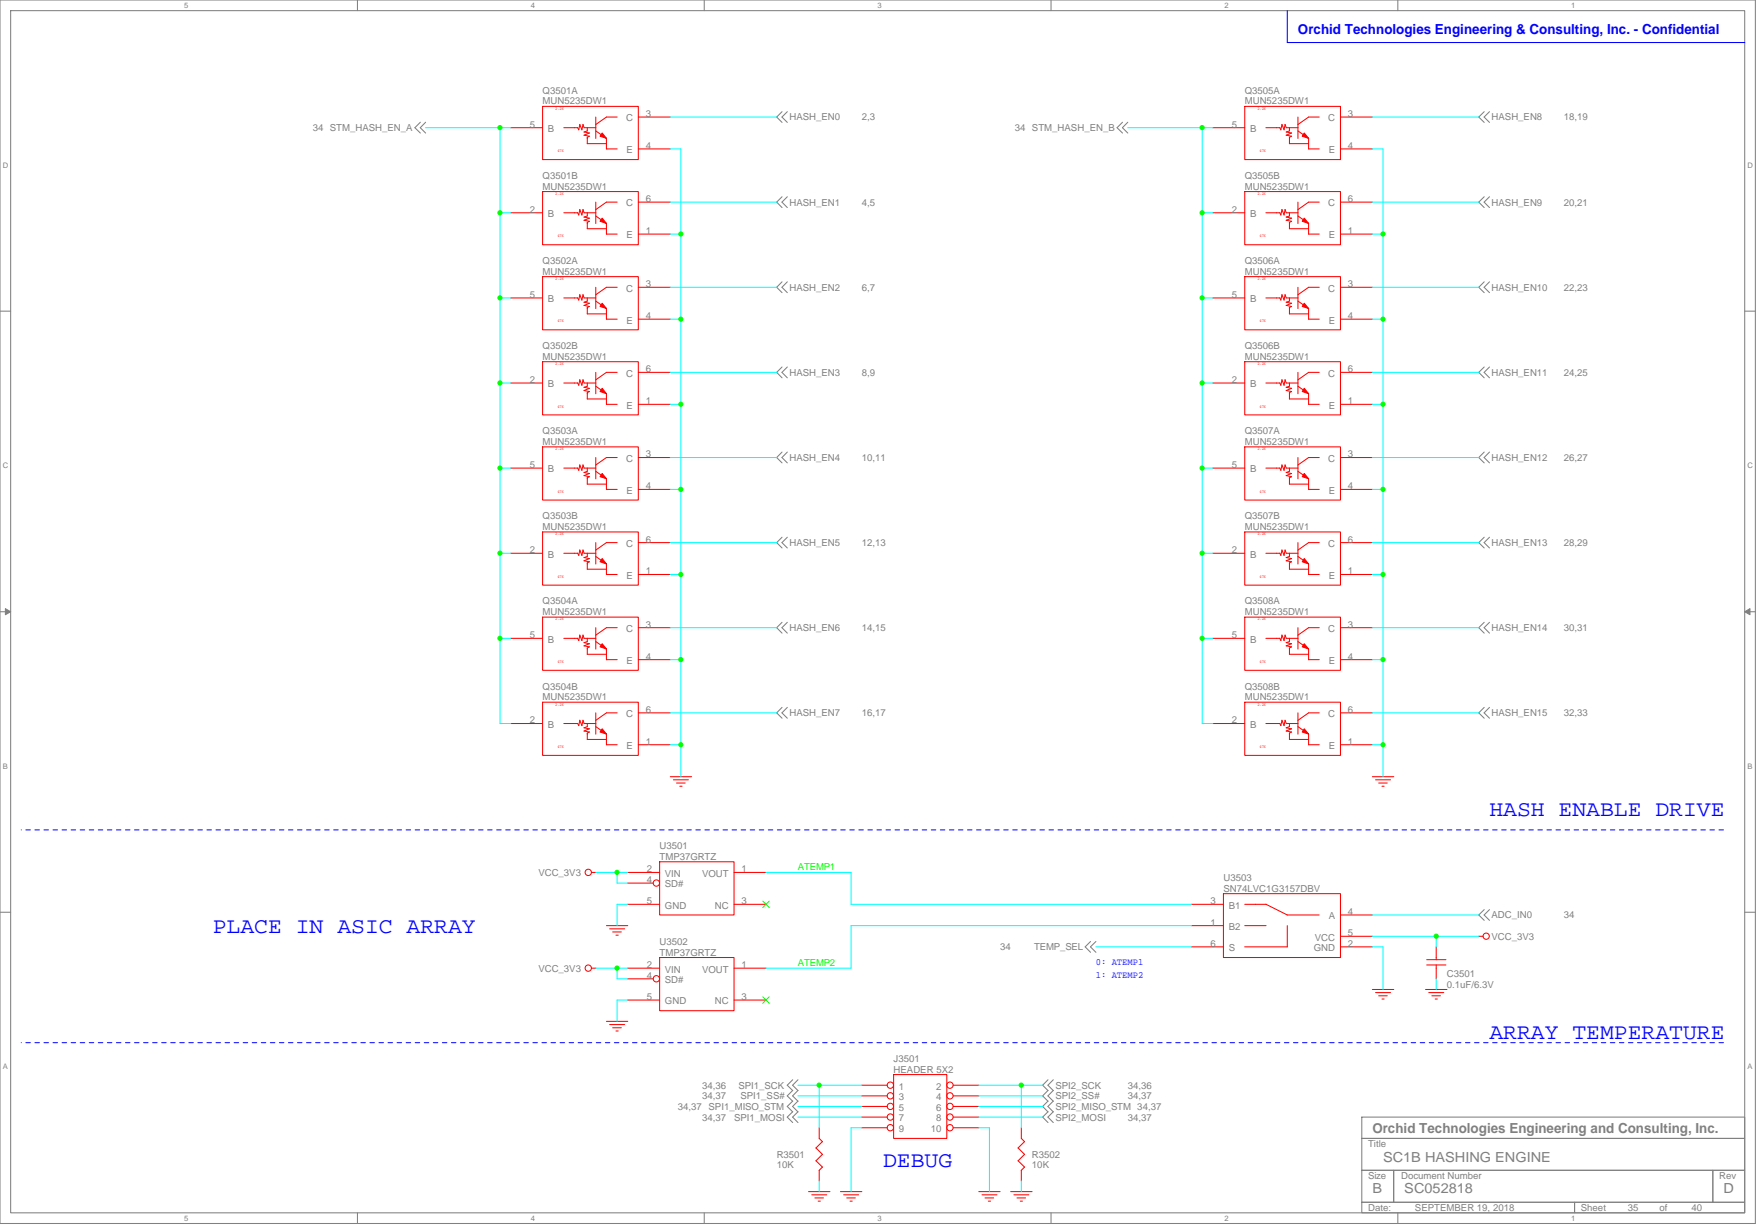
[picture p187: page 35]

PLACE IN ASIC ARRAY

Orchid Technologies Engineering and Consulting, Inc.

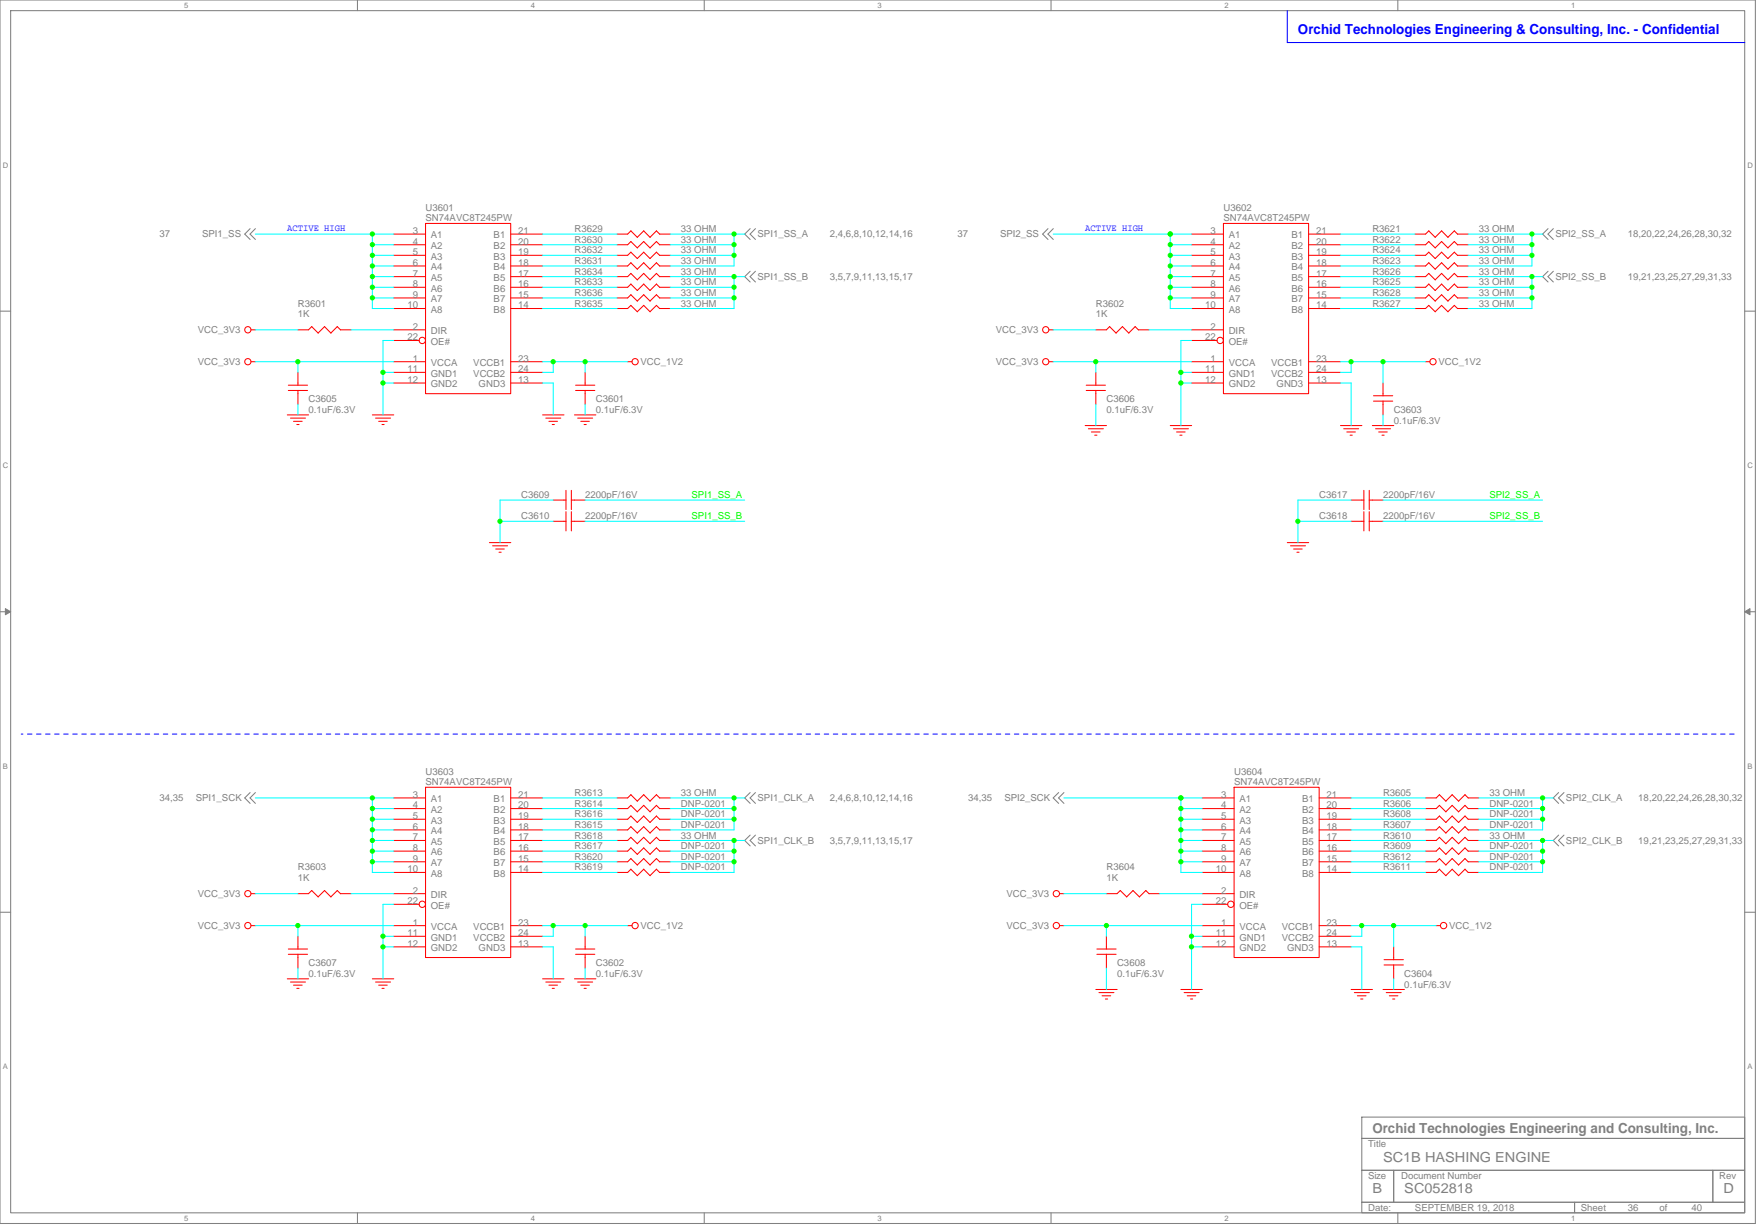
[picture p188: page 36]

Orchid Technologies Engineering and Consulting, Inc.

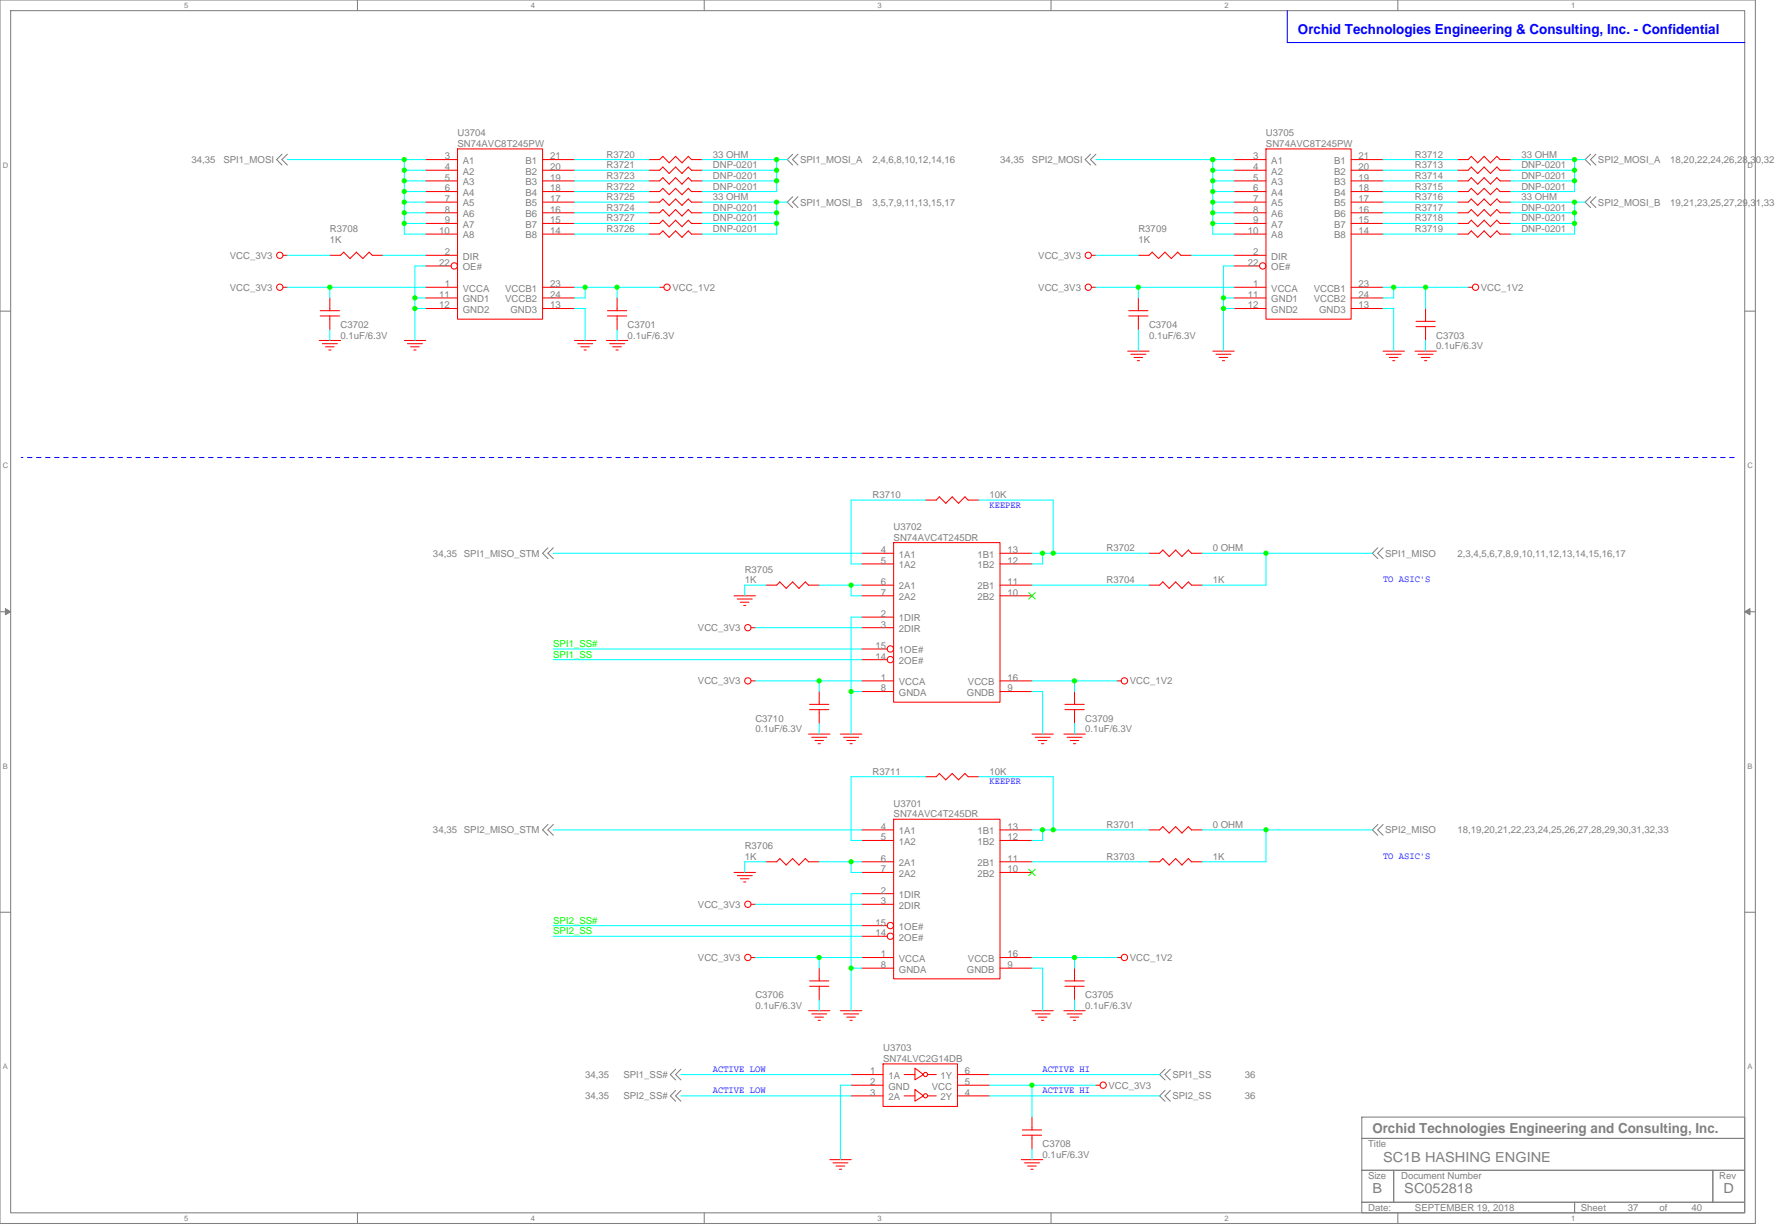
[picture p189: page 37]

Orchid Technologies Engineering and Consulting, Inc.

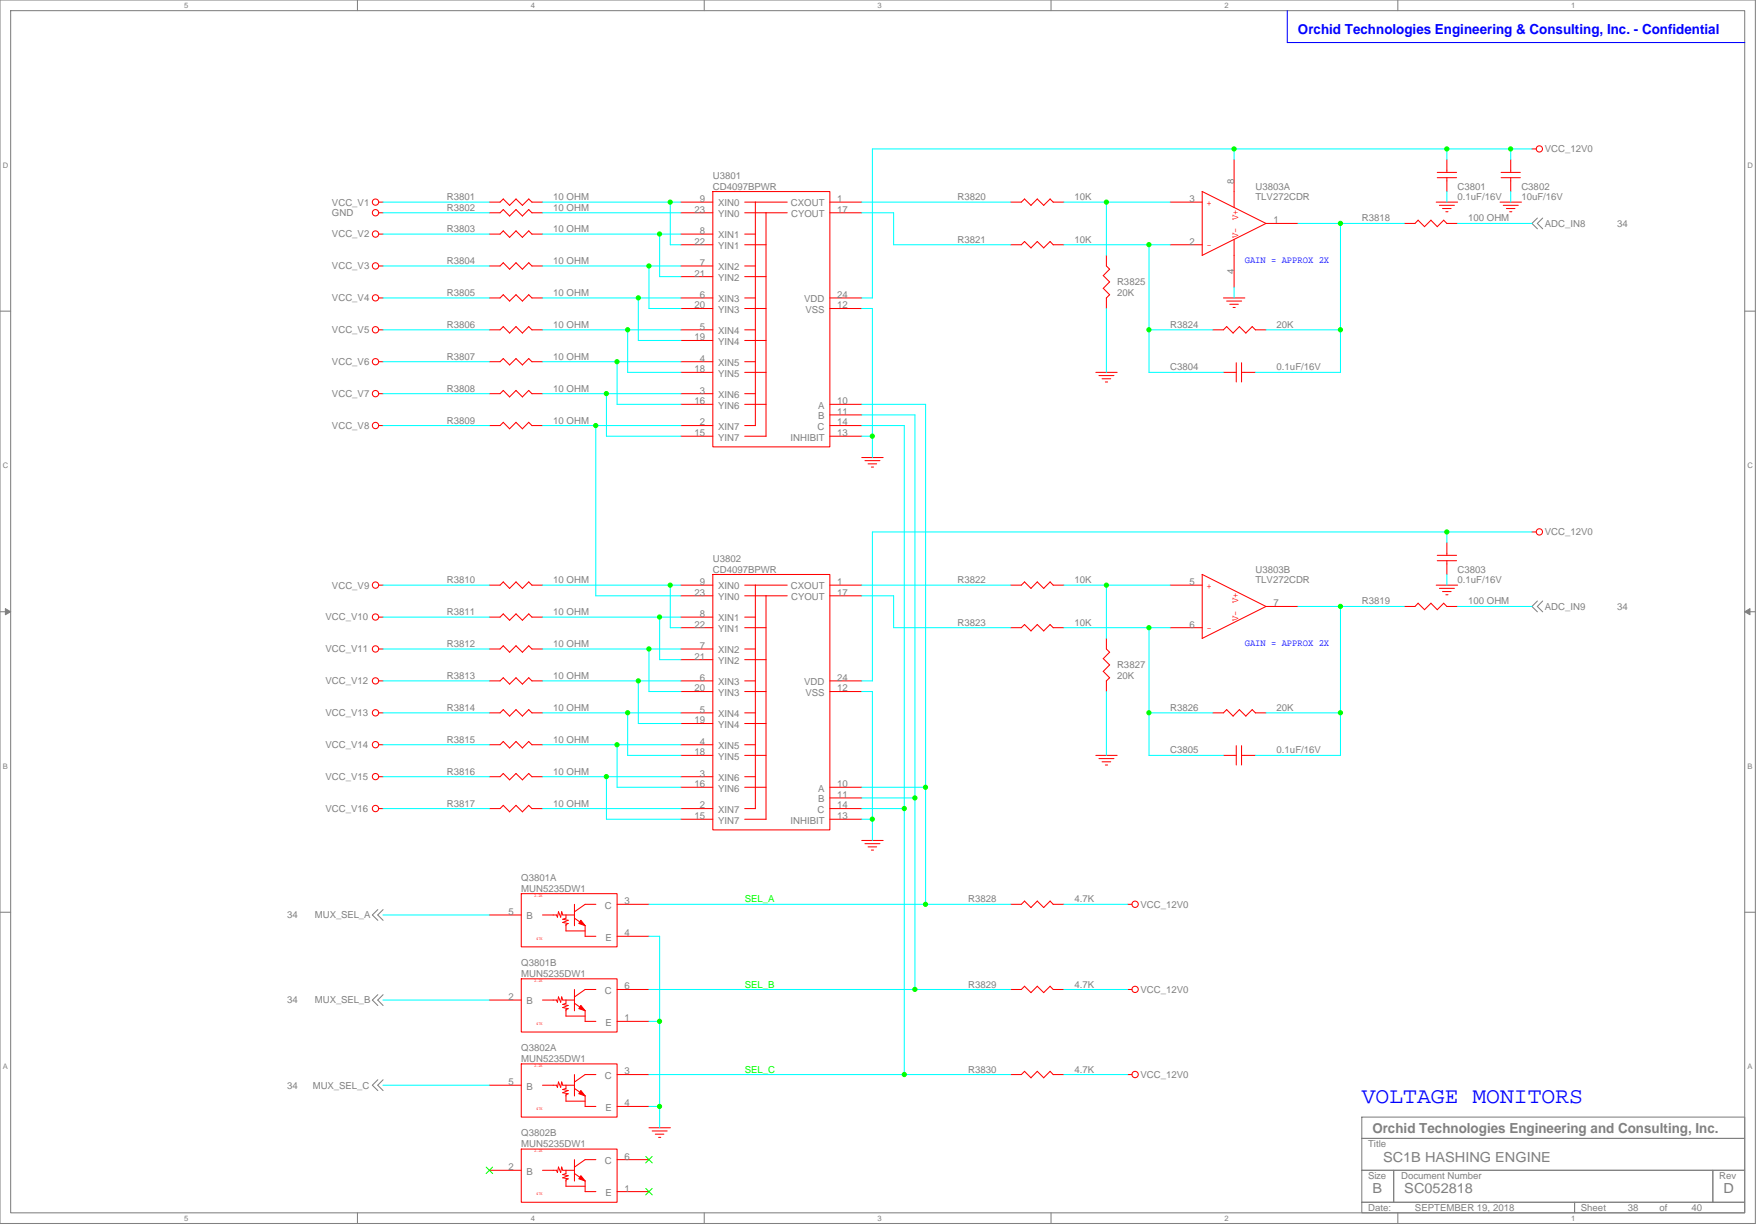
[picture p190: page 38]

Orchid Technologies Engineering and Consulting, Inc.

# 10.5V @ 50 AMP

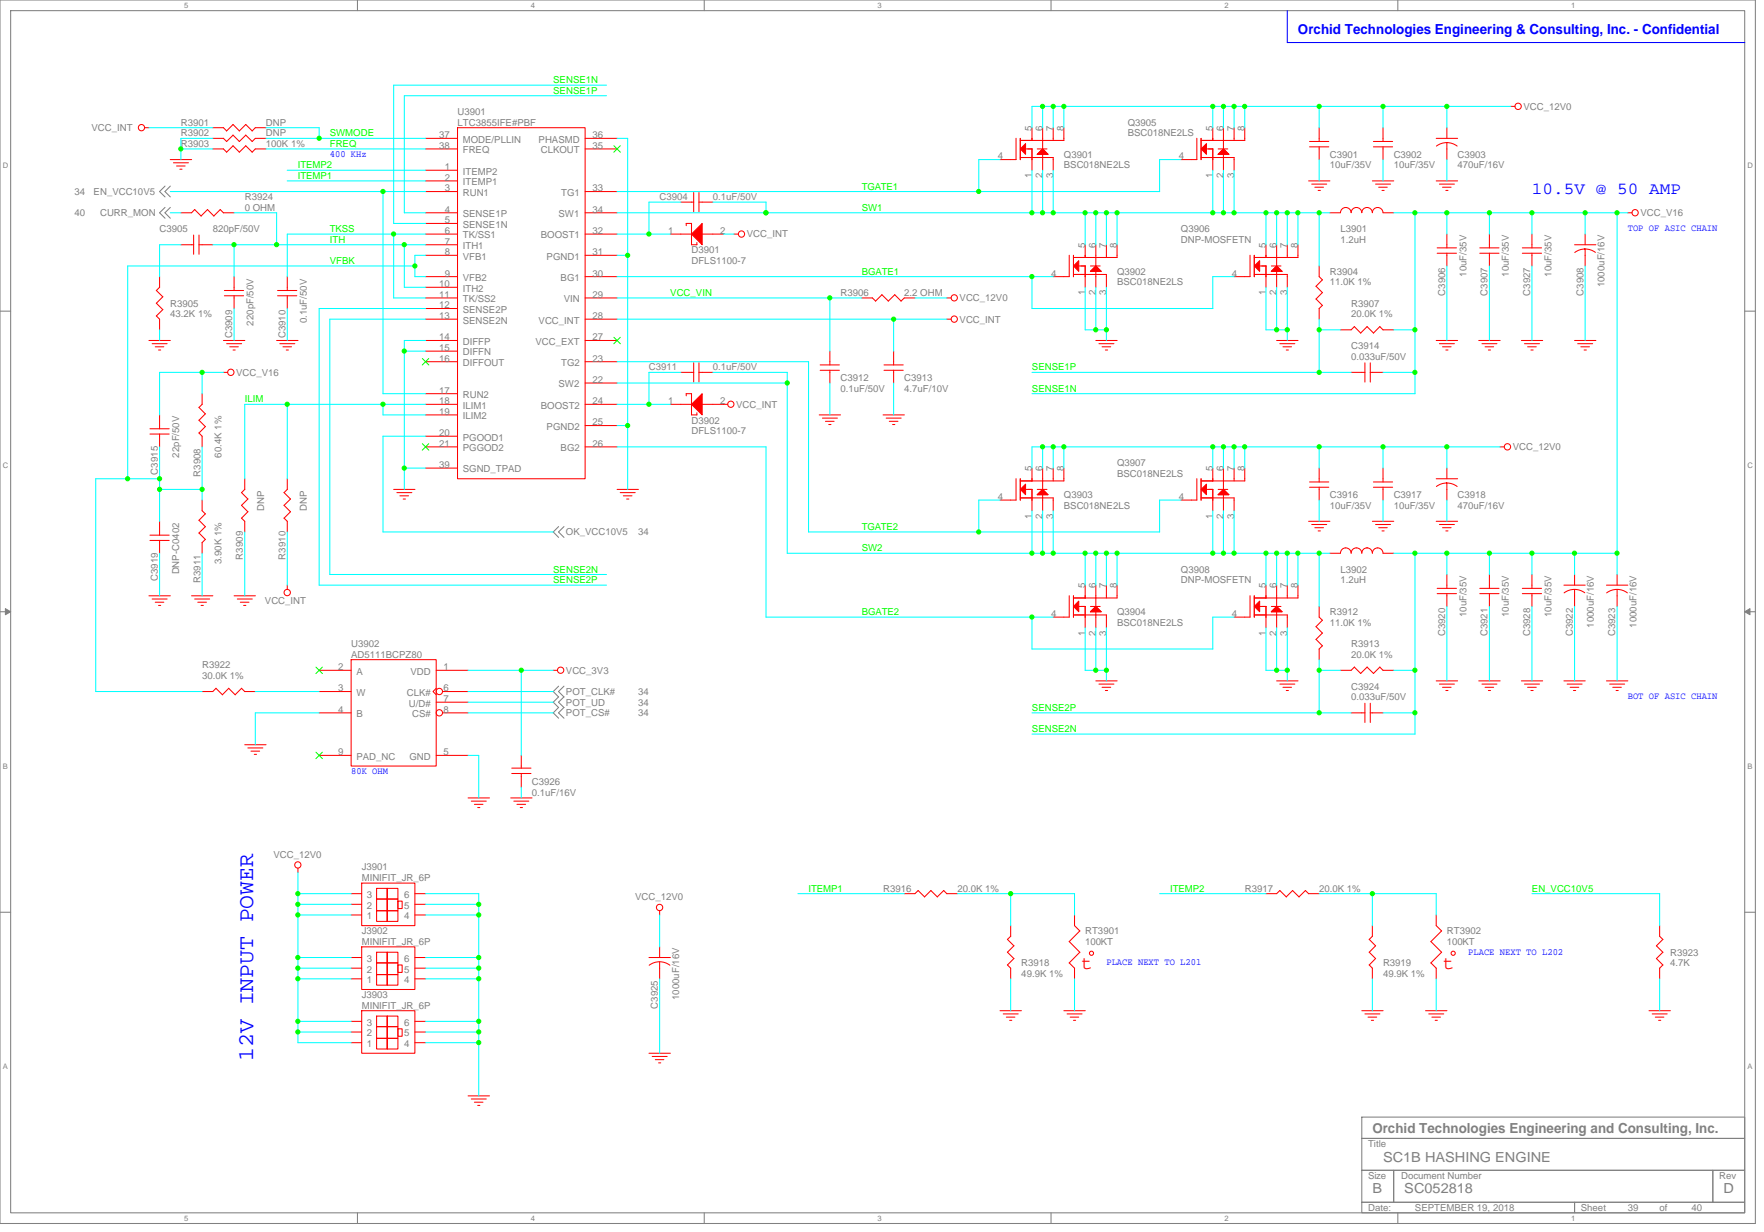
[picture p191: page 39]

VCC_V16
TOP OF ASIC CHAIN

BOT OF ASIC CHAIN

Orchid Technologies Engineering and Consulting, Inc.

# UART PORTS, CMOS LEVELS

# COMMUNICATIONS CONNECTOR

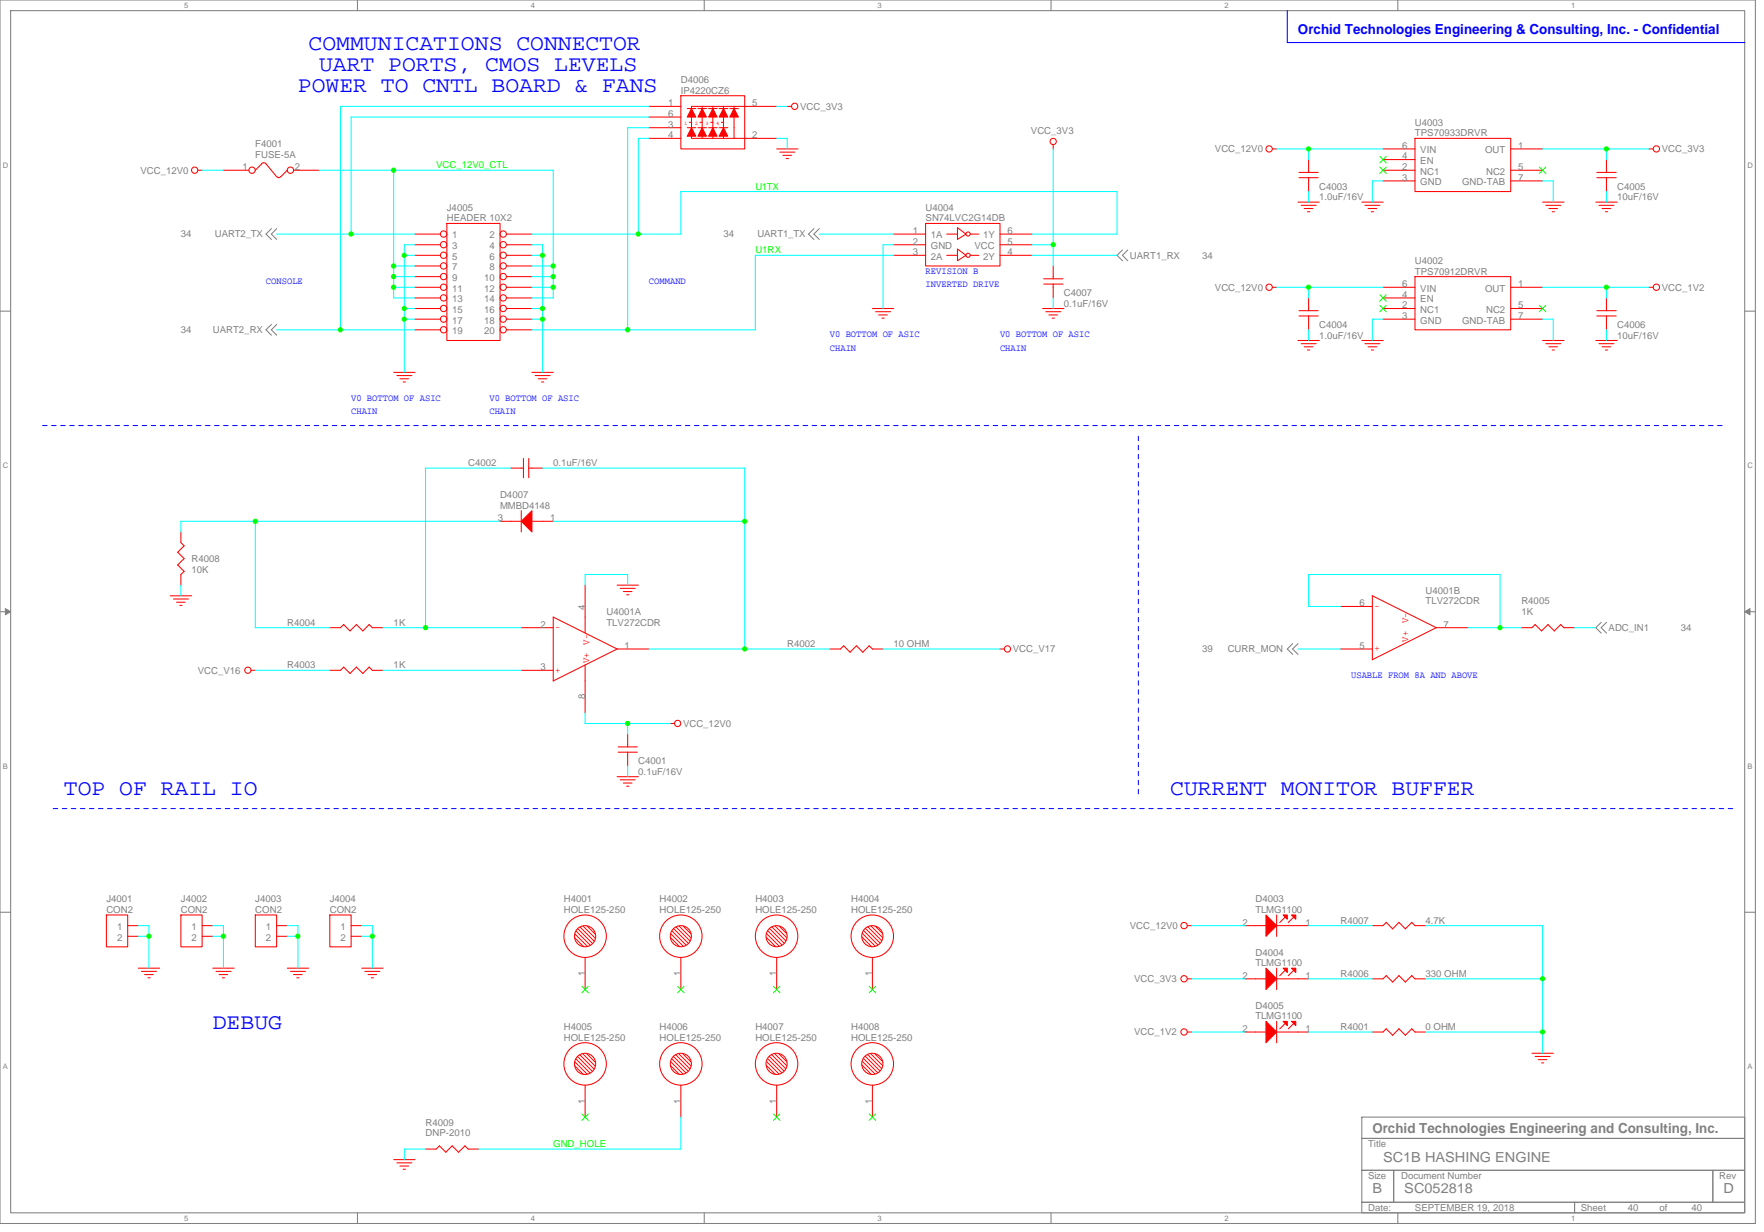
[picture p192: page 40]

POWER TO CNTL BOARD & FANS

USABLE FROM 8A AND ABOVE

TOP OF RAIL IO

Orchid Technologies Engineering and Consulting, Inc.
