ObeliskInc/obelisk-hardware/Generation 2 Mining Hardware/Electrical/Control Board/pcb/CC1B_REVA_ASY/CC1B_REVA_AS1.pdf

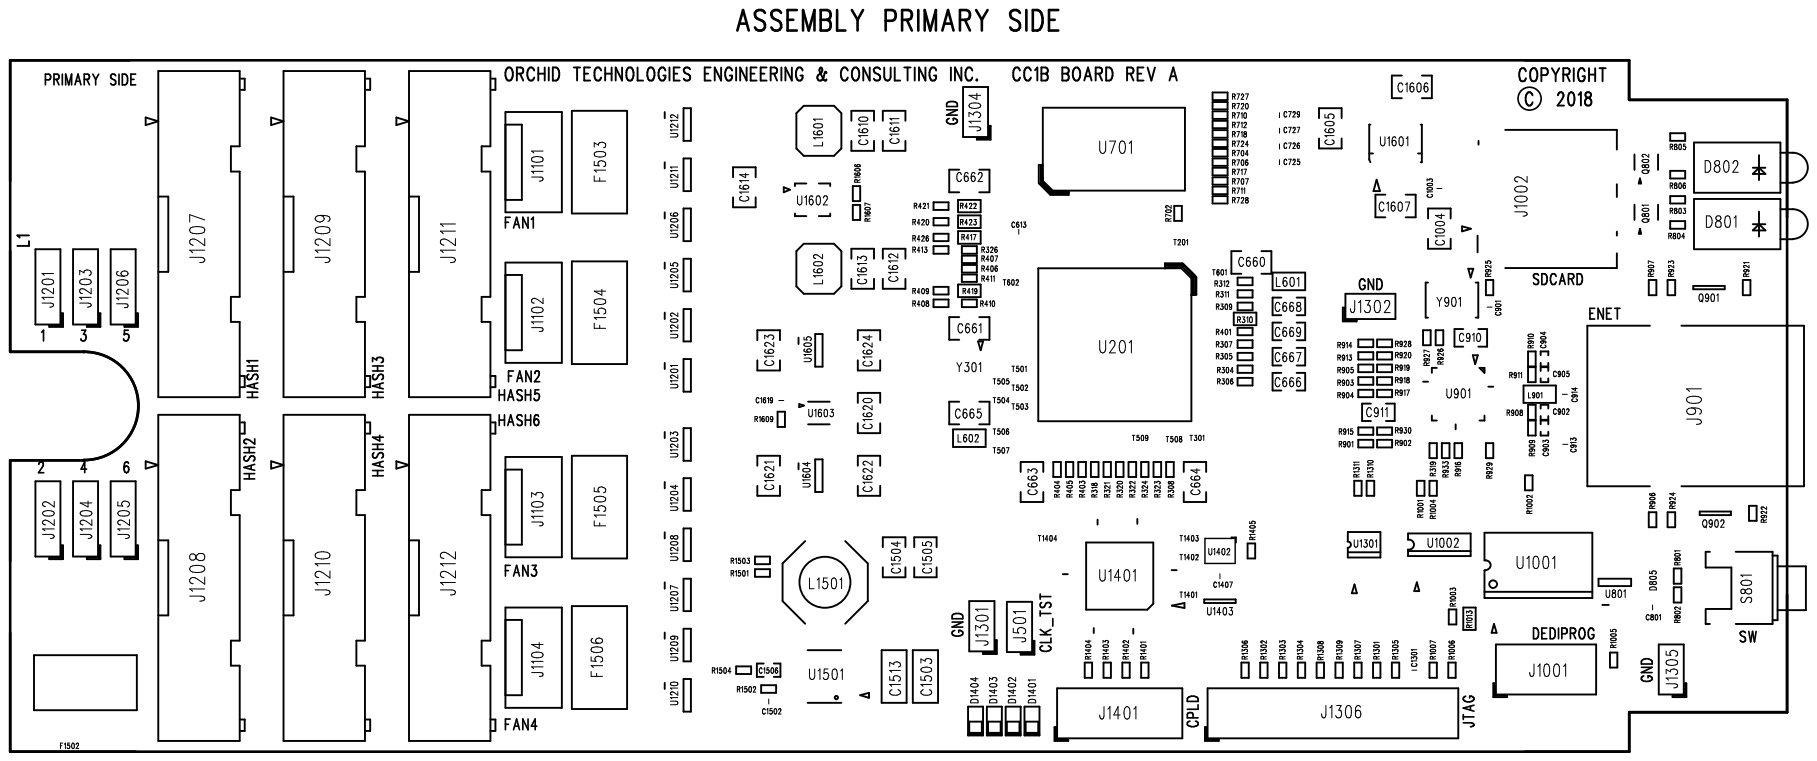
[picture p193: page 1]
