ObeliskInc/obelisk-hardware/Generation 2 Mining Hardware/Electrical/Control Board/pcb/CC1B_REVA_ASY/CC1B_REVA_AS2.pdf

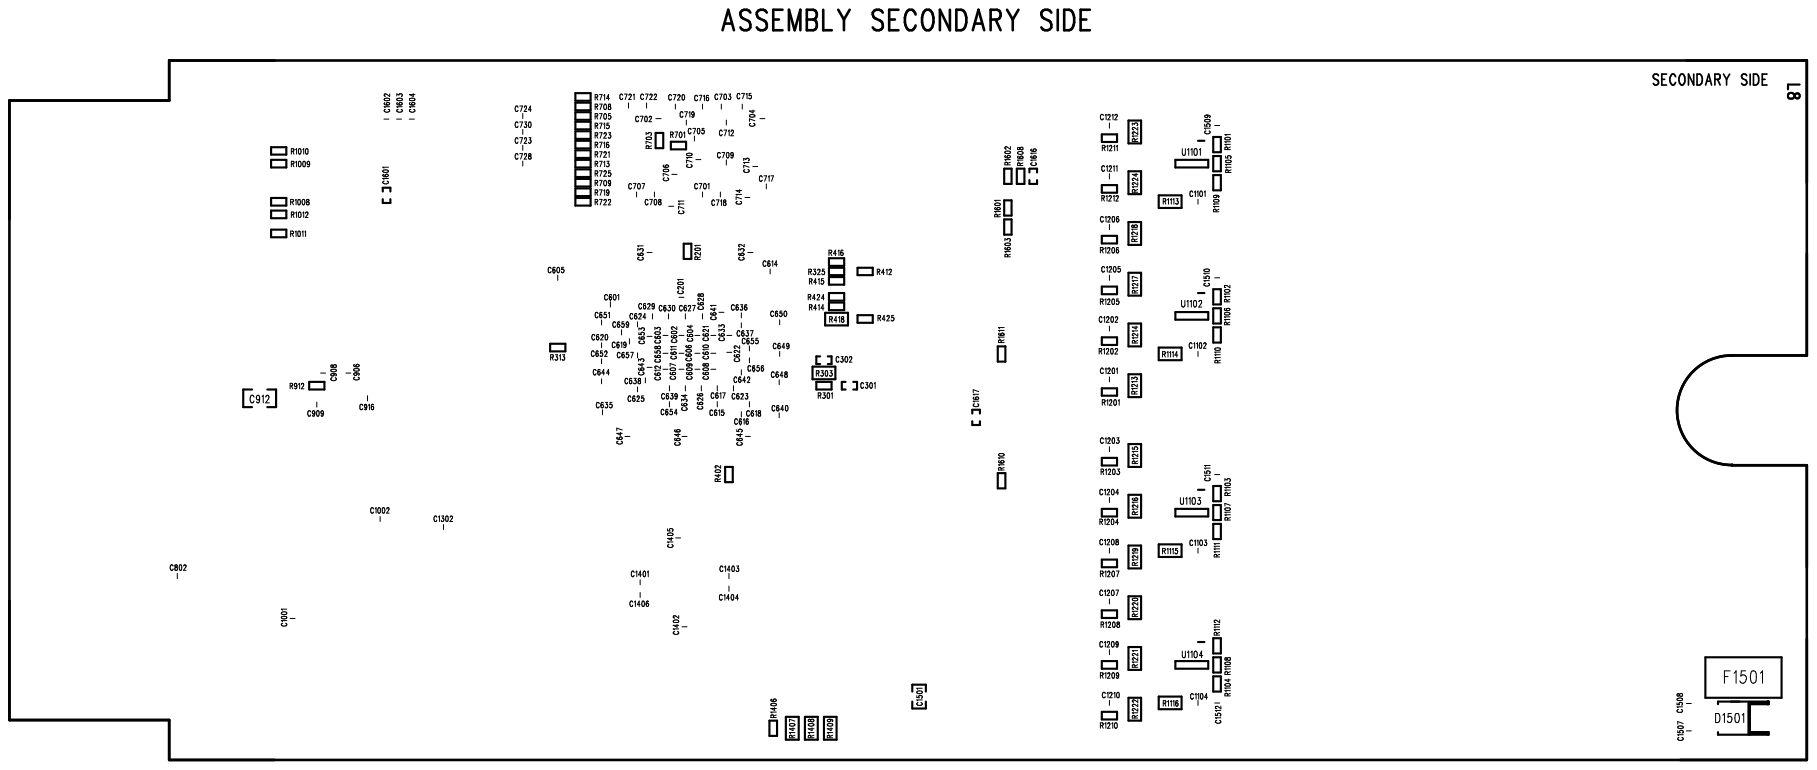
[picture p194: page 1]
