ObeliskInc/obelisk-hardware/Generation 2 Mining Hardware/Electrical/Control Board/pcb/CC1B_REVA_ASY/CC1B_REVA_FAB.pdf

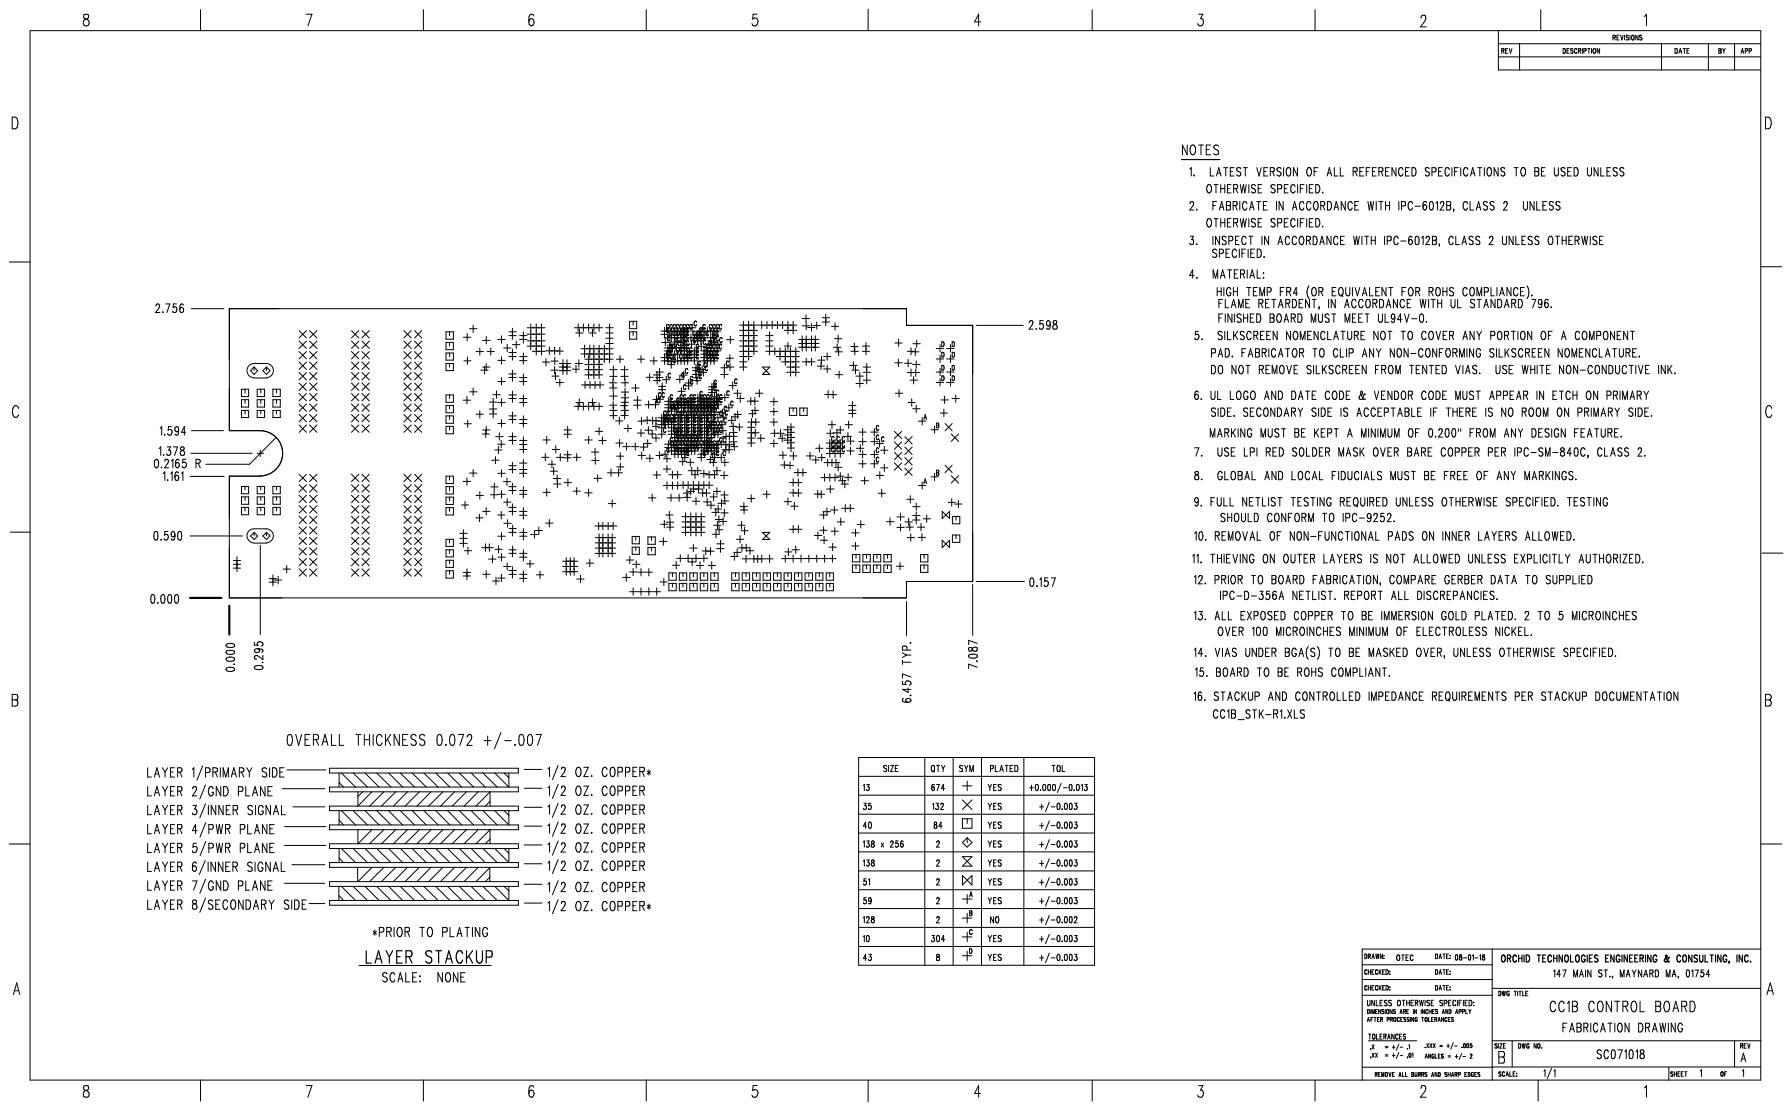
[picture p195: page 1]
