ObeliskInc/obelisk-hardware/Generation 2 Mining Hardware/Electrical/Control Board/pcb/CC1B_REVA_PDF/CC1B_REVA_L02.pdf

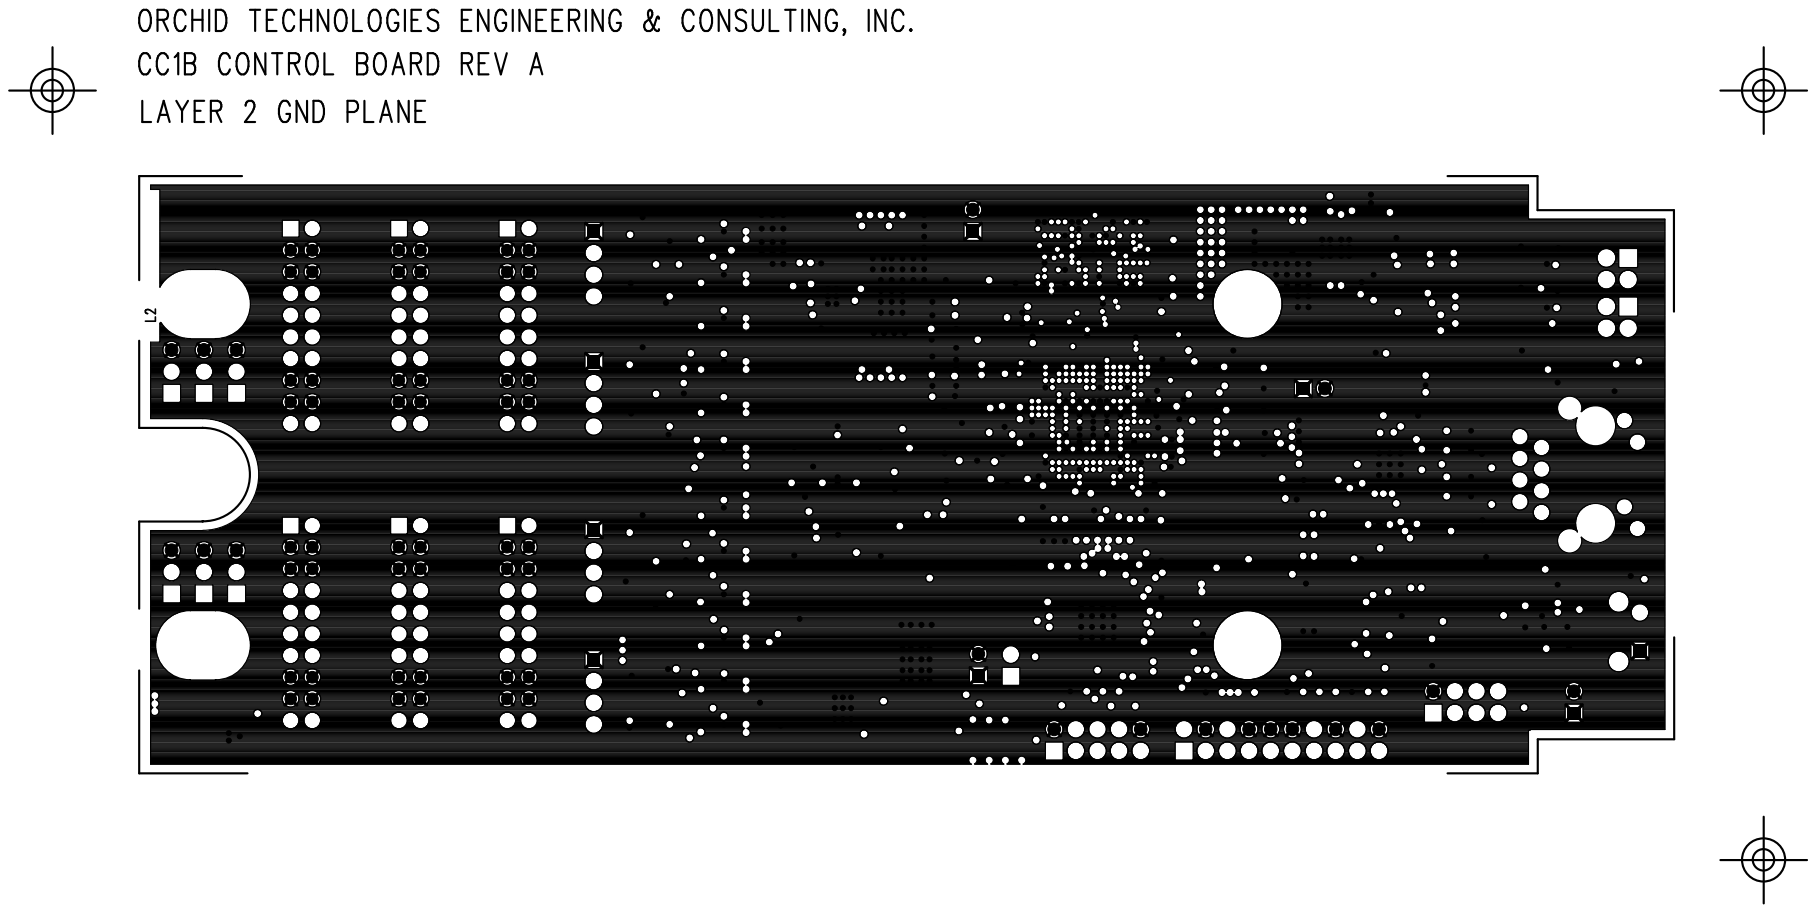
[picture p197: page 1]
