ObeliskInc/obelisk-hardware/Generation 2 Mining Hardware/Electrical/Control Board/pcb/CC1B_REVA_PDF/CC1B_REVA_L03.pdf

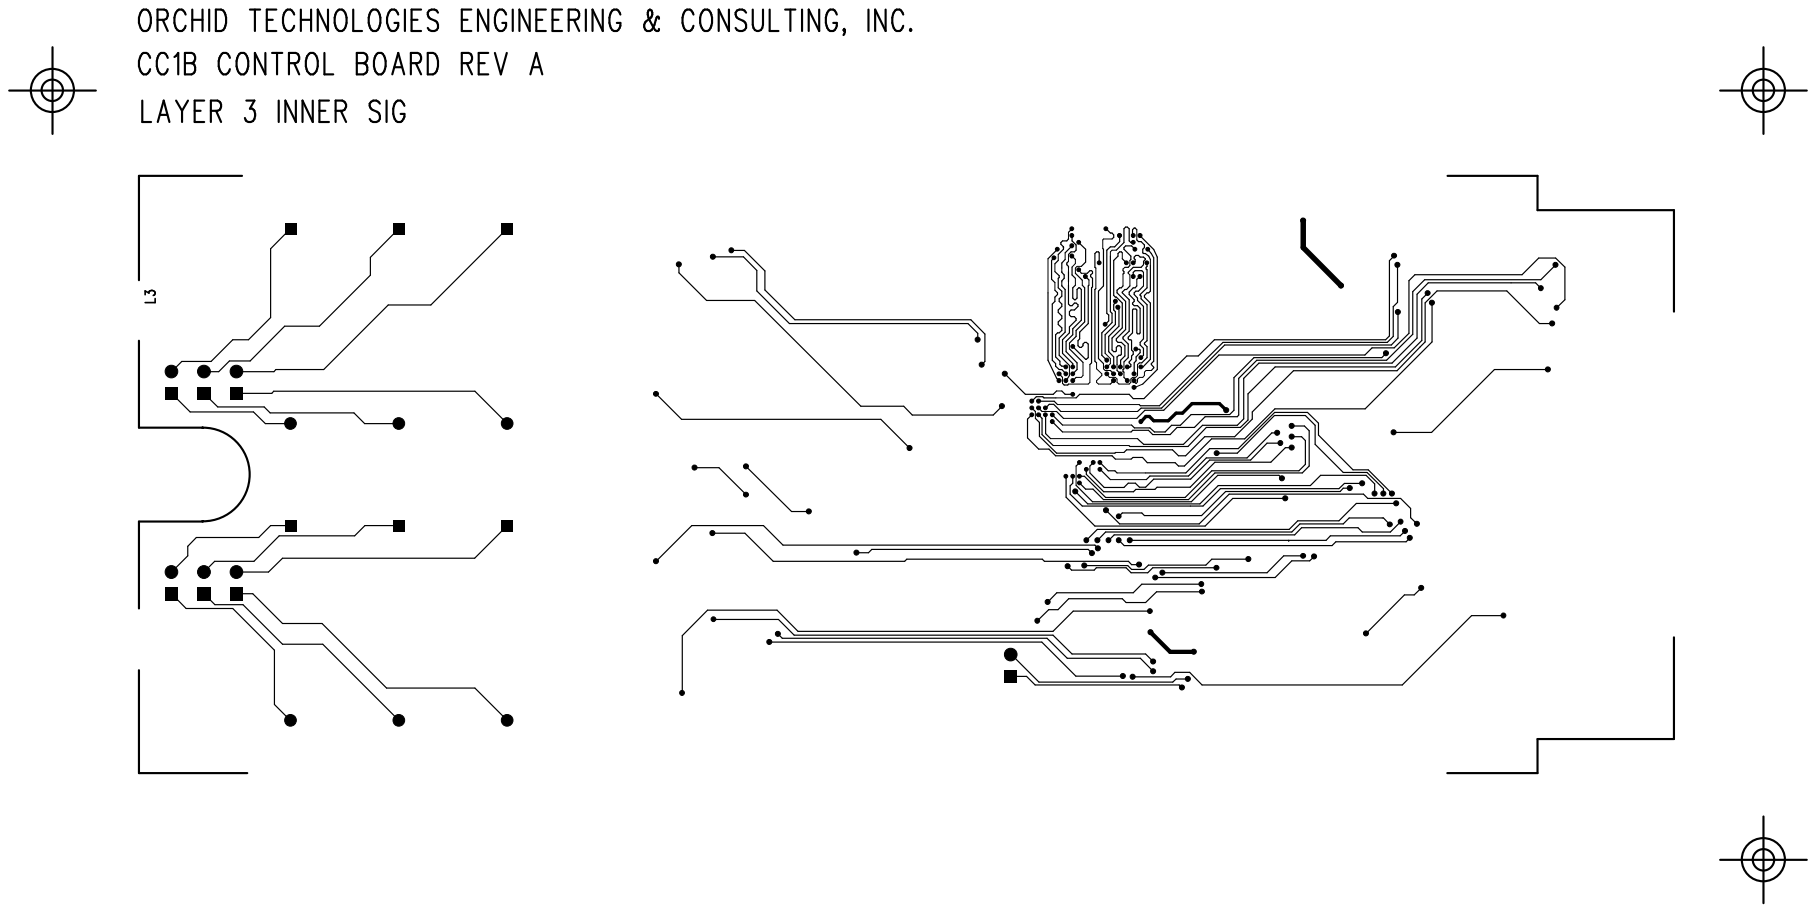
[picture p198: page 1]
