ObeliskInc/obelisk-hardware/Generation 2 Mining Hardware/Electrical/Control Board/pcb/CC1B_REVA_PDF/CC1B_REVA_L05.pdf

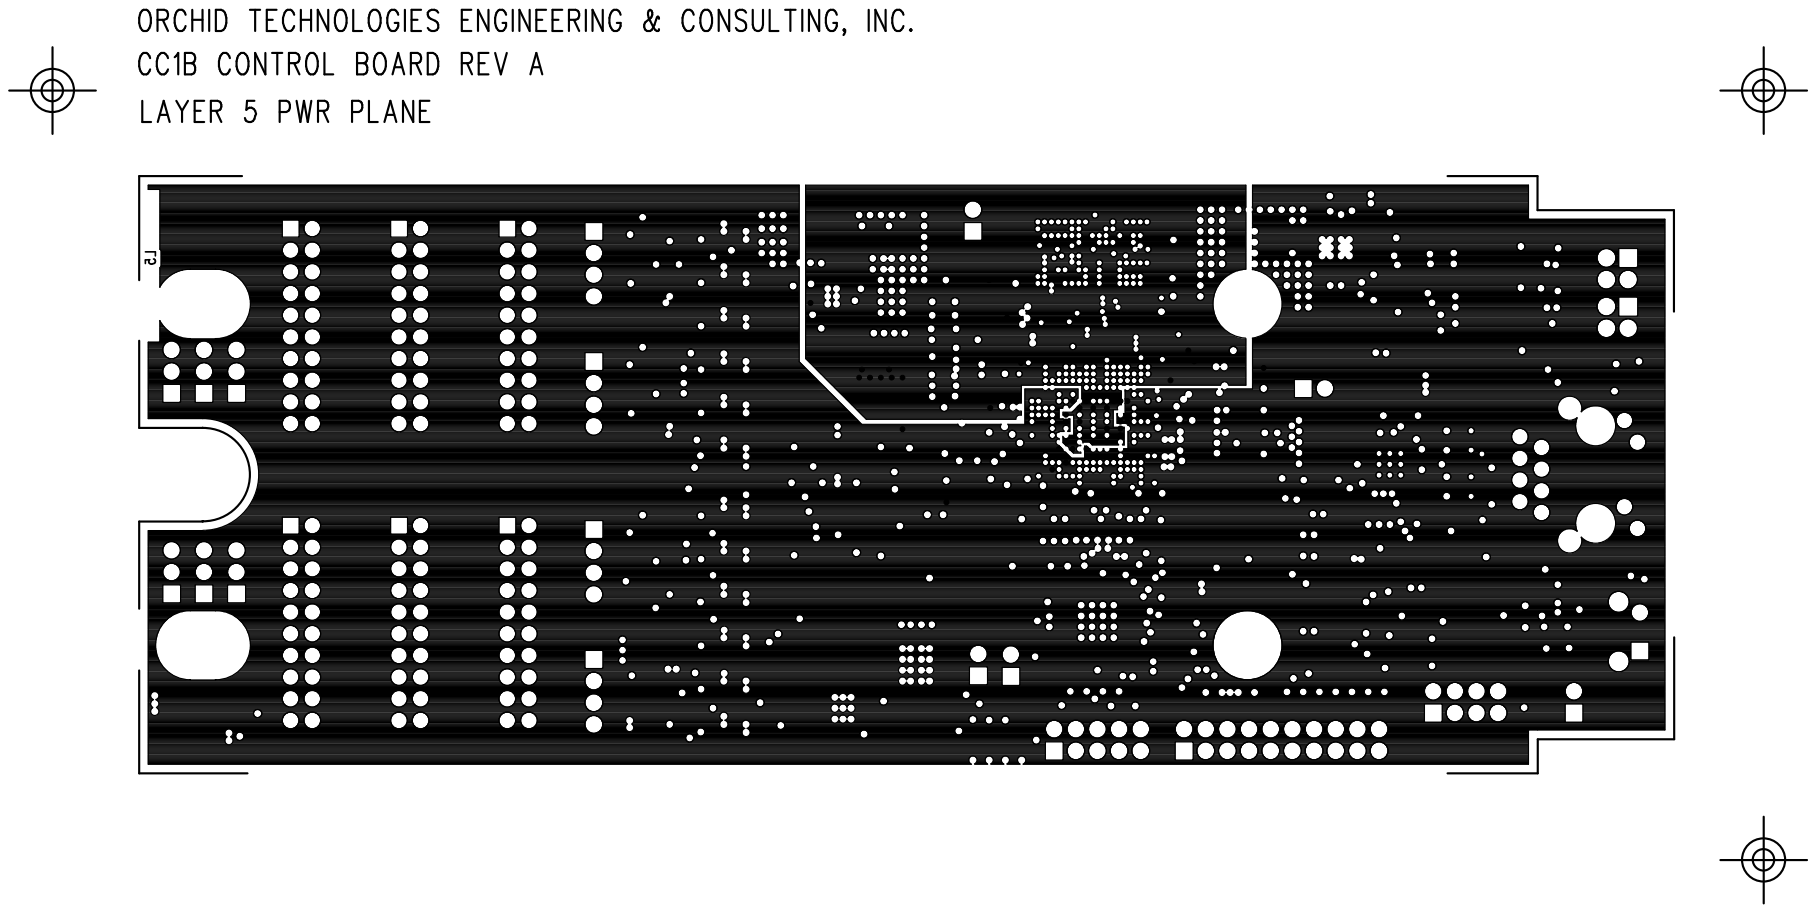
[picture p200: page 1]
