ObeliskInc/obelisk-hardware/Generation 2 Mining Hardware/Electrical/Hashing Board/pcb/SC1B_REVD_ASY/SC1B_REVD_AS1.pdf

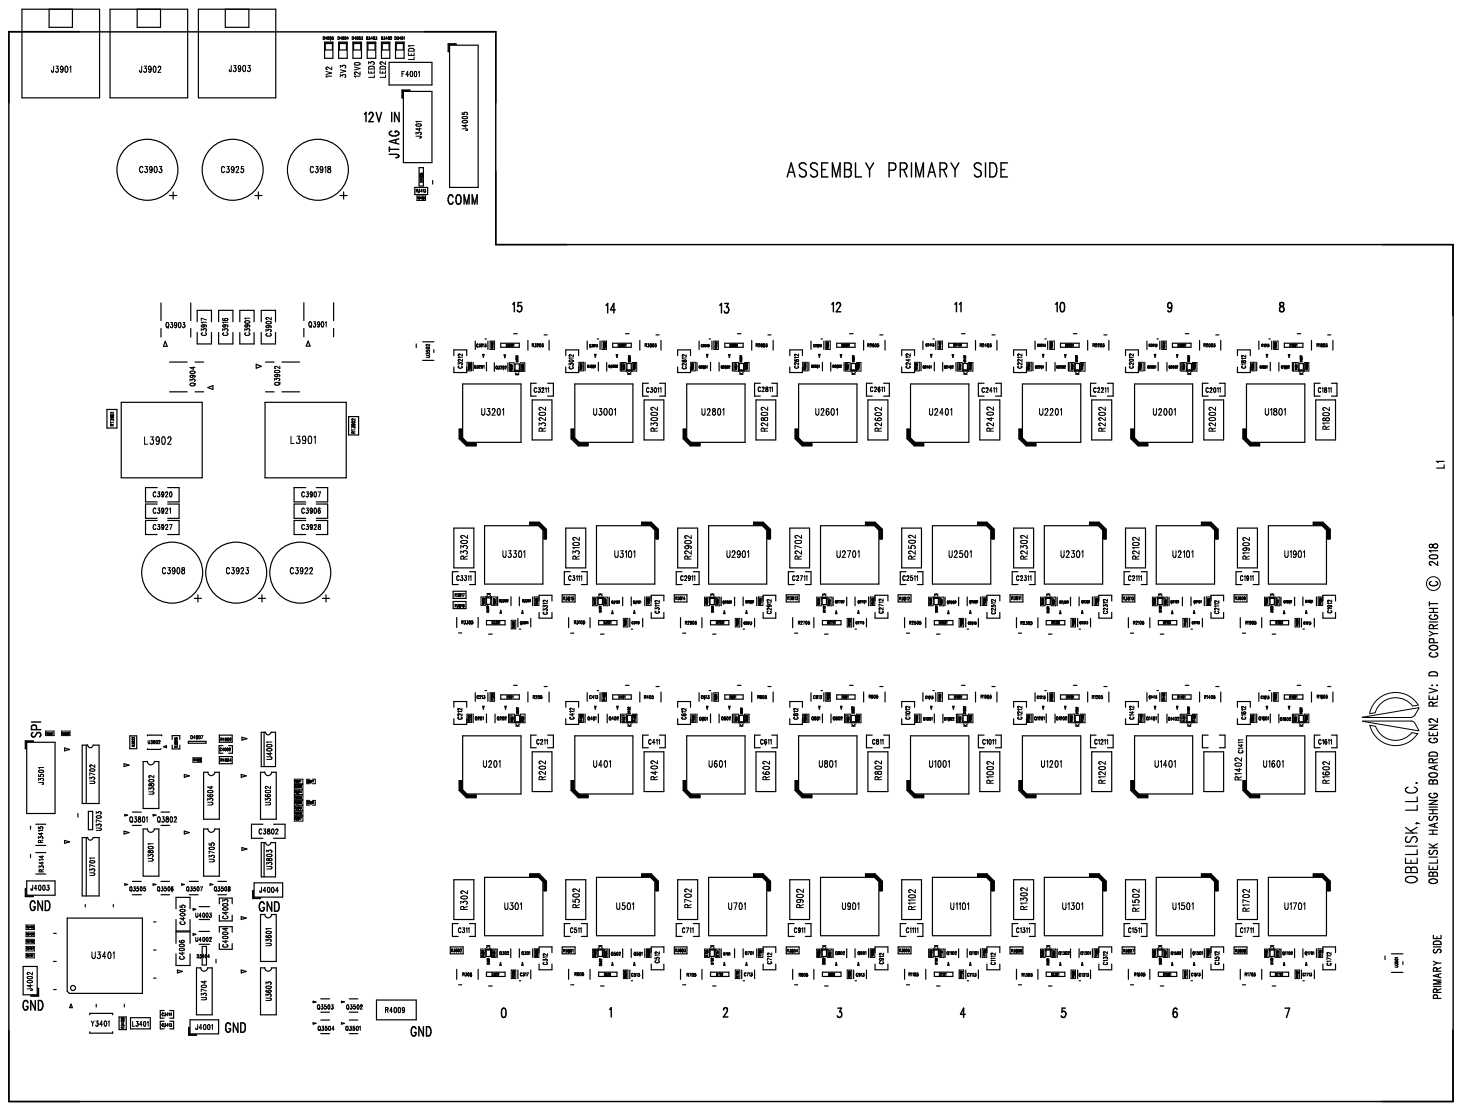
[picture p210: page 1]
