ObeliskInc/obelisk-hardware/Generation 2 Mining Hardware/Electrical/Hashing Board/pcb/SC1B_REVD_ASY/SC1B_REVD_FAB.pdf

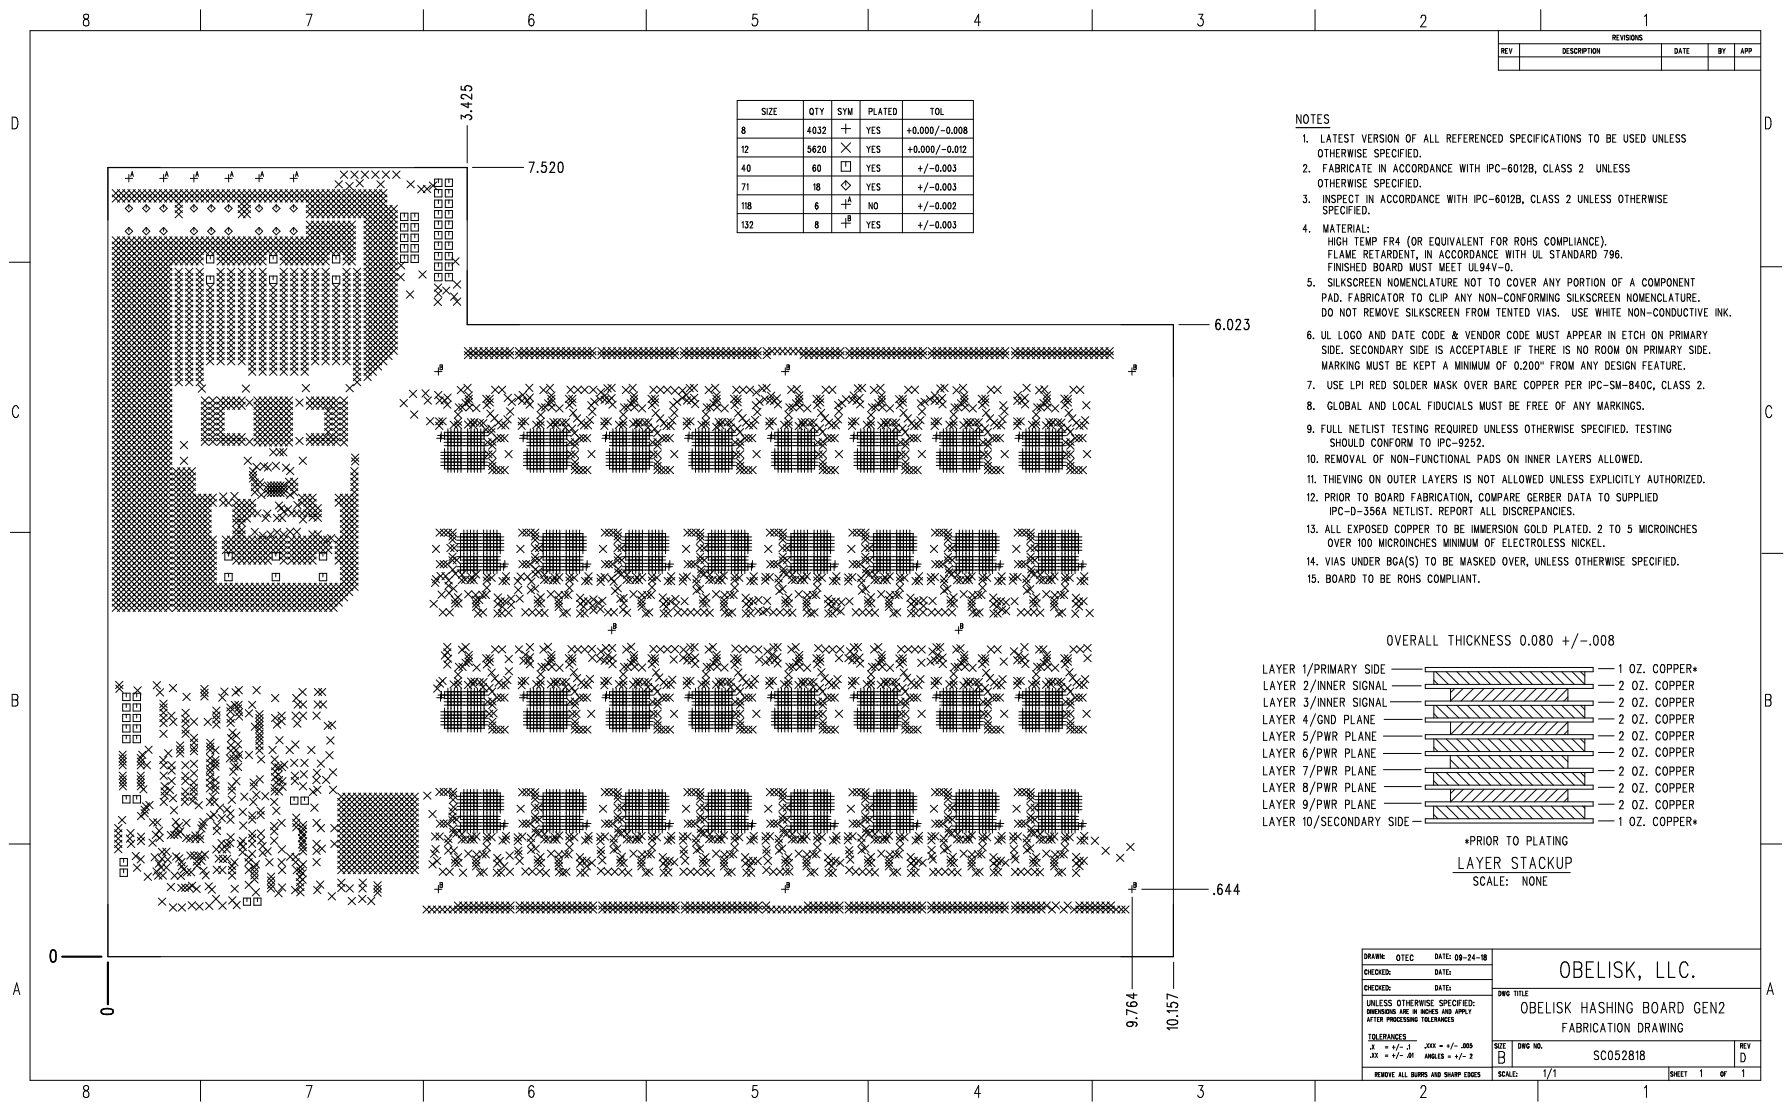
[picture p211: page 1]
