ObeliskInc/obelisk-hardware/Generation 2 Mining Hardware/Electrical/Hashing Board/pcb/SC1B_REVD_PDF/SC1B_REVD_L04.pdf

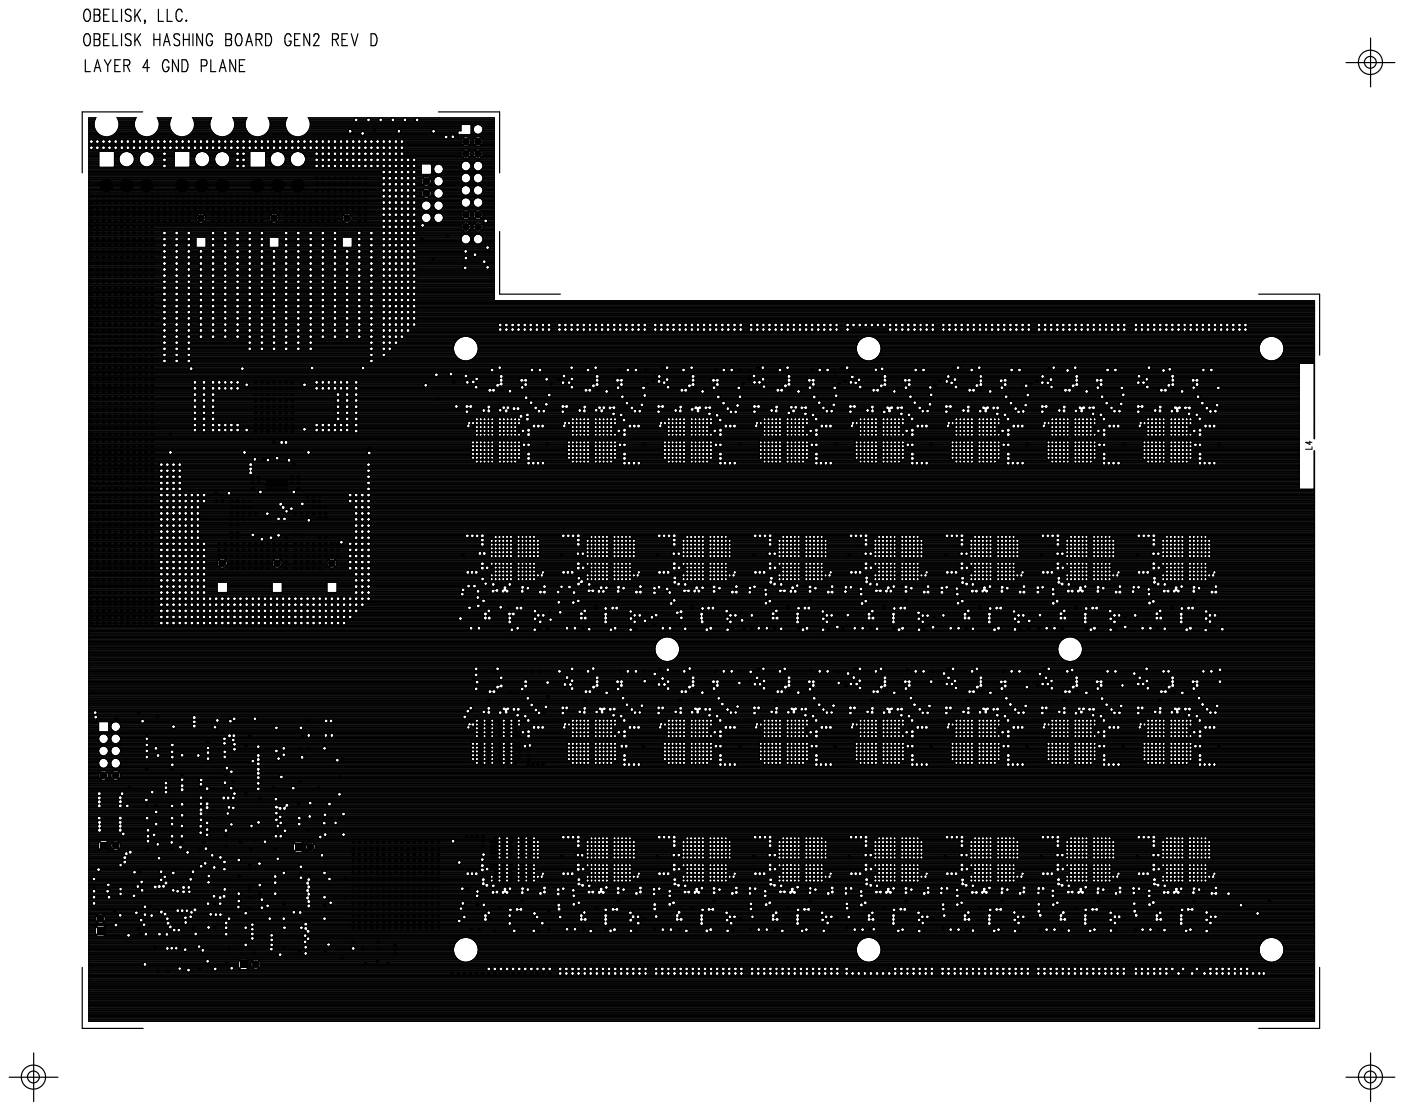
[picture p215: page 1]
